ksr/YACC1-D/hardware/cards/README.md

# hardware/cards

One folder per card: README.md, kicad/ (current), eagle/<rev>/ (deprecated), docs/, bom/.

_Contents migrated 2026-09-19; MIGRATION.md at the repo root says which copy each item came from._
