ksr/YACC1-D/hardware/mechanical/README.md

# hardware/mechanical

Card divider clips (.stl/.skp), switch template (.svg), spacers, layout specs.

_Contents migrated 2026-09-19; MIGRATION.md at the repo root says which copy each item came from._
