ksr/YACC1-D/hardware/bus/bus-jumper-horizontal/README.md

# hardware/bus/bus-jumper-horizontal

V3.2.

_Contents migrated 2026-09-19; MIGRATION.md at the repo root says which copy each item came from._

Note (2026-09-20): the schematic is byte-identical to the vertical jumper's; only the board differs. `eagle/v3.2/` is the 4-layer 231 x 115 mm board in the machine (its `.brd.orig` is the unrouted intermediate labelled V3.1); `eagle/deprecated/v3.0/` is the first 2-layer 231 x 70 mm version.

Status (2026-09-20): built, **not fitted** — the jumper boards were for an older bus arrangement and are obsolete.
