ksr/YACC1-D/hardware/cards/sequencer-memory/kicad/v2.1/README.md

# sequencer-memory-v2.1 — KiCad conversion

Generated 2026-09-23 by `tools/eagle_to_kicad_all.py` from the Eagle design `Sequencer-Memory-V2.1` in `hardware/cards/sequencer-memory/eagle/v2.1/`. **The Eagle files are the record of what was designed and built; this KiCad project is derived from them and is regenerated from scratch on every run of the tool** (hand edits here will be lost - once a card is edited in KiCad, remove it from the tool's list). This revision was FABRICATED (see `hardware/FABRICATED.md`).

## Files

| File | What it is |
|---|---|
| `sequencer-memory-v2.1.kicad_pro` | project; OSH Park rules (6 mil track, 5 mil clearance, 10 mil drill, 4 mil annular) |
| `sequencer-memory-v2.1.kicad_sch` | root sheet; 4 sub-sheet(s) `sequencer-memory-v2.1-sheetN.kicad_sch` mirror the Eagle sheets |
| `sequencer-memory-v2.1-eagle.kicad_sym` | project symbol library generated from the Eagle libraries used (units = Eagle gates) |
| `sequencer-memory-v2.1.kicad_pcb` | the board: 4 copper layers, 63 footprints, 1681 track segments, 198 vias |
| `sequencer-memory-v2.1-eagle.pretty/` | project footprint library extracted from the imported board |
| `reports/` | ERC (`erc.json`), DRC (`drc.json`), schematic PDF, board renders (`-top.png`, `-bottom.png`), netlist + `netlist-compare.txt` |

## Proof

Schematic-vs-board netlist comparison (`tools/kicad/compare_netlists.py`: every (reference, pad) partition must be identical): **MATCH (106/106 nets)**

```
  same connectivity, different net name: [('/Sheet 3/ARD-RXIN', 'ARD-RXIN'), ('/Sheet 3/ARD-TXOUT', 'ARD-TXOUT'), ('/Sheet 3/FAULT', 'FAULT'), ('/Sheet 3/LD', 'LD'), ('/Sheet 3/LED-READY', 'LED-READY'), ('Net-(C19-Pad1)', 'N$8'), ('Net-(FAULT0-C)', 'N$27'), ('Net-(IC9-WP)', 'N$32'), ('Net-(IC15-AREF)', 'N$17'), ('Net-(IC15-PB6(XTAL1{slash}TOSC1))', 'N$6'), ('Net-(IC15-PB7(XTAL2{slash}TOSC2))', 'N$7'), ('Net-(IC15-PC0(ADC0))', 'N$30'), ('Net-(IC15-PC2(ADC2))', 'N$39'), ('Net-(JP3-DTR)', 'N$33'), ('Net-(JP3-VCC)', 'N$34'), ('Net-(LOADING0-C)', 'N$26'), ('Net-(PWR0-PadA)', 'N$1'), ('Net-(READY0-C)', 'N$25')]
```

## Readability

`tools/kicad/sch_overlaps.py` over every sheet: text over text 3, text over a symbol body 12, text crossed by a line 13, items off the drawing frame or on the title block 0. What is left is mostly the Eagle drawing itself (parts placed that close in Eagle) or KiCad drawing pin numbers centred on short pins.

## Residual ERC / DRC

ERC by type: unconnected_wire_endpoint 11.
`isolated_pin_label` = the converter's per-net global labels (cosmetic); `power_pin_not_driven` / unused-unit notes are the same ones KiCad's own Eagle importer leaves. `unconnected_wire_endpoint` / `pin_not_connected` = wire stubs Eagle leaves bare (mostly net wires ending on a bus, which is drawn as graphics here); since 2026-09-23 the converter no longer hangs a label on every such end (that was most of the label clutter), so they show as KiCad warnings.

DRC by type: lib_footprint_mismatch 2, shorting_items 1, silk_edge_clearance 9, silk_over_copper 199, silk_overlap 44, text_height 6, text_thickness 1, track_width 199; unconnected items 0; schematic parity 0.
Silk-over-pad and clearance notes reflect the Eagle design as drawn; unconnected items are Eagle airwires (parts the design left unrouted).

Converter: converted: 110 symbols, 584 wires, 398 labels, 82 junctions, 3 bus lines, 23 no-connects
