ksr/YACC1-D/hardware/cards/io/eagle/v1.1/Notes.md

*Converted from `Notes.rtf` (saved 2025-03-06) by `tools/rtf_to_md.py`; the .rtf is the original.*

IO Board V1.0    

Changes -  V1.1

TIL311 data latch connect to god so they always show data latch
TIL311 vcc to pin 14

LEDS are reversed hi bit to low bit

Add do not place under lcd (trestrict)

Change DB9 connector
 And add null modem logic to route tx/rx

Breakout TIL-311 to separate IO control

Next Version V1.2
Add a directional data bus buffer, probably driven by -io-rd (not done yet)

Connect 74138 IC5 pin 5 to -BUS-EN. (Not tested yet)
