ksr/YACC1-D/hardware/cards/mem-switch/eagle/v1.1/Notes.md

*Converted from `Notes.rtf` (saved 2025-03-06) by `tools/rtf_to_md.py`; the .rtf is the original.*

Version 1.0

Works
Missing bypass caps for address selection logic
Change to 74240 (inverted output)
Rotate switches (on up)

Add leds per address byte ?
Add additional address selection to locate with 16 byte blocks ?
