ksr/YACC1-D/hardware/cards/register/eagle/v1.1/Notes.md

*Converted from `Notes.rtf` (saved 2025-03-06) by `tools/rtf_to_md.py`; the .rtf is the original.*

Index registers V1.0

Next version 1.1

Changes since 1.0

Signal -IN and -OUT converted to In and OUT. Neither used in Index Register board

BUS Description PDF dated June 18 2020 is updated to new spec

NOTE from old design

Up or Down on rising edge other line must be high

IC38 switched to 4077 pin compatible with 74266

Version 1.1 to production 

Next version 1.2
SEE page 7
Is bus direction correct, should it be based on -rd-sel
