ksr/YACC1-D/hardware/cards/bus-tester/kicad/v3.1/reports/netlist-compare.txt

schematic: 110 components, 239 multi-pin nets; board: 239 multi-pin nets
identical net groups: 239 of 239
  same connectivity, different net name: [('/Sheet 3/ARD-RXIN', 'ARD-RXIN'), ('/Sheet 3/ARD-TXOUT', 'ARD-TXOUT'), ('Net-(C10-Pad1)', 'N$9'), ('Net-(IC7-WP)', 'N$2'), ('Net-(IC8-1Q)', 'N$38'), ('Net-(IC8-2Q)', 'N$31'), ('Net-(IC8-3Q)', 'N$35'), ('Net-(IC8-4Q)', 'N$32'), ('Net-(IC8-5Q)', 'N$33'), ('Net-(IC8-6Q)', 'N$34'), ('Net-(IC8-7Q)', 'N$36'), ('Net-(IC8-8Q)', 'N$37'), ('Net-(IC9A-A1)', 'N$40'), ('Net-(IC9A-A2)', 'N$43'), ('Net-(IC9A-A3)', 'N$42'), ('Net-(IC9A-A4)', 'N$41'), ('Net-(IC9B-A1)', 'N$44'), ('Net-(IC9B-A2)', 'N$46'), ('Net-(IC9B-A3)', 'N$47'), ('Net-(IC9B-A4)', 'N$45'), ('Net-(IC10-AREF)', 'N$14'), ('Net-(IC10-PB1(OC1A))', 'N$10'), ('Net-(IC10-PB2(SS{slash}OC1B))', 'N$8'), ('Net-(IC10-PB3(MOSI{slash}OC2))', 'N$7'), ('Net-(IC10-PB4(MISO))', 'N$6'), ('Net-(IC10-PB5(SCK))', 'N$1'), ('Net-(IC10-PB6(XTAL1{slash}TOSC1))', 'N$3'), ('Net-(IC10-PB7(XTAL2{slash}TOSC2))', 'N$4'), ('Net-(IC10-PC0(ADC0))', 'N$18'), ('Net-(IC10-PC1(ADC1))', 'N$19'), ('Net-(IC10-PC2(ADC2))', 'N$39'), ('Net-(IC18-2Q)', 'N$30'), ('Net-(IC18-4Q)', 'N$48'), ('Net-(JP1-DTR)', 'N$28'), ('Net-(JP1-VCC)', 'N$29'), ('Net-(L0-C)', 'N$26'), ('Net-(L1-C)', 'N$25'), ('Net-(L2-C)', 'N$24'), ('Net-(L3-C)', 'N$23'), ('Net-(L4-C)', 'N$22'), ('Net-(L5-C)', 'N$21'), ('Net-(L6-C)', 'N$20'), ('Net-(L7-C)', 'N$17'), ('Net-(LED1-C)', 'N$12'), ('Net-(LED2-C)', 'N$11'), ('Net-(LED3-C)', 'N$13'), ('Net-(LED4-C)', 'N$15'), ('Net-(LED5-C)', 'N$16'), ('Net-(OUT0-C)', 'N$27'), ('Net-(PWR0-PadA)', 'N$5')]
RESULT: MATCH
