ksr/YACC1-D/hardware/cards/cf/kicad/v1.0/reports/netlist-proof.txt

schematic 26 parts, 46 nets / 171 net pins, 92 unconnected pins (23 no-connect + 69 unused bus pins): MATCH
board     26 parts, 46 nets / 171 net pins, 92 unconnected pins (23 no-connect + 69 unused bus pins): MATCH
RESULT: MATCH (schematic and board both implement cf_netlist.py exactly)
