ksr/YACC1-D/hardware/cards/video/kicad/v1.1/reports/netlist-compare.txt

schematic: 47 components, 116 multi-pin nets; board: 116 multi-pin nets
identical net groups: 116 of 116
RESULT: MATCH
