ksr/YACC1-D/hardware/cards/memory/kicad/v2.0/options-keep-copper/reports/option-c-drc-summary.txt

     schematic parity: 53 items (built v1.3: 220); new: none
DRC: {'clearance': 1, 'items_not_allowed': 2, 'lib_footprint_mismatch': 1, 'shorting_items': 14, 'silk_edge_clearance': 4, 'silk_over_copper': 199, 'silk_overlap': 48, 'solder_mask_bridge': 63, 'text_height': 2, 'text_thickness': 1}
     the built card under the same rules: {'items_not_allowed': 2, 'lib_footprint_mismatch': 1, 'silk_edge_clearance': 4, 'silk_over_copper': 199, 'silk_overlap': 45, 'text_height': 2, 'text_thickness': 1}
     ratsnest 61 airwires (2488 mm), 61 of them touching a CF part (2488 mm); the built card: 0
     copper items (tracks + vias) 1377 = the built card's 1377, all kept (reports/option-X-locked.txt)
     non-cosmetic violations beyond the built card's: {'shorting_items': 14, 'clearance': 1, 'solder_mask_bridge': 63} -> FAIL
