ksr/YACC1-D/docs/programming/C-COMPILER.md

# y1cc — the C cross compiler for the YACC1

What C the compiler accepts, how the generated code works, how to build, run and test a program, and what to watch
for. Written 2026-09-23 from the YACC1-D tree.

Sources: `software/compiler/y1cc.py` (the compiler, its docstring is the primary reference; read as of 2026-09-23 09:37, when
`sys()`/`funcaddr()` had just been added — `README.md` is the 2026-09-22 text and does not have them yet), `software/compiler/README.md`,
`software/compiler/lib/y1lib.c`, `software/compiler/bench/sizecmp.sh` and `bench/*.c`, `tests/compiler/run.py`,
`tests/compiler/host_shim.h`, `tests/compiler/*.c`, `tests/ucemu/run.py`, `os/Makefile`, `os/lib_abi.c`,
`os/commands/*.c`, `firmware/abi/README.md`, `BACKLOG.md`. The worked example in section 9 was compiled, assembled
and run on `software/emulator` on 2026-09-23.

## 1. What it is

`y1cc.py` (Python 3, no dependencies, ~1,600 lines) turns a small C subset into YACC1 assembly for the RC/asm
assembler (`software/assembler`, `yacc1.def`). Written 2026-09-22; the front end (lexer, parser, the subset) is that
of the P8X compiler `p8cc.py`, so P8X C programs port unchanged as far as the subset goes; the back end is new,
written for what the YACC1 has: an 8-bit ACC and TMP, a carry flip-flop, eight 16-bit registers with R0 = PC and
R1 = SP, byte loads/stores through any register, absolute 16-bit register loads/stores, big-endian words, and no
indexed addressing.

```
python3 software/compiler/y1cc.py prog.c -o prog.asm            # for the machine: G3000 calls main (monitor of 2026-09-22)
python3 software/compiler/y1cc.py prog.c -o prog.asm --vector   # for the monitor as burned in 2021 (G = BRVR R7)
python3 software/compiler/y1cc.py prog.c -o prog.asm --boot     # stand-alone on an emulator
cd <dir with rcasm.rc (-h) + yacc1.def> && software/assembler/asm prog -d=yacc1 > prog.lst      # -> prog.img
software/emulator/emulator -x -f prog.img                       # runs a --boot image, exits at HALT
software/ucemu/y1ucemu -x -m -f prog.img                        # the same on the microcode emulator, ROM loaded
```
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
