ksr/YACC1-D/docs/cards/alu.md

# ALU card (V3.2) — theory of operation

The 8-bit arithmetic/logic unit of the YACC1 with the accumulator (AC), the carry flip-flop, the shift register and
the branch-condition multiplexer that every conditional branch in the machine goes through.

Written 2026-09-23 from the YACC1-D tree.
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
