ksr/YACC1-D/hardware/bus/backplane/kicad/v2.0/reports/backplane-v2.0-bottom.png

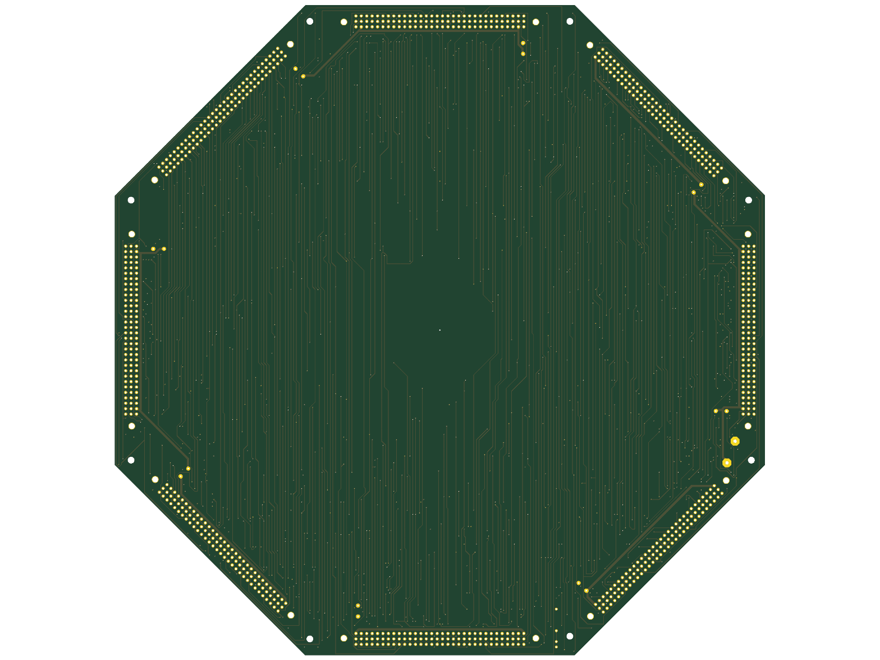
hardware/bus/backplane/kicad/v2.0/reports/backplane-v2.0-bottom.png
