ksr/YACC1-D/hardware/bus/blank-card/kicad/v3.2/reports/blank-card-v3.2-bottom.png

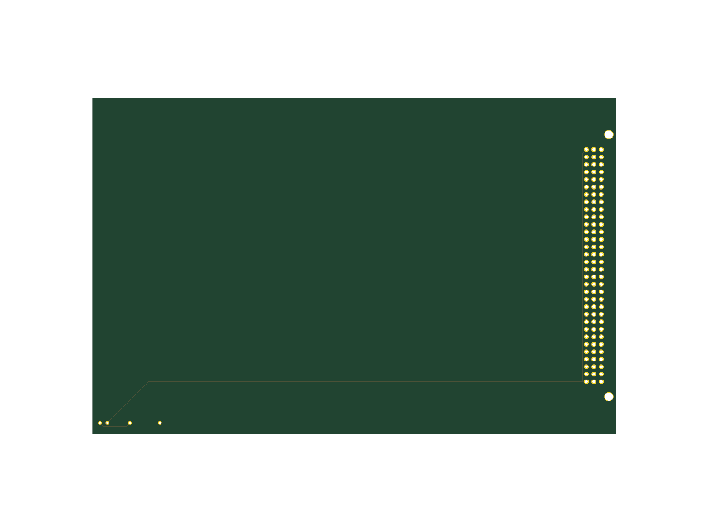
hardware/bus/blank-card/kicad/v3.2/reports/blank-card-v3.2-bottom.png
