ksr/YACC1-D/hardware/bus/bus-jumper-horizontal/kicad/v3.2/reports/bus-jumper-horizontal-v3.2-bottom.png

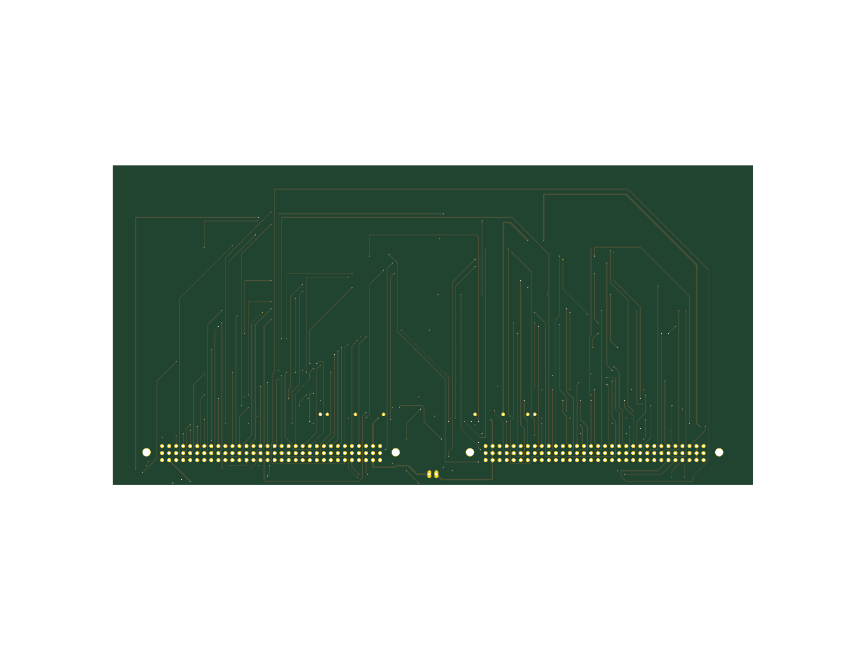
hardware/bus/bus-jumper-horizontal/kicad/v3.2/reports/bus-jumper-horizontal-v3.2-bottom.png
