ksr/YACC1-D/hardware/bus/bus-jumper-vertical/kicad/v3.0/reports/bus-jumper-vertical-v3.0-top.png

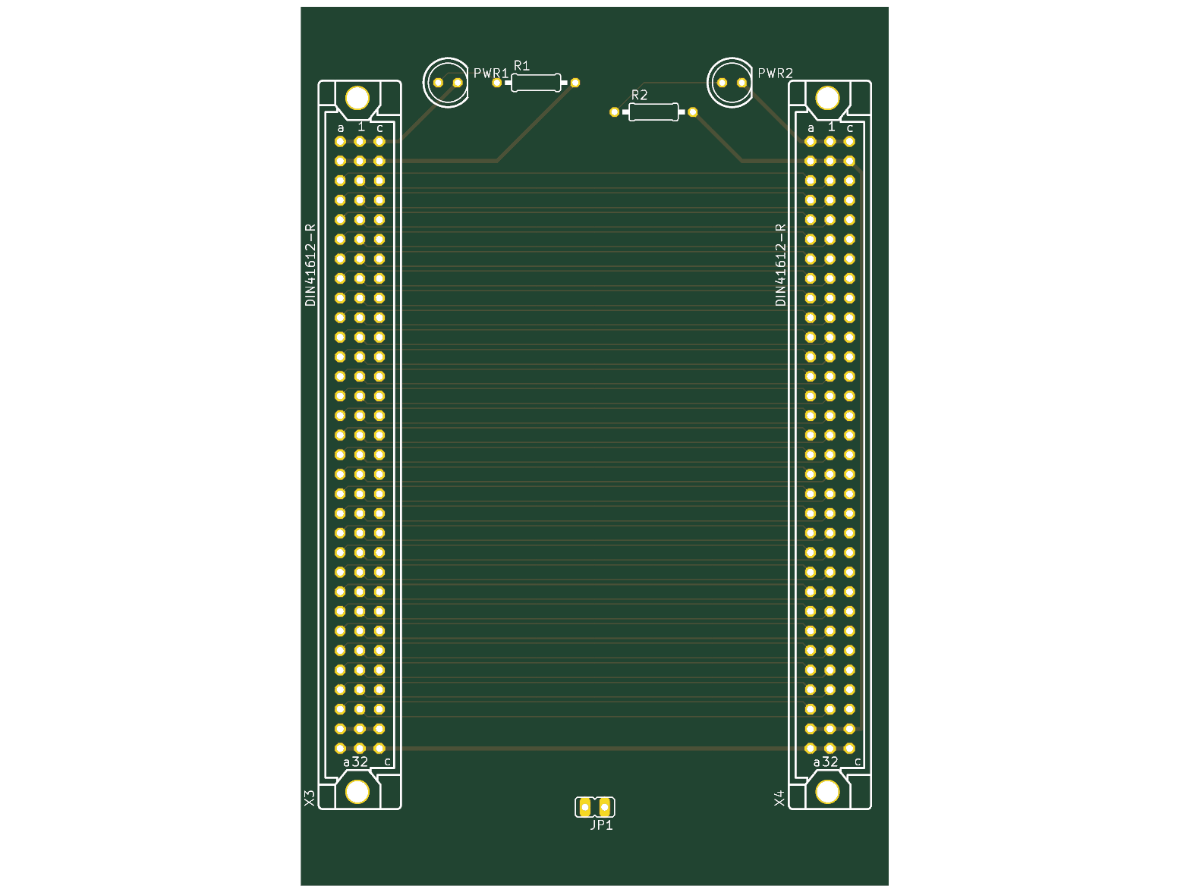
hardware/bus/bus-jumper-vertical/kicad/v3.0/reports/bus-jumper-vertical-v3.0-top.png
