ksr/YACC1-D/hardware/cards/alu/kicad/v3.2/reports/alu-v3.2-bottom.png

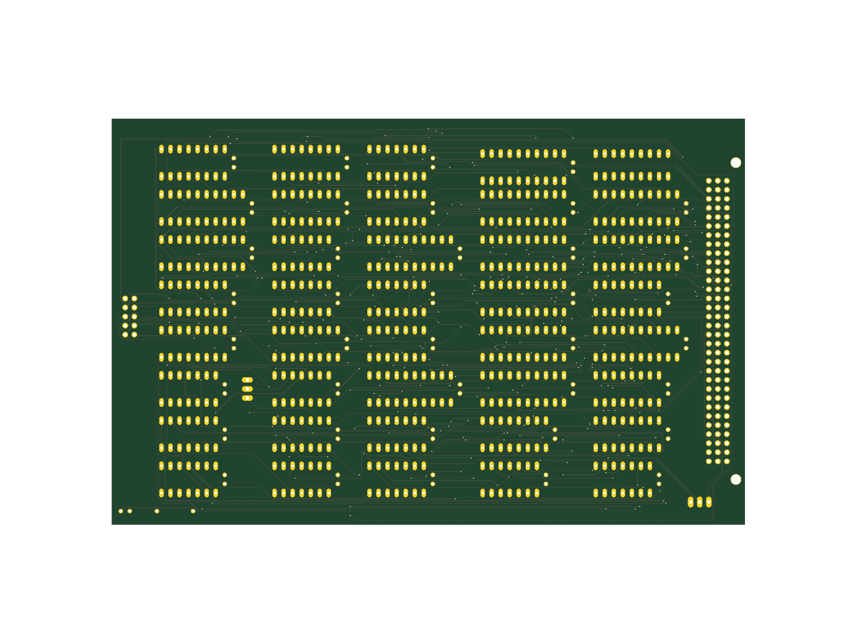
hardware/cards/alu/kicad/v3.2/reports/alu-v3.2-bottom.png
