ksr/YACC1-D/hardware/cards/cf/kicad/v1.0/yacc1-cf-card-render-top.png

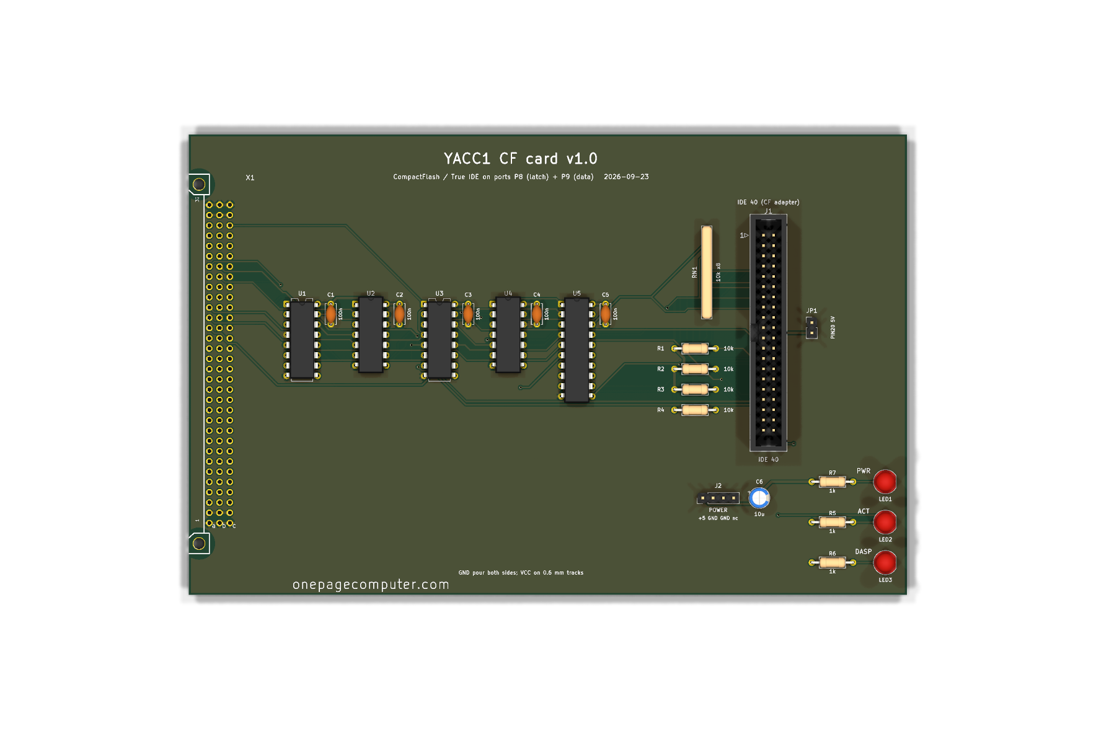
hardware/cards/cf/kicad/v1.0/yacc1-cf-card-render-top.png
