ksr/YACC1-D/hardware/cards/mem-register/kicad/v1.0/reports/mem-register-v1.0-bottom.png

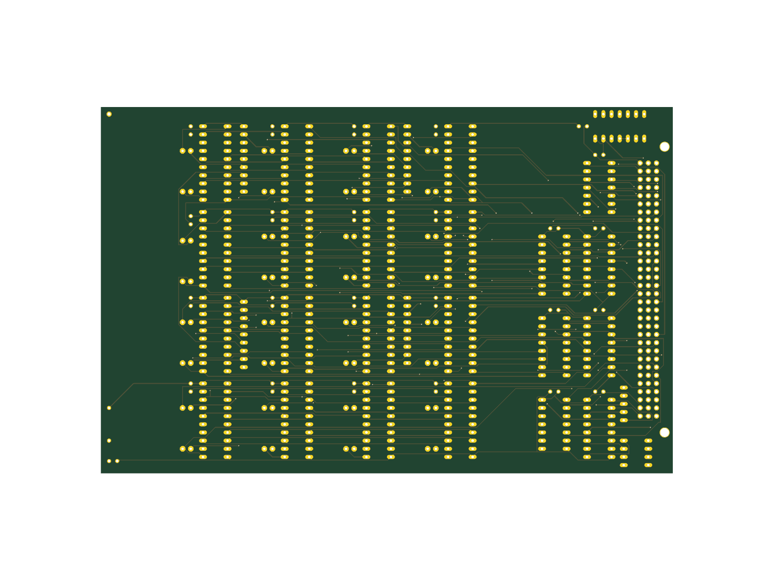
hardware/cards/mem-register/kicad/v1.0/reports/mem-register-v1.0-bottom.png
