ksr/YACC1-D/hardware/cards/mem-switch/kicad/v1.1/reports/mem-switch-v1.1-bottom.png

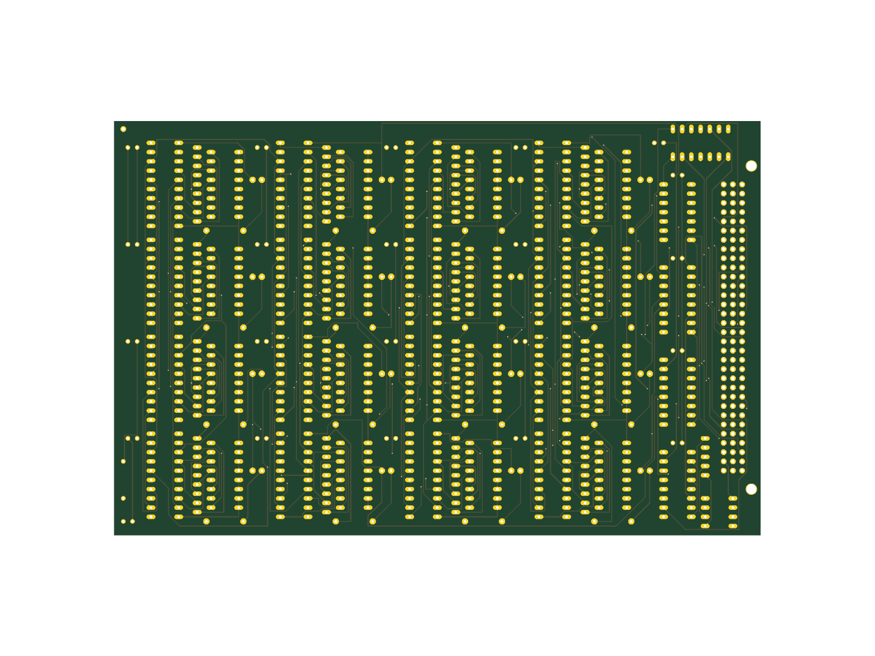
hardware/cards/mem-switch/kicad/v1.1/reports/mem-switch-v1.1-bottom.png
