ksr/YACC1-D/hardware/cards/memory/kicad/v2.0/memory-v2.0-render-bottom.png

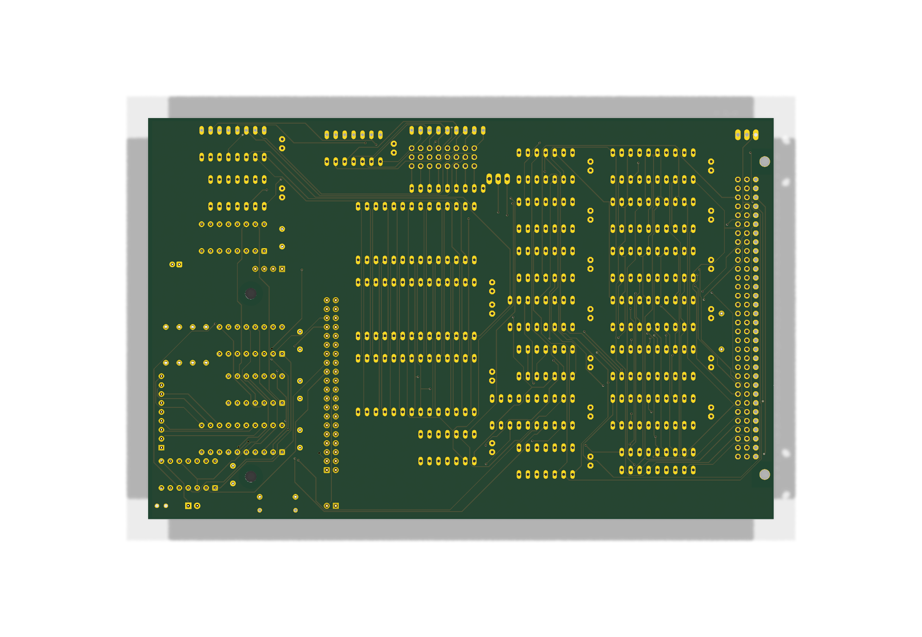
hardware/cards/memory/kicad/v2.0/memory-v2.0-render-bottom.png
