ksr/YACC1-D/hardware/cards/memory/kicad/v2.0/memory-v2.0-render-top.png

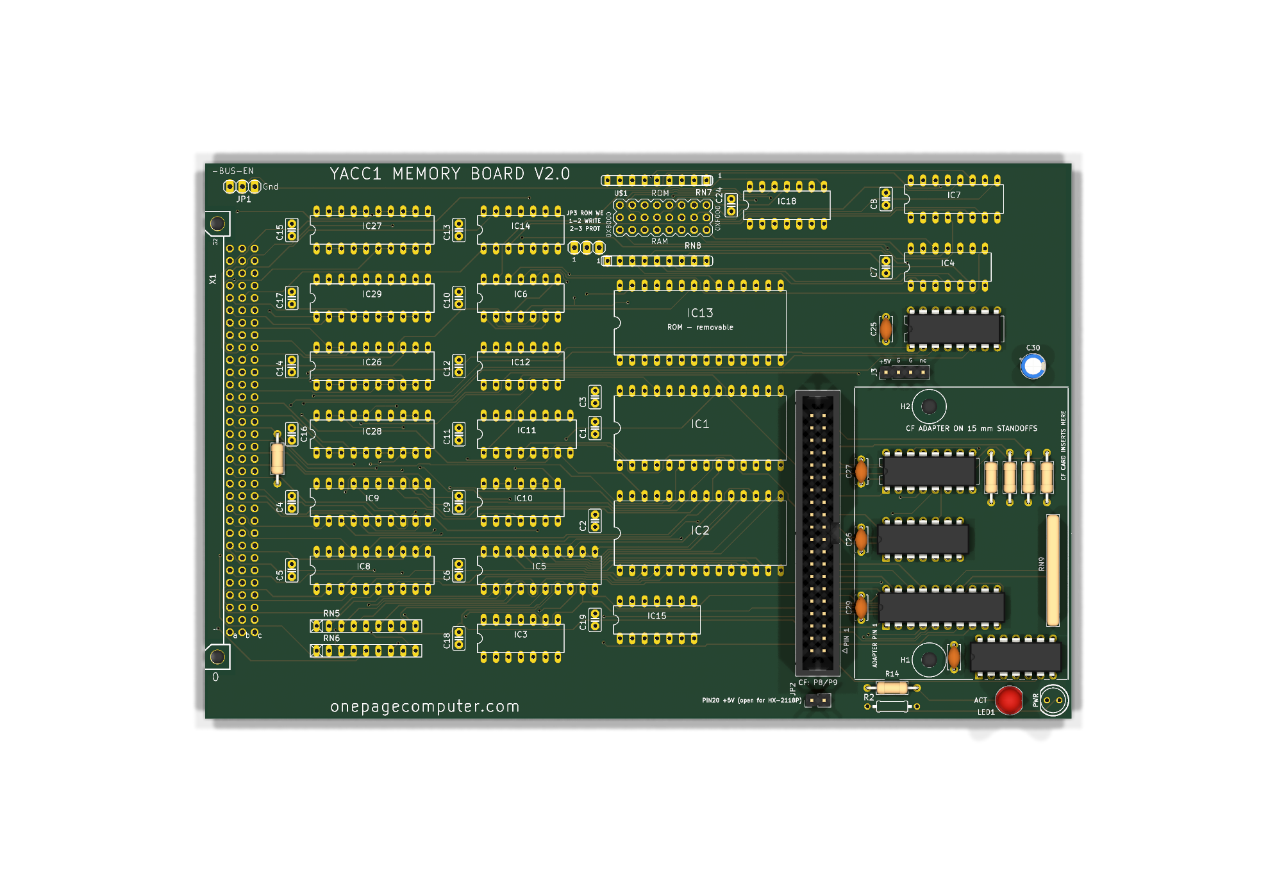
hardware/cards/memory/kicad/v2.0/memory-v2.0-render-top.png
