ksr/YACC1-D/hardware/cards/memory/kicad/v2.0/options-keep-copper/memory-v2.0-option-a-placement.png

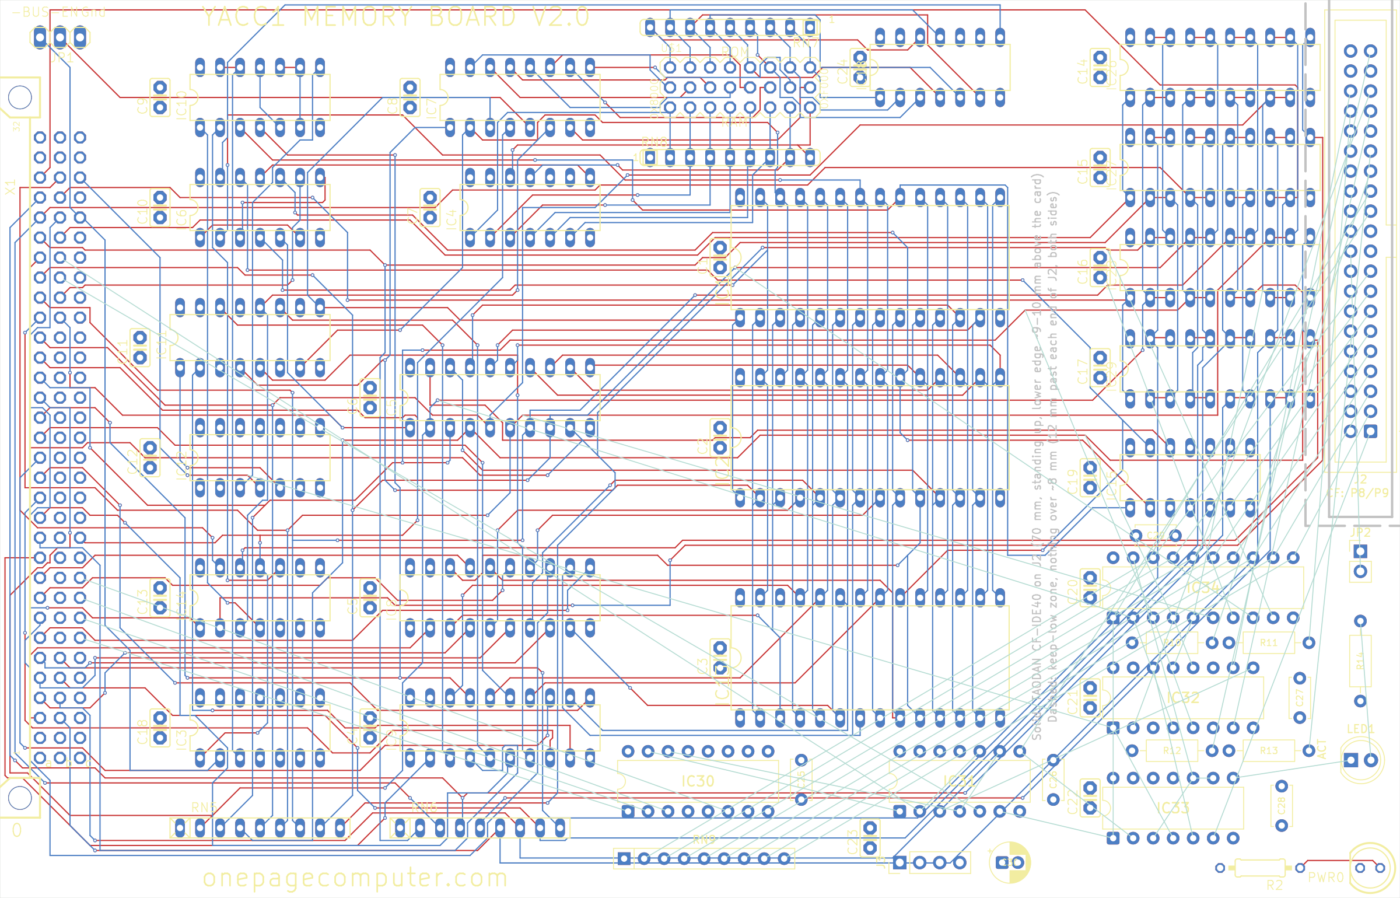
hardware/cards/memory/kicad/v2.0/options-keep-copper/memory-v2.0-option-a-placement.png
