ksr/YACC1-D/hardware/cards/memory/kicad/v2.0/options-keep-copper/memory-v2.0-option-a-render-top.png

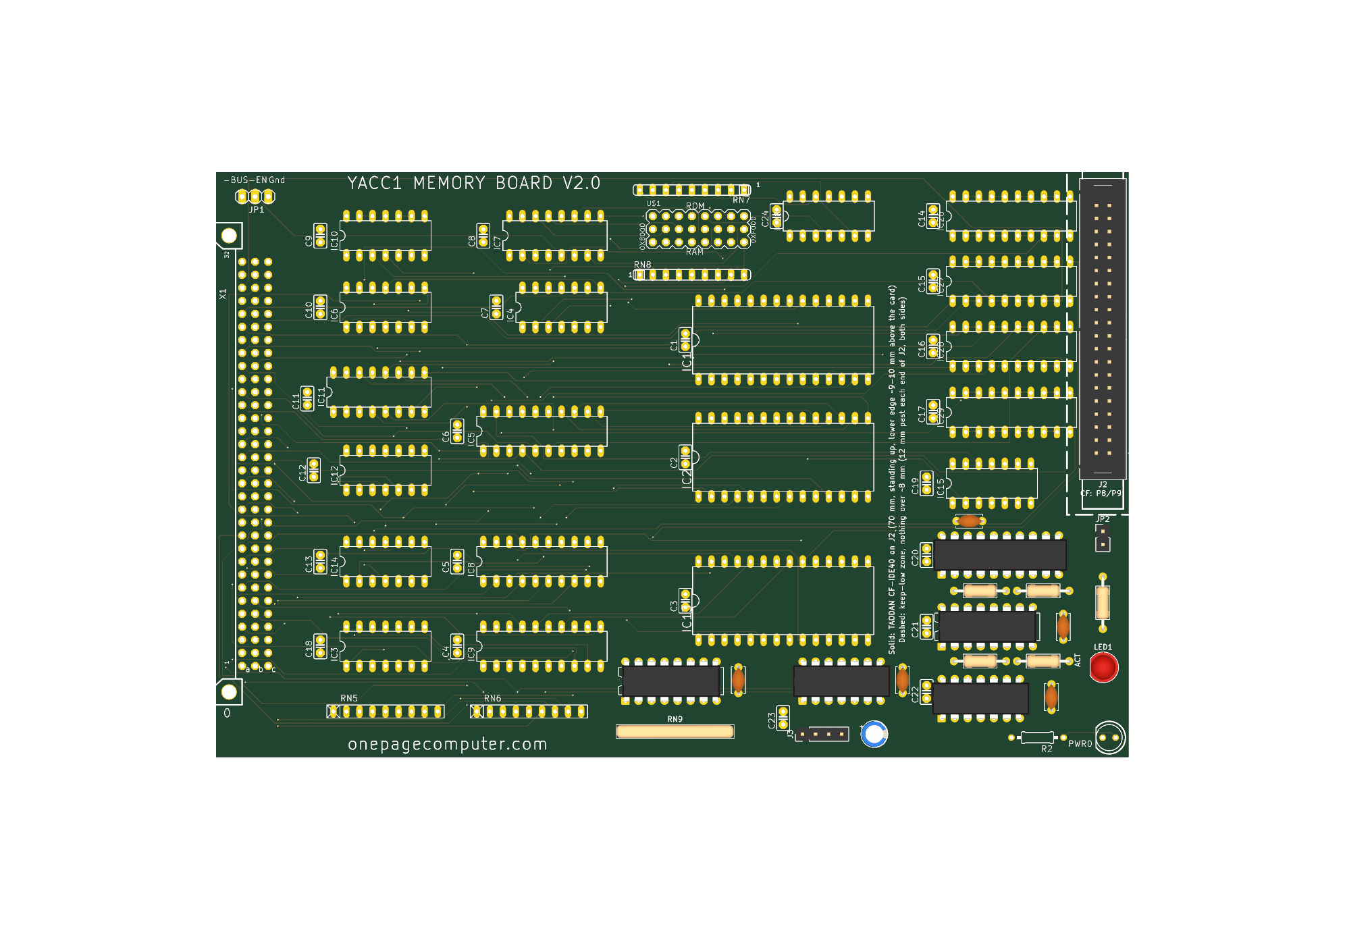
hardware/cards/memory/kicad/v2.0/options-keep-copper/memory-v2.0-option-a-render-top.png
