ksr/YACC1-D/hardware/cards/memory/kicad/v2.0/options-standoff/memory-v2.0-standoff-a-placement.png

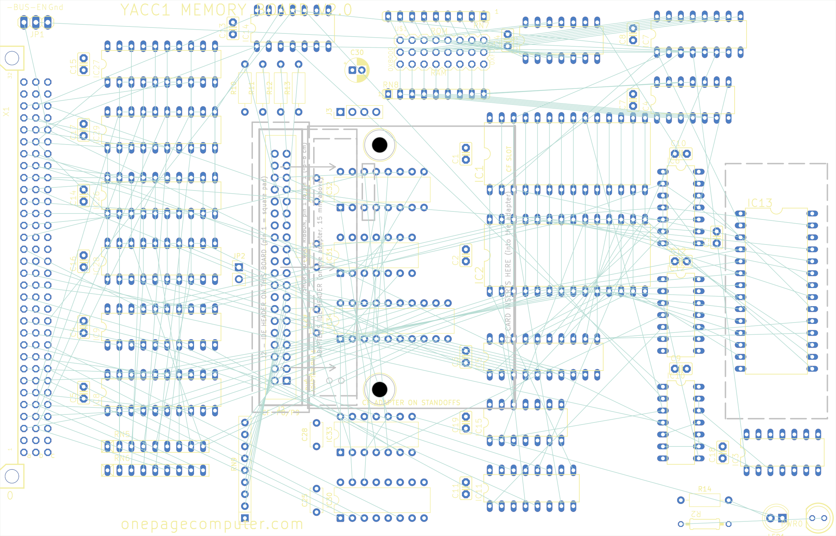
hardware/cards/memory/kicad/v2.0/options-standoff/memory-v2.0-standoff-a-placement.png
