ksr/YACC1-D/hardware/cards/memory/kicad/v2.0/options-standoff/memory-v2.0-standoff-e-render-top.png

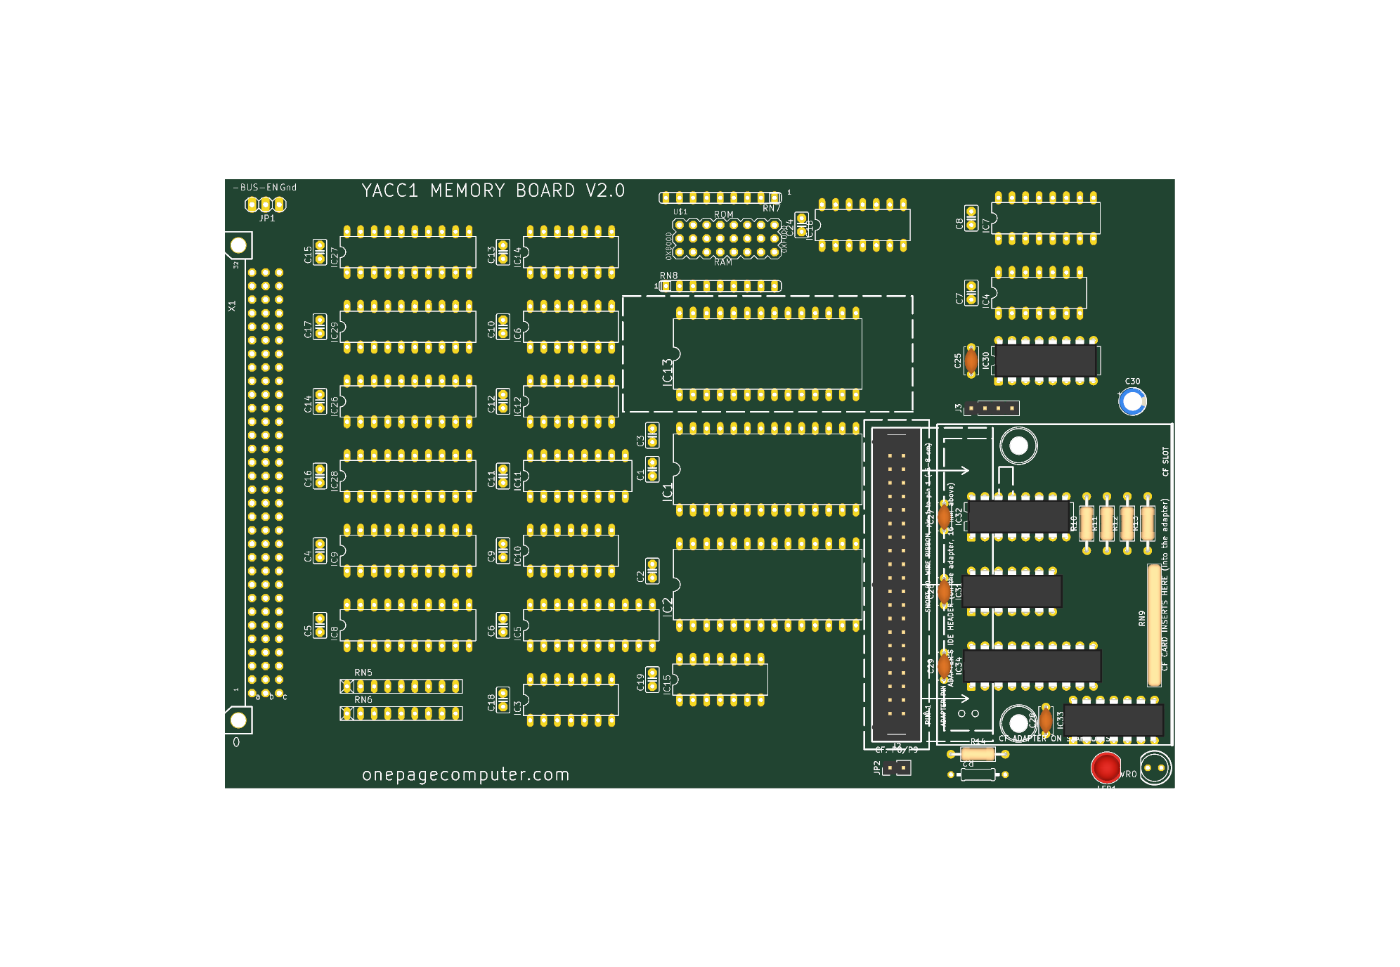
hardware/cards/memory/kicad/v2.0/options-standoff/memory-v2.0-standoff-e-render-top.png
