ksr/YACC1-D/hardware/cards/memory/kicad/v2.0/options-top-edge-J2/memory-v2.0-relayout-b-placement.png

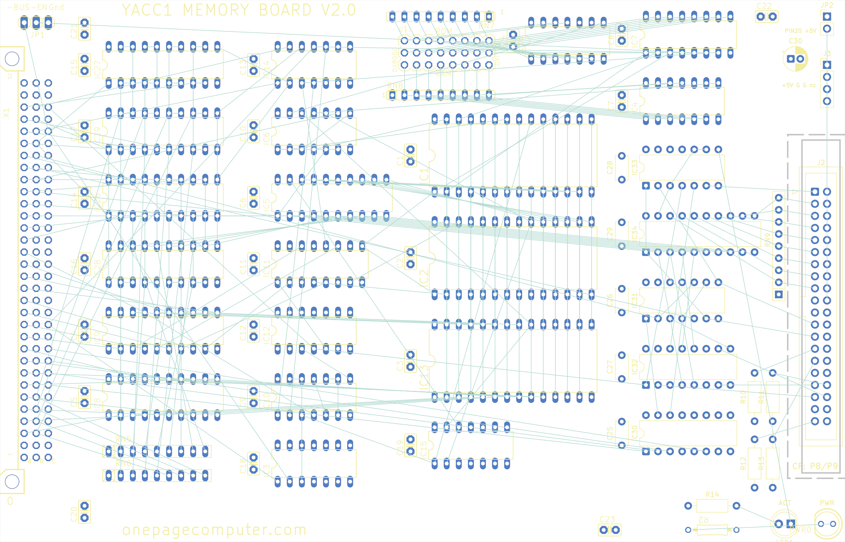
hardware/cards/memory/kicad/v2.0/options-top-edge-J2/memory-v2.0-relayout-b-placement.png
