ksr/YACC1-D/hardware/cards/protocard/kicad/v1.0/reports/protocard-v1.0-bottom.png

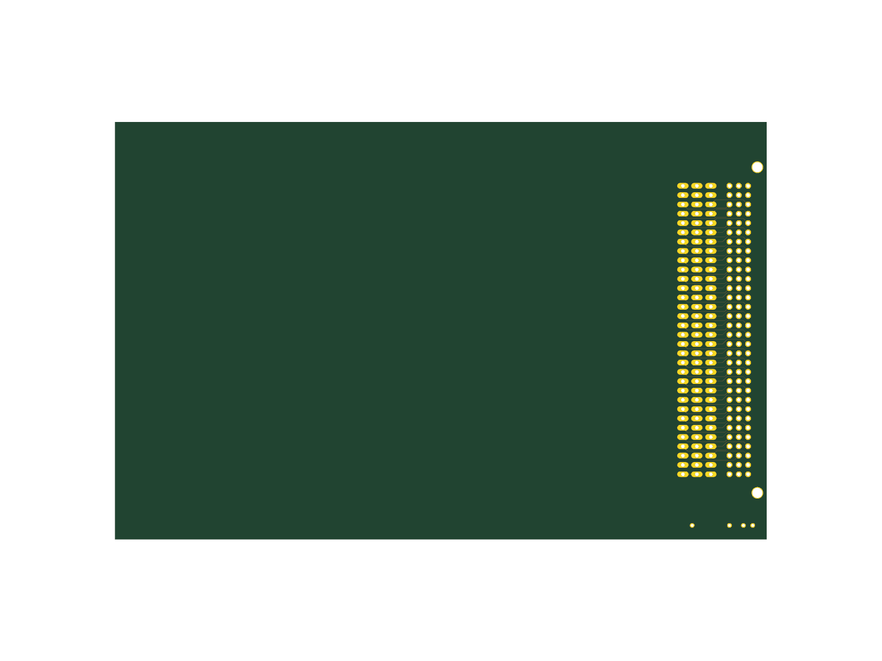
hardware/cards/protocard/kicad/v1.0/reports/protocard-v1.0-bottom.png
