ksr/YACC1-D/hardware/cards/register/kicad/v1.1/reports/register-v1.1-bottom.png

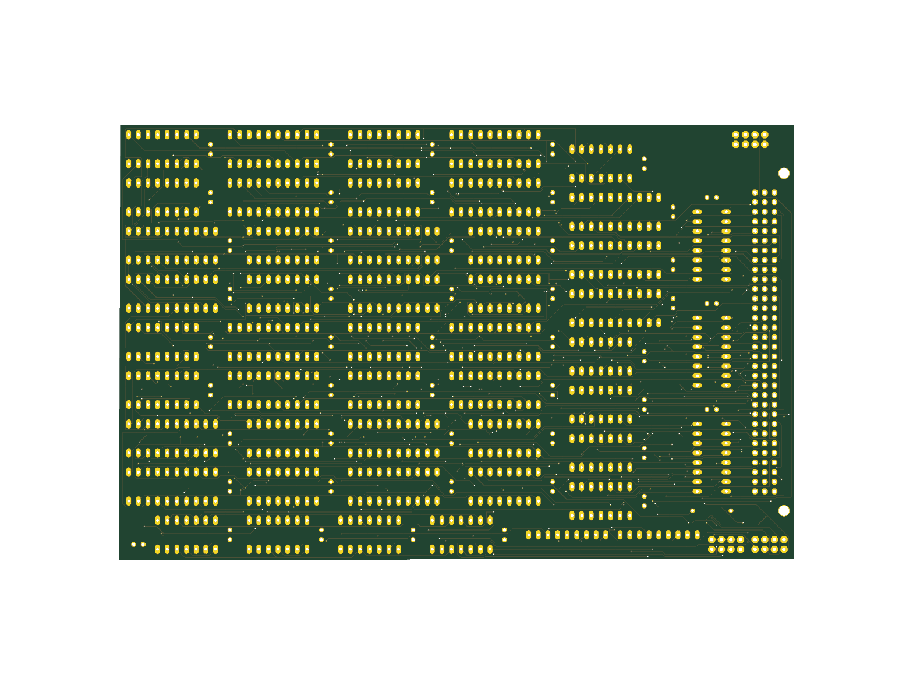
hardware/cards/register/kicad/v1.1/reports/register-v1.1-bottom.png
