ksr/YACC1-D/hardware/cards/register/kicad/v1.1/reports/register-v1.1-top.png

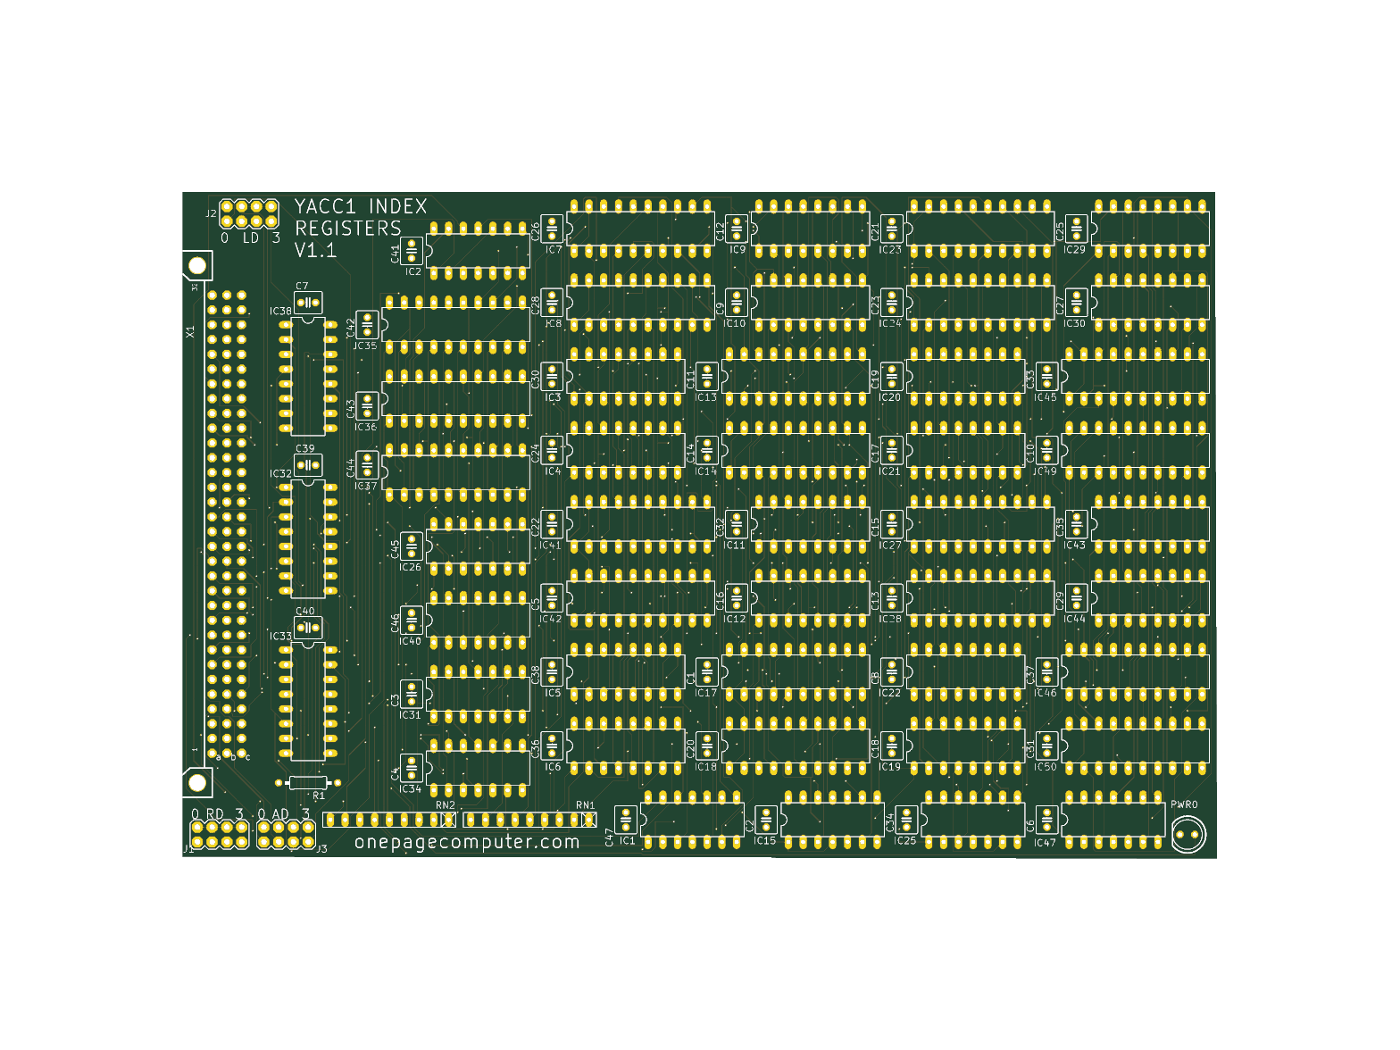
hardware/cards/register/kicad/v1.1/reports/register-v1.1-top.png
