ksr/YACC1-D/hardware/cards/sequencer-logic/kicad/v2.1/reports/sequencer-logic-v2.1-bottom.png

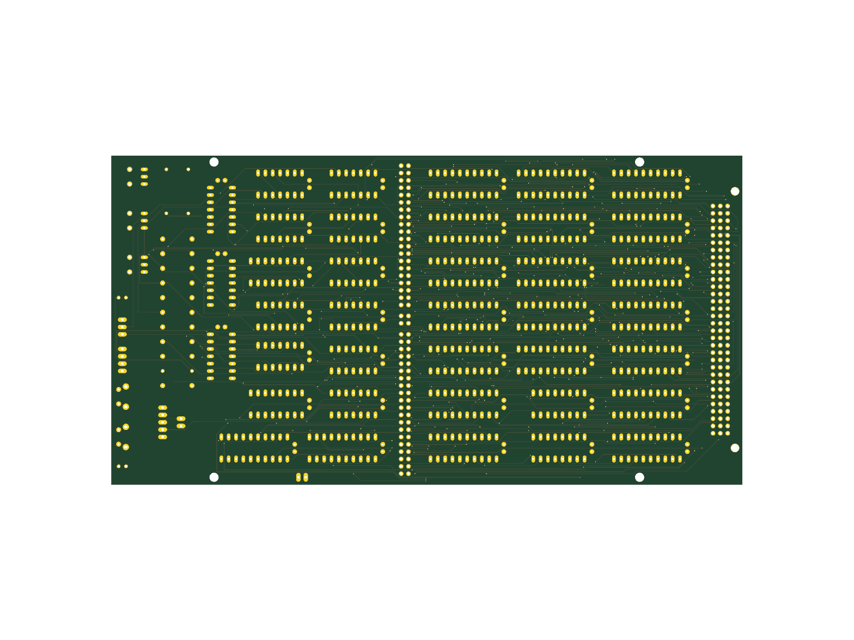
hardware/cards/sequencer-logic/kicad/v2.1/reports/sequencer-logic-v2.1-bottom.png
