ksr/YACC1-D/hardware/cards/sequencer-memory/accessories/eeprom-adaptor/kicad/reports/sequencer-memory-eeprom-adaptor-bottom.png

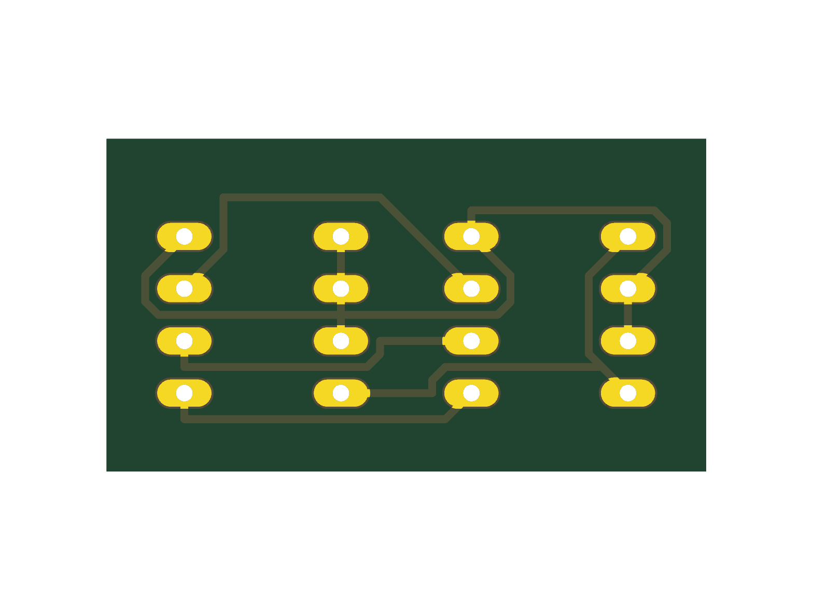
hardware/cards/sequencer-memory/accessories/eeprom-adaptor/kicad/reports/sequencer-memory-eeprom-adaptor-bottom.png
