ksr/YACC1-D/hardware/cards/sequencer-memory/kicad/v2.1/reports/sequencer-memory-v2.1-bottom.png

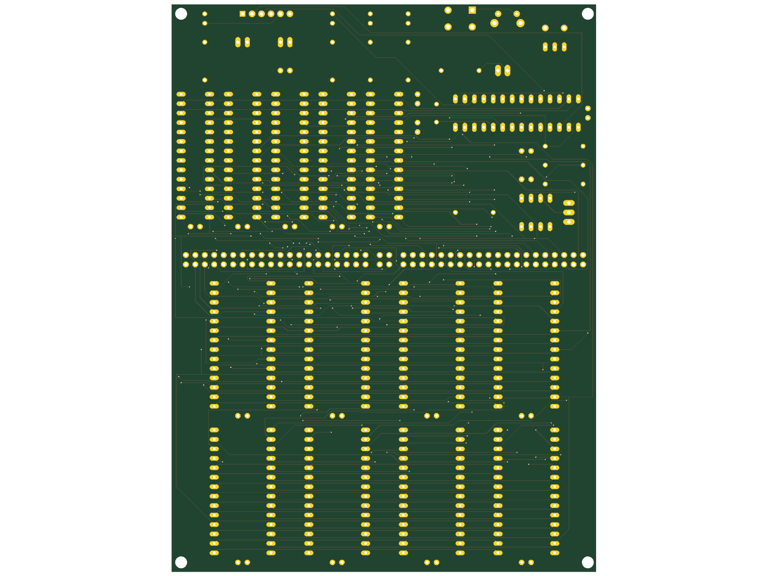
hardware/cards/sequencer-memory/kicad/v2.1/reports/sequencer-memory-v2.1-bottom.png
