ksr/YACC1-D/hardware/cards/video/kicad/v1.0-fusion-export-2026-09-18/reports/video-v1.0-fusion-export-2026-09-18-top.png

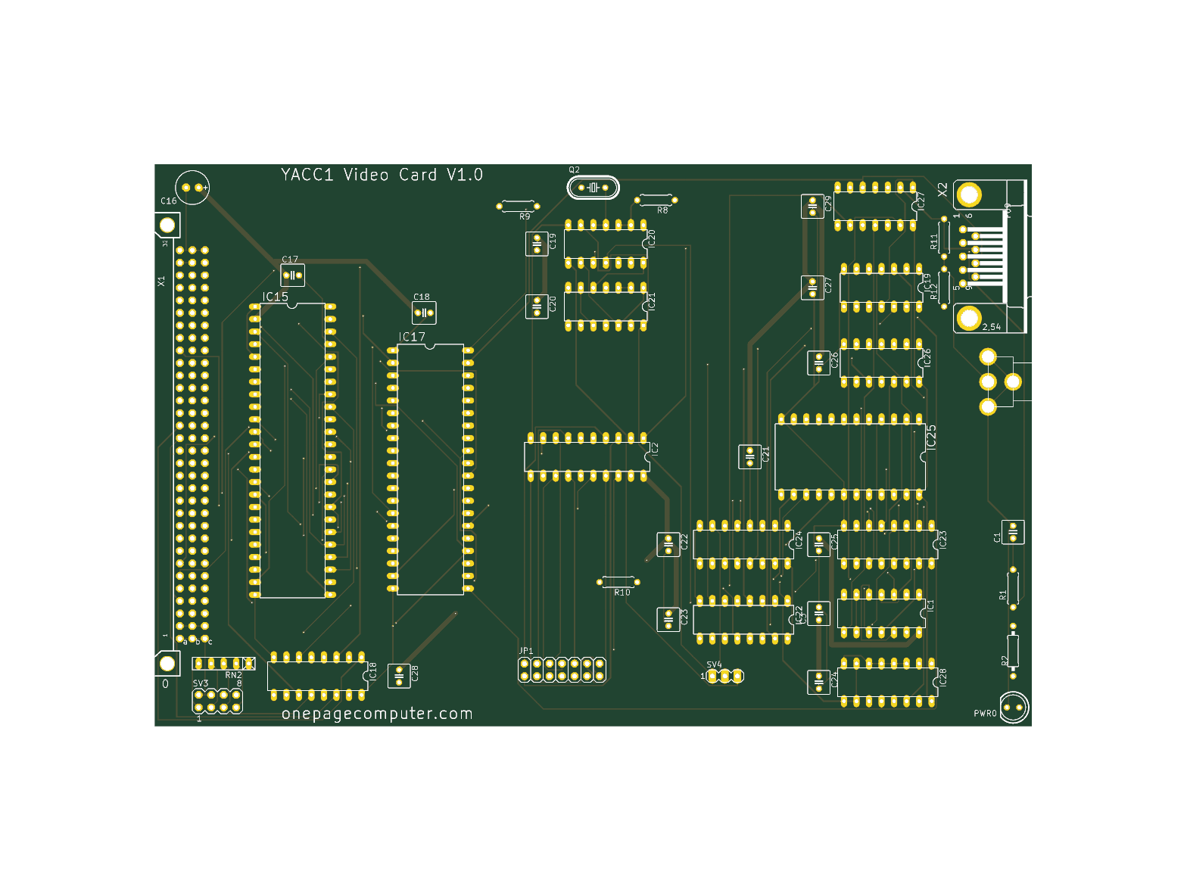
hardware/cards/video/kicad/v1.0-fusion-export-2026-09-18/reports/video-v1.0-fusion-export-2026-09-18-top.png
