ksr/YACC1-D/docs/bom/video.md

# BOM: Video V1.0 (Fusion export)

GENERATED by `tools/gen_bom.py` on 2026-09-23 from `hardware/cards/video/eagle/v1.0-fusion-export-2026-09-18/Video_1.0.sch` (Eagle 9.7.0) - do not edit; edit the schematic and re-run `make bom`.  
Role: machine. installed for bring-up, 6845 socket empty (MACHINE.md); KiCad v1.1 is the design master.

47 parts (16 ICs, 24 passives, 5 connectors/headers/jumpers, 2 others); 19 supply/frame symbols skipped. Value = the schematic's value attribute, or the deviceset with the Eagle technology substituted for `*` (a `*` left in a value means the schematic names no technology: the part number was never filled in).

## Parts by designator

| Designator | Value | Device (deviceset/device) | Package | Library | Technology | Class |
|---|---|---|---|---|---|---|
| C1 | 1 | C-US/025-050X050 | C025-050X050 | rcl |  | passive |
| C3 | .1 | C-US/025-050X050 | C025-050X050 | rcl |  | passive |
| C16 | 10.0 | CPOL-US/E2.5-7 | E2,5-7 | rcl |  | passive |
| C17 | .1 | C-US/025-050X050 | C025-050X050 | rcl |  | passive |
| C18 | .1 | C-US/025-050X050 | C025-050X050 | rcl |  | passive |
| C19 | .1 | C-US/025-050X050 | C025-050X050 | rcl |  | passive |
| C20 | .1 | C-US/025-050X050 | C025-050X050 | rcl |  | passive |
| C21 | .1 | C-US/025-050X050 | C025-050X050 | rcl |  | passive |
| C22 | .1 | C-US/025-050X050 | C025-050X050 | rcl |  | passive |
| C23 | .1 | C-US/025-050X050 | C025-050X050 | rcl |  | passive |
| C24 | .1 | C-US/025-050X050 | C025-050X050 | rcl |  | passive |
| C25 | .1 | C-US/025-050X050 | C025-050X050 | rcl |  | passive |
| C26 | .1 | C-US/025-050X050 | C025-050X050 | rcl |  | passive |
| C27 | .1 | C-US/025-050X050 | C025-050X050 | rcl |  | passive |
| C28 | .1 | C-US/025-050X050 | C025-050X050 | rcl |  | passive |
| C29 | .1 | C-US/025-050X050 | C025-050X050 | rcl |  | passive |
| IC1 | 74ALS08 | 74*08/N | DIL14 | 74xx-us | ALS | IC |
| IC2 | 74LS373 | 74*373/N | DIL20 | 74xx-us | LS | IC |
| IC15 | VRAM | 7134P | DIL48 | memory-idt |  | IC |
| IC17 | 6845 | 6845 | DIL40 | micro-motorola |  | IC |
| IC18 | 74S85 | 74*85/N | DIL16 | 74xx-us | S | IC |
| IC19 | 74LS00 | 74*00/N | DIL14 | 74xx-us | LS | IC |
| IC20 | 74LS04 | 74*04/N | DIL14 | 74xx-us | LS | IC |
| IC21 | 74LS90 | 74*90/N | DIL14 | 74xx-us | LS | IC |
| IC22 | 74LS175 | 74*175/N | DIL16 | 74xx-us | LS | IC |
| IC23 | 74LS174 | 74*174/N | DIL16 | 74xx-us | LS | IC |
| IC24 | 74LS166 | 74*166/N | DIL16 | 74xx-us | LS | IC |
| IC25 | CHARGEN | 2732 | DIL24 | memory |  | IC |
| IC26 | 74LS86 | 74*86/N | DIL14 | 74xx-us | LS | IC |
| IC27 | 74*16 | 74*16/N | DIL14 | 74xx-us |  | IC |
| IC28 | 74HC160 | 74*160/N | DIL16 | 74xx-eu | HC | IC |
| JP1 | PINHD-2X7 | PINHD-2X7 | 2X07 | Connector |  | connector |
| PWR | LED | LED/5MM | LED5MM | led |  | other |
| Q2 | CRYTAL | CRYTAL/HC49U-V | HC49U-V | crystal |  | other |
| R1 | 10K | R-US_/0207/7 | 0207/7 | rcl |  | passive |
| R2 | 330 | R/0207/10 | 0207/10 | eagle-ltspice |  | passive |
| R8 | 1K | R-US_/0207/7 | 0207/7 | rcl |  | passive |
| R9 | 1K | R-US_/0207/7 | 0207/7 | rcl |  | passive |
| R10 | 1K | R-US_/0207/7 | 0207/7 | rcl |  | passive |
| R11 | 33 | R-US_/0207/7 | 0207/7 | rcl |  | passive |
| R12 | 270 | R-US_/0207/7 | 0207/7 | rcl |  | passive |
| RN2 | RNX4 | RNX4 | RN-5 | resistor-net |  | passive |
| SV3 | MA04-2 | MA04-2 | MA04-2 | con-lstb |  | connector |
| SV4 | MA03-1 | MA03-1 | MA03-1 | con-lstb |  | connector |
| U$3 | RCA | RCA | RCA | cdp |  | IC |
| X1 | FABC96R | FABC96R | FABC96R | con-vg |  | connector |
| X2 | F09?S | F09?S/HP | F09HP | con-subd |  | connector |

## Order list (value + package)

| Qty | Value | Package | Designators |
|---|---|---|---|
| 14 | .1 | C025-050X050 | C3, C17, C18, C19, C20, C21, C22, C23, C24, C25, C26, C27, C28, C29 |
| 3 | 1K | 0207/7 | R8, R9, R10 |
| 1 | 1 | C025-050X050 | C1 |
| 1 | 10.0 | E2,5-7 | C16 |
| 1 | 10K | 0207/7 | R1 |
| 1 | 270 | 0207/7 | R12 |
| 1 | 33 | 0207/7 | R11 |
| 1 | 330 | 0207/10 | R2 |
| 1 | 6845 | DIL40 | IC17 |
| 1 | 74*16 | DIL14 | IC27 |
| 1 | 74ALS08 | DIL14 | IC1 |
| 1 | 74HC160 | DIL16 | IC28 |
| 1 | 74LS00 | DIL14 | IC19 |
| 1 | 74LS04 | DIL14 | IC20 |
| 1 | 74LS166 | DIL16 | IC24 |
| 1 | 74LS174 | DIL16 | IC23 |
| 1 | 74LS175 | DIL16 | IC22 |
| 1 | 74LS373 | DIL20 | IC2 |
| 1 | 74LS86 | DIL14 | IC26 |
| 1 | 74LS90 | DIL14 | IC21 |
| 1 | 74S85 | DIL16 | IC18 |
| 1 | CHARGEN | DIL24 | IC25 |
| 1 | CRYTAL | HC49U-V | Q2 |
| 1 | F09?S | F09HP | X2 |
| 1 | FABC96R | FABC96R | X1 |
| 1 | LED | LED5MM | PWR |
| 1 | MA03-1 | MA03-1 | SV4 |
| 1 | MA04-2 | MA04-2 | SV3 |
| 1 | PINHD-2X7 | 2X07 | JP1 |
| 1 | RCA | RCA | U$3 |
| 1 | RNX4 | RN-5 | RN2 |
| 1 | VRAM | DIL48 | IC15 |
