ksr/YACC1-D/hardware/cards/memory/kicad/v2.0/memory-v2.0-jlcpcb-order.txt

YACC1 memory card v2.0 - PCB order parameters (JLCPCB)            *** ORDERED 2026-10-09, 2000765A-Y52 ***
The v2.0 board: standoff option E (chosen 2026-09-25).
Generated by finish_v2.py fab from memory-v2.0.kicad_pcb.

The same stack-up and options as the built card's order: JLCPCB 2000765A-Y42 (2025-06-27, "Memory V1_2025-06-27_Y42",
hardware/cards/memory/eagle/v1.3/fab/jlcpcb-order-2000765A-Y42.zip, file YG/4te.json):

  Gerber file          memory-v2.0-gerbers.zip
  Base material        FR-4                              (4te.json board_type)
  Layers               4                                 (layers 4)
  Dimensions           177.8 x 114.0 mm                 (built card: 177.8 x 114.0 mm, size_x/size_y in cm)
  PCB thickness        1.6 mm                            (thickness 1.6)
  Outer copper weight  1 oz                              (cu_outer 1.0)
  Inner copper weight  0.5 oz                            (cu_inner 0.5)
  Solder mask          green                             (color_sm)
  Silkscreen           white                             (color_ss)
  Surface finish       HASL with lead                    (finished)
  Via covering         plugged (solder-mask plugged)     (via)
  Impedance control    none; castellated / gold fingers: none

Layer stack (top to bottom), the gerbers in the zip:
  L1  memory-v2.0-F_Cu.gbr     signals (top, component side)
  L2  memory-v2.0-In1_Cu.gbr   GND plane (solid, thermal reliefs on the GND pads)
  L3  memory-v2.0-In2_Cu.gbr   VCC plane (solid, thermal reliefs on the VCC pads)
  L4  memory-v2.0-B_Cu.gbr     signals (bottom)
  plus F_Mask, B_Mask, F_Silkscreen, B_Silkscreen, Edge_Cuts, the Excellon drill files (memory-v2.0-PTH.drl plated,
  memory-v2.0-NPTH.drl non-plated: the two 3.2 mm standoff holes H1 / H2 for the CF adapter and the bus connector
  X1's two 2.79 mm mounting holes) and the drill maps.

Design minimums on this board: track 0.25 mm, clearance 0.2 mm, via 0.8 mm pad / 0.4 mm drill, copper to edge 0.5 mm;
72 vias, all through vias; every part through-hole (no SMD, no assembly, no stencil).
