ksr/YACC1-D/hardware/cards/memory/kicad/v2.0/reports/memory-v2.0-order.txt

  kept: run 1 (order 15)
  run 1 (order 15): unrouted 0, vias 69, track 12783 mm
