ksr/YACC1-D/hardware/cards/memory/kicad/v2.0/memory-v2.0-bom.csv

Refs | Value | Footprint | Qty
C1-C19,C24 | C-US | memory-v1.3-eagle:C025-025X050 | 20
C25-C29 | 100n | Capacitor_THT:C_Disc_D5.0mm_W2.5mm_P5.00mm | 5
C30 | 10u | Capacitor_THT:CP_Radial_D5.0mm_P2.00mm | 1
IC1,IC2 | 62256P | memory-v1.3-eagle:DIL28-6 | 2
IC3 | 74*32 | memory-v1.3-eagle:DIL14 | 1
IC4,IC18 | 74*30 | memory-v1.3-eagle:DIL14 | 2
IC5 | 74*245 | memory-v1.3-eagle:DIL20 | 1
IC6,IC14 | 74*04 | memory-v1.3-eagle:DIL14 | 2
IC7 | 74*138 | memory-v1.3-eagle:DIL16 | 1
IC8,IC9 | 74*244 | memory-v1.3-eagle:DIL20 | 2
IC10 | 74*00 | memory-v1.3-eagle:DIL14 | 1
IC11 | 74*157 | memory-v1.3-eagle:DIL16 | 1
IC12 | 74*74 | memory-v1.3-eagle:DIL14 | 1
IC13 | 28C64C | memory-v1.3-eagle:DIL28-6 | 1
IC15 | 74*11 | memory-v1.3-eagle:DIL14 | 1
IC26-IC29 | 74*374 | memory-v1.3-eagle:DIL20 | 4
IC30 | 74LS138 | Package_DIP:DIP-16_W7.62mm | 1
IC31 | 74LS32 | Package_DIP:DIP-14_W7.62mm | 1
IC32 | 74LS175 | Package_DIP:DIP-16_W7.62mm | 1
IC33 | 74LS08 | Package_DIP:DIP-14_W7.62mm | 1
IC34 | 74LS245 | Package_DIP:DIP-20_W7.62mm | 1
J2 | IDE 40 | Connector_IDC:IDC-Header_2x20_P2.54mm_Vertical | 1
J3 | POWER | Connector_PinHeader_2.54mm:PinHeader_1x04_P2.54mm_Vertical | 1
JP1,JP3 | PINHD-1X3 | memory-v1.3-eagle:1X03 | 2
JP2 | PIN20 5V | Connector_PinHeader_2.54mm:PinHeader_1x02_P2.54mm_Vertical | 1
LED1 | ACT yellow | LED_THT:LED_D5.0mm | 1
PWR0 | LED | memory-v1.3-eagle:LED5MM | 1
R2 | 330 | memory-v1.3-eagle:0207_10 | 1
R10-R13 | 10k | Resistor_THT:R_Axial_DIN0207_L6.3mm_D2.5mm_P10.16mm_Horizontal | 4
R14 | 1k | Resistor_THT:R_Axial_DIN0207_L6.3mm_D2.5mm_P10.16mm_Horizontal | 1
R15 | 470 | Resistor_THT:R_Axial_DIN0207_L6.3mm_D2.5mm_P10.16mm_Horizontal | 1
RN5,RN6 | RNX8 | memory-v1.3-eagle:RN-9 | 2
RN7,RN8 | G08R | memory-v1.3-eagle:SIL9 | 2
RN9 | 10k x8 | Resistor_THT:R_Array_SIP9 | 1
U$1 | PIN_3X8 | memory-v1.3-eagle:PIN_3X8 | 1
X1 | FABC96R | memory-v1.3-eagle:FABC96R | 1
H1,H2 | M3 mounting hole 3.2 mm NPTH - board feature, NO PART (the adapter's standoffs) | MountingHole:MountingHole_3.2mm_M3 | 0
HW1 | M3 hex standoff 15 mm female-female (5.5 mm across flats) | hardware | 2
HW2 | M3 x 6 mm screw (2 above the adapter, 2 under the card) | hardware | 4
HW3 | M3 flat washer 7 mm OD | hardware | 4
HW4 | 40-wire IDE ribbon ~5-8 cm between two 40-way IDC plugs, crimped alike (pin 1 to pin 1); pin 20 OPEN on the J2 plug (or pull J2 pin 20) | hardware | 1
HW5 | adapter power cable J3 (+5V G G nc) -> the adapter's four power pads (floppy order +5V G G +12V): straight through, pin 1 to pin 1; find the adapter's pin-1 pad | hardware | 1
HW6 | HX-2118P CF-to-IDE adapter (40-pin male header, no pin 20) | hardware | 1
