ksr/YACC1-D/migration/inventory-2026-09-20.txt

indexed 10550 files; dataless (not on disk): 0; unreadable: 0
