ksr/YACC1-D/archive/gen1-2015-2018/YACC1A1/Old/4 reg no inc-dec-PROD-V1.1/regsimple2addfp-bom.txt

Partlist exported from /Users/ksr77/Library/Mobile Documents/com~apple~CloudDocs/eagle/YACC1A/Prod V1.0/4 reg no inc:dec-PROD-V1.0/regsimple2addfp.sch at 5/26/16 10:07 AM

Part        Value    Device          Package      Description                                               MF MPN OC_FARNELL OC_NEWARK
ADDOUT-SEL           PINHD-2X4       2X04         PIN HEADER                                                                           
ADDRCLK-SEL          PINHD-2X4       2X04         PIN HEADER                                                                           
C1                   C-US025-040X050 C025-040X050 CAPACITOR, American symbol                                                           
C2                   C-US025-040X050 C025-040X050 CAPACITOR, American symbol                                                           
C3                   C-US025-040X050 C025-040X050 CAPACITOR, American symbol                                                           
C4                   C-US025-040X050 C025-040X050 CAPACITOR, American symbol                                                           
C21                  C-US025-040X050 C025-040X050 CAPACITOR, American symbol                                                           
C22                  C-US025-040X050 C025-040X050 CAPACITOR, American symbol                                                           
C23                  C-US025-040X050 C025-040X050 CAPACITOR, American symbol                                                           
C24                  C-US025-040X050 C025-040X050 CAPACITOR, American symbol                                                           
C25                  C-US025-040X050 C025-040X050 CAPACITOR, American symbol                                                           
C26                  C-US025-040X050 C025-040X050 CAPACITOR, American symbol                                                           
C27                  C-US025-040X050 C025-040X050 CAPACITOR, American symbol                                                           
C28                  C-US025-040X050 C025-040X050 CAPACITOR, American symbol                                                           
C29                  C-US025-040X050 C025-040X050 CAPACITOR, American symbol                                                           
C30                  C-US025-040X050 C025-040X050 CAPACITOR, American symbol                                                           
C31                  C-US025-040X050 C025-040X050 CAPACITOR, American symbol                                                           
C32                  C-US025-040X050 C025-040X050 CAPACITOR, American symbol                                                           
C33                  C-US025-040X050 C025-040X050 CAPACITOR, American symbol                                                           
C34                  C-US025-040X050 C025-040X050 CAPACITOR, American symbol                                                           
C35                  C-US025-040X050 C025-040X050 CAPACITOR, American symbol                                                           
C36                  C-US025-040X050 C025-040X050 CAPACITOR, American symbol                                                           
C37                  C-US025-040X050 C025-040X050 CAPACITOR, American symbol                                                           
C38                  C-US025-040X050 C025-040X050 CAPACITOR, American symbol                                                           
C39                  C-US025-040X050 C025-040X050 CAPACITOR, American symbol                                                           
C40                  C-US025-040X050 C025-040X050 CAPACITOR, American symbol                                                           
IC1         74S374N  74S374N         DIL20        Octal D type transparent LATCH, edge triggered                                       
IC2         74S374N  74S374N         DIL20        Octal D type transparent LATCH, edge triggered                                       
IC3         74S374N  74S374N         DIL20        Octal D type transparent LATCH, edge triggered                                       
IC4         74S374N  74S374N         DIL20        Octal D type transparent LATCH, edge triggered                                       
IC5         74S374N  74S374N         DIL20        Octal D type transparent LATCH, edge triggered                                       
IC6         74S374N  74S374N         DIL20        Octal D type transparent LATCH, edge triggered                                       
IC7         74S374N  74S374N         DIL20        Octal D type transparent LATCH, edge triggered                                       
IC8         74S374N  74S374N         DIL20        Octal D type transparent LATCH, edge triggered                                       
IC9         74LS139N 74LS139N        DIL16        Dual 2-line to 4-line DECODER/DEMULTIPLEXER                                          
IC10        7432N    7432N           DIL14        Quad 2-input OR gate                                                                 
IC11        74LS139N 74LS139N        DIL16        Dual 2-line to 4-line DECODER/DEMULTIPLEXER                                          
IC12        74LS02N  74LS02N         DIL14        Quad 2-input NOR gate                                                                
IC13        74LS04N  74LS04N         DIL14        Hex INVERTER                                                                         
IC14        7432N    7432N           DIL14        Quad 2-input OR gate                                                                 
IC15        74LS02N  74LS02N         DIL14        Quad 2-input NOR gate                                                                
IC16        74S374N  74S374N         DIL20        Octal D type transparent LATCH, edge triggered                                       
IC17        74S374N  74S374N         DIL20        Octal D type transparent LATCH, edge triggered                                       
IC18        74LS139N 74LS139N        DIL16        Dual 2-line to 4-line DECODER/DEMULTIPLEXER                                          
IC19        74LS00N  74LS00N         DIL14        Quad 2-input NAND gate                                                               
IC20        74LS00N  74LS00N         DIL14        Quad 2-input NAND gate                                                               
IC29        74LS245N 74LS245N        DIL20        Octal BUS TRANSCEIVER, 3-state                                                       
IC30        74LS245N 74LS245N        DIL20        Octal BUS TRANSCEIVER, 3-state                                                       
IC31        74LS245N 74LS245N        DIL20        Octal BUS TRANSCEIVER, 3-state                                                       
IC41        74S244N  74S244N         DIL20        Octal BUFFER and LINE DRIVER, 3-state                                                
JP5                  PINHD-2X14      2X14         PIN HEADER                                                                           
RD-BRDSEL            PINHD-2X4       2X04         PIN HEADER                                                                           
RN3                  RNX8            RN-9         RESISTOR NETWORK                                                 unknown    unknown  
RN4                  RNX8            RN-9         RESISTOR NETWORK                                                 unknown    unknown  
WR-BRDSEL            PINHD-2X4       2X04         PIN HEADER                                                                           
X1          FABC96R  FABC96R         FABC96R      CONNECTOR female, 96 pins, type R, rows ABC, grid 2.54 mm
