ksr/YACC1-D/archive/gen1-2015-2018/YACC1A1/Old/alu conv accum to shift/alu2-bom.txt

Partlist exported from /Users/ksr77/Library/Mobile Documents/com~apple~CloudDocs/eagle/YACC1A/Working/alu/alu2.sch at 5/26/16 10:17 AM

Part Value    Device   Package Description                                               MF MPN OC_FARNELL OC_NEWARK
IC1  74LS83N  74LS83N  DIL16   4-bit binary full ADDER, fast carry                                                  
IC2  74LS83N  74LS83N  DIL16   4-bit binary full ADDER, fast carry                                                  
IC3  74LS244N 74LS244N DIL20   Octal BUFFER and LINE DRIVER, 3-state                                                
IC4  74LS138N 74LS138N DIL16   3-line to 8-line DECODER/DEMULTIPLEXER                                               
IC5  74LS32N  74LS32N  DIL14   Quad 2-input OR gate                                                                 
IC6  74LS32N  74LS32N  DIL14   Quad 2-input OR gate                                                                 
IC7  74LS08N  74LS08N  DIL14   Quad 2-input AND gate                                                                
IC8  74LS86N  74LS86N  DIL14   Quad 2-input EXCLUSIV-OR (XOR) gate                                                  
IC9  74LS86N  74LS86N  DIL14   Quad 2-input EXCLUSIV-OR (XOR) gate                                                  
IC10 74LS08N  74LS08N  DIL14   Quad 2-input AND gate                                                                
IC11 74LS86N  74LS86N  DIL14   Quad 2-input EXCLUSIV-OR (XOR) gate                                                  
IC12 74LS86N  74LS86N  DIL14   Quad 2-input EXCLUSIV-OR (XOR) gate                                                  
IC13 74LS244N 74LS244N DIL20   Octal BUFFER and LINE DRIVER, 3-state                                                
IC14 74LS244N 74LS244N DIL20   Octal BUFFER and LINE DRIVER, 3-state                                                
IC15 74LS244N 74LS244N DIL20   Octal BUFFER and LINE DRIVER, 3-state                                                
IC16 74LS240N 74LS240N DIL20   Octal BUFFER and LINE DRIVER, 3-state                                                
IC17 74LS244N 74LS244N DIL20   Octal BUFFER and LINE DRIVER, 3-state                                                
IC18 74LS244N 74LS244N DIL20   Octal BUFFER and LINE DRIVER, 3-state                                                
IC19 74LS374N 74LS374N DIL20   Octal D type transparent LATCH, edge triggered                                       
IC20 74LS244N 74LS244N DIL20   Octal BUFFER and LINE DRIVER, 3-state                                                
IC21 74LS244N 74LS244N DIL20   Octal BUFFER and LINE DRIVER, 3-state                                                
IC22 74LS85N  74LS85N  DIL16   4-bit magnitude COMPARATOR                                                           
IC23 74LS85N  74LS85N  DIL16   4-bit magnitude COMPARATOR                                                           
IC24 74ALS04N 74ALS04N DIL14   Hex INVERTER                                                                         
IC25 74LS32N  74LS32N  DIL14   Quad 2-input OR gate                                                                 
IC26 74LS251N 74LS251N DIL16   1 of 8 data SELECTOR/MULTIPLEXER, 3-state                                            
IC27 74LS86N  74LS86N  DIL14   Quad 2-input EXCLUSIV-OR (XOR) gate                                                  
IC28 74LS192N 74LS192N DIL16   Synchronous 4-bit UP/DOWN COUNTER                                                    
IC29 74LS192N 74LS192N DIL16   Synchronous 4-bit UP/DOWN COUNTER                                                    
IC30 74LS192N 74LS192N DIL16   Synchronous 4-bit UP/DOWN COUNTER                                                    
IC31 74LS192N 74LS192N DIL16   Synchronous 4-bit UP/DOWN COUNTER                                                    
IC32 74LS244N 74LS244N DIL20   Octal BUFFER and LINE DRIVER, 3-state                                                
IC33 74LS245N 74LS245N DIL20   Octal BUS TRANSCEIVER, 3-state                                                       
IC34 74LS244N 74LS244N DIL20   Octal BUFFER and LINE DRIVER, 3-state                                                
IC35 74LS245N 74LS245N DIL20   Octal BUS TRANSCEIVER, 3-state                                                       
IC39 74LS00N  74LS00N  DIL14   Quad 2-input NAND gate                                                               
IC41 74LS245N 74LS245N DIL20   Octal BUS TRANSCEIVER, 3-state                                                       
RN3           RNX8     RN-9    RESISTOR NETWORK                                                 unknown    unknown  
RN4           RNX8     RN-9    RESISTOR NETWORK                                                 unknown    unknown  
V1   744078N  744078N  DIL14   8-input OR/NOR, complementary outputs                                                
V2   744078N  744078N  DIL14   8-input OR/NOR, complementary outputs                                                
X1   FABC96R  FABC96R  FABC96R CONNECTOR female, 96 pins, type R, rows ABC, grid 2.54 mm
