ksr/YACC1-D/hardware/cards/memory/kicad/v2.0/reports/memory-v2.0-make.txt

make-e: memory-v2.0.kicad_pcb from final-e.kicad_pcb; 0 via(s) were imported as buried/blind -> through; taken off: {'silk corner marks': 8, 'User.Drawings': 50, 'option silk texts': 5}
cleanup: 0 via(s) removed []; 69 kept (why, per side tried: {'a track of another net there': 66, 'the run does not end on a pad or via': 12, 'a T-junction on the run': 4, 'a pad of another net there': 1}); 2049 -> 2038 track segments (collinear merged); every via a through via
adapter outline on the silkscreen: 15 pieces (cut around pads, vias and other silk)
silk tidy: 51 text(s) moved ['ref:R13 2.0 mm', 'ref:IC2 0.3 mm', 'ref:R2 1.1 mm (turned upright)', 'ref:C11 0.3 mm', 'ref:C28 2.3 mm', 'ref:C2 0.3 mm', 'ref:RN7 0.5 mm', 'ref:RN8 0.5 mm', 'ref:X1 0.3 mm', 'ref:C10 0.3 mm', 'ref:C14 0.3 mm', 'ref:IC8 1.8 mm', 'ref:R11 2.0 mm', 'ref:R14 0.5 mm', 'ref:JP2 2.7 mm', 'ref:C1 0.3 mm', 'ref:C16 0.3 mm', 'ref:IC28 0.3 mm', 'ref:C8 0.3 mm', 'ref:IC10 0.5 mm', 'ref:R10 2.0 mm', 'ref:C6 0.3 mm', 'ref:C18 0.3 mm', 'ref:C9 0.3 mm', 'ref:C5 0.3 mm', 'ref:C15 0.3 mm', 'ref:R12 2.0 mm', 'ref:J2 3.3 mm', 'ref:C12 0.3 mm', 'ref:C13 0.3 mm', 'ref:C7 0.3 mm', 'ref:C3 0.3 mm', 'ref:C4 0.3 mm', 'ref:C19 0.3 mm', 'ref:C24 2.6 mm', 'ref:C17 0.3 mm', 'ref:LED1 5.1 mm', 'gr:nc@165.070,50.680 0.3 mm', 'gr:G@162.530,50.680 0.3 mm', 'gr:G@159.990,50.680 0.3 mm', 'gr:+5V@157.450,50.680 0.3 mm', 'gr:PWR@188.695,120.190 0.5 mm', 'gr:CF CARD INSERTS HERE@194.090,67.900 0.3 mm', 'gr:ADAPTER PIN 1@152.140,108.900 3.0 mm', 'gr:IDE@140.020,85.900 6.6 mm', 'gr:PIN 1@149.350,110.030 2.8 mm', 'gr:0X8000@100.300,19.860 0.3 mm', 'gr:0XF000@121.890,18.590 0.5 mm', 'gr:Gnd@29.210,14.780 0.3 mm', 'gr:ROM@109.190,17.320 0.5 mm', 'gr:RAM@109.190,26.210 0.5 mm']
