ksr/YACC1-D/hardware/cards/memory/kicad/v2.0/options-top-edge-J2/reports/memory-v2.0-make.txt

make: memory-v2.0.kicad_pcb from memory-v2.0-relayout-b-trial.kicad_pcb; 43 via(s) were imported as buried/blind -> through
cleanup: 0 via(s) removed []; 43 kept (why, per side tried: {'a track of another net there': 43, 'a pad of another net there': 2, 'the run does not end on a pad or via': 2, 'a T-junction on the run': 2}); 1801 -> 1794 track segments (collinear merged); every via a through via
silk tidy: 46 text(s) moved ['ref:C4 0.3 mm', 'ref:C20 0.3 mm', 'ref:J2 0.3 mm', 'ref:C8 3.1 mm', 'ref:C16 0.3 mm', 'ref:IC12 0.3 mm', 'ref:C11 0.3 mm', 'ref:R13 2.0 mm', 'ref:C21 1.0 mm', 'ref:C22 2.4 mm', 'ref:C10 0.3 mm', 'ref:IC7 1.5 mm', 'ref:C27 1.0 mm', 'ref:C17 0.3 mm', 'ref:C1 0.3 mm', 'ref:C2 0.3 mm', 'ref:RN8 0.5 mm', 'ref:C5 0.6 mm', 'ref:RN7 0.5 mm', 'ref:C15 0.3 mm', 'ref:C18 0.3 mm', 'ref:C7 0.3 mm', 'ref:C19 0.3 mm', 'ref:C3 0.3 mm', 'ref:C6 0.3 mm', 'ref:C12 0.3 mm', 'ref:R2 1.0 mm (turned upright)', 'ref:PWR0 2.6 mm', 'ref:C13 0.3 mm', 'ref:C24 2.6 mm', 'ref:X1 0.3 mm', 'ref:LED1 5.1 mm', 'ref:JP2 1.8 mm', 'ref:C14 0.3 mm', 'ref:R11 2.0 mm', 'ref:C23 0.3 mm', 'ref:C9 0.3 mm', 'gr:nc@190.590,31.290 0.5 mm', 'gr:G@190.590,28.750 0.5 mm', 'gr:G@190.590,26.210 0.5 mm', 'gr:+5V@190.590,23.670 0.5 mm', 'gr:0X8000@100.300,19.860 0.3 mm', 'gr:0XF000@121.890,18.590 0.5 mm', 'gr:Gnd@29.210,14.780 0.3 mm', 'gr:ROM@109.190,17.320 0.5 mm', 'gr:RAM@109.190,26.210 0.5 mm']
