ksr/YACC1-D/archive/superseded-revisions/software-old-obsolete/Assembler-old/Readme.md

Classic assembler - Takes a .asm file and generates a .img file

asm.doc and asm.txt have more info

yacc1.def contains the definitions of the YACC1 instruction set
