ksr/YACC1-D/archive/gen1-2015-2018/YACC1-BACKUP/Build notes and revisions.rtf

Build Notes

PCB generation process

board name & version (location)
onepagecomputer.com (location)
power led
connector is centered at 2.25

Board size is 7 inches x 4.5 inches (177.8 * 114.3)

Design Changes
1) Remove address latch register from register file
recover bus pins & men cantle pins
update 1.2 bus definition
on definition
cards in progress or prod

2) add temp 8 bit latch to sequencer card to facilitate men to men transfer

3) convert reg card to 8 registers
modify bus definition to 3 bits register select, 1 bit board select
modify bus definition + all cords in process

4) Reduce to 8 registers only, jumper to hold the now 1 bit board select to 0
maybe add jumpers so reg selection is 3 bit, tie upper bit to 0

5) TESTER Board
probably (almost for sure) do not need individual pull-ups for CNTL chips

Gerber File
Copper
CMP
LY2 (4 layer)
LY15 (4 layer)
SOL

Silk Screen
PLS

Stop Masks
Top
STC
Bottom
STS

Drill file
DRD

Test
