ksr/YACC1-D/archive/gen1-2015-2018/YACC1A/PCB Build notes.rtfd/TXT.rtf

PCB generation process

DRU File
USE YACC1-…
Update 2 layer to match YACC1… 4 layer file

1. board name & version (location)
2. onepagecomputer.com (location)
3. power led (location) POWER LED .15” from edge x+y, flat edge of LED down
4. connector is centered at 2.25 x ???

Board size is 7 inches x 4.5 inches (177.8 * 114.3)

Gerber Files

document gerber file generation process

Layers as suggested (default) not 27

Copper
CMP
LY2 (4 layer)
LY15 (4 layer)
SOL

Silk Screen
PLS

Stop Masks
Top
STC
Bottom
STS

Drill file
DRD

Layout
¬
