ksr/YACC1-D/docs/bom/bus-tester.md

# BOM: Bus Test Card v1.1

GENERATED by `tools/gen_bom.py` on 2026-09-23 from `hardware/cards/bus-tester/eagle/v1.1/tester.sch` (Eagle 9.6.2) - do not edit; edit the schematic and re-run `make bom`.  
Role: bench. plugged in for bring-up sessions.

86 parts (10 ICs, 42 passives, 5 connectors/headers/jumpers, 29 others); 39 supply/frame symbols skipped. Value = the schematic's value attribute, or the deviceset with the Eagle technology substituted for `*` (a `*` left in a value means the schematic names no technology: the part number was never filled in).

## Parts by designator

| Designator | Value | Device (deviceset/device) | Package | Library | Technology | Class |
|---|---|---|---|---|---|---|
| BUS-RESET | SWITCH-MOMENTARY-2 | SWITCH-MOMENTARY-2/SIDE_EZ | TACTILE-PTH-SIDEEZ | SparkFun-Electromechanical |  | other |
| C1 | 0.1 | C-US/025-024X044 | C025-024X044 | adafruit |  | passive |
| C2 | 0.1 | C-US/025-024X044 | C025-024X044 | adafruit |  | passive |
| C3 | 0.1 | C-US/025-024X044 | C025-024X044 | adafruit |  | passive |
| C4 | 0.1 | C-US/025-024X044 | C025-024X044 | adafruit |  | passive |
| C5 | 0.1 | C-US/025-024X044 | C025-024X044 | adafruit |  | passive |
| C6 | 20pf | C-US/025-024X044 | C025-024X044 | adafruit |  | passive |
| C7 | 20pf | C-US/025-024X044 | C025-024X044 | adafruit |  | passive |
| C8 | 0.1 | C-US/025-024X044 | C025-024X044 | adafruit |  | passive |
| C9 | 0.1 | C-US/025-024X044 | C025-024X044 | adafruit |  | passive |
| C10 | 0.1 | C-US/025-024X044 | C025-024X044 | adafruit |  | passive |
| C11 | 0.1 | C-US/025-024X044 | C025-024X044 | adafruit |  | passive |
| C12 | 0.1 | C-US/025-024X044 | C025-024X044 | adafruit |  | passive |
| C13 | 0.1 | C-US/025-024X044 | C025-024X044 | adafruit |  | passive |
| CPU-RESET | TS-1109-7 | DIP-BUTTON-TOP-BLACK(4P-D6.2MM) | SW4-6.2X6.2X5.0MM | Seeed-OPL-Switch |  | other |
| DTR-RESET | JP1E | JP1E | JP1 | jumper |  | connector |
| FTDI-VCC | JP1E | JP1E | JP1 | jumper |  | connector |
| IC1 | MCP23017 | MCP23017/SP | DIL28-3 | microchip |  | IC |
| IC2 | MCP23017 | MCP23017/SP | DIL28-3 | microchip |  | IC |
| IC3 | MCP23017 | MCP23017/SP | DIL28-3 | microchip |  | IC |
| IC4 | MCP23017 | MCP23017/SP | DIL28-3 | microchip |  | IC |
| IC5 | MCP23017 | MCP23017/SP | DIL28-3 | microchip |  | IC |
| IC6 | MCP23017 | MCP23017/SP | DIL28-3 | microchip |  | IC |
| IC7 | 24AA01 | 24*/P | DIL8 | microchip | AA01 | IC |
| IC8 | 74LS374 | 74*374/N | DIL20 | 74xx-us | LS | IC |
| IC9 | 74LS244 | 74*244/N | DIL20 | 74xx-us | LS | IC |
| IC10 | ATMEGA328P_PDIP | ATMEGA328P_PDIP | DIL28-3 | SparkFun-DigitalIC |  | IC |
| IN | M9040P | M9040P | M9040P | switch |  | other |
| JP1 | FTDI_DEVICE | FTDI_DEVICE | FTDI_DEVICE_SIDE | SparkFun-Connectors |  | connector |
| JP2 | PINHD-1X3 | PINHD-1X3 | 1X03 | pinhead |  | connector |
| L0 | LED | LED/5MM | LED5MM | led |  | other |
| L1 | LED | LED/5MM | LED5MM | led |  | other |
| L2 | LED | LED/5MM | LED5MM | led |  | other |
| L3 | LED | LED/5MM | LED5MM | led |  | other |
| L4 | LED | LED/5MM | LED5MM | led |  | other |
| L5 | LED | LED/5MM | LED5MM | led |  | other |
| L6 | LED | LED/5MM | LED5MM | led |  | other |
| L7 | LED | LED/5MM | LED5MM | led |  | other |
| LED1 | LED | LED/5MM | LED5MM | led |  | other |
| LED2 | LED | LED/5MM | LED5MM | led |  | other |
| LED3 | LED | LED/5MM | LED5MM | led |  | other |
| LED4 | LED | LED/5MM | LED5MM | led |  | other |
| LED5 | LED | LED/5MM | LED5MM | led |  | other |
| OUT | LED | LED/5MM | LED5MM | led |  | other |
| PWR | LED | LED/5MM | LED5MM | led |  | other |
| Q1 | 16Mhz | CRYSTAL/HC49S | HC49/S | crystal |  | other |
| R1 | 330 | R/0207/10 | 0207/10 | eagle-ltspice |  | passive |
| R2 | 10k | R-US_/0207/10 | 0207/10 | adafruit |  | passive |
| R3 | 10k | R-US_/0207/10 | 0207/10 | adafruit |  | passive |
| R4 | 10k | R-US_/0207/10 | 0207/10 | adafruit |  | passive |
| R5 | 10k | R-US_/0207/10 | 0207/10 | adafruit |  | passive |
| R6 | 10k | R-US_/0207/10 | 0207/10 | adafruit |  | passive |
| R7 | 10k | R-US_/0207/10 | 0207/10 | adafruit |  | passive |
| R8 | 10k | R-US_/0207/10 | 0207/10 | resistor |  | passive |
| R9 | 330 | R-US_/0207/10 | 0207/10 | resistor |  | passive |
| R10 | 2.2k | R-US_/0207/10 | 0207/10 | resistor |  | passive |
| R11 | 330 | R-US_/0207/10 | 0207/10 | resistor |  | passive |
| R12 | 2.2k | R-US_/0207/10 | 0207/10 | resistor |  | passive |
| R13 | 330 | R-US_/0207/10 | 0207/10 | resistor |  | passive |
| R14 | 330 | R-US_/0207/10 | 0207/10 | resistor |  | passive |
| R15 | 330 | R-US_/0207/10 | 0207/10 | resistor |  | passive |
| R16 | 330 | R-US_/0207/10 | 0207/10 | resistor |  | passive |
| R17 | 330 | R-US_/0207/10 | 0207/10 | resistor |  | passive |
| R18 | 330 | R-US_/0207/10 | 0207/10 | resistor |  | passive |
| R19 | 330 | R-US_/0207/10 | 0207/10 | resistor |  | passive |
| R20 | 330 | R-US_/0207/10 | 0207/10 | resistor |  | passive |
| R21 | 330 | R-US_/0207/10 | 0207/10 | resistor |  | passive |
| R22 | 330 | R-US_/0207/10 | 0207/10 | resistor |  | passive |
| R23 | 330 | R-US_/0207/10 | 0207/10 | resistor |  | passive |
| R24 | 330 | R-US_/0207/10 | 0207/10 | resistor |  | passive |
| R25 | 10k | R-US_/0207/10 | 0207/10 | resistor |  | passive |
| RN1 | RNX8 | RNX8 | RN-9 | resistor-net |  | passive |
| RN2 | RNX8 | RNX8 | RN-9 | resistor-net |  | passive |
| RN3 | RNX8 | RNX8 | RN-9 | resistor-net |  | passive |
| RN4 | RNX8 | RNX8 | RN-9 | resistor-net |  | passive |
| S0 | M9040P | M9040P | M9040P | switch |  | other |
| S1 | M9040P | M9040P | M9040P | switch |  | other |
| S2 | M9040P | M9040P | M9040P | switch |  | other |
| S3 | M9040P | M9040P | M9040P | switch |  | other |
| S4 | M9040P | M9040P | M9040P | switch |  | other |
| S5 | M9040P | M9040P | M9040P | switch |  | other |
| S6 | M9040P | M9040P | M9040P | switch |  | other |
| S7 | M9040P | M9040P | M9040P | switch |  | other |
| S-A | 9070-1W | 9070-1W | 9070-1W | switch |  | other |
| S-B | 9070-1W | 9070-1W | 9070-1W | switch |  | other |
| X1 | FABC96R | FABC96R | FABC96R | con-vg |  | connector |

## Order list (value + package)

| Qty | Value | Package | Designators |
|---|---|---|---|
| 15 | 330 | 0207/10 | R1, R9, R11, R13, R14, R15, R16, R17, R18, R19, R20, R21, R22, R23, R24 |
| 15 | LED | LED5MM | L0, L1, L2, L3, L4, L5, L6, L7, LED1, LED2, LED3, LED4, LED5, OUT, PWR |
| 11 | 0.1 | C025-024X044 | C1, C2, C3, C4, C5, C8, C9, C10, C11, C12, C13 |
| 9 | M9040P | M9040P | IN, S0, S1, S2, S3, S4, S5, S6, S7 |
| 8 | 10k | 0207/10 | R2, R3, R4, R5, R6, R7, R8, R25 |
| 6 | MCP23017 | DIL28-3 | IC1, IC2, IC3, IC4, IC5, IC6 |
| 4 | RNX8 | RN-9 | RN1, RN2, RN3, RN4 |
| 2 | 2.2k | 0207/10 | R10, R12 |
| 2 | 20pf | C025-024X044 | C6, C7 |
| 2 | 9070-1W | 9070-1W | S-A, S-B |
| 2 | JP1E | JP1 | DTR-RESET, FTDI-VCC |
| 1 | 16Mhz | HC49/S | Q1 |
| 1 | 24AA01 | DIL8 | IC7 |
| 1 | 74LS244 | DIL20 | IC9 |
| 1 | 74LS374 | DIL20 | IC8 |
| 1 | ATMEGA328P_PDIP | DIL28-3 | IC10 |
| 1 | FABC96R | FABC96R | X1 |
| 1 | FTDI_DEVICE | FTDI_DEVICE_SIDE | JP1 |
| 1 | PINHD-1X3 | 1X03 | JP2 |
| 1 | SWITCH-MOMENTARY-2 | TACTILE-PTH-SIDEEZ | BUS-RESET |
| 1 | TS-1109-7 | SW4-6.2X6.2X5.0MM | CPU-RESET |
