ksr/YACC1-D/tests/assembler/test_output.txt

RC/asm v2.2
by Michael H. Riley

yacc1 -> Native
2 Classes read.
92 Patterns read.
    1 0000:             
    2 0000:             ;
    3 0000:             ; Hardware info
    4 0000:             UARTA0:       EQU 000h
    5 0000:             UARTA1:       EQU 008h
    6 0000:             UARTA2:       EQU 010h
    7 0000:             UARTA3:       EQU 018h
    8 0000:             UARTA4:       EQU 020h
    9 0000:             UARTA5:       EQU 028h
   10 0000:             UARTA6:       EQU 030h
   11 0000:             UARTA7:       EQU 038h
   12 0000:             
   13 0000:             SWITCHLED:    EQU 001H
   14 0000:             LCDENABLE:    EQU 002H
   15 0000:             LCDREGISTER:  EQU 004H
   16 0000:             UARTCS:       EQU 040H
   17 0000:             TIL311:       EQU 080H
   18 0000:             
   19 0000:             CNTL-PORT:    EQU "P0"
   20 0000:             DATAPORT:     EQU "P1"
   21 0000:             
   22 0000:             ;
   23 0000:             ; Basic interpreter tokens
   24 0000:             ;
   25 0000:             TOKENIZER_ERROR: EQU 00
   26 0000:             TOKENIZER_EOF: EQU 01
   27 0000:             TOKENIZER_NUMBER: EQU 02
   28 0000:             TOKENIZER_STRING: EQU 03
   29 0000:             TOKENIZER_VARIABLE: EQU 04
   30 0000:             TOKENIZER_LET: EQU 05
   31 0000:             TOKENIZER_PRINT: EQU 06
   32 0000:             TOKENIZER_IF: EQU 07
   33 0000:             TOKENIZER_THEN: EQU 08
   34 0000:             TOKENIZER_ELSE: EQU 09
   35 0000:             TOKENIZER_FOR: EQU 10
   36 0000:             TOKENIZER_TO: EQU 11
   37 0000:             TOKENIZER_NEXT: EQU 12
   38 0000:             TOKENIZER_GOTO: EQU 13
   39 0000:             TOKENIZER_GOSUB: EQU 14
   40 0000:             TOKENIZER_RETURN: EQU 15
   41 0000:             TOKENIZER_CALL: EQU 16
   42 0000:             TOKENIZER_REM: EQU 17
   43 0000:             TOKENIZER_PEEK: EQU 18
   44 0000:             TOKENIZER_POKE: EQU 19
   45 0000:             TOKENIZER_END: EQU 20
   46 0000:             TOKENIZER_COMMA: EQU 21
   47 0000:             TOKENIZER_SEMICOLON: EQU 22
   48 0000:             TOKENIZER_PLUS: EQU 23
   49 0000:             TOKENIZER_MINUS: EQU 24
   50 0000:             TOKENIZER_AND: EQU 25
   51 0000:             TOKENIZER_OR: EQU 26
   52 0000:             TOKENIZER_ASTR: EQU 27
   53 0000:             TOKENIZER_SLASH: EQU 28
   54 0000:             TOKENIZER_MOD: EQU 29
   55 0000:             TOKENIZER_HASH: EQU 30
   56 0000:             TOKENIZER_LEFTP: EQU 31
   57 0000:             TOKENIZER_RIGHTP: EQU 32
   58 0000:             TOKENIZER_LT: EQU 33
   59 0000:             TOKENIZER_GT: EQU 34
   60 0000:             TOKENIZER_EQ: EQU 35
   61 0000:             TOKENIZER_CR: EQU 36
   62 0000:             TOKENIZER_LINENUM: EQU 37
   63 0000:             
   64 0000:             ;
   65 0000:             ; MONITOR MODES
   66 0000:             ;
   67 0000:             NOMODE:       EQU 0
   68 0000:             EXAMINEMODE:  EQU 1
   69 0000:             DUMPMODE:     EQU 2
   70 0000:             BLOCKMODE:    EQU 3
   71 0000:             FILLMODE:     EQU 4
   72 0000:             
   73 0000:             ;
   74 0000:             ; Setup Stack, use R1
   75 0000:             ;
   76 0000:             STACK: EQU 0FFFh
   77 0000:             
   78 0000:             ;
   79 0000:             ; remap eprom from 0x0000 to 0xf000 by initial access to 0xf003 via BRanch
   80 0000:             ;
   81 0000:                      ORG 0f000h
   82 f000: a0 f0 03             BR eprom
   83 f003:                      ORG 0f003h
   84 f003:             eprom:
   85 f003:             ;
   86 f003:             ; Setup Stack
   87 f003:             ;
   88 f003: 19 0f ff             MVIW R1,STACK
   89 f006:             
   90 f006:             ;
   91 f006:             ; BASIC interpreter user variables area
   92 f006:             ; currently 26 1-byte variables
   93 f006:             ; for now must be 0xAA00 (256 byte) aligned
   94 f006:             ;
   95 f006:             BASIC_VARS: EQU 0100h
   96 f006:             
   97 f006:             ;
   98 f006:             ; Basic interpreter internal variables
   99 f006:             ;
  100 f006:             emu_mode: EQU 01f0H
  101 f006:             ;
  102 f006:             bas_ended: EQU 0200h
  103 f006:             
  104 f006:             ;
  105 f006:             ; for next statement stack ptr and stack data
  106 f006:             ;
  107 f006:             ; for next stack data
  108 f006:             ; format
  109 f006:             ;   2 bytes for variable id (only first byte used for now)
  110 f006:             ;   2 bytes to value (upper value) (format HL) (only first byte used for now)
  111 f006:             ;   2 bytes ptr to line after for instruction (format HL)
  112 f006:             ; later add step amount
  113 f006:             ;
  114 f006:             bas_forstackptr: EQU 0202h
  115 f006:             bas_forstack: EQU 0204h
  116 f006:             
  117 f006:             ;
  118 f006:             ; gosub stack ptr and data
  119 f006:             ;
  120 f006:             ; gosub STACK
  121 f006:             ; format
  122 f006:             ;   2 bytes return location ptr
  123 f006:             ;
  124 f006:             bas_gosubptr: EQU 0240h
  125 f006:             bas_gosubstack: EQU 0242h
  126 f006:             
  127 f006:             ;
  128 f006:             ; Basic interpreter text line buffer
  129 f006:             ;
  130 f006:             parse_input_line: EQU 300h
  131 f006:             parse_token_buffer: EQU 400h
  132 f006:             
  133 f006:             ;
  134 f006:             ; basic interpreter, add IO and peek/poke
  135 f006:             ;
  136 f006:             
  137 f006:             ;
  138 f006:             ; SERIAL OUT SETUP
  139 f006:             ;
  140 f006: 70 58                OUTI  P0,(UARTA3!UARTCS)
  141 f008: 71 80                OUTI  P1,080H
  142 f00a:             
  143 f00a: 70 40                OUTI  P0,(UARTA0!UARTCS)
  144 f00c: 71 0c                OUTI  P1,12
  145 f00e:             
  146 f00e: 70 48                OUTI  P0,(UARTA1!UARTCS)
  147 f010: 71 00                OUTI  P1,00
  148 f012:             
  149 f012: 70 58                OUTI  P0,(UARTA3!UARTCS)
  150 f014: 71 03                OUTI  P1,03H
  151 f016:             
  152 f016:             ; Set intial monitor mode
  153 f016:             
  154 f016: 16 00                MVIB R6,NOMODE
  155 f018:             ;
  156 f018:             ; Main
  157 f018:             ;
  158 f018: 04 f7 e2              JSR lblink
  159 f01b: 1a f8 08              MVIW R2,hello
  160 f01e: 04 f7 60              JSR stringout
  161 f021:             ;
  162 f021:             ; additional proof of life
  163 f021:             ;
  164 f021:             ; show first 16 bytes of ROM & REGISTERS
  165 f021:             ;
  166 f021: 1b f0 00             MVIW R3,0f000h
  167 f024: 04 f6 4f             JSR showaddr
  168 f027: 04 f6 eb             JSR show16
  169 f02a: 04 f6 b6             JSR showregs
  170 f02d: 1a f8 28             MVIW R2,CRLF
  171 f030: 04 f7 60             JSR stringout
  172 f033:             ;
  173 f033:             ; show test code addr to use with go command
  174 f033:             ;
  175 f033: 1b f0 42             MVIW R3,tttt
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
 1783 e044:             exe:
 1784 e044:             
 1785 e044:             ;
 1786 e044:             ; void ubasic_init()
 1787 e044:             ;
 1788 e044:             ; Setup basic interpreter execution engine
 1789 e044:             ;
 1790 e044:             ; destorys R4 and accumulator
 1791 e044:             ; ?? Should these pointers be zero based or actual address in memory
 1792 e044:             ;
 1793 e044:             exe_init:
 1794 e044: 1d 02 42        MVIW R5,bas_gosubstack
 1795 e047:             ;    movrr r6,r9
 1796 e047: 1c 02 04        MVIW R4,bas_forstack
 1797 e04a:             ;    movrr r6,r8
 1798 e04a: 1e 02 00        MVIW R6,bas_ended
 1799 e04d: 0e 00           LDAI 0
 1800 e04f: 4e              STAVR R6
 1801 e050:             ;
 1802 e050:             ; initialize tokenbufferptr to start of tokenBuffer (actual memory address)
 1803 e050:             ;
 1804 e050: 04 e3 b3        JSR tok_init
 1805 e053: 05              RET
 1806 e054:             
 1807 e054:             ;
 1808 e054:             ; void accept(int)
 1809 e054:             ;
 1810 e054:             ; compare accumulator with current token then advance to next token in buffer
 1811 e054:             ; assume accumulator destroyed
 1812 e054:             ;
 1813 e054:             exe_accept:
 1814 e054: 09              push
 1815 e055:             ;
 1816 e055:             ; get current token into accumulator
 1817 e055:             ;
 1818 e055: 04 e3 b1        jsr tok_token
 1819 e058: 0b              MVAT
 1820 e059: 0a              POP
 1821 e05a: a8 e0 63        BREQ exe_accept_done
 1822 e05d: 1a e0 00        mviw r2,bas_msg1
 1823 e060: 04 e3 b0        JSR bas_error
 1824 e063:             exe_accept_done:
 1825 e063: 04 e3 b7        jsr tok_next
 1826 e066: 05              RET
 1827 e067:             
 1828 e067:             ;
 1829 e067:             ; int varfactor()
 1830 e067:             ;
 1831 e067:             ; get variable id pointed to by tok_variable_num in token stream
 1832 e067:             ; (this is not a value but a variable id)
 1833 e067:             ; value returned by exe_get_variable in r7
 1834 e067:             ;
 1835 e067:             ; return value in R7
 1836 e067:             ;
 1837 e067:             exe_varfactor:
 1838 e067:             ; get variable number id (one byte for now a-z) into accumulator
 1839 e067:             ;
 1840 e067: 04 e3 f0        jsr tok_variable_num
 1841 e06a:             ;
 1842 e06a:             ; variable id in accumulator, return in r7
 1843 e06a:             ;
 1844 e06a: 04 e3 a6        jsr exe_get_variable
 1845 e06d: 0e 04           LDAI TOKENIZER_VARIABLE
 1846 e06f: 04 e0 54        JSR exe_accept
 1847 e072: 05              RET
 1848 e073:             
 1849 e073:             ;
 1850 e073:             ; int factor()
 1851 e073:             ; return value in R7
 1852 e073:             ;
 1853 e073:             exe_factor:
 1854 e073:             ;
 1855 e073:             ; get current token into accumulator
 1856 e073:             ;
 1857 e073: 04 e3 b1        jsr tok_token
 1858 e076:             ;
 1859 e076: 0d 02           LDTI TOKENIZER_NUMBER
 1860 e078: aa e0 83        BRNEQ exe_factor1
 1861 e07b: 04 e3 e7        JSR tok_num
 1862 e07e: 0c              MVTA
 1863 e07f: 04 e0 54        JSR exe_accept
 1864 e082: 05              RET
 1865 e083:             
 1866 e083:             exe_factor1:
 1867 e083: 0d 1f           LDTI TOKENIZER_LEFTP
 1868 e085: aa e0 94        BRNEQ exe_factor2
 1869 e088: 04 e0 54        JSR exe_accept
 1870 e08b: 04 e0 de        JSR exe_expr
 1871 e08e: 0e 20           LDAI TOKENIZER_RIGHTP
 1872 e090: 04 e0 54        JSR exe_accept
 1873 e093: 05              RET
 1874 e094:             
 1875 e094:             exe_factor2:
 1876 e094: 04 e0 67        jsr exe_varfactor
 1877 e097: 05              ret
 1878 e098:             
 1879 e098:             ;
 1880 e098:             ; int term()
 1881 e098:             ; R5 = F1
 1882 e098:             ; R6 = F2
 1883 e098:             ; R7 = return value
 1884 e098:             ;
 1885 e098:             exe_term:
 1886 e098: 07 05           pushr r5
 1887 e09a: 07 06           pushr r6
 1888 e09c:             
 1889 e09c: 04 e0 73        jsr exe_factor
 1890 e09f: 0f 57           MOVRR r7,r5
 1891 e0a1:             
 1892 e0a1:             exe_term_loop:
 1893 e0a1: 04 e3 b1        jsr tok_token
 1894 e0a4: 0d 1b           ldti TOKENIZER_ASTR
 1895 e0a6: a8 e0 b6        BREQ exe_term_astr
 1896 e0a9: 0d 1c           LDTI TOKENIZER_SLASH
 1897 e0ab: a8 e0 c1        breq exe_term_slash
 1898 e0ae: 0d 1d           ldti TOKENIZER_MOD
 1899 e0b0: a8 e0 cc        breq exe_term_mod
 1900 e0b3: a0 e0 d7        br exe_term_done
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
 3669 ea00: 20 64 6f 6e 
            65 00 24 25 
            6e 00 11 00 
            06 03 69 6e     DB  20h,64h,6fh,6eh,65h,00h,24h,25h,6eh,00h,11h,00h,06h,03h,69h,6eh
 3670 ea10: 20 67 6f 73 
            75 62 00 24 
            25 70 00 11 
            00 06 03 69     DB  20h,67h,6fh,73h,75h,62h,00h,24h,25h,70h,00h,11h,00h,06h,03h,69h
 3671 ea20: 6e 20 73 75 
            62 20 32 00 
            24 25 72 00 
            07 00 0f 24     DB  6eh,20h,73h,75h,62h,20h,32h,00h,24h,25h,72h,00h,07h,00h,0fh,24h
 3672 ea30: 25 7d 00 0c 
            00 06 03 65 
            6e 64 00 24 
            25 7e 00 07     DB  25h,7dh,00h,0ch,00h,06h,03h,65h,6eh,64h,00h,24h,25h,7eh,00h,07h
 3673 ea40: 00 14 24 01 
            00 00 00 00 
            00 00 00 00 
            00 00 00 00     DB  00h,14h,24h,01h,00h,00h,00h,00h,00h,00h,00h,00h,00h,00h,00h,00h
 3674 ea50:             
 3675 ea50:             ;
 3676 ea50:             ; The End
 3677 ea50:             ;
 3678 ea50:             ZZZZ:
 3679 ea50: 00            DB   0
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
