ksr/YACC1-D/hardware/cards/bus-tester/kicad/v3.1/reports/bus-tester-v3.1-top.png

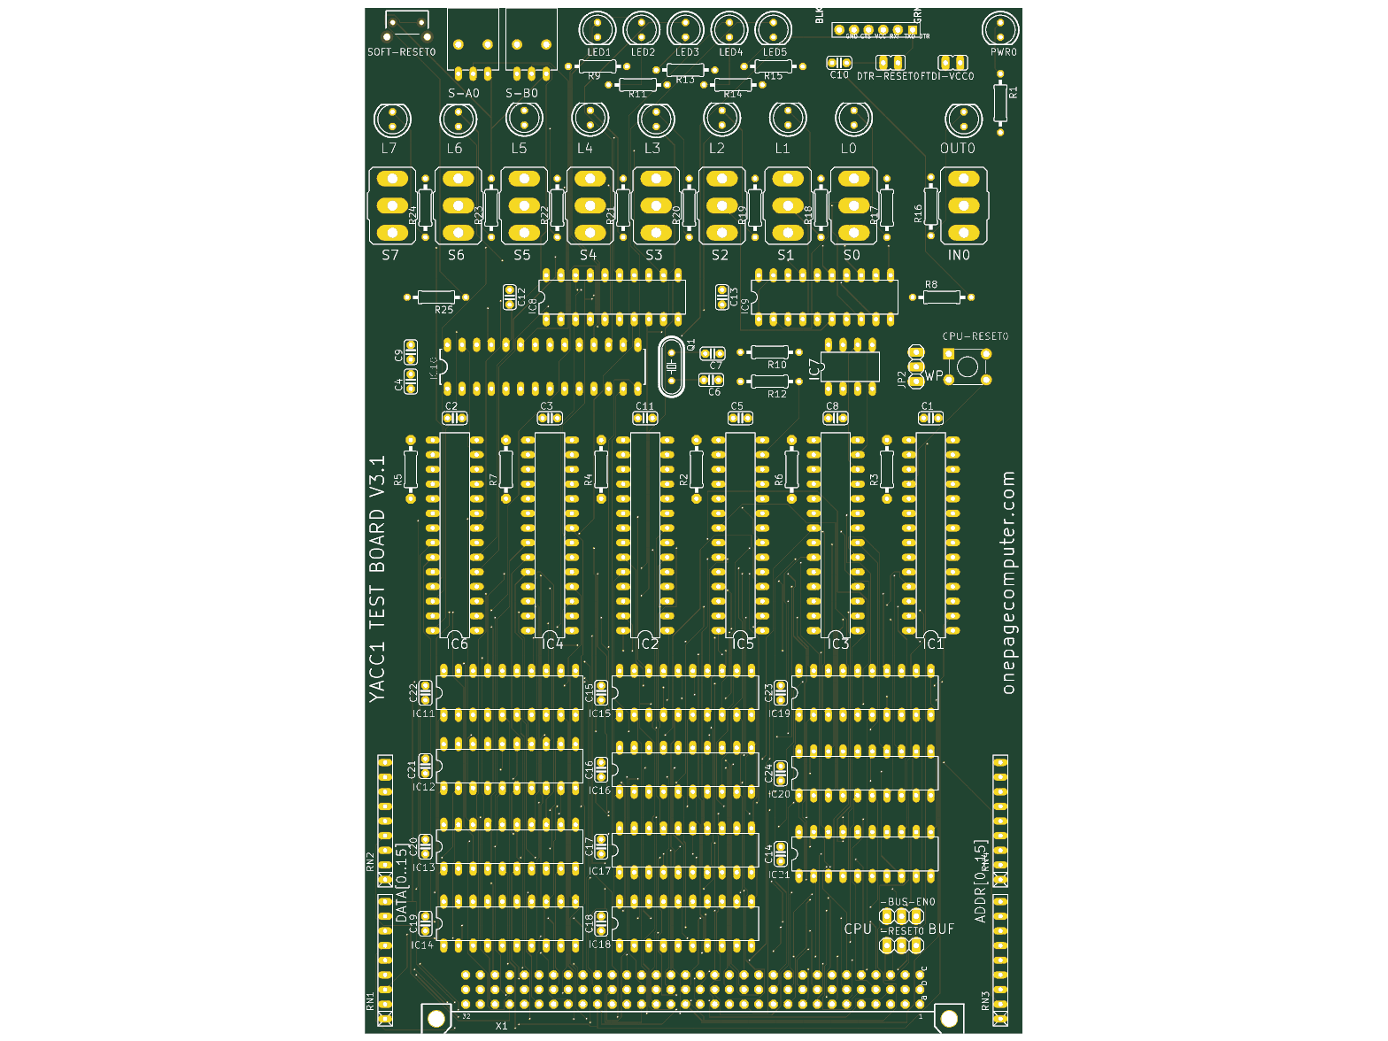
hardware/cards/bus-tester/kicad/v3.1/reports/bus-tester-v3.1-top.png
