ksr/YACC1-D/archive/superseded-revisions/README.md

# archive/superseded-revisions

2020-era board revisions replaced by later ones, and everything from the 'Old and obsolete' folders.

_Contents migrated 2026-09-19; MIGRATION.md at the repo root says which copy each item came from._
