ksr/YACC1-D/archive/gen1-2015-2018/YACC1A1/PRODUCTION/TESTER-PROD-V1.1/new - 1.21 bus/changes.rtf

Adjusted to use Bus 1.21 from Bus 1.20

No electrical differences -

0) Rename original UNSED2 to RUN

1) removed ADDR register on Register File Board therefore 4 control lines free up
1a) renamed to UNUSED2-UNUSED5

2) Change Register File Board from 4 - 8 registers

2A) Rename REG-BRD-RD-ID[0..1] and REG-BRD-LD-ID[0..1] to
REG-BRD-RD-ID and REG-BRD-LD-ID
Freed up signal used for extra register id, see next step

2B) Change REG-RD-ID[0..1] and REG-LD-ID[0..1] to
REG-RD-ID[0..2] and REG-LD-ID[0..2]

FIX
Join R21 to R9 to gnd 8 leds
