ksr/YACC1-D/hardware/cards/memory/kicad/v2.0/options-top-edge-J2/memory-v2.0-placement.pdf

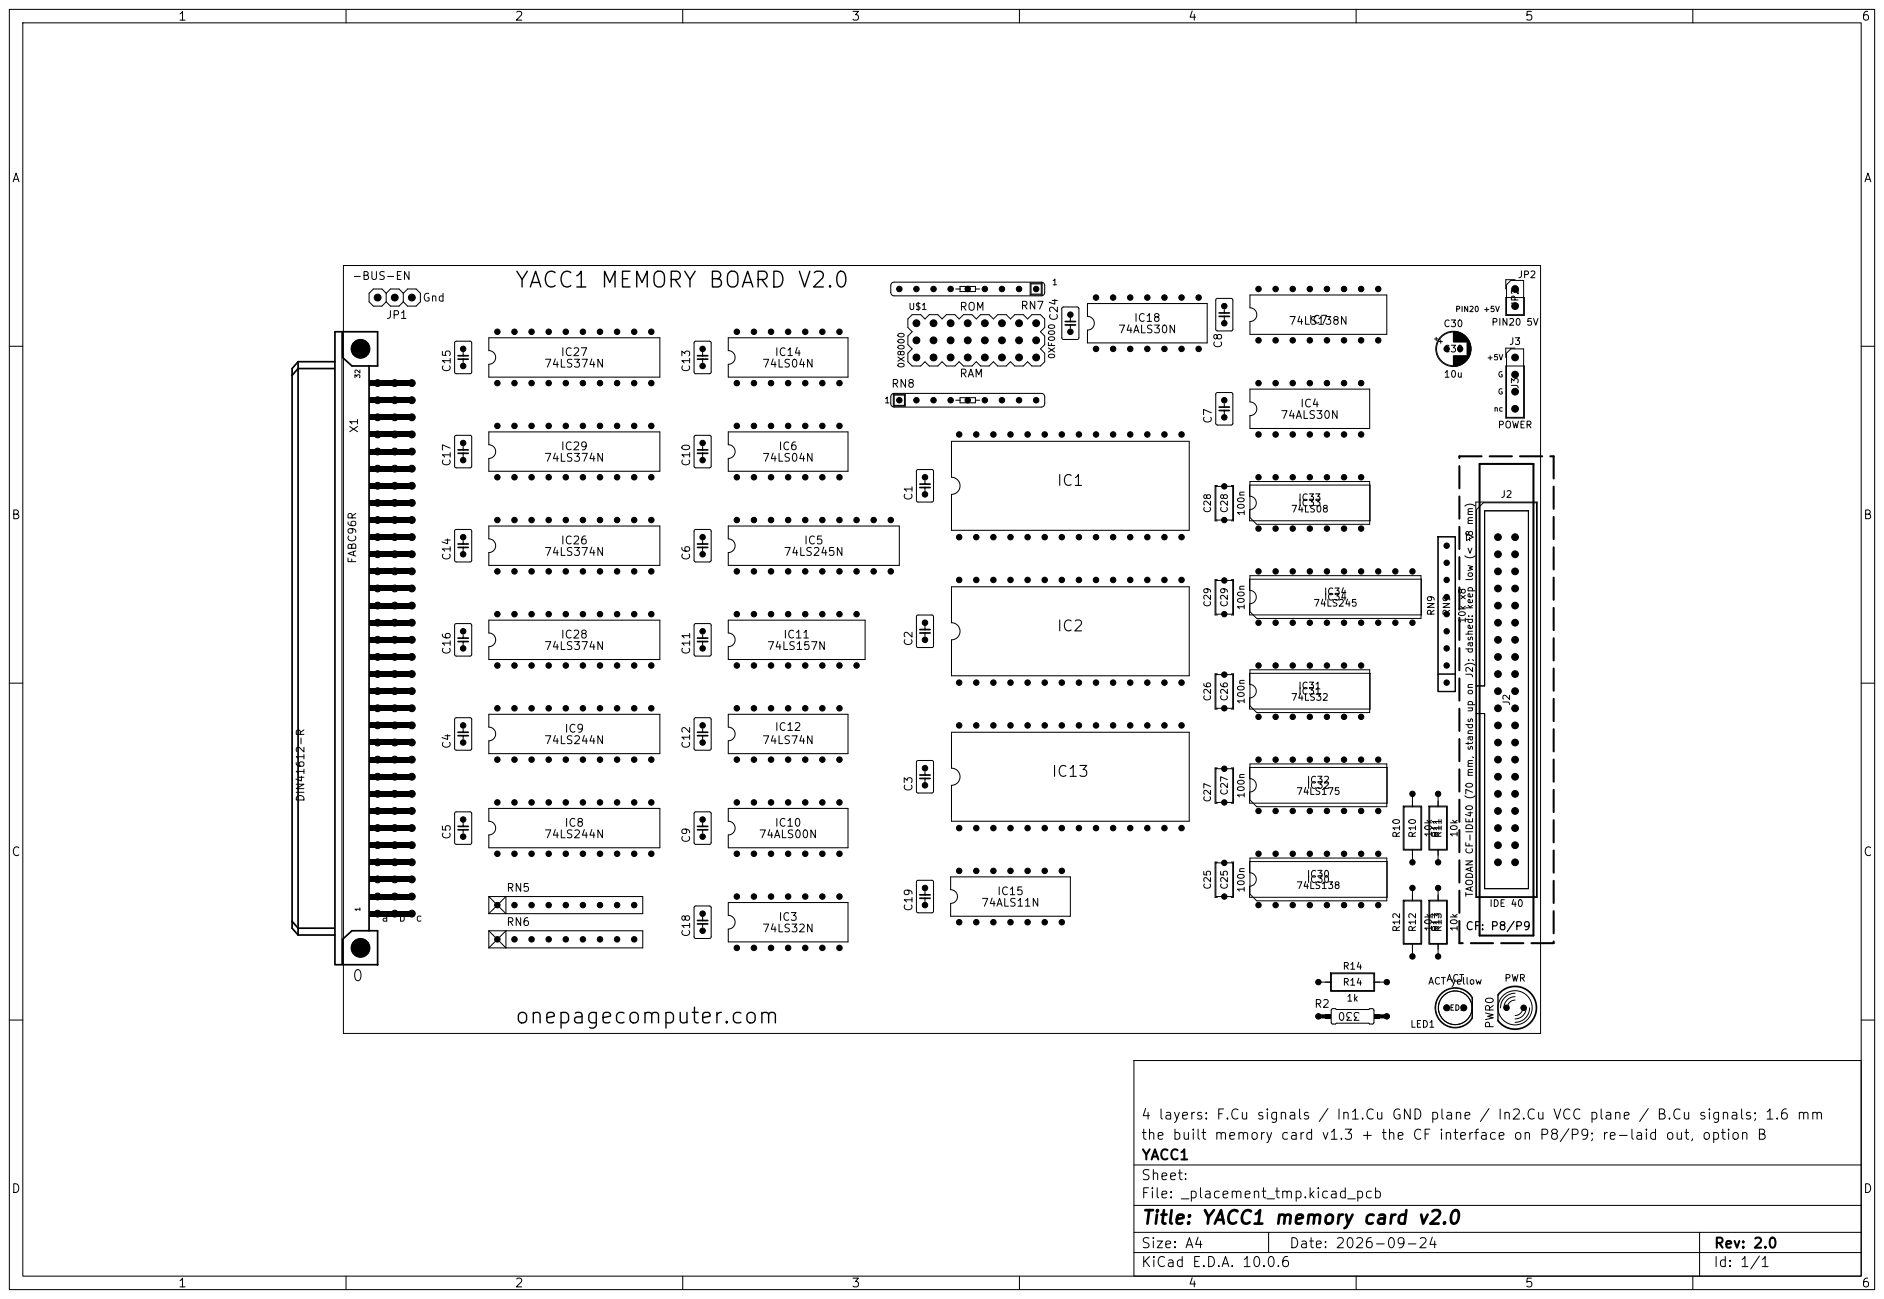
[picture p69: page 1]

4 layers: F.Cu signals / In1.Cu GND plane / In2.Cu VCC plane / B.Cu signals; 1.6 mm
the built memory card v1.3 + the CF interface on P8/P9; re-laid out, option B
YACC1
Sheet:
File: _placement_tmp.kicad_pcb
Title: YACC1 memory card v2.0

Size: A4 | Rev: 2.0
KiCad E.D.A. 10.0.6 | Id: 1/1
