ksr/YACC1-D/hardware/cards/memory/eagle/v1.3/pdf/Memory V1.3-schematic.pdf

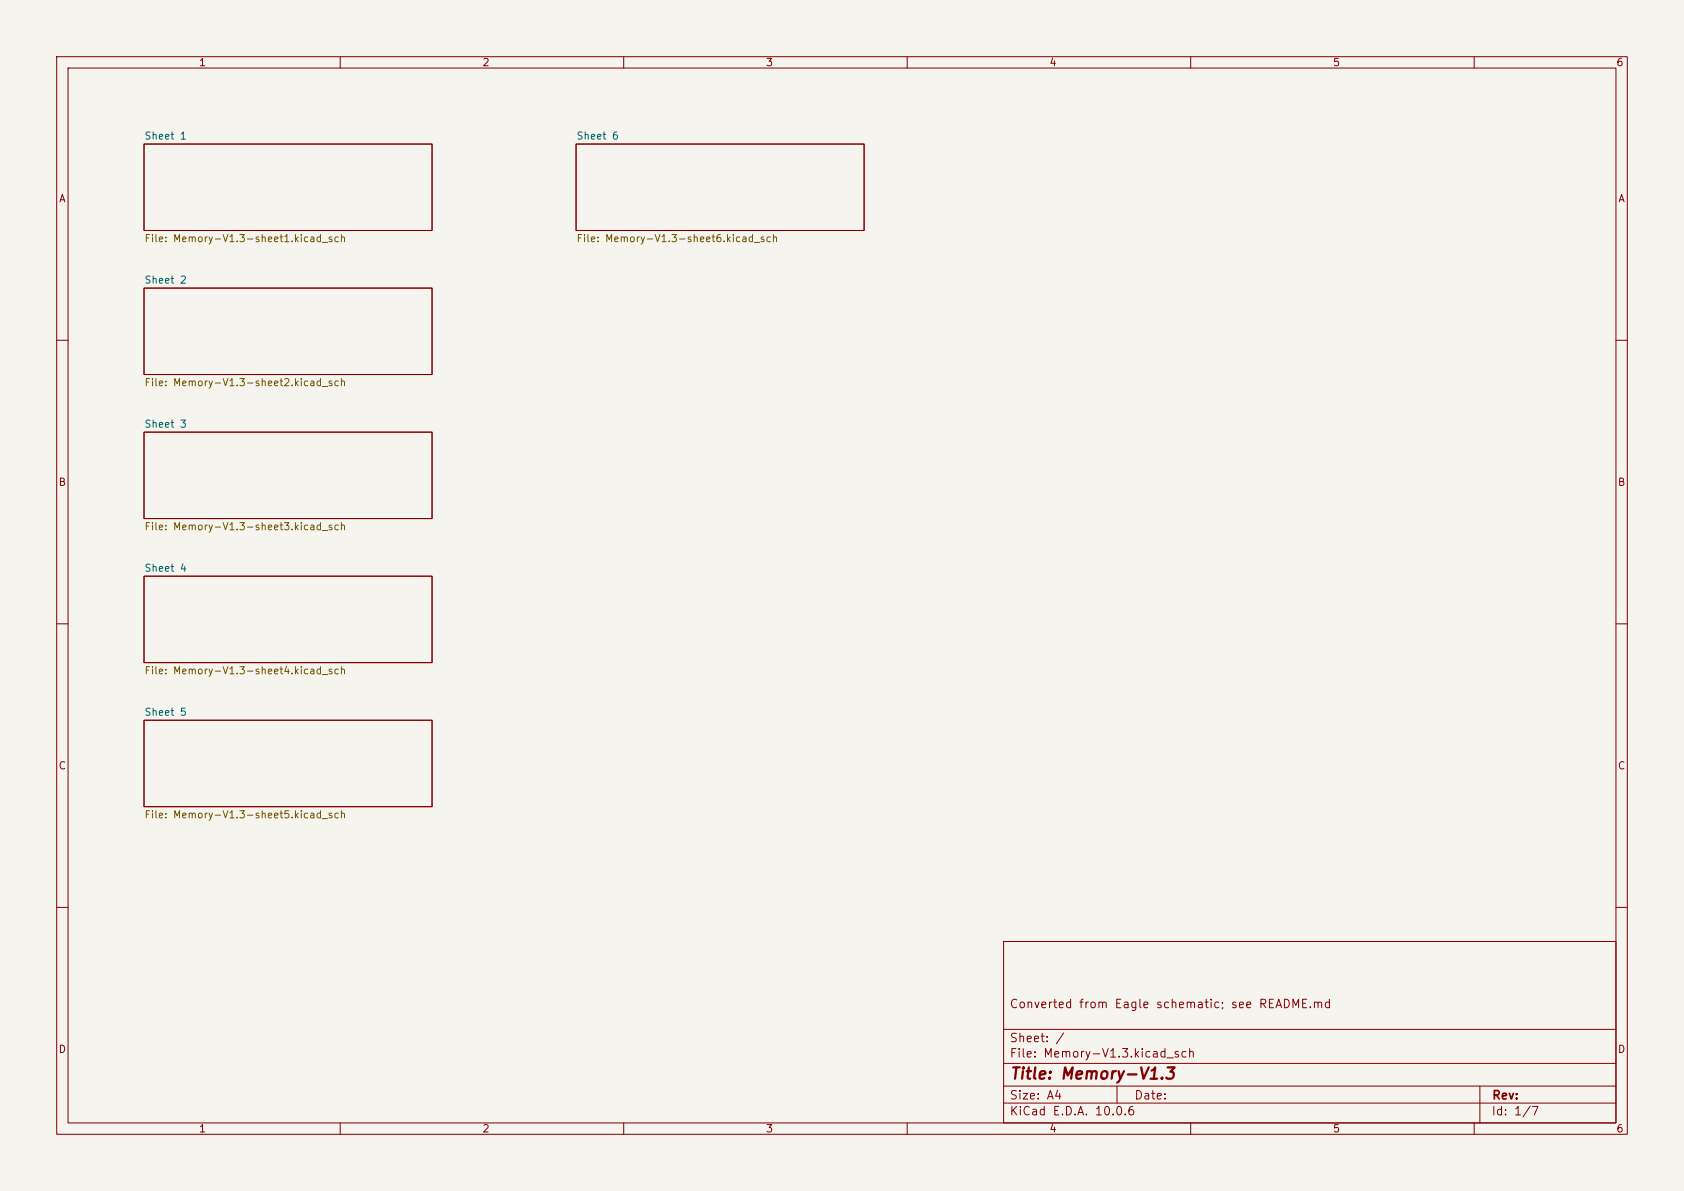
[picture p70: page 1]

Converted from Eagle schematic; see README.md

Size: A4 | Rev:
KiCad E.D.A. 10.0.6 | Id: 1/7

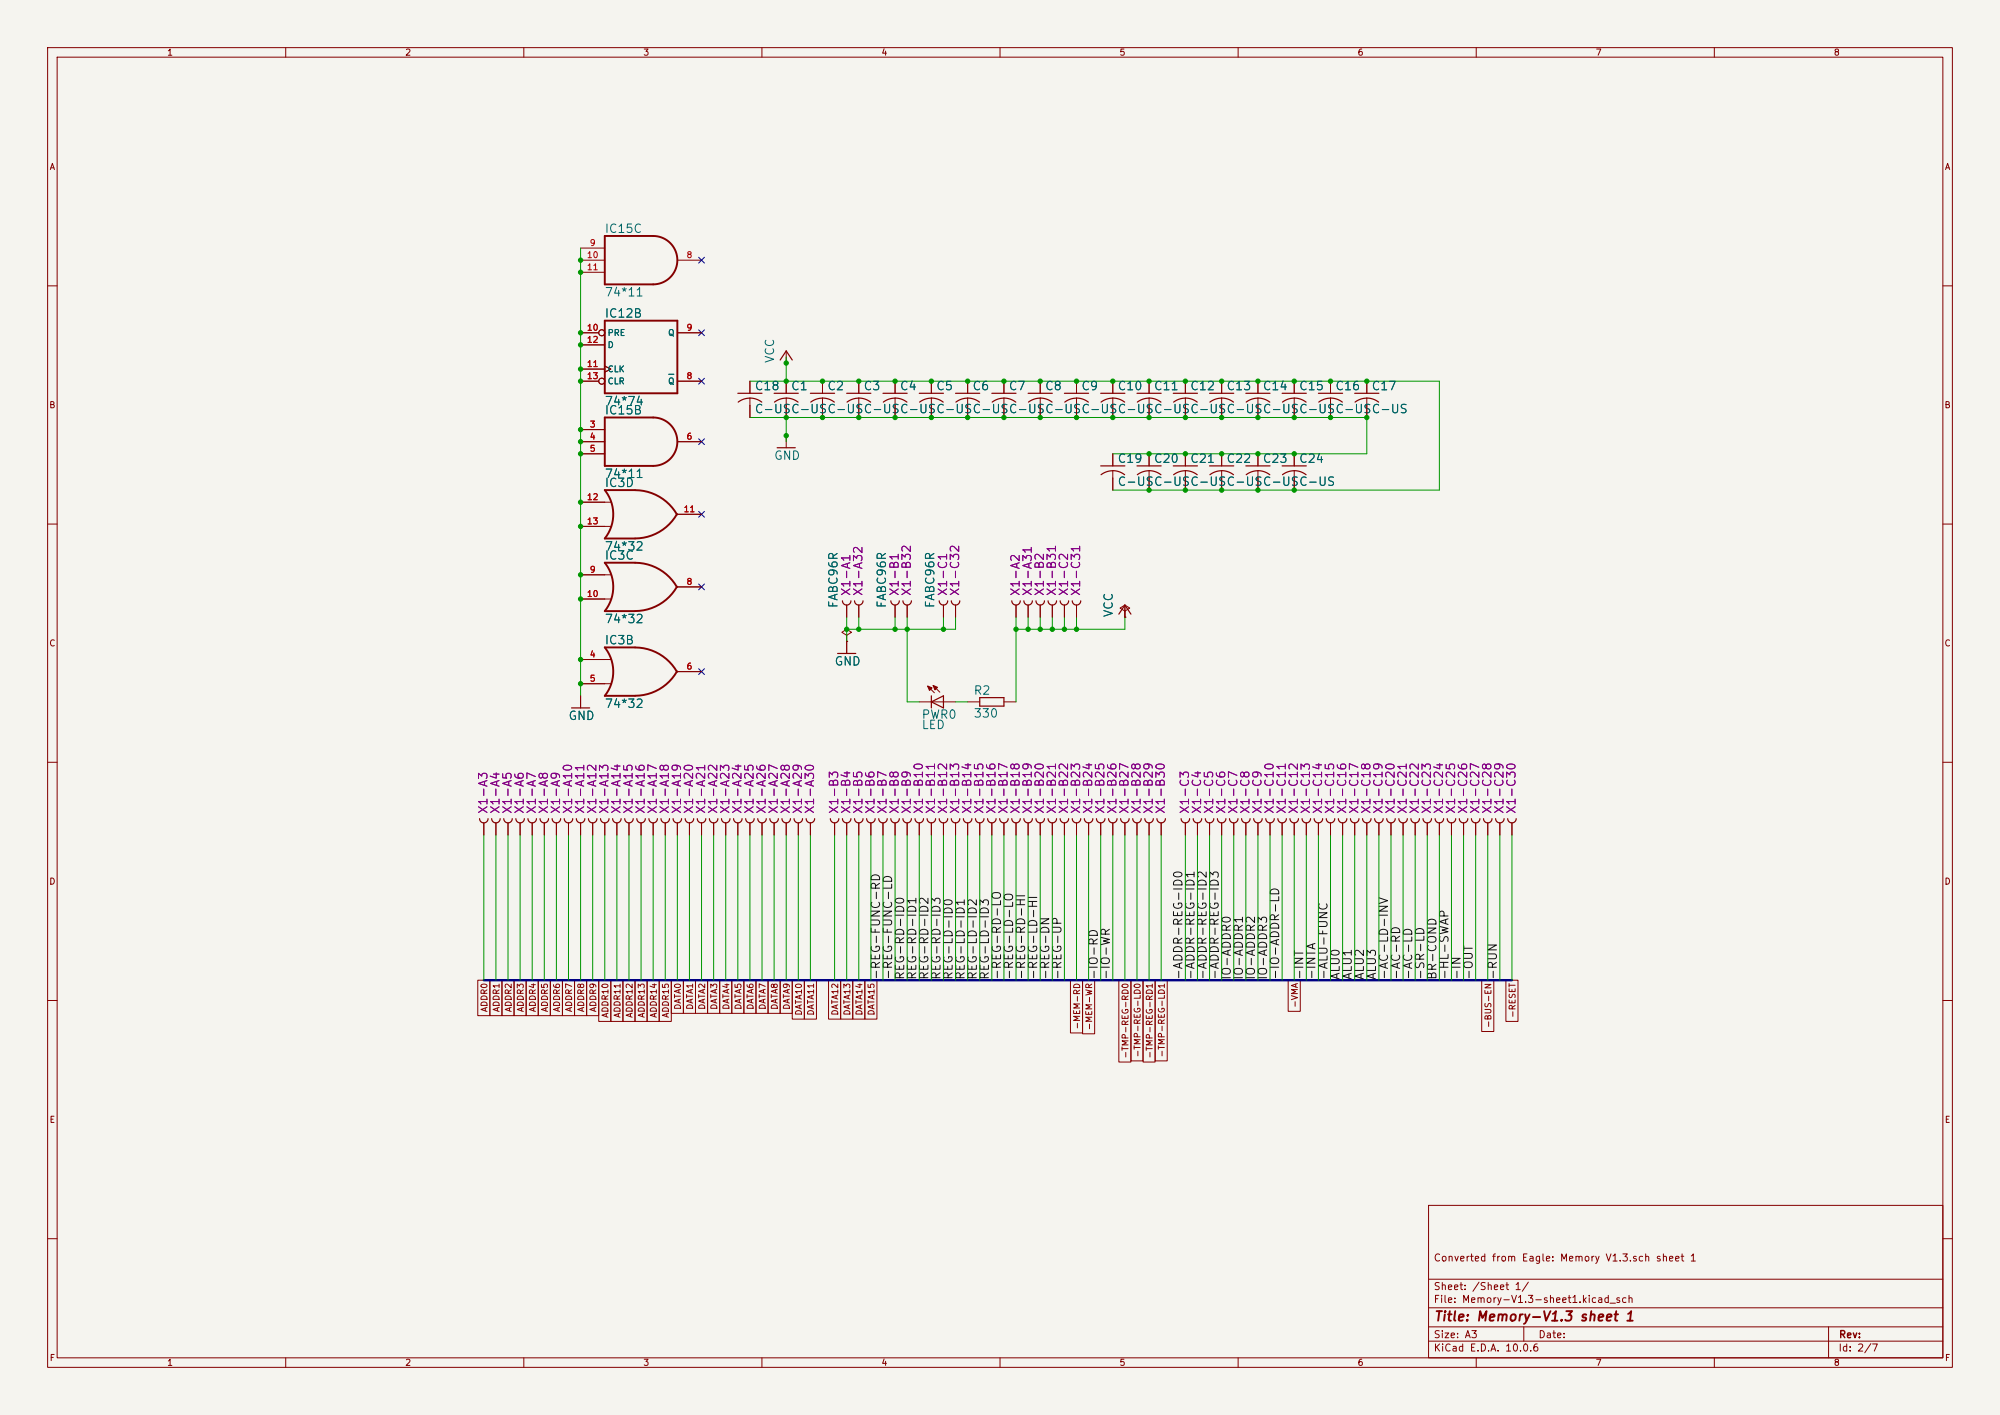
[picture p71: page 2]

Converted from Eagle: Memory V1.3.sch sheet 1 X1-A7

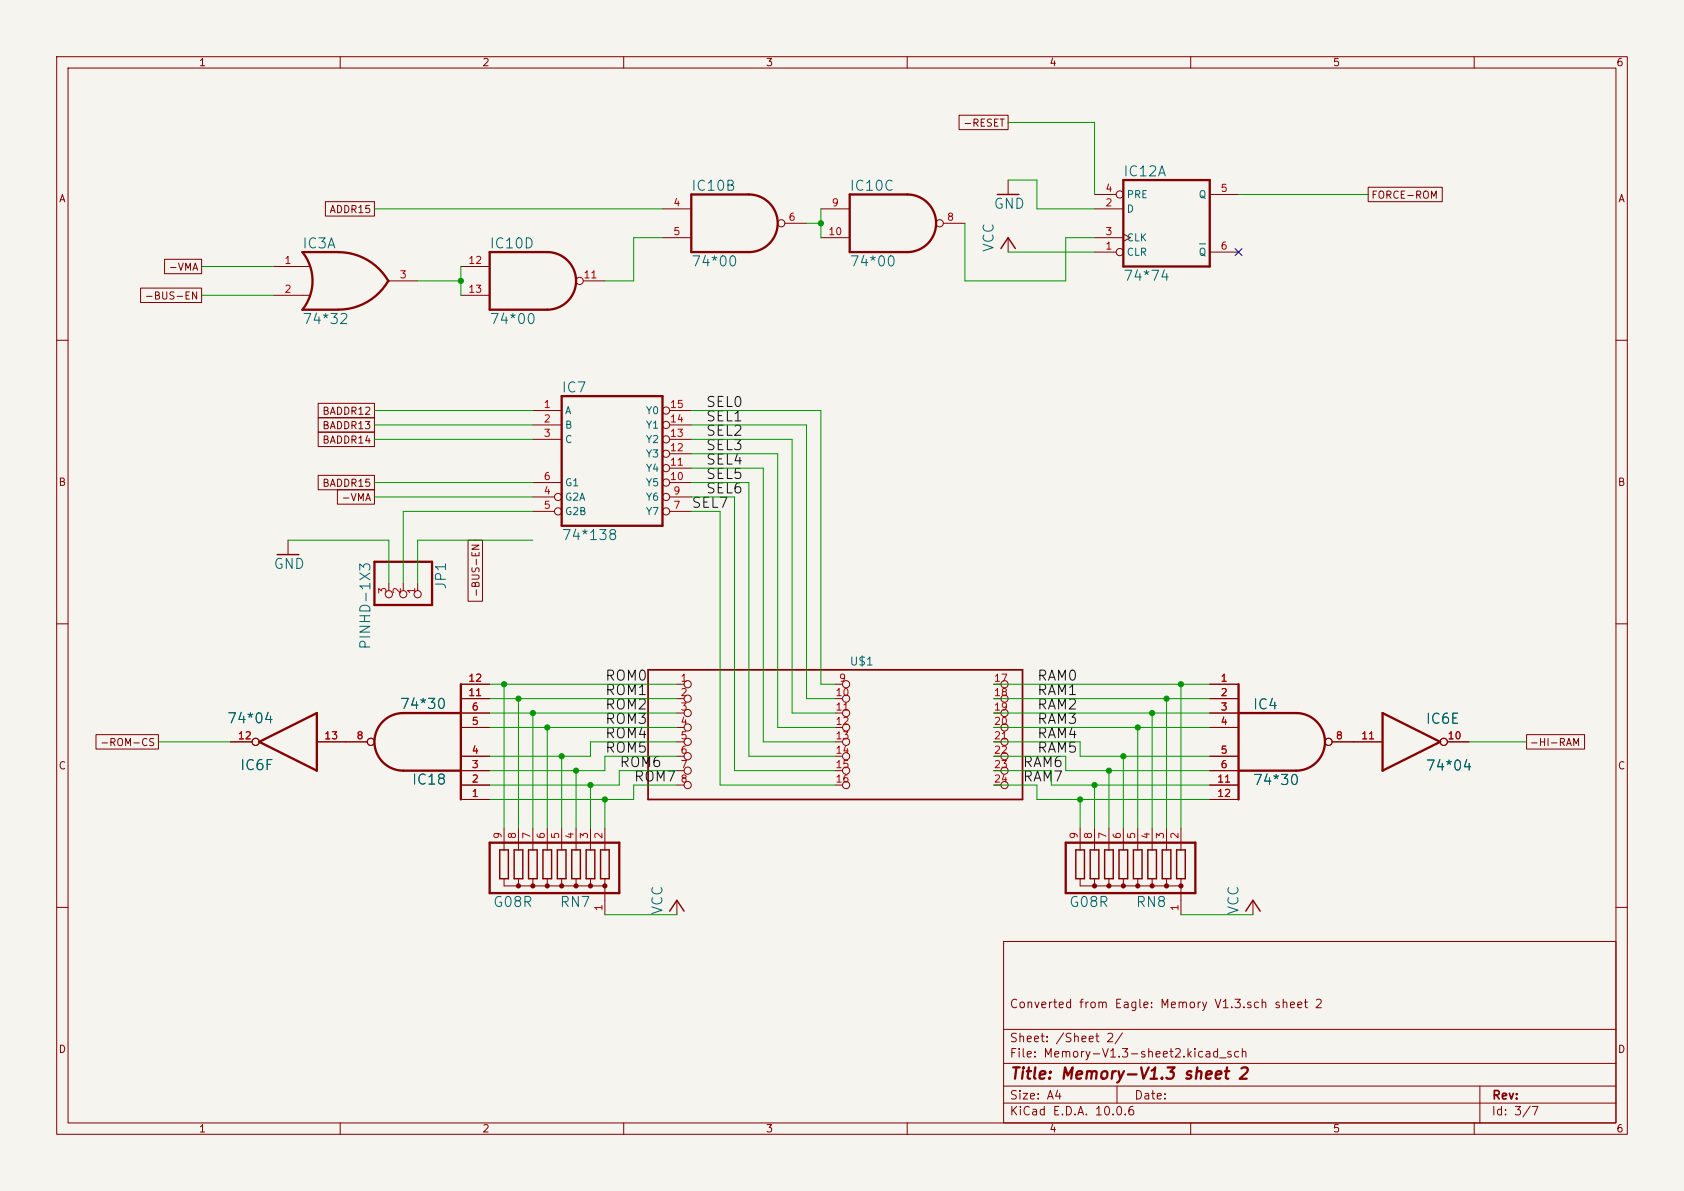
[picture p72: page 3]

11 11 | ROM1
6 6 | | ROM2
5 5 | | | ROM3
4 4 | | | | ROM4

Converted from Eagle: Memory V1.3.sch sheet 2

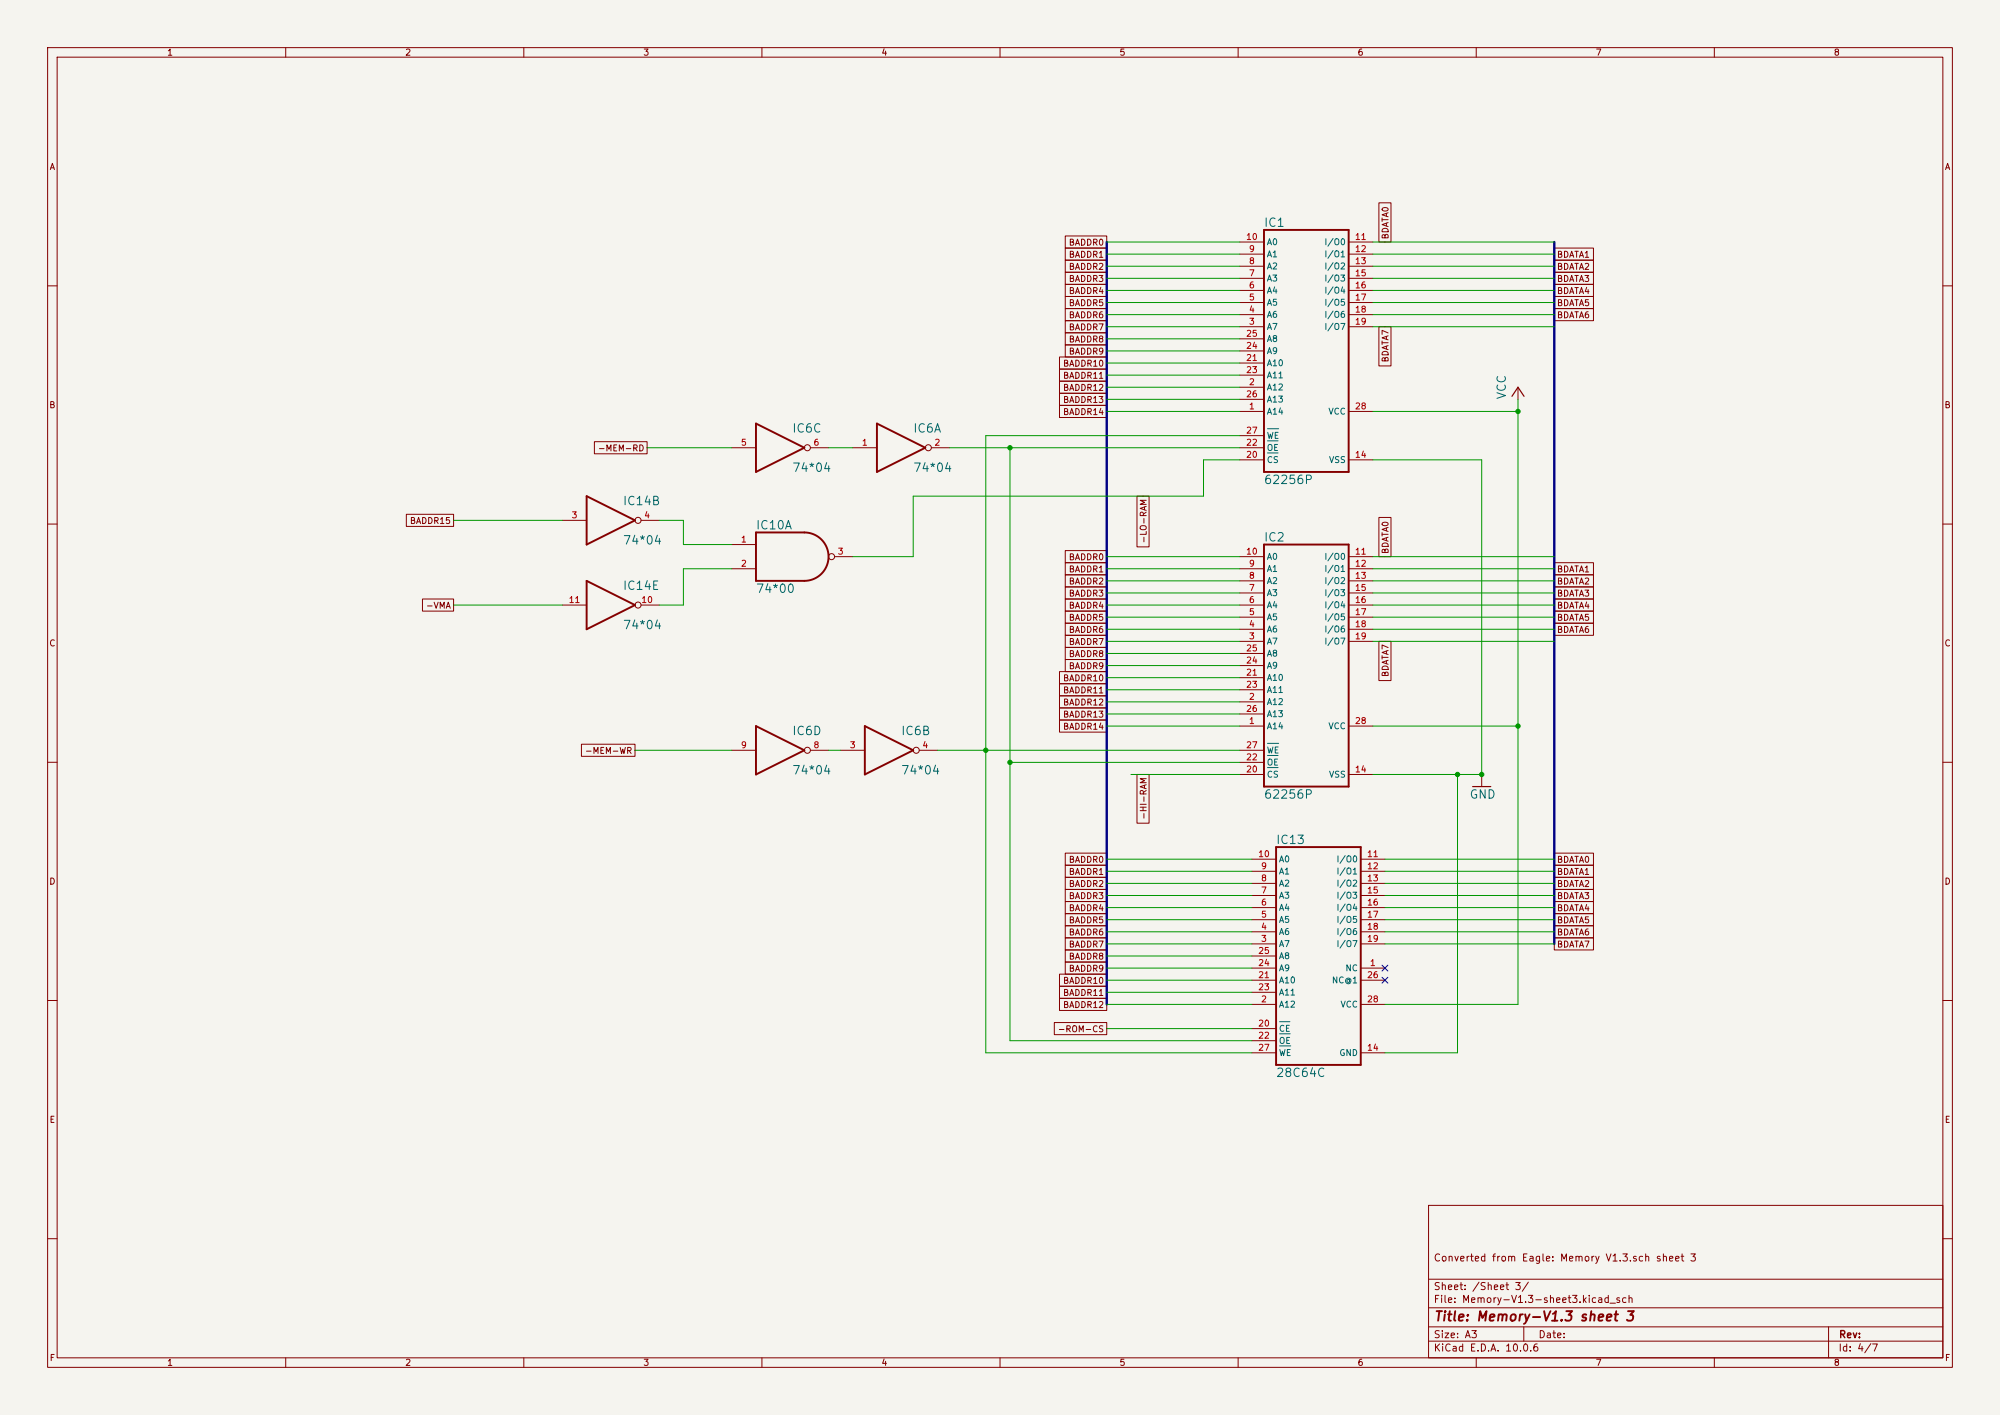
[picture p73: page 4]

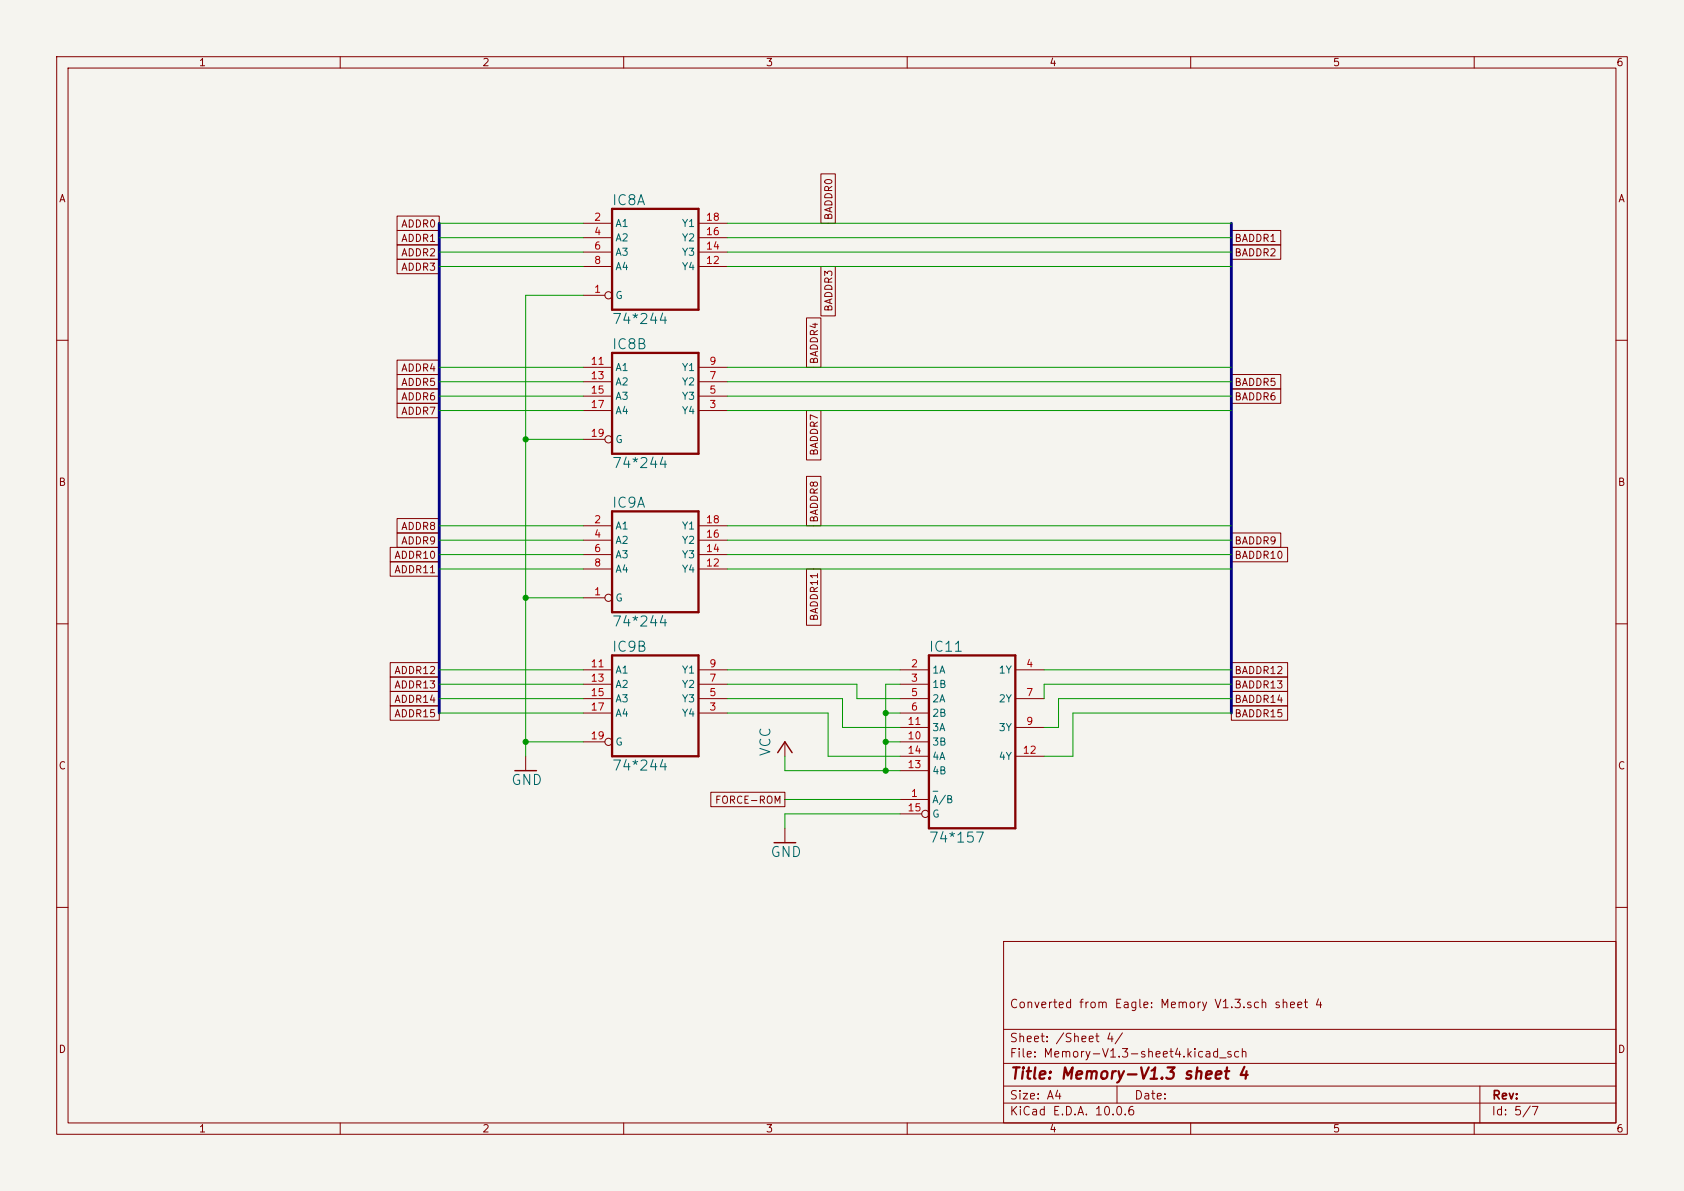
[picture p74: page 5]

Converted from Eagle: Memory V1.3.sch sheet 4 A/B 1

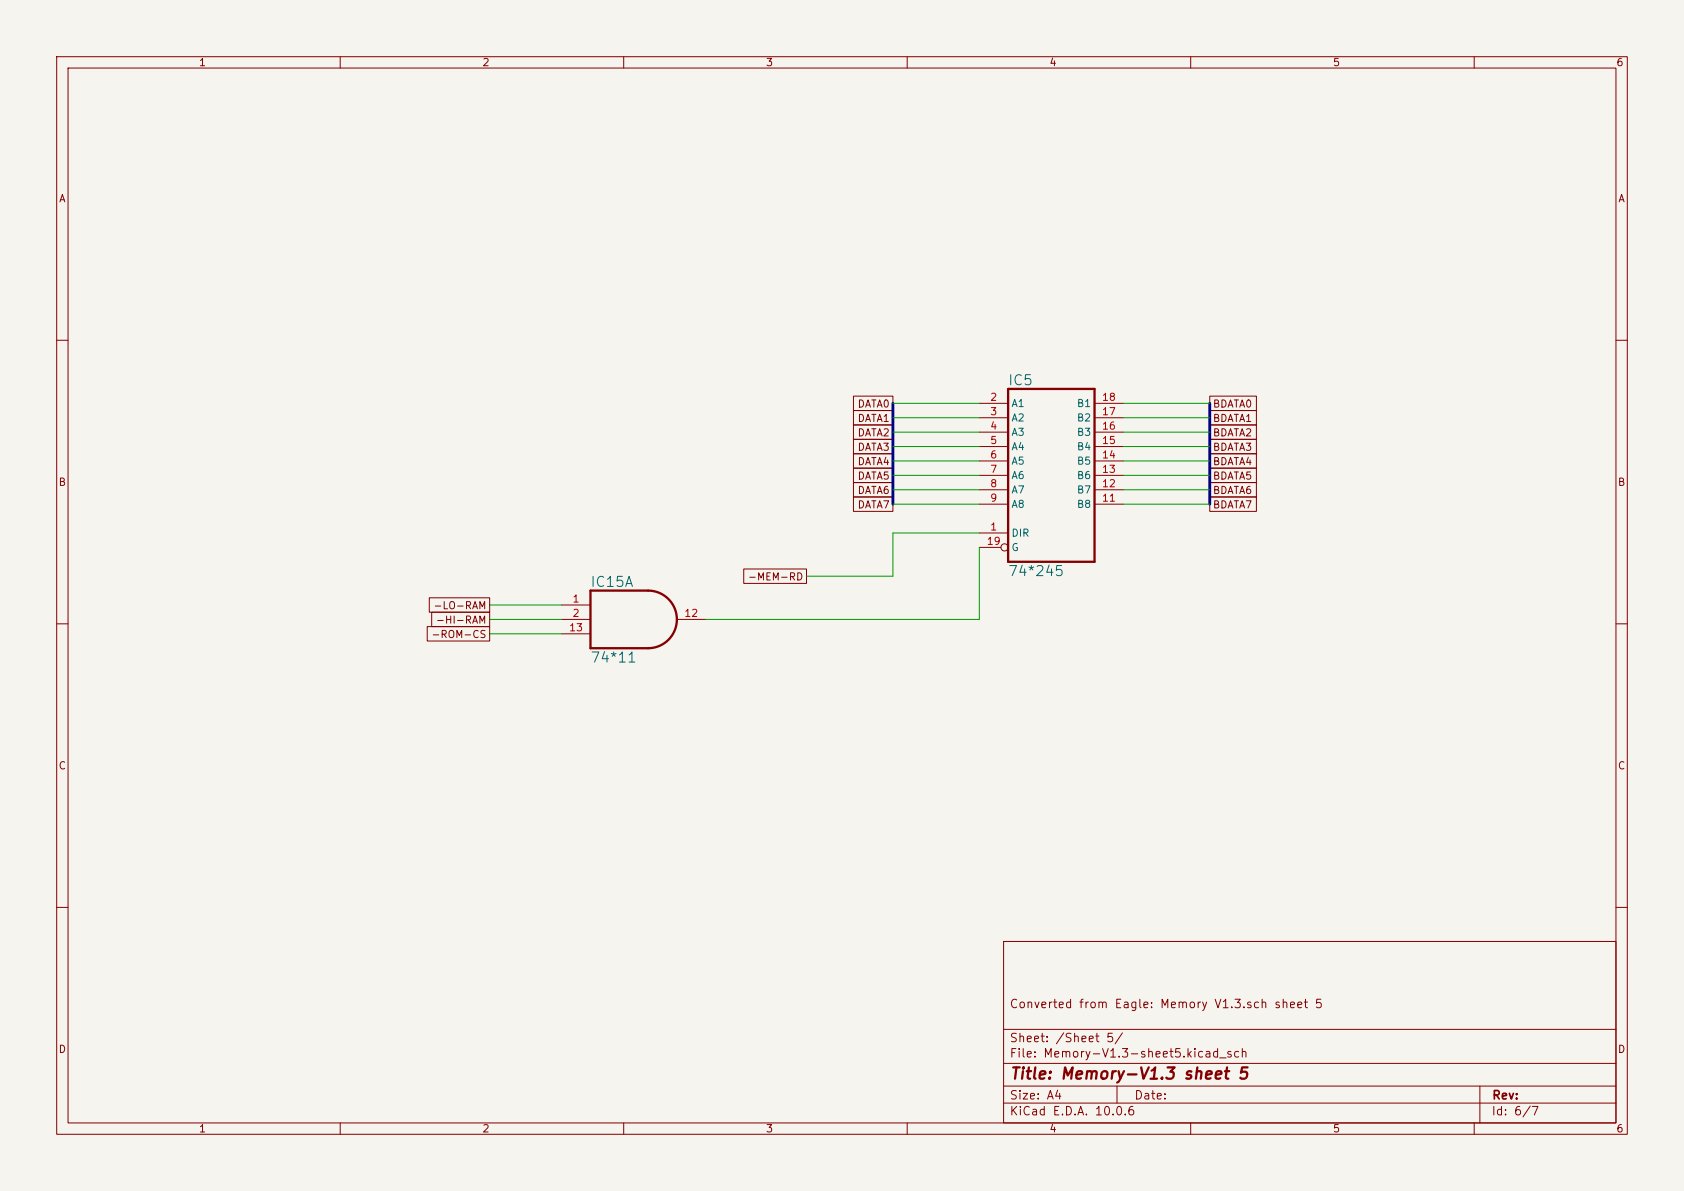
[picture p75: page 6]

Converted from Eagle: Memory V1.3.sch sheet 5

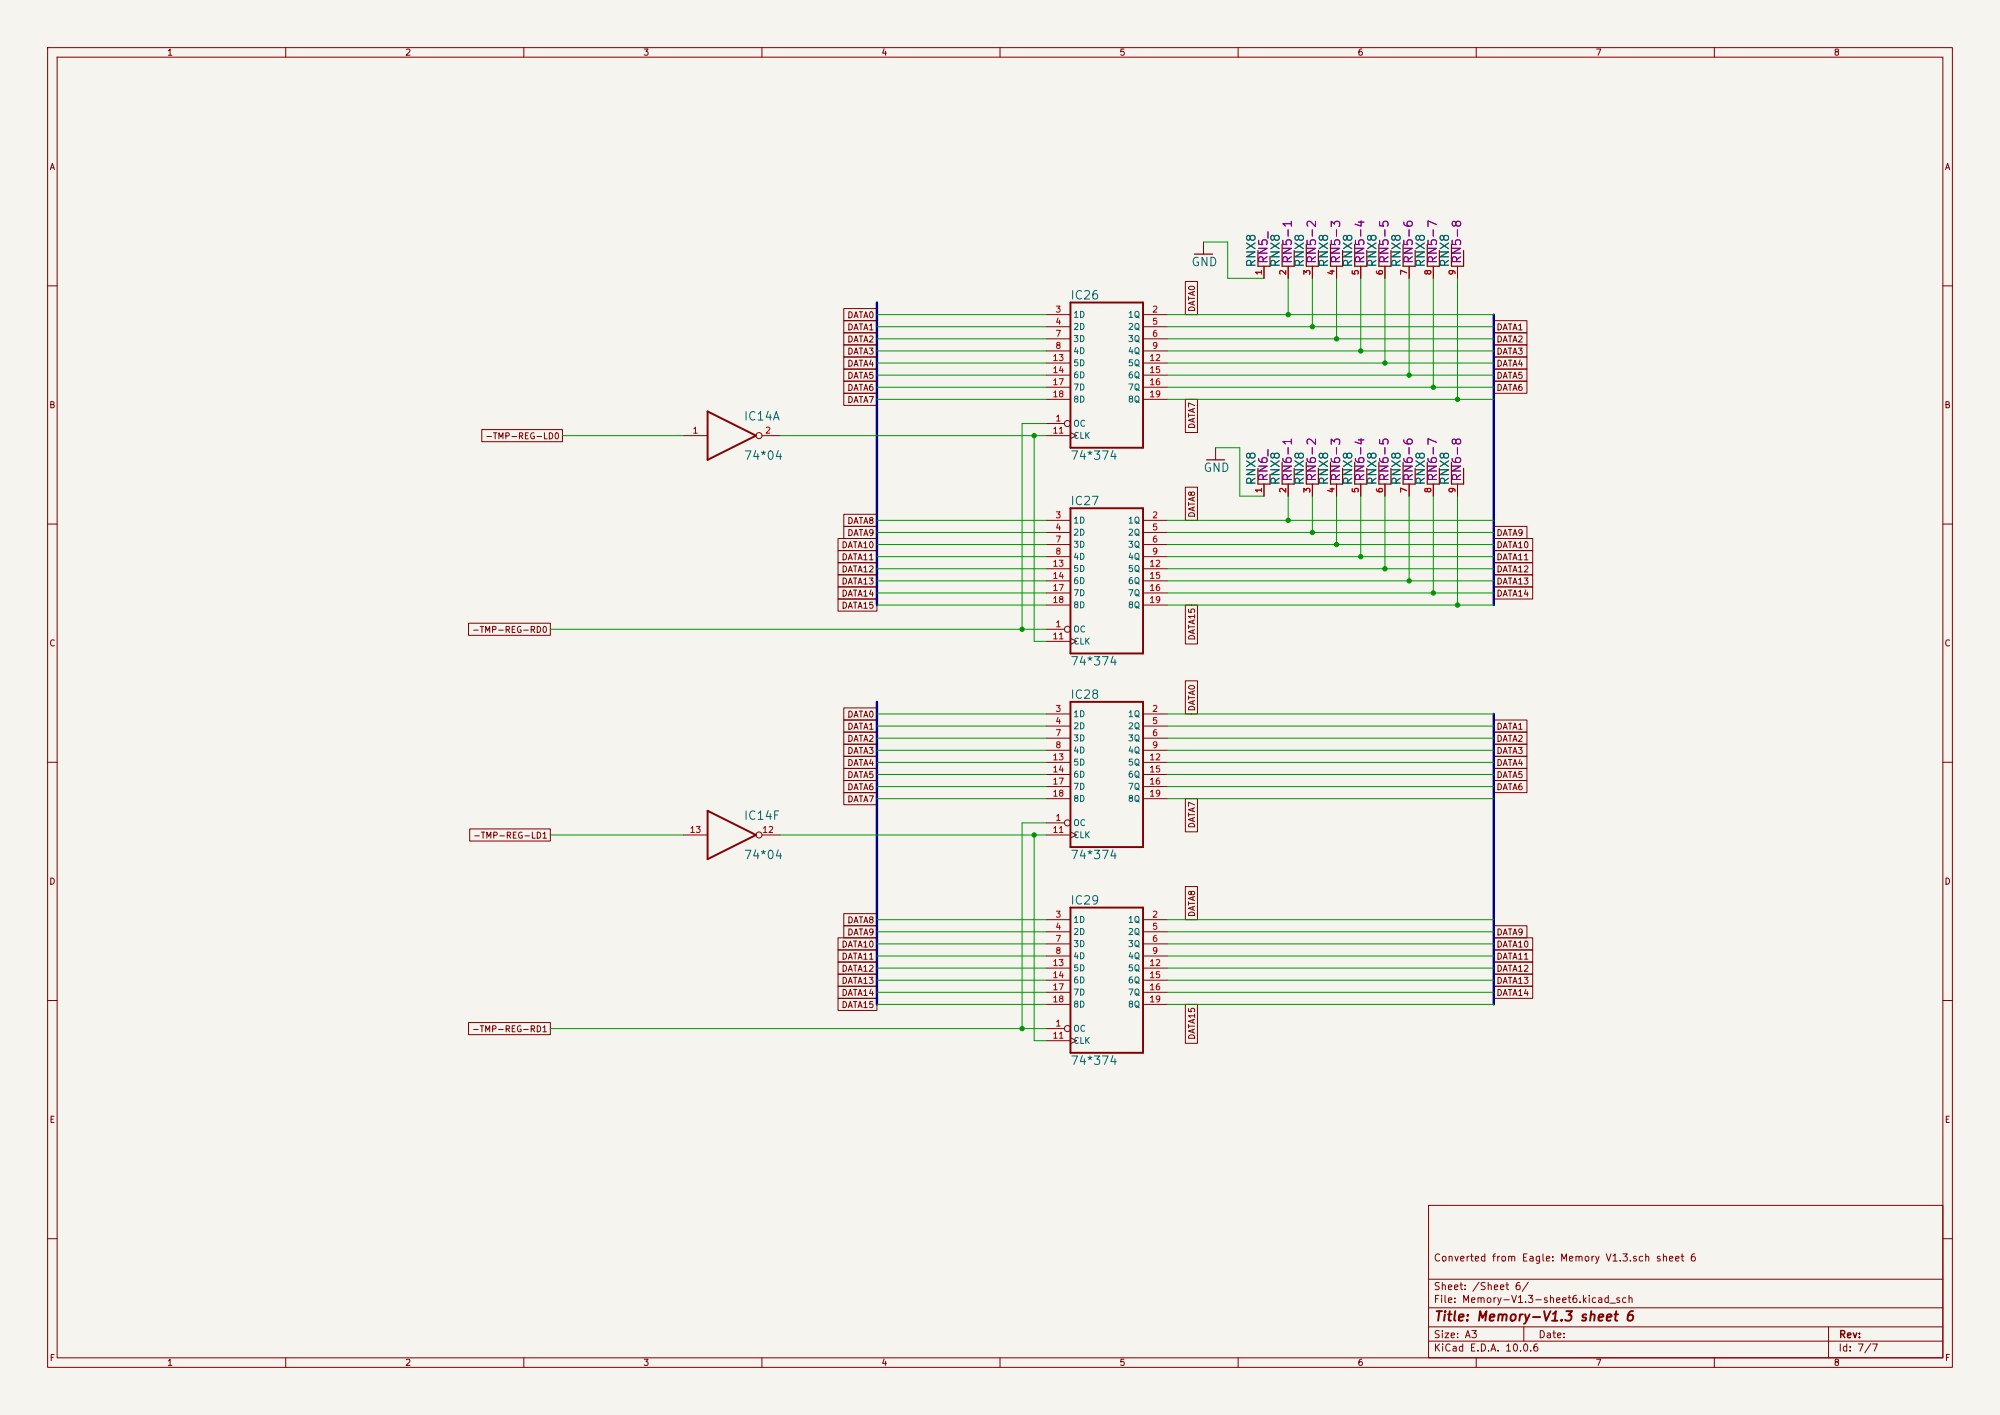
[picture p76: page 7]

Converted from Eagle: Memory V1.3.sch sheet 6 9 RNX8 RN6-8
