ksr/YACC1-D/hardware/bus/backplane/eagle/v2.0/pdf/yacc2buss-schematic.pdf

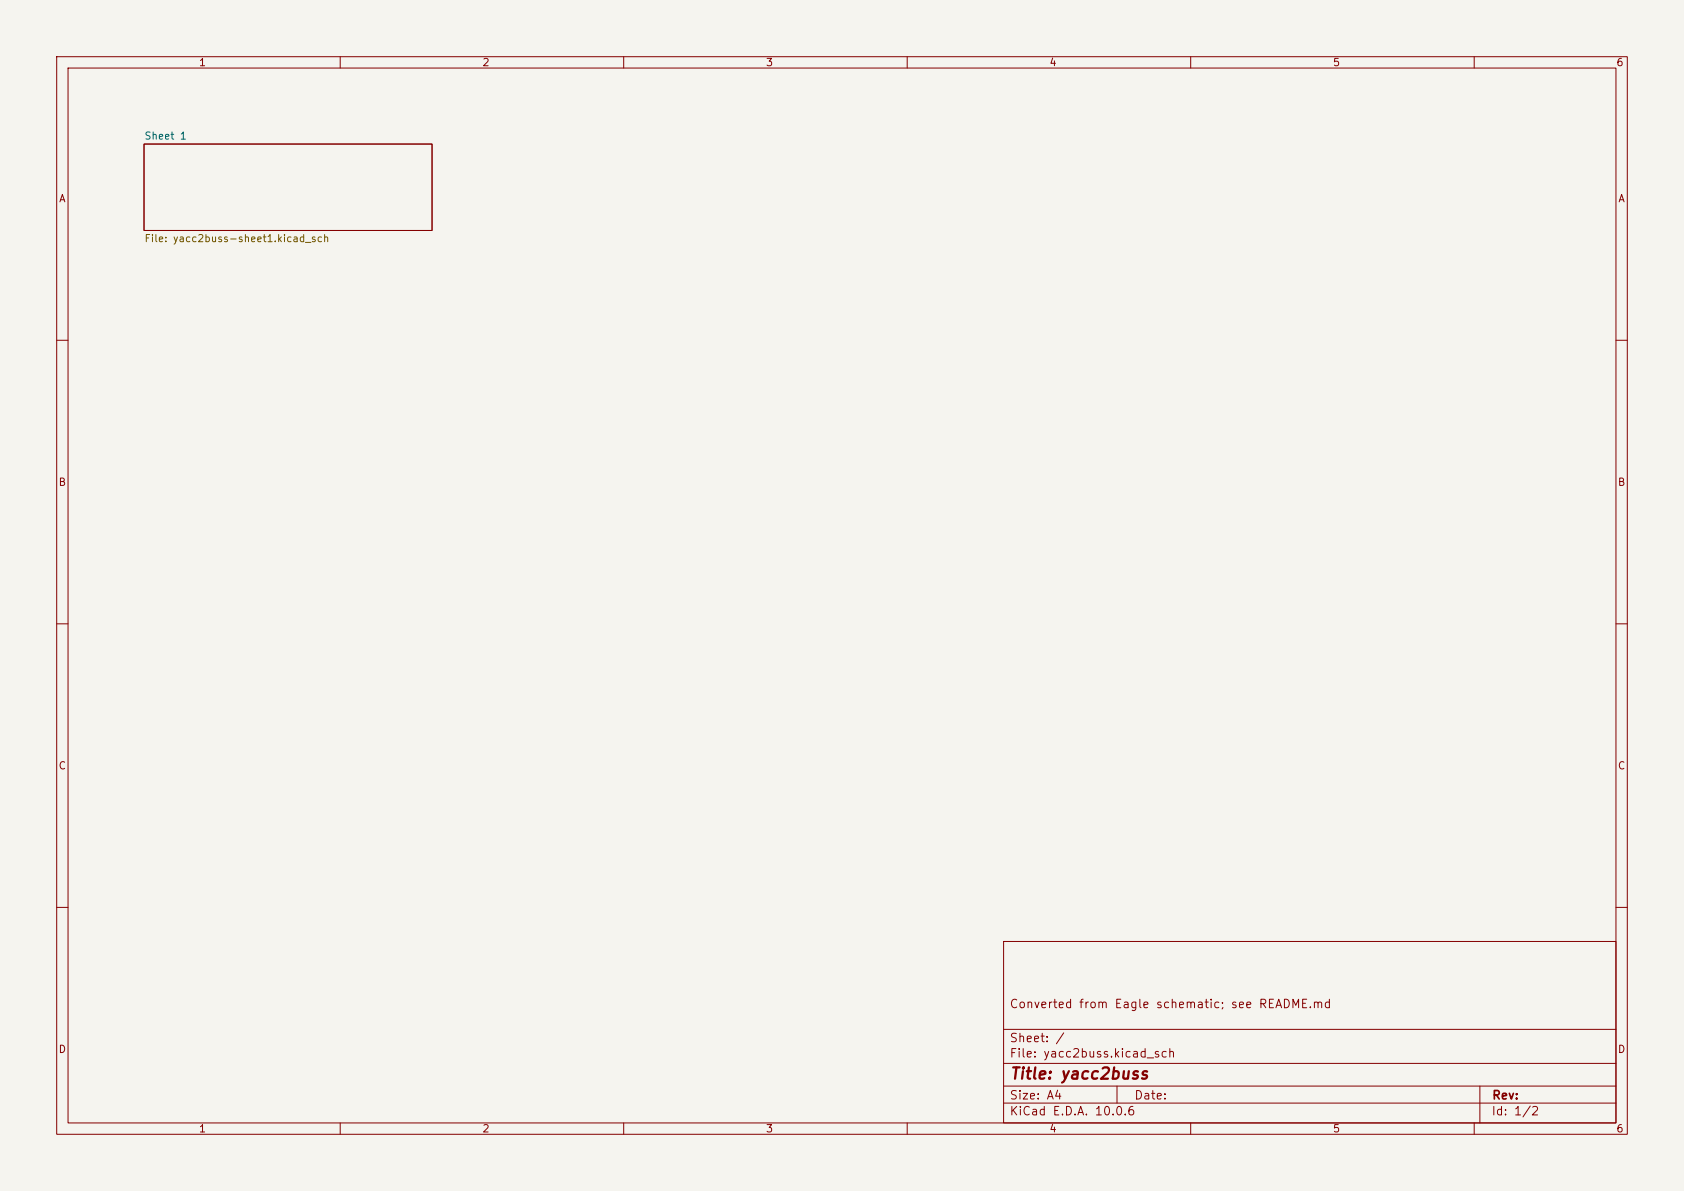
[picture p77: page 1]

Converted from Eagle schematic; see README.md

Size: A4 | Rev:
KiCad E.D.A. 10.0.6 | Id: 1/2

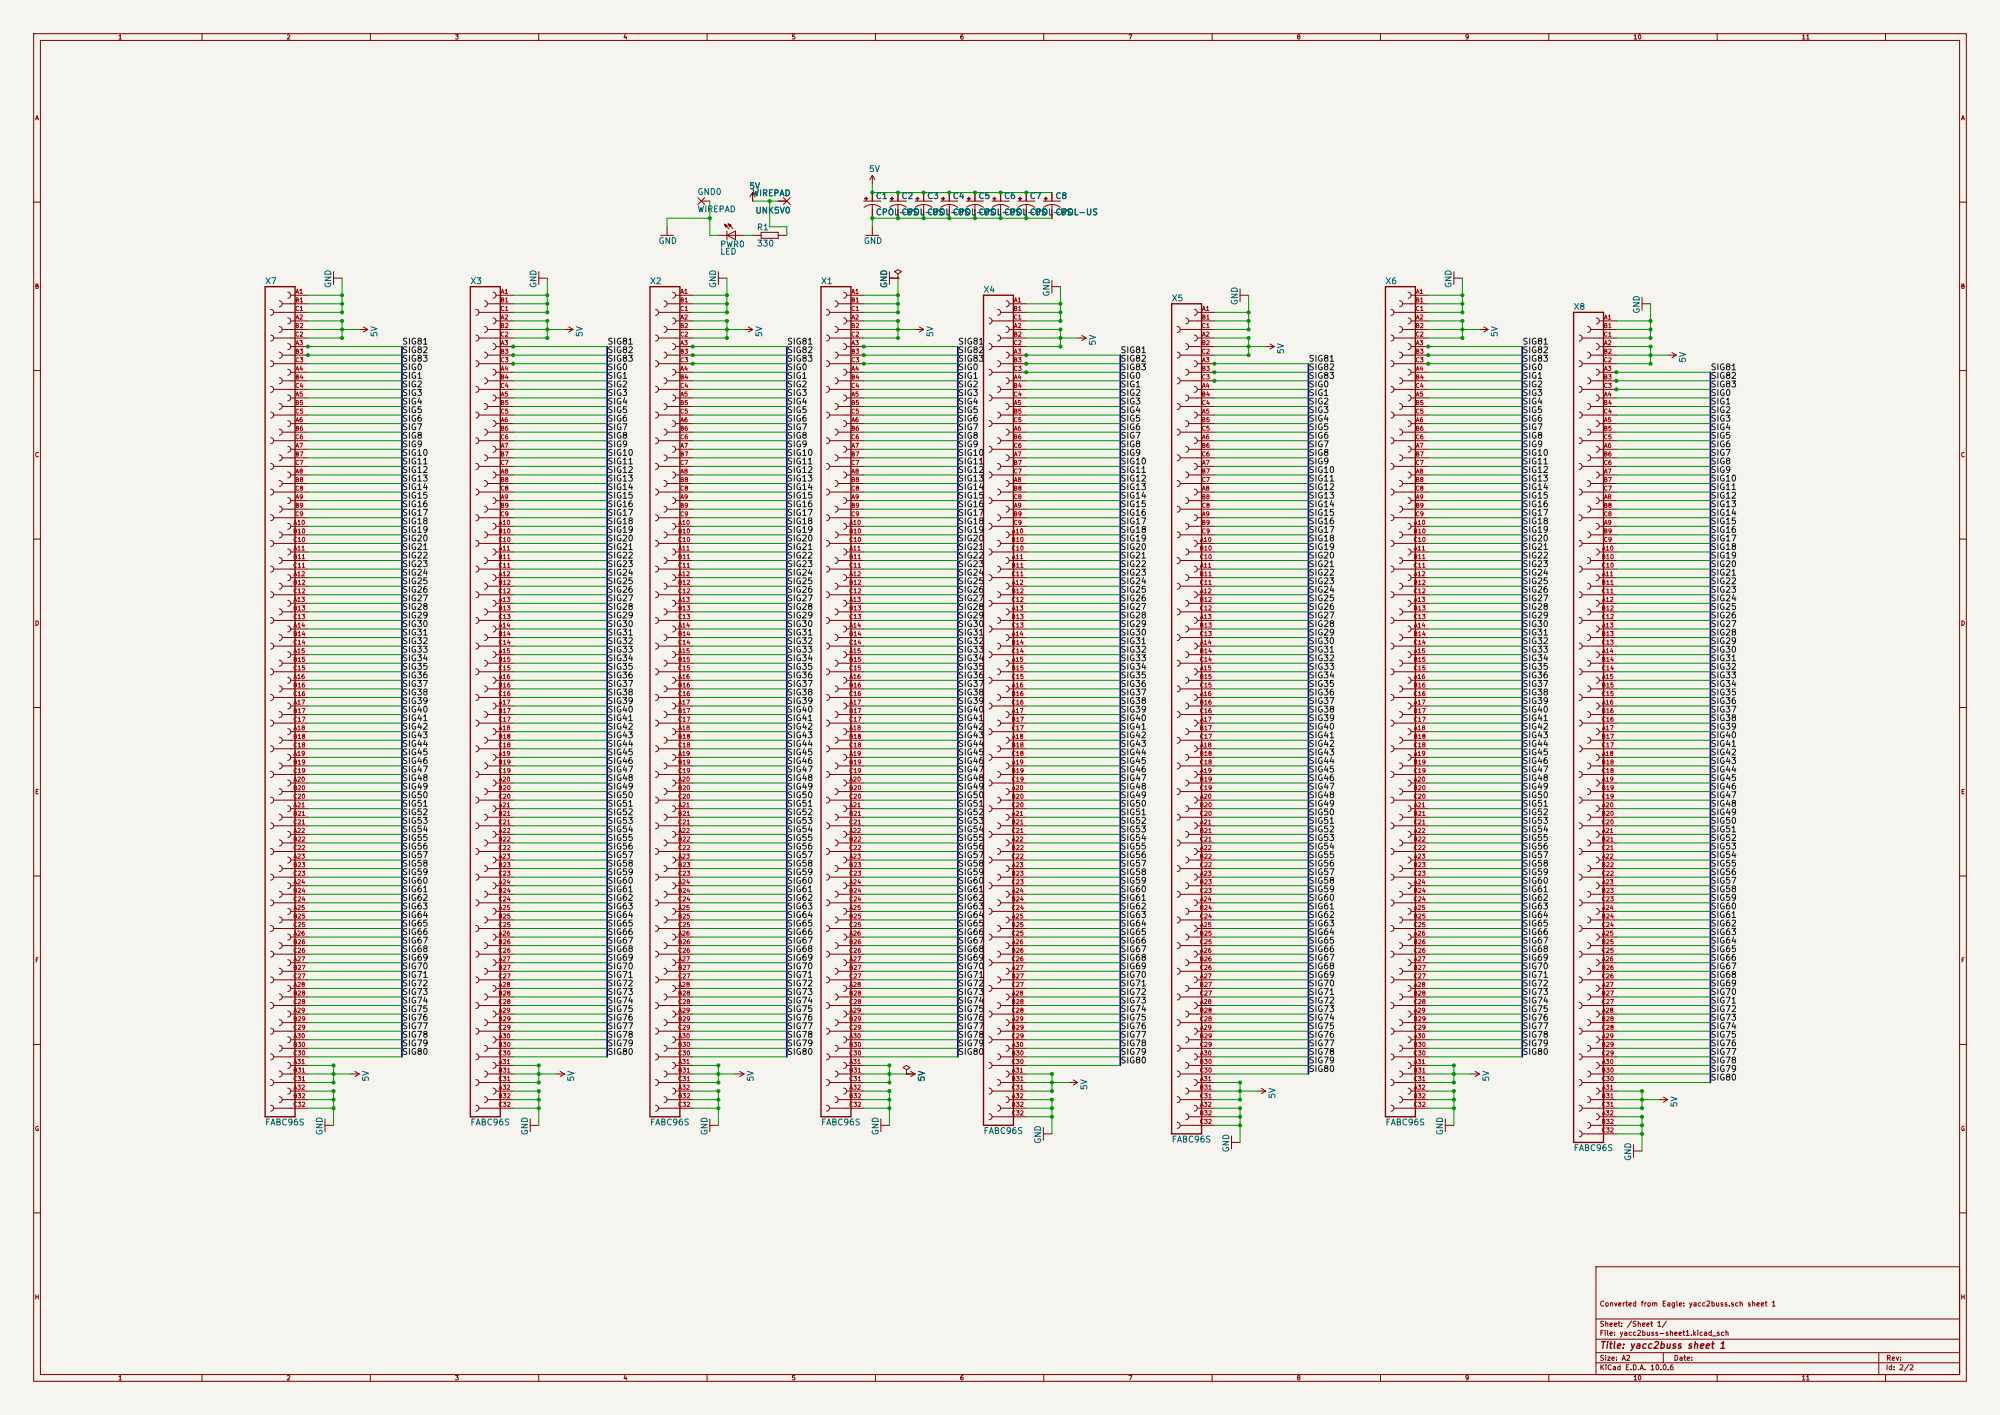
[picture p78: page 2]

Size: A2 | Rev:
KiCad E.D.A. 10.0.6 | Id: 2/2
