ksr/YACC1-D/hardware/bus/backplane/kicad/v2.0/reports/backplane-v2.0-schematic.pdf

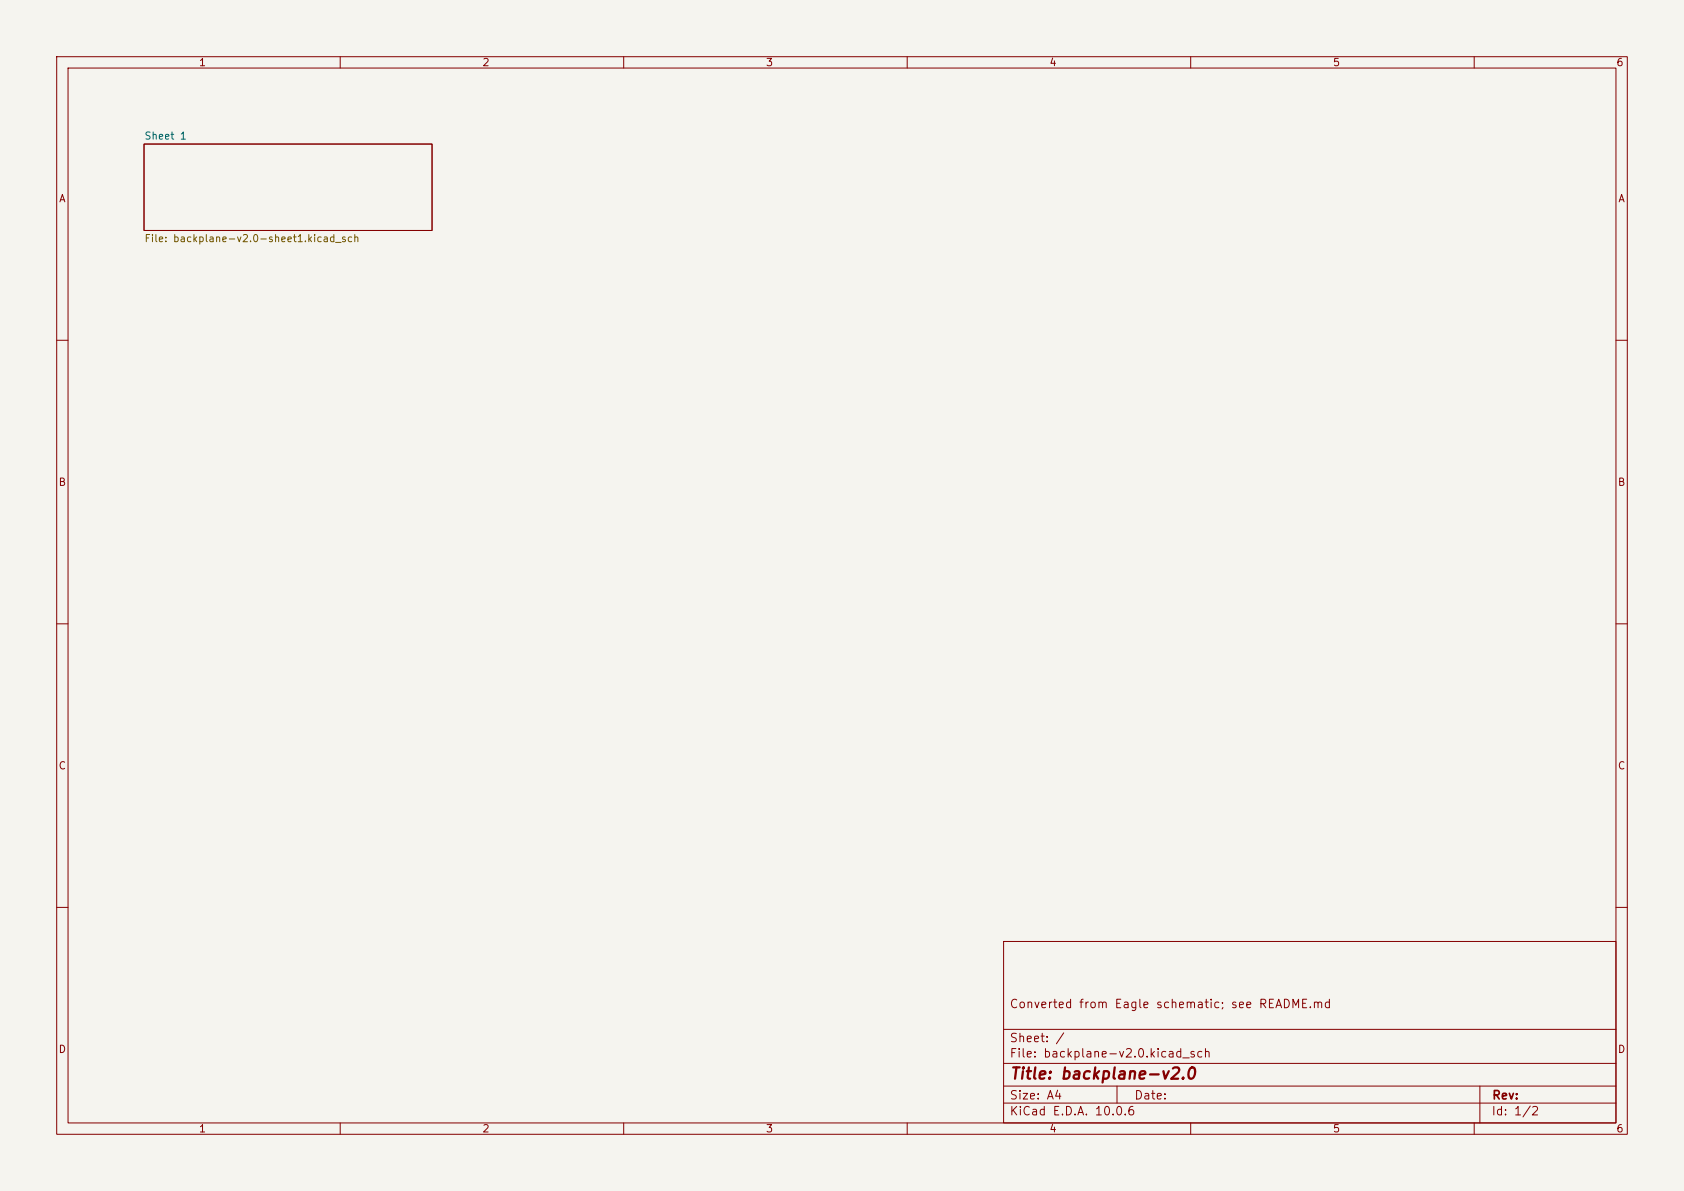
[picture p79: page 1]

Converted from Eagle schematic; see README.md

Size: A4 | Rev:
KiCad E.D.A. 10.0.6 | Id: 1/2

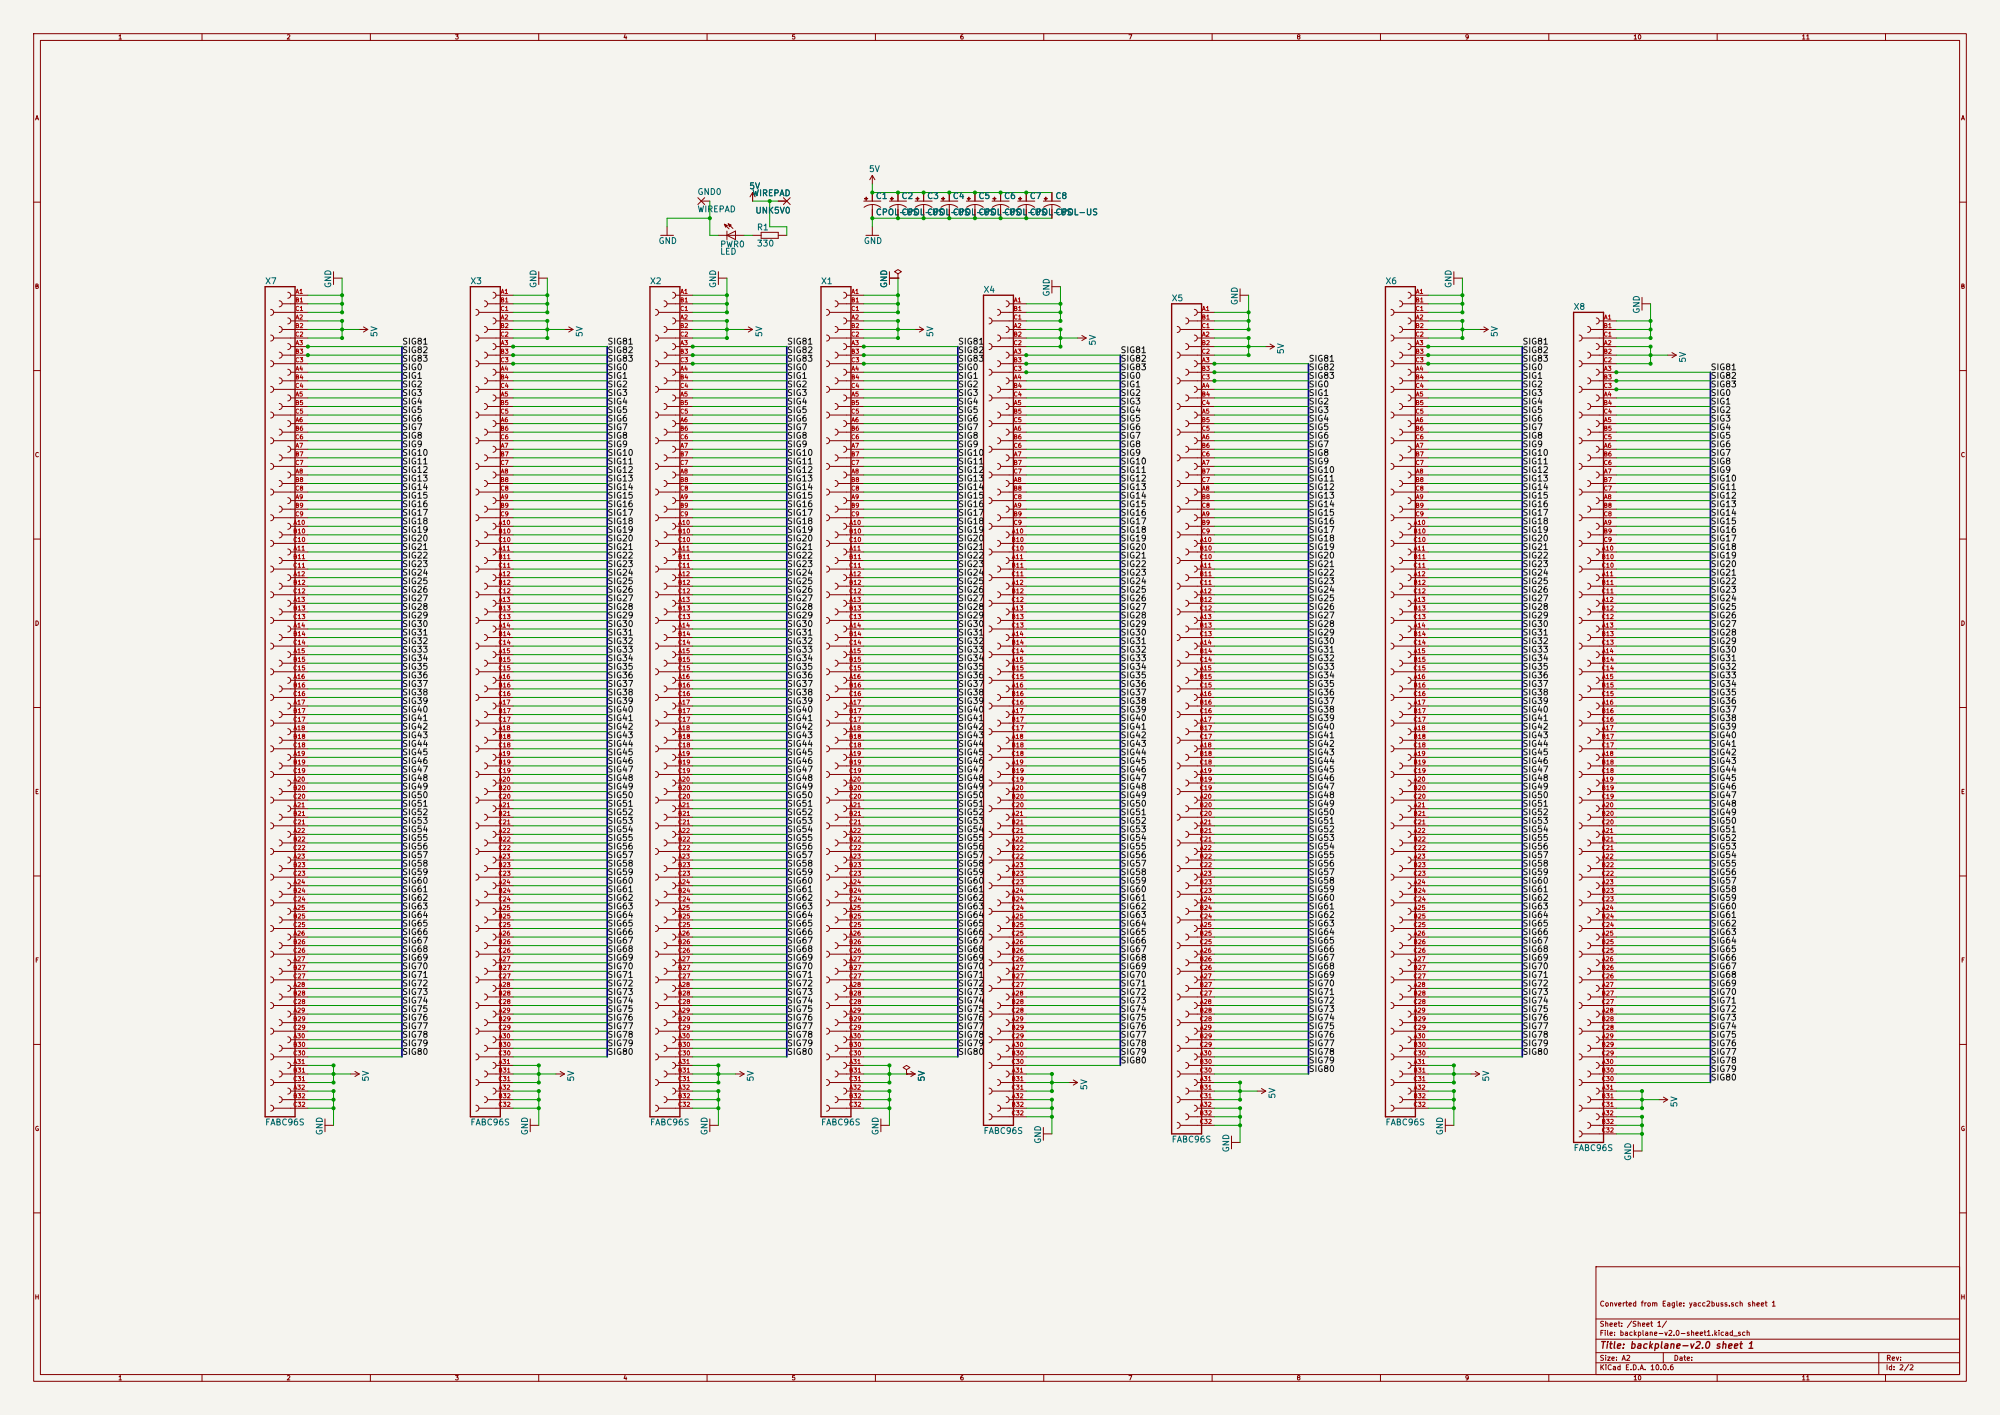
[picture p80: page 2]

Size: A2 | Rev:
KiCad E.D.A. 10.0.6 | Id: 2/2
