ksr/YACC1-D/hardware/bus/blank-card/eagle/v3.2/pdf/Blank V3.2-schematic.pdf

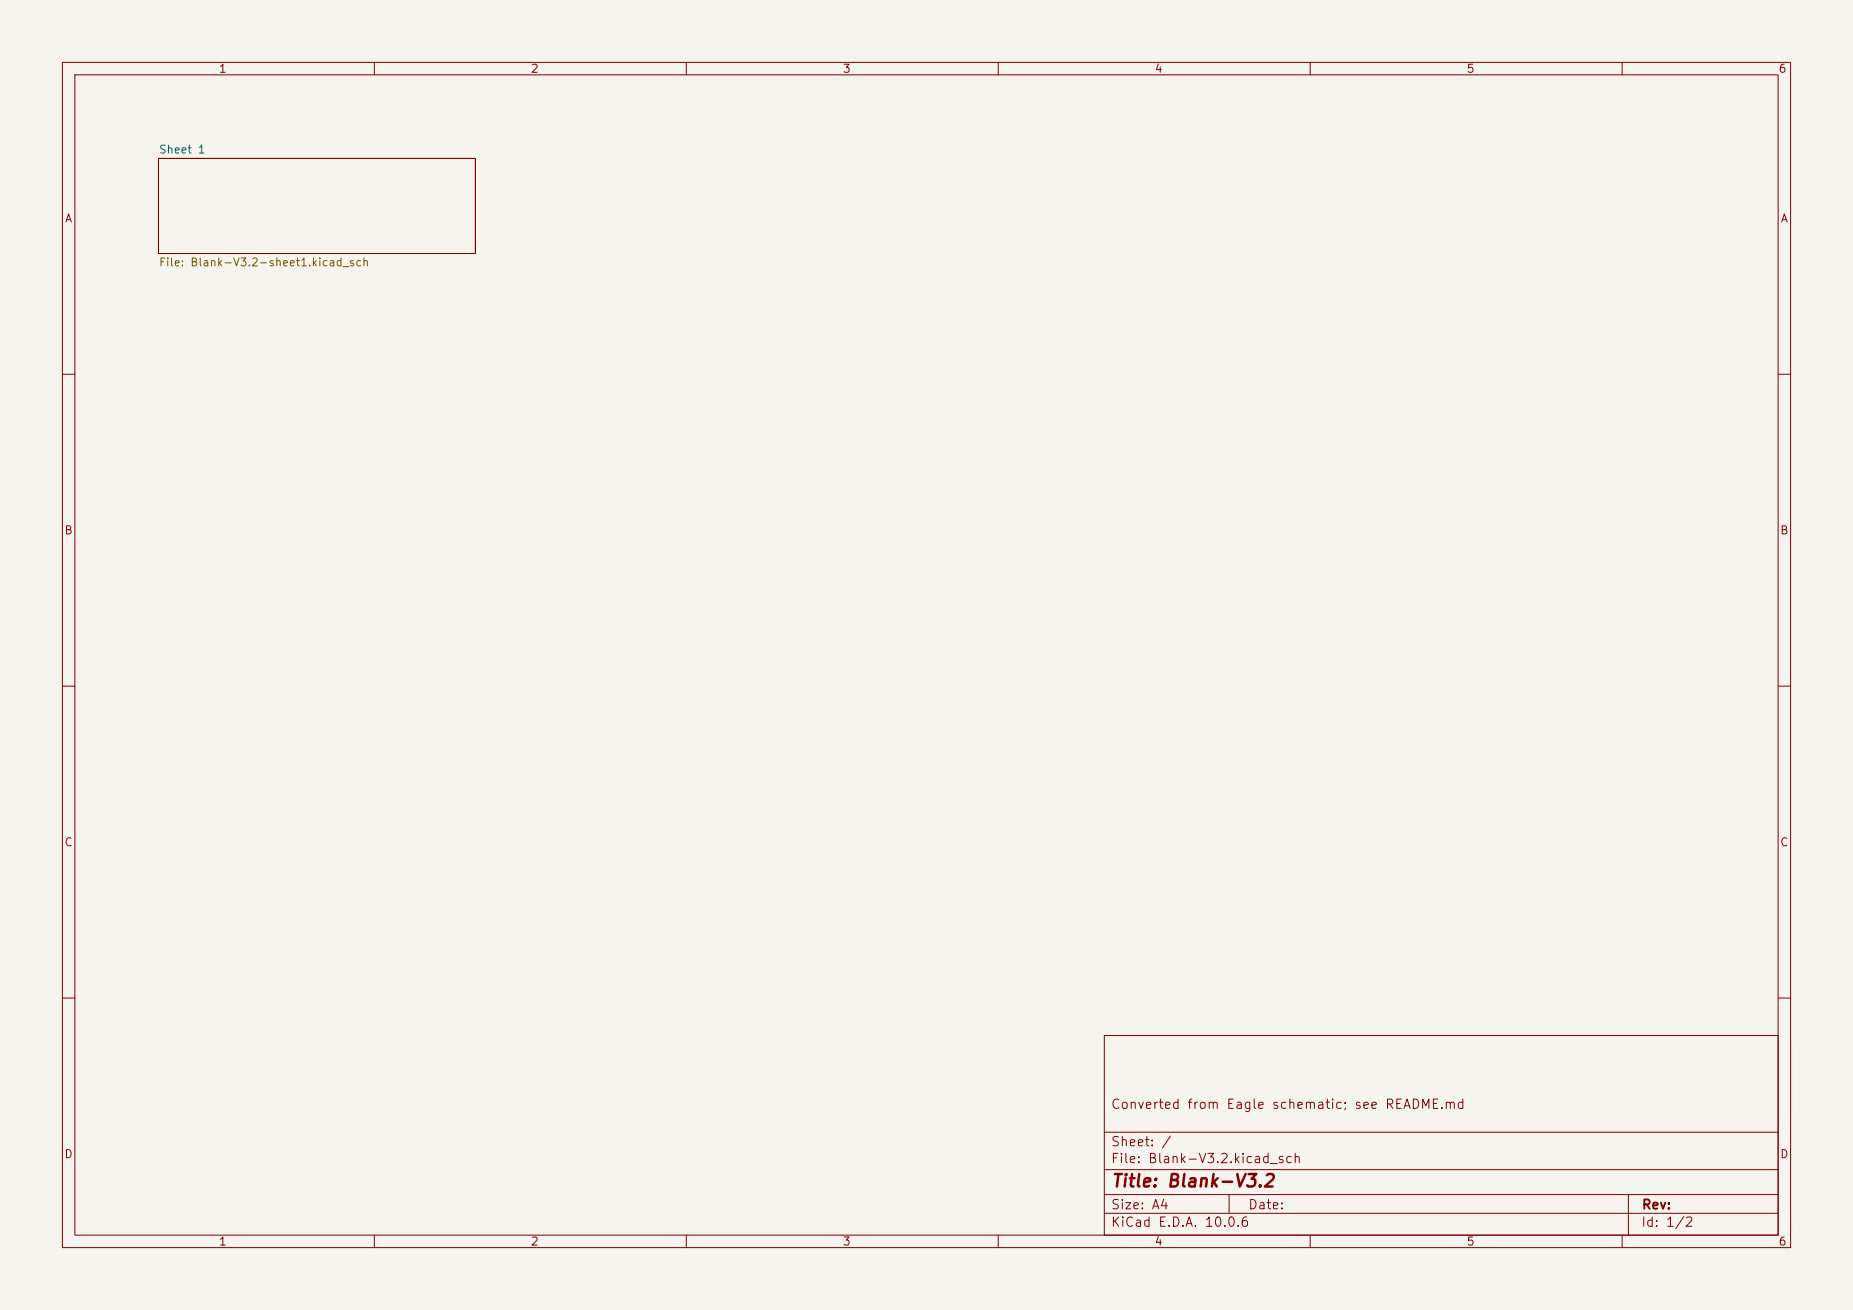
[picture p81: page 1]

Converted from Eagle schematic; see README.md

Size: A4 | Rev:
KiCad E.D.A. 10.0.6 | Id: 1/2

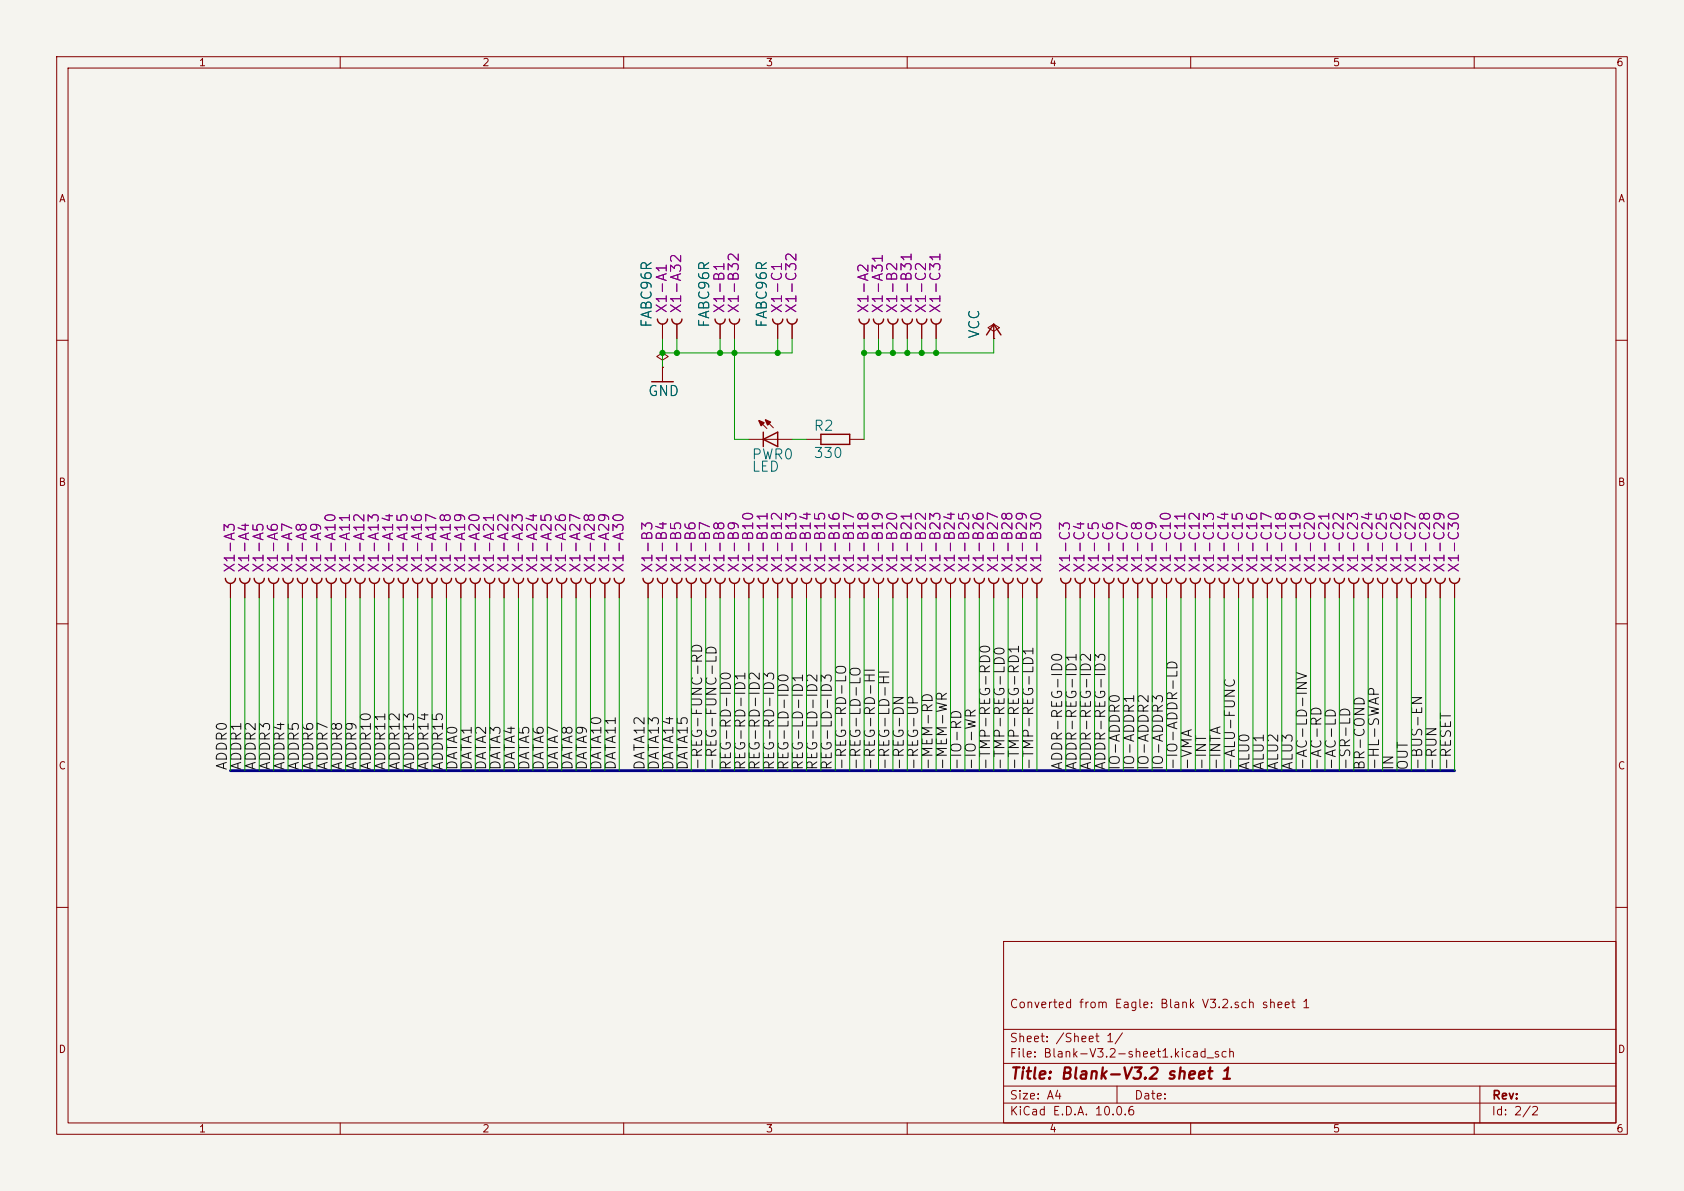
[picture p82: page 2]

Size: A4 | Rev:
KiCad E.D.A. 10.0.6 | Id: 2/2
