ksr/YACC1-D/hardware/bus/bus-jumper-horizontal/eagle/v3.2/pdf/Jumper Board Horizontal V3.1-schematic.pdf

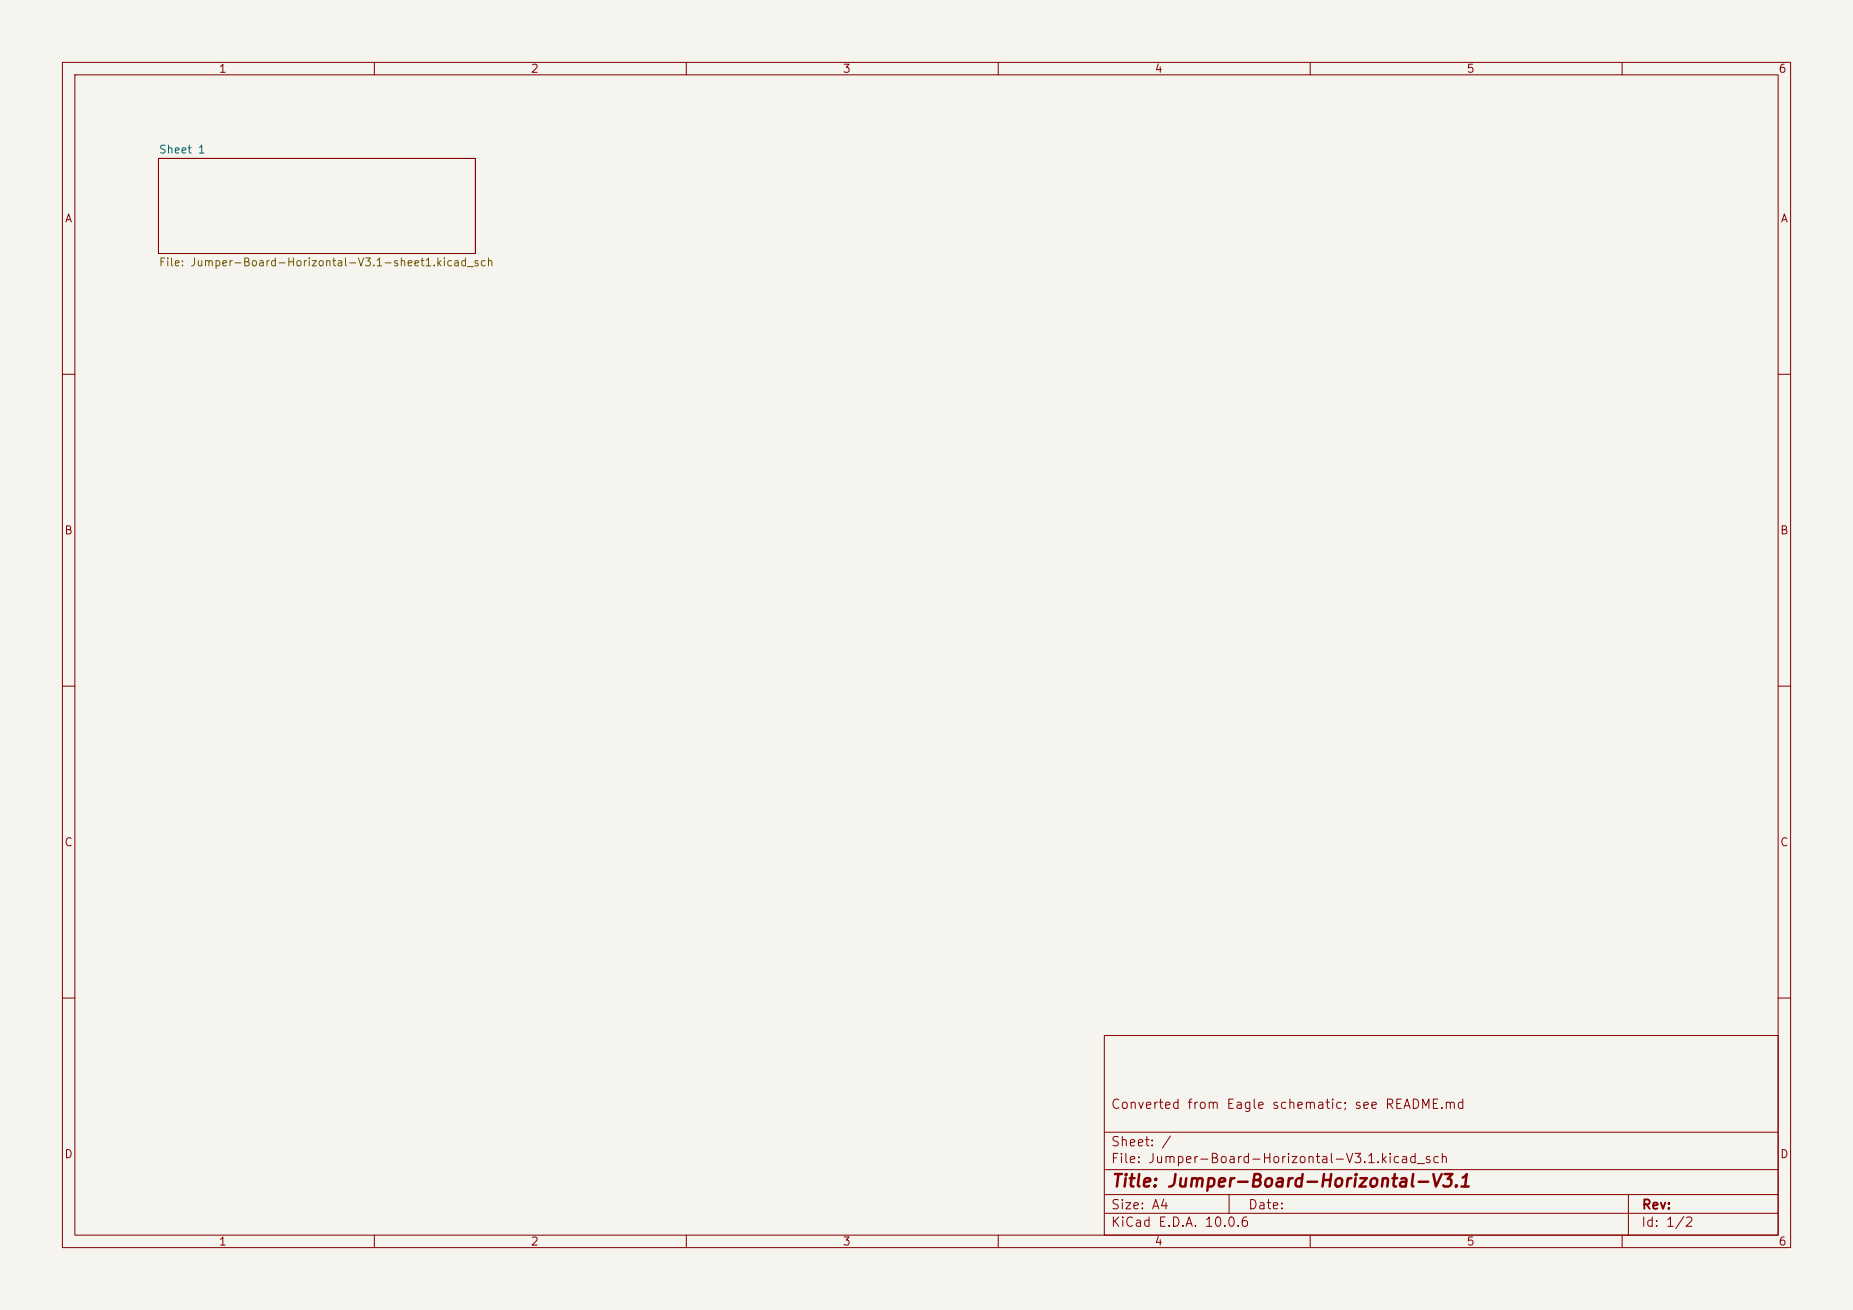
[picture p85: page 1]

File: Jumper-Board-Horizontal-V3.1-sheet1.kicad_sch

Converted from Eagle schematic; see README.md

Sheet: /
File: Jumper-Board-Horizontal-V3.1.kicad_sch
Title: Jumper-Board-Horizontal-V3.1

Size: A4 | Rev:
KiCad E.D.A. 10.0.6 | Id: 1/2

1 | 2 | 3 | 4 | 5 | 6

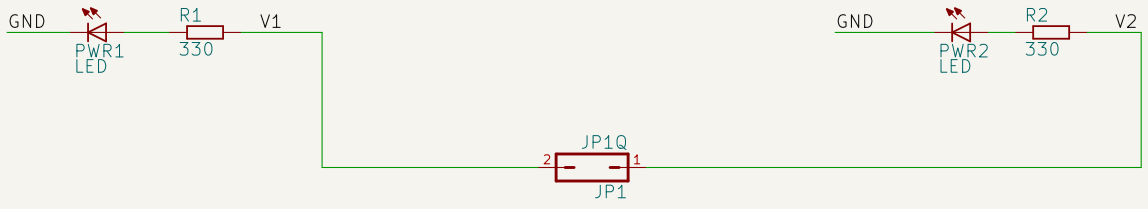
[picture p86: figure]
PWR2; PWR1

1 | 2 | 3 | 4 | 5 | 6

AB

C

D

AB

C

### D Date:

Size: A4 | Rev:
KiCad E.D.A. 10.0.6 | Id: 2/2

## Title: Jumper-Board-Horizontal-V3.1 sheet 1

### File: Jumper-Board-Horizontal-V3.1-sheet1.kicad_sch

### Sheet: /Sheet 1/

Converted from Eagle: Jumper Board Horizontal V3.1.sch sheet 1 X3-B12 | X4-B14 MABC96RX3-A1 | X4-B23 X3-A4 | X4-B20 X3-B15 | X4-B21 X3-B20 | X4-B22 X3-B18 X4-B19 X3-B13 | X3-B16 | X3-B23 X4-A20 | X4-B3 | X4-C4 X3-A19 | X3-A26 | X3-A31 X4-A10 | X3-B9 | X4-B30 | X4-C23 | X3-C29 X4-C14 X3-A2 | X3-A14 | X3-B14 | X3-B22 | X3-C10 X4-A2 | X4-C5 X3-A9 | X3-B2 | X3-B5 X4-B6 | X4-C27 X4-B5 | X3-C25 X4-C8 X3-A25 | X3-C4 X4-A28 | X4-C18 | X3-C22 X4-A6 | X4-A16 | X4-B16 X3-A10 | X3-C14 X4-A17 | X3-C17 X4-B27 | X3-B29 X4-A30 | X4-B25 | X4-C2 X3-A7 | X3-B4 | X4-C22 X3-B7 X4-A3 | MABC96R X4-C1 | X4-C25
LED X4-B2 | X4-B32 | X4-C31
JP1Q | X3-C23 X4-C11 X3-C6 | X3-C27 | X3-C30 X4-C10 X3-A27 X4-A9 | X4-A24 | X4-A29 | X4-C16 X3-C9 X4-A23 | X4-C20 X3-B30 | X3-C21 X4-A19
330 X3-A11 | X3-A16 | X3-C12 X4-B18 X3-A23 X4-A11 | X3-A21 | X3-B19 X4-A12 | X4-A32 | X4-B13 | X4-B26 X3-B10 | X3-B26 X4-A31 | X4-B24 | X4-B28 X3-A5 | X4-C7 MABC96RX3-B1 | X3-B24 MABC96R X4-A1 | X3-A8 | X3-A32 | X3-B6 | X3-B8 | X3-B11 | X4-C26 X4-C3 X3-B31 | X4-C6 | X4-C24 X4-B8 X3-A6 | X4-B9 | X4-B31 | X4-C21 X4-A4 | X4-B29 | X4-C30 X4-B7MABC96R X4-B1 | X4-B4 | X4-C28
LED | X4-B11 | X4-C32 X3-C8 | X3-C24 | X3-C26 X4-C12 | X3-C28 X4-A7 | X3-C31 X4-C9 X3-A29 | X3-C5 | X3-C32 X4-C13 X3-A28 | X3-B32 X4-A25 | X4-A27 | X4-C19 X3-C3 X4-A21 | X4-A26 | X4-C17 X4-A8 | X4-A22 | X4-C15 X3-B3 | X3-B28 | X3-C16 | X3-C18 X3-C19 X3-C20 X4-A14 | X3-A30 X4-A15 X3-A13 | X3-C11 X4-B15 X3-A12 X4-A13 | X3-A15 | X4-B17 X3-A3 | X3-A17 X3-A18 | X3-A20 | X3-A22 | X3-A24 | X3-B21 | X3-C2 | X3-C13 | X3-C15 X4-A18 | X3-B17 X4-B10 | X4-B12 | X3-B25 | X3-B27 | MABC96RX3-C1 X4-A5 | X3-C7 | X4-C29
330 | GND | V2 V1 GND
GND | V1 | V1 GND V2 | GND
GND V2 | V2 | V1 GNDGNDV1 | V2 V1

V2 V2

V1 | X3-B14 X3-B15 X3-B16 X3-B17 X3-B18 X3-B19 X3-B20 X3-B21 X3-B22 X3-B23 X3-B24 X3-B25 X3-B26 X3-B27 X3-B28 X3-B29 | X3-B31 | MABC96RX3-B30 | X3-B32 | X3-C1 X3-C2 X3-C3 X3-C4 X3-C5 X3-C6 X3-C7 X3-C8 X3-C9 X3-C10 X3-C11 X3-C12 X3-C13 X3-C14 X3-C15 X3-C16 X3-C17 X4-C11 X4-C12 | X4-C21 X4-C22 X4-C23 X4-C24 X4-C25 X4-C26 X4-C27 X4-C28 X4-C29 X4-C30 X4-C31 X4-C32 X4-C8 X4-C9 X4-B14 X4-B15 X4-B16 X4-B17 X4-B18 X4-B19 X4-B20 X4-B21 X4-B22 X4-B23 X4-B24 X4-B25 X4-B26 X4-B27 X4-B28 | X4-C10 | X4-C13 X4-C14 X4-C15 X4-C16 X4-C17 X4-C18 X4-C19 X4-C20 X4-C2 X4-C3 X4-C4 X4-C5 X4-C6 X4-C7MABC96R X4-C1 X4-B29 X4-B30 X4-B31 X4-B32 X3-A10 X3-A11 X3-A12 X3-A13 X3-A14 X3-A15 X3-A16 X3-A17 X3-A18 X3-A19 X3-A20 X3-A21 X3-A22 X3-A23 X3-A24 | X3-C18 X3-C19 X3-C20 X3-C21 X3-C22 X3-C23 X3-C24 X3-C25 X3-C26 X3-C27 X3-C28 X3-C29 X3-C30 X3-C31 X3-C32 X4-B4 X4-B5 X4-B6 X4-B7 X4-B8 X4-B9 X3-B4 X3-B5 X3-B6 X3-B7 X3-B8 X3-B9 X3-B10 X3-B11 X3-B12 X3-B13 X4-A14 X4-A15 X4-A16 X4-A17 X4-A18 X4-A19 X4-A20 X4-A21 X4-A22 X4-A23 X4-A24 X4-A25 X4-A26 X4-A27 X4-A28 X4-A29 | X4-B10 X4-B11 X4-B12 X4-B13 X3-A25 X3-A26 X3-A27 X3-A28 X3-A29 X3-A30 X3-A31 X3-A32 | X3-B2 X3-B3 MABC96RX3-B1 X4-A30 X4-A31 | X4-B3 X4-A32 | MABC96R X4-B1 X4-B2 X3-A5 X3-A6 X3-A7 X3-A8 X3-A9 X4-A10 X4-A11 X4-A12 X4-A13 X4-A3 X4-A4 X4-A5 X4-A6 X4-A7 X4-A8 X4-A9MABC96R X4-A1 X4-A2 X3-A3 X3-A4 MABC96RX3-A1 X3-A2
