ksr/YACC1-D/hardware/bus/bus-template/eagle/v3.2/pdf/Bus Template V3.2-schematic.pdf

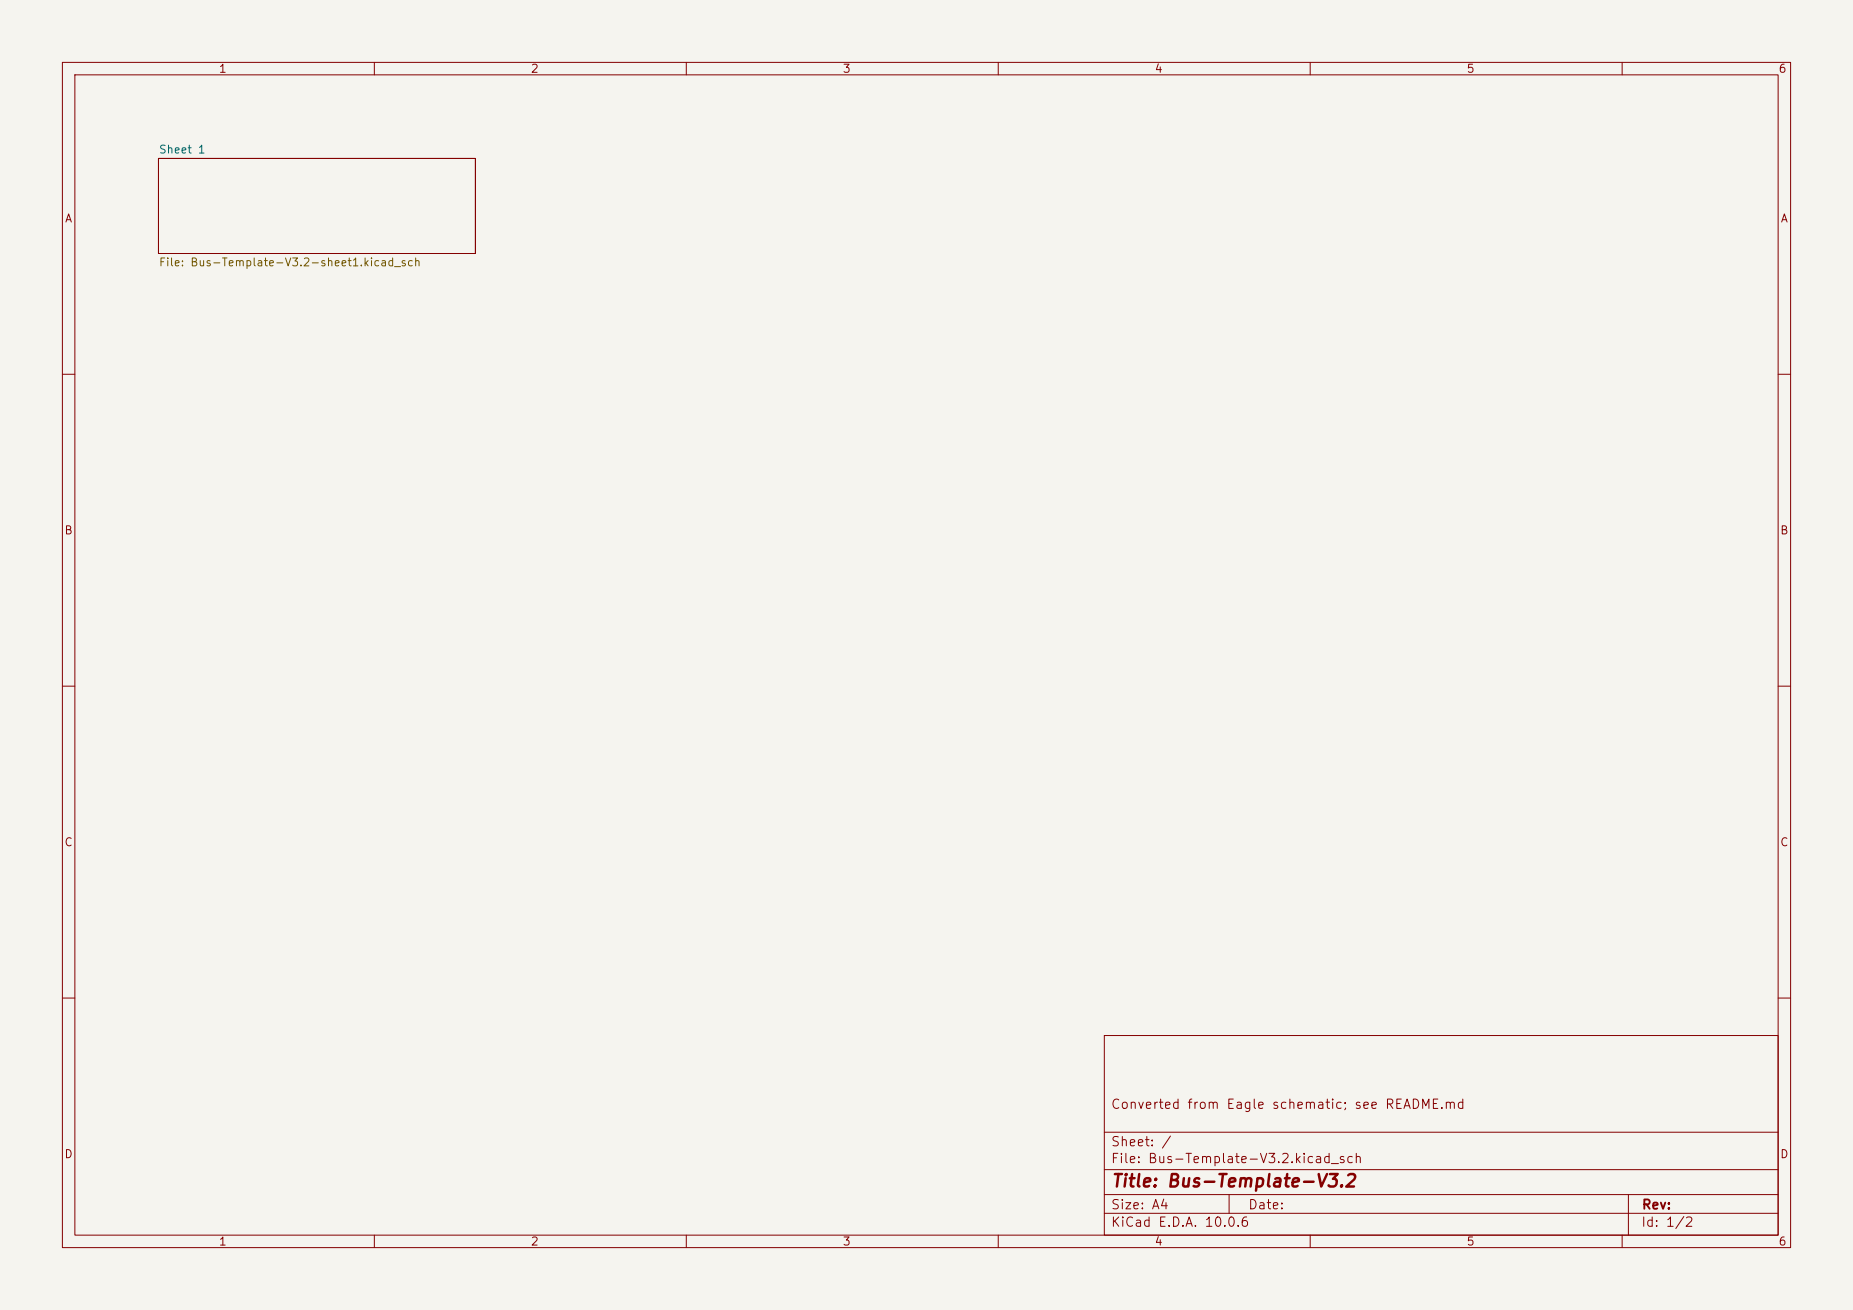
[picture p87: page 1]

Converted from Eagle schematic; see README.md

Size: A4 | Rev:
KiCad E.D.A. 10.0.6 | Id: 1/2

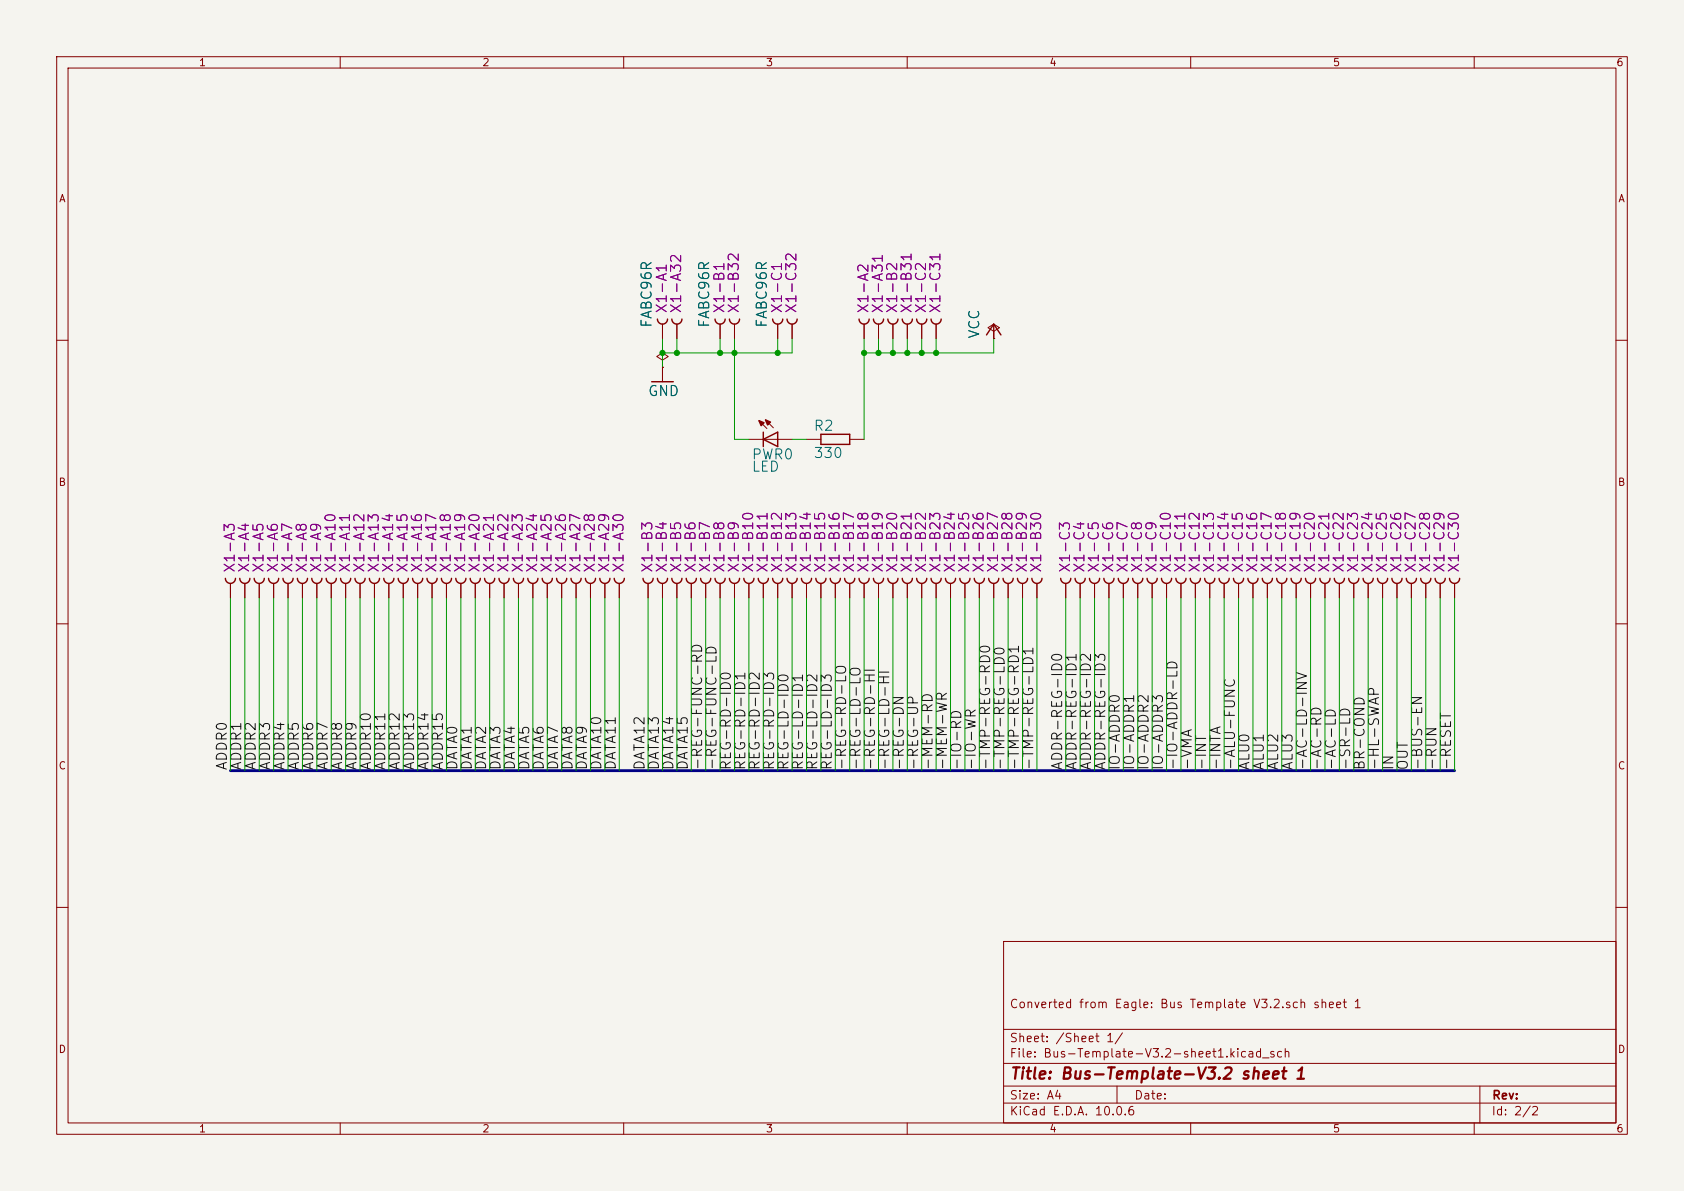
[picture p88: page 2]

Sheet: /Sheet 1/
File: Bus-Template-V3.2-sheet1.kicad_sch
Title: Bus-Template-V3.2 sheet 1

Size: A4 | Rev:
KiCad E.D.A. 10.0.6 | Id: 2/2
