ksr/YACC1-D/hardware/cards/alu/eagle/v3.2/pdf/ALU V3.2-schematic.pdf

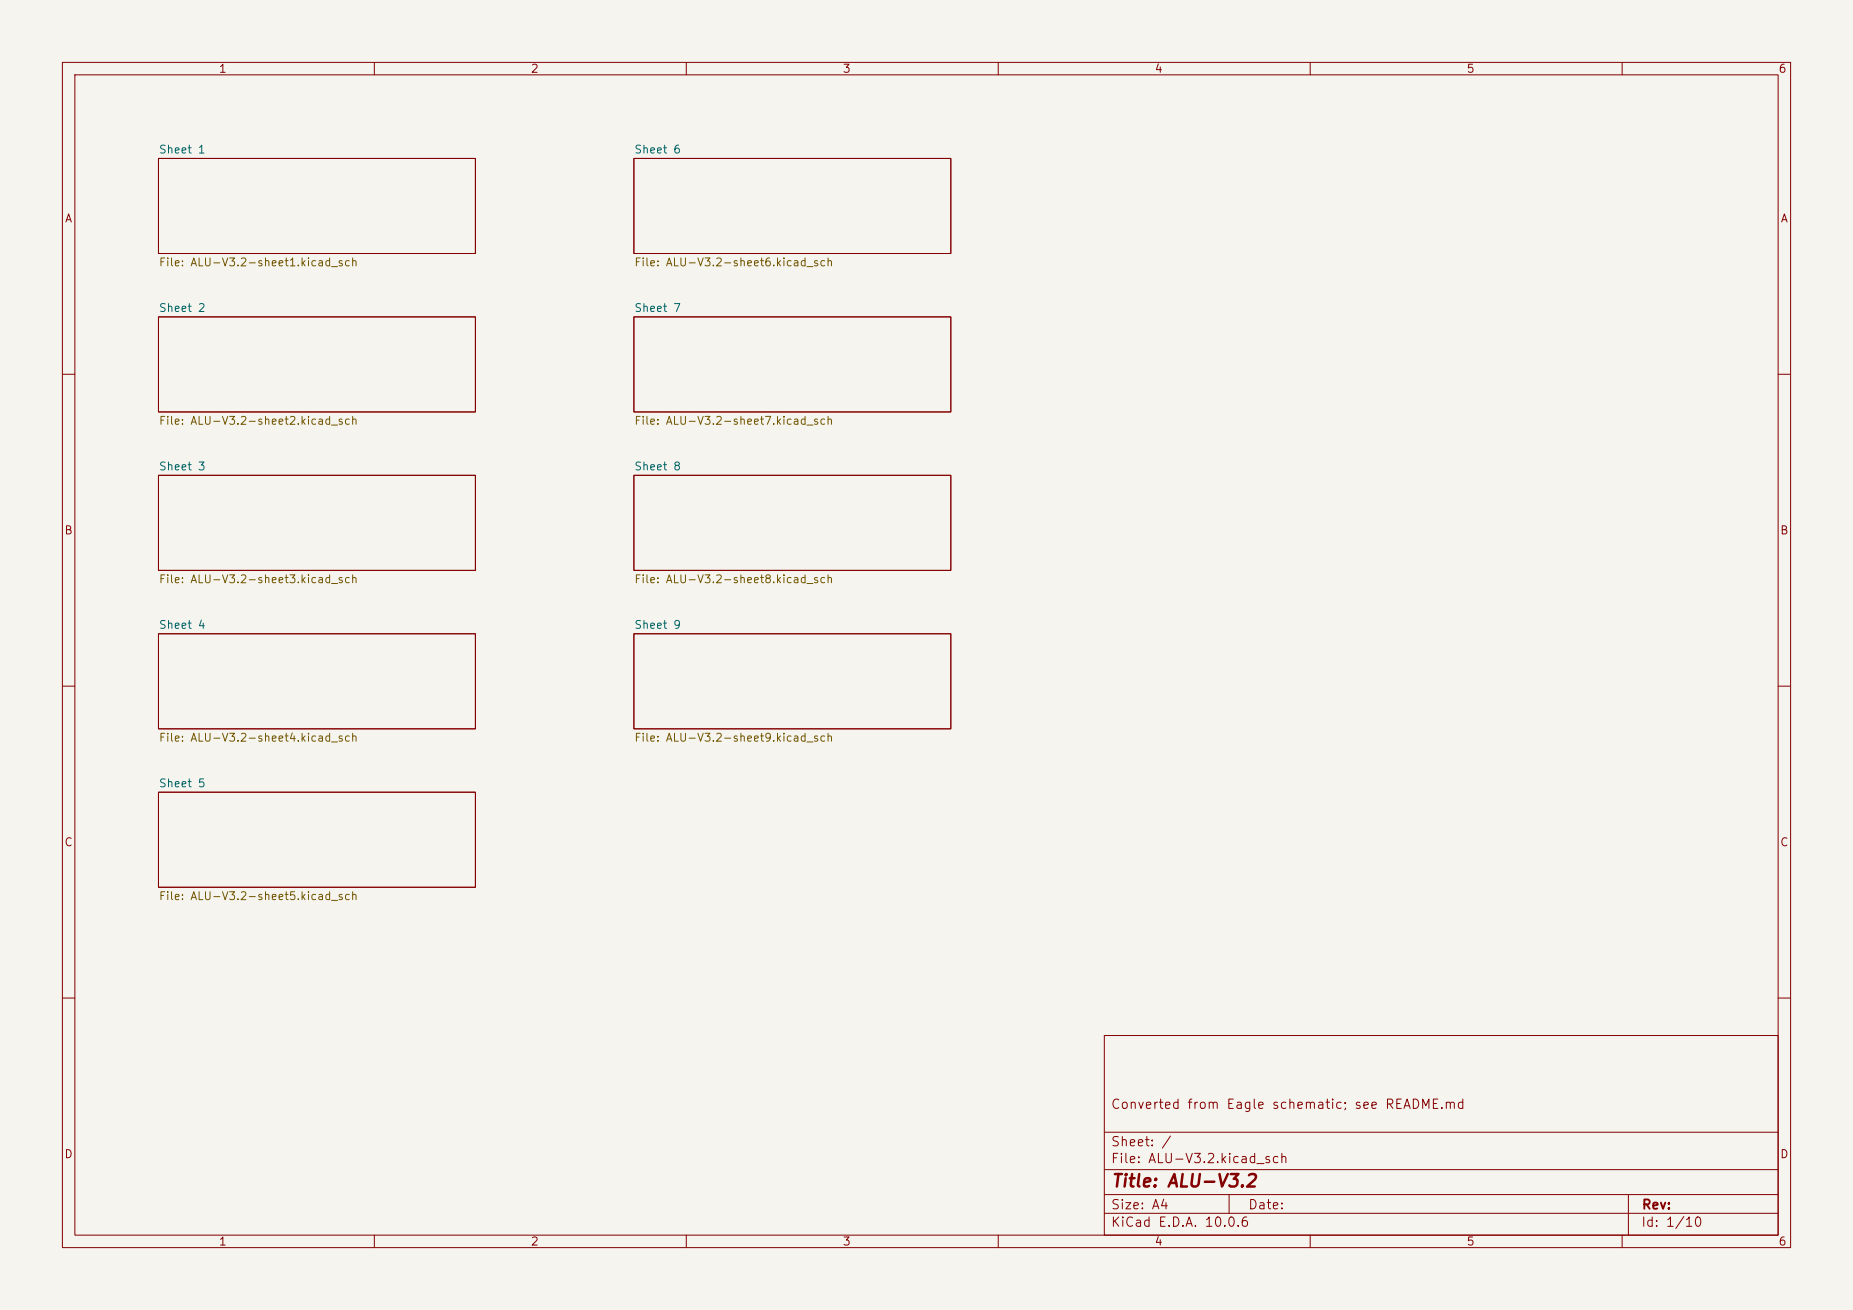
[picture p91: page 1]

Converted from Eagle schematic; see README.md

Size: A4 | Rev:
KiCad E.D.A. 10.0.6 | Id: 1/10

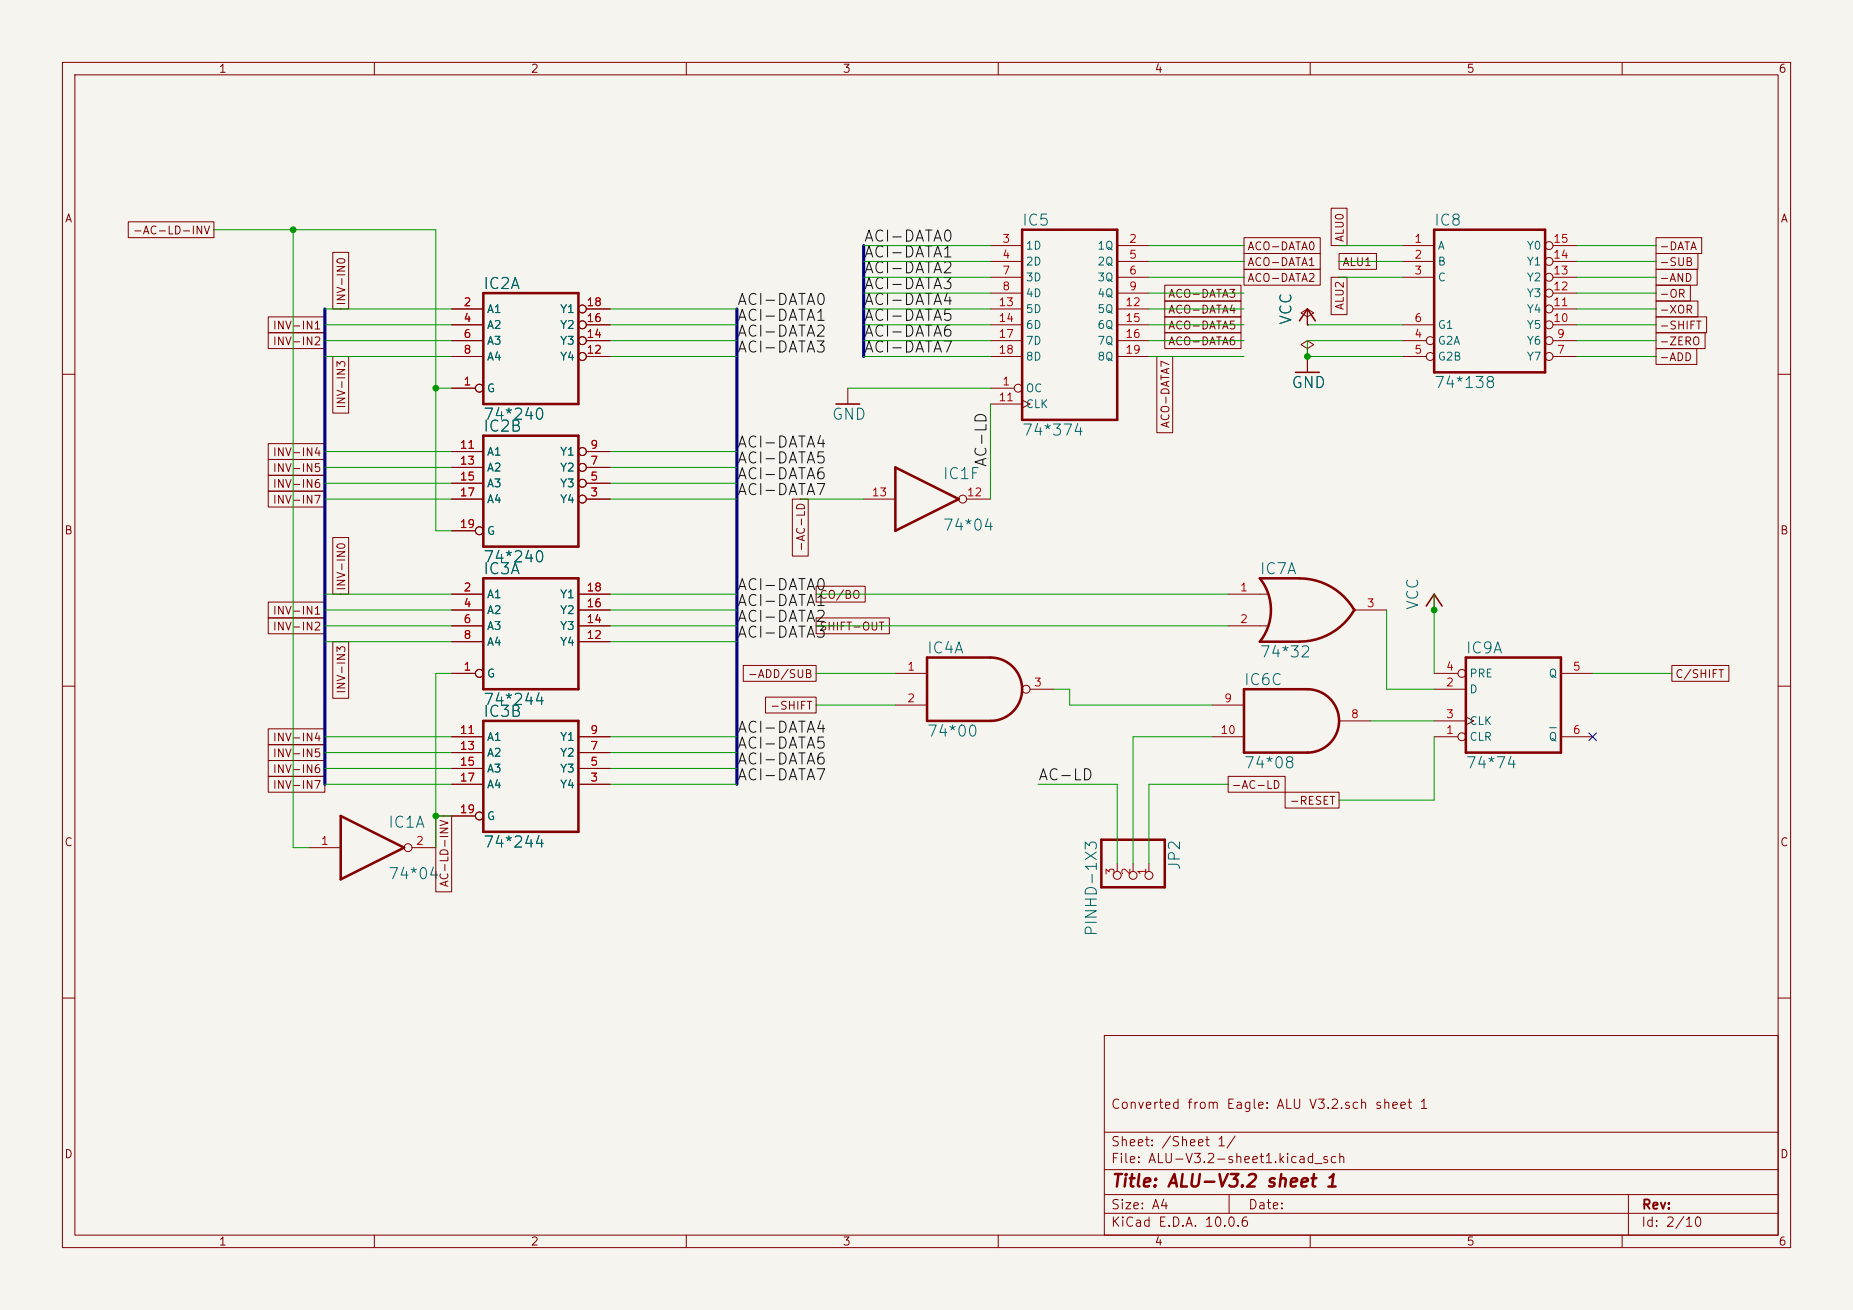
[picture p92: page 2]

ACO-DATA1 -AC-LD -RESET

INV-IN2 -AC-LD-INV

A2 13
A3 15

Converted from Eagle: ALU V3.2.sch sheet 1

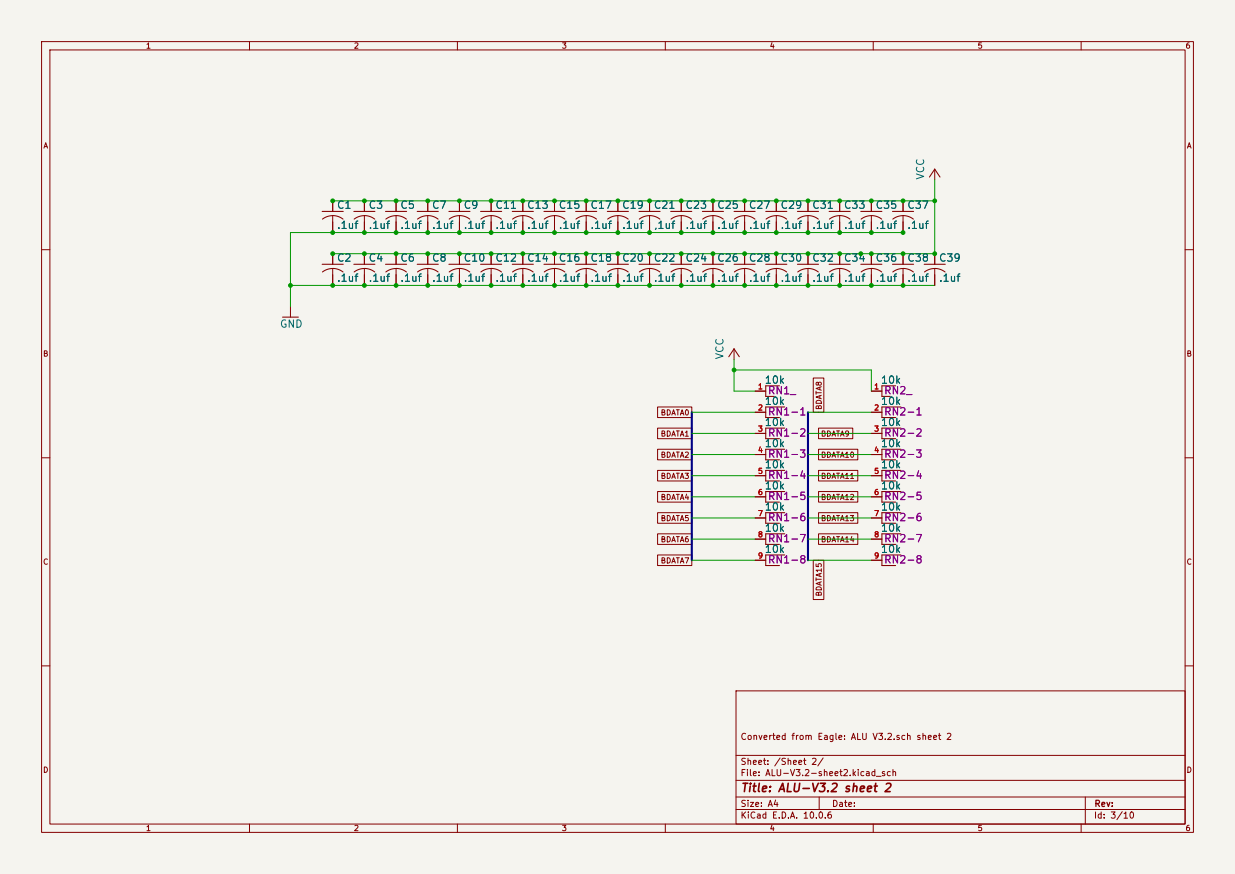
[picture p93: page 3]

Converted from Eagle: ALU V3.2.sch sheet 2

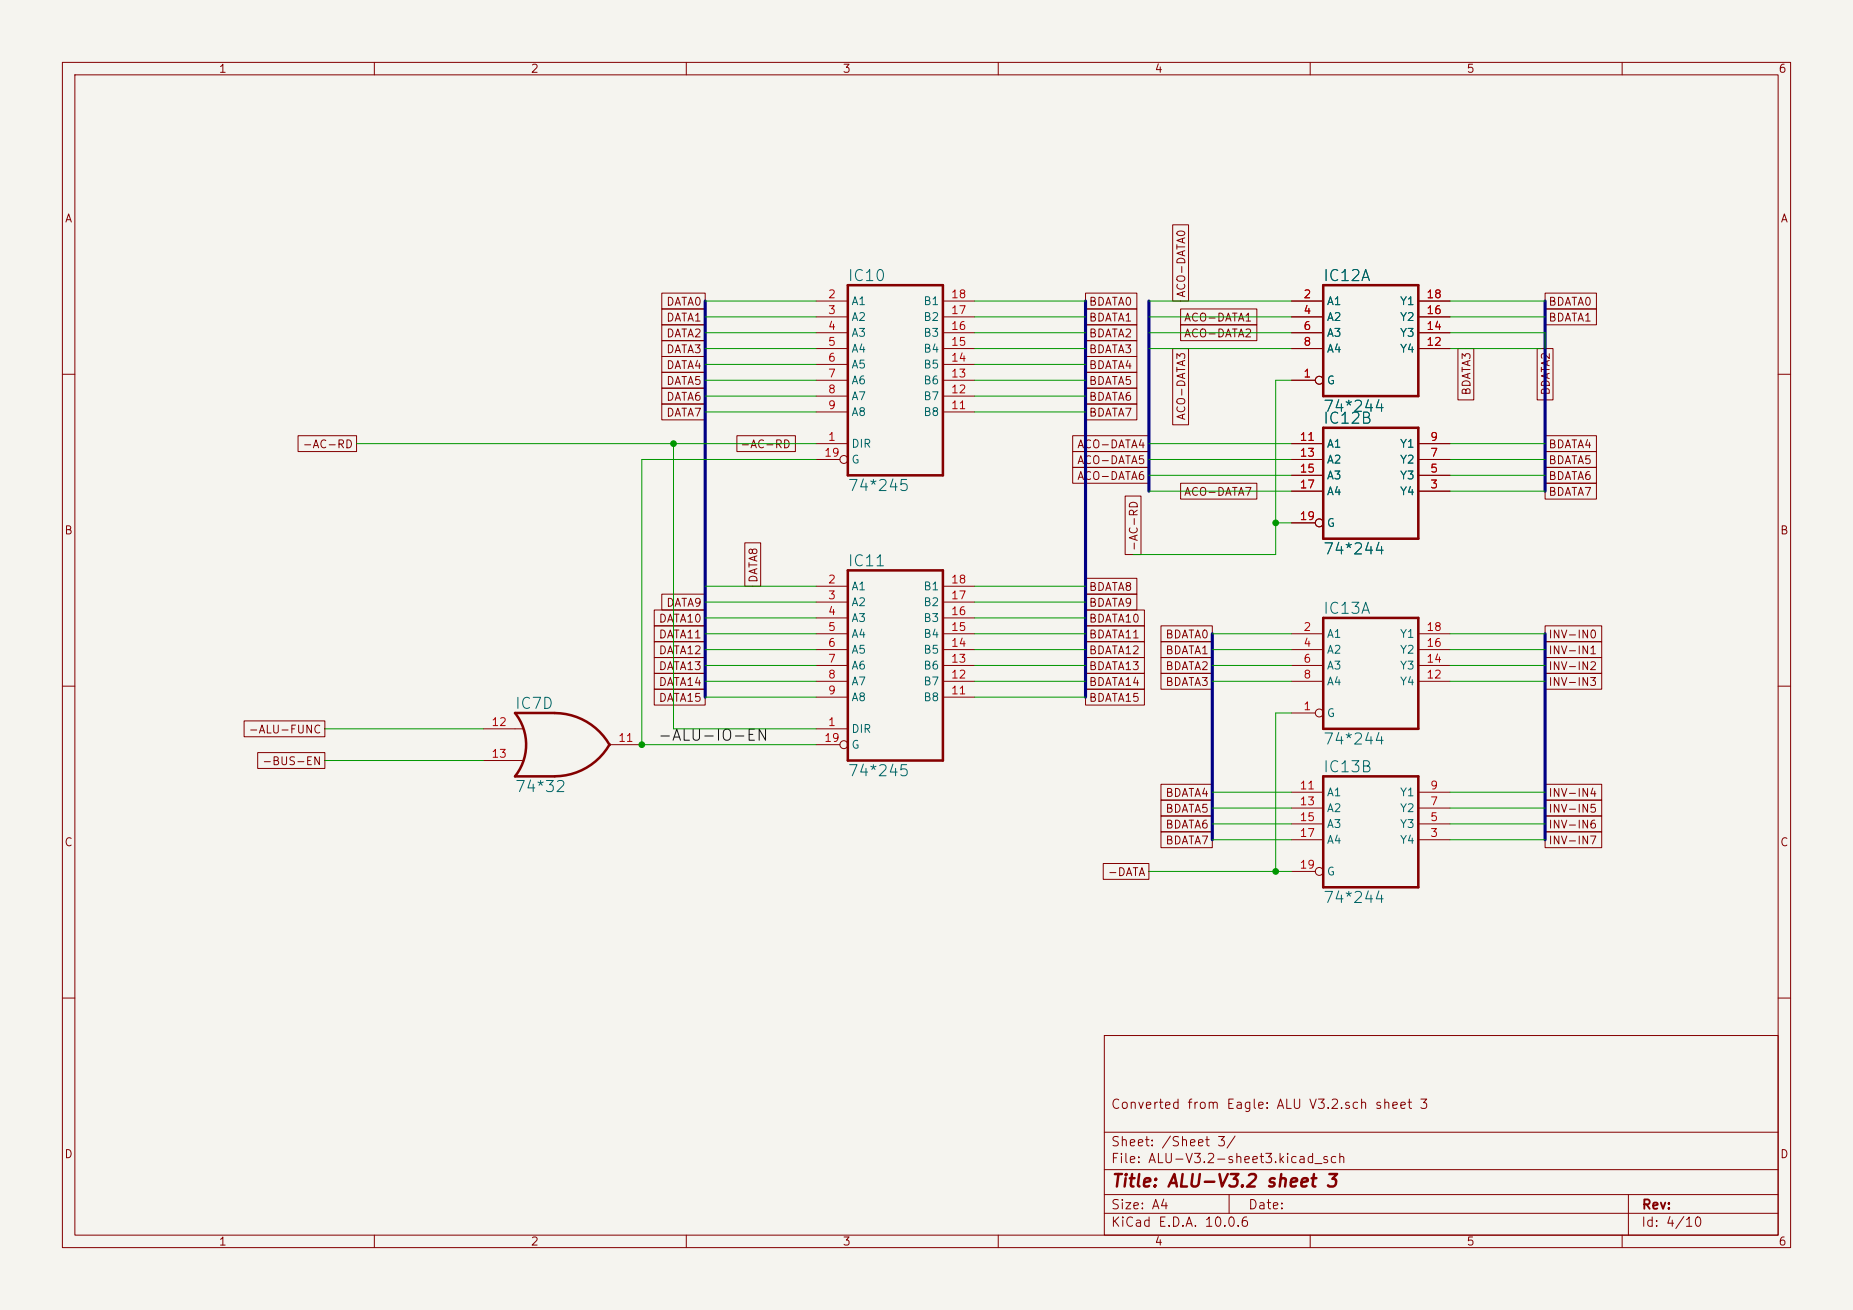
[picture p94: page 4]

INV-IN0 BDATA1 -ALU-IO-EN

Converted from Eagle: ALU V3.2.sch sheet 3

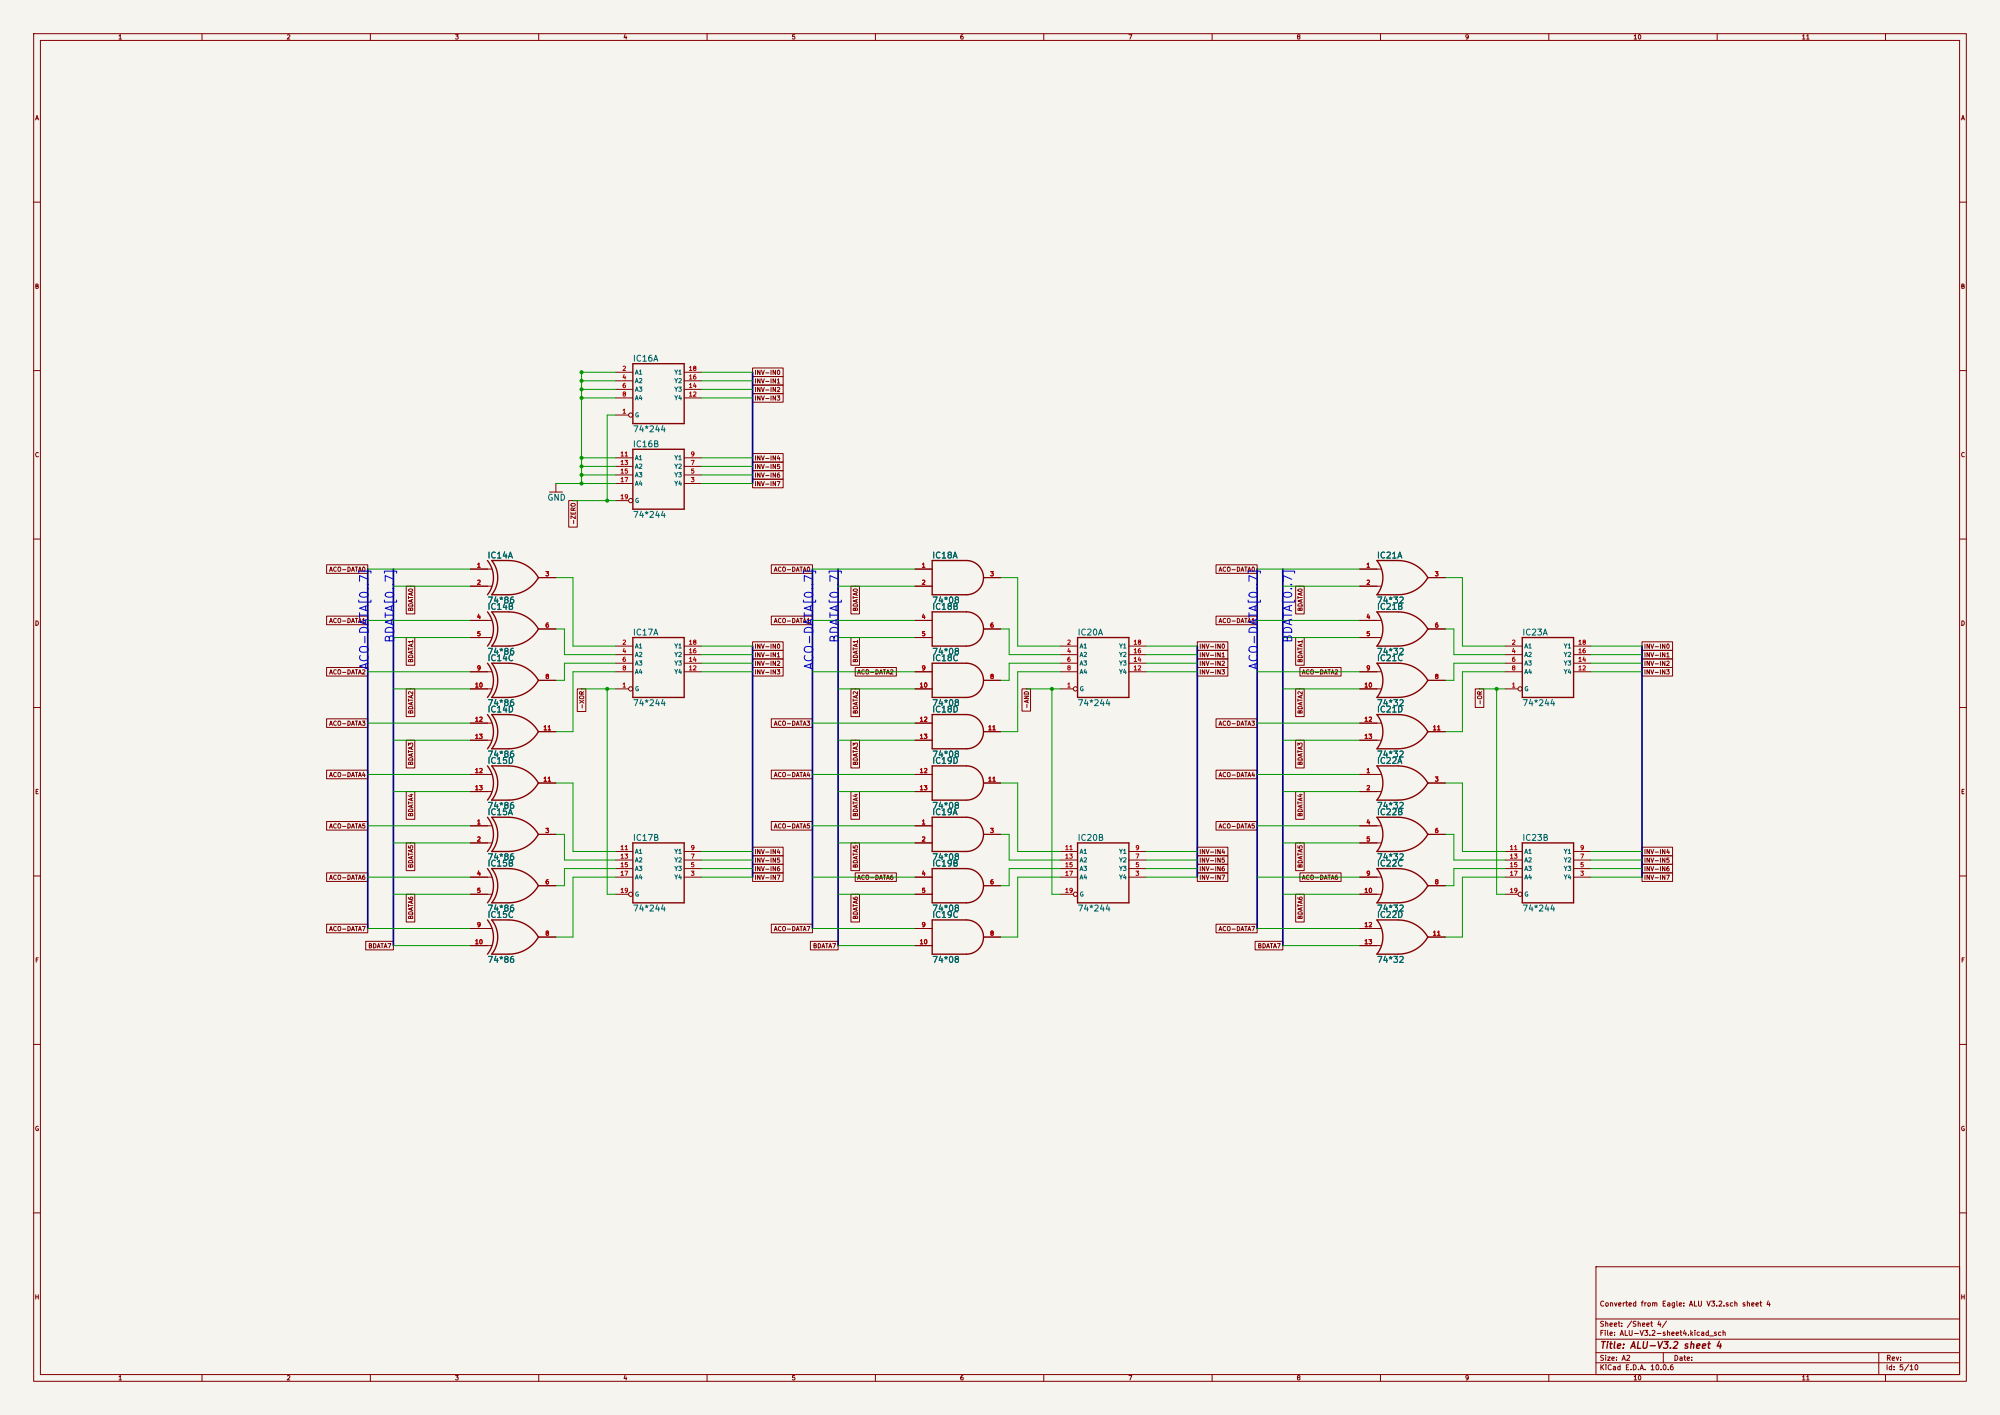
[picture p95: page 5]

Converted from Eagle: ALU V3.2.sch sheet 4

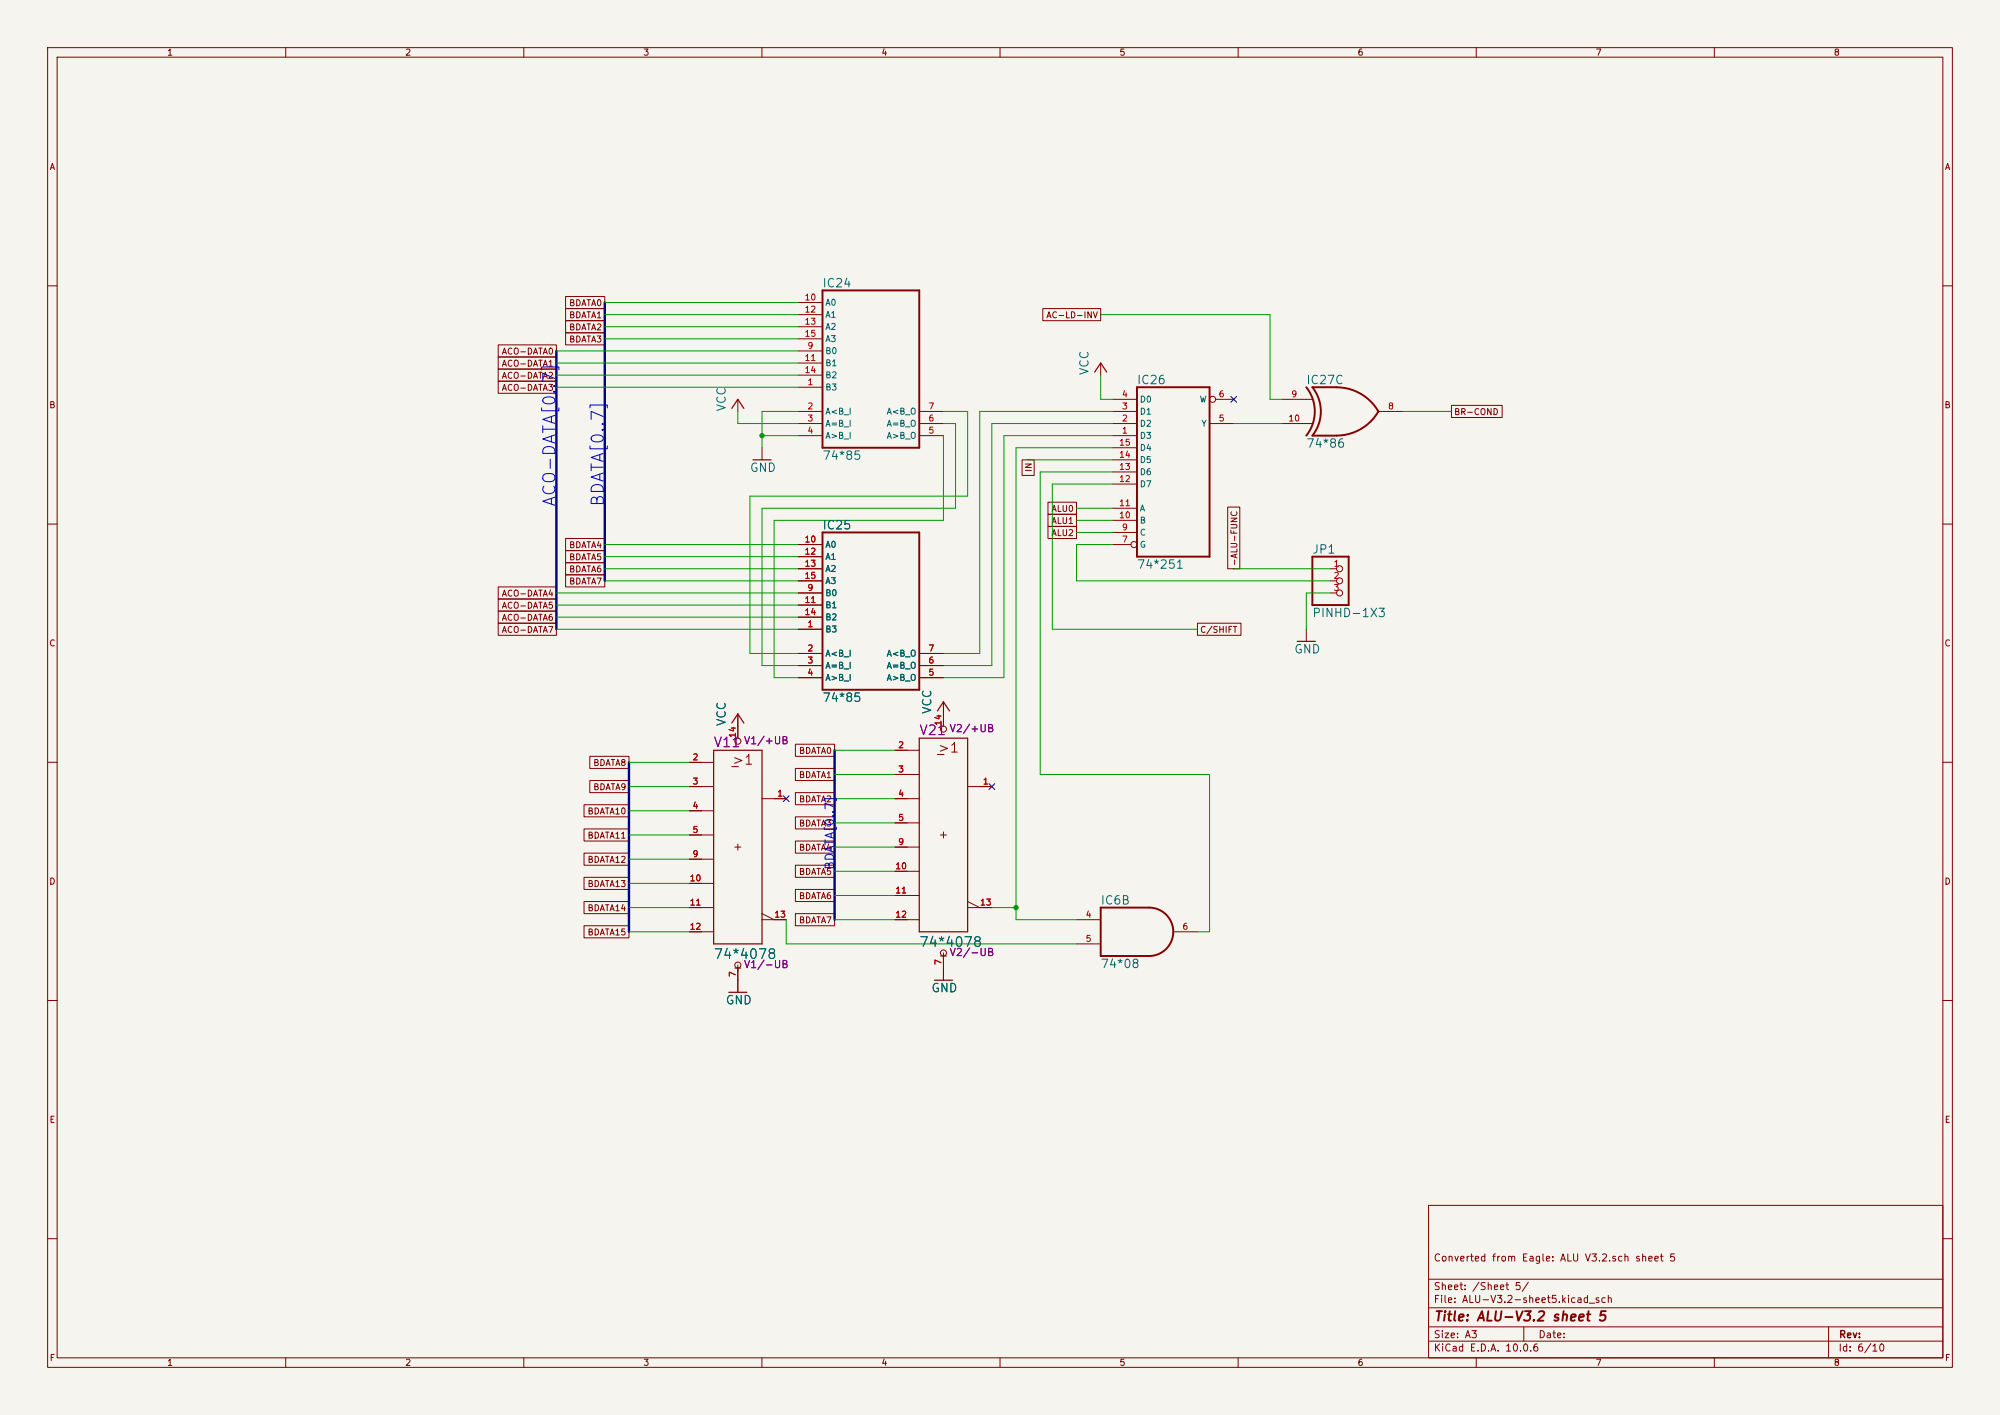
[picture p96: page 6]

A1 12
A2 13 B2 14 A2 13 B2 14 A3 15

A<B_I 2
A=B_I 3

Converted from Eagle: ALU V3.2.sch sheet 5

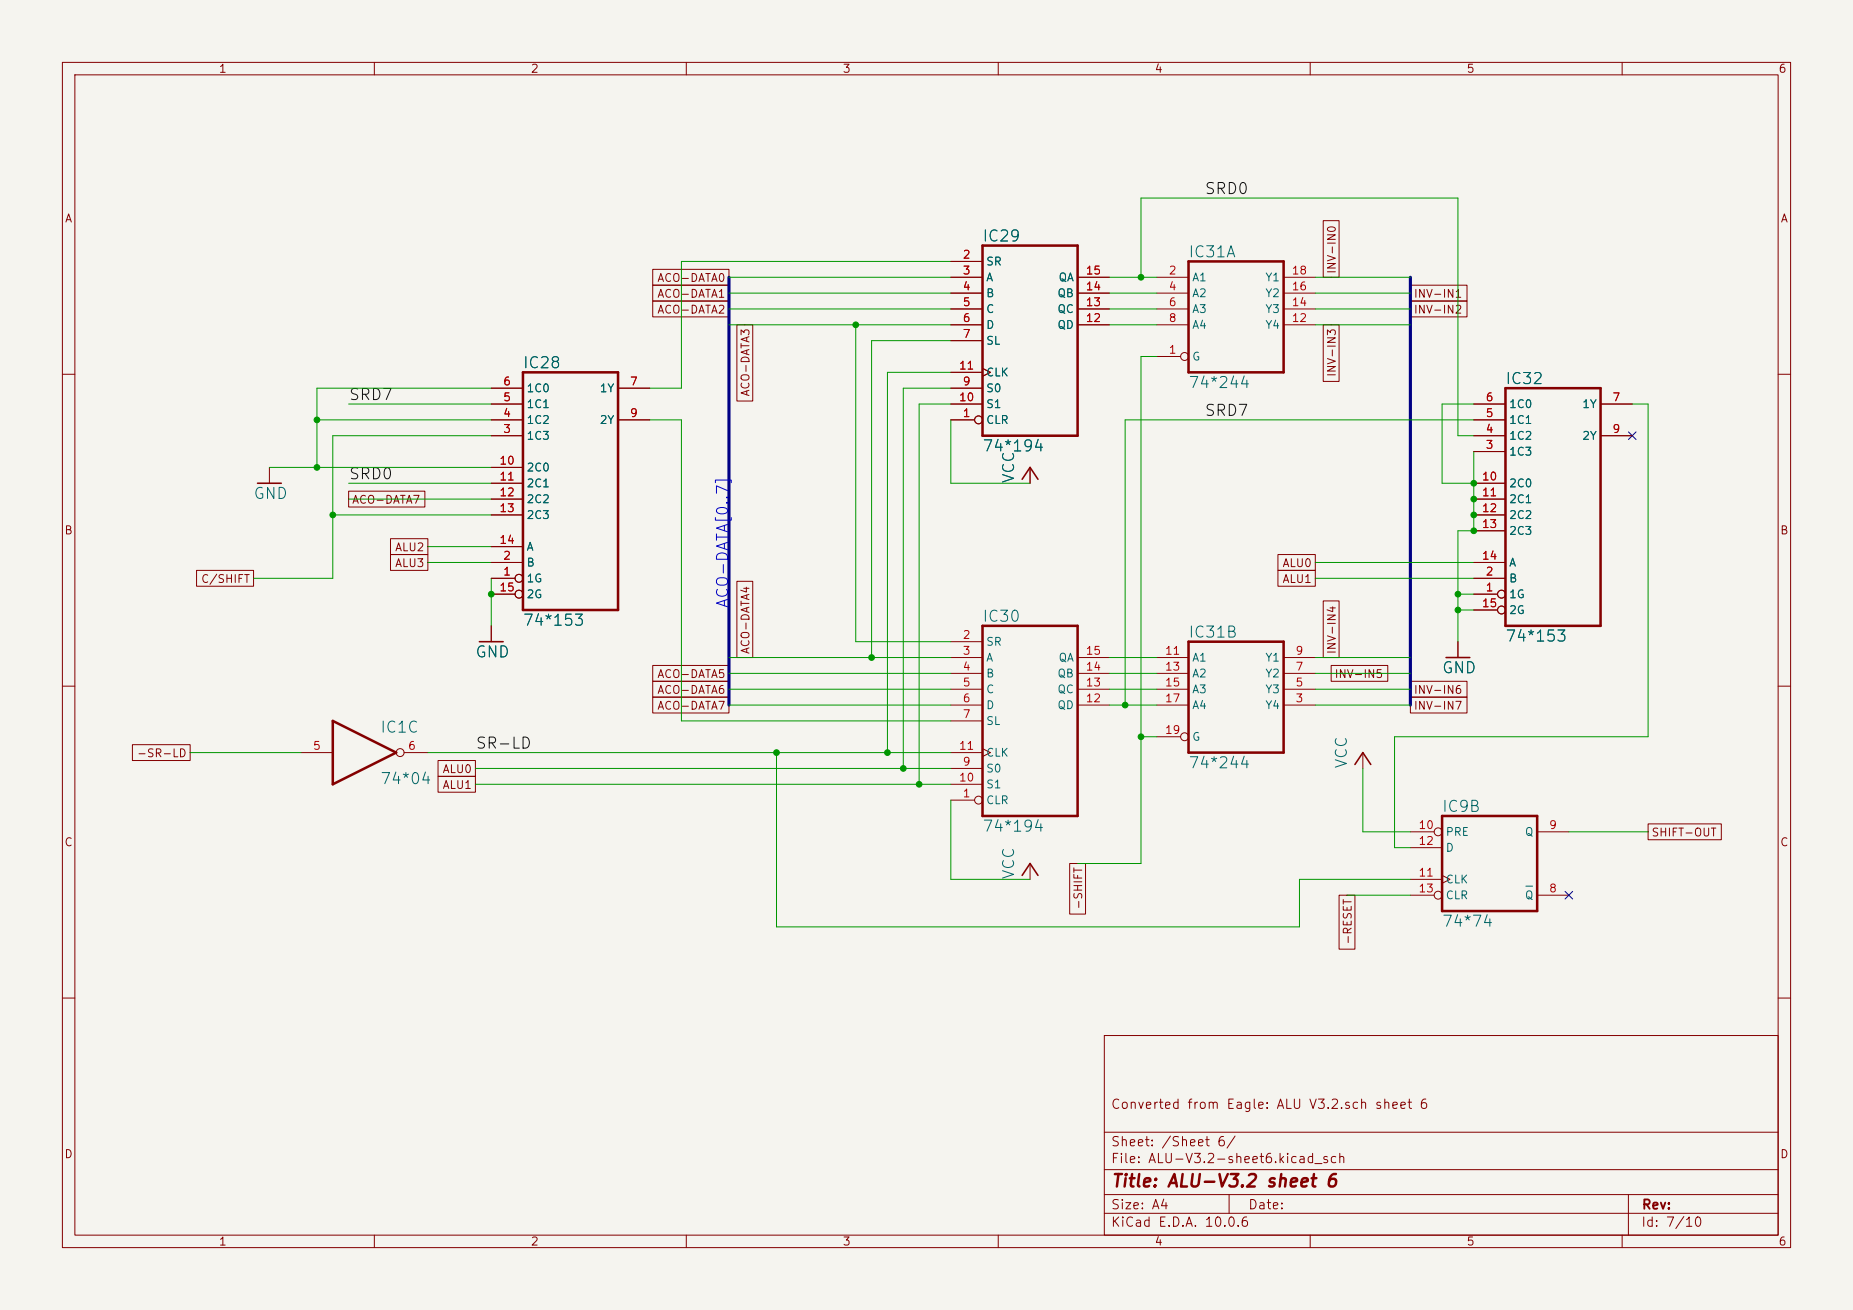
[picture p97: page 7]

Converted from Eagle: ALU V3.2.sch sheet 6

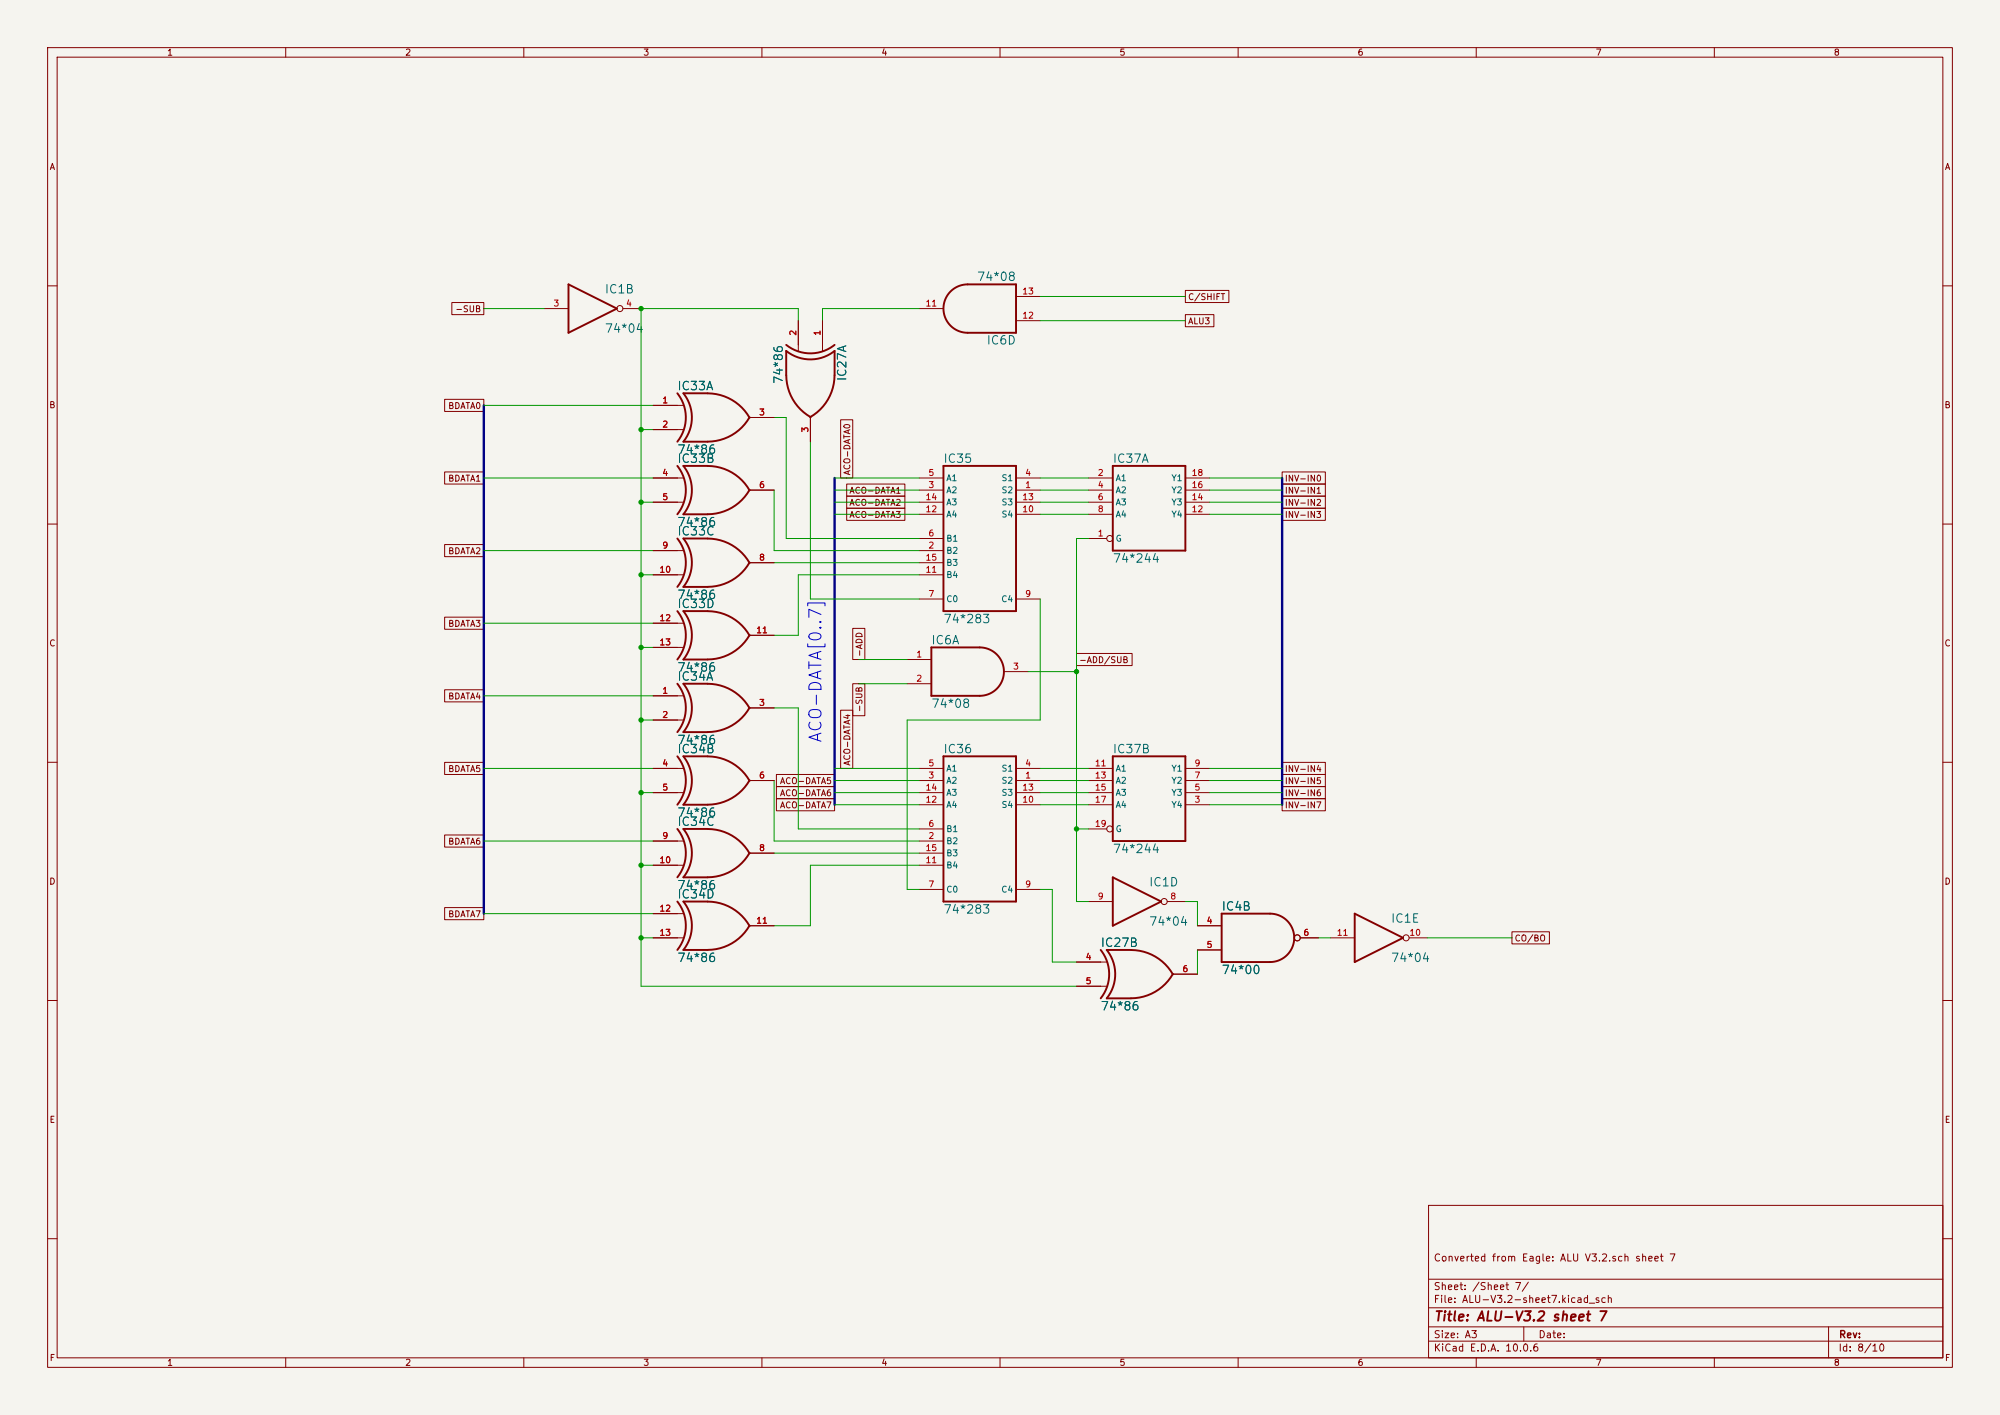
[picture p98: page 8]

Converted from Eagle: ALU V3.2.sch sheet 7

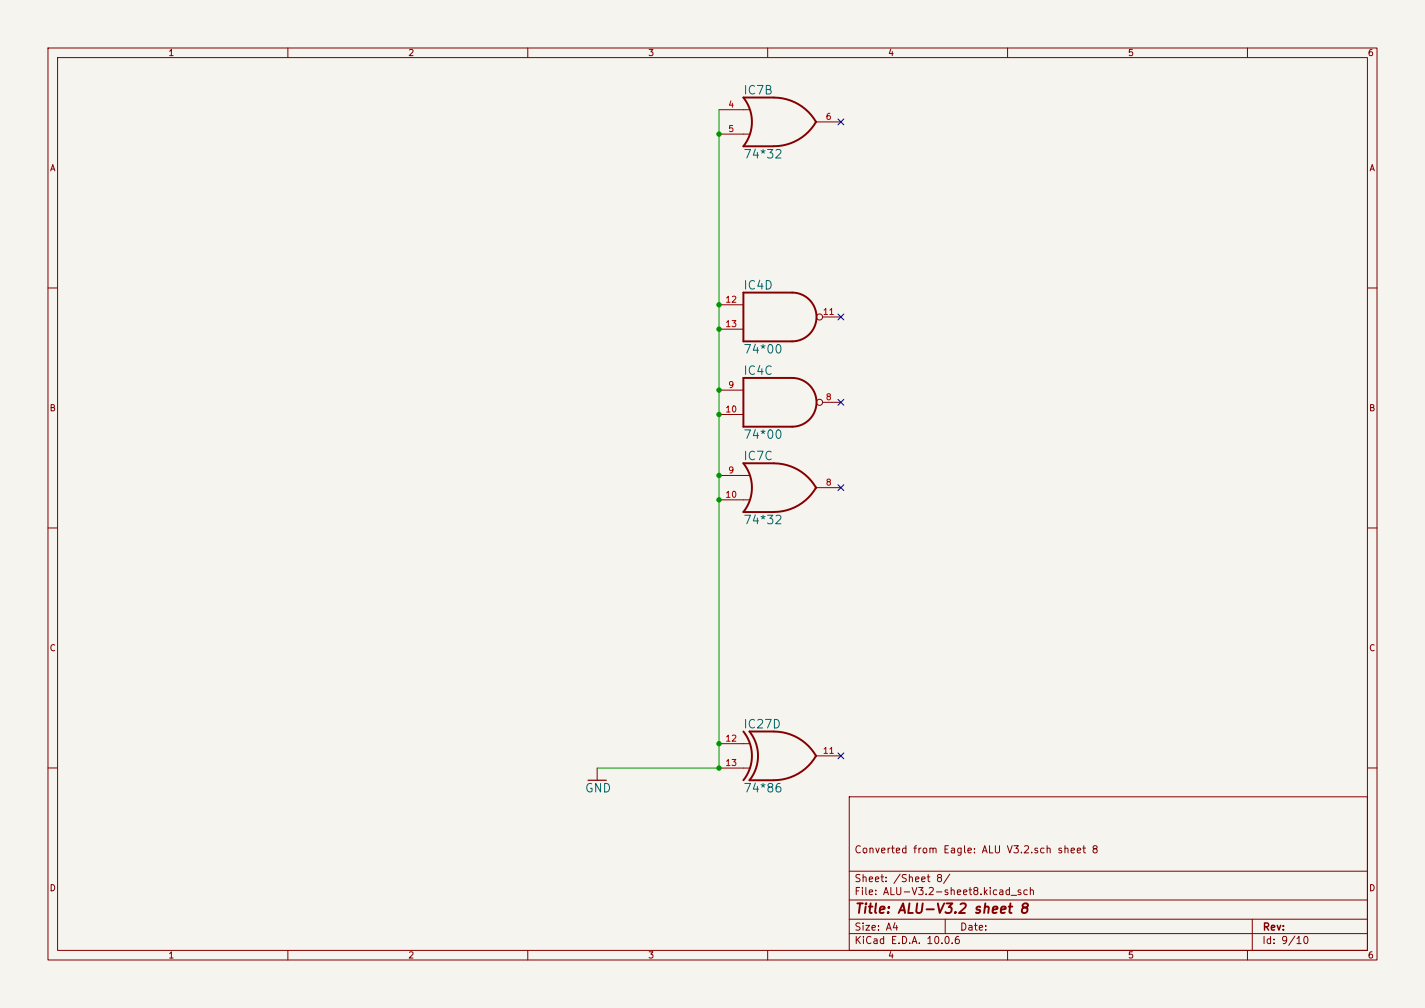
[picture p99: page 9]

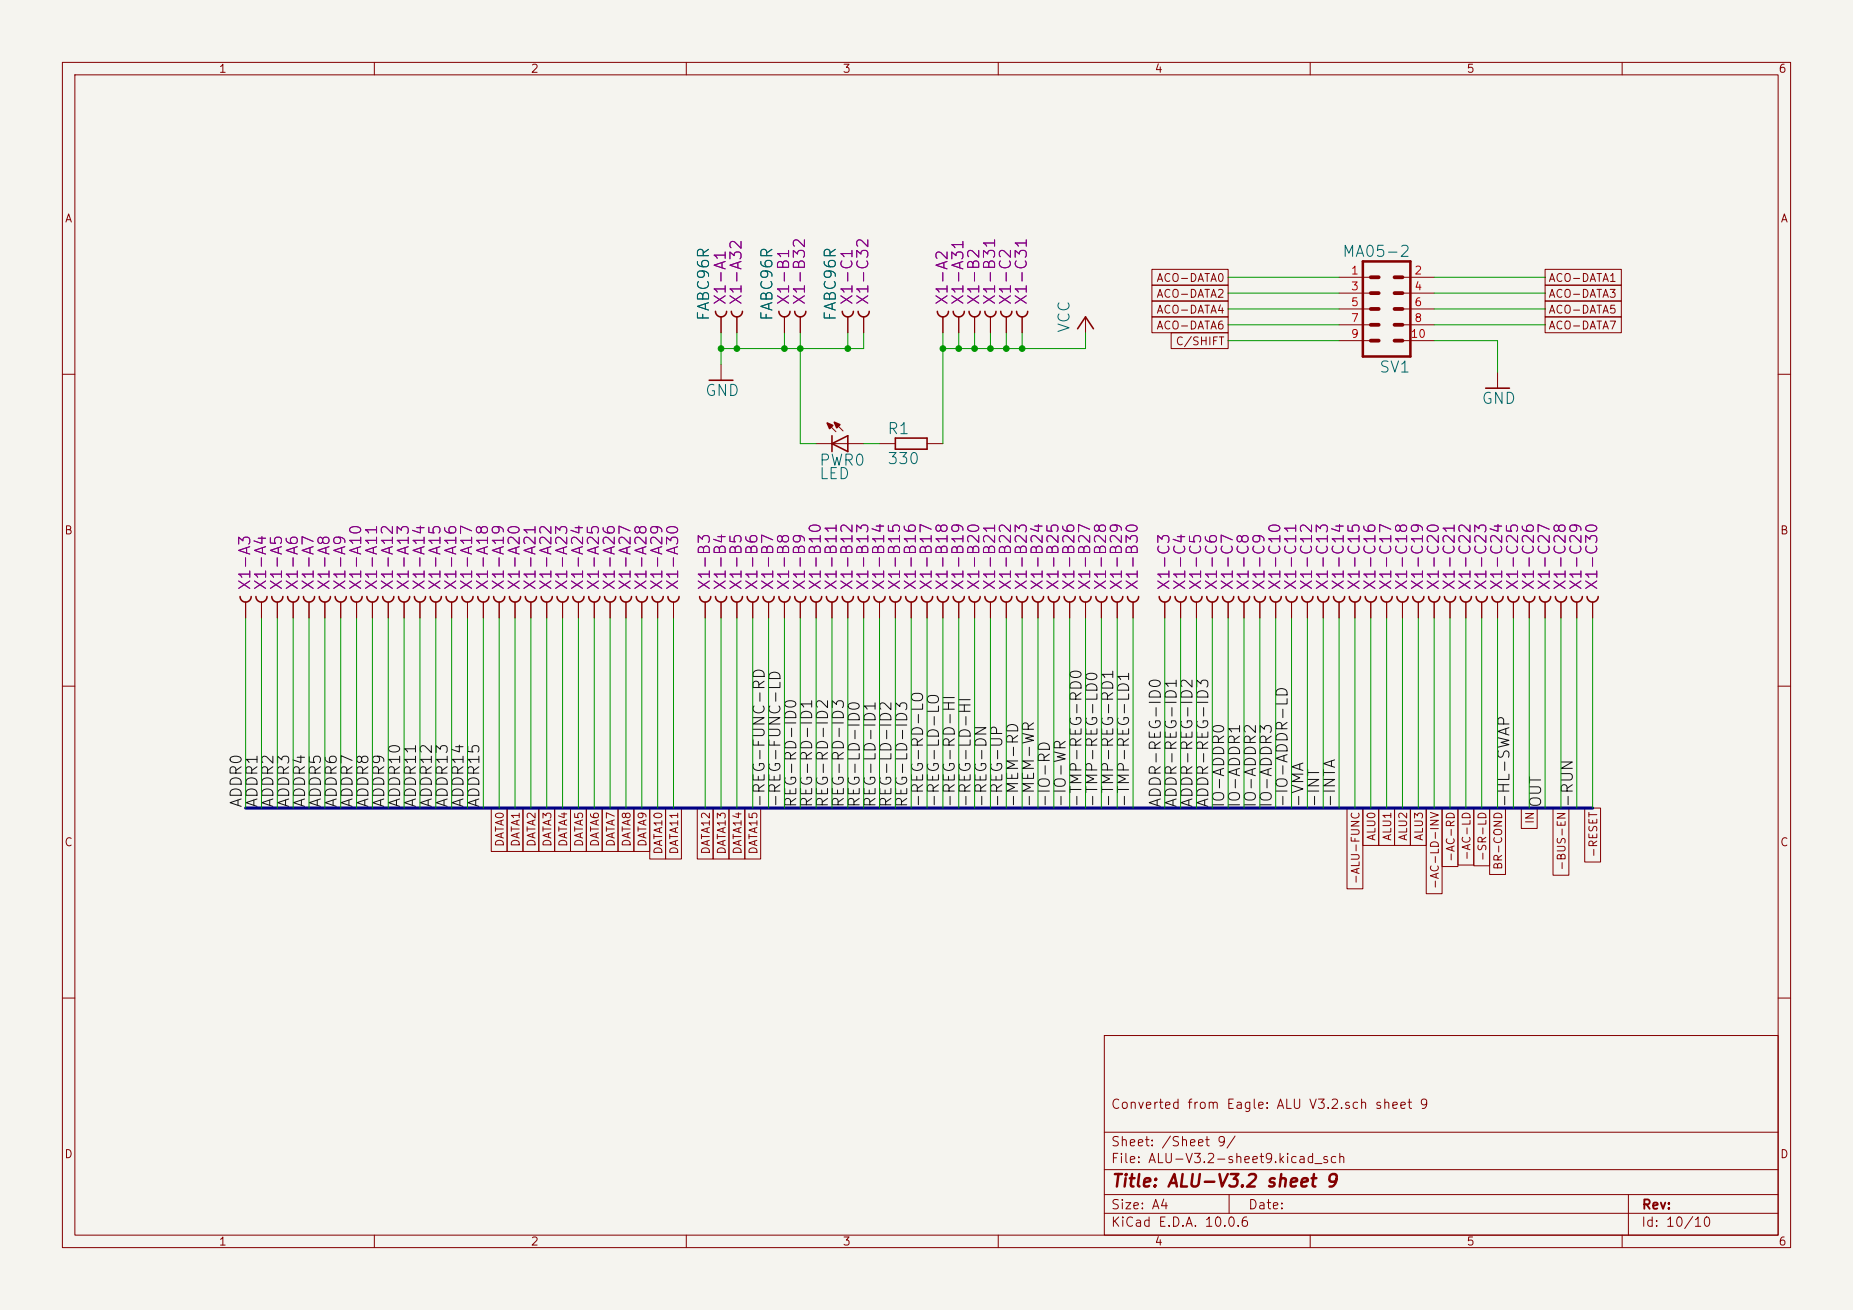
[picture p100: page 10]
