ksr/YACC1-D/hardware/cards/bus-tester/eagle/v3.1/pdf/tester-schematic.pdf

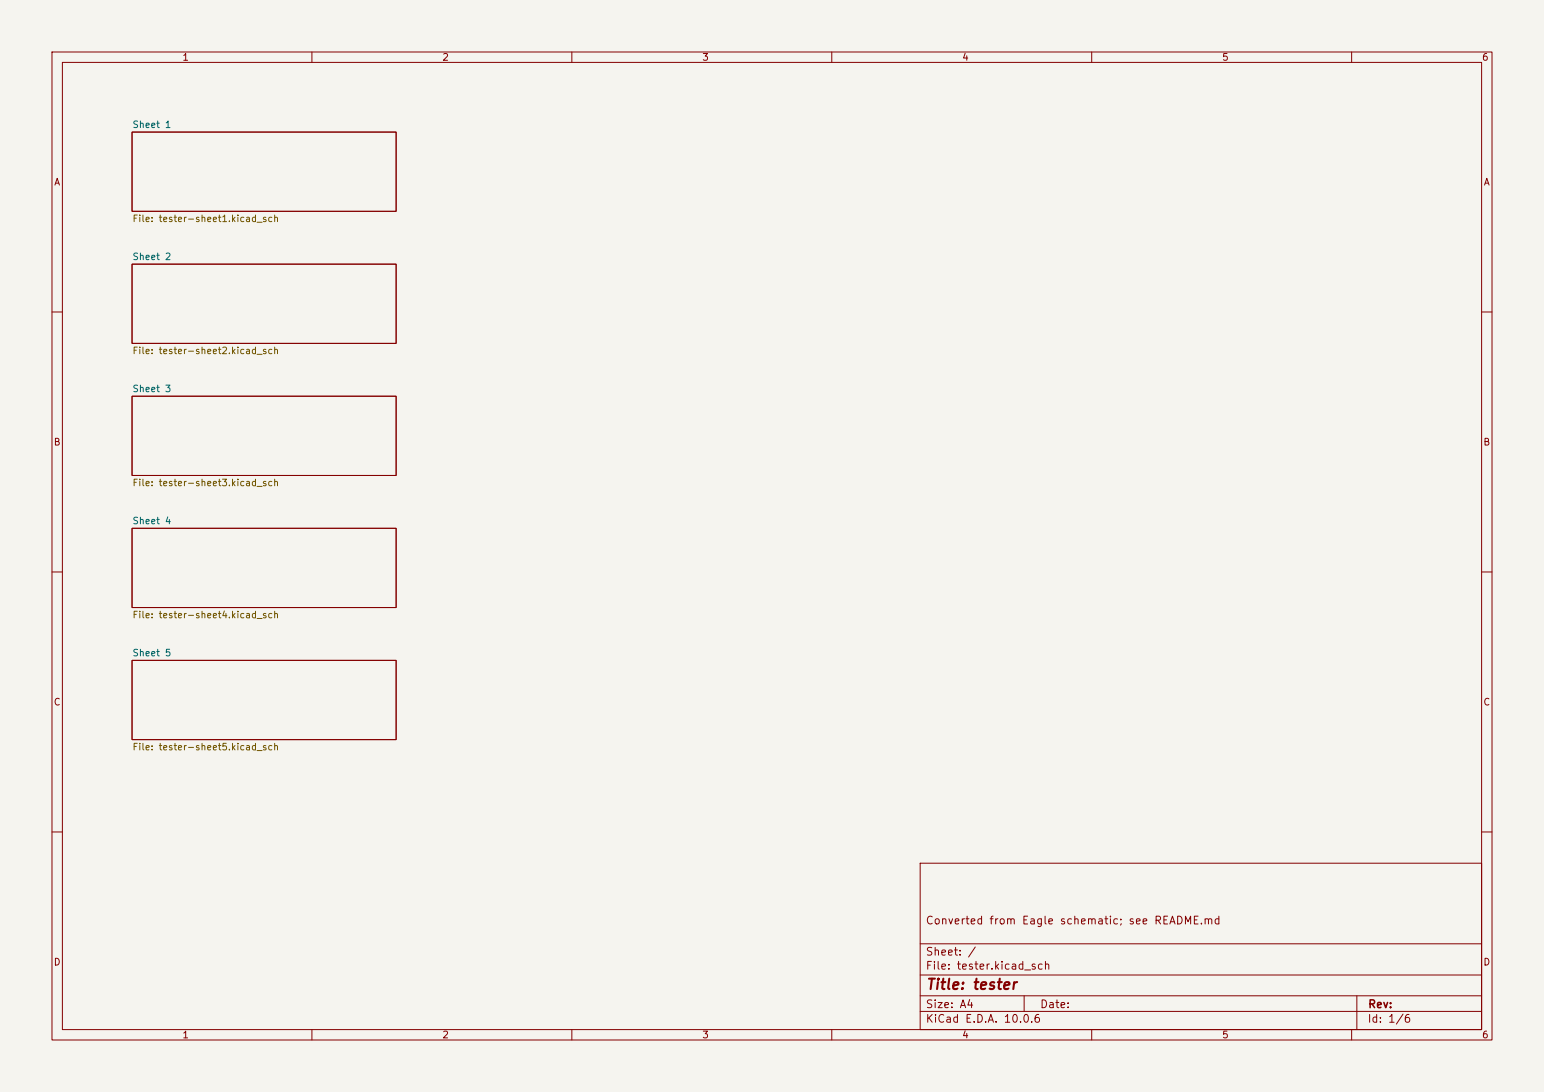
[picture p111: page 1]

Converted from Eagle schematic; see README.md

Size: A4 | Rev:
KiCad E.D.A. 10.0.6 | Id: 1/6

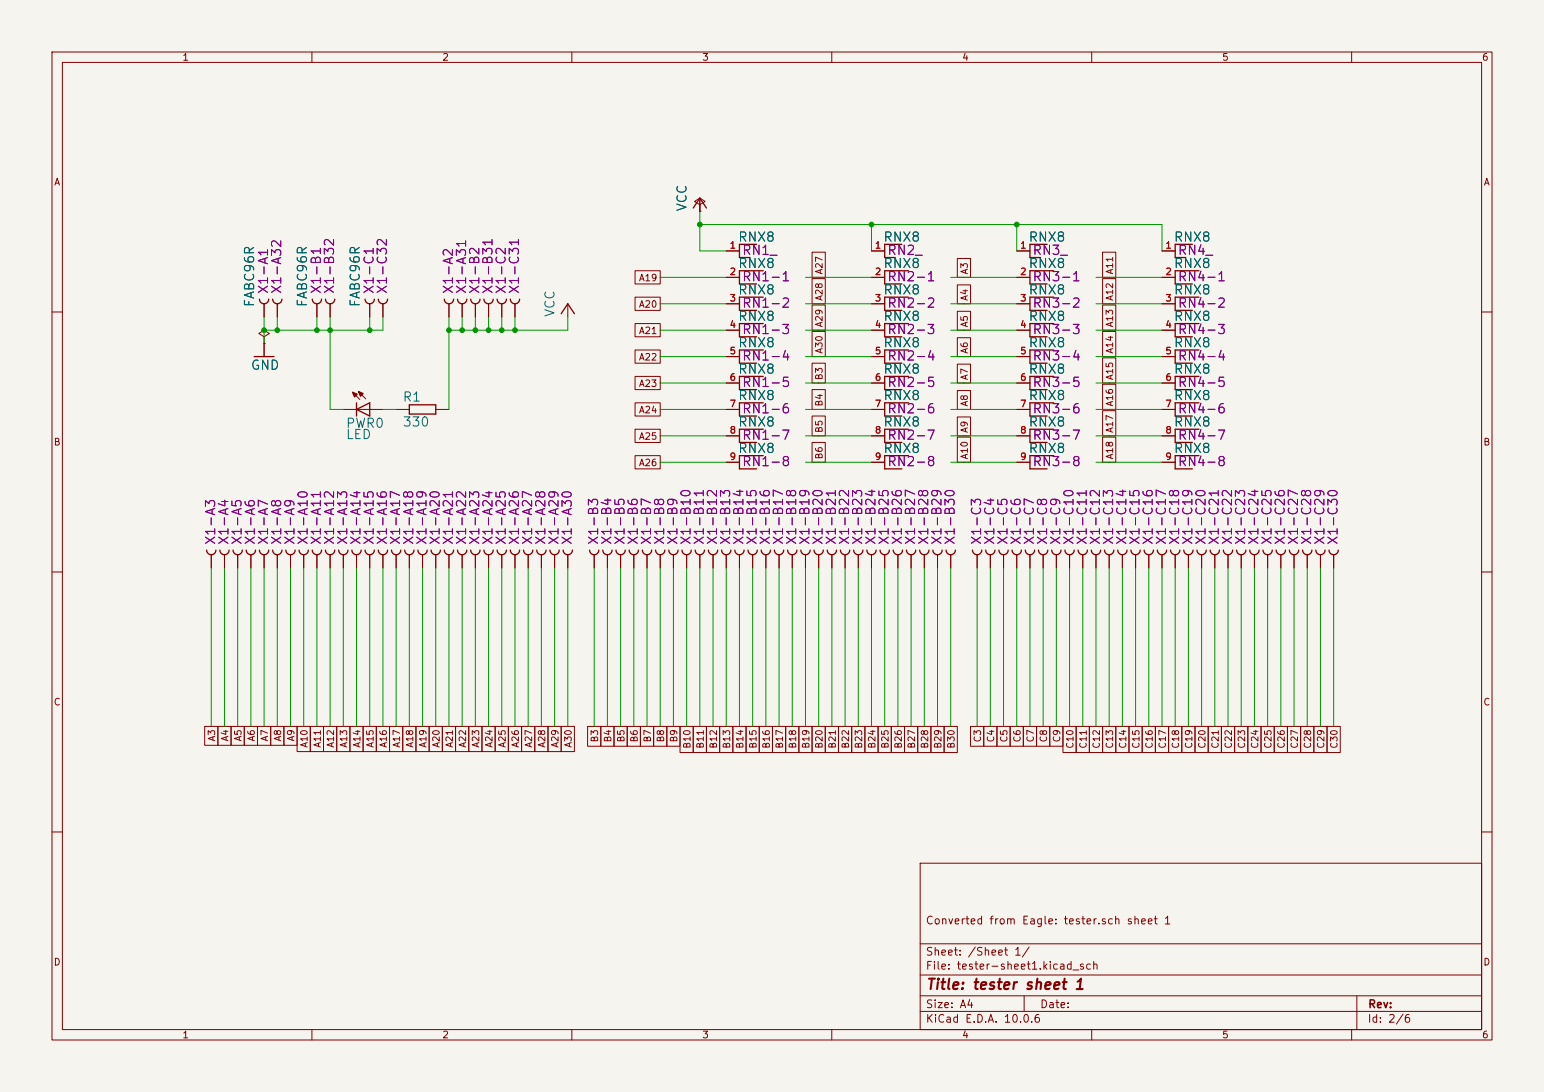
[picture p112: page 2]

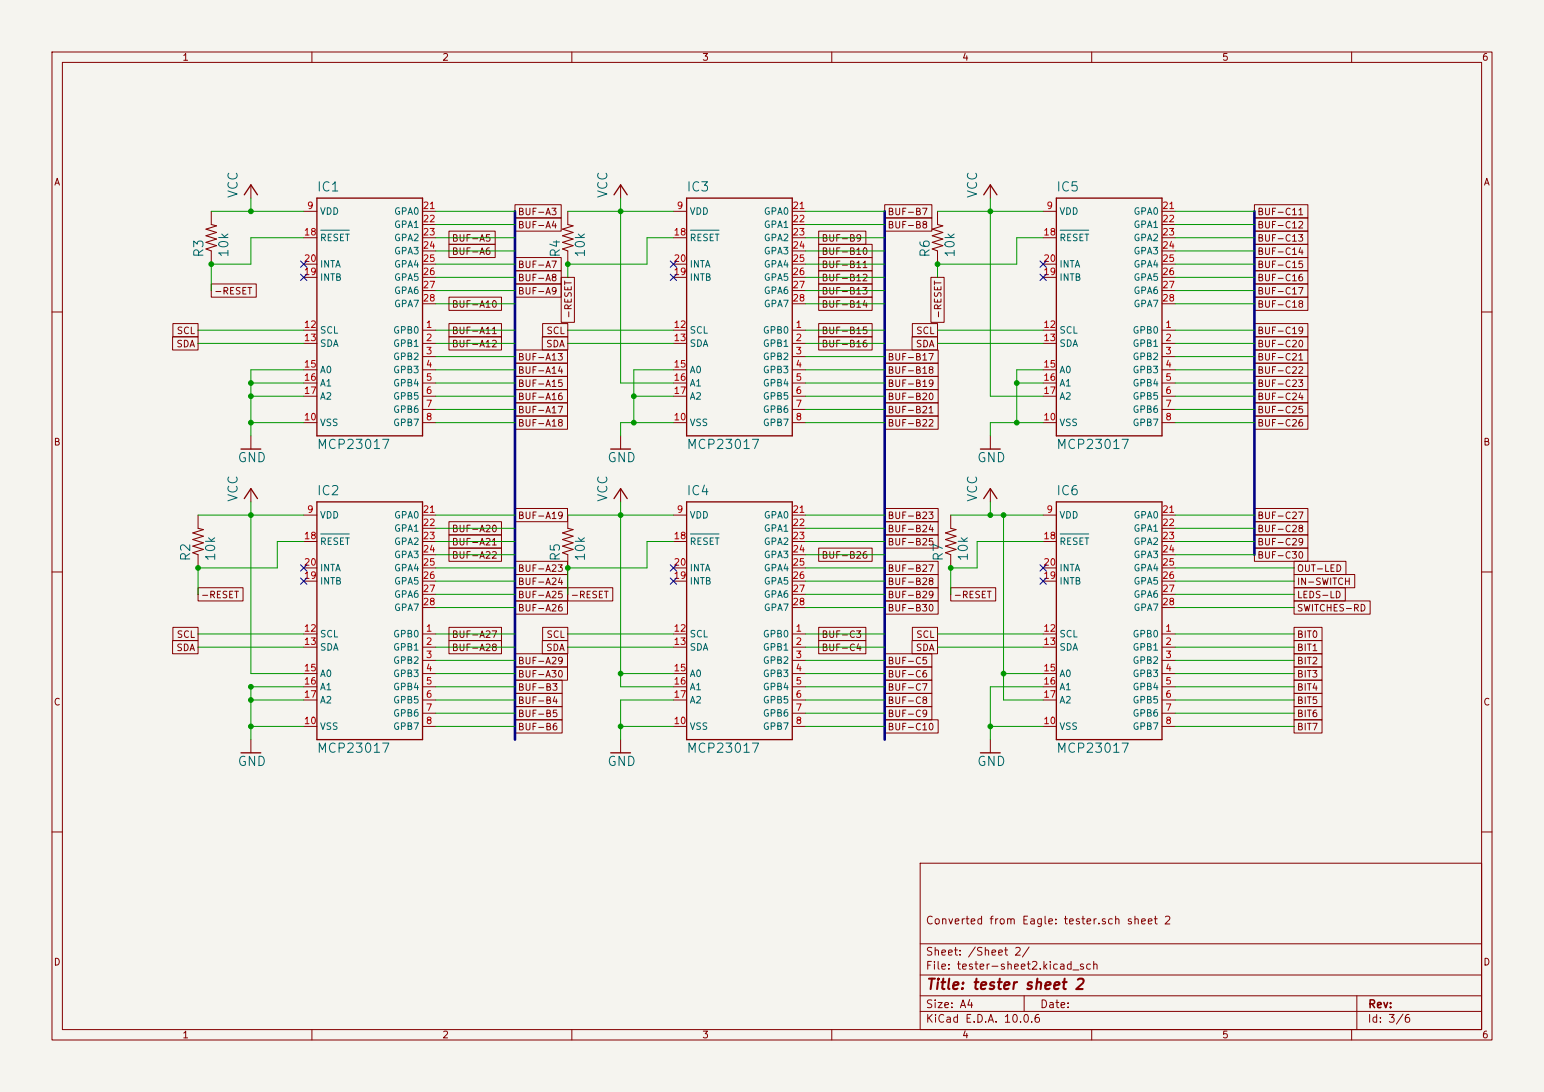
[picture p113: page 3]

BIT0 BUF-C15BIT1 BIT2 BIT3 BUF-C16BIT4 BIT5 BIT6 BUF-C17BIT7 BUF-C18 BUF-C19 BUF-C20 BUF-B22

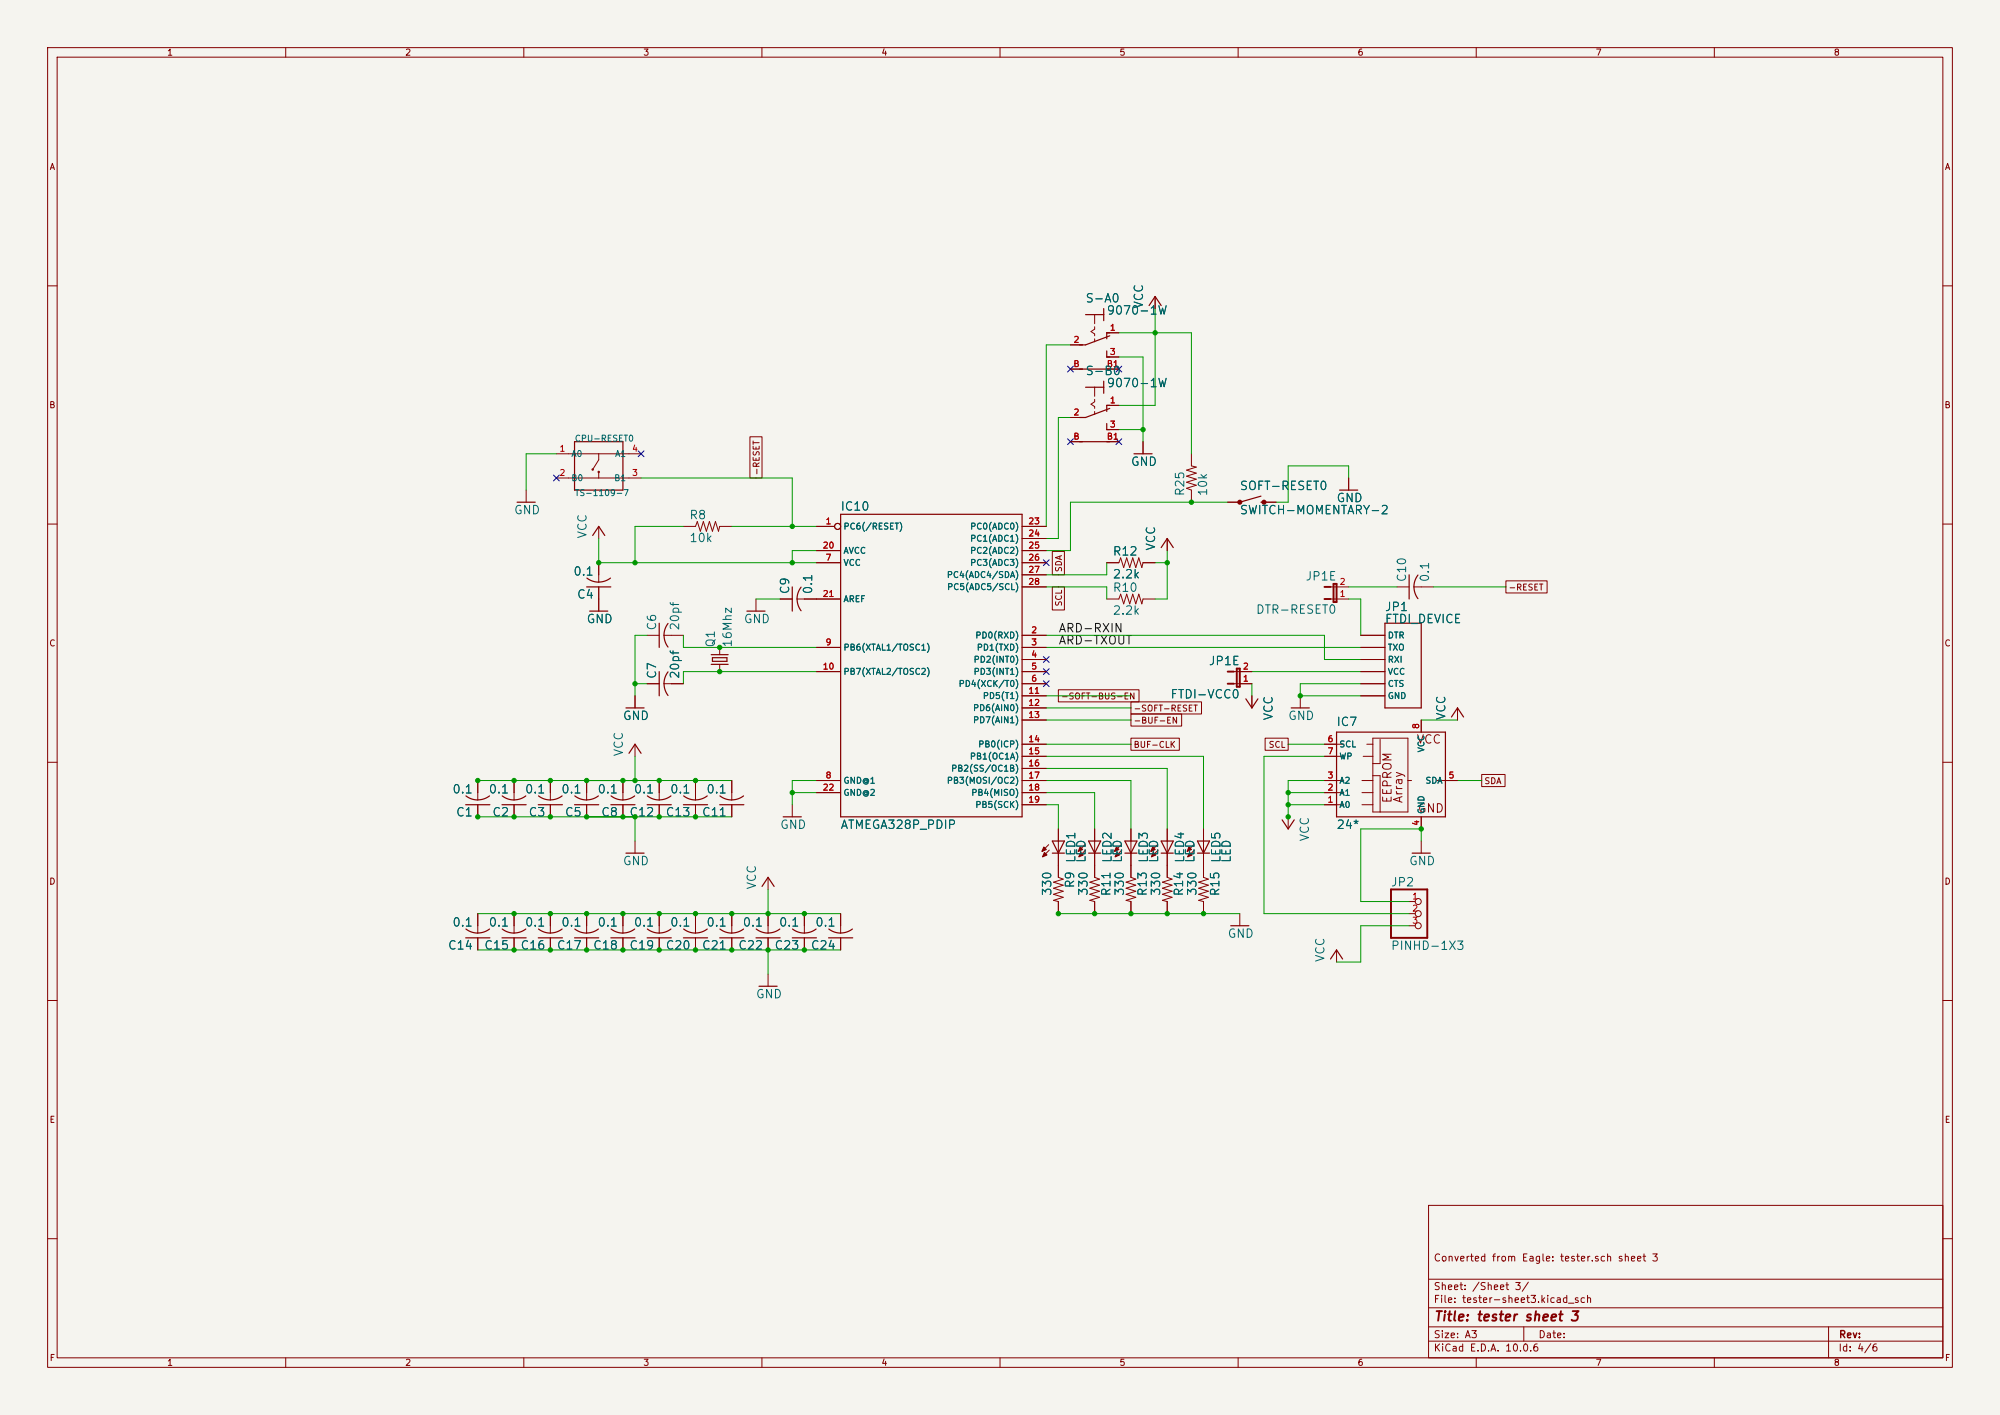
[picture p114: page 4]

Converted from Eagle: tester.sch sheet 3

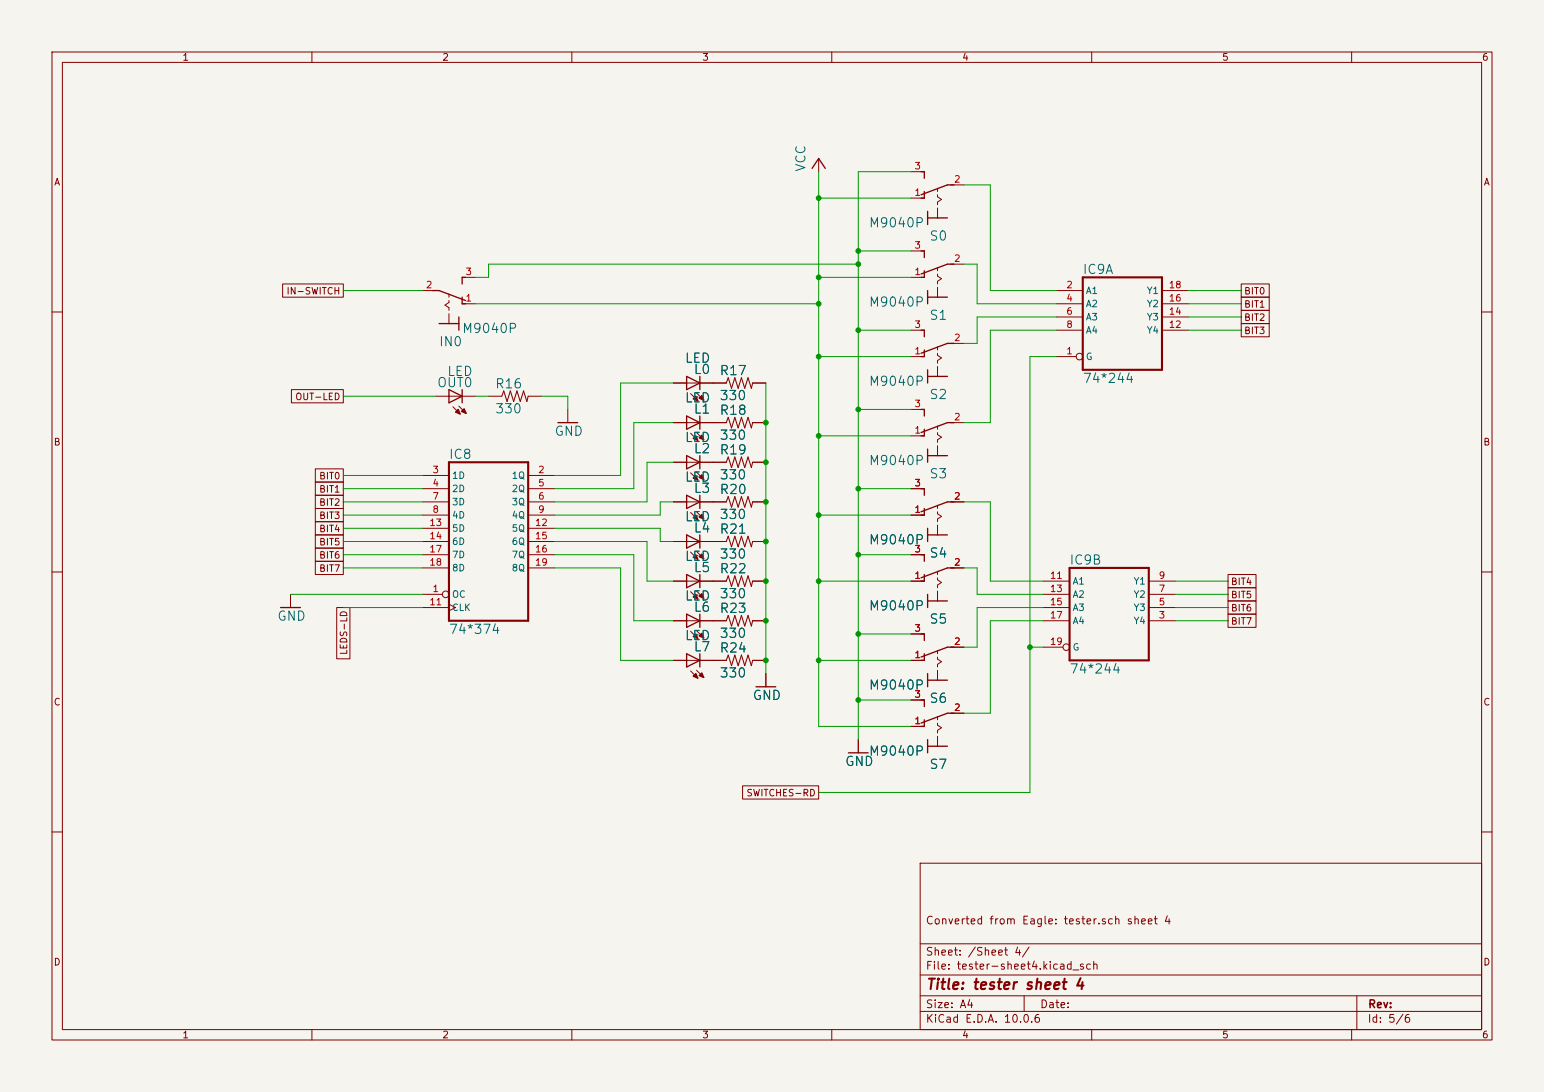
[picture p115: page 5]

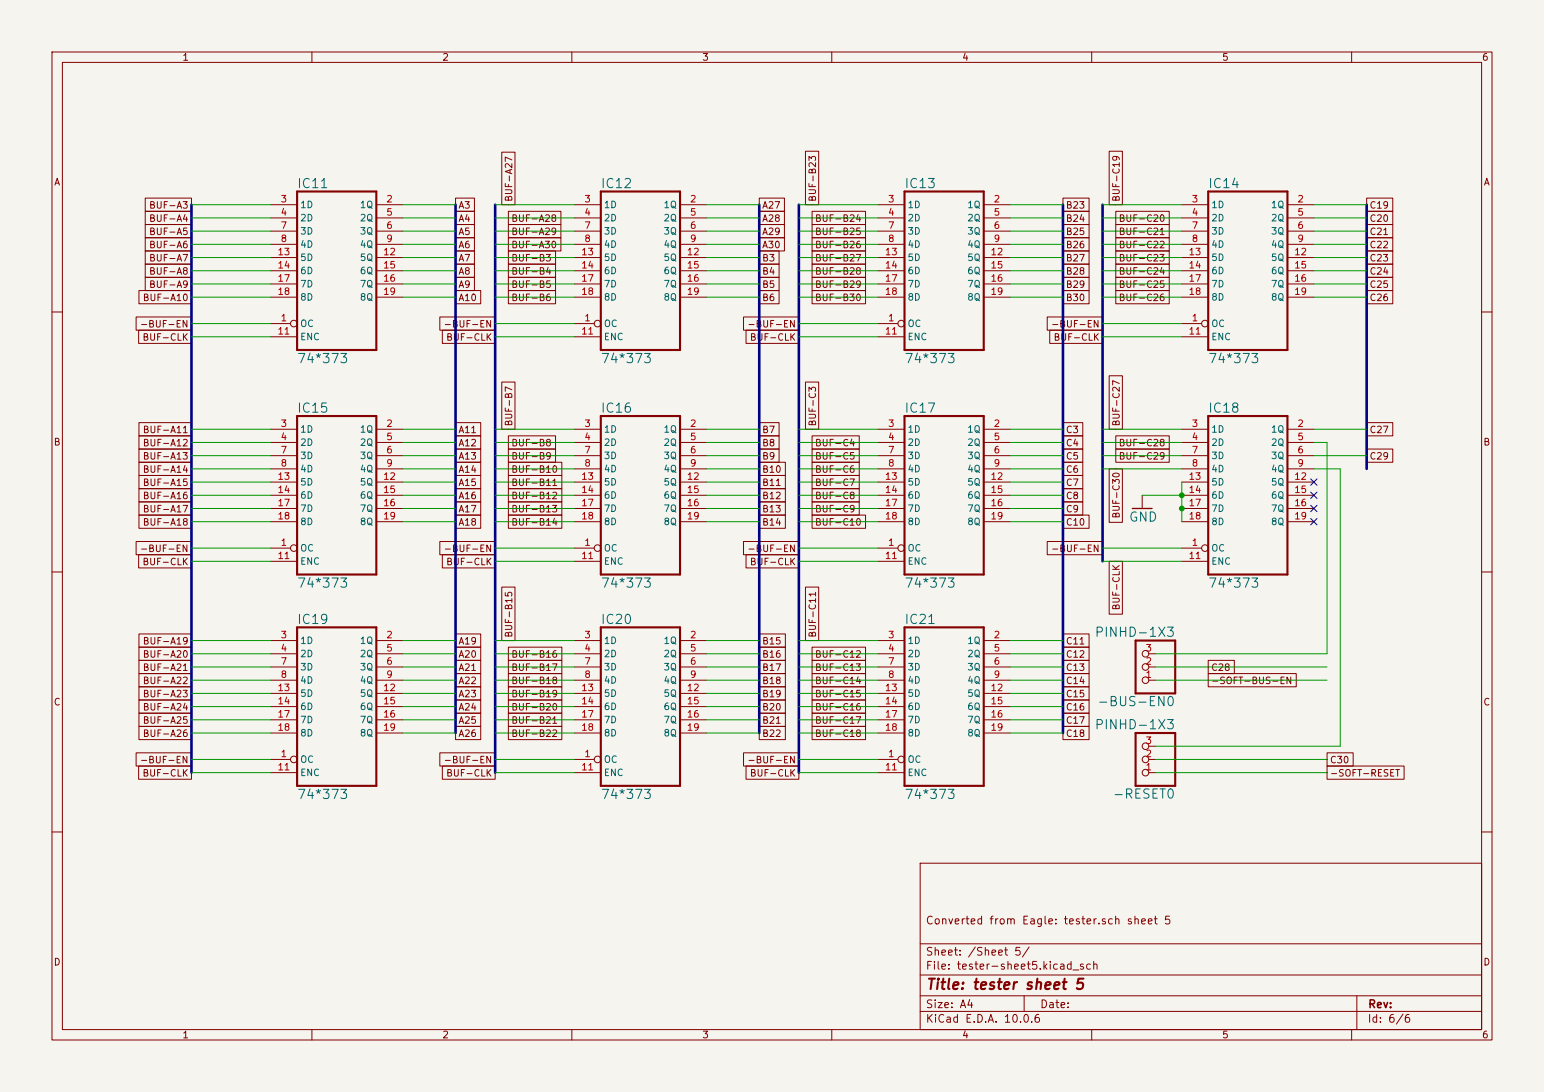
[picture p116: page 6]

BUF-C26 BUF-C25 BUF-C24 BUF-C23

BUF-C10 BUF-C9 BUF-C8 BUF-C7 BUF-C6 BUF-CLK -BUF-EN

Converted from Eagle: tester.sch sheet 5
