ksr/YACC1-D/hardware/cards/bus-tester/kicad/v3.1/reports/bus-tester-v3.1-schematic.pdf

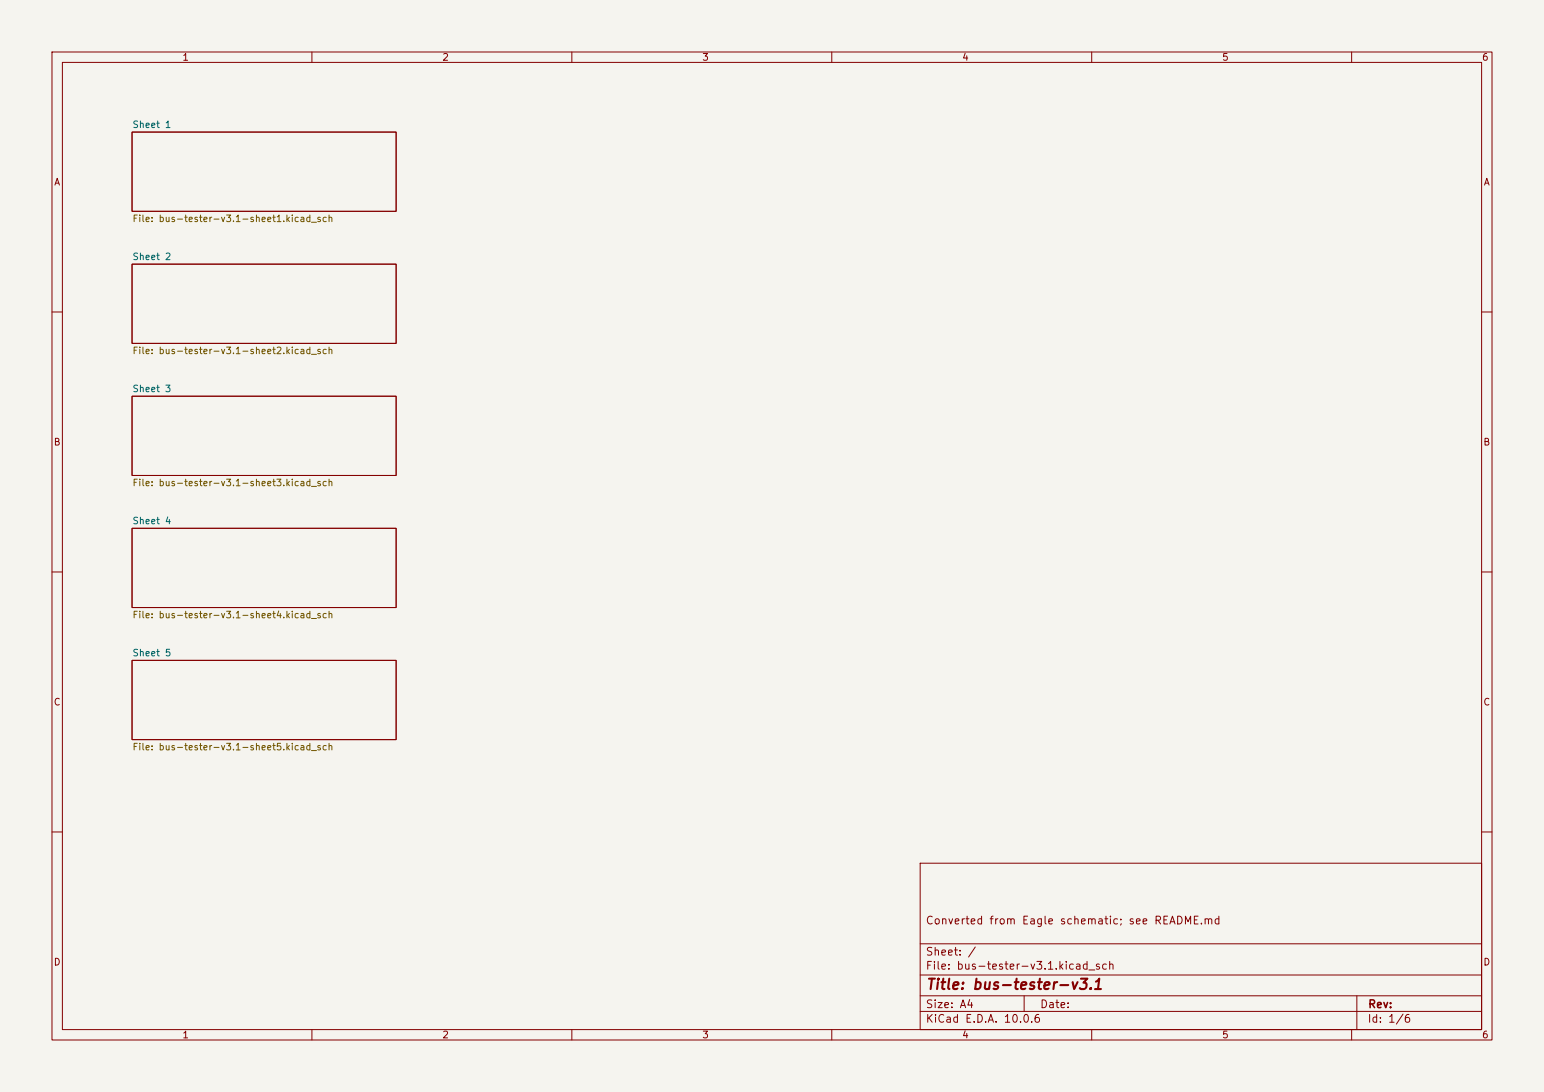
[picture p117: page 1]

File: bus-tester-v3.1-sheet1.kicad_sch Sheet 2

File: bus-tester-v3.1-sheet2.kicad_sch Sheet 3

File: bus-tester-v3.1-sheet3.kicad_sch Sheet 4

File: bus-tester-v3.1-sheet4.kicad_sch Sheet 5

Converted from Eagle schematic; see README.md

Size: A4 | Rev:
KiCad E.D.A. 10.0.6 | Id: 1/6

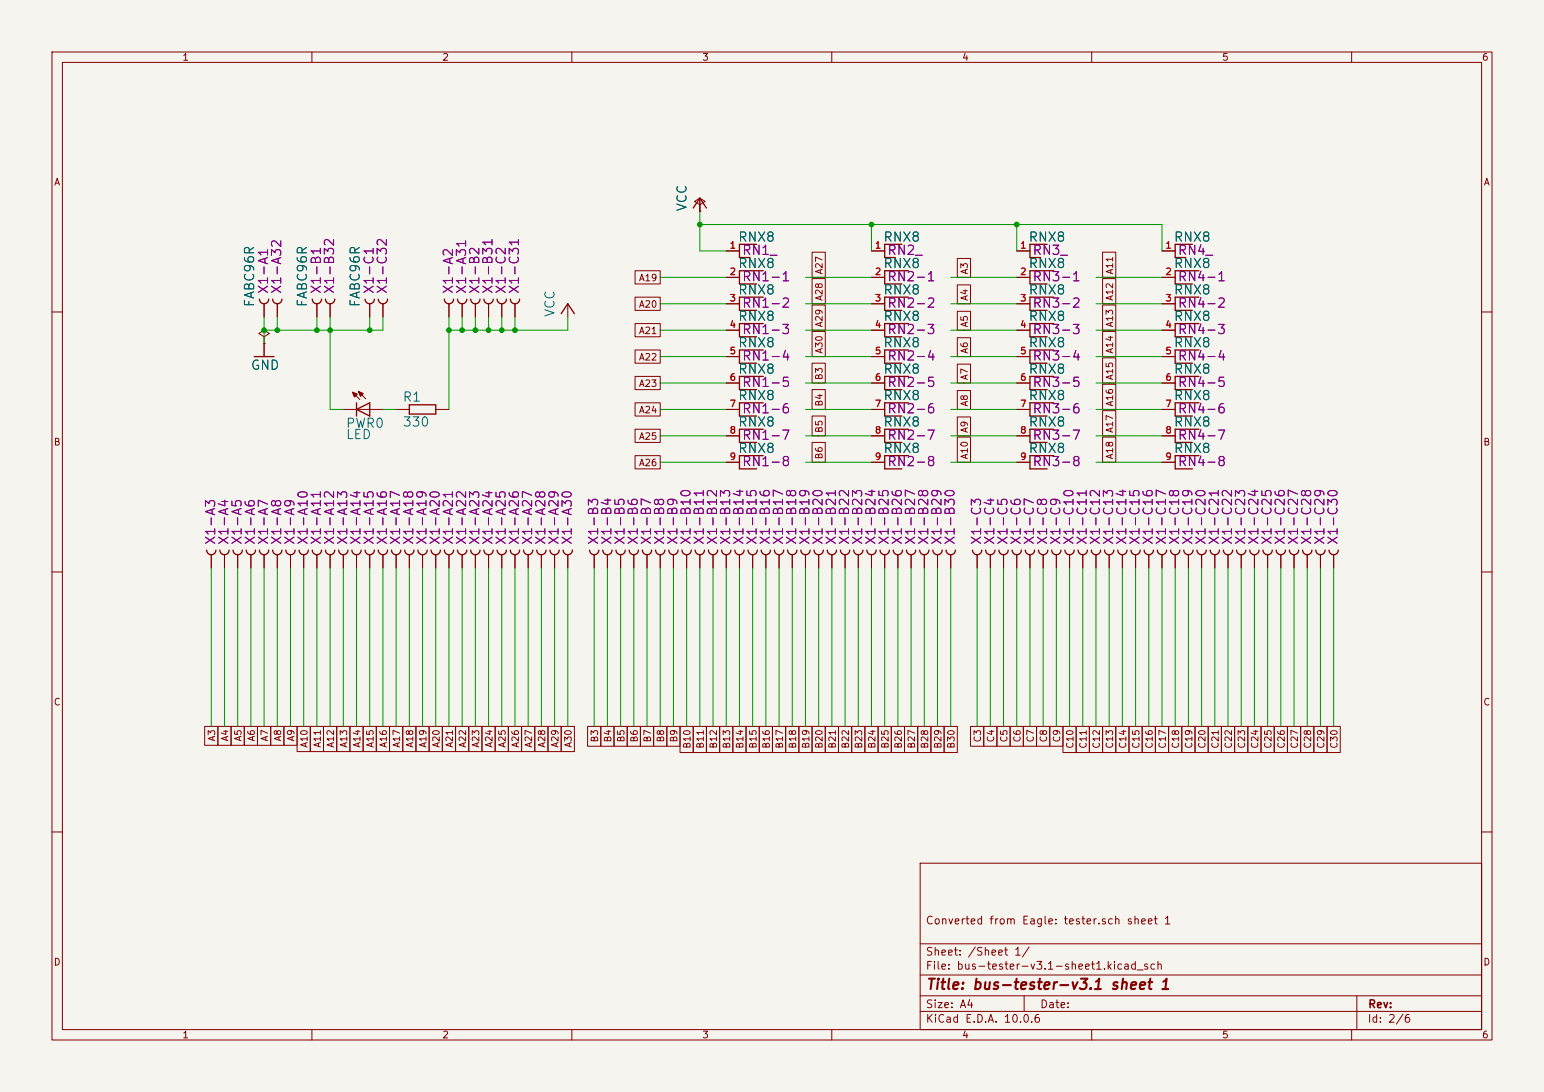
[picture p118: page 2]

Sheet: /Sheet 1/
File: bus-tester-v3.1-sheet1.kicad_sch
Title: bus-tester-v3.1 sheet 1

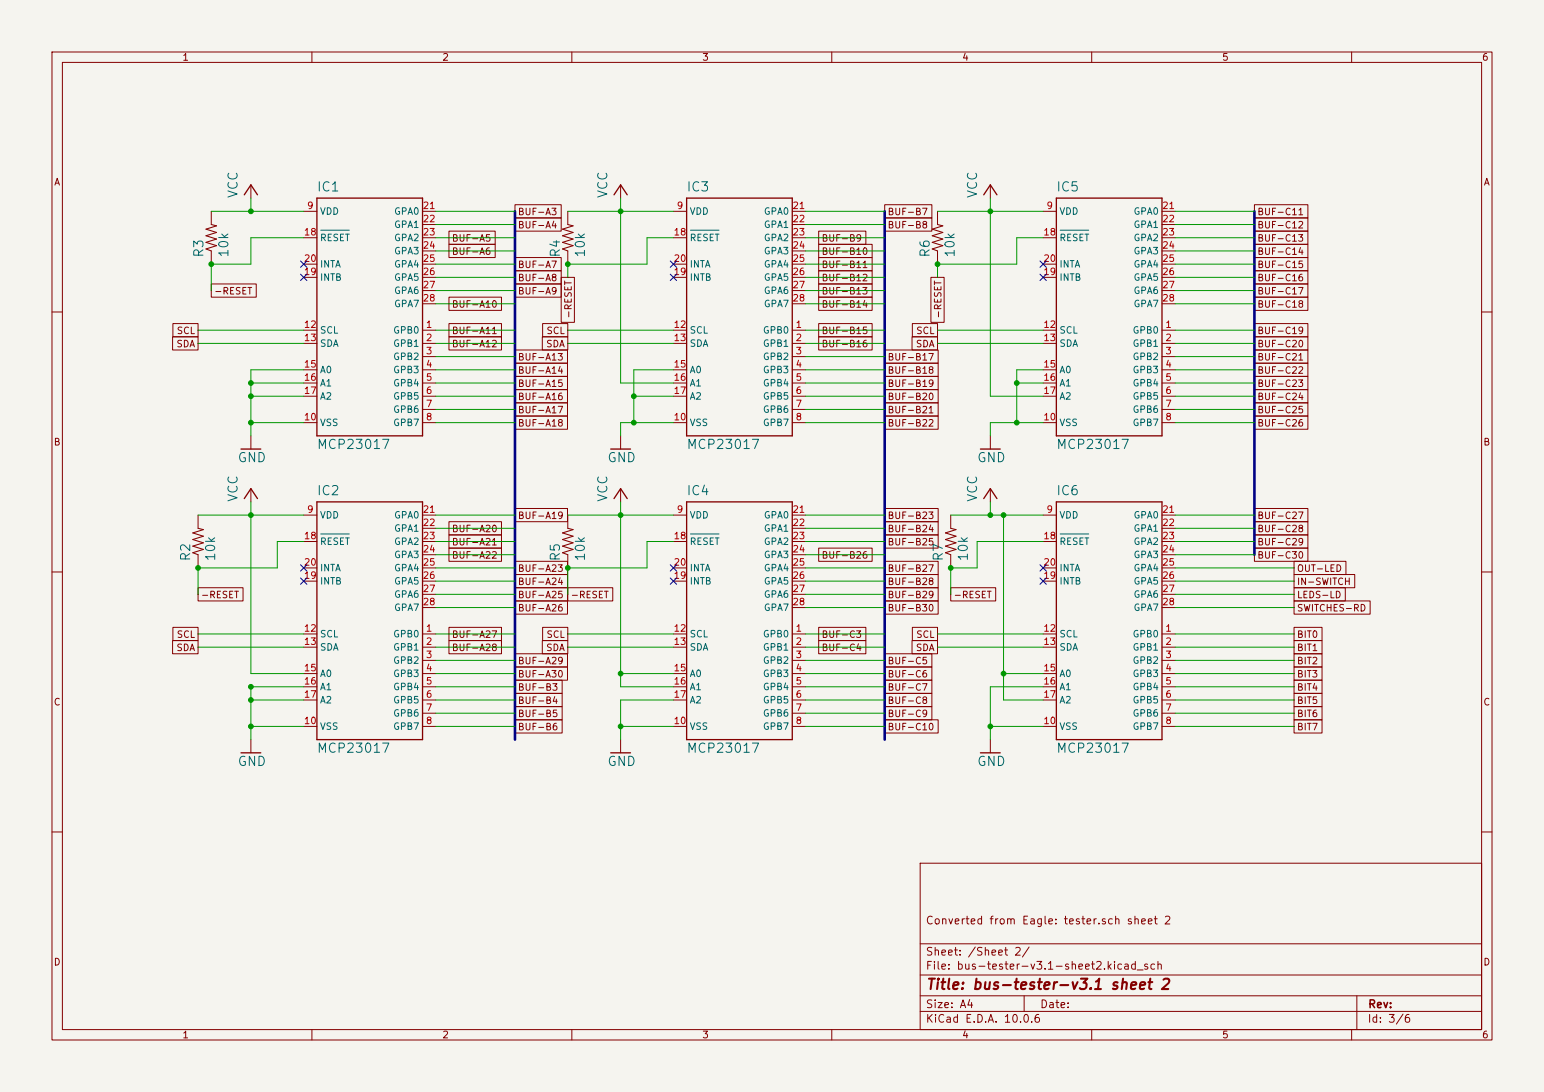
[picture p119: page 3]

BIT0 BUF-C15BIT1 BIT2 BIT3 BUF-C16BIT4 BIT5 BIT6 BUF-C17BIT7 BUF-C18 BUF-C19 BUF-C20 BUF-B22

Sheet: /Sheet 2/
File: bus-tester-v3.1-sheet2.kicad_sch
Title: bus-tester-v3.1 sheet 2

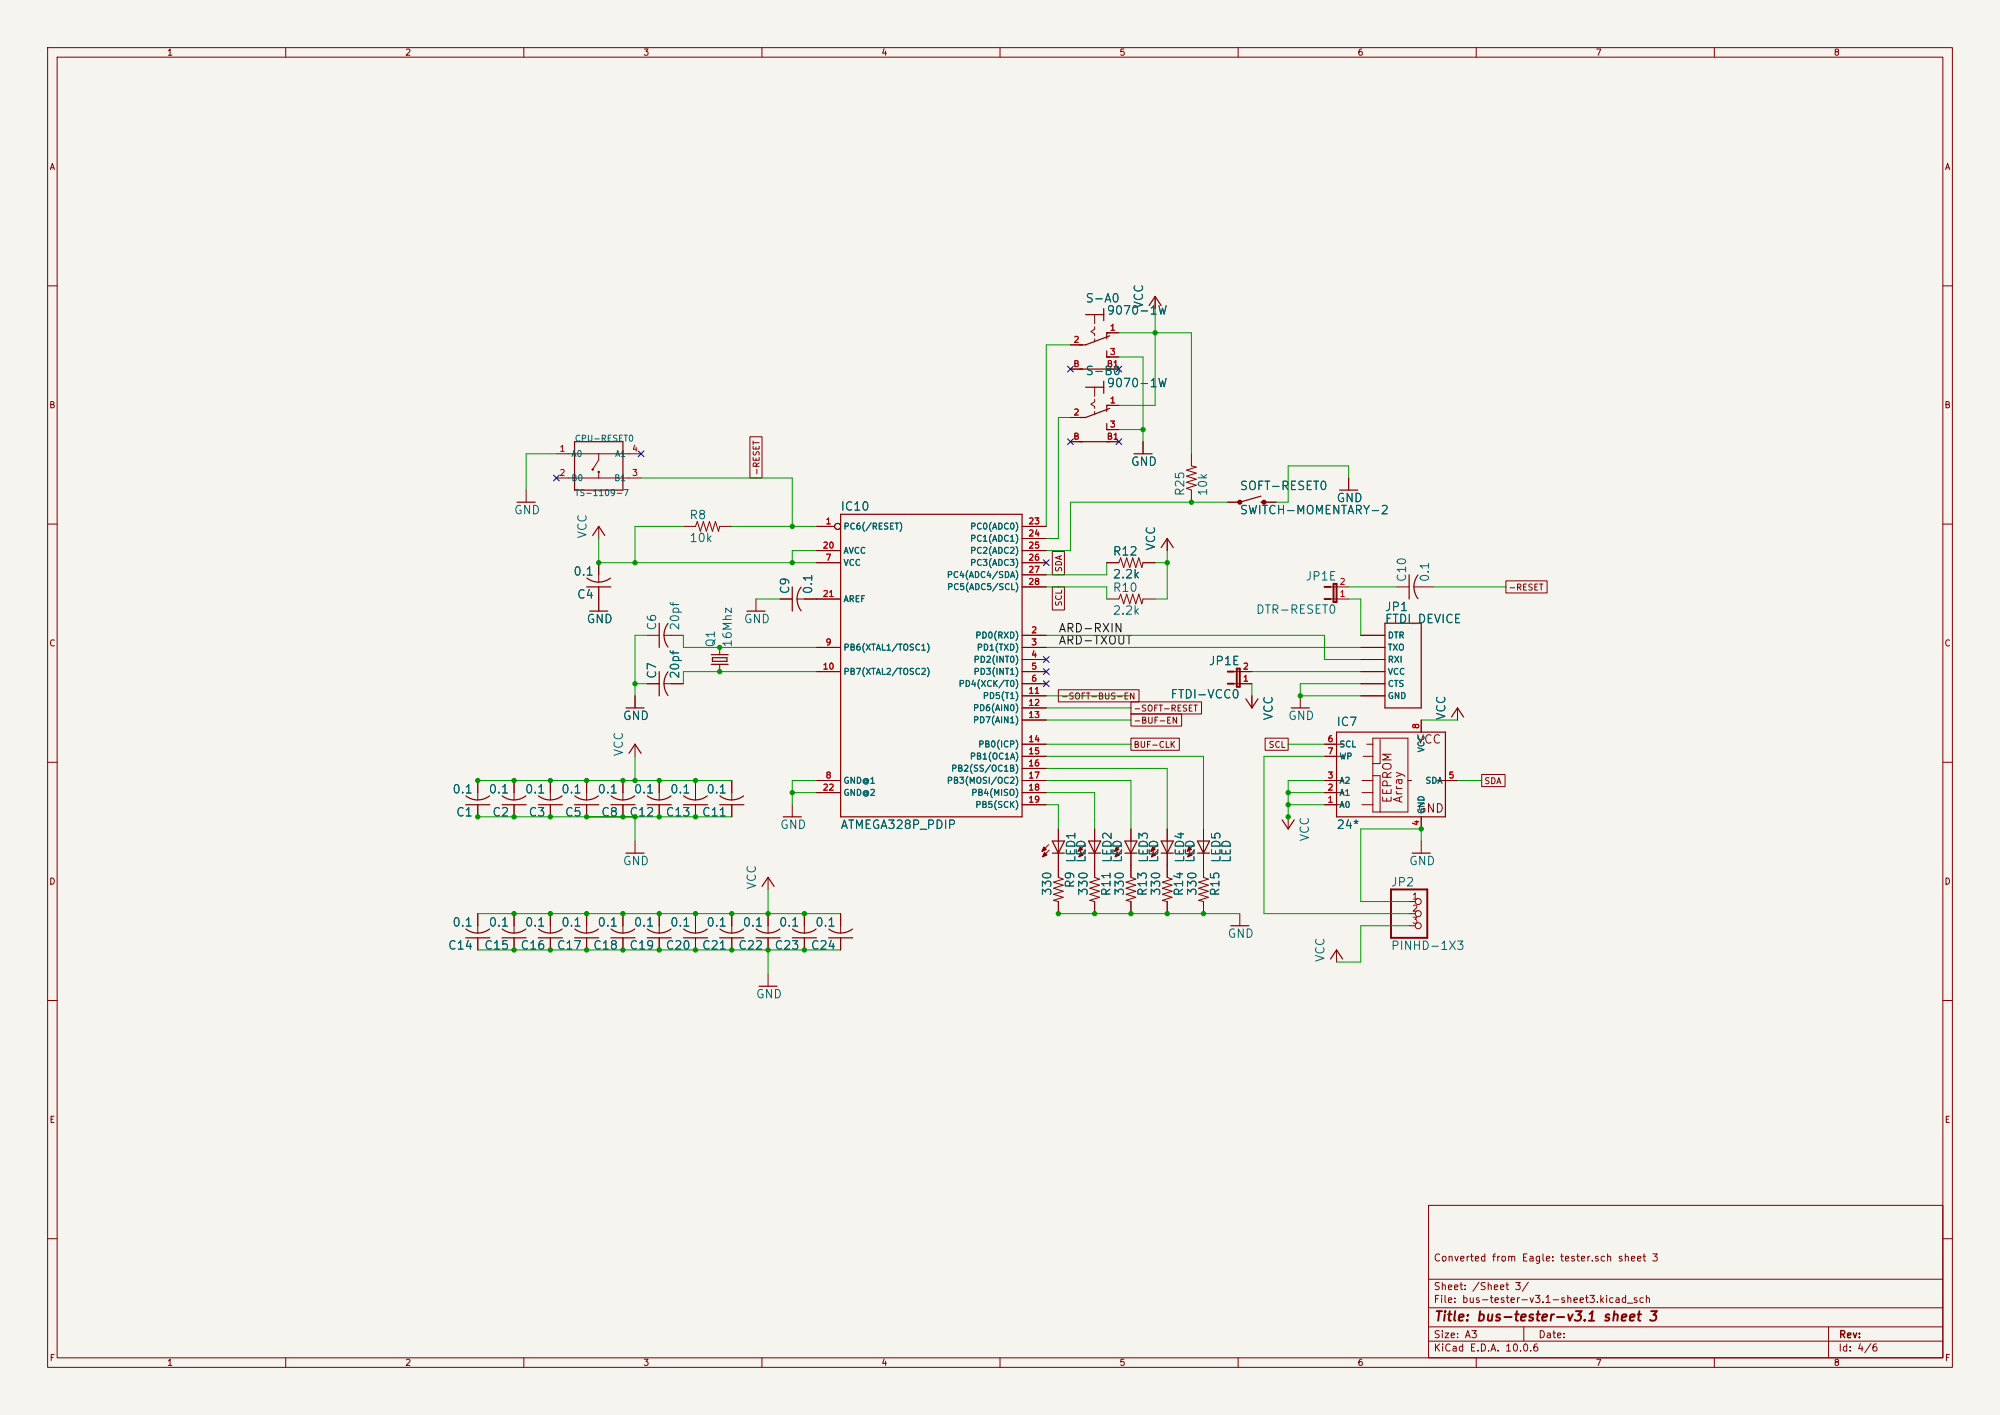
[picture p120: page 4]

Converted from Eagle: tester.sch sheet 3

Sheet: /Sheet 3/
File: bus-tester-v3.1-sheet3.kicad_sch
Title: bus-tester-v3.1 sheet 3

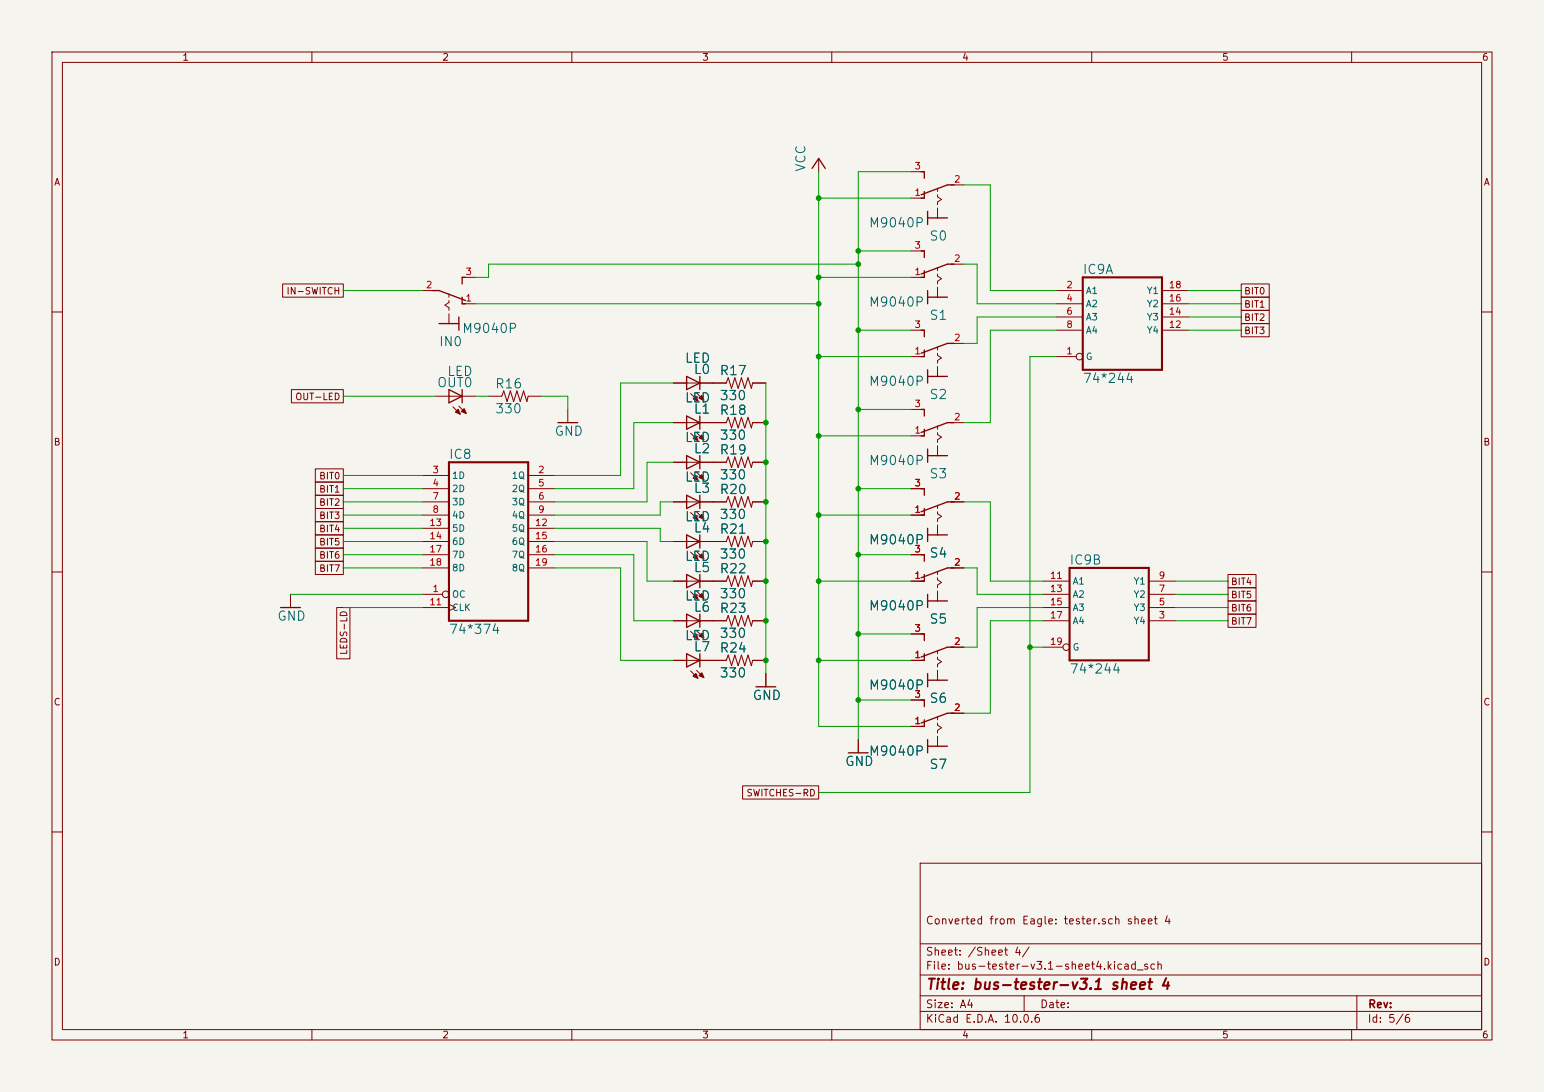
[picture p121: page 5]

Sheet: /Sheet 4/
File: bus-tester-v3.1-sheet4.kicad_sch
Title: bus-tester-v3.1 sheet 4

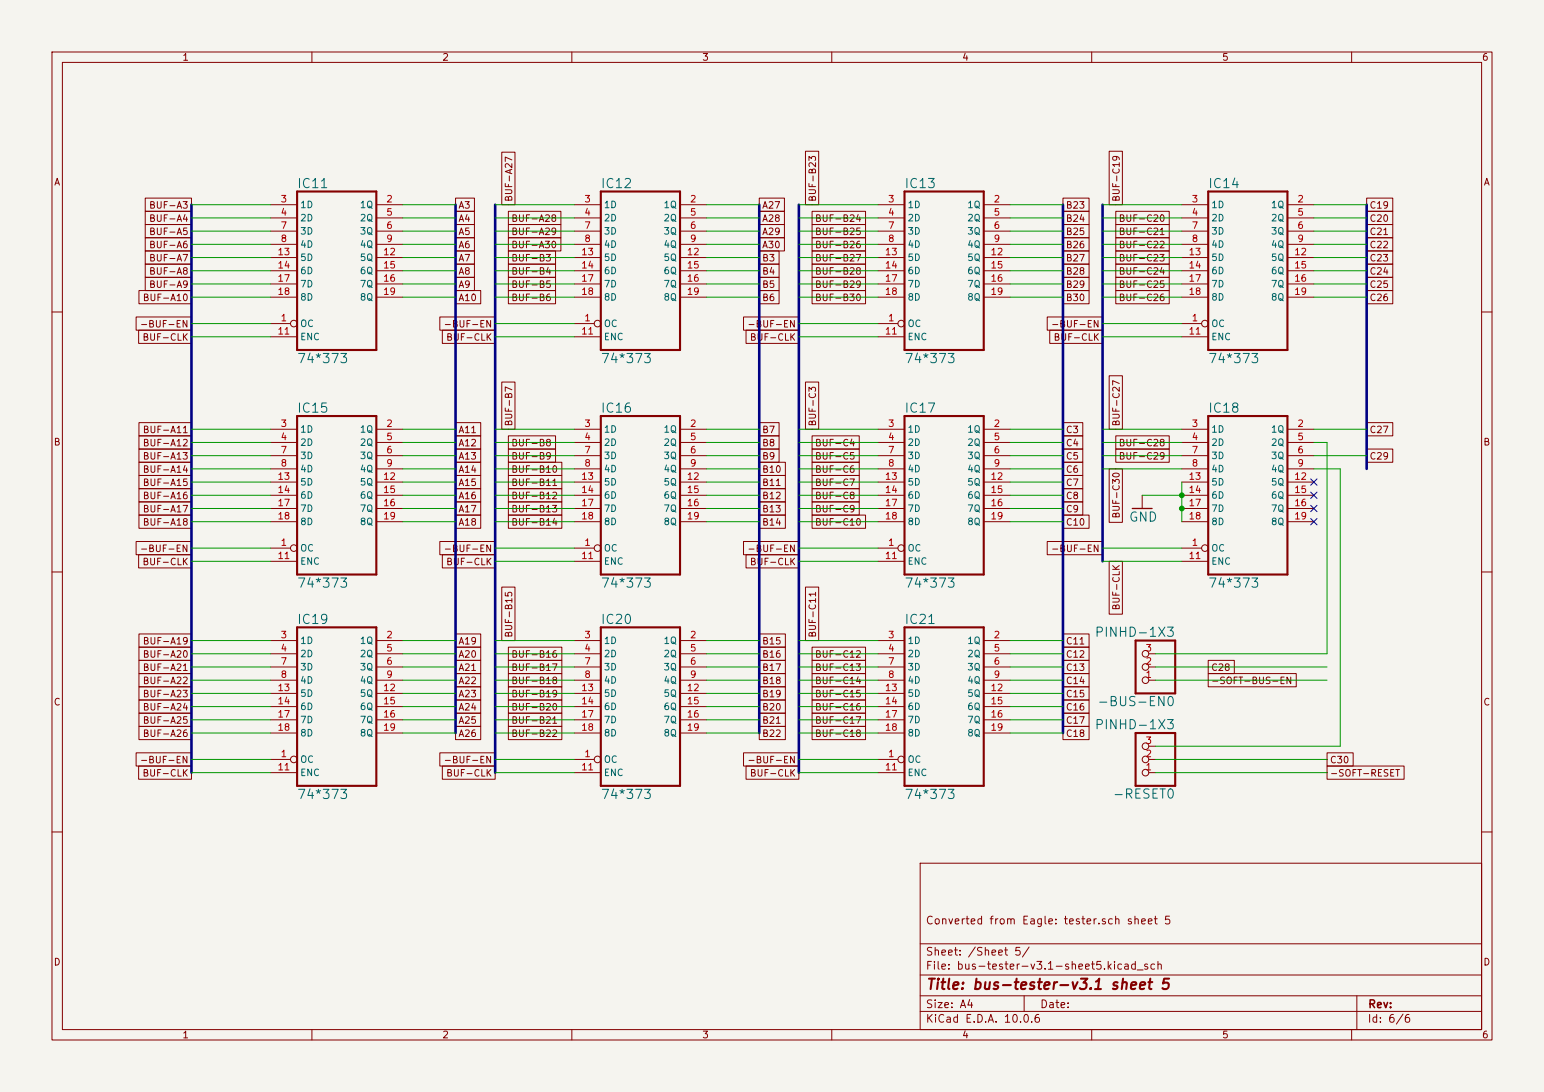
[picture p122: page 6]

BUF-C26 BUF-C25 BUF-C24 BUF-C23

BUF-C10 BUF-C9 BUF-C8 BUF-C7 BUF-C6 BUF-CLK -BUF-EN

Converted from Eagle: tester.sch sheet 5

Sheet: /Sheet 5/
File: bus-tester-v3.1-sheet5.kicad_sch
Title: bus-tester-v3.1 sheet 5
