ksr/YACC1-D/hardware/cards/io/eagle/v1.1/pdf/IO V1.1-schematic.pdf

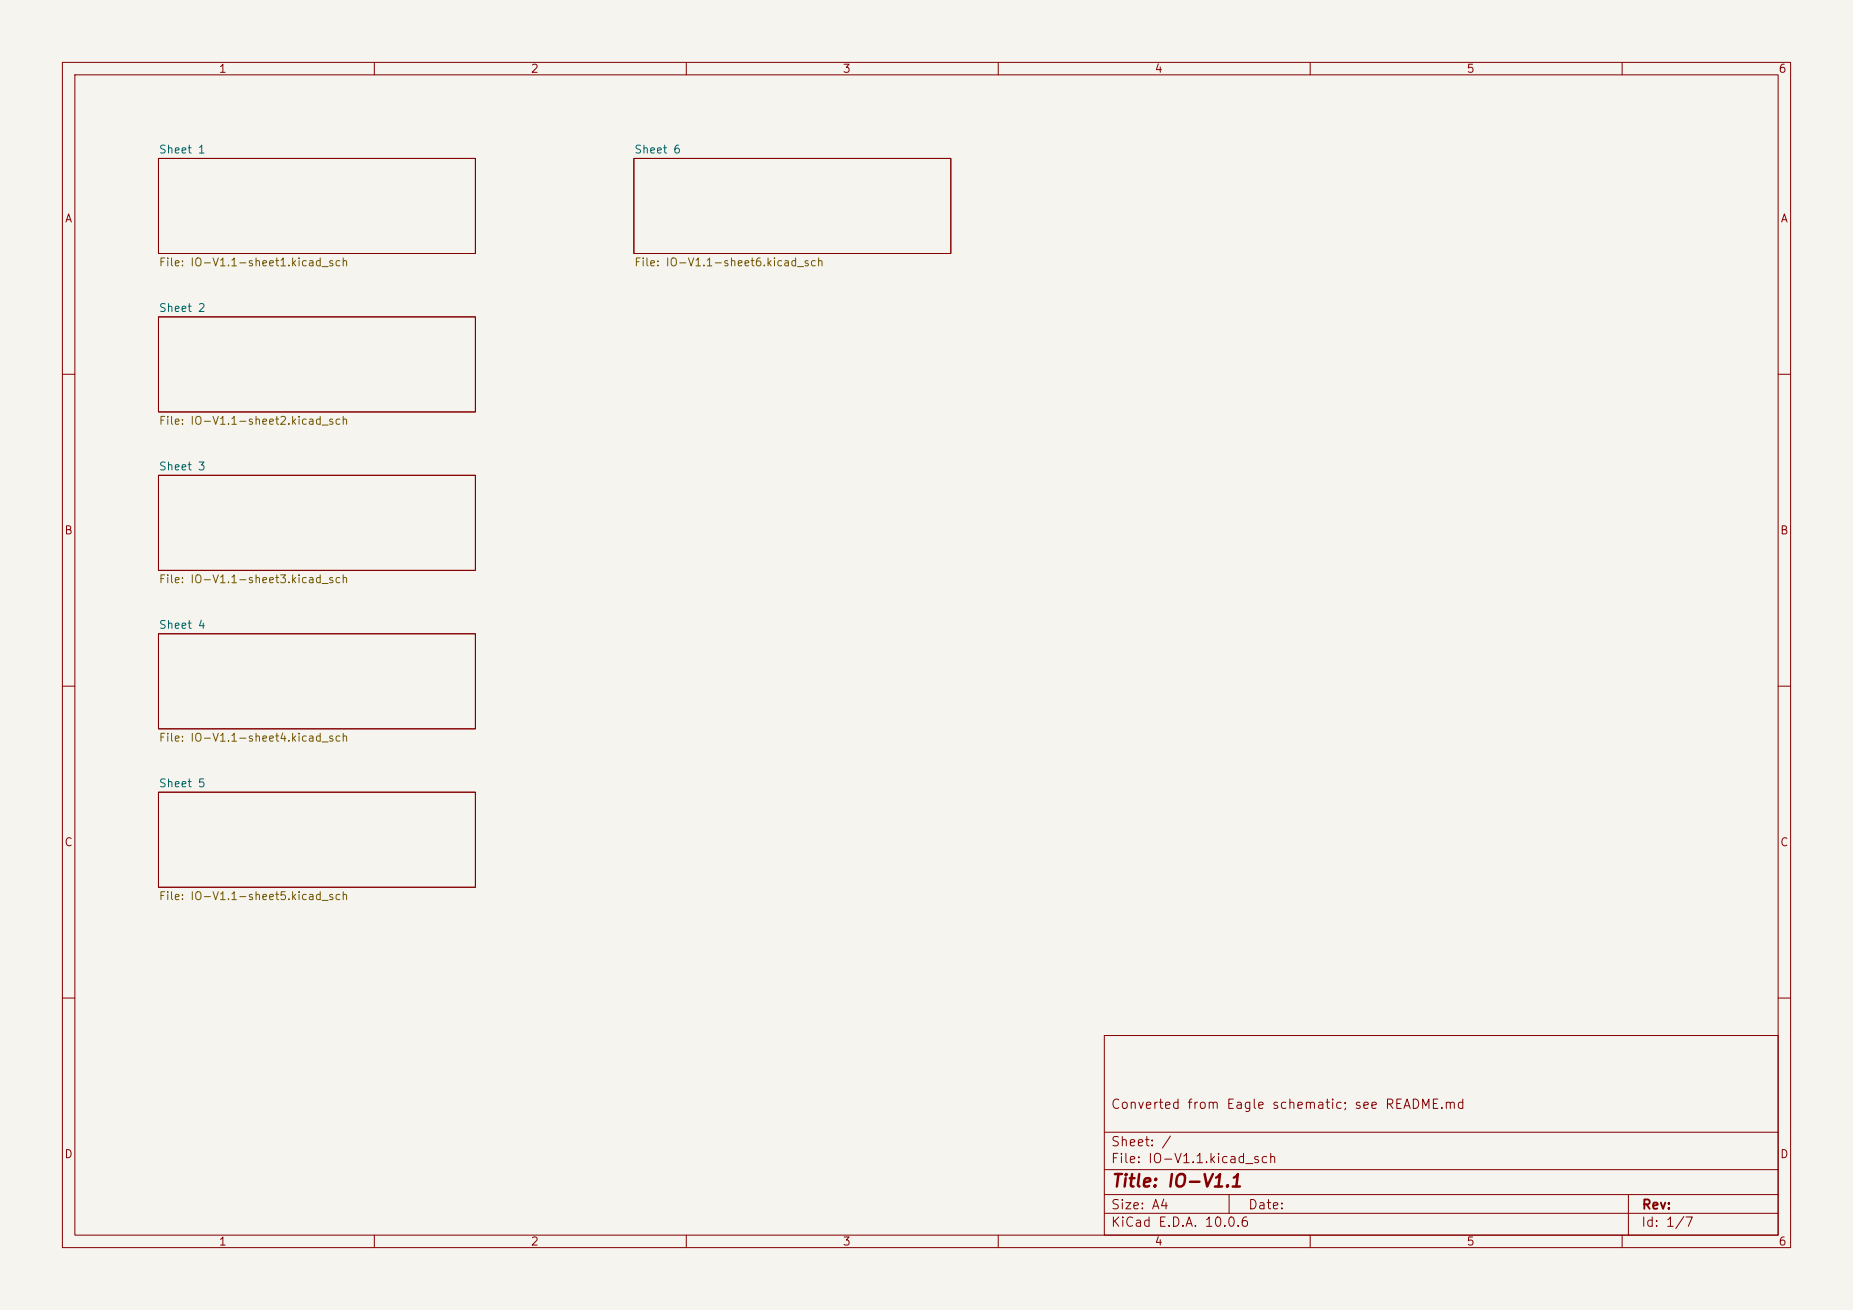
[picture p123: page 1]

Converted from Eagle schematic; see README.md

Size: A4 | Rev:
KiCad E.D.A. 10.0.6 | Id: 1/7

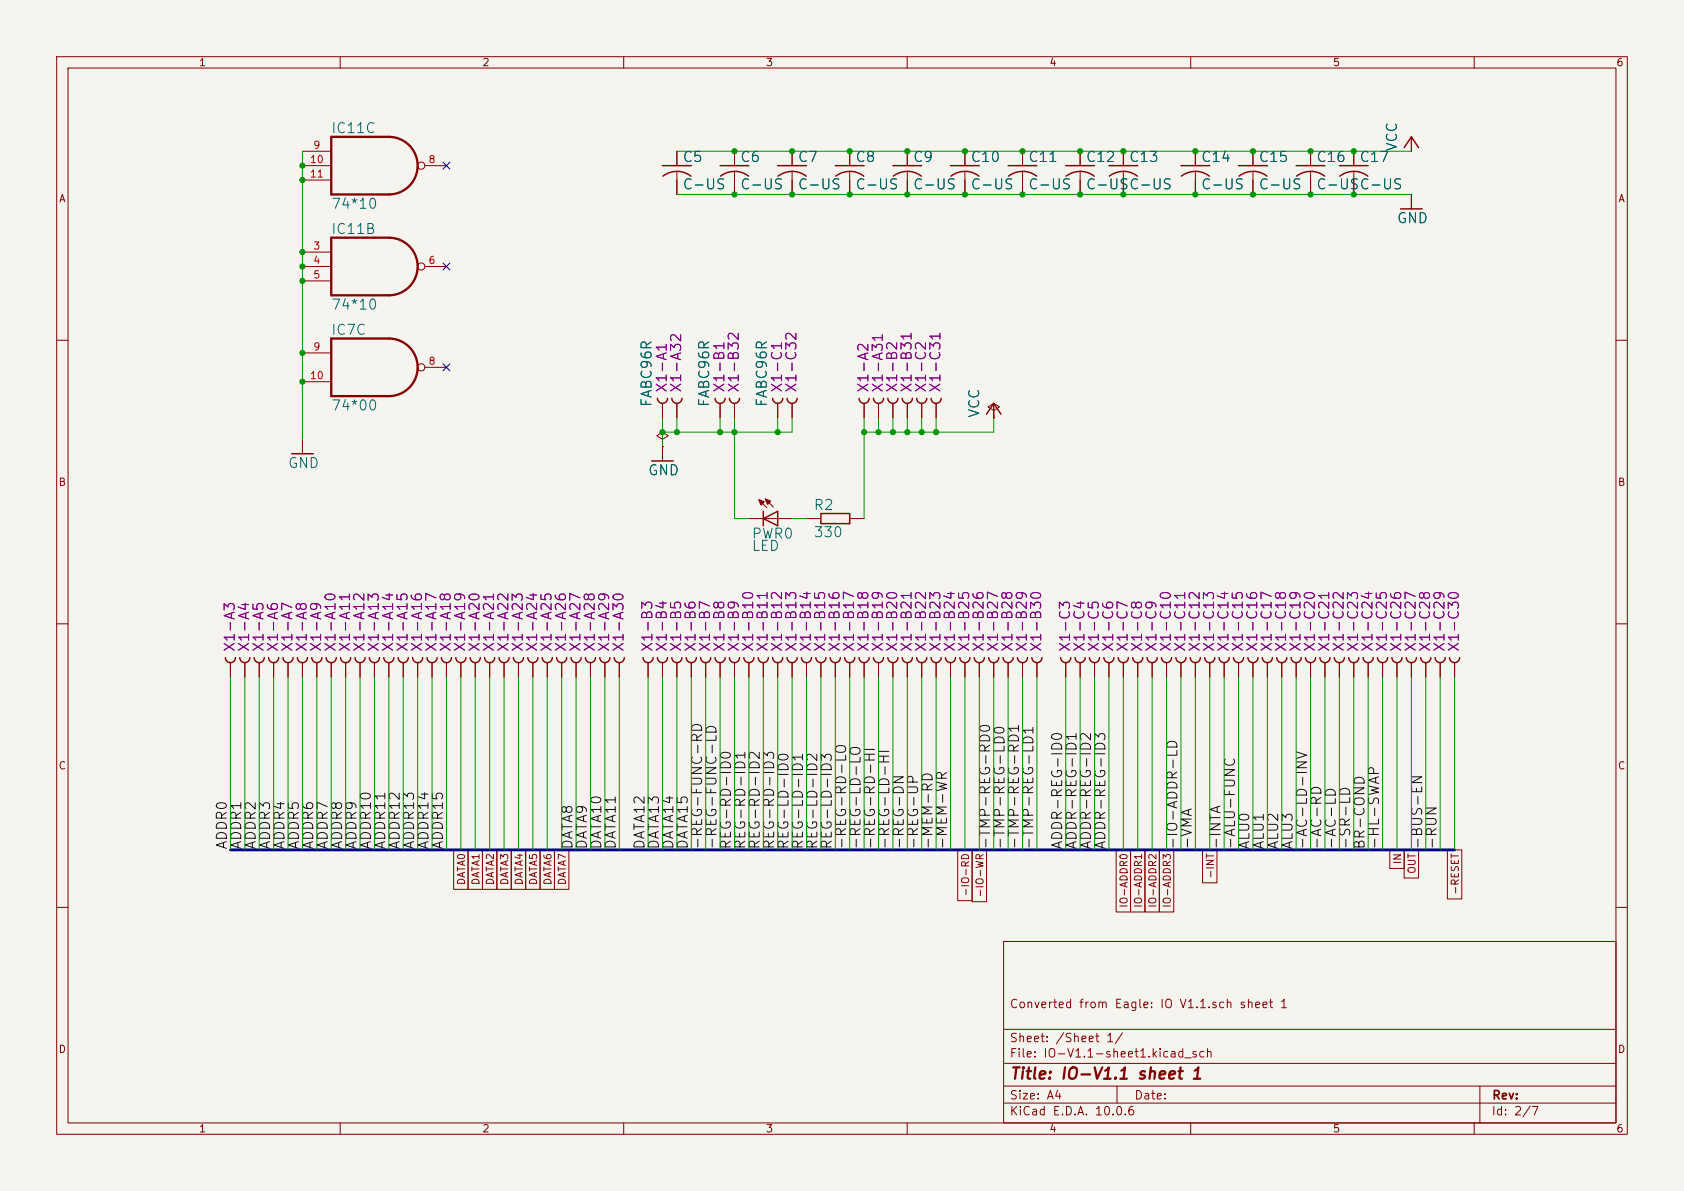
[picture p124: page 2]

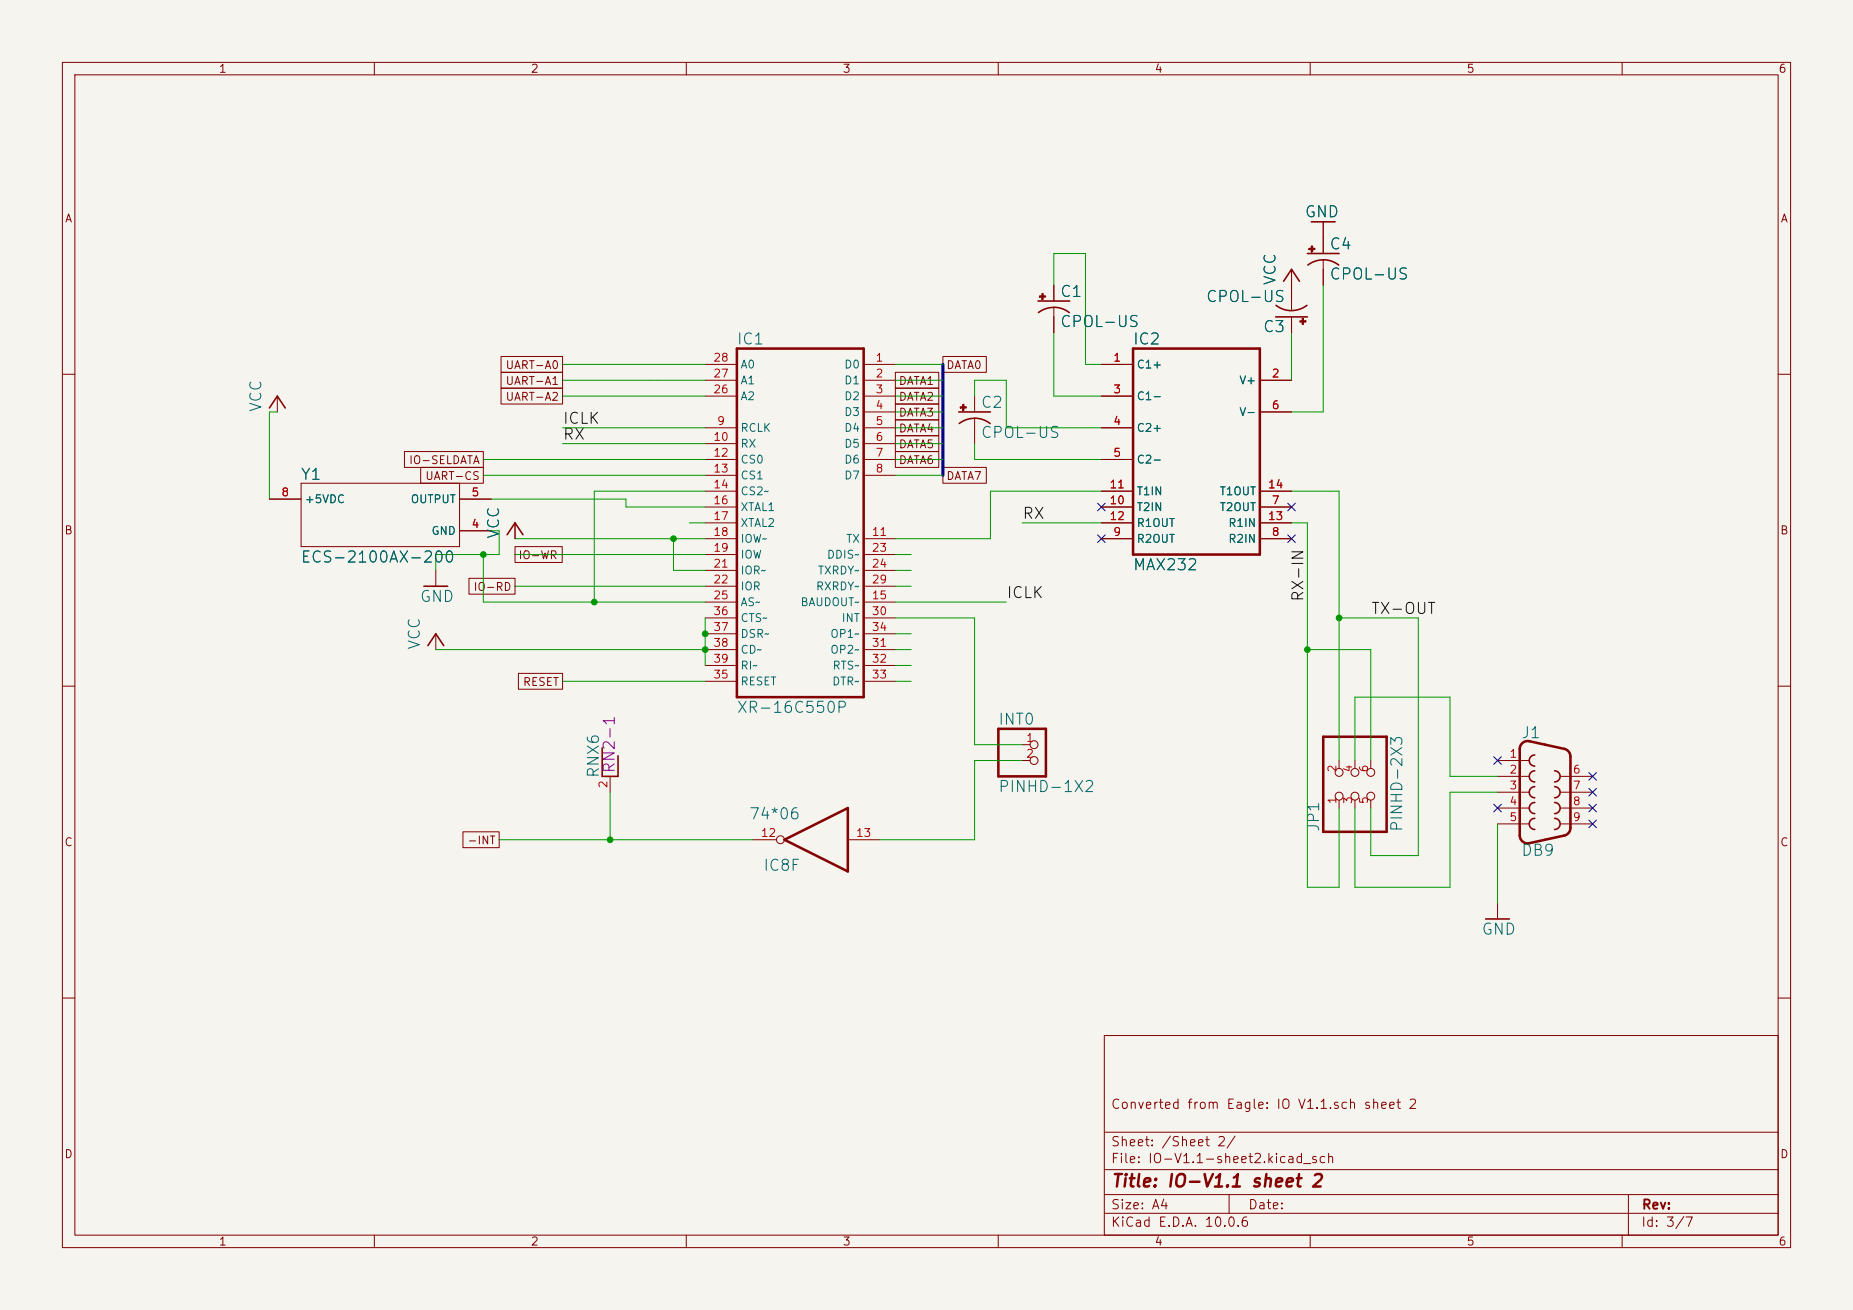
[picture p125: page 3]

Converted from Eagle: IO V1.1.sch sheet 2

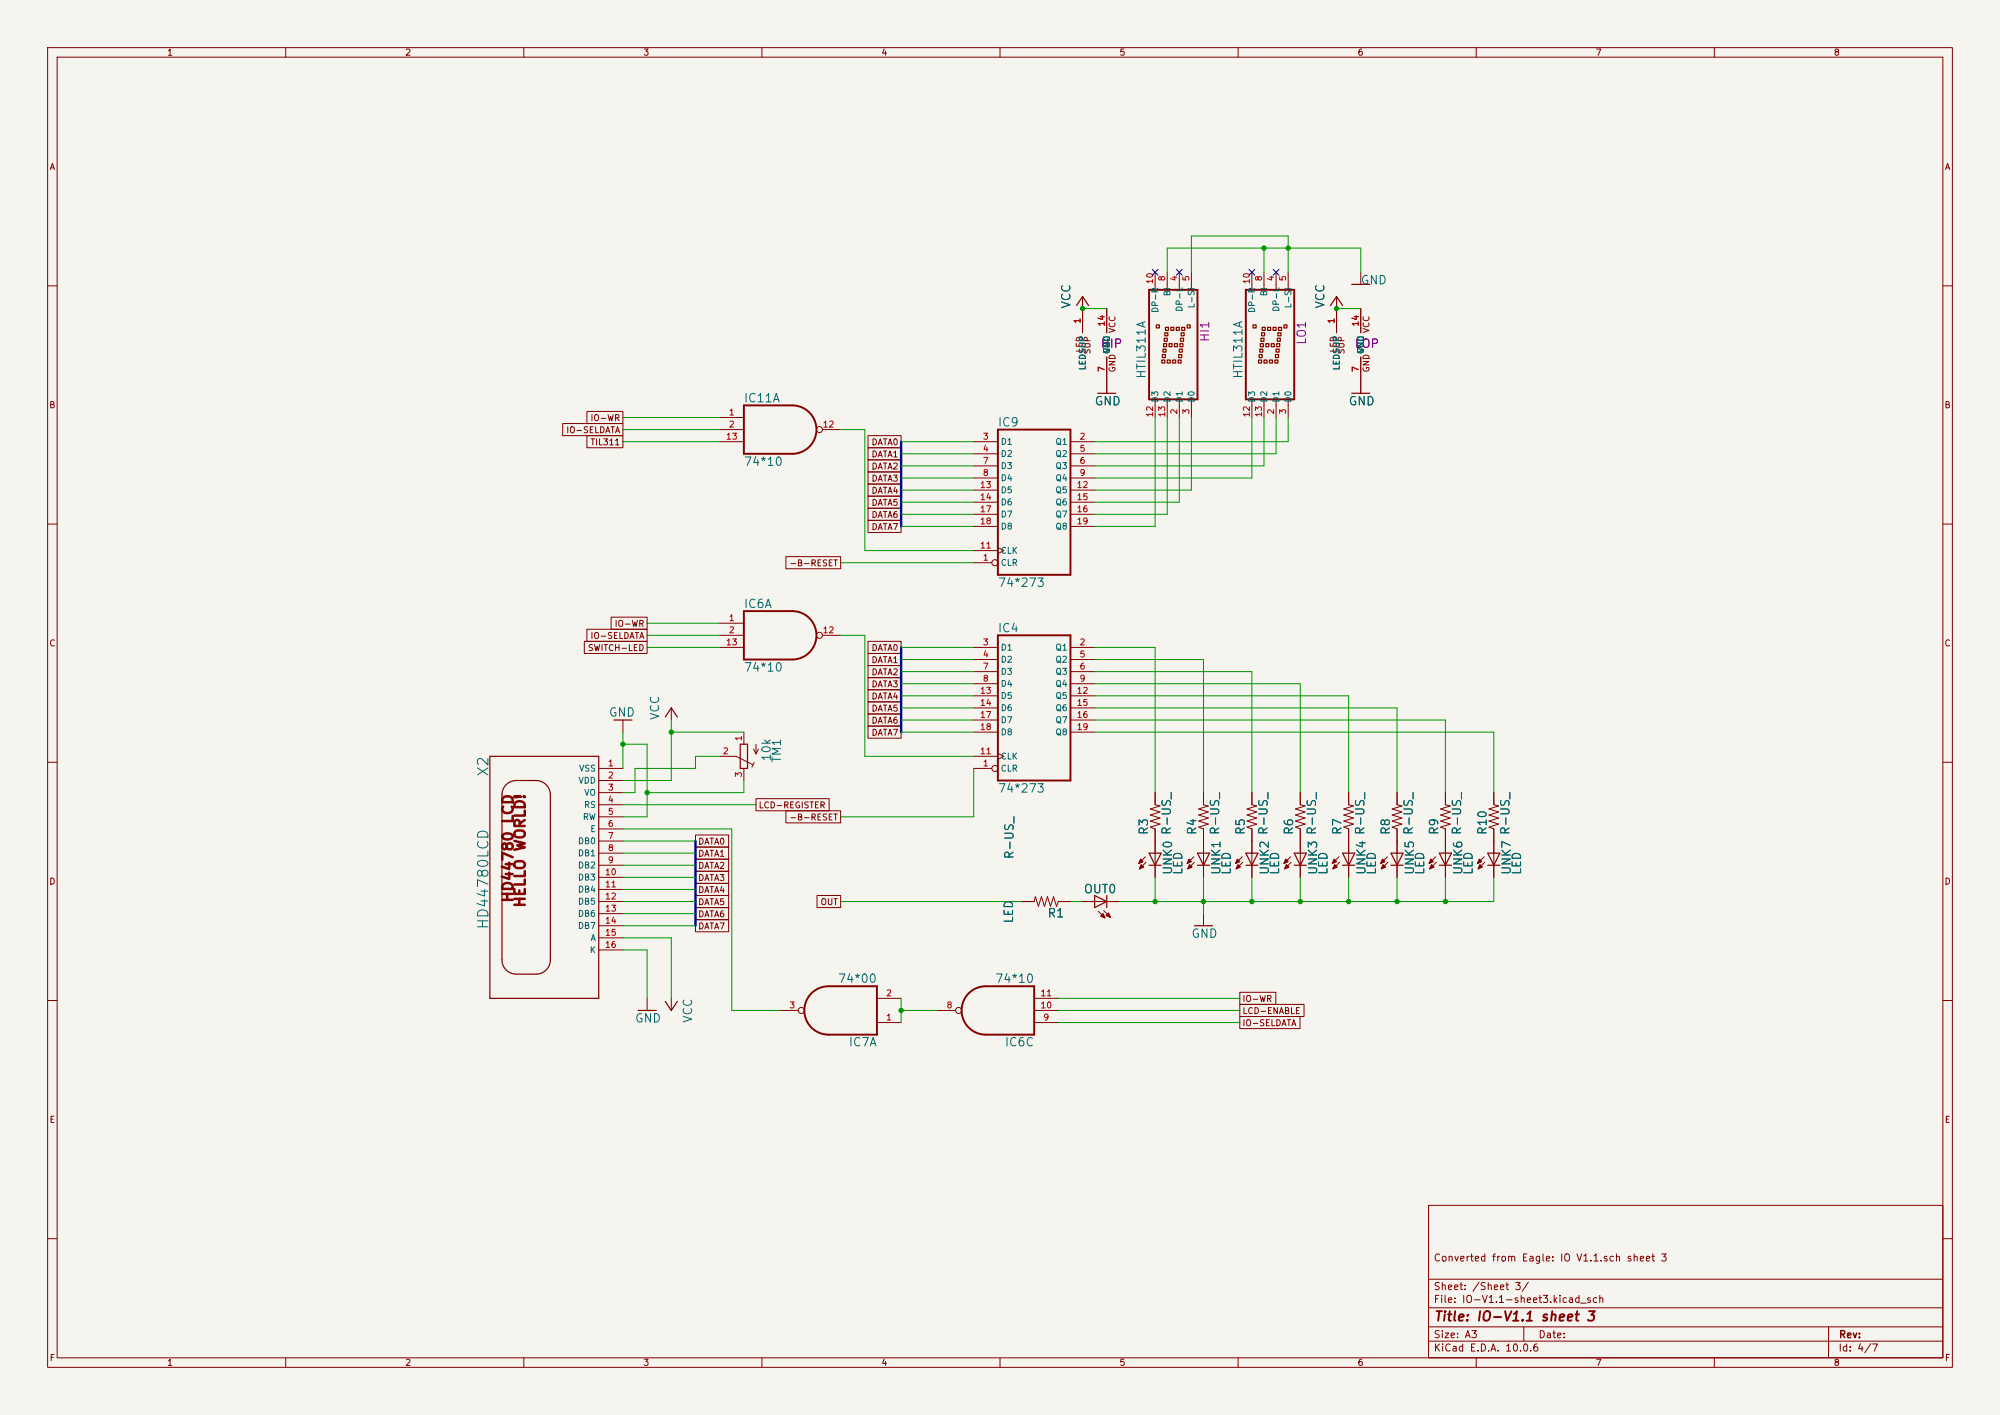
[picture p126: page 4]

Converted from Eagle: IO V1.1.sch sheet 3

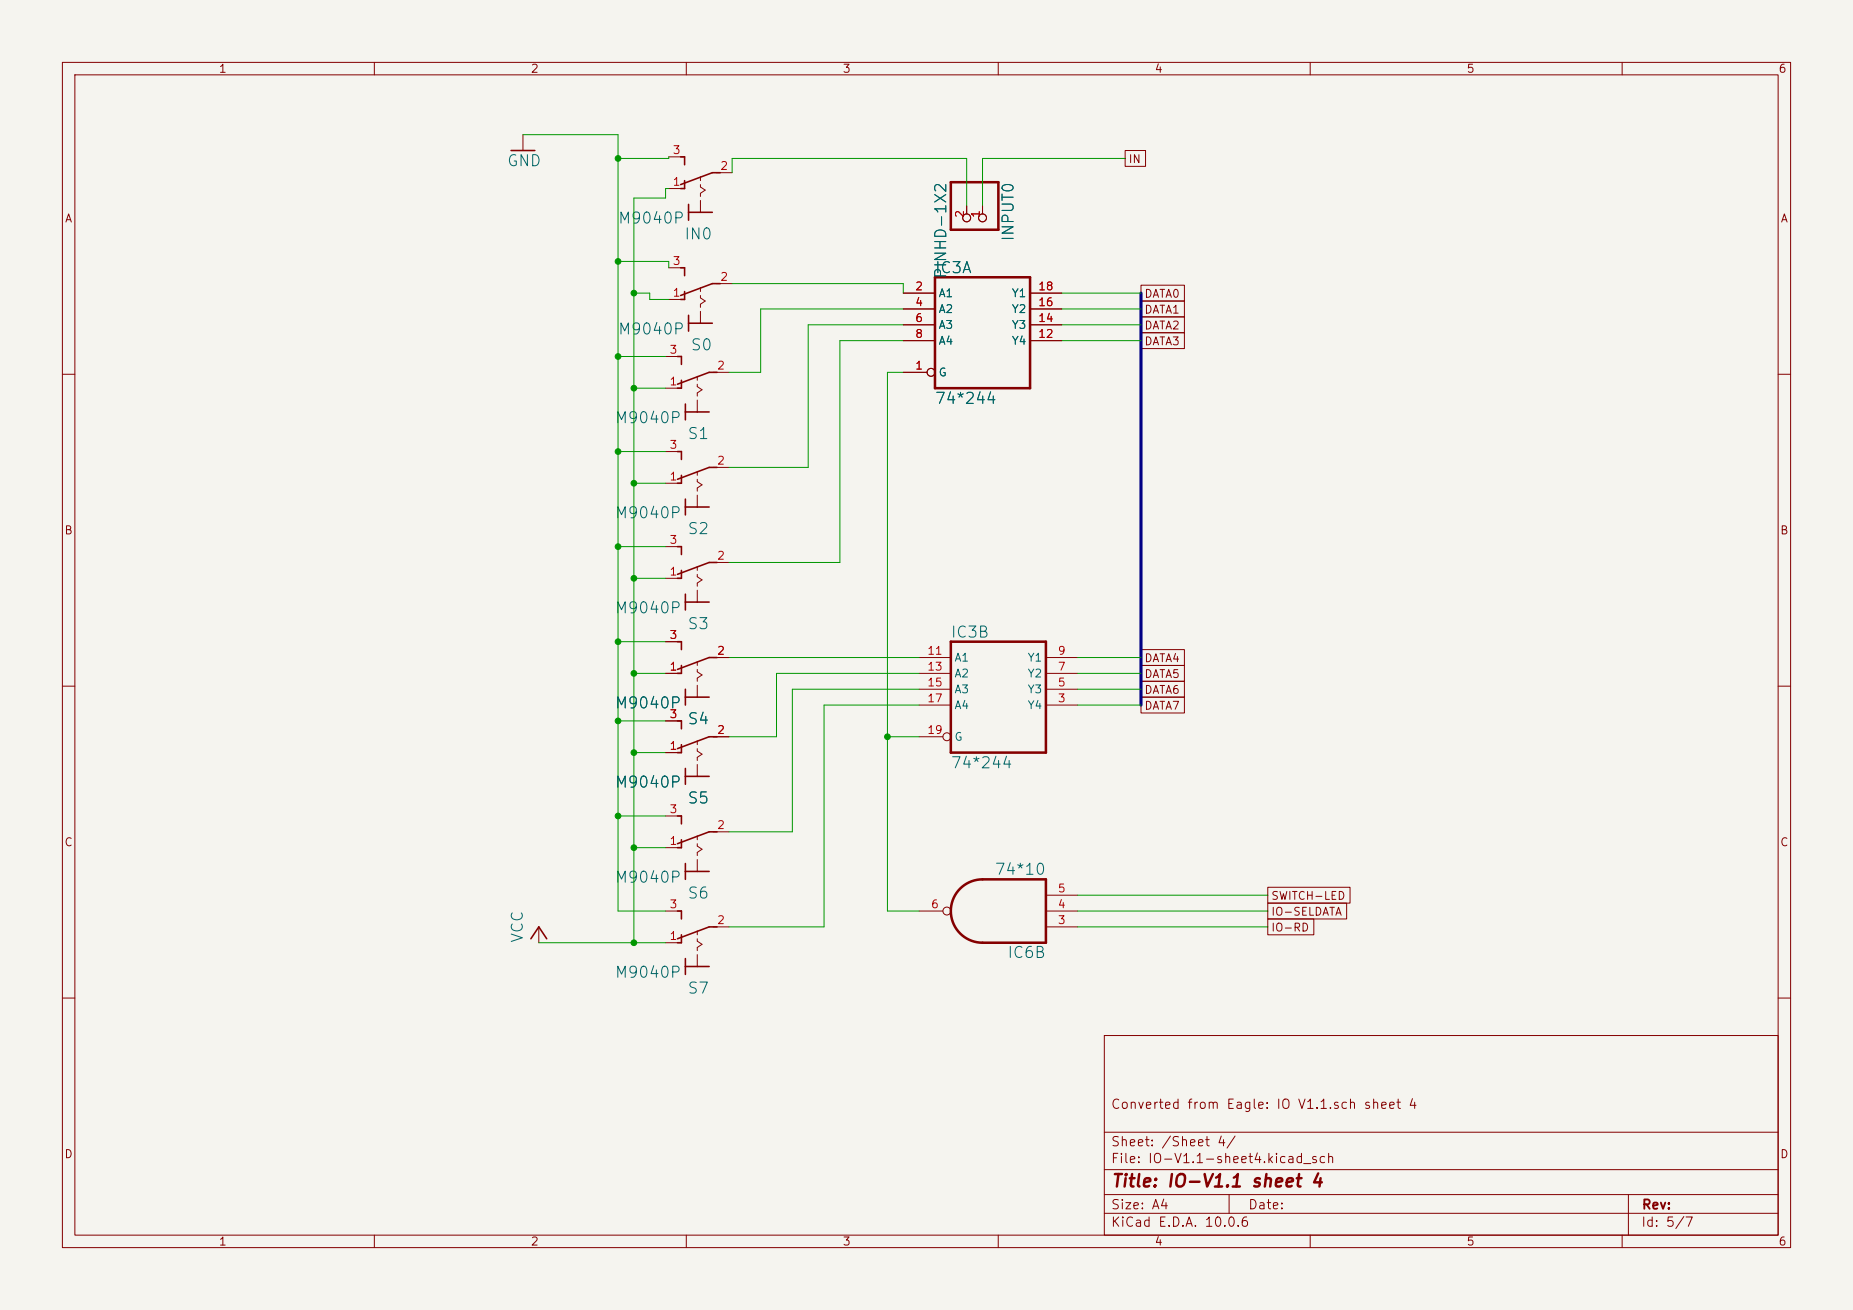
[picture p127: page 5]

Converted from Eagle: IO V1.1.sch sheet 4 VCC

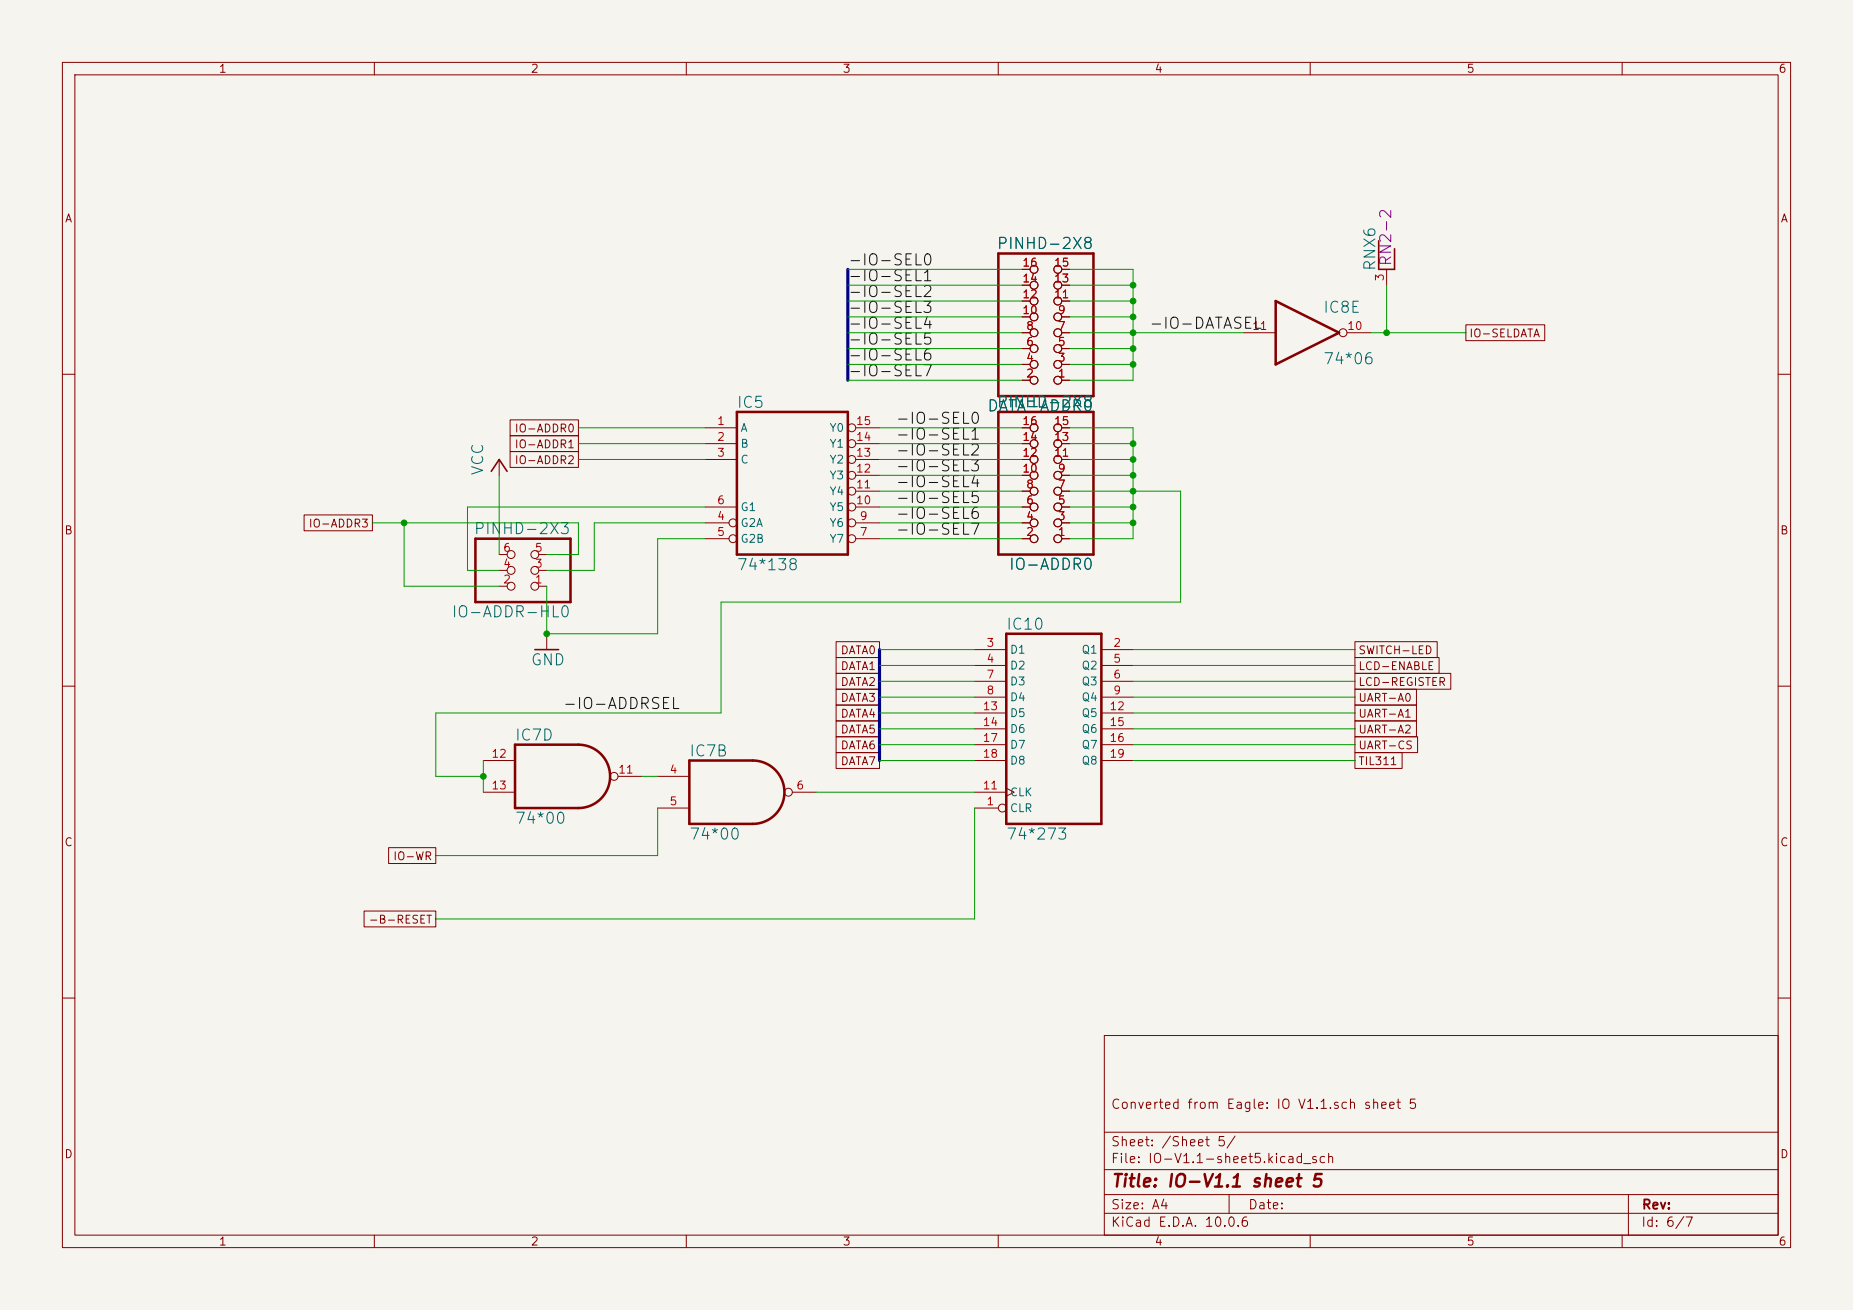
[picture p128: page 6]

IO-SELDATA -IO-ADDRSEL
IO-ADDR3-B-RESET

LCD-REGISTER UART-CS UART-A2 UART-A1 UART-A0 DATA0 DATA1
DATA2 DATA6

Converted from Eagle: IO V1.1.sch sheet 5

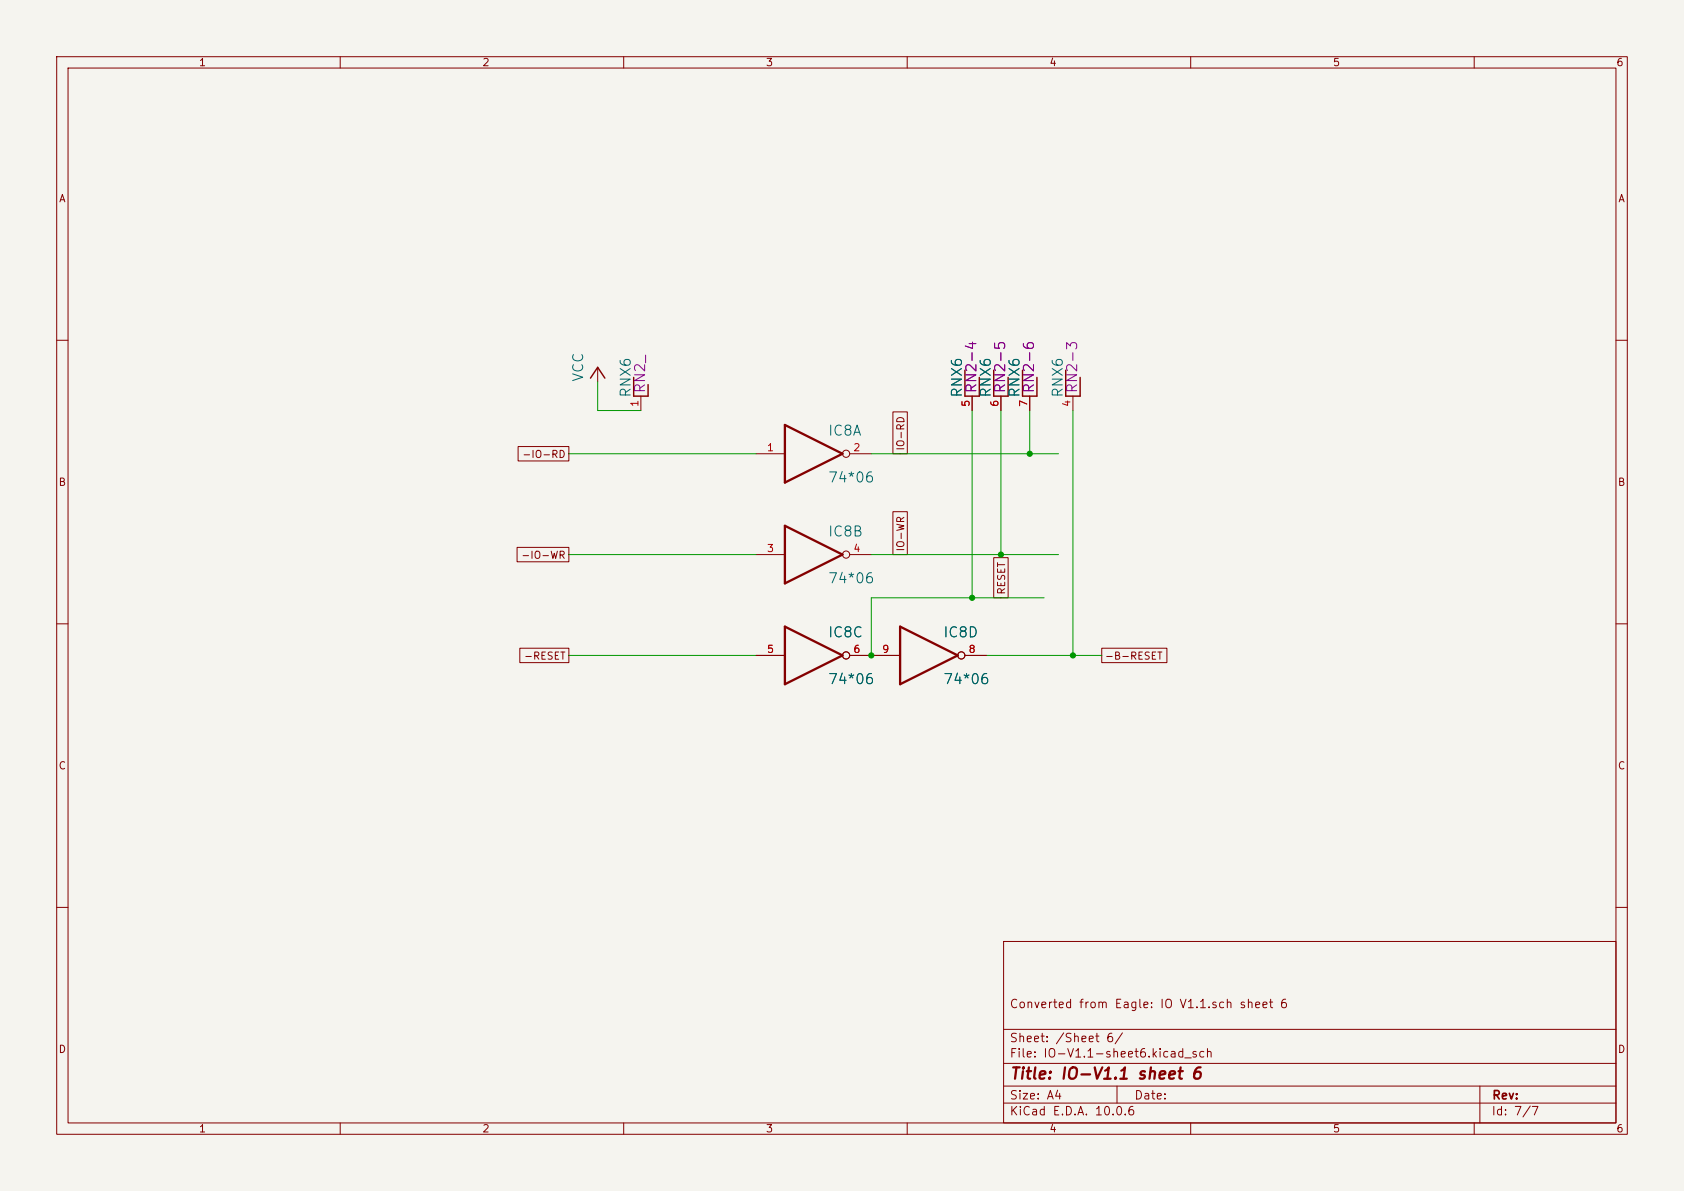
[picture p129: page 7]

Converted from Eagle: IO V1.1.sch sheet 6
