ksr/YACC1-D/hardware/cards/mem-register/eagle/v1.0/pdf/Mem Register V1.0-schematic.pdf

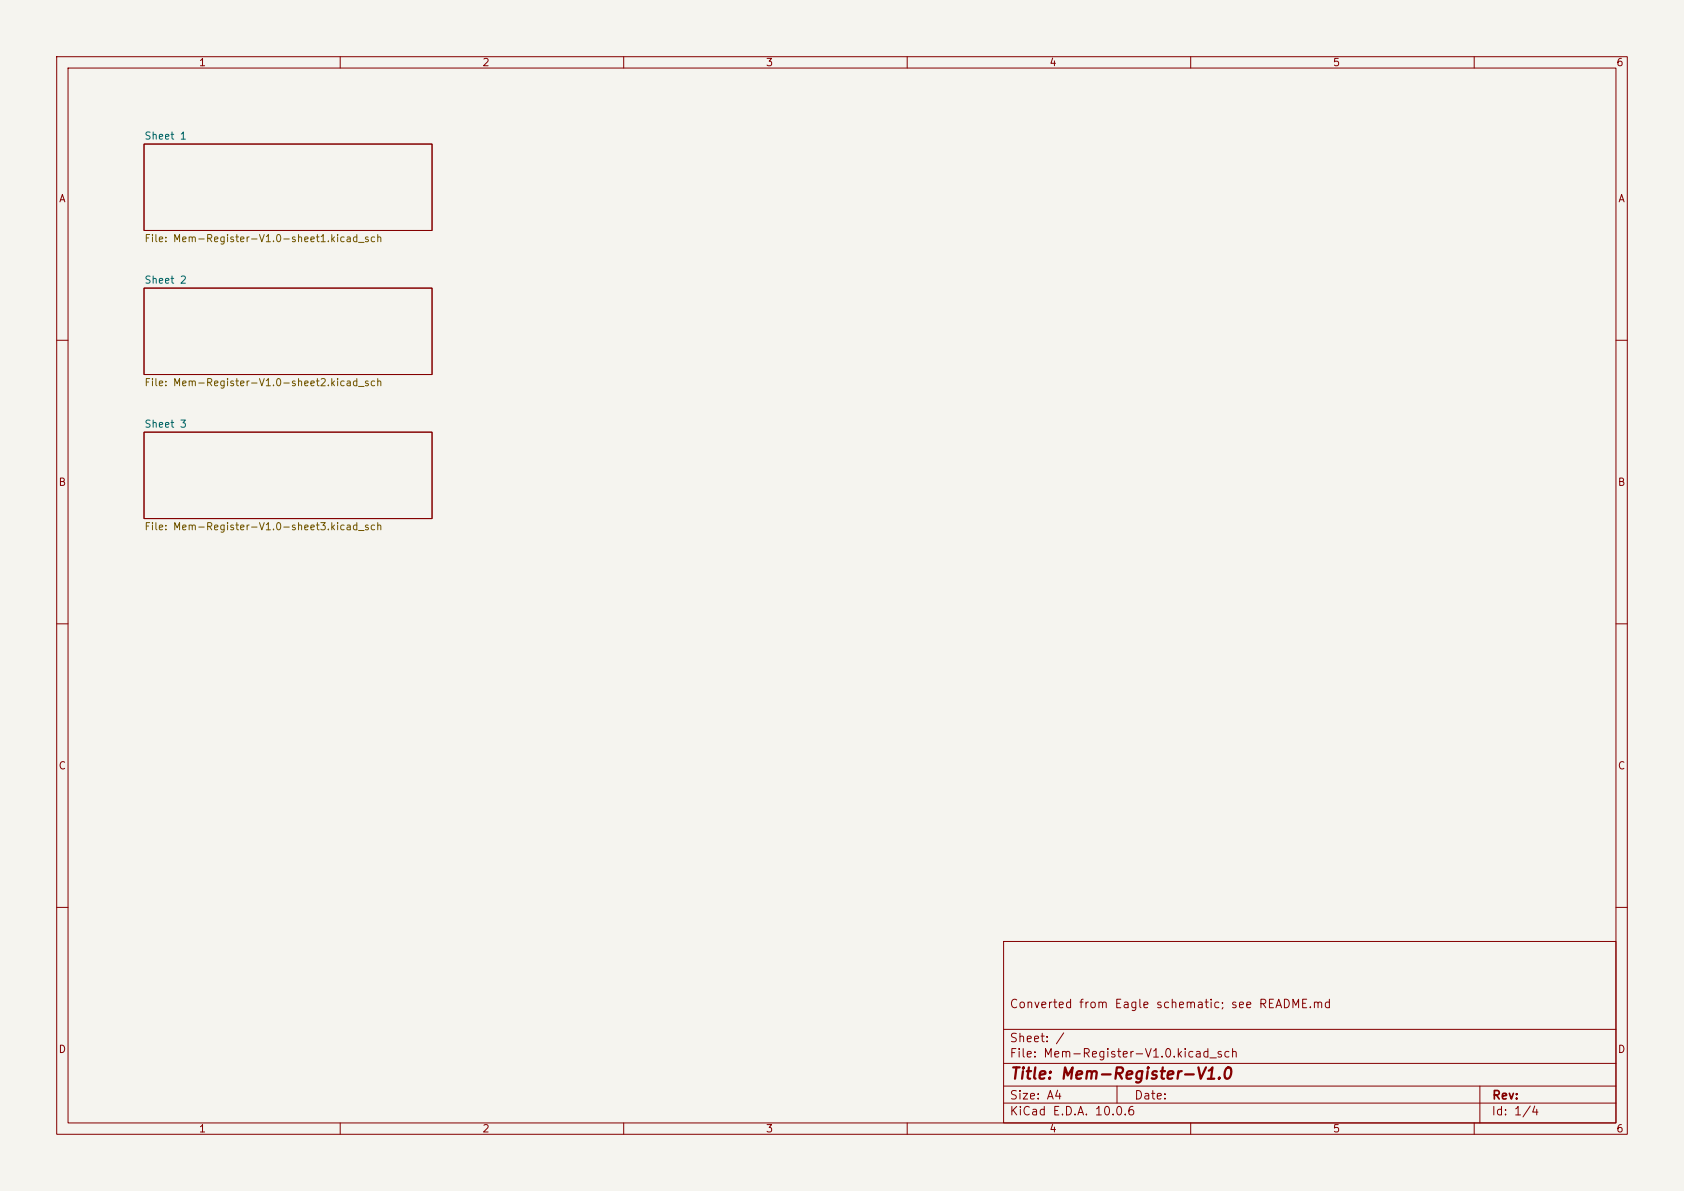
[picture p130: page 1]

File: Mem-Register-V1.0-sheet1.kicad_sch Sheet 2

File: Mem-Register-V1.0-sheet2.kicad_sch Sheet 3

Converted from Eagle schematic; see README.md

Size: A4 | Rev:
KiCad E.D.A. 10.0.6 | Id: 1/4

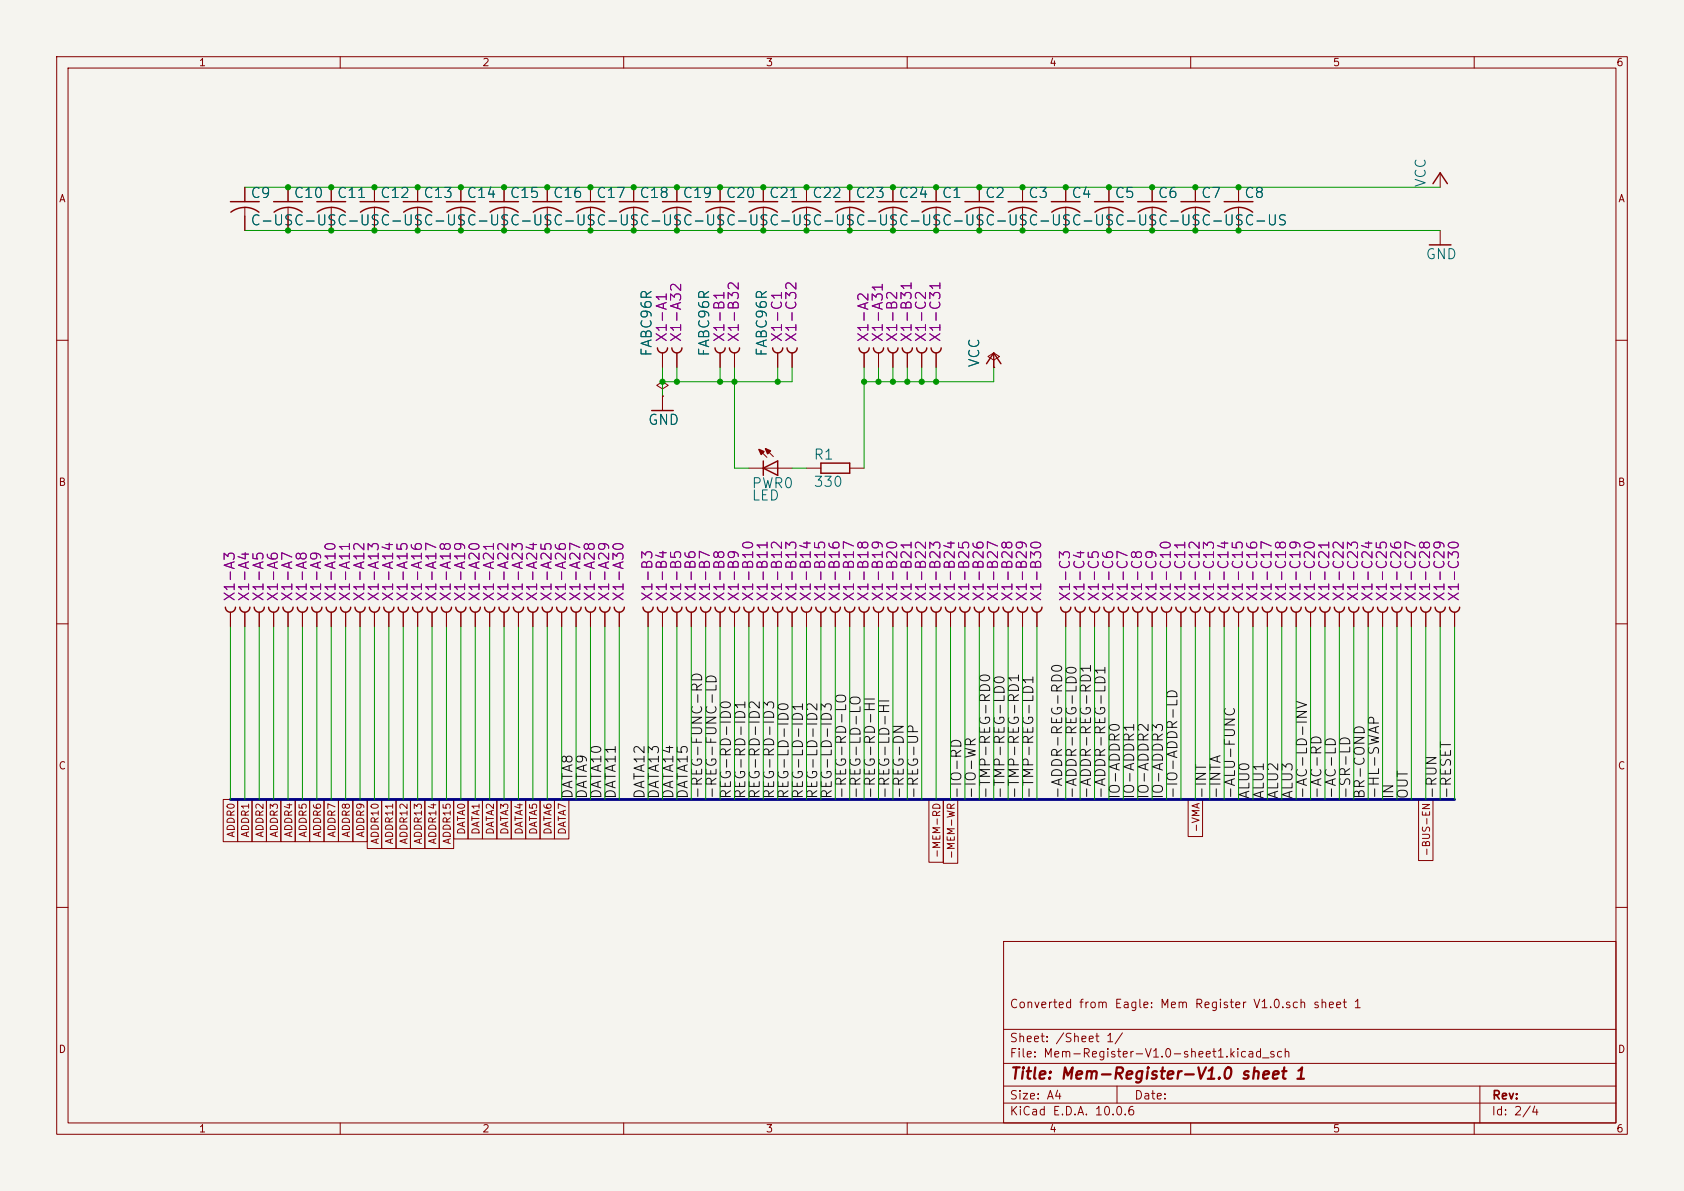
[picture p131: page 2]

Sheet: /Sheet 1/
File: Mem-Register-V1.0-sheet1.kicad_sch
Title: Mem-Register-V1.0 sheet 1

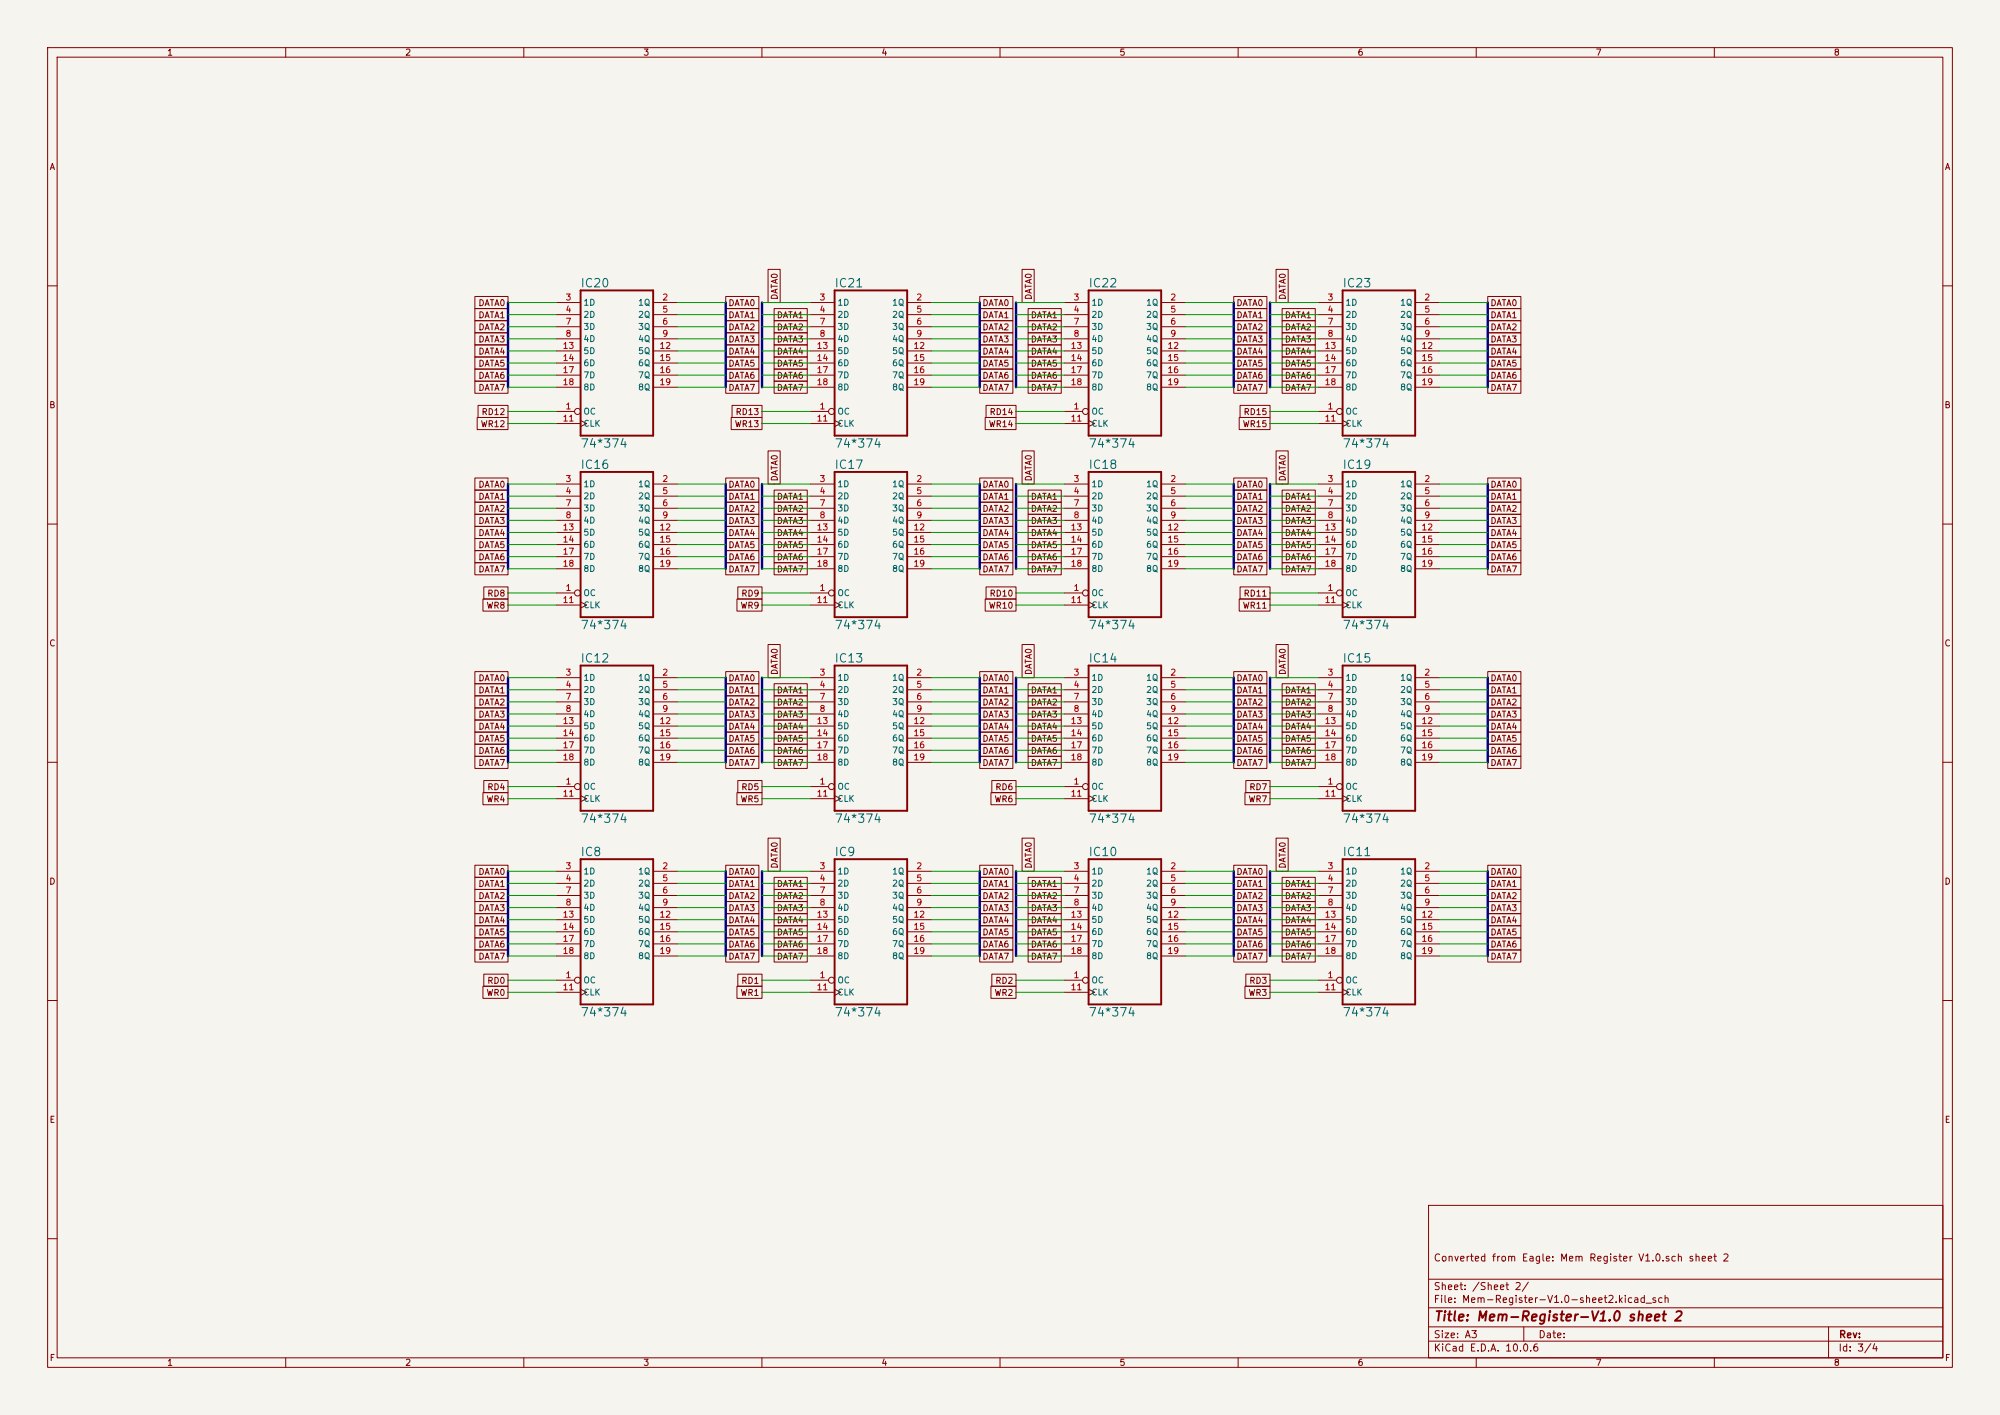
[picture p132: page 3]

Converted from Eagle: Mem Register V1.0.sch sheet 2

Sheet: /Sheet 2/
File: Mem-Register-V1.0-sheet2.kicad_sch
Title: Mem-Register-V1.0 sheet 2

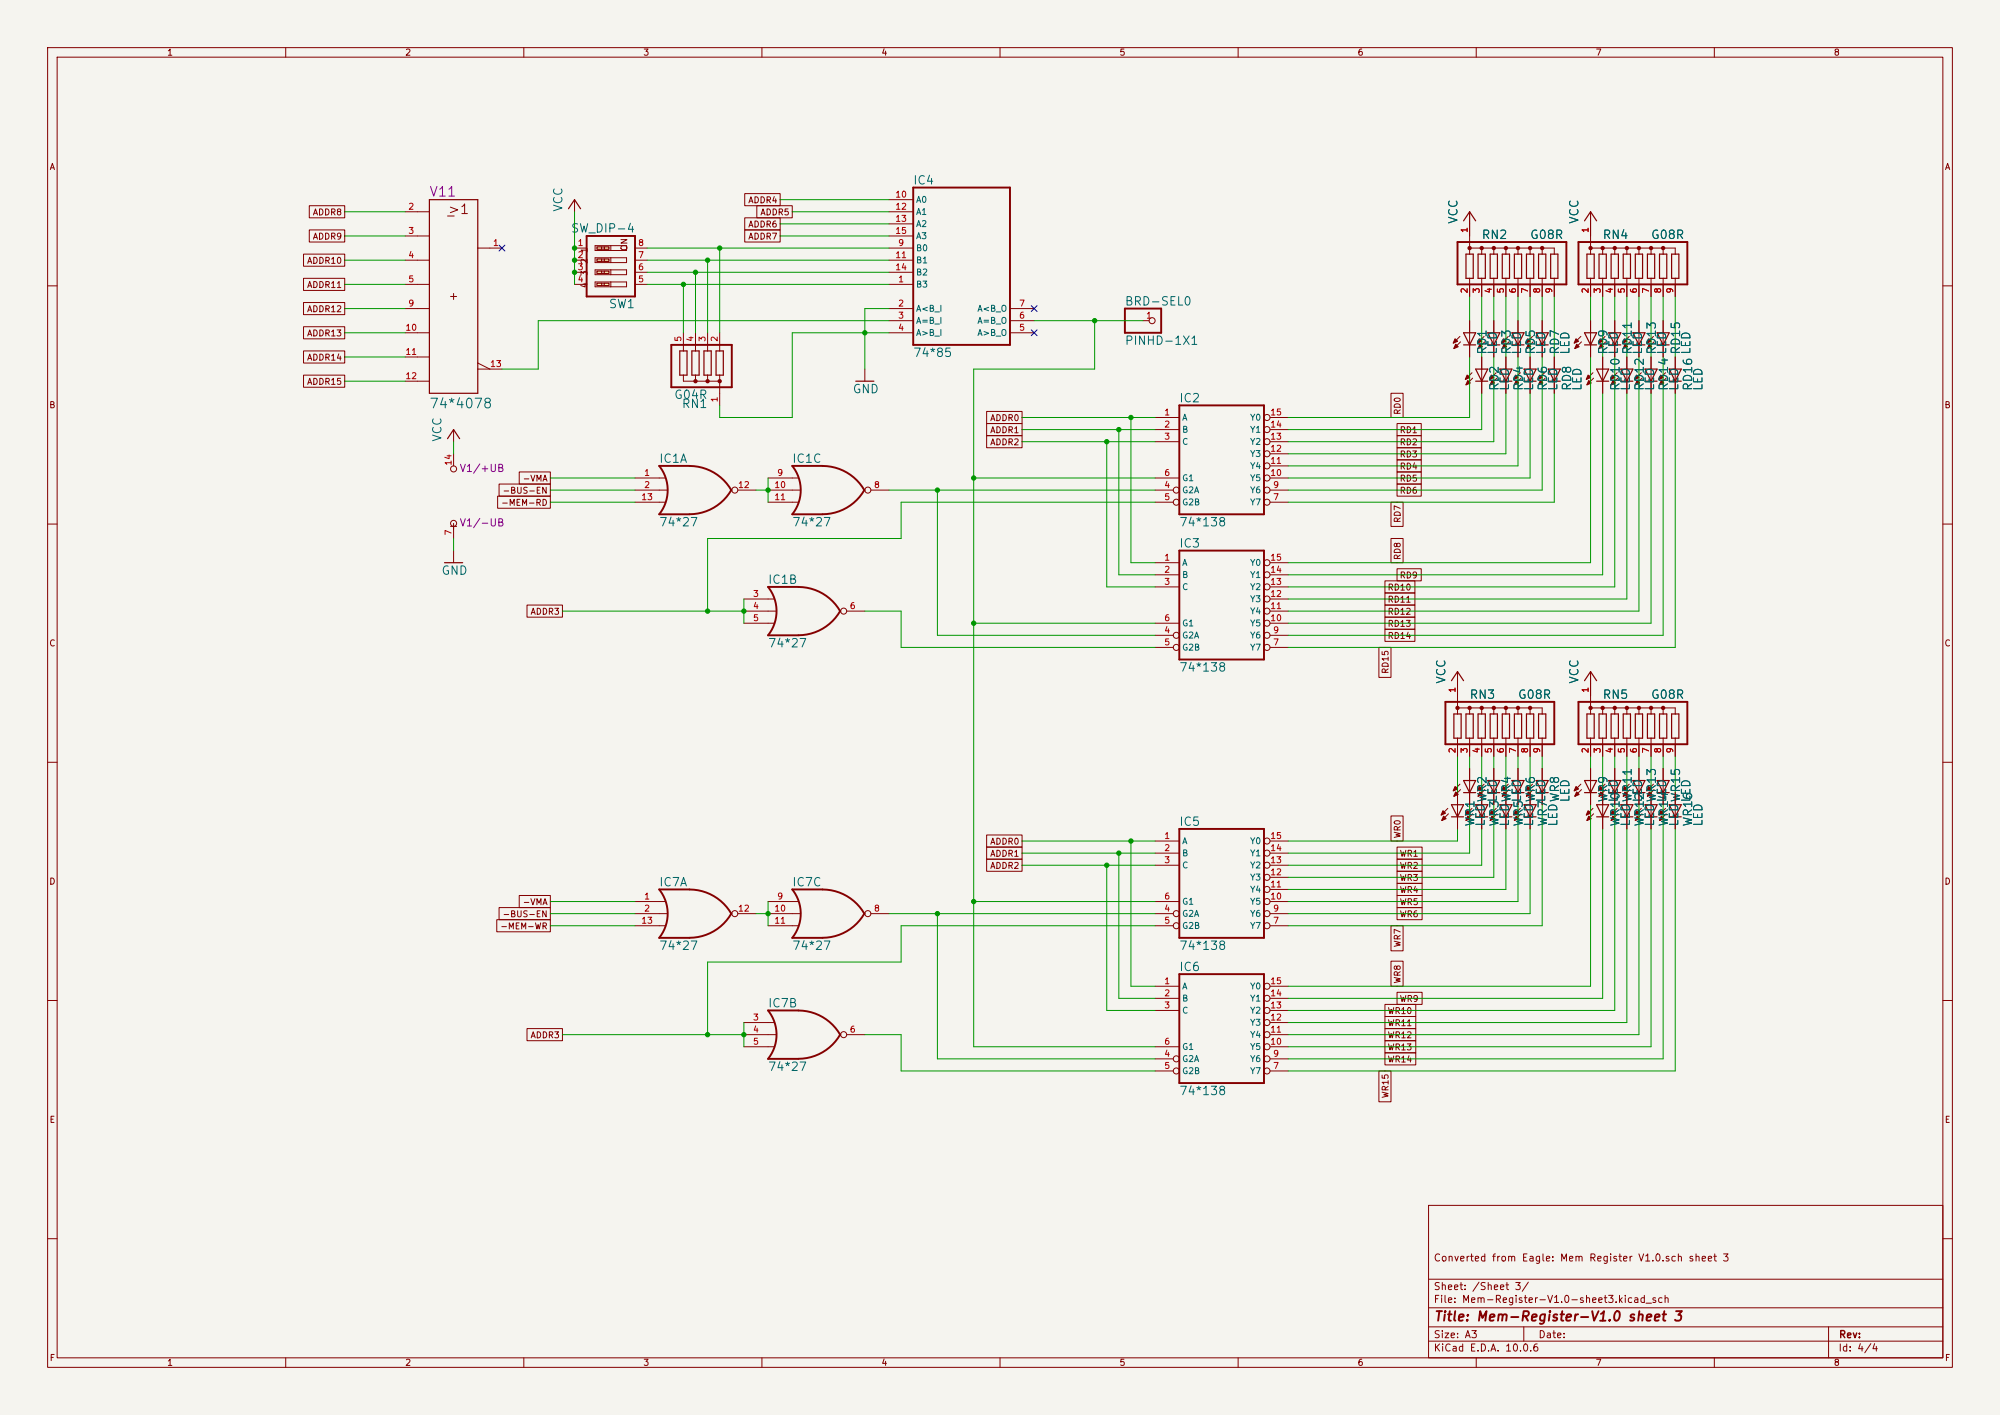
[picture p133: page 4]

Sheet: /Sheet 3/
File: Mem-Register-V1.0-sheet3.kicad_sch
Title: Mem-Register-V1.0 sheet 3
