ksr/YACC1-D/hardware/cards/mem-switch/kicad/v1.1/reports/mem-switch-v1.1-schematic.pdf

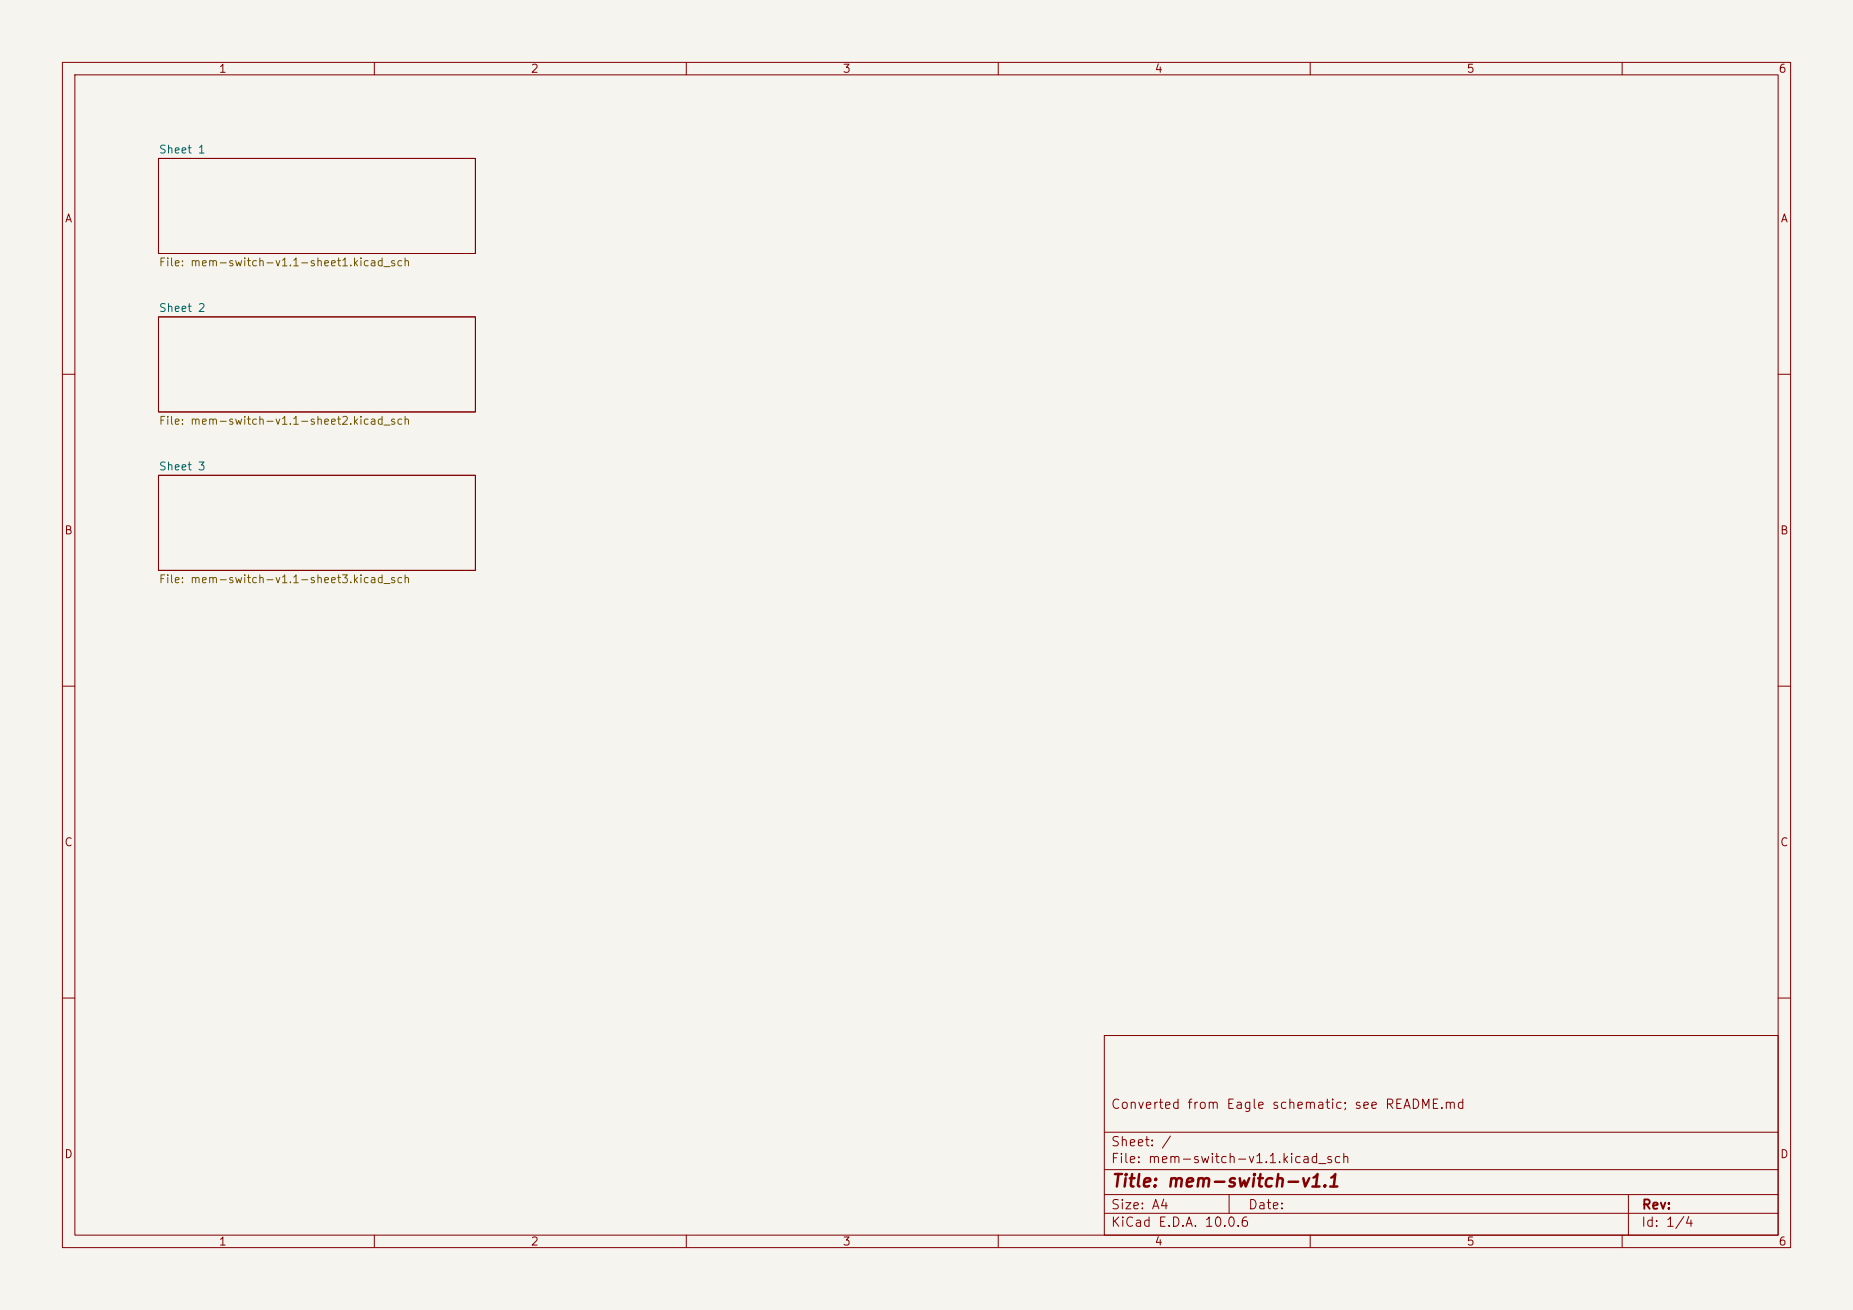
[picture p142: page 1]

File: mem-switch-v1.1-sheet1.kicad_sch Sheet 2

File: mem-switch-v1.1-sheet2.kicad_sch Sheet 3

Converted from Eagle schematic; see README.md

Size: A4 | Rev:
KiCad E.D.A. 10.0.6 | Id: 1/4

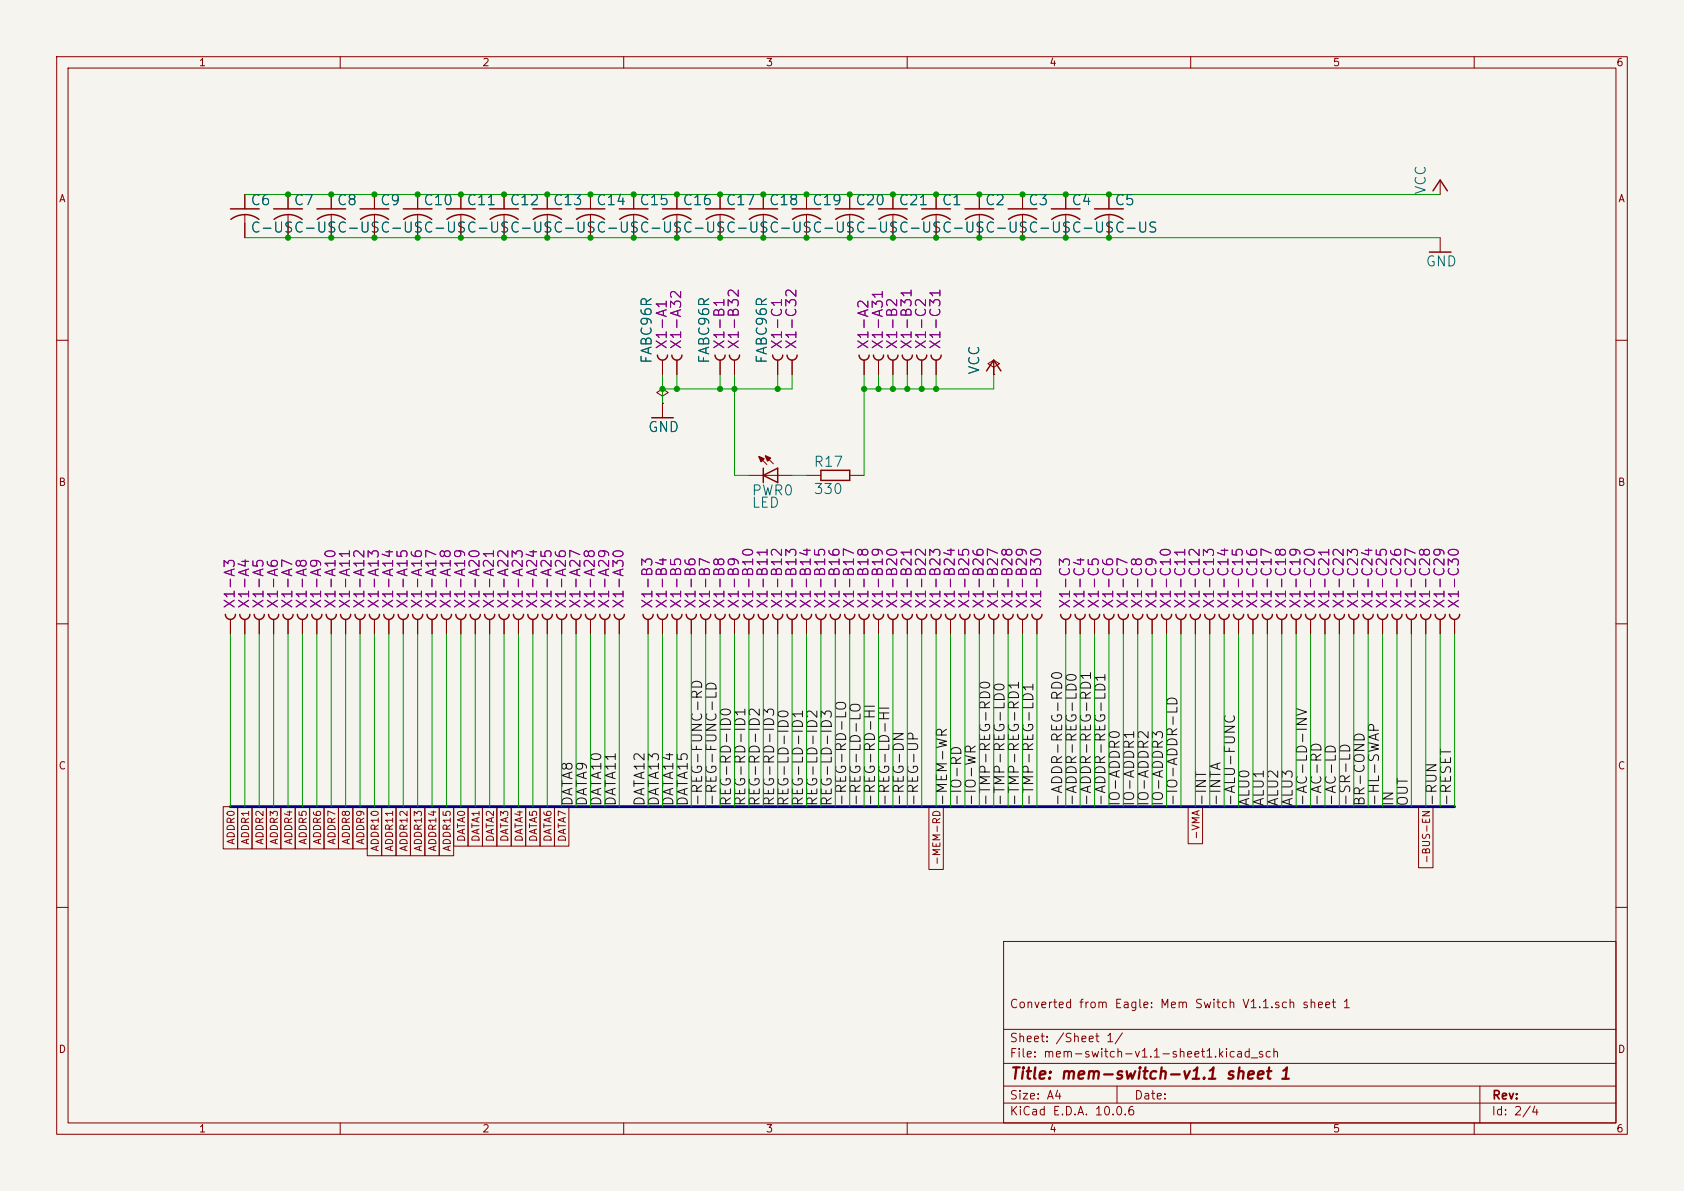
[picture p143: page 2]

Converted from Eagle: Mem Switch V1.1.sch sheet 1

Sheet: /Sheet 1/
File: mem-switch-v1.1-sheet1.kicad_sch
Title: mem-switch-v1.1 sheet 1

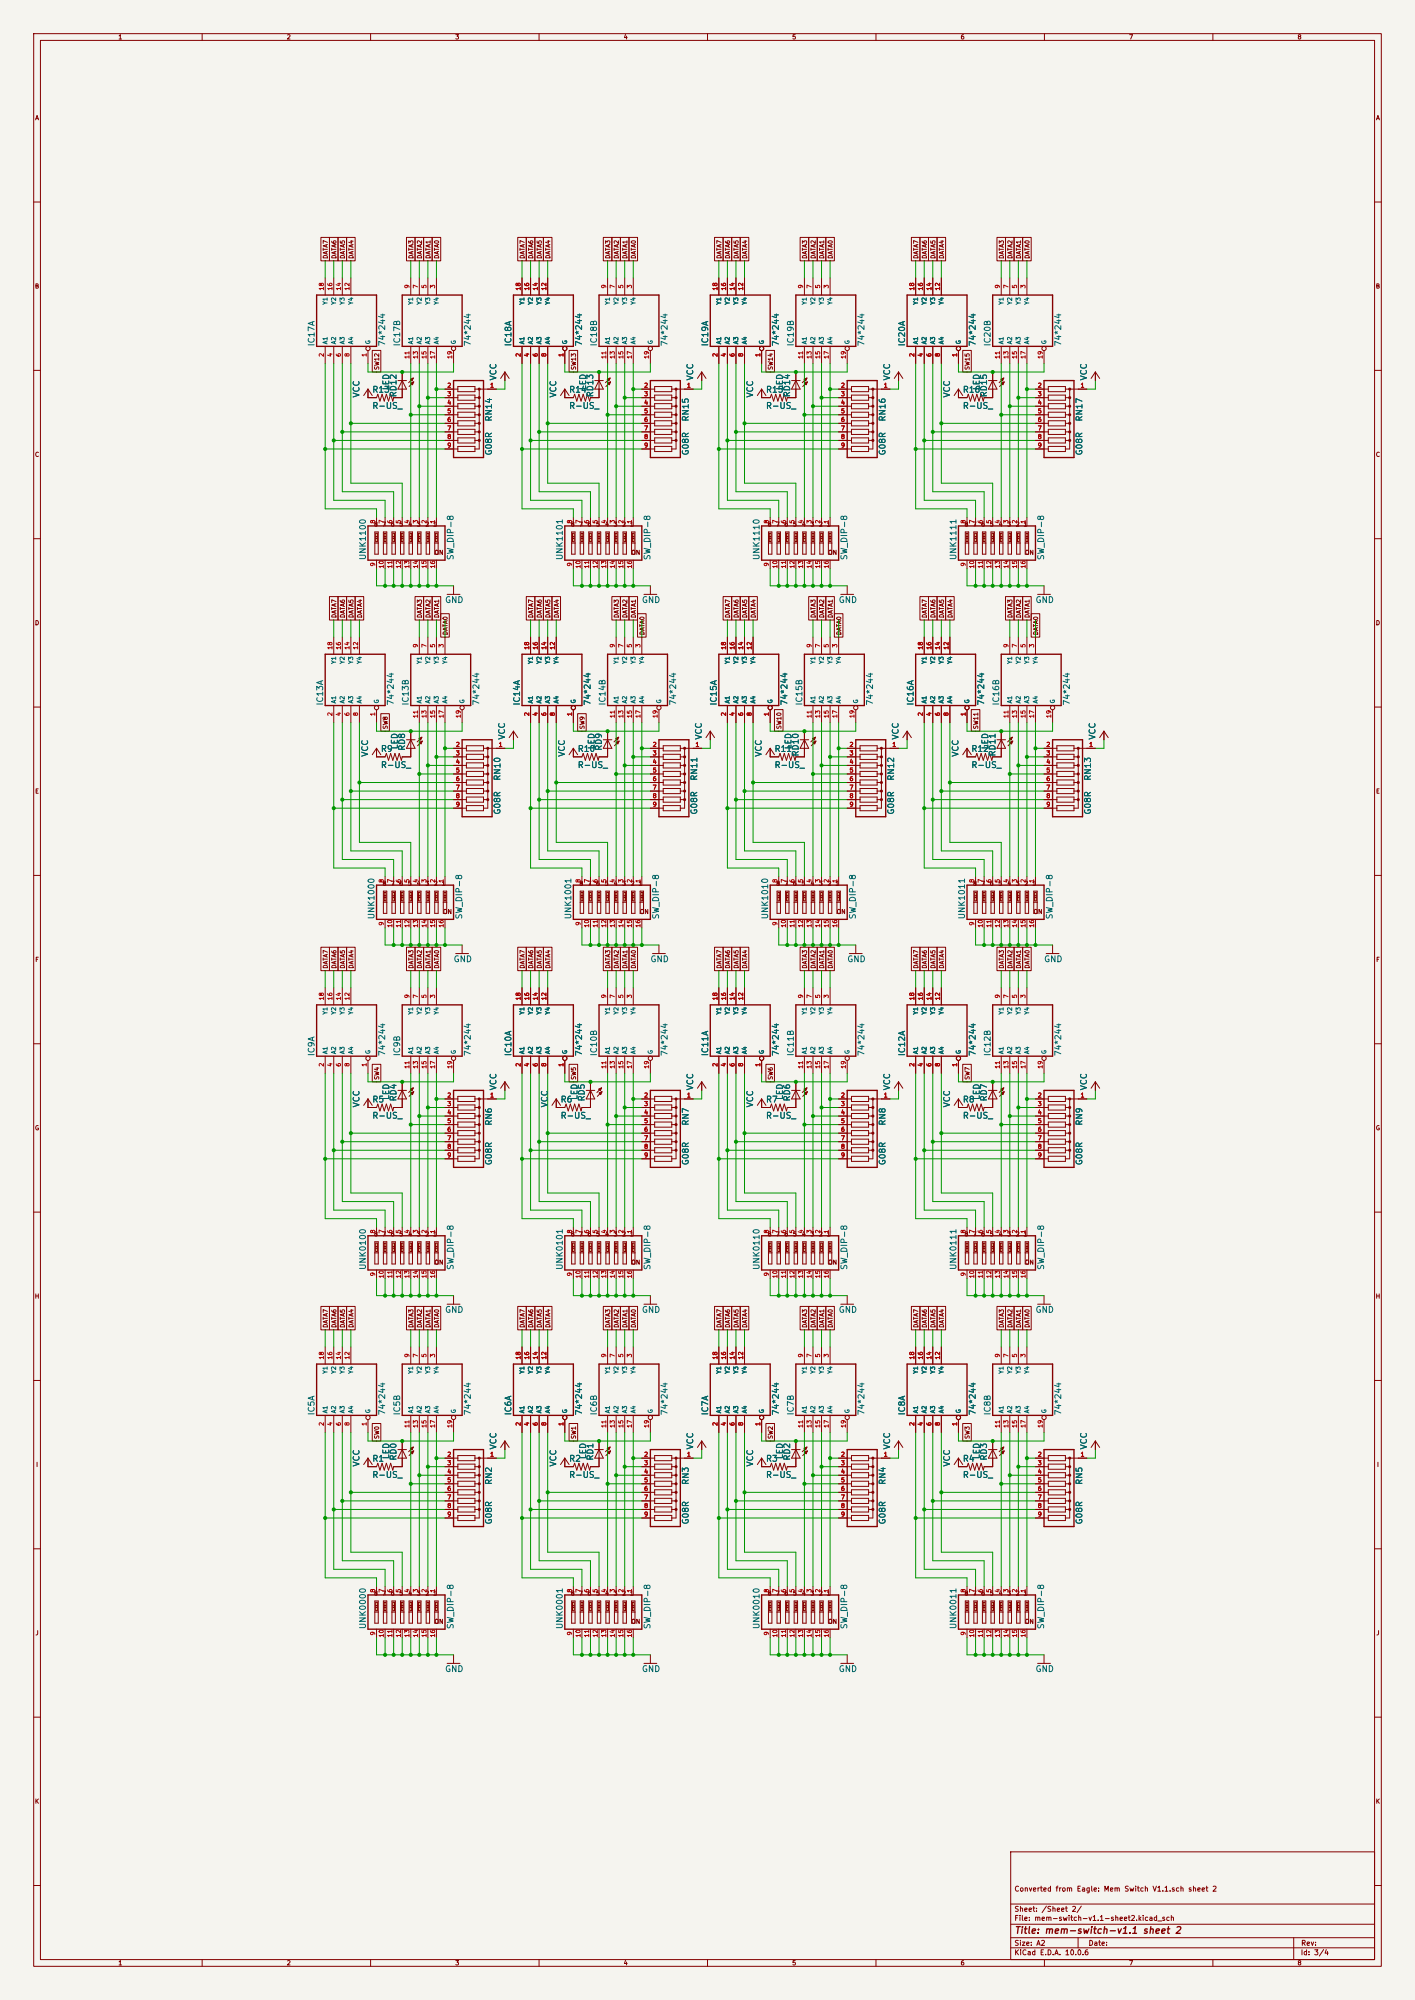
[picture p144: page 3]

Converted from Eagle: Mem Switch V1.1.sch sheet 2 Y4

Sheet: /Sheet 2/
File: mem-switch-v1.1-sheet2.kicad_sch
Title: mem-switch-v1.1 sheet 2

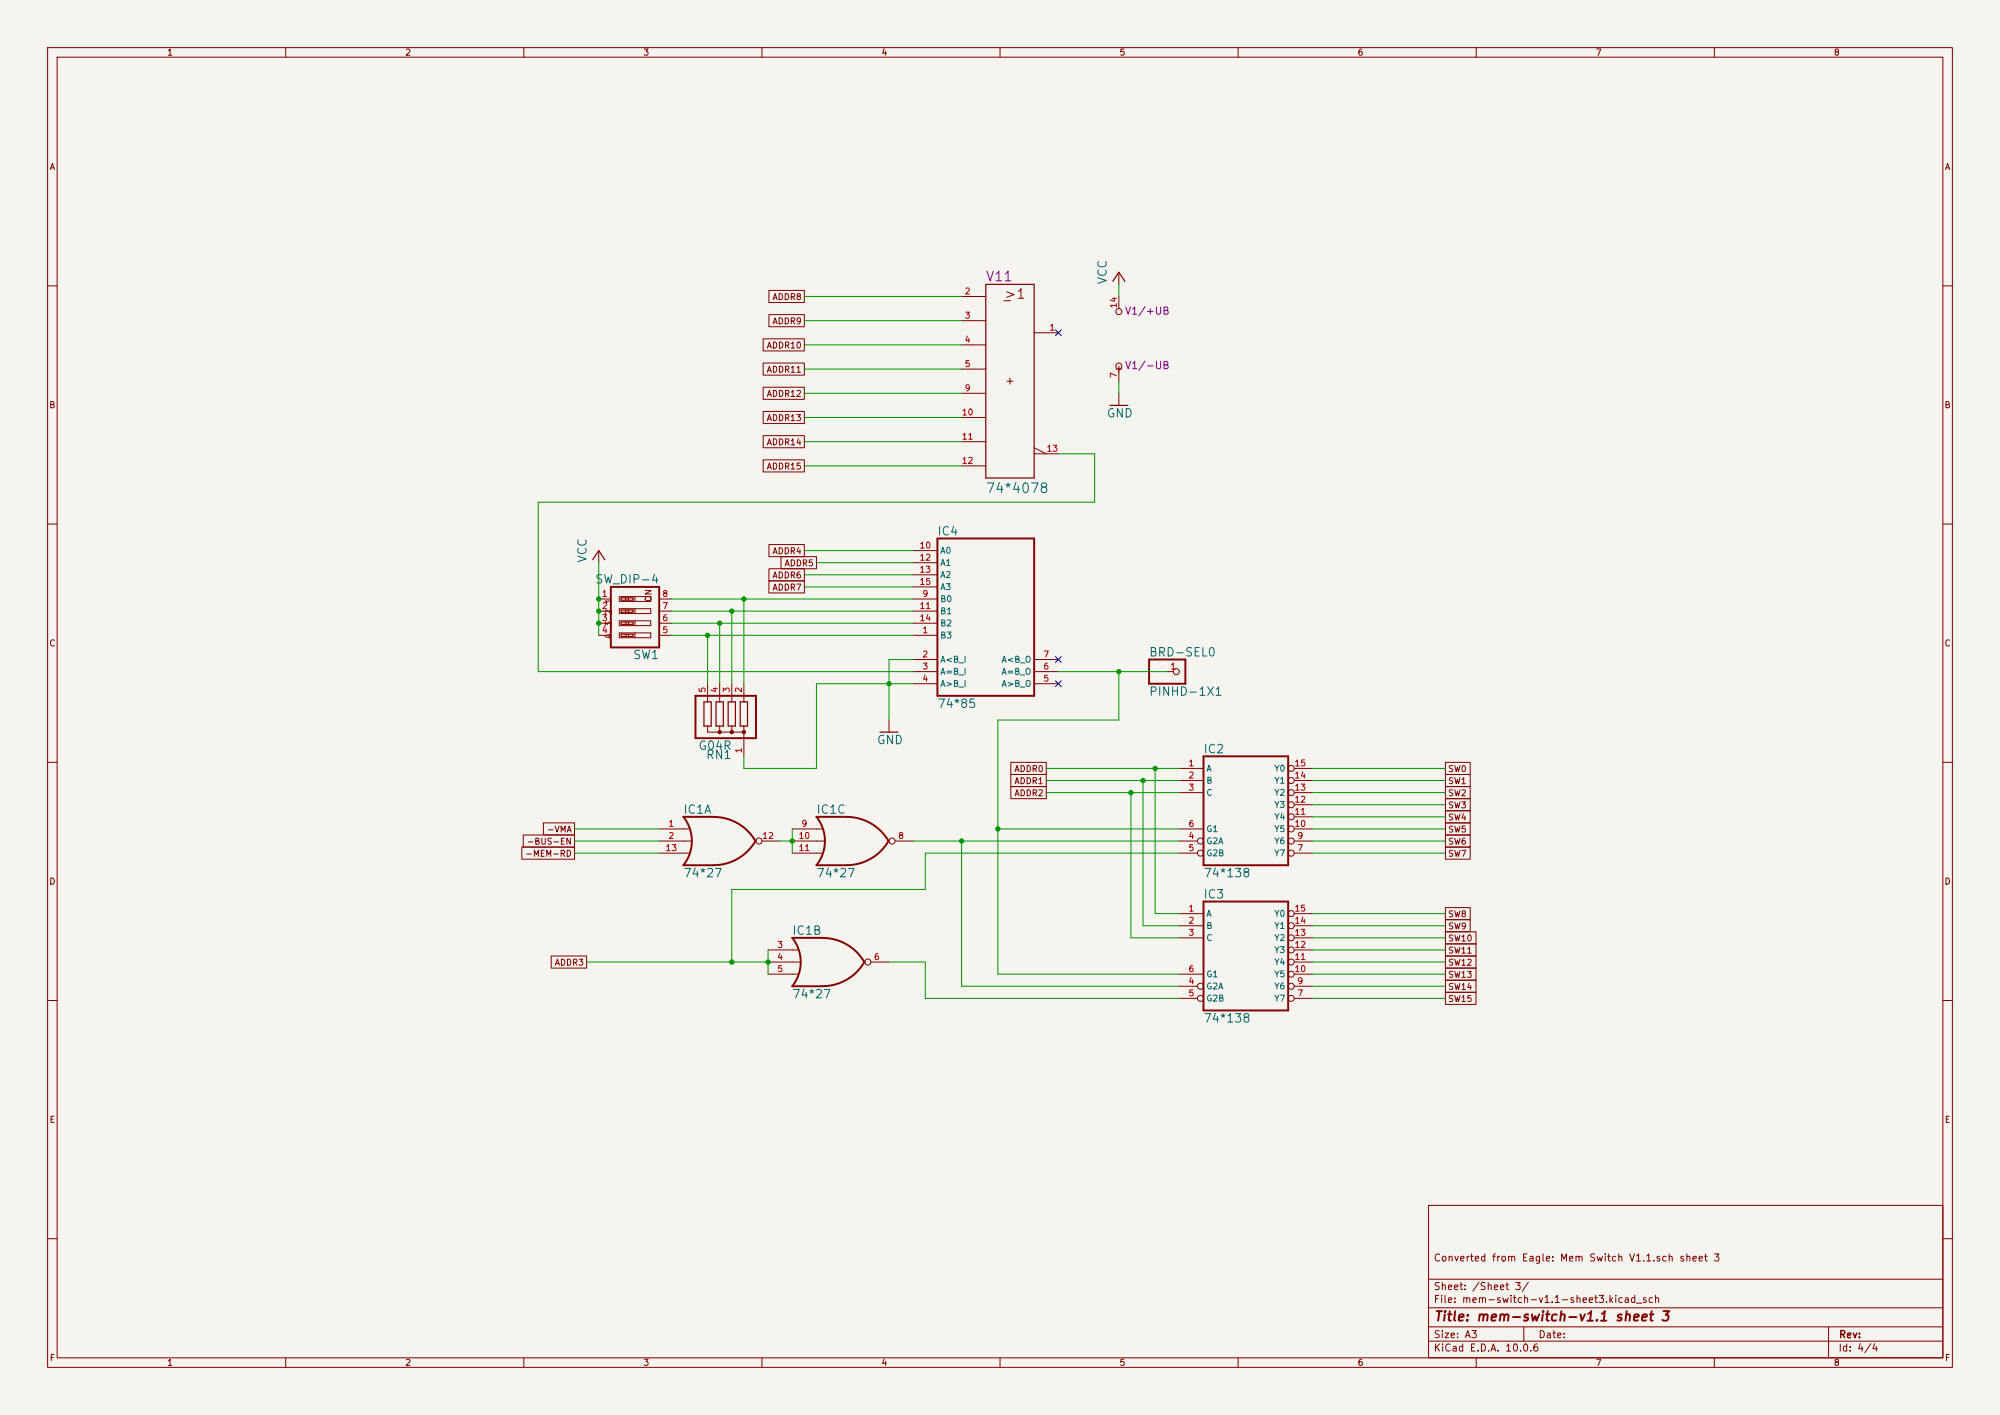
[picture p145: page 4]

Converted from Eagle: Mem Switch V1.1.sch sheet 3

Sheet: /Sheet 3/
File: mem-switch-v1.1-sheet3.kicad_sch
Title: mem-switch-v1.1 sheet 3
