ksr/YACC1-D/hardware/cards/protocard/kicad/v1.0/reports/protocard-v1.0-schematic.pdf

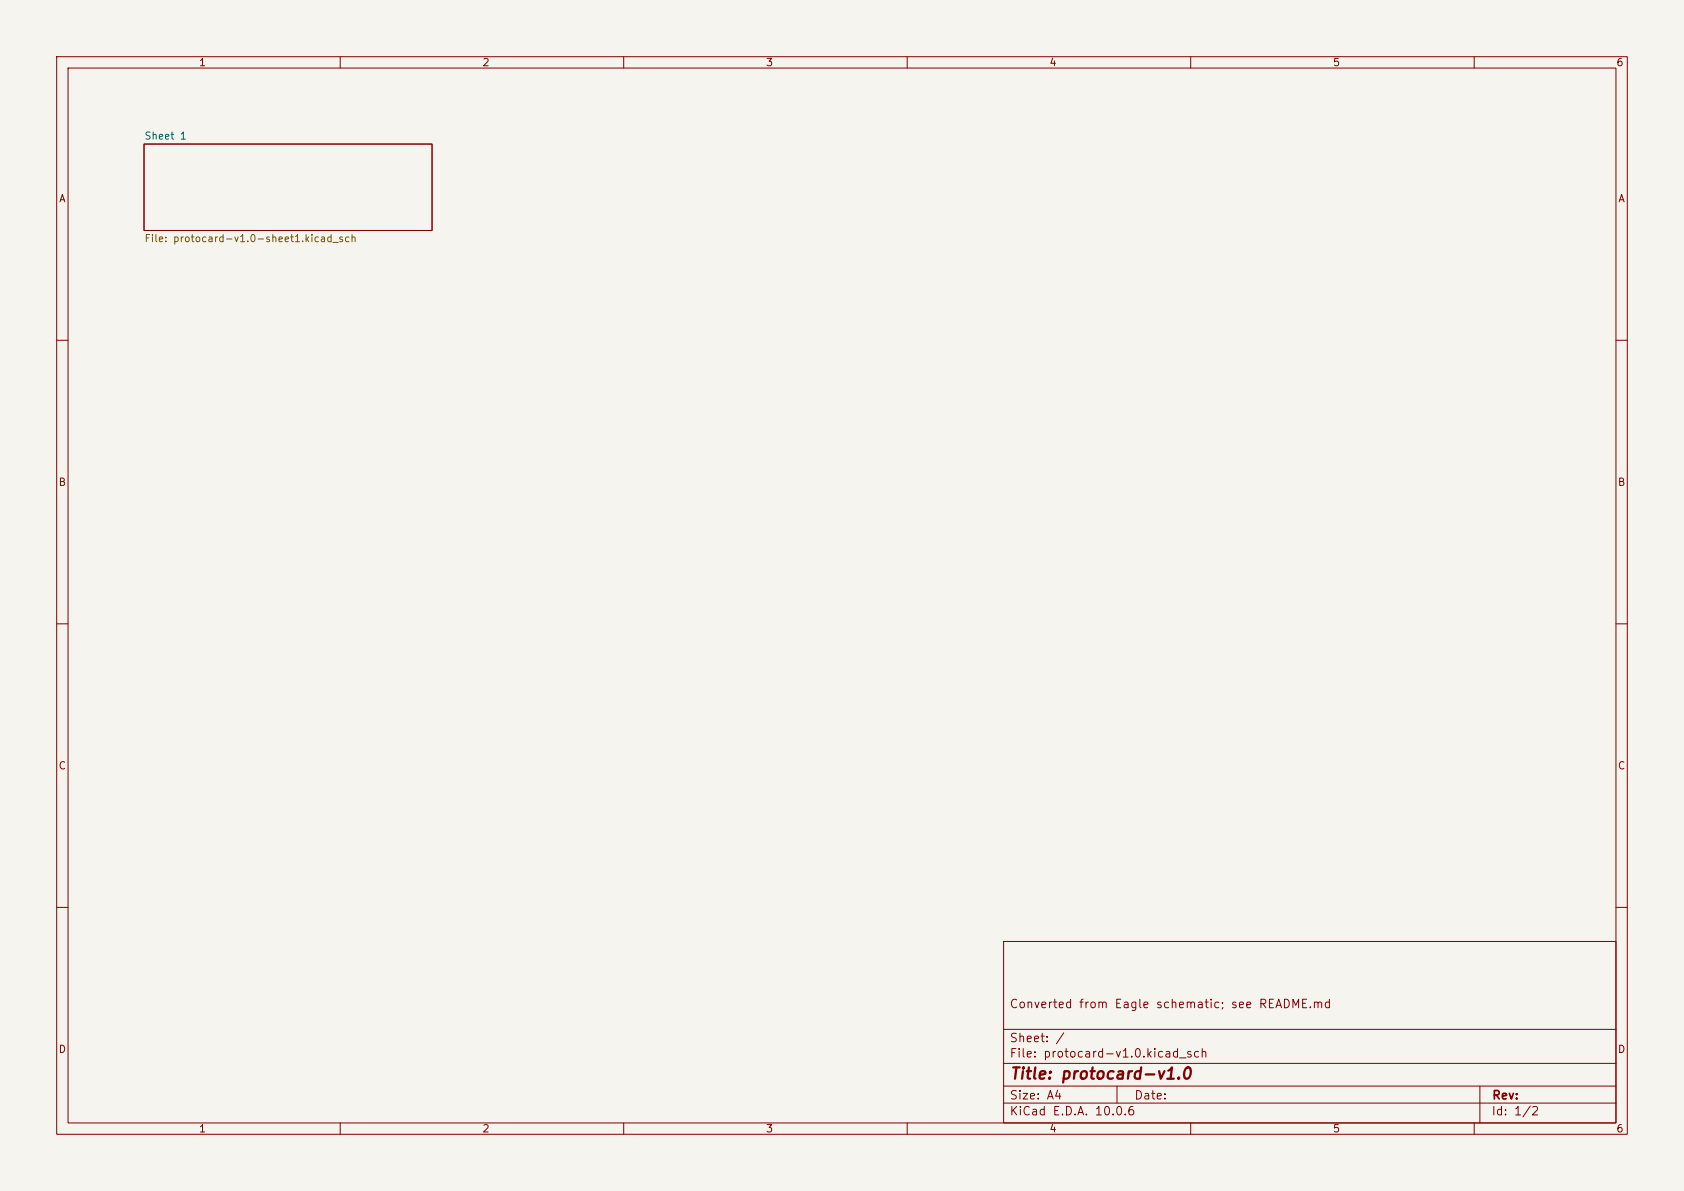
[picture p148: page 1]

Converted from Eagle schematic; see README.md

Size: A4 | Rev:
KiCad E.D.A. 10.0.6 | Id: 1/2

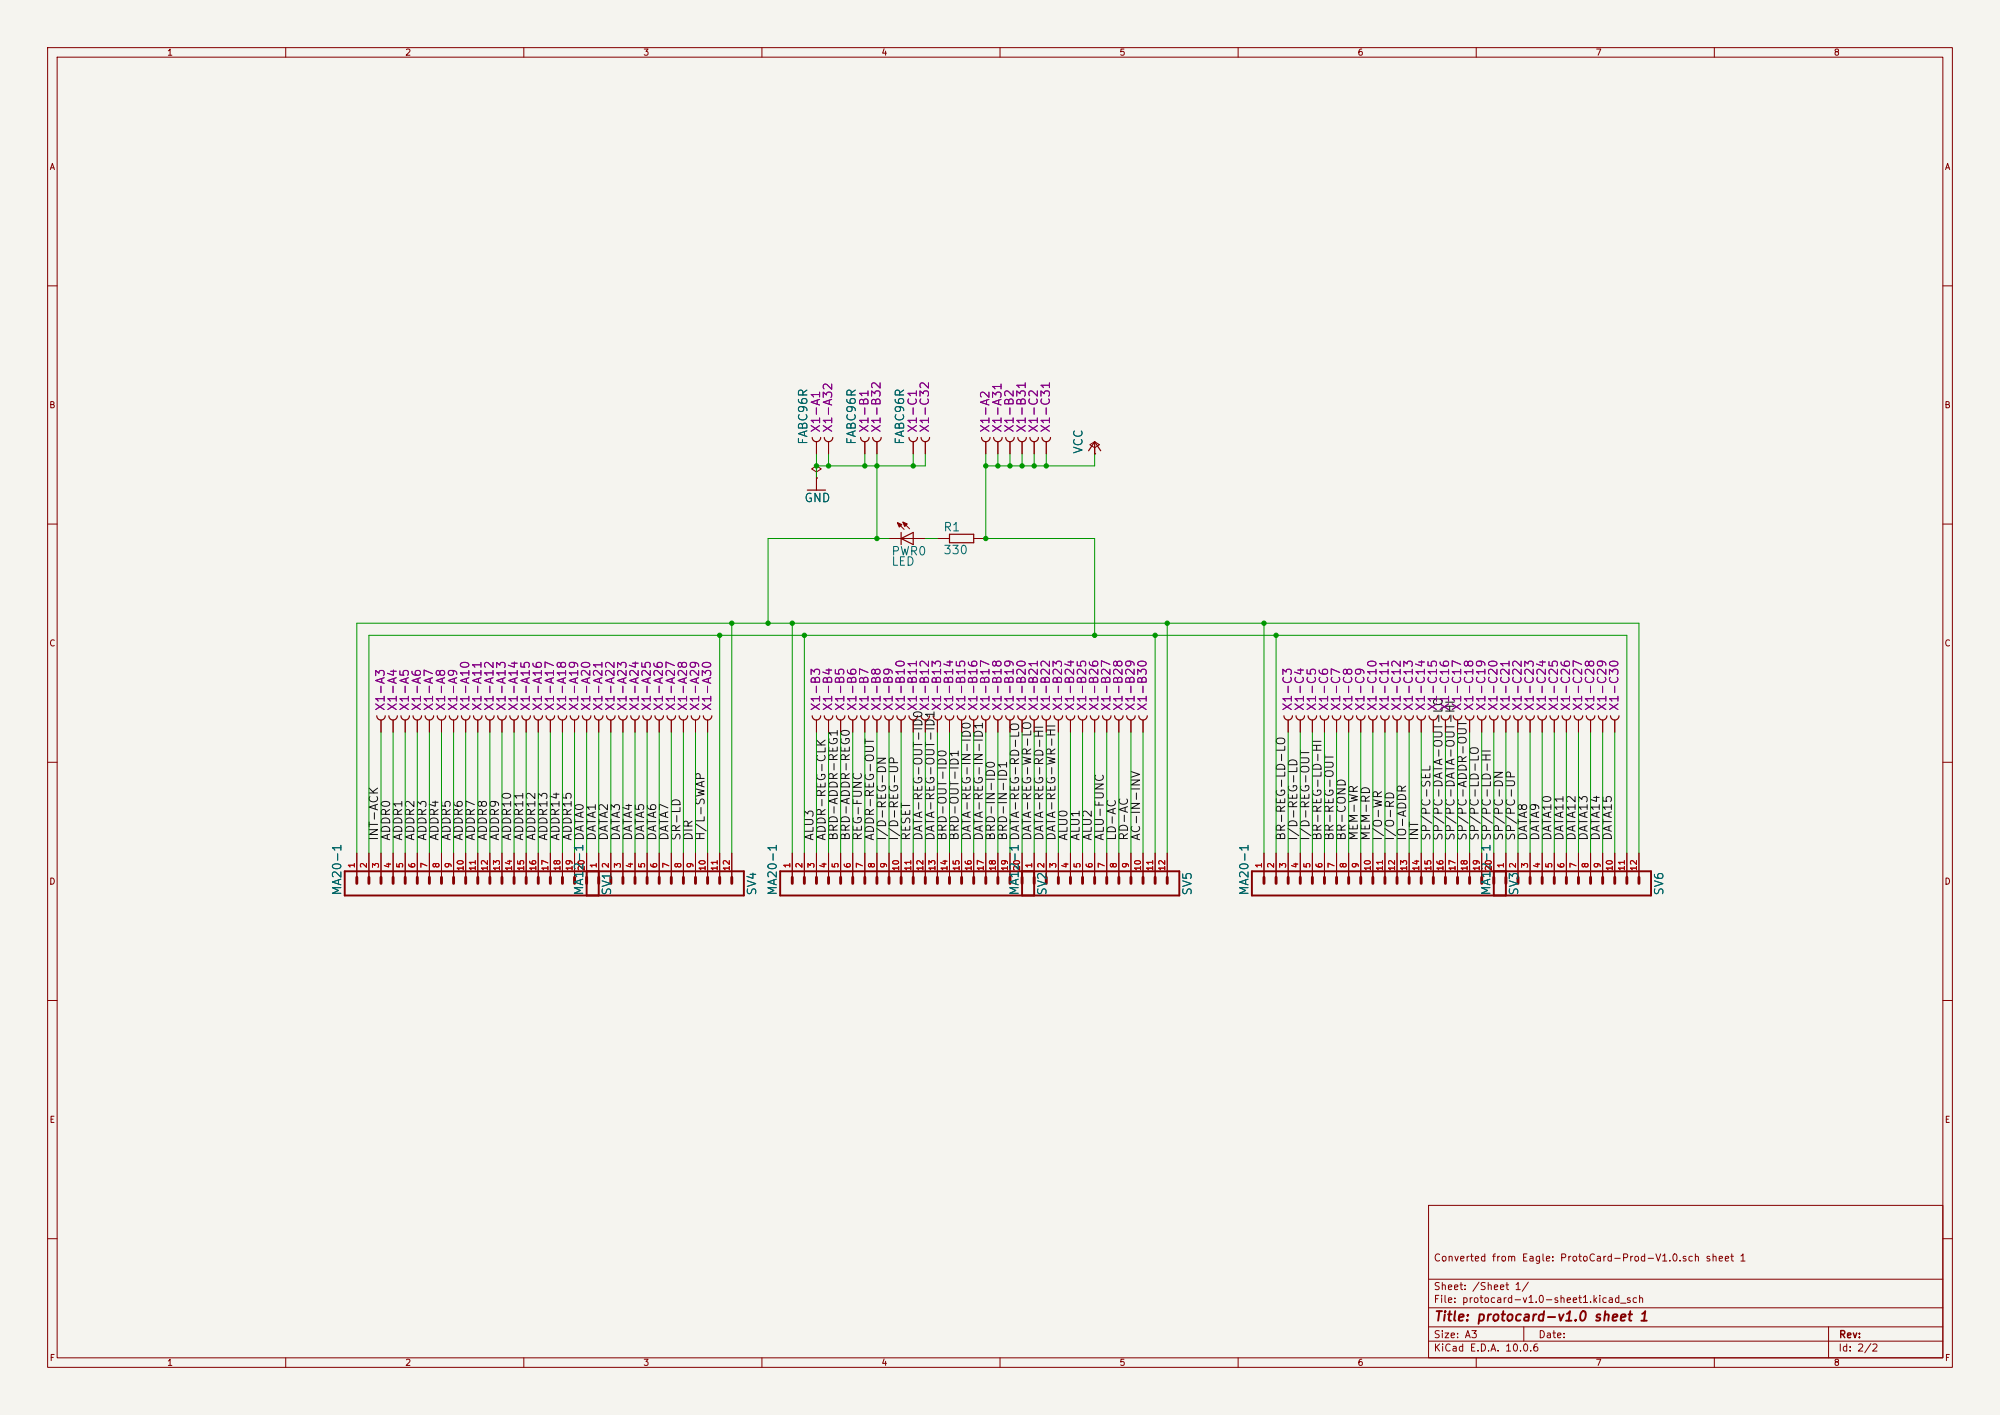
[picture p149: page 2]

91011121314151617181920 MA20-1 SV2 INT-ACK ADDR0 ADDR1 ADDR2 ADDR3 ADDR4 ADDR5 ADDR6 ADDR7 ADDR8 ADDR9 ADDR10 ADDR11 ADDR12 ADDR13 ADDR14 ADDR15 DATA0 DATA1 DATA2 DATA3 DATA4 DATA5 DATA6 DATA7 SR-LD DIR H/L-SWAP ALU3 ADDR-REG-CLK BRD-ADDR-REG1 BRD-ADDR-REG0 REG-FUNC ADDR-REG-OUT I/D-REG-DN I/D-REG-UP RESET DATA-REG-OUT-ID0 DATA-REG-OUT-ID1 BRD-OUT-ID0 BRD-OUT-ID1 DATA-REG-IN-ID0 DATA-REG-IN-ID1 BRD-IN-ID0 BRD-IN-ID1 DATA-REG-RD-LO DATA-REG-WR-LO DATA-REG-RD-HI DATA-REG-WR-HI ALU0 ALU1 ALU2 ALU-FUNC LD-AC RD-AC AC-IN-INV BR-REG-LD-LO I/D-REG-LD I/D-REG-OUT BR-REG-LD-HI BR-REG-OUT BR-COND MEM-WR MEM-RD I/O-WR I/O-RD IO-ADDR INT SP/PC-SEL SP/PC-DATA-OUT-LO SP/PC-DATA-OUT-HI SP/PC-ADDR-OUT SP/PC-LD-LO SP/PC-LD-HI SP/PC-DN SP/PC-UP DATA8 DATA9 DATA10 DATA11 DATA12 DATA13 DATA14 DATA15 X1-A3 X1-A8 X1-A9 X1-A10 X1-A11 X1-A13 X1-A14 MA20-1 SV1

Converted from Eagle: ProtoCard-Prod-V1.0.sch sheet 1

Size: A3 | Rev: | F Date:
KiCad E.D.A. 10.0.6 | Id: 2/2
