ksr/YACC1-D/hardware/cards/register/eagle/v1.1/pdf/Index Registers - 1.1-schematic.pdf

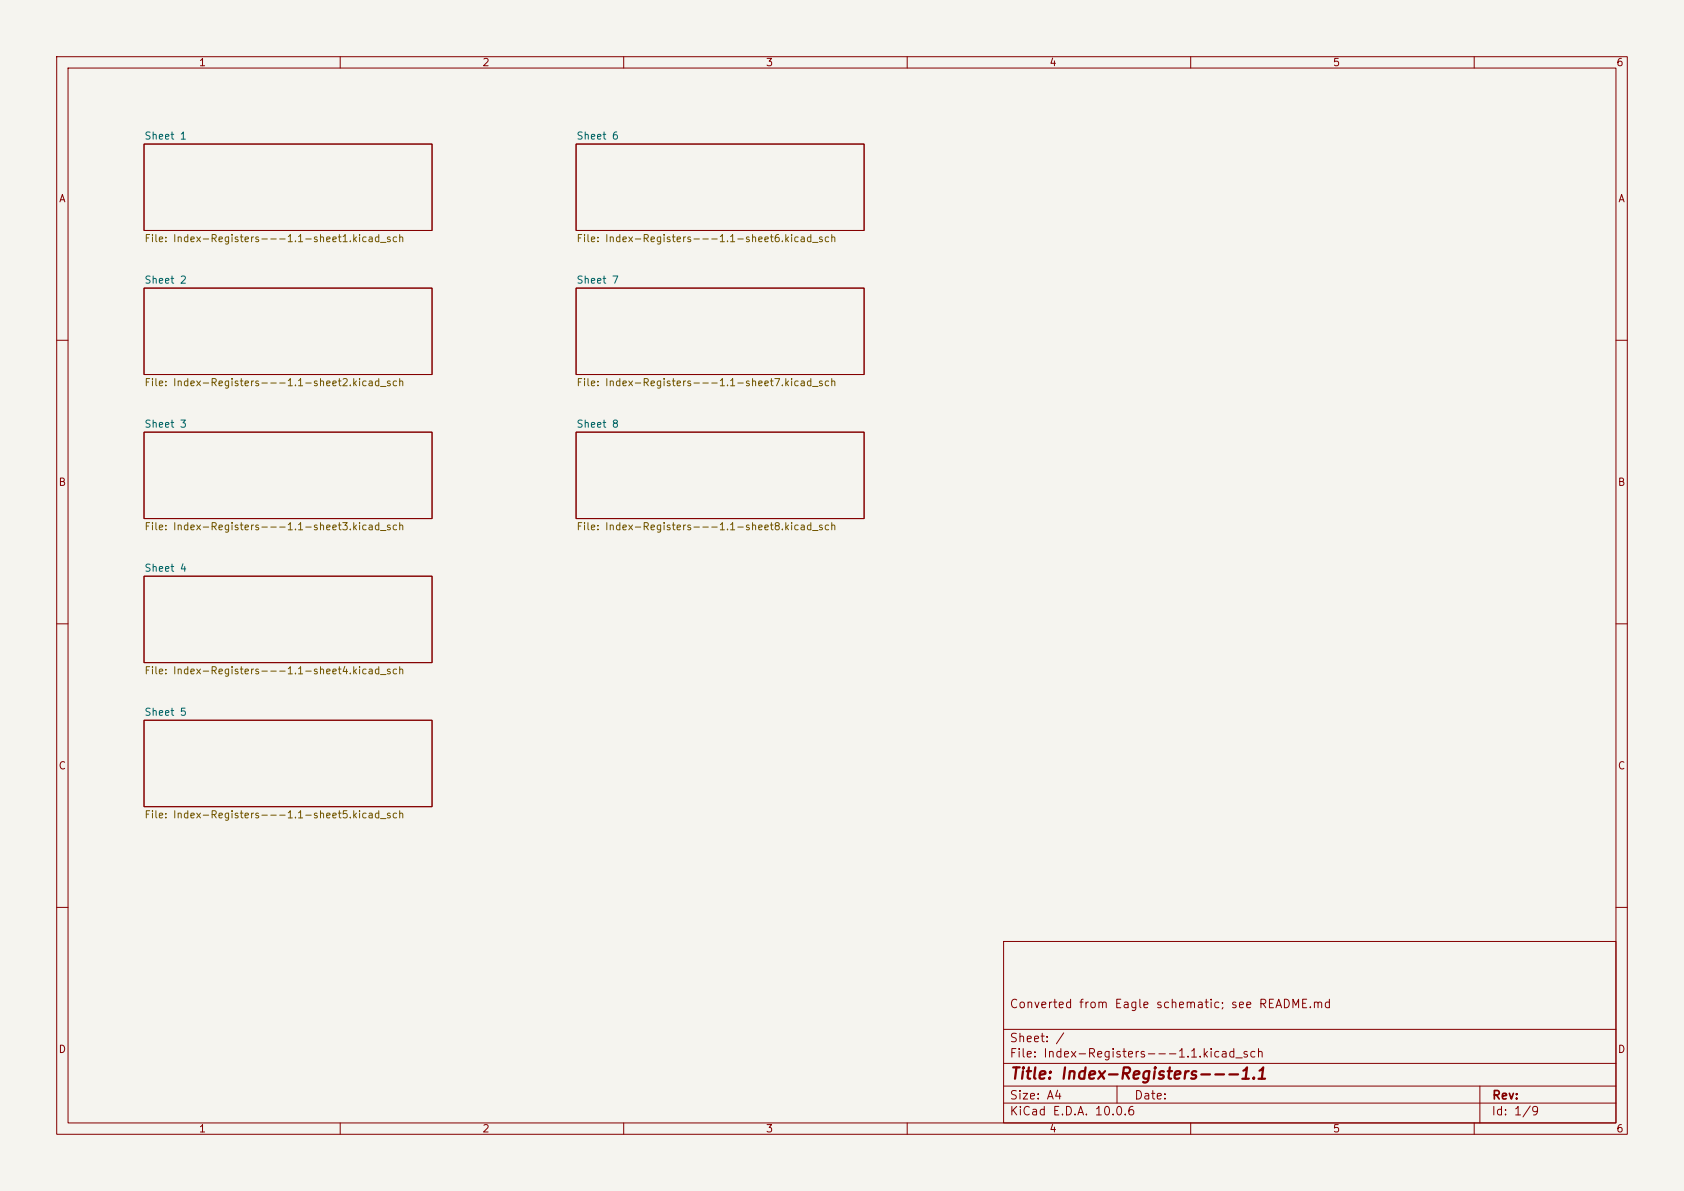
[picture p150: page 1]

File: Index-Registers---1.1-sheet1.kicad_sch Sheet 2

File: Index-Registers---1.1-sheet6.kicad_sch Sheet 7

File: Index-Registers---1.1-sheet2.kicad_sch Sheet 3

File: Index-Registers---1.1-sheet7.kicad_sch Sheet 8

File: Index-Registers---1.1-sheet3.kicad_sch Sheet 4

File: Index-Registers---1.1-sheet4.kicad_sch Sheet 5

Converted from Eagle schematic; see README.md

Size: A4 | Rev:
KiCad E.D.A. 10.0.6 | Id: 1/9

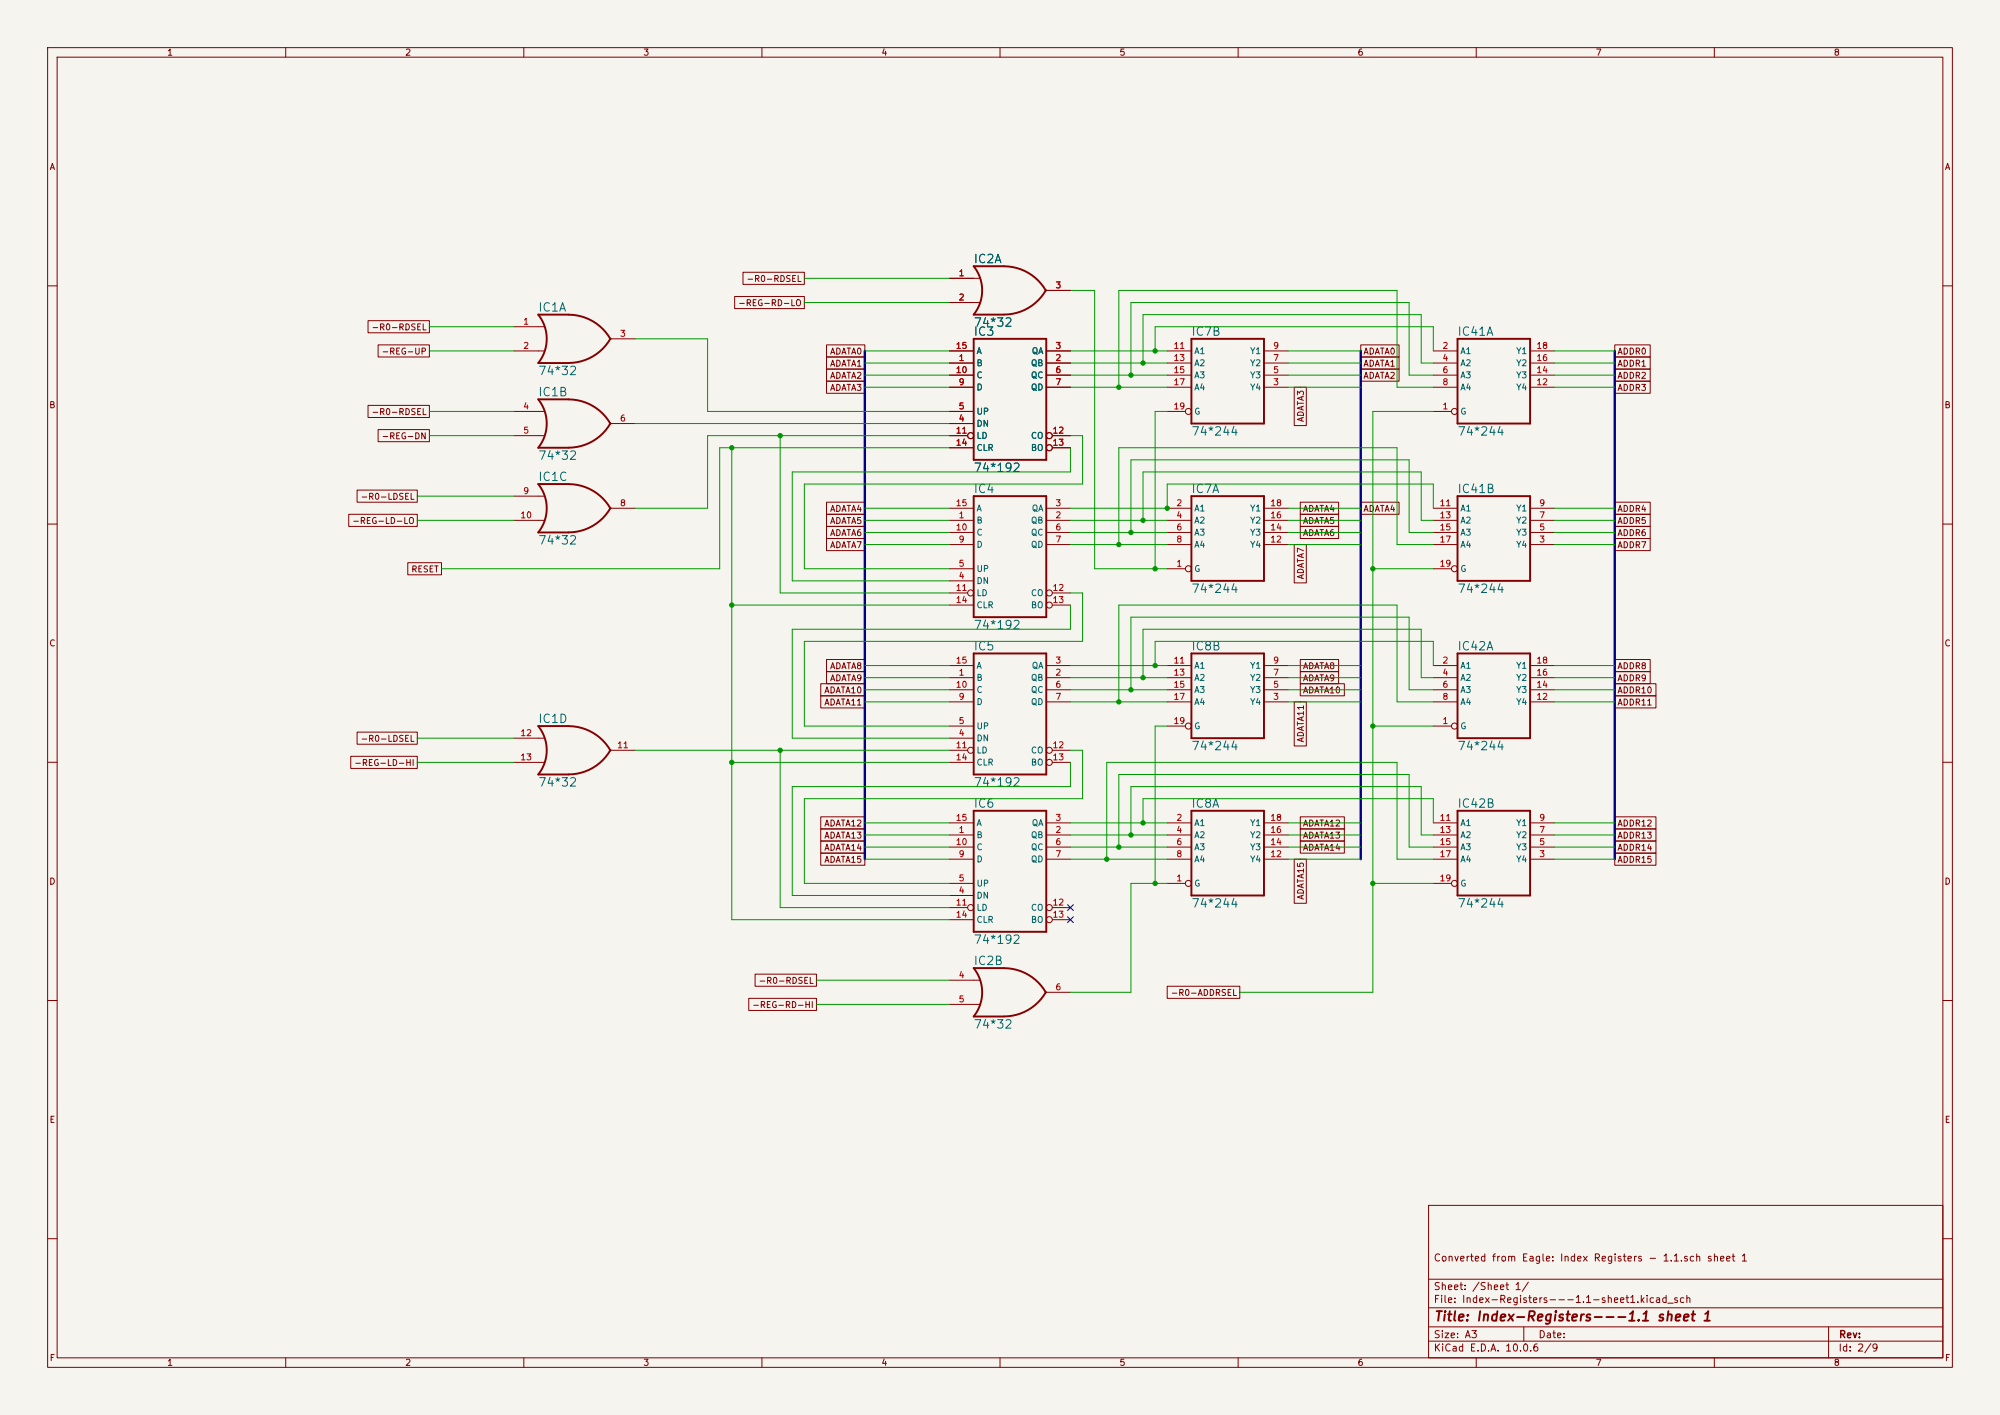
[picture p151: page 2]

Sheet: /Sheet 1/
File: Index-Registers---1.1-sheet1.kicad_sch
Title: Index-Registers---1.1 sheet 1

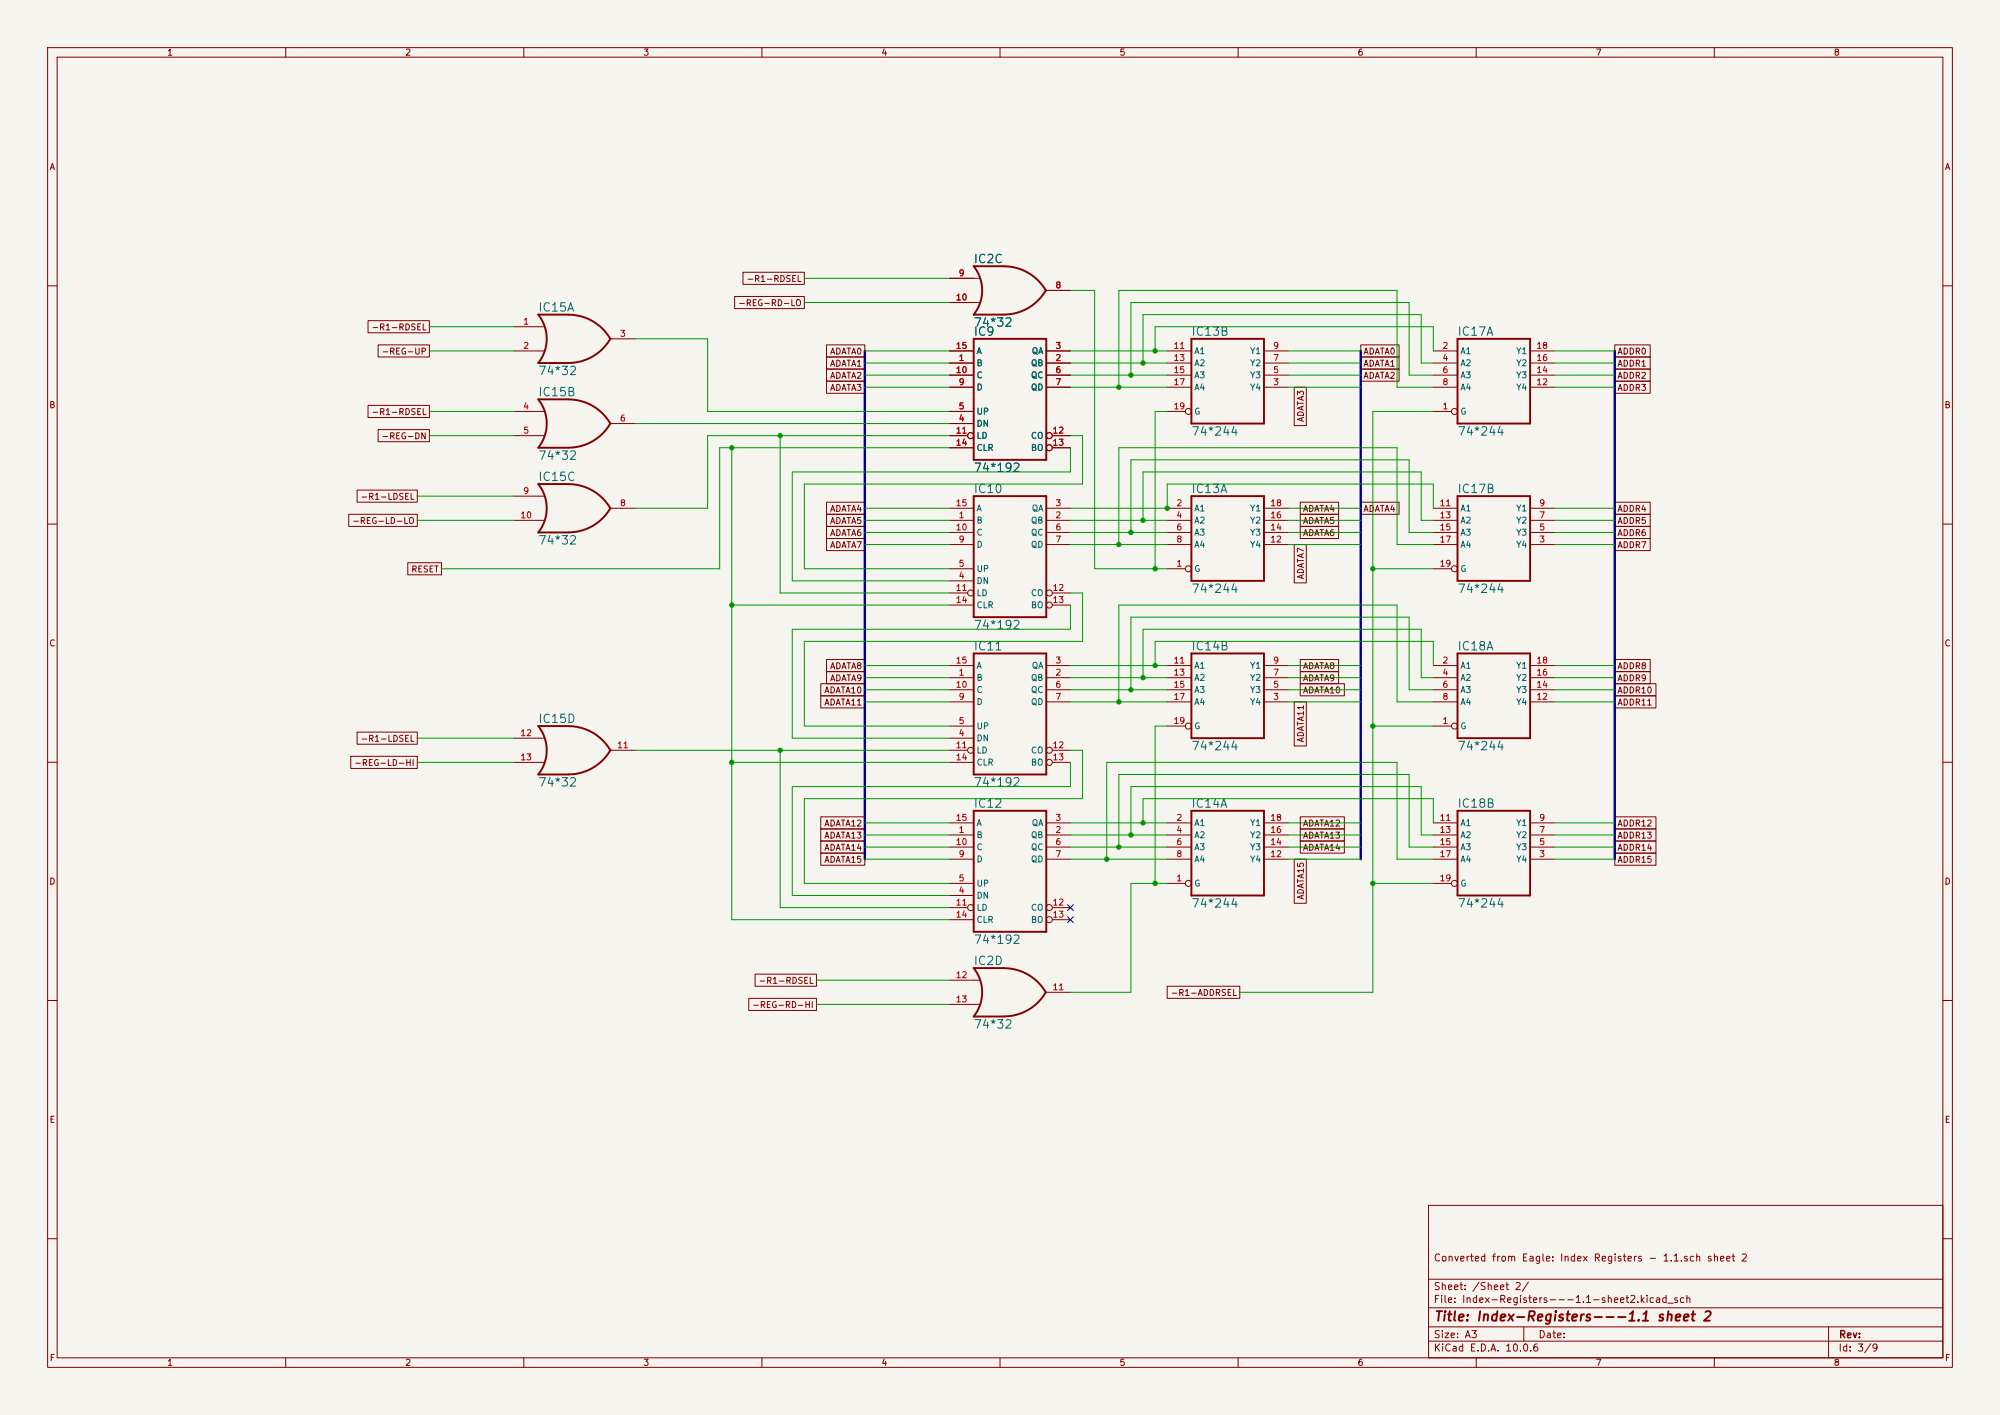
[picture p152: page 3]

ADATA0 -R1-RDSEL -REG-RD-LO

ADDR12 -R1-RDSEL -R1-RDSEL -REG-DN -REG-UP

Converted from Eagle: Index Registers - 1.1.sch sheet 2

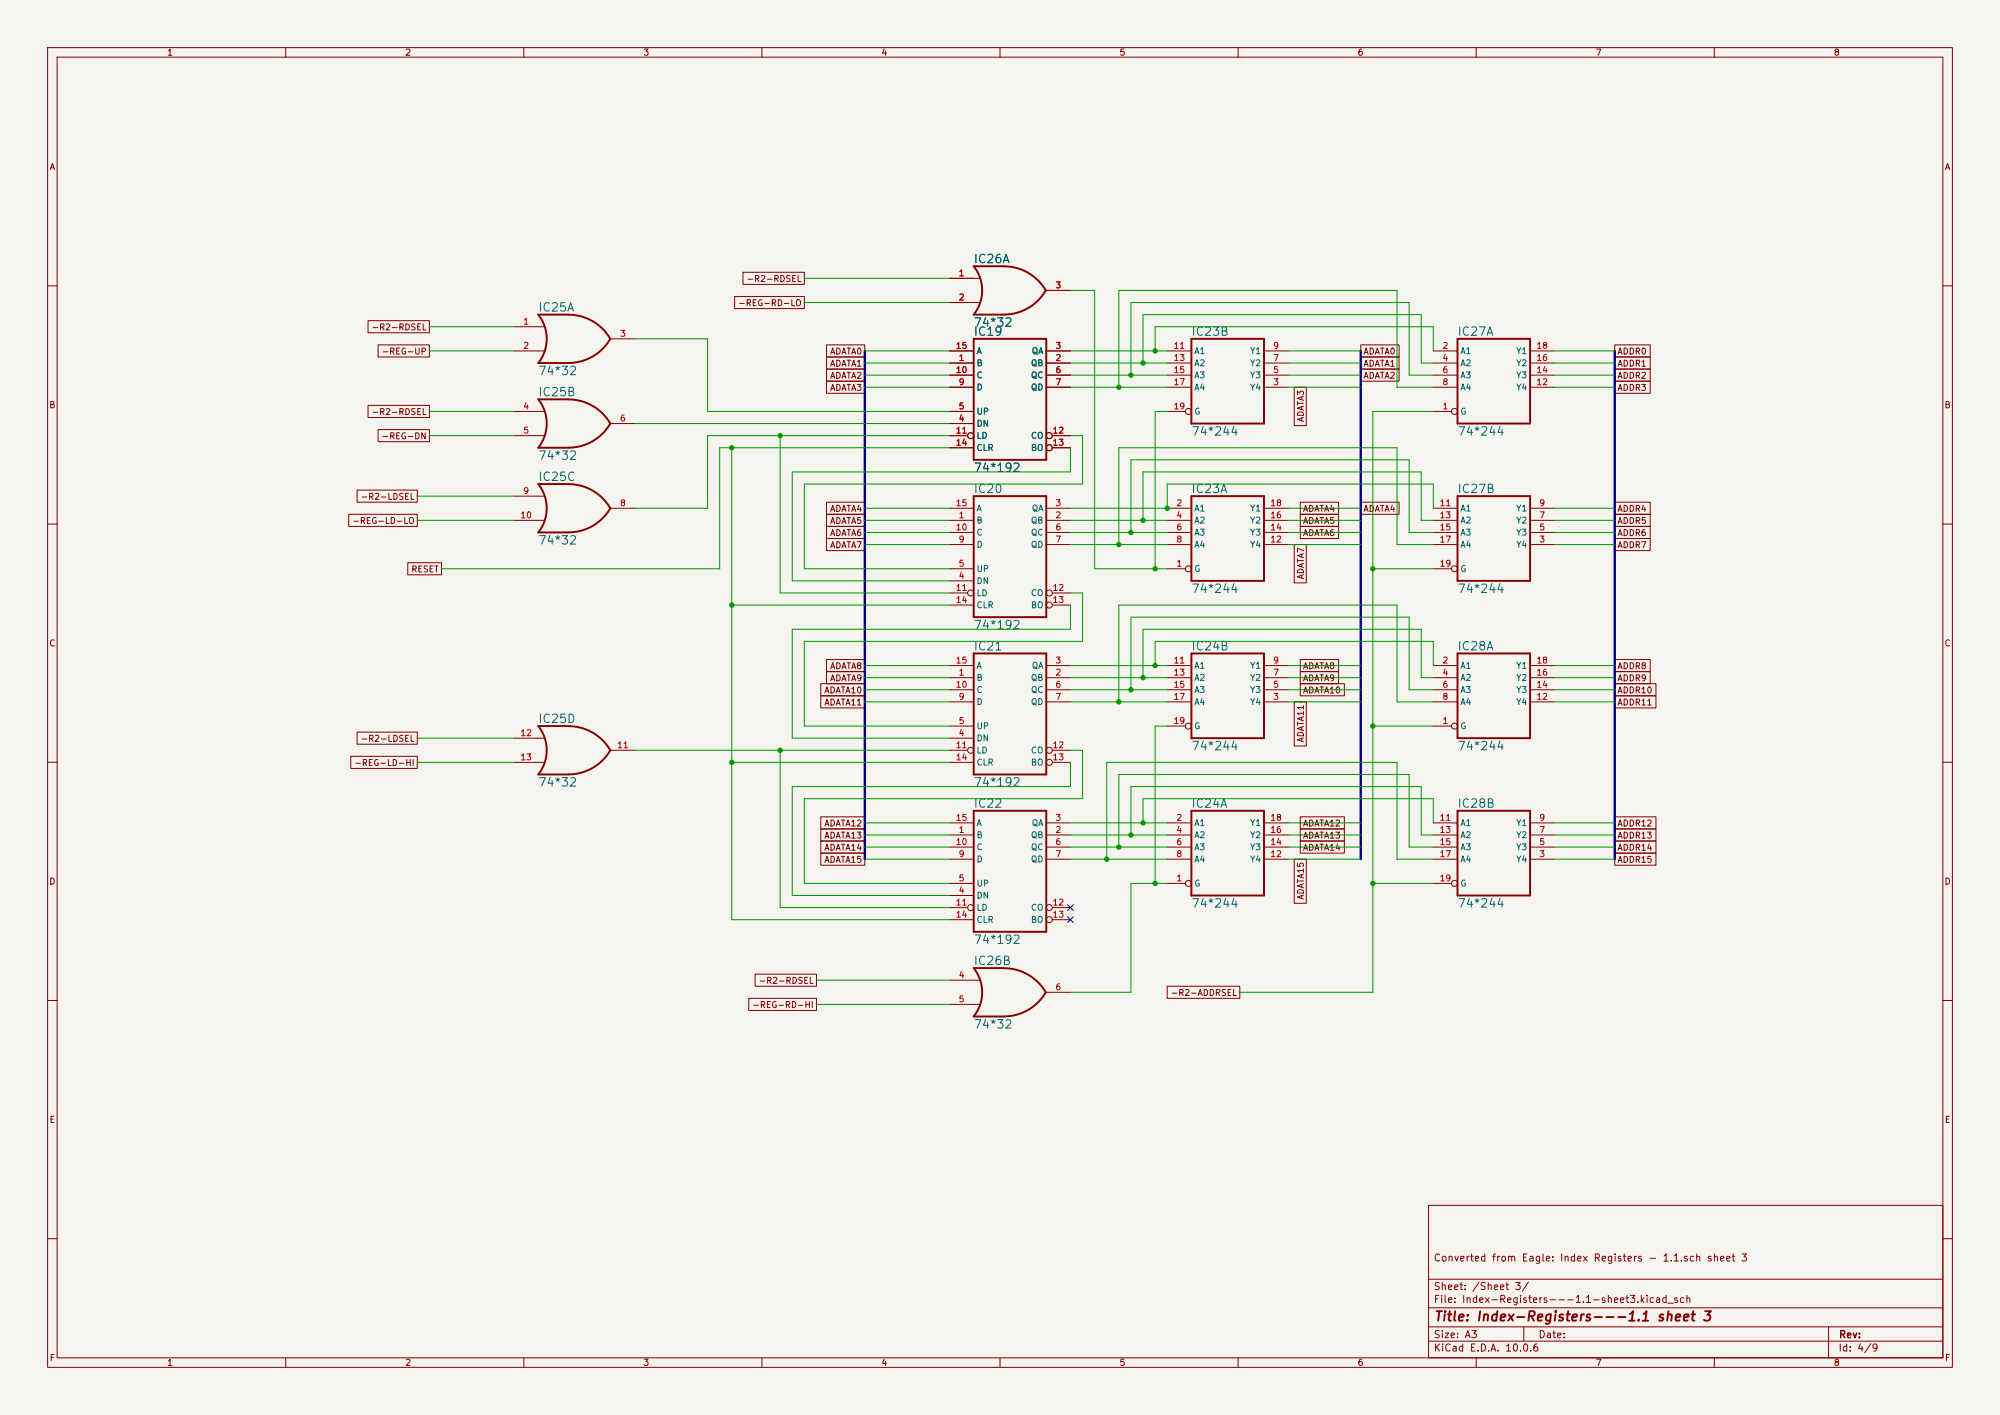
[picture p153: page 4]

Converted from Eagle: Index Registers - 1.1.sch sheet 3 8 9

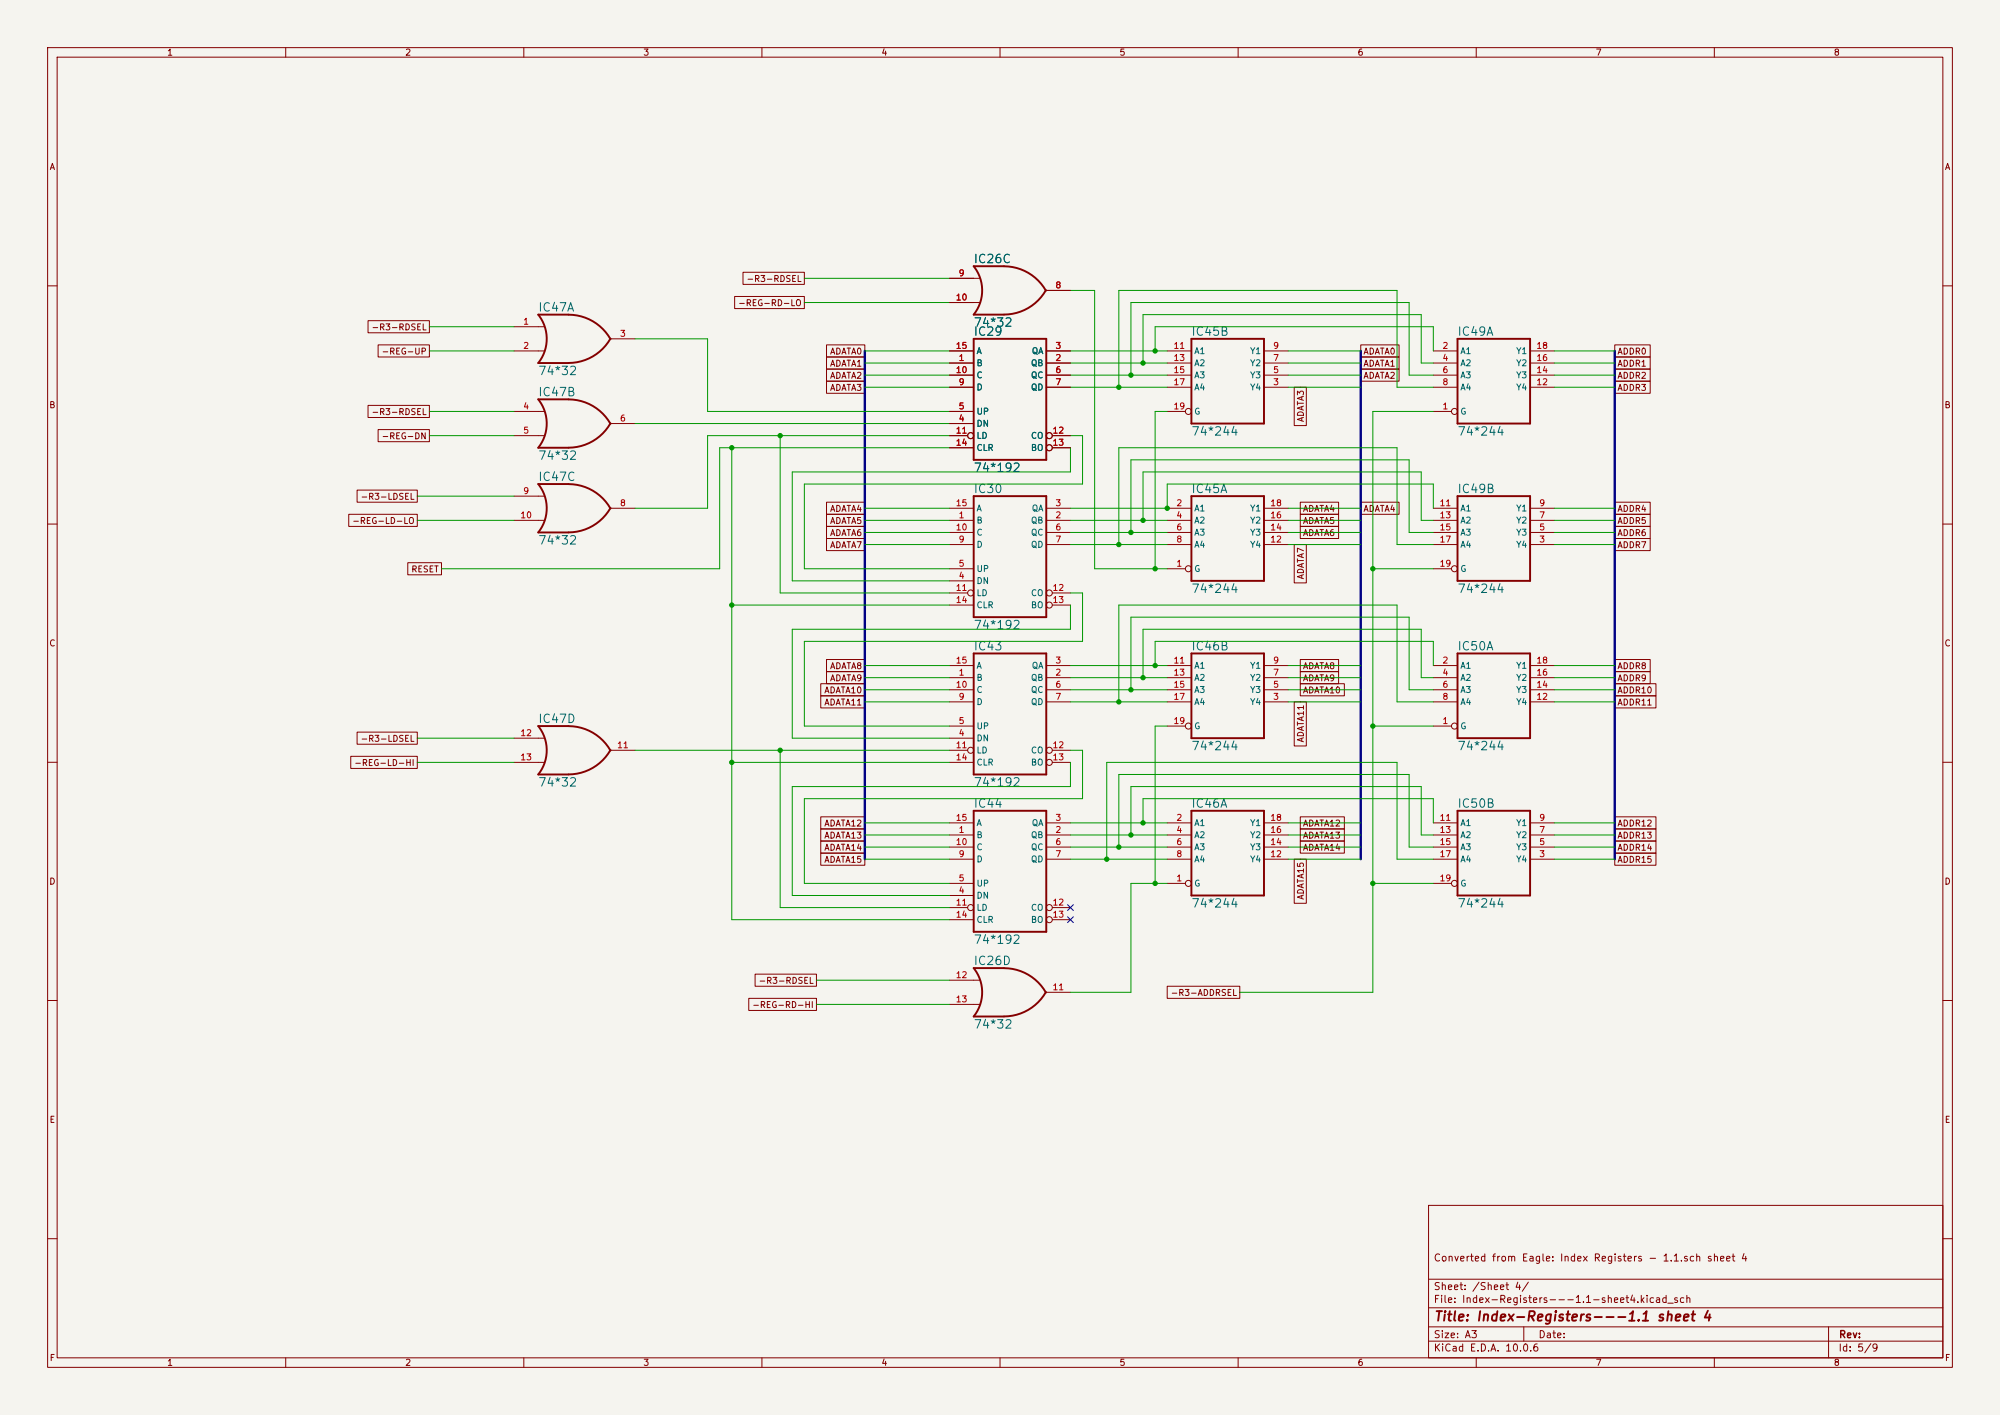
[picture p154: page 5]

ADATA0 -R3-RDSEL -REG-RD-LO

ADDR12 -R3-RDSEL -R3-RDSEL -REG-DN -REG-UP

Converted from Eagle: Index Registers - 1.1.sch sheet 4

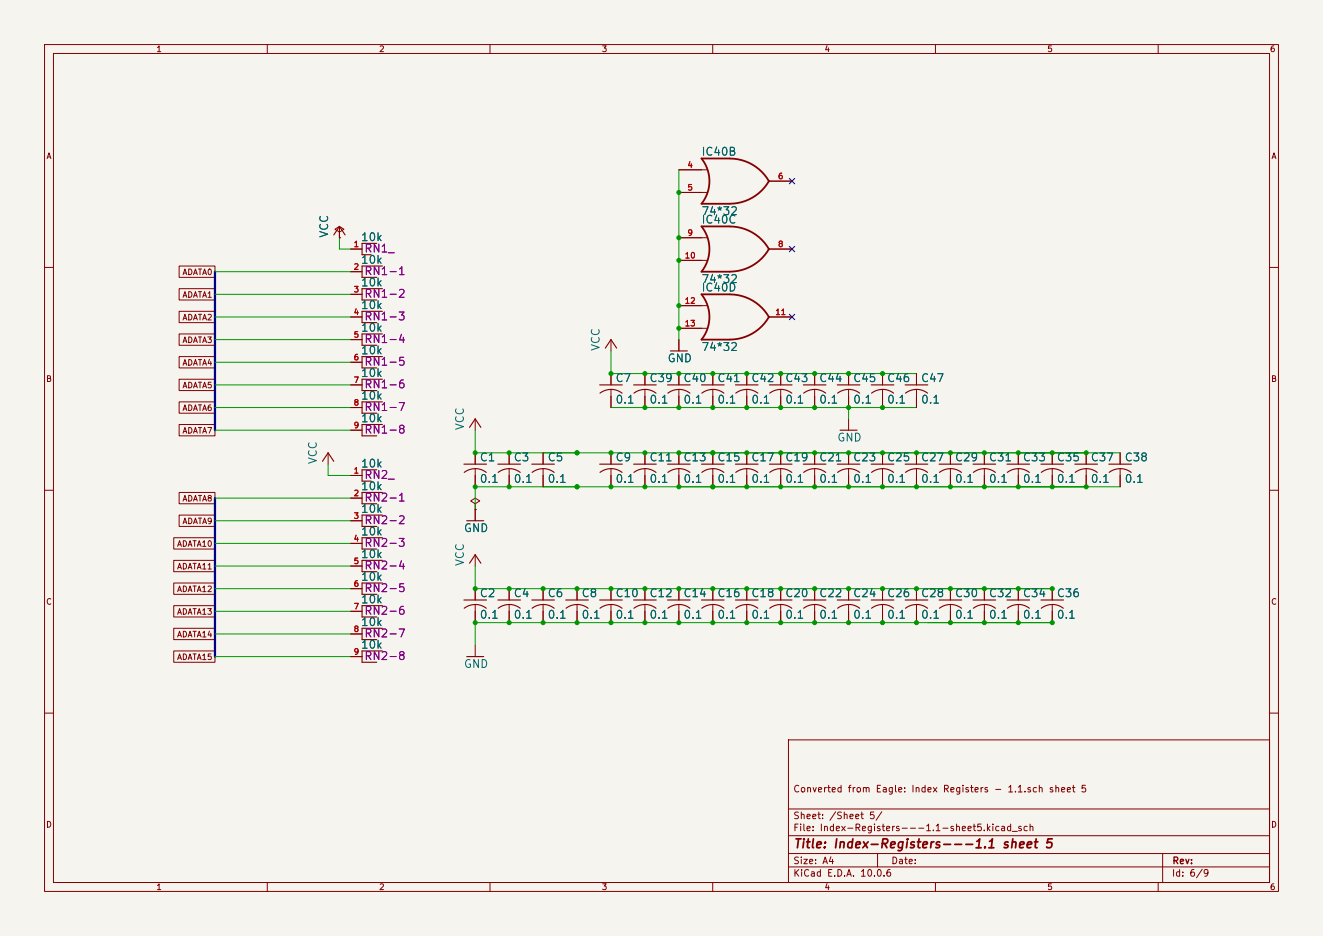
[picture p155: page 6]

Converted from Eagle: Index Registers - 1.1.sch sheet 5

Sheet: /Sheet 5/
File: Index-Registers---1.1-sheet5.kicad_sch
Title: Index-Registers---1.1 sheet 5

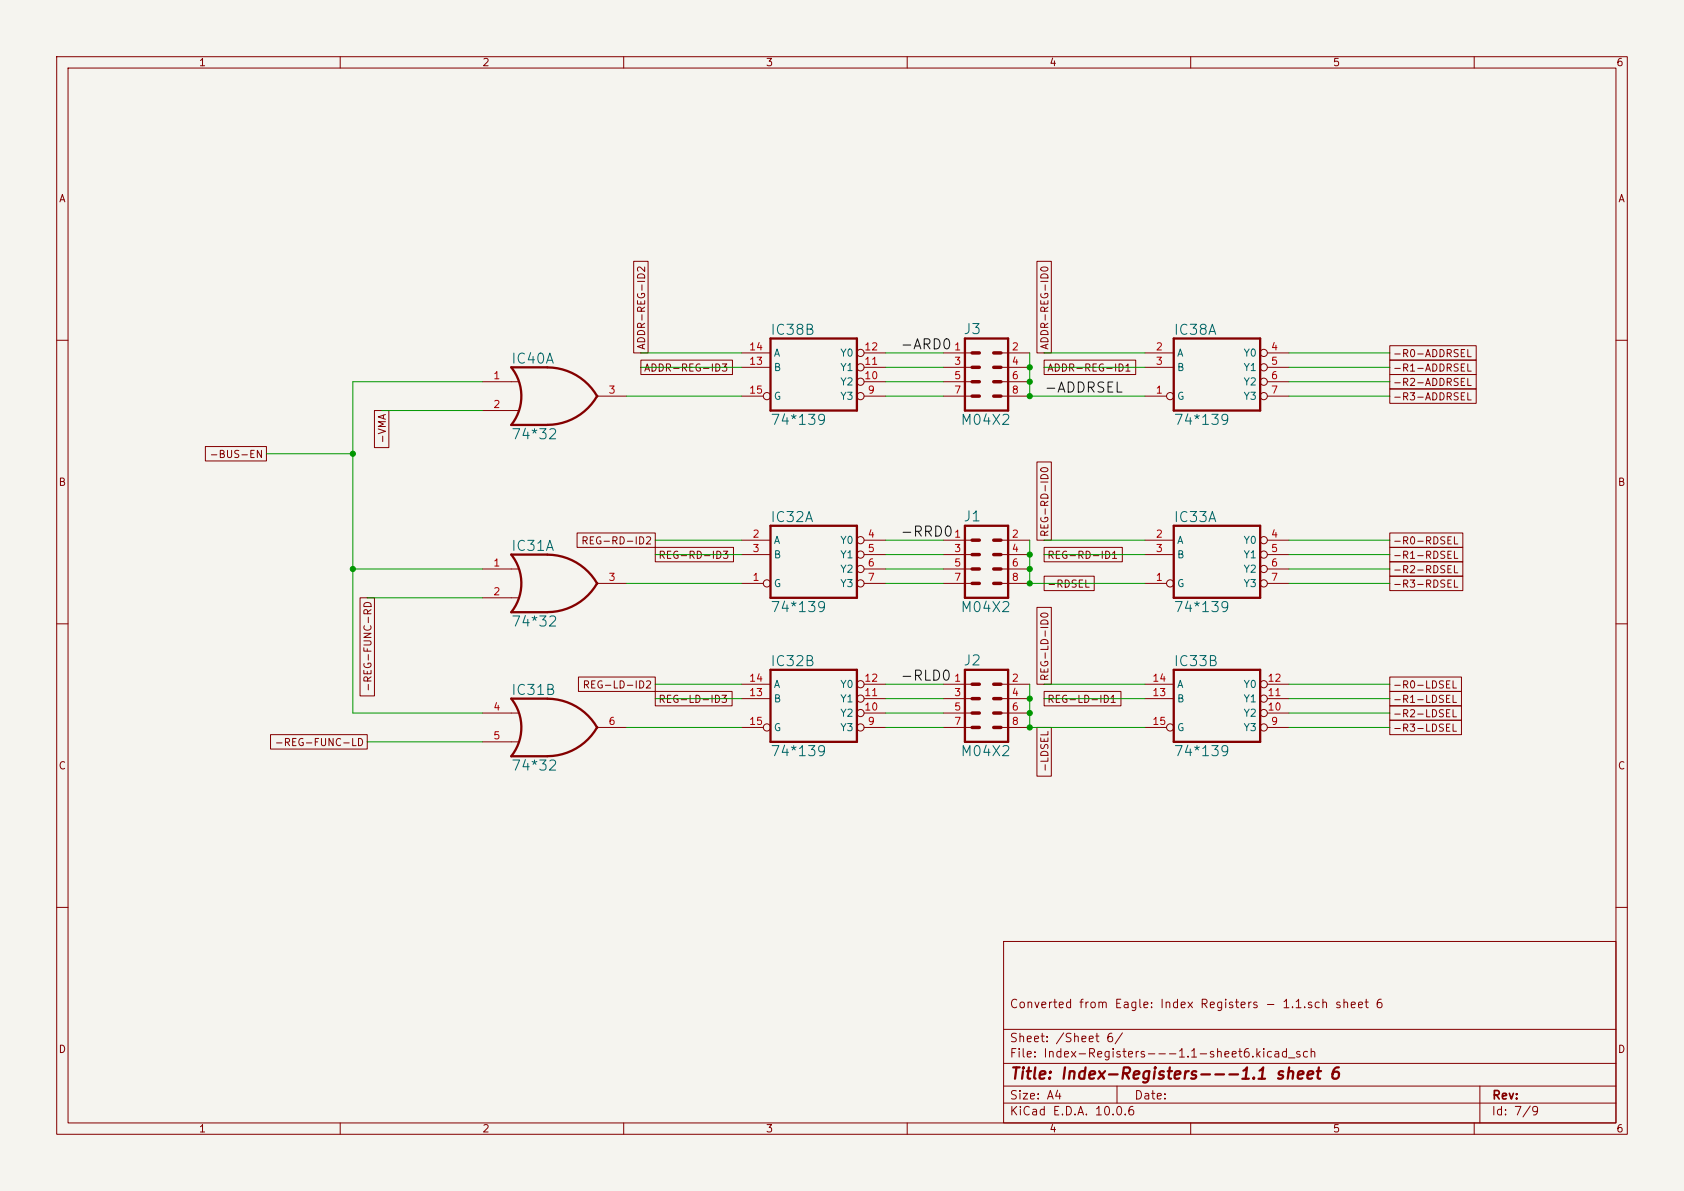
[picture p156: page 7]

Converted from Eagle: Index Registers - 1.1.sch sheet 6

Sheet: /Sheet 6/
File: Index-Registers---1.1-sheet6.kicad_sch
Title: Index-Registers---1.1 sheet 6

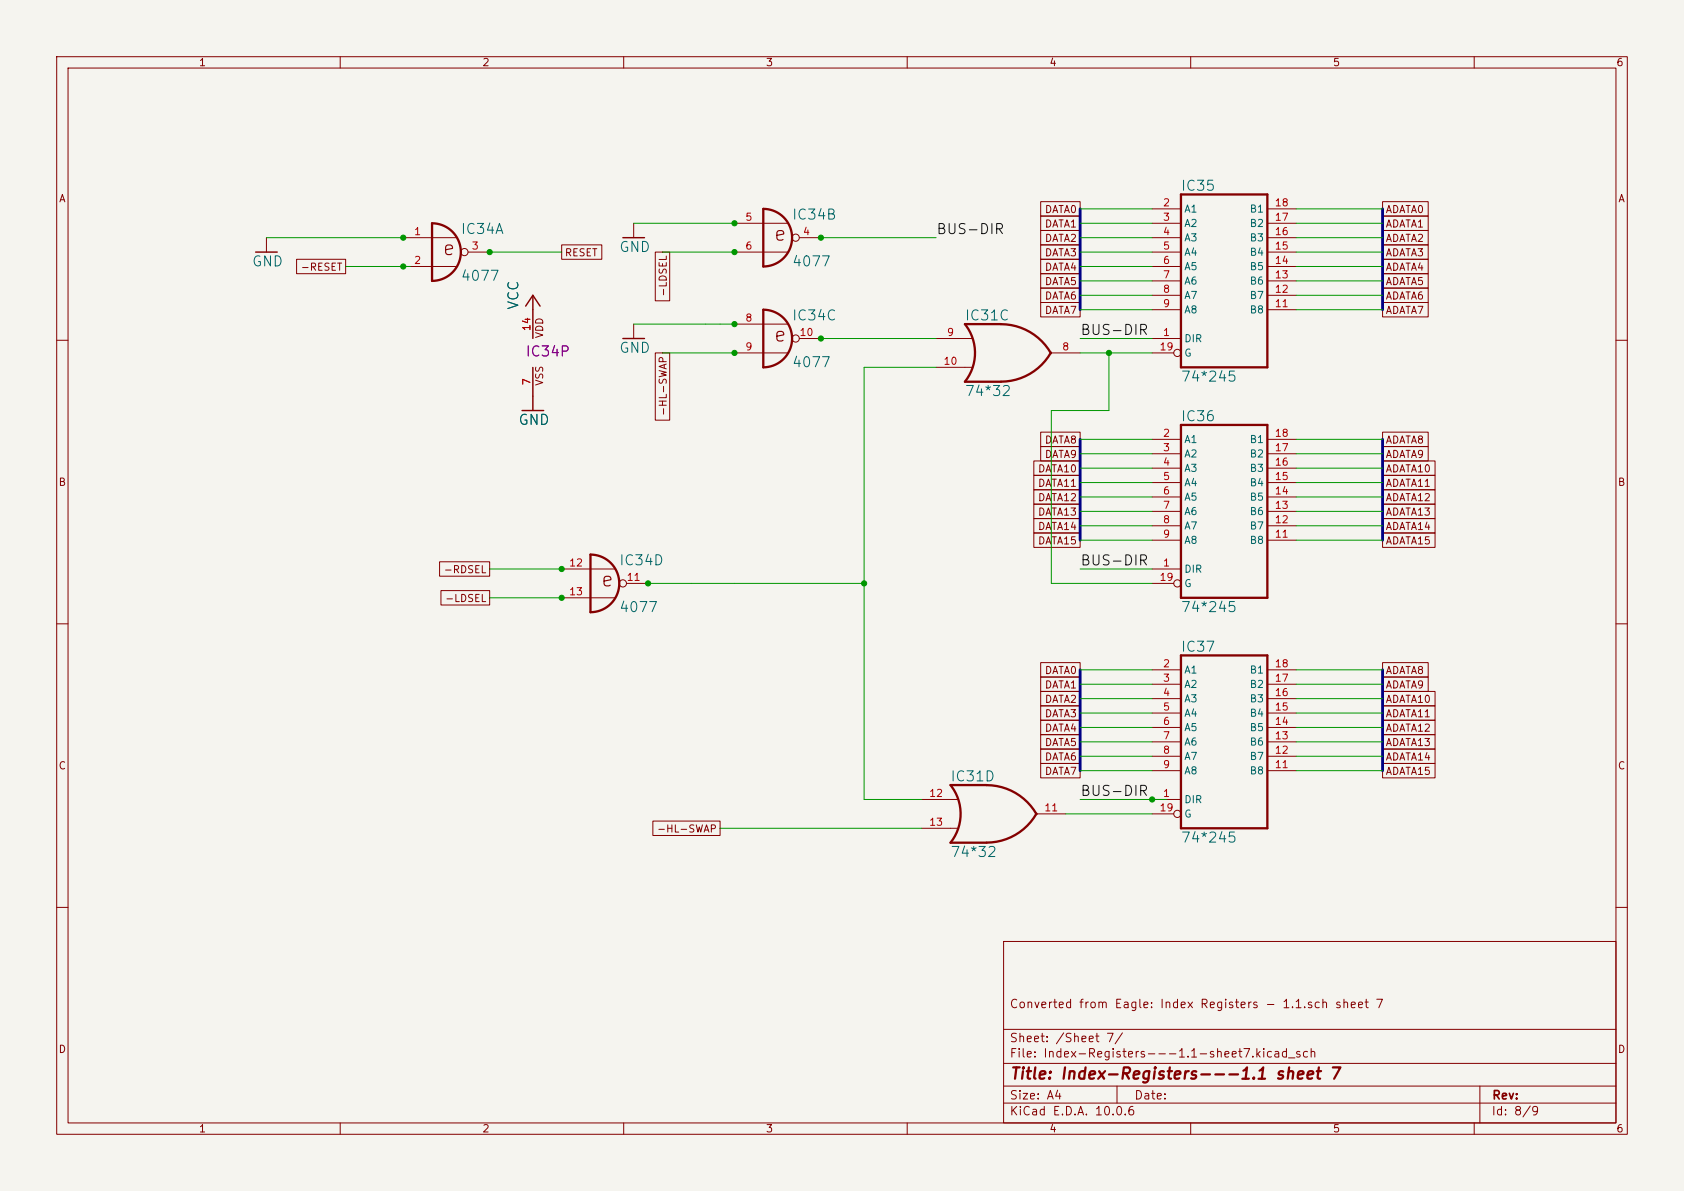
[picture p157: page 8]

Converted from Eagle: Index Registers - 1.1.sch sheet 7

Sheet: /Sheet 7/
File: Index-Registers---1.1-sheet7.kicad_sch
Title: Index-Registers---1.1 sheet 7

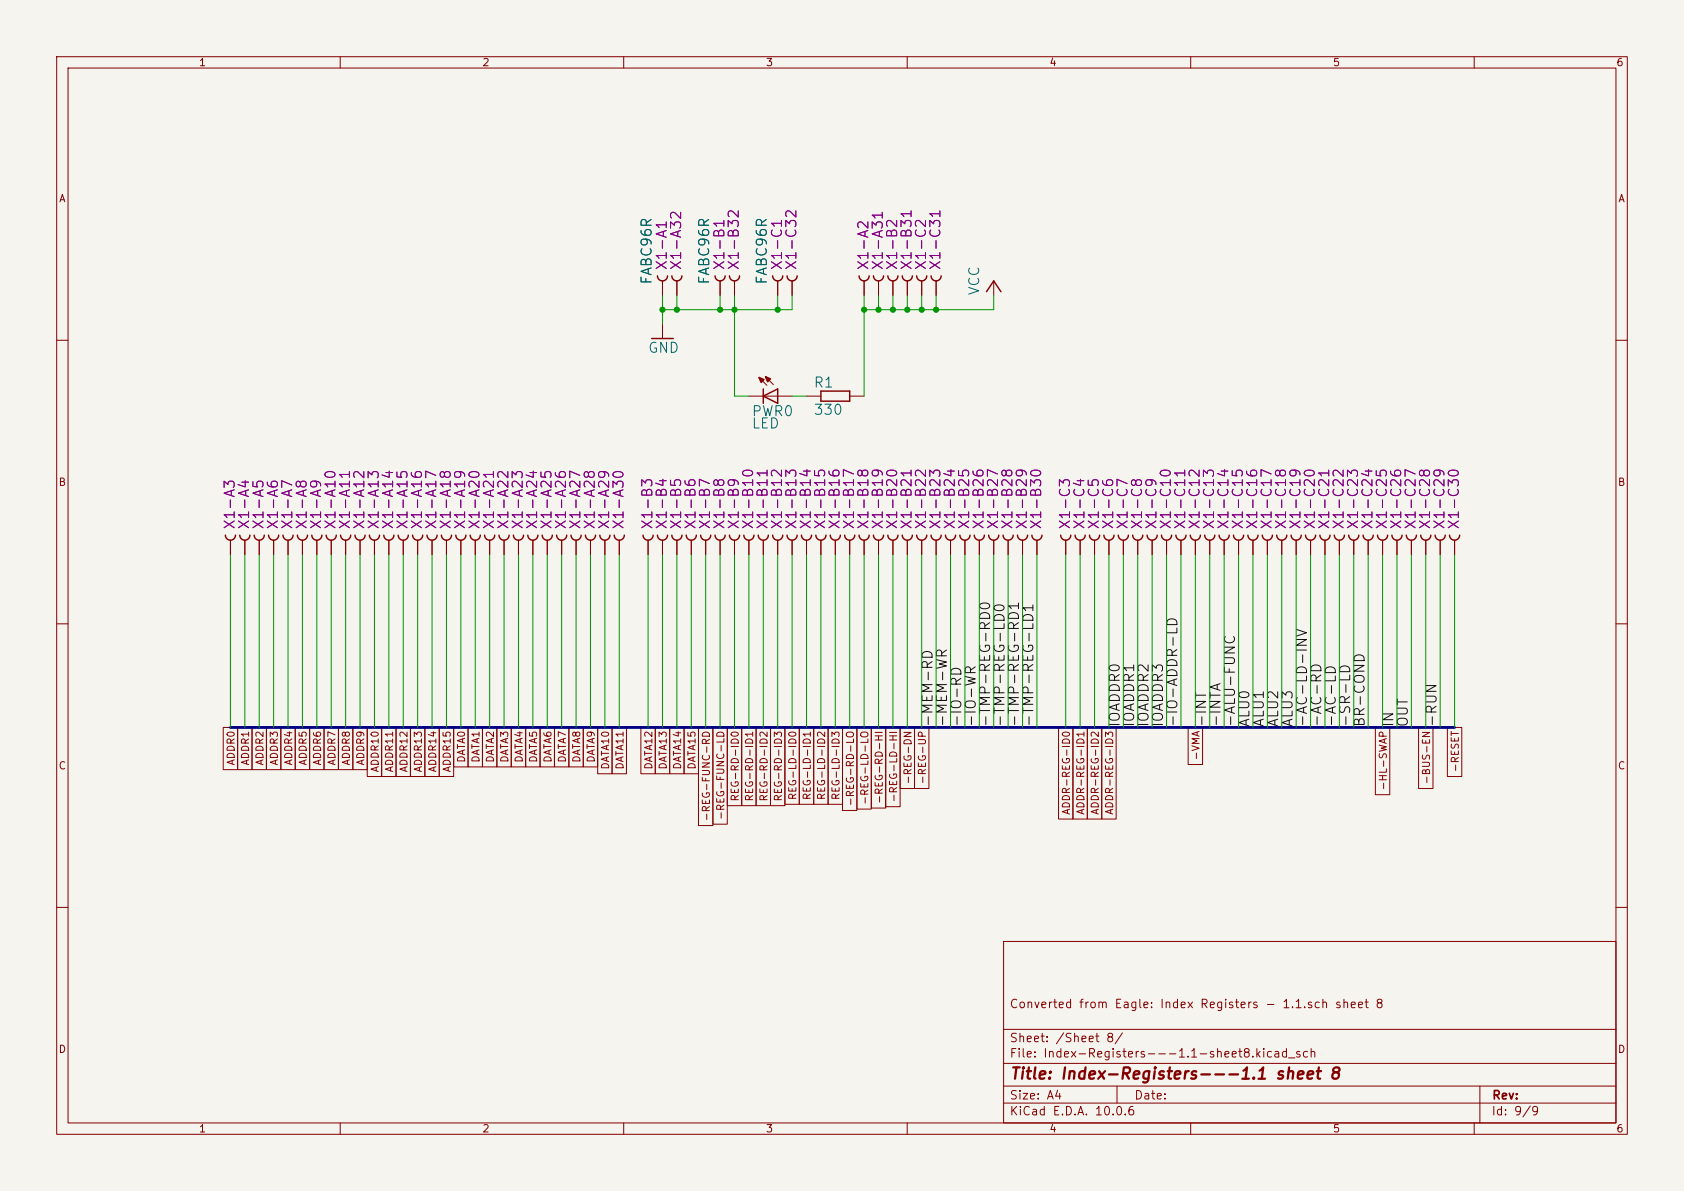
[picture p158: page 9]

Sheet: /Sheet 8/
File: Index-Registers---1.1-sheet8.kicad_sch
Title: Index-Registers---1.1 sheet 8
