ksr/YACC1-D/hardware/cards/register/kicad/v1.1/reports/register-v1.1-schematic.pdf

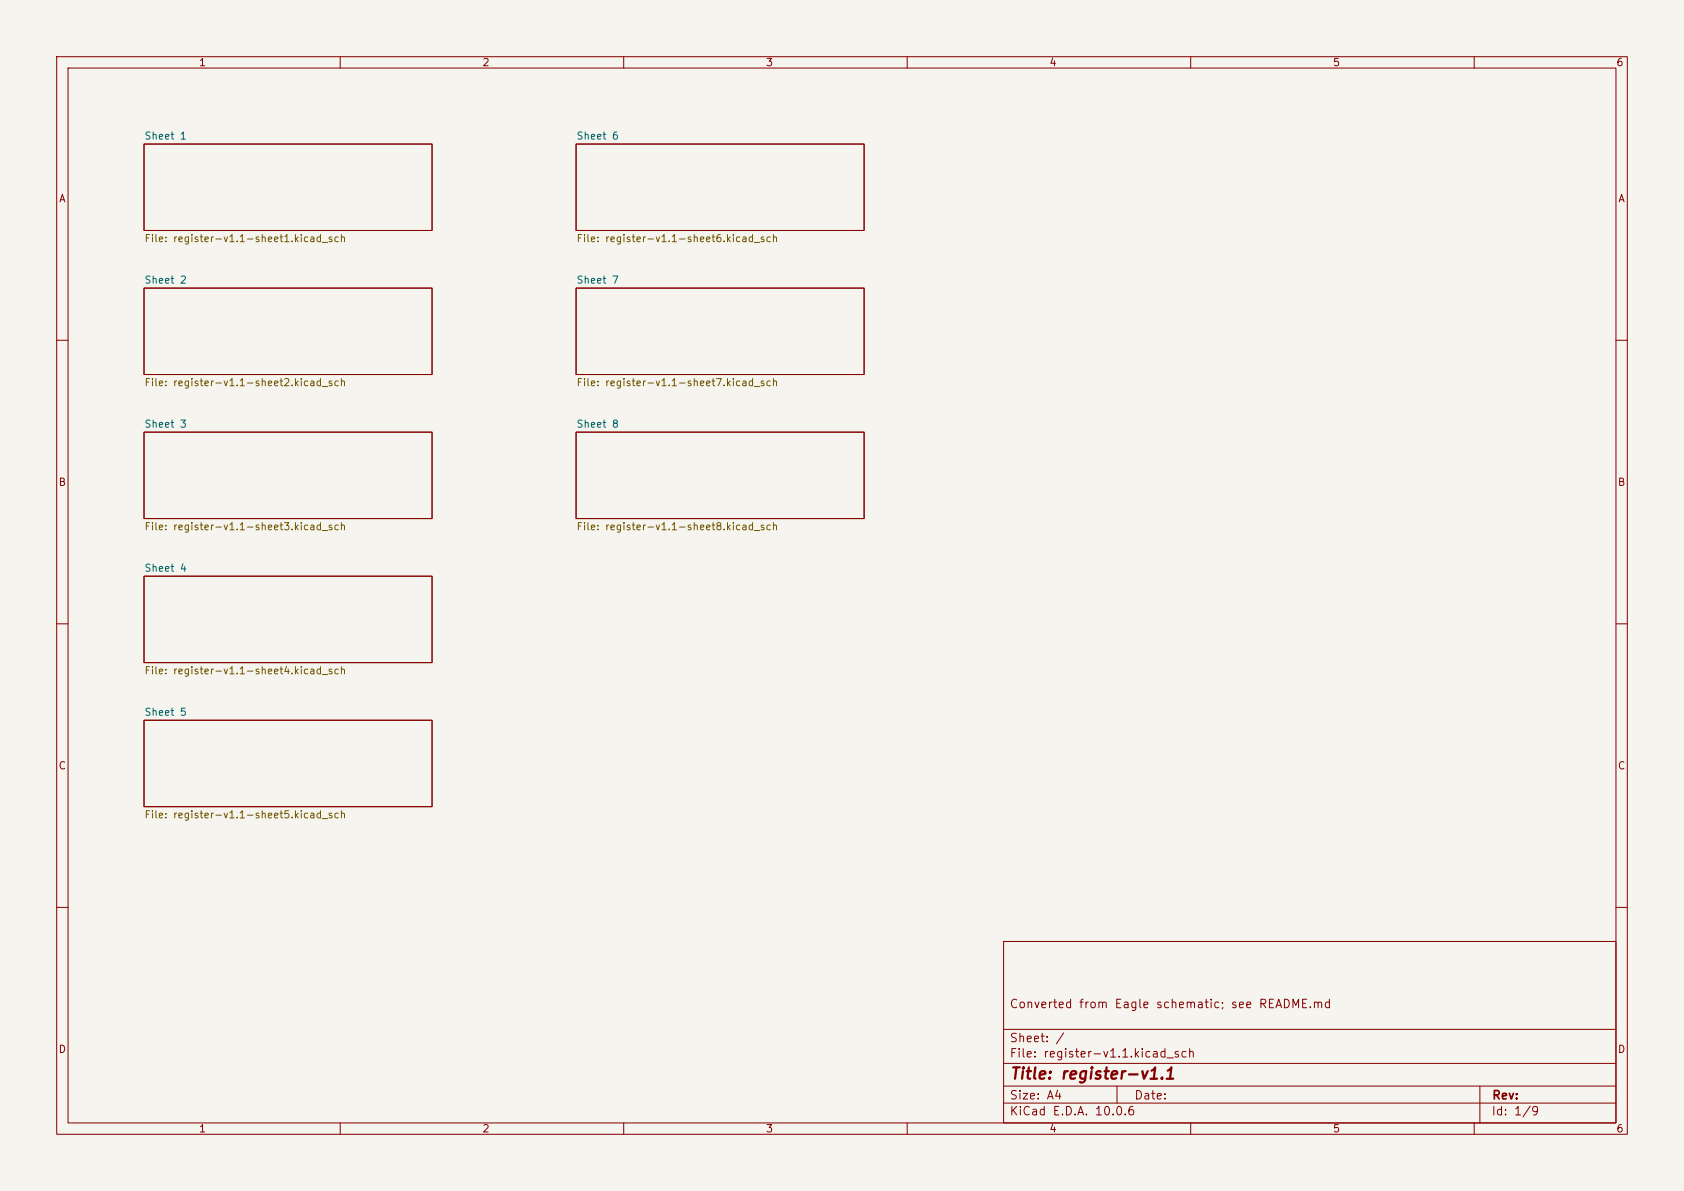
[picture p159: page 1]

Converted from Eagle schematic; see README.md

Size: A4 | Rev:
KiCad E.D.A. 10.0.6 | Id: 1/9

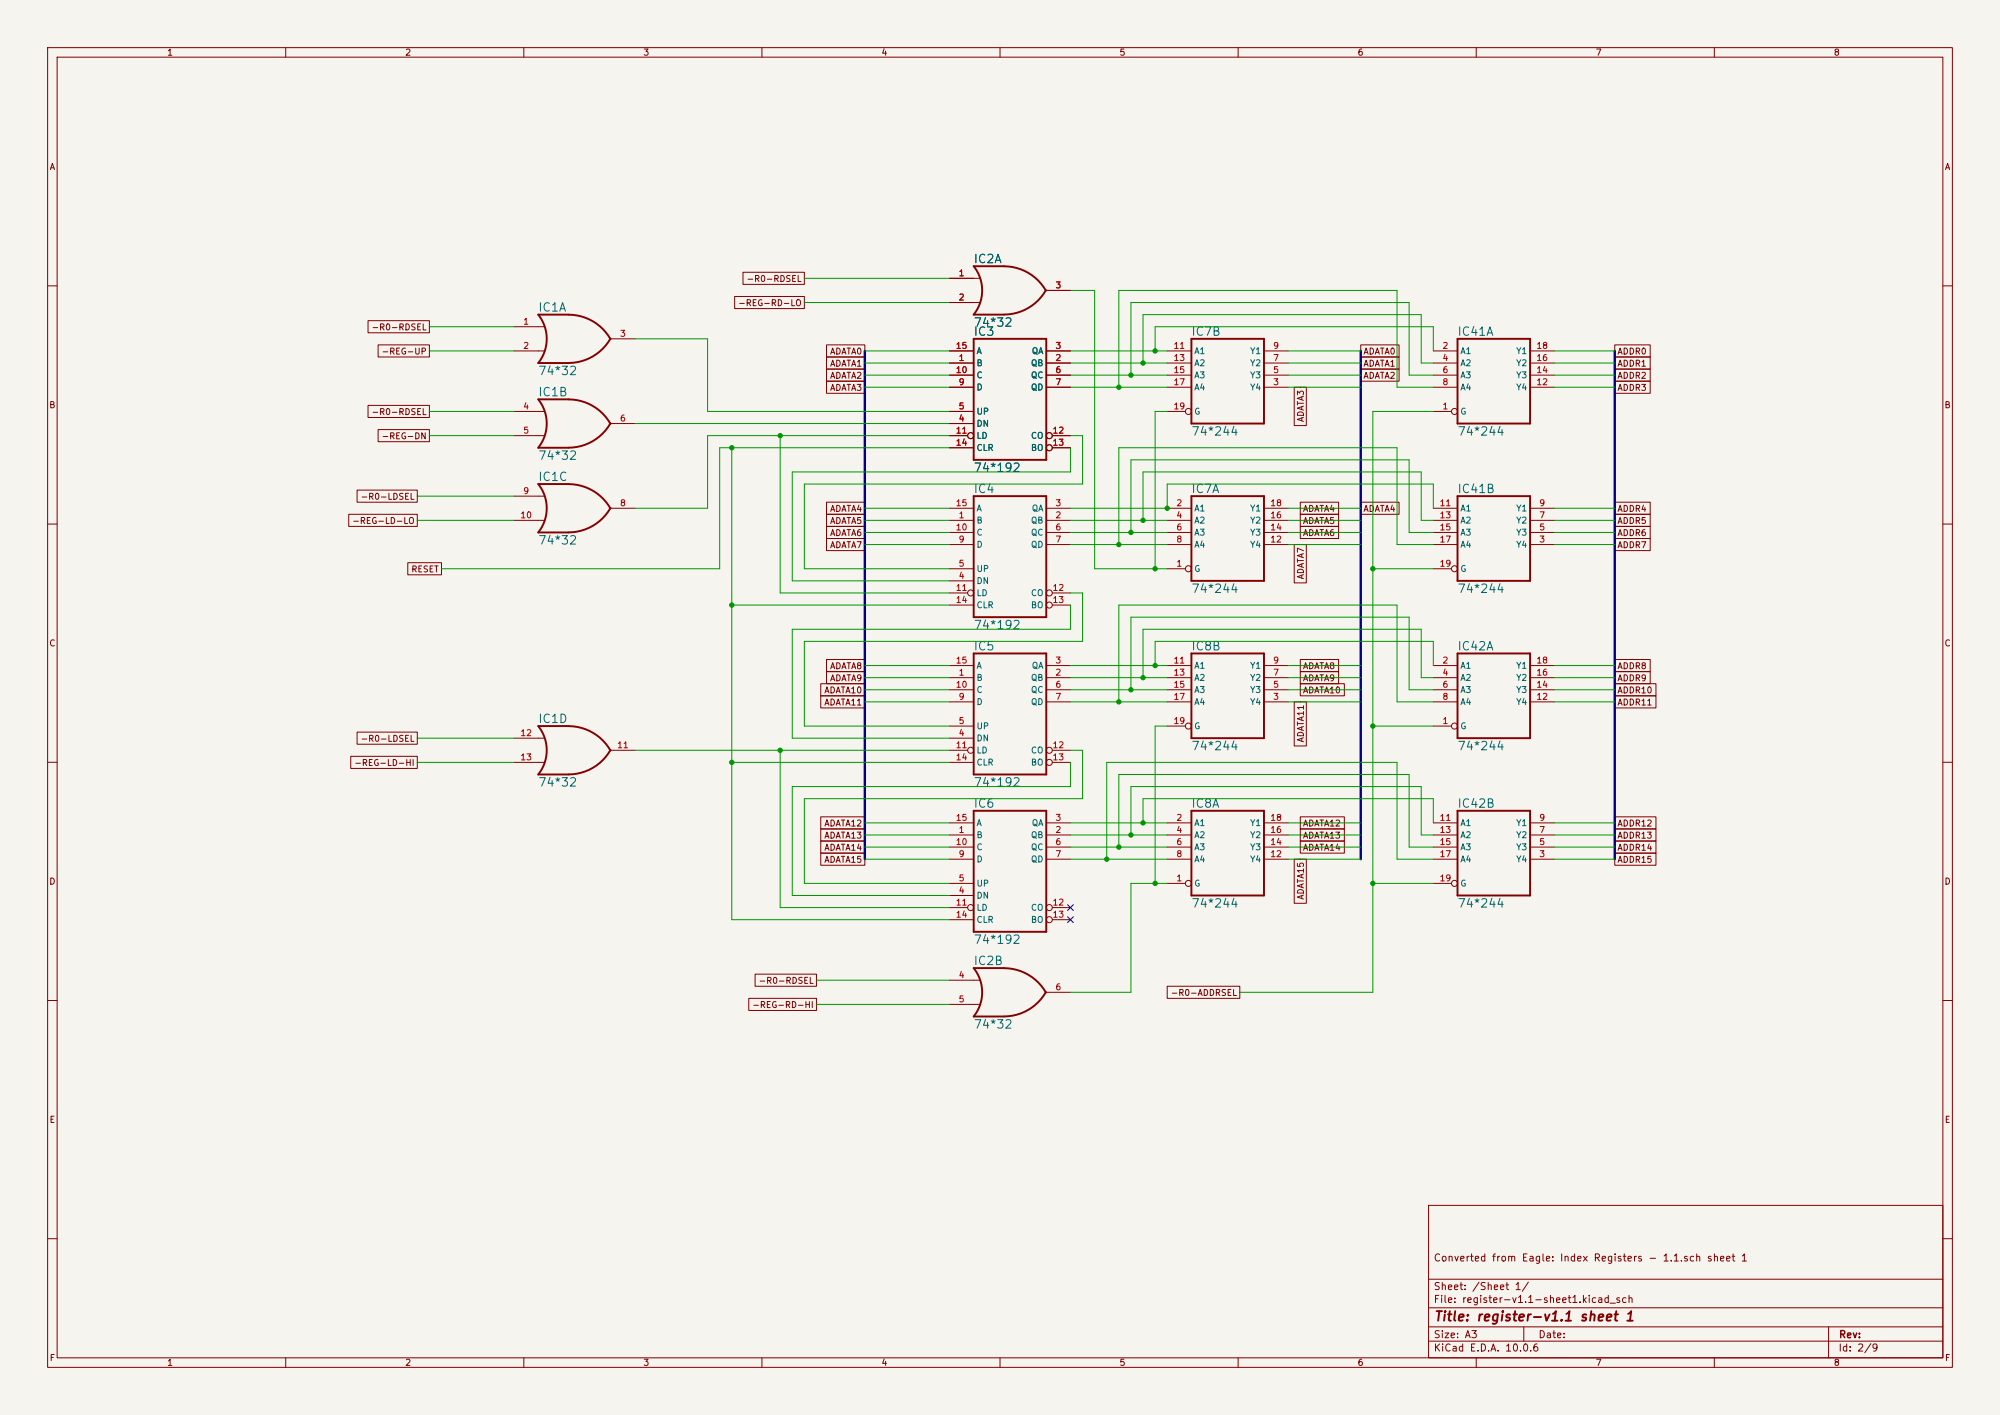
[picture p160: page 2]

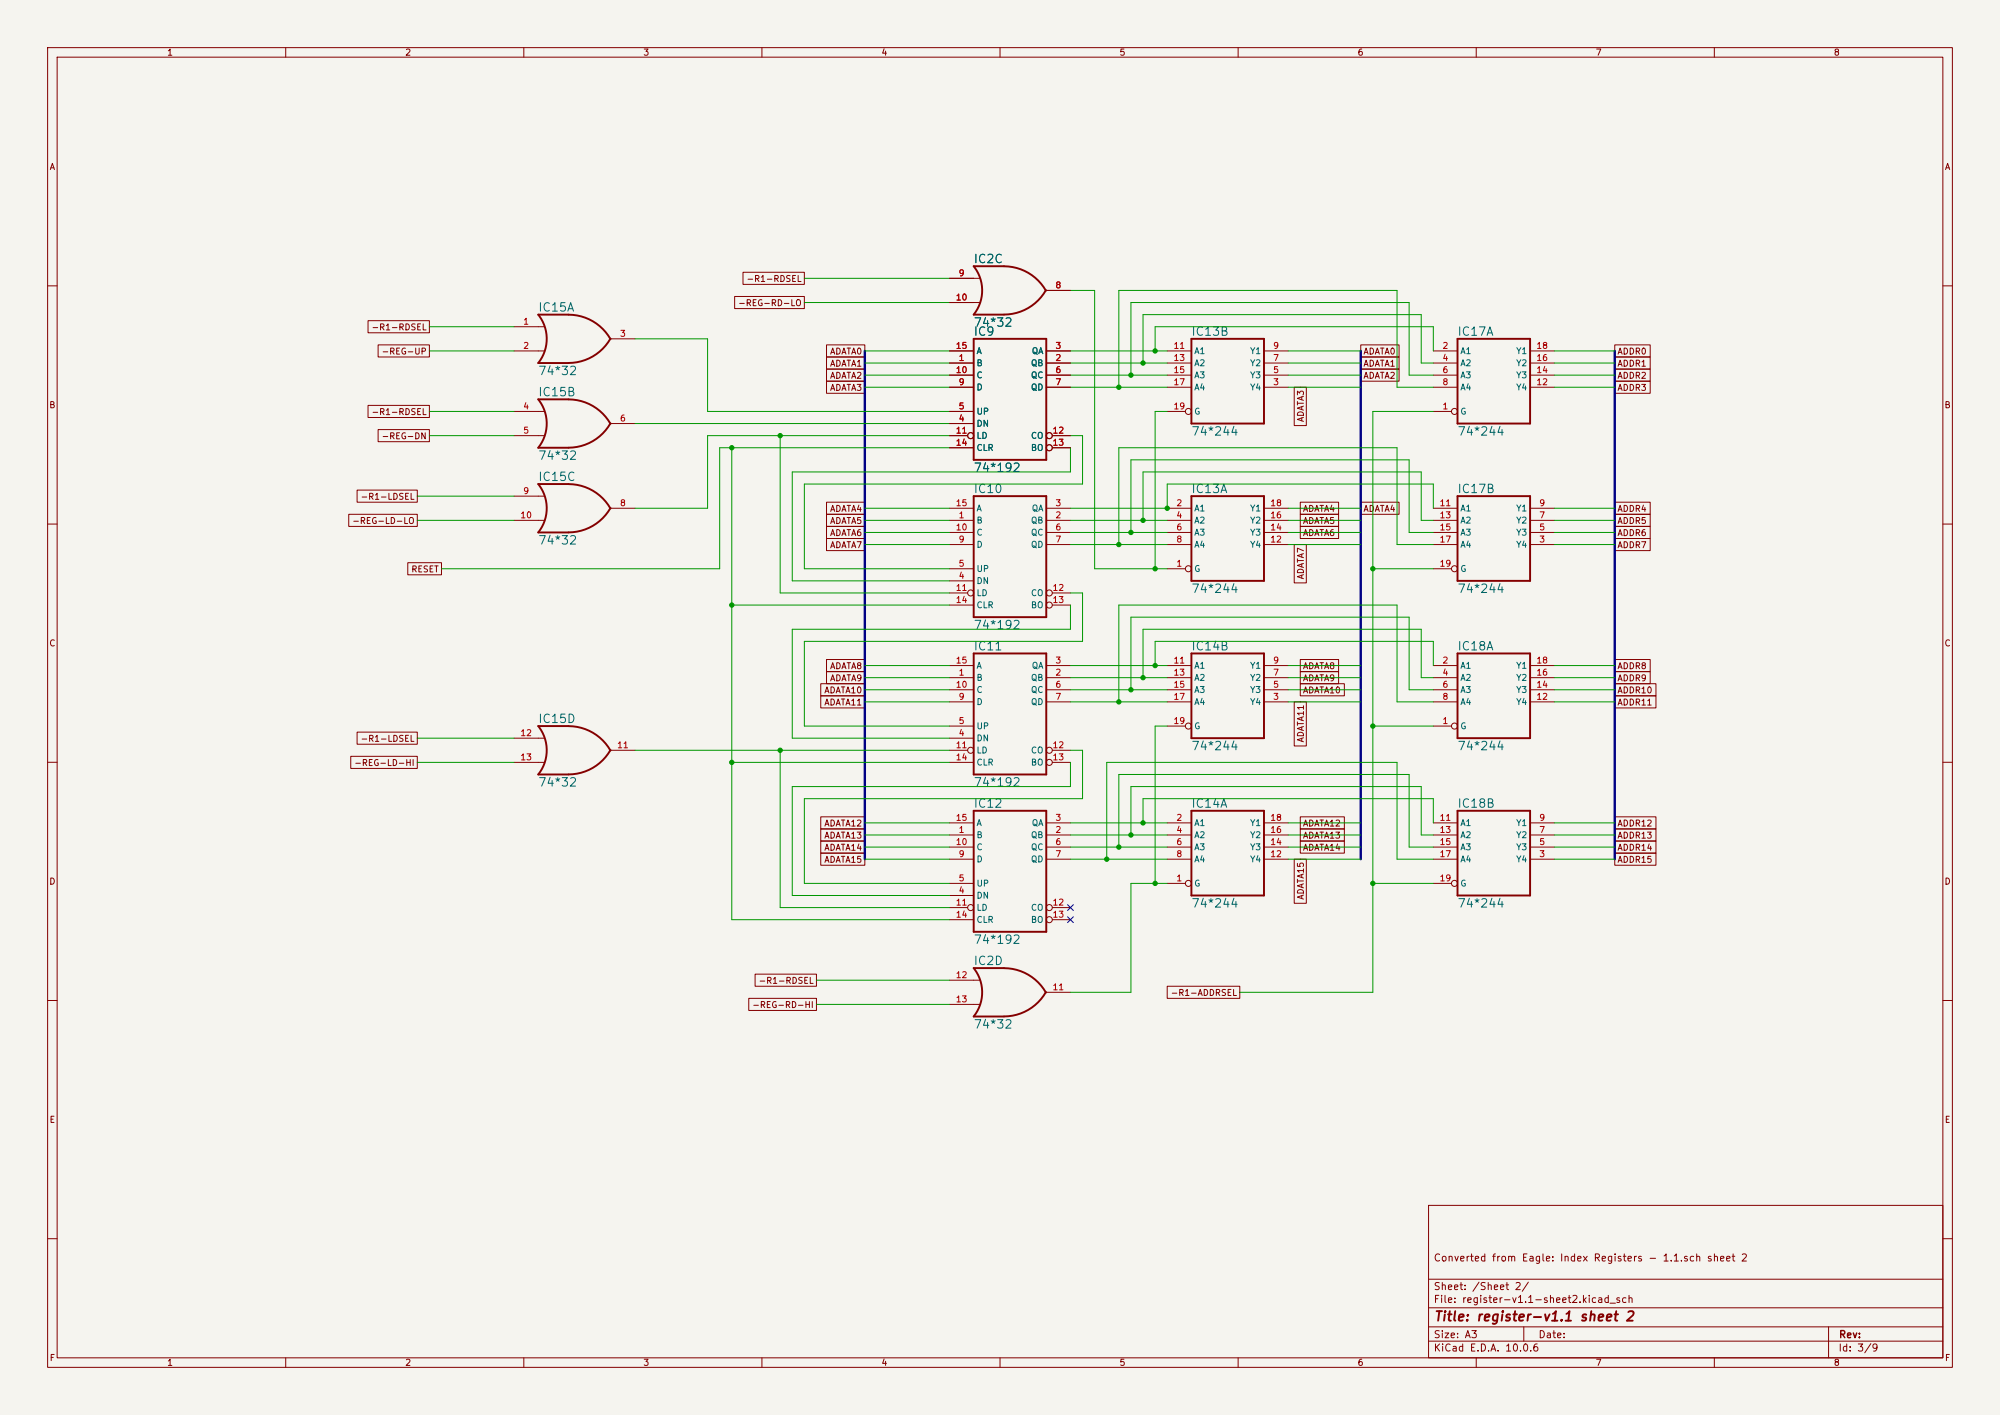
[picture p161: page 3]

ADATA0 -R1-RDSEL -REG-RD-LO

ADDR12 -R1-RDSEL -R1-RDSEL -REG-DN -REG-UP

Converted from Eagle: Index Registers - 1.1.sch sheet 2

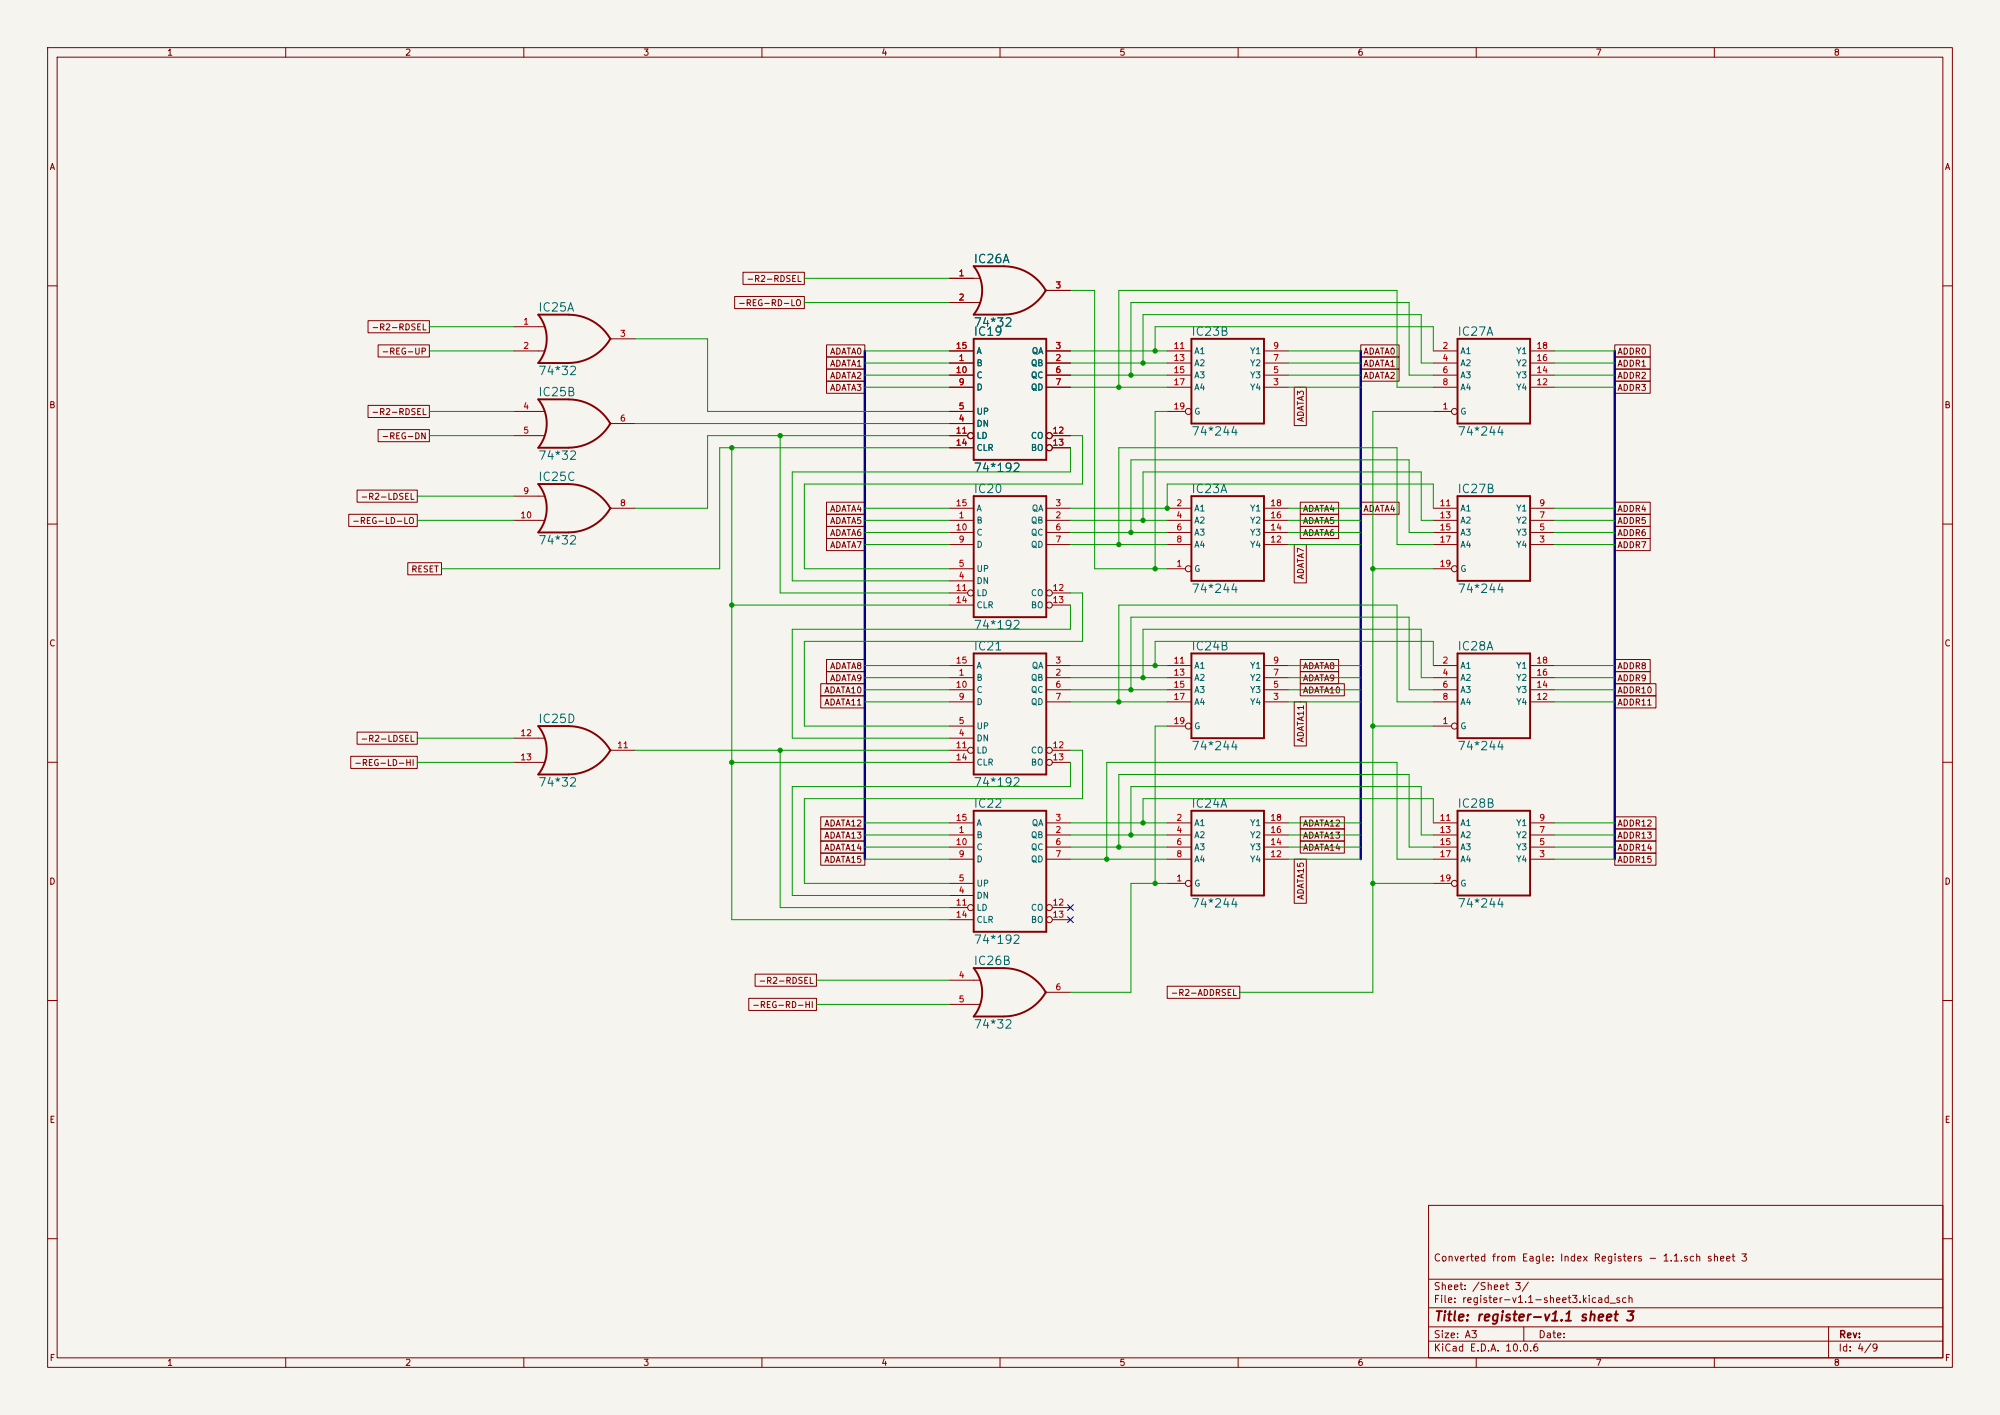
[picture p162: page 4]

Converted from Eagle: Index Registers - 1.1.sch sheet 3 8 9

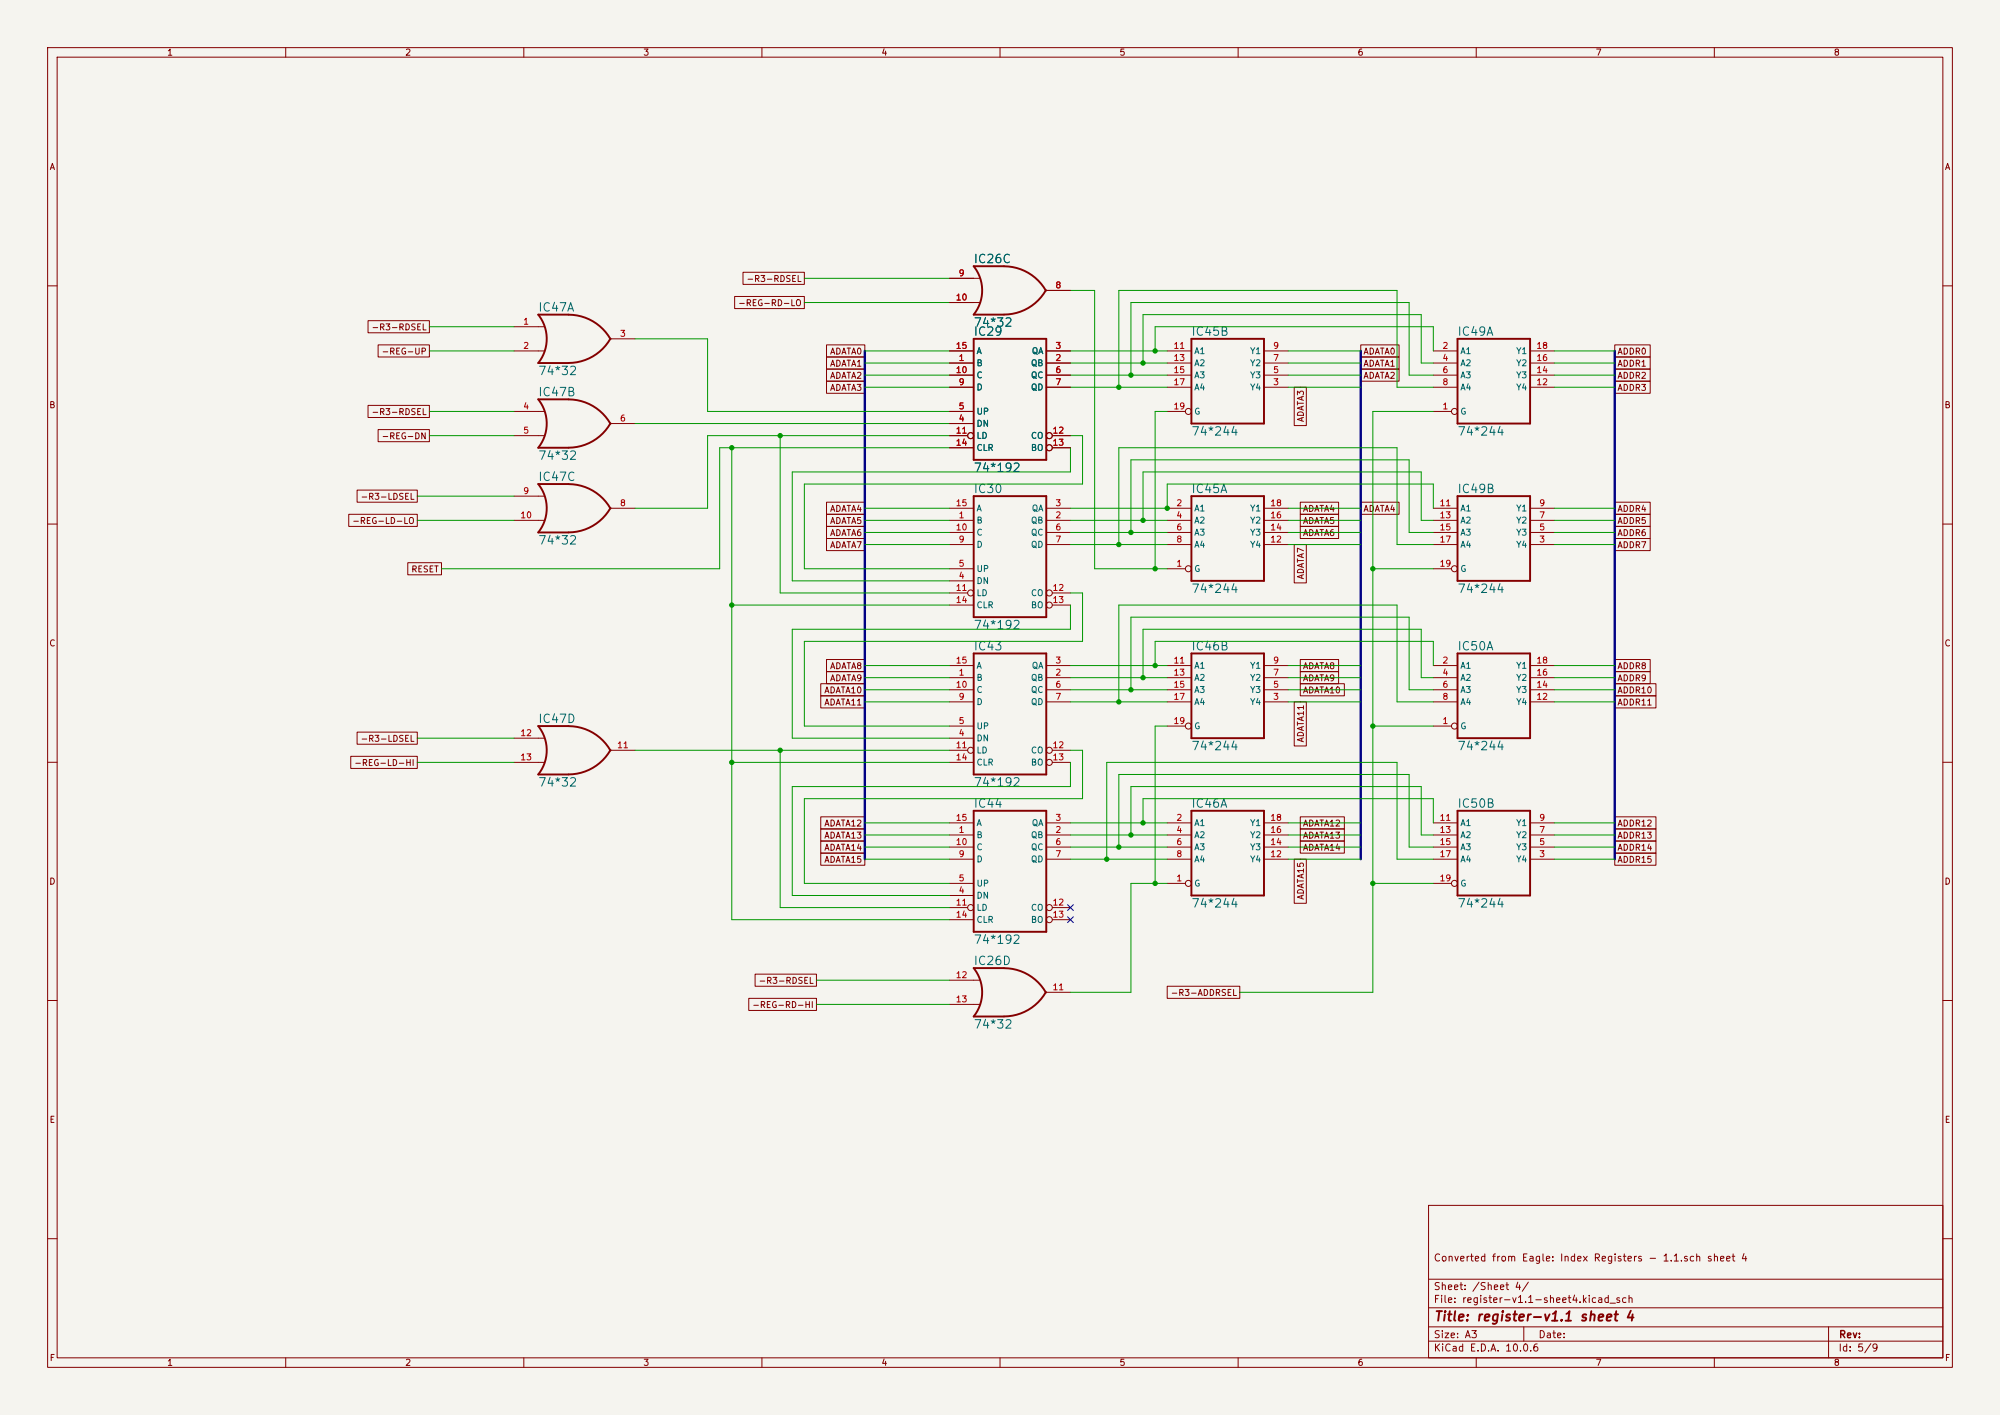
[picture p163: page 5]

ADATA0 -R3-RDSEL -REG-RD-LO

ADDR12 -R3-RDSEL -R3-RDSEL -REG-DN -REG-UP

Converted from Eagle: Index Registers - 1.1.sch sheet 4

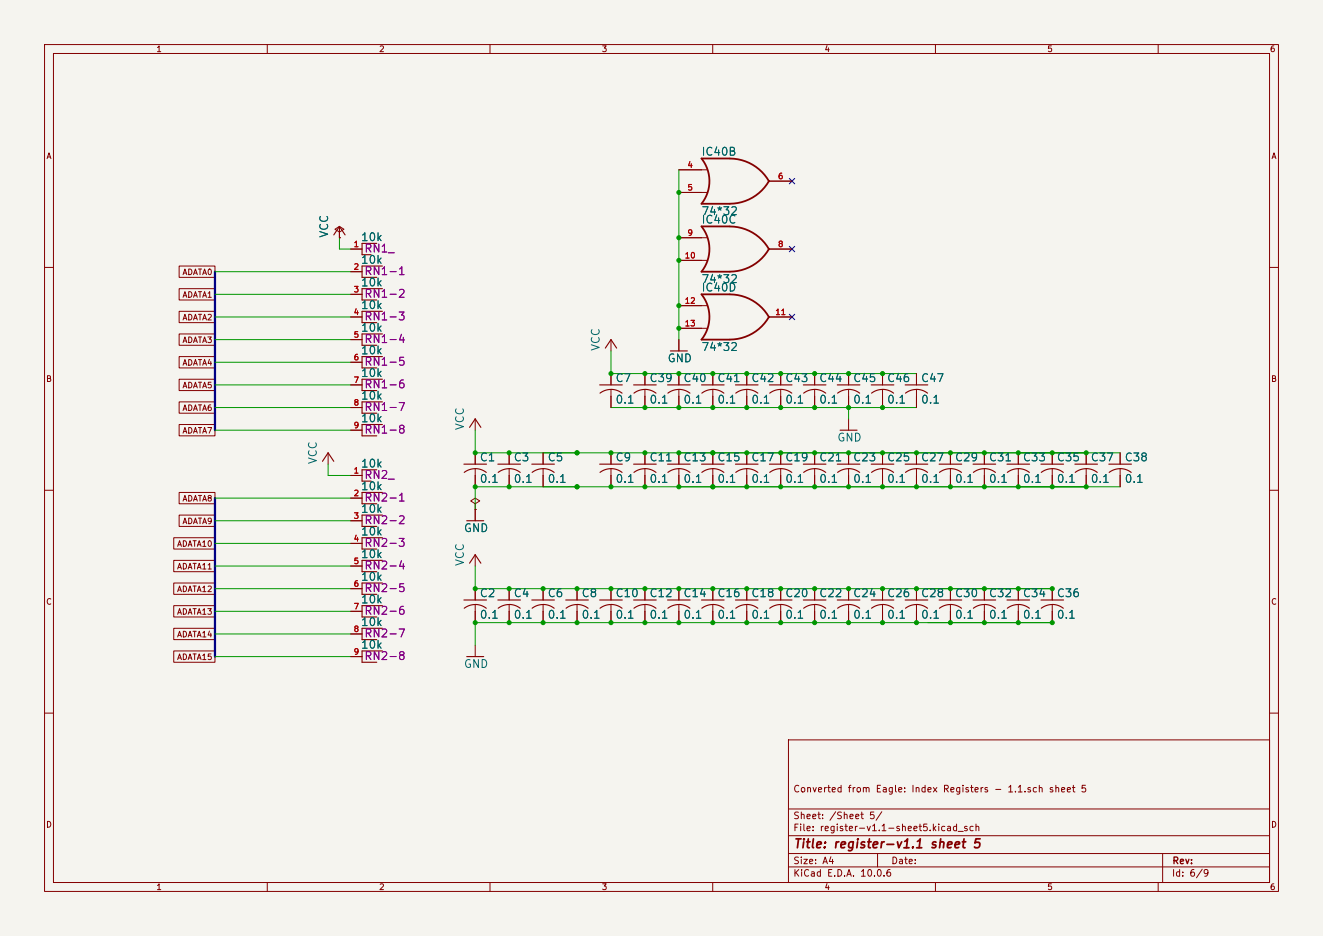
[picture p164: page 6]

Converted from Eagle: Index Registers - 1.1.sch sheet 5

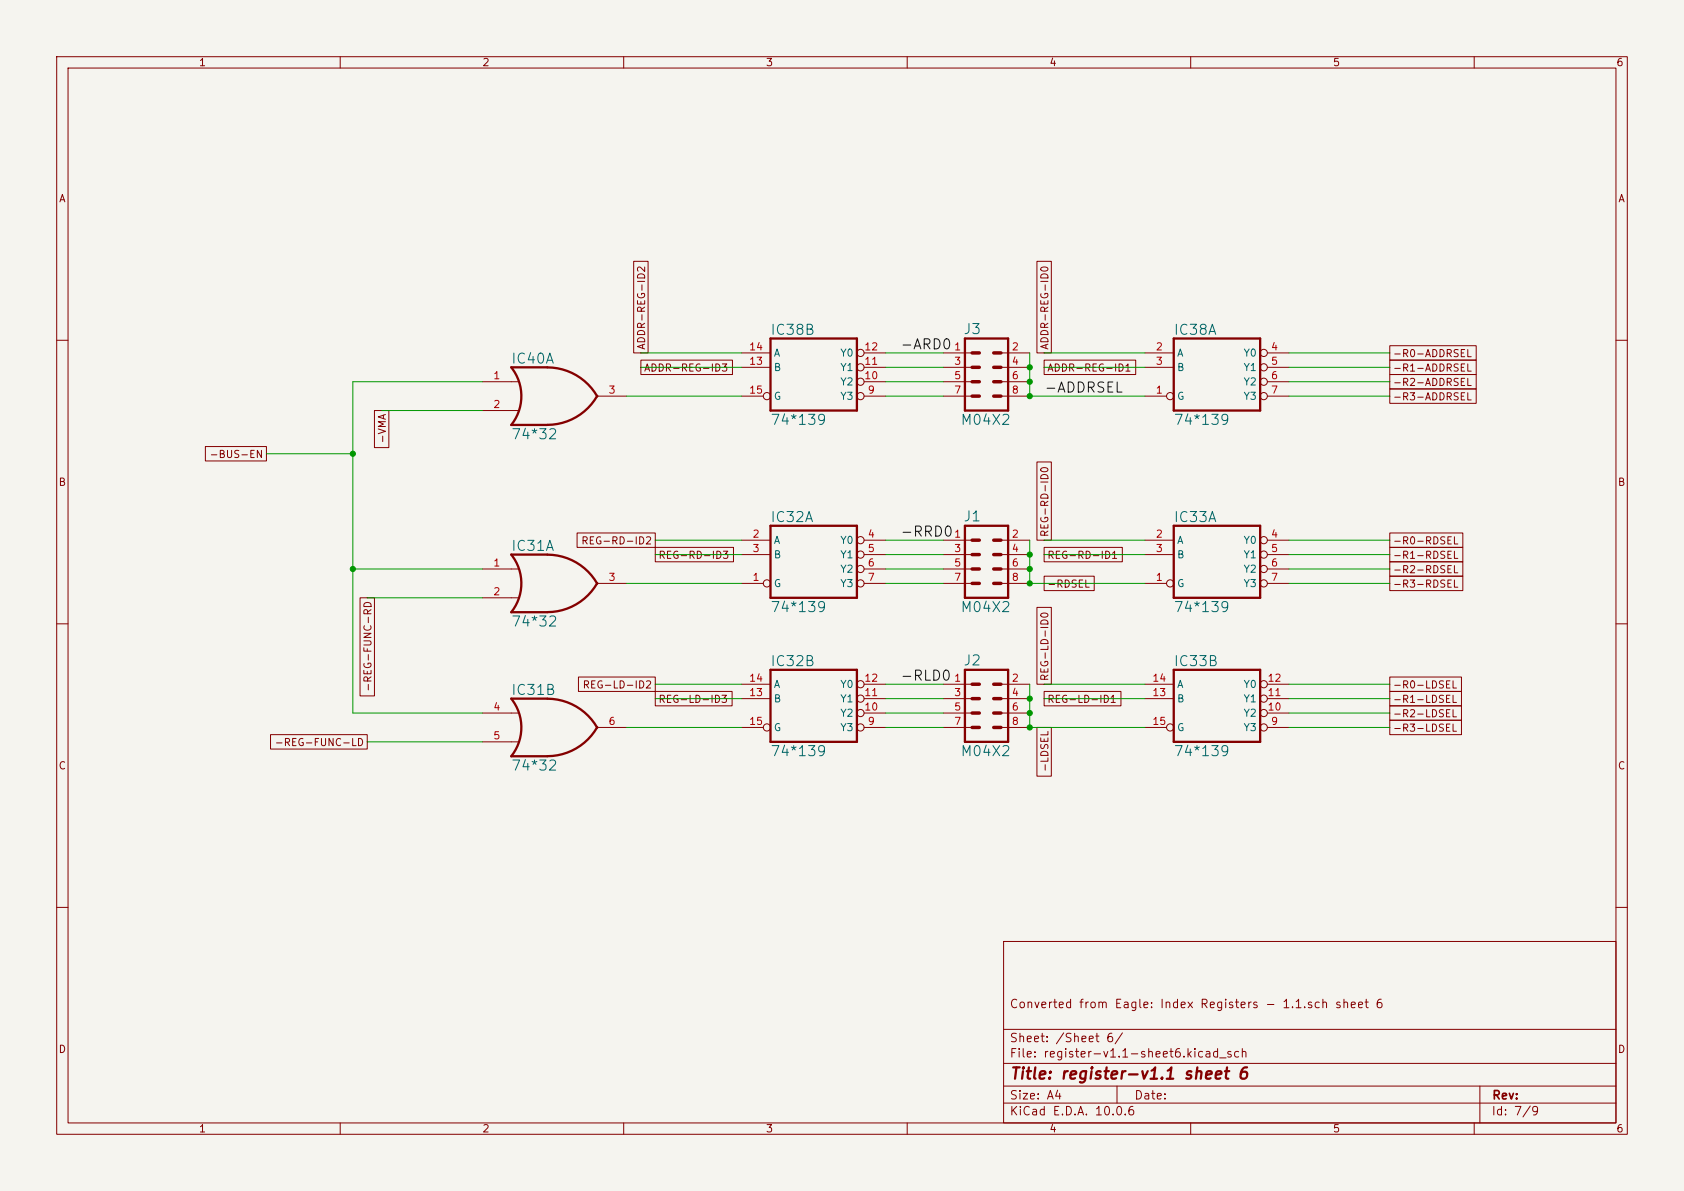
[picture p165: page 7]

Converted from Eagle: Index Registers - 1.1.sch sheet 6

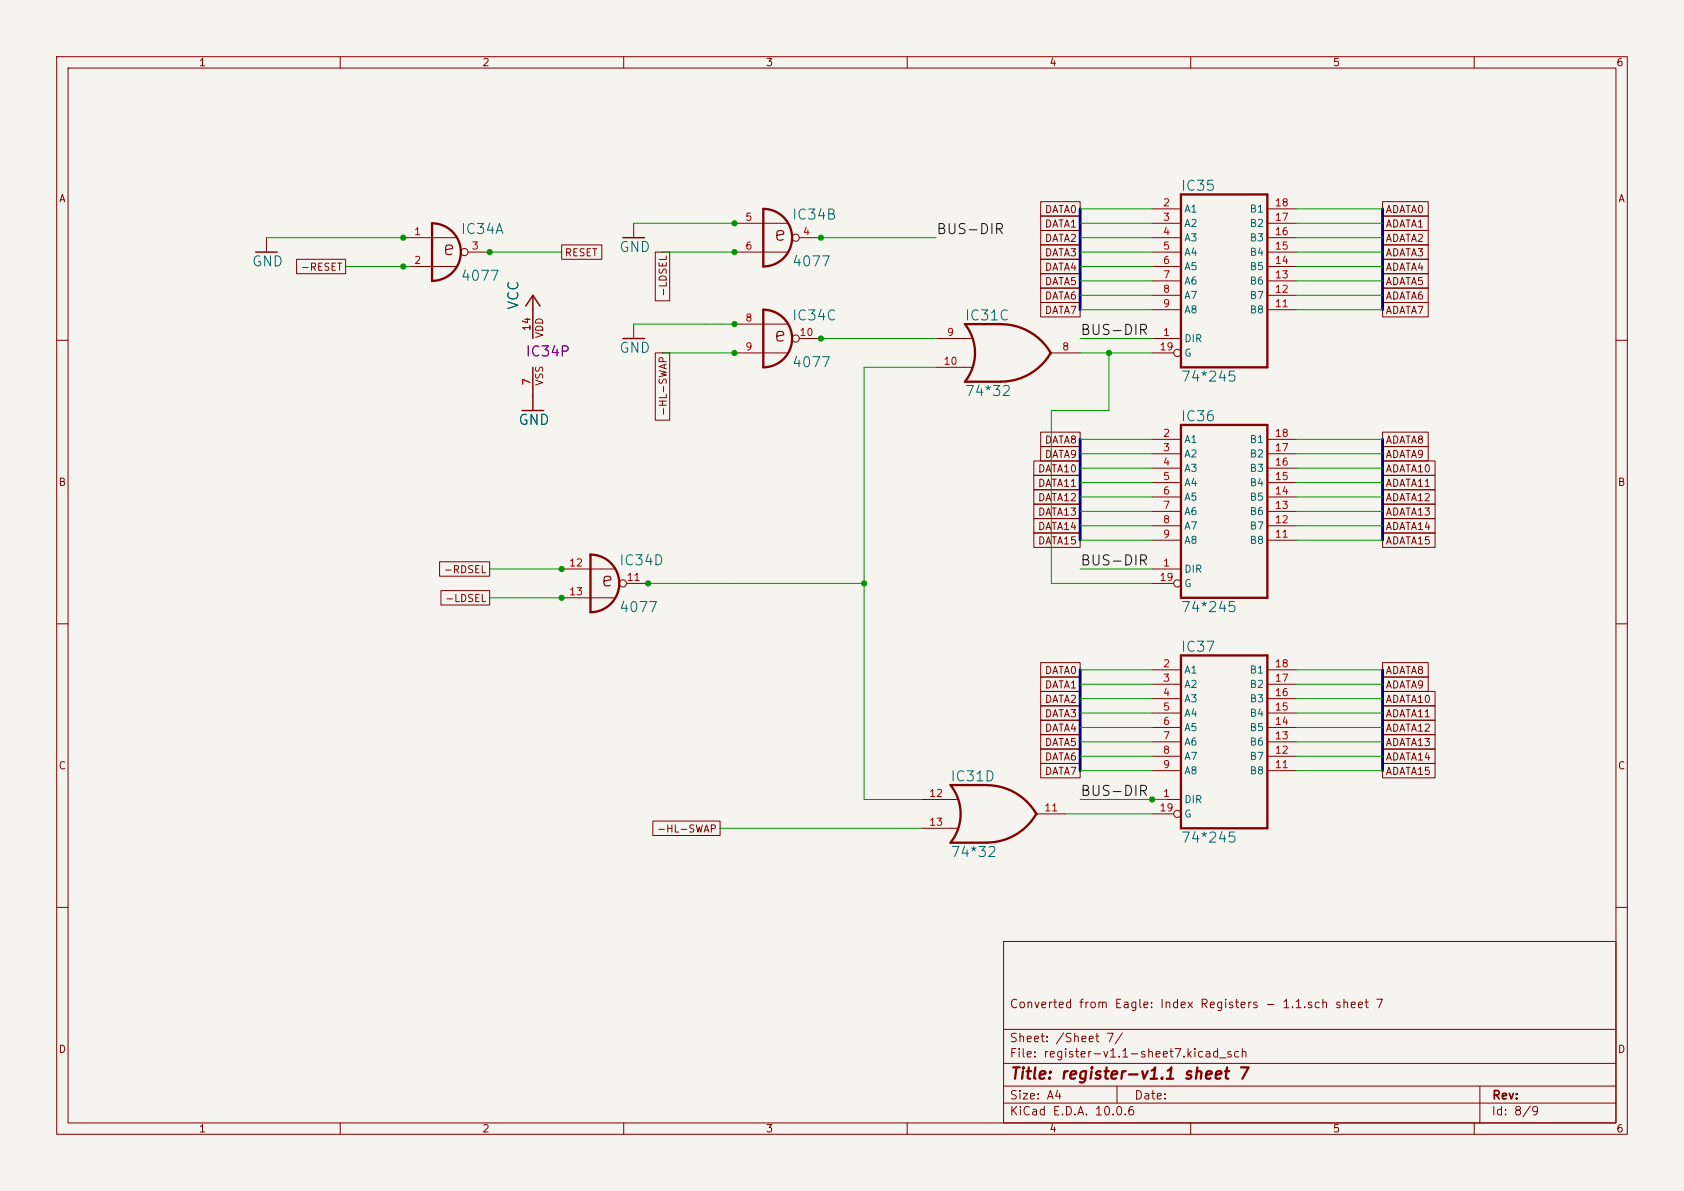
[picture p166: page 8]

Converted from Eagle: Index Registers - 1.1.sch sheet 7

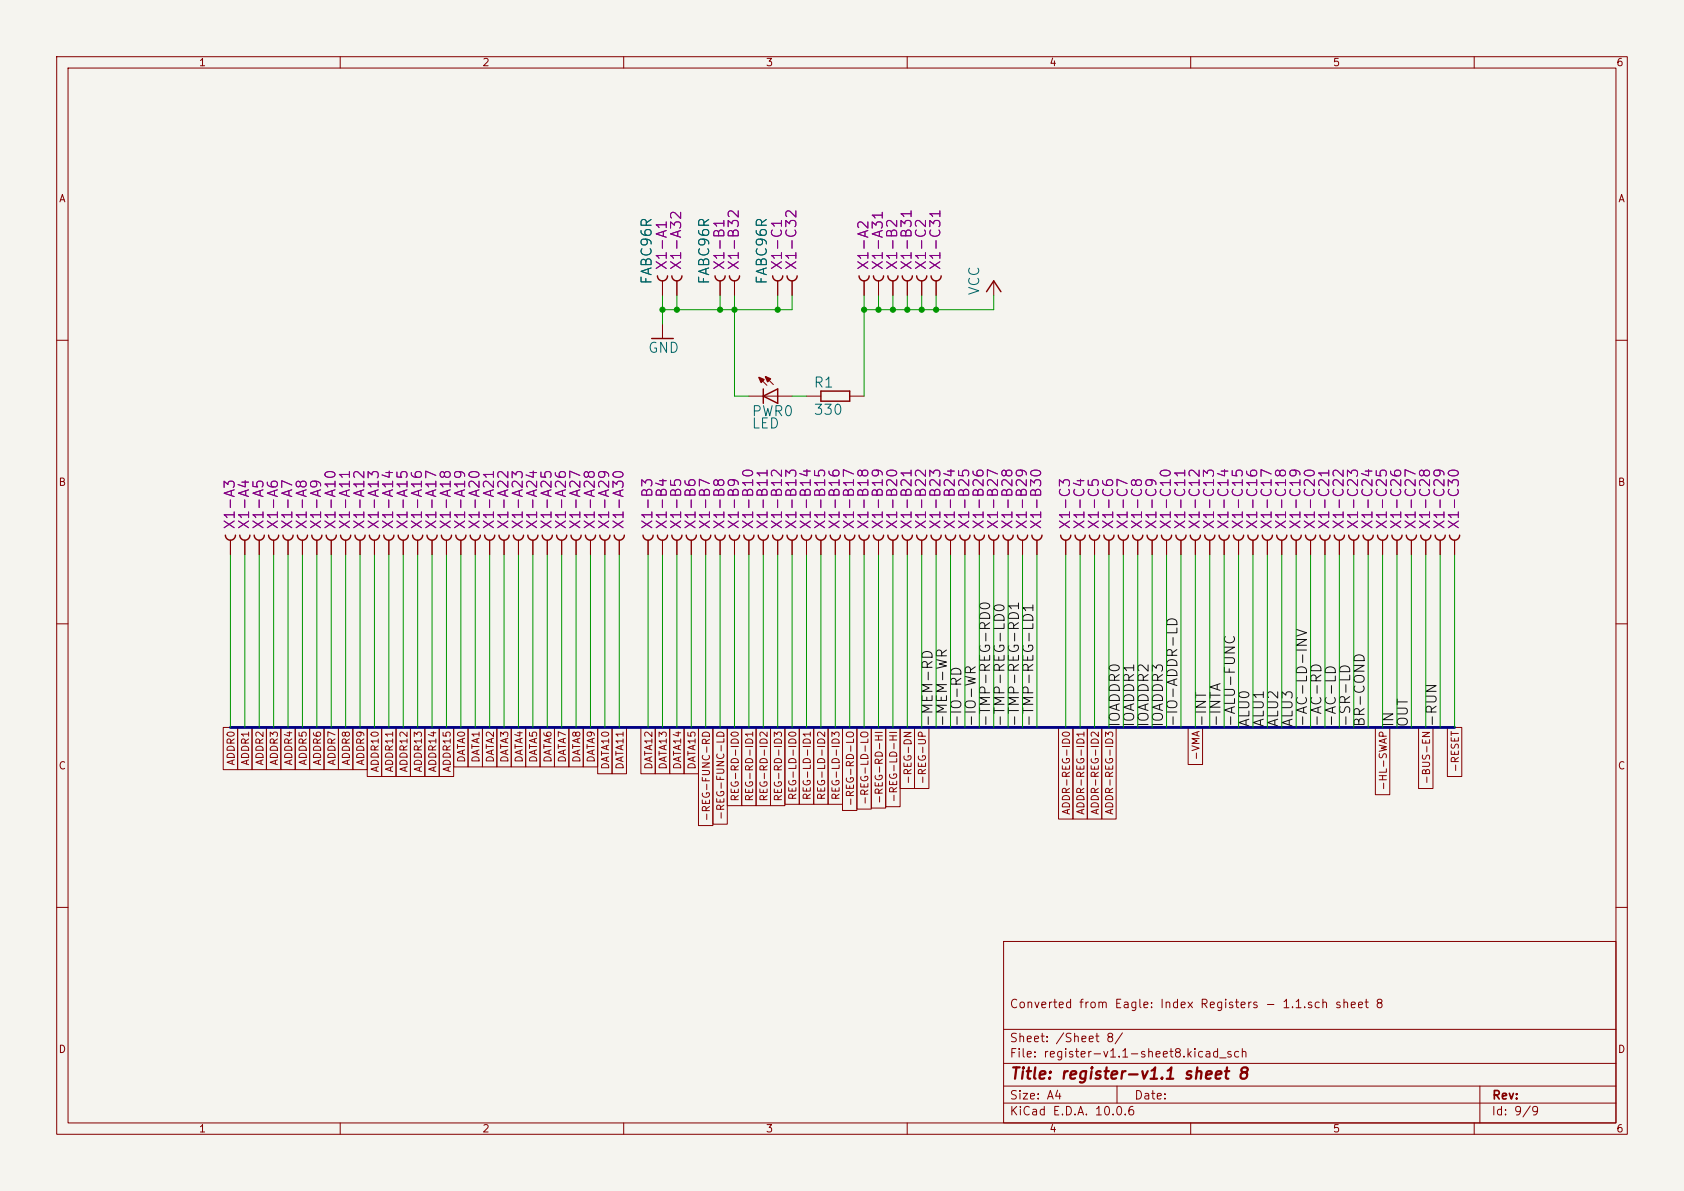
[picture p167: page 9]
