ksr/YACC1-D/hardware/cards/sequencer-logic/eagle/v2.1/pdf/Sequencer-Logic-Prod-V2.1l-schematic.pdf

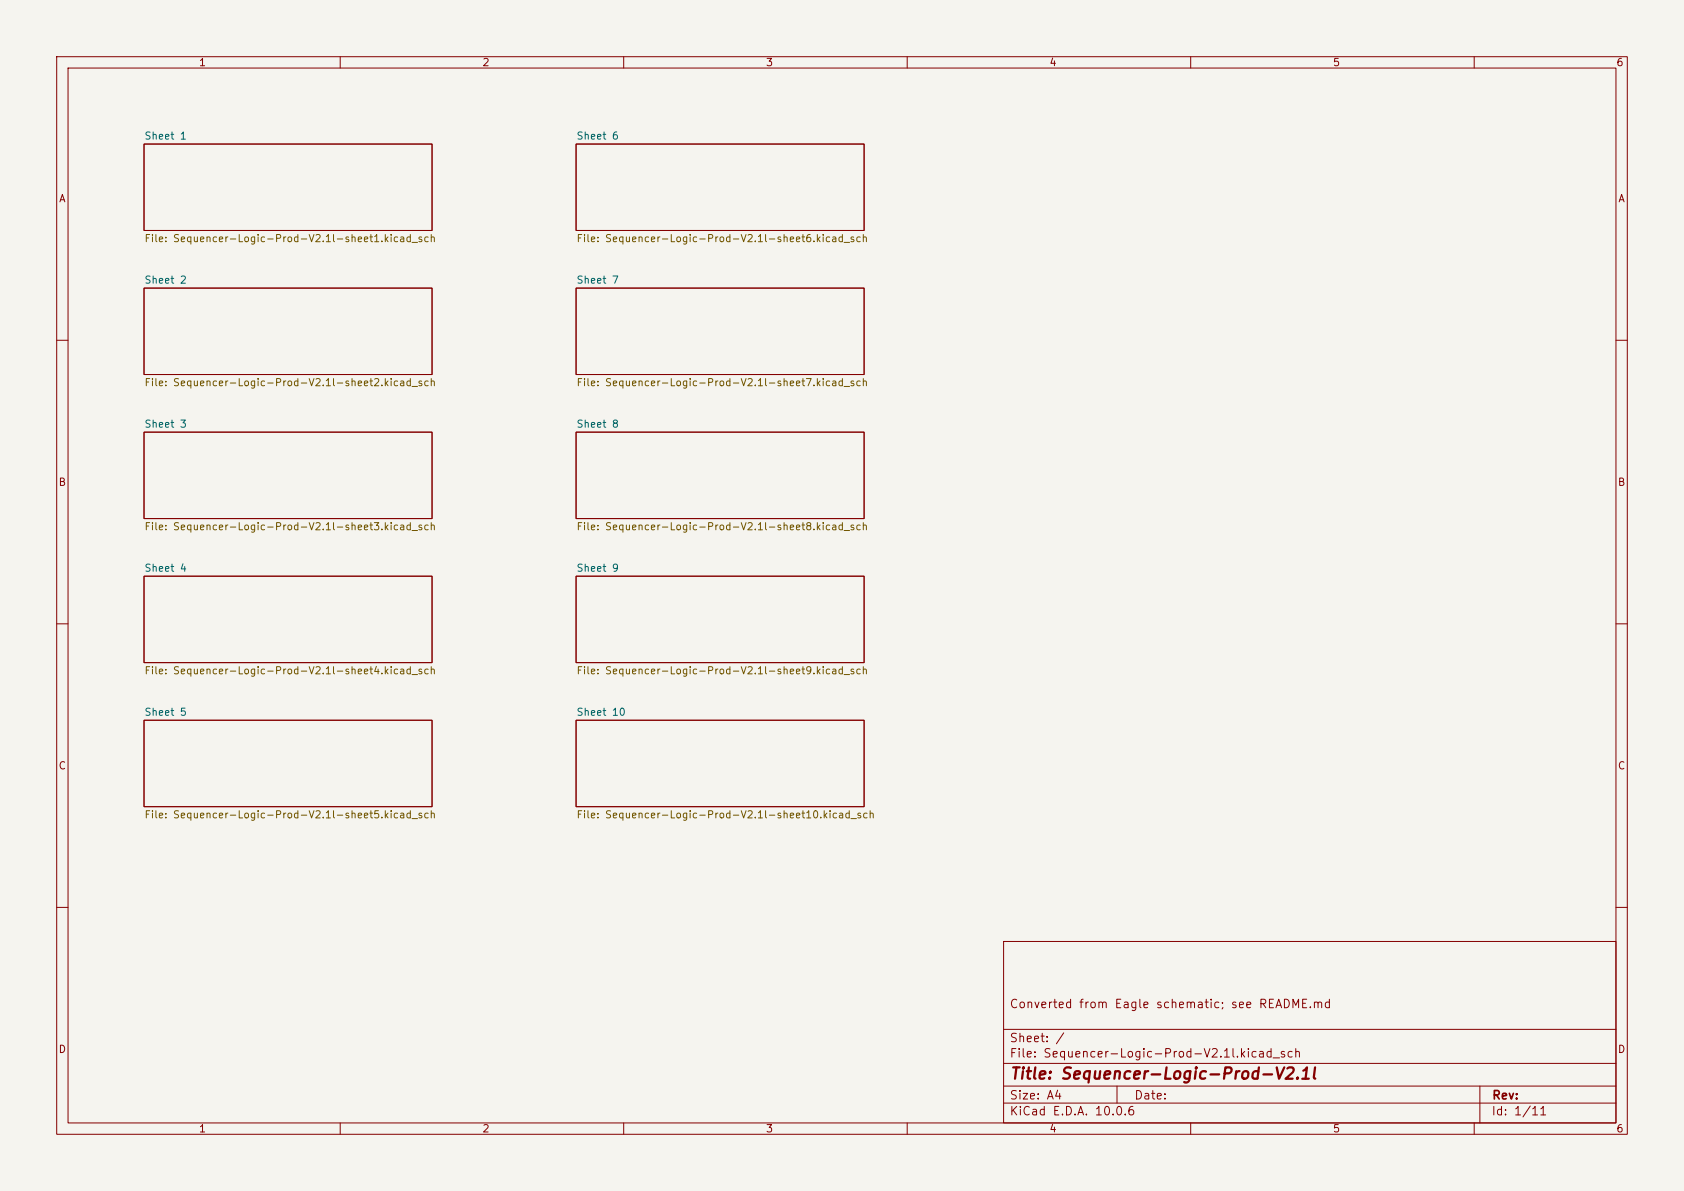
[picture p168: page 1]

File: Sequencer-Logic-Prod-V2.1l-sheet1.kicad_sch Sheet 2

File: Sequencer-Logic-Prod-V2.1l-sheet6.kicad_sch Sheet 7

File: Sequencer-Logic-Prod-V2.1l-sheet2.kicad_sch Sheet 3

File: Sequencer-Logic-Prod-V2.1l-sheet7.kicad_sch Sheet 8

File: Sequencer-Logic-Prod-V2.1l-sheet3.kicad_sch Sheet 4

File: Sequencer-Logic-Prod-V2.1l-sheet8.kicad_sch Sheet 9

File: Sequencer-Logic-Prod-V2.1l-sheet4.kicad_sch Sheet 5

File: Sequencer-Logic-Prod-V2.1l-sheet9.kicad_sch Sheet 10

File: Sequencer-Logic-Prod-V2.1l-sheet5.kicad_sch

File: Sequencer-Logic-Prod-V2.1l-sheet10.kicad_sch

Converted from Eagle schematic; see README.md

Sheet: /
File: Sequencer-Logic-Prod-V2.1l.kicad_sch
Title: Sequencer-Logic-Prod-V2.1l

Size: A4 | Rev:
KiCad E.D.A. 10.0.6 | Id: 1/11

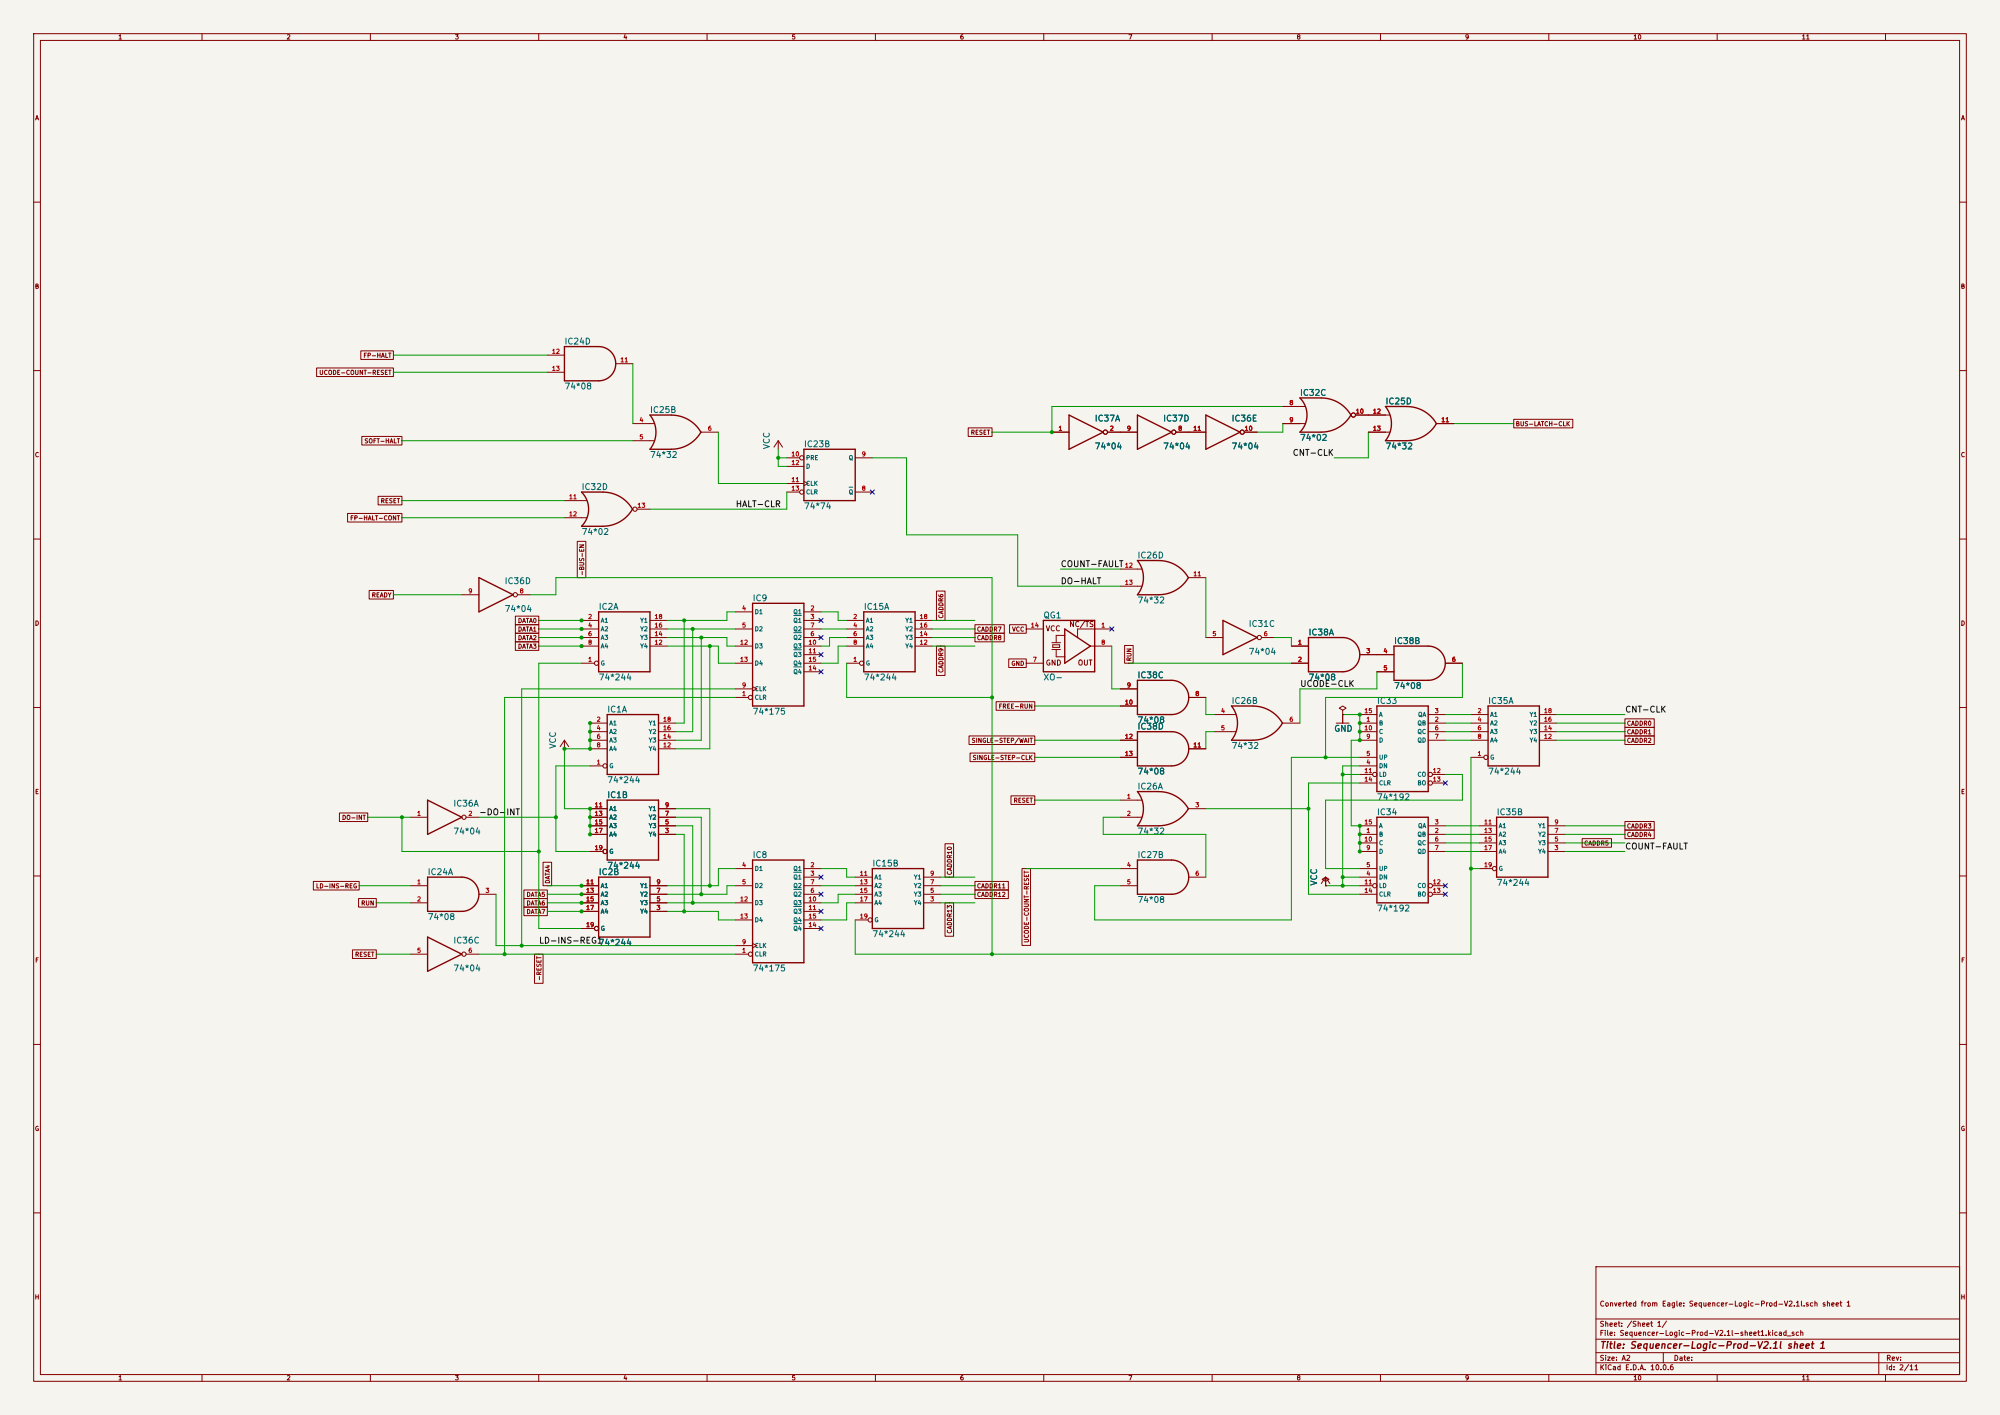
[picture p169: page 2]

Converted from Eagle: Sequencer-Logic-Prod-V2.1l.sch sheet 1

Sheet: /Sheet 1/
File: Sequencer-Logic-Prod-V2.1l-sheet1.kicad_sch
Title: Sequencer-Logic-Prod-V2.1l sheet 1

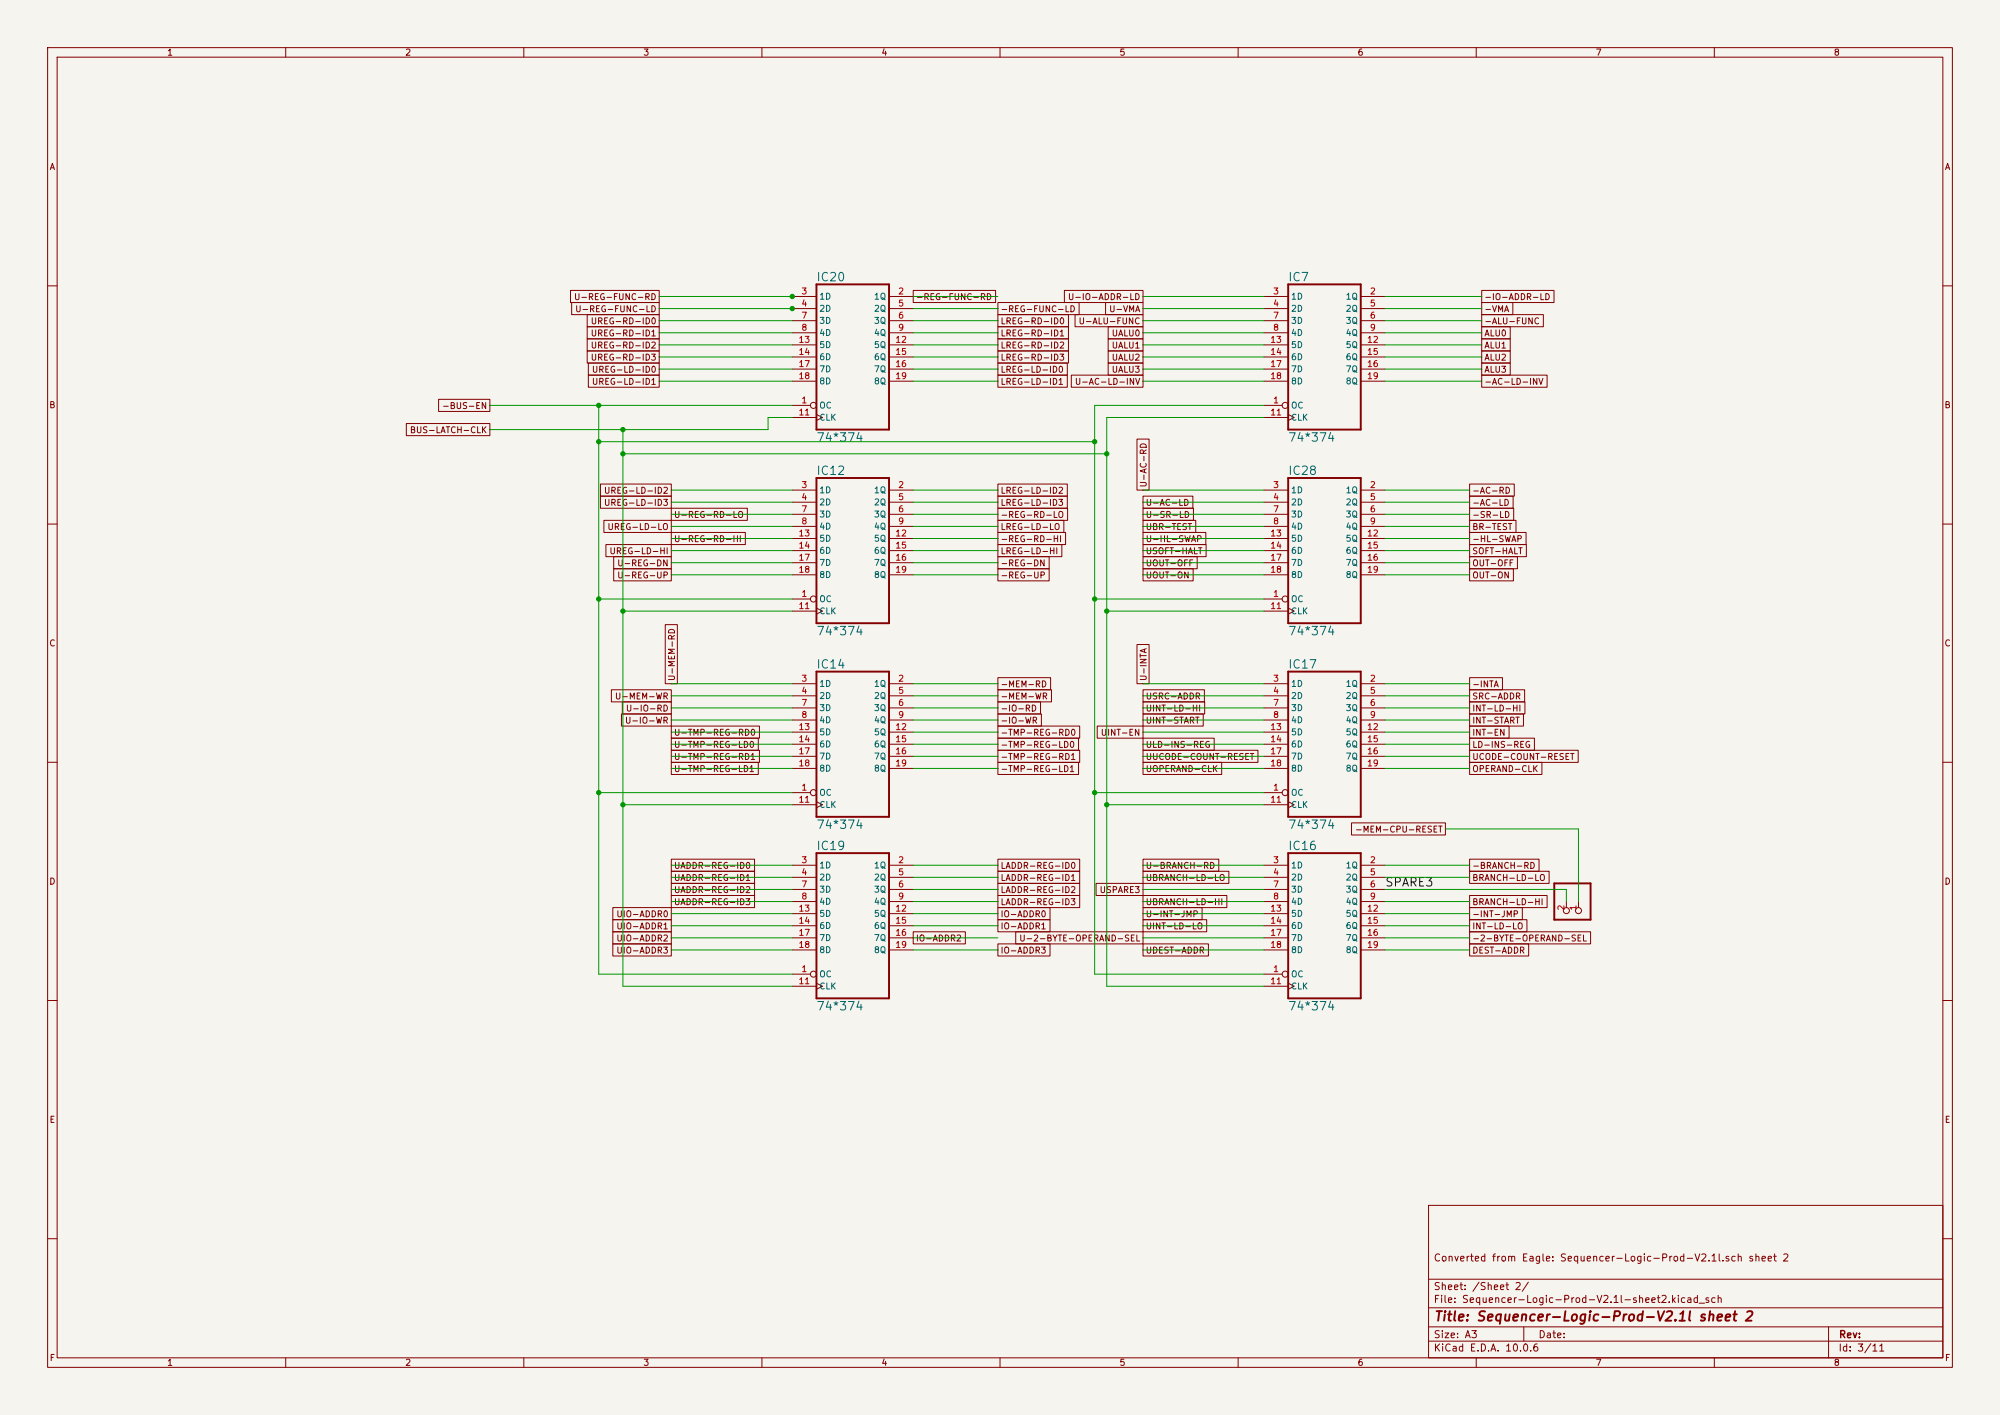
[picture p170: page 3]

LD-INS-REG -AC-LD-INV

SRC-ADDR OPERAND-CLK -SR-LD
BR-TEST -HL-SWAP
SOFT-HALT OUT-OFF OUT-ON -INTA

ULD-INS-REG UUCODE-COUNT-RESET UOPERAND-CLK -BUS-EN

UBRANCH-LD-HI U-INT-JMP UDEST-ADDR -TMP-REG-LD0

IO-ADDR2 UADDR-REG-ID3 UADDR-REG-ID2 UADDR-REG-ID1 UADDR-REG-ID0 UIO-ADDR1 UIO-ADDR0

BRANCH-LD-LO -BRANCH-RD -INT-JMP

BRANCH-LD-HI DEST-ADDR

INT-LD-LO -2-BYTE-OPERAND-SEL

Converted from Eagle: Sequencer-Logic-Prod-V2.1l.sch sheet 2

Sheet: /Sheet 2/
File: Sequencer-Logic-Prod-V2.1l-sheet2.kicad_sch
Title: Sequencer-Logic-Prod-V2.1l sheet 2

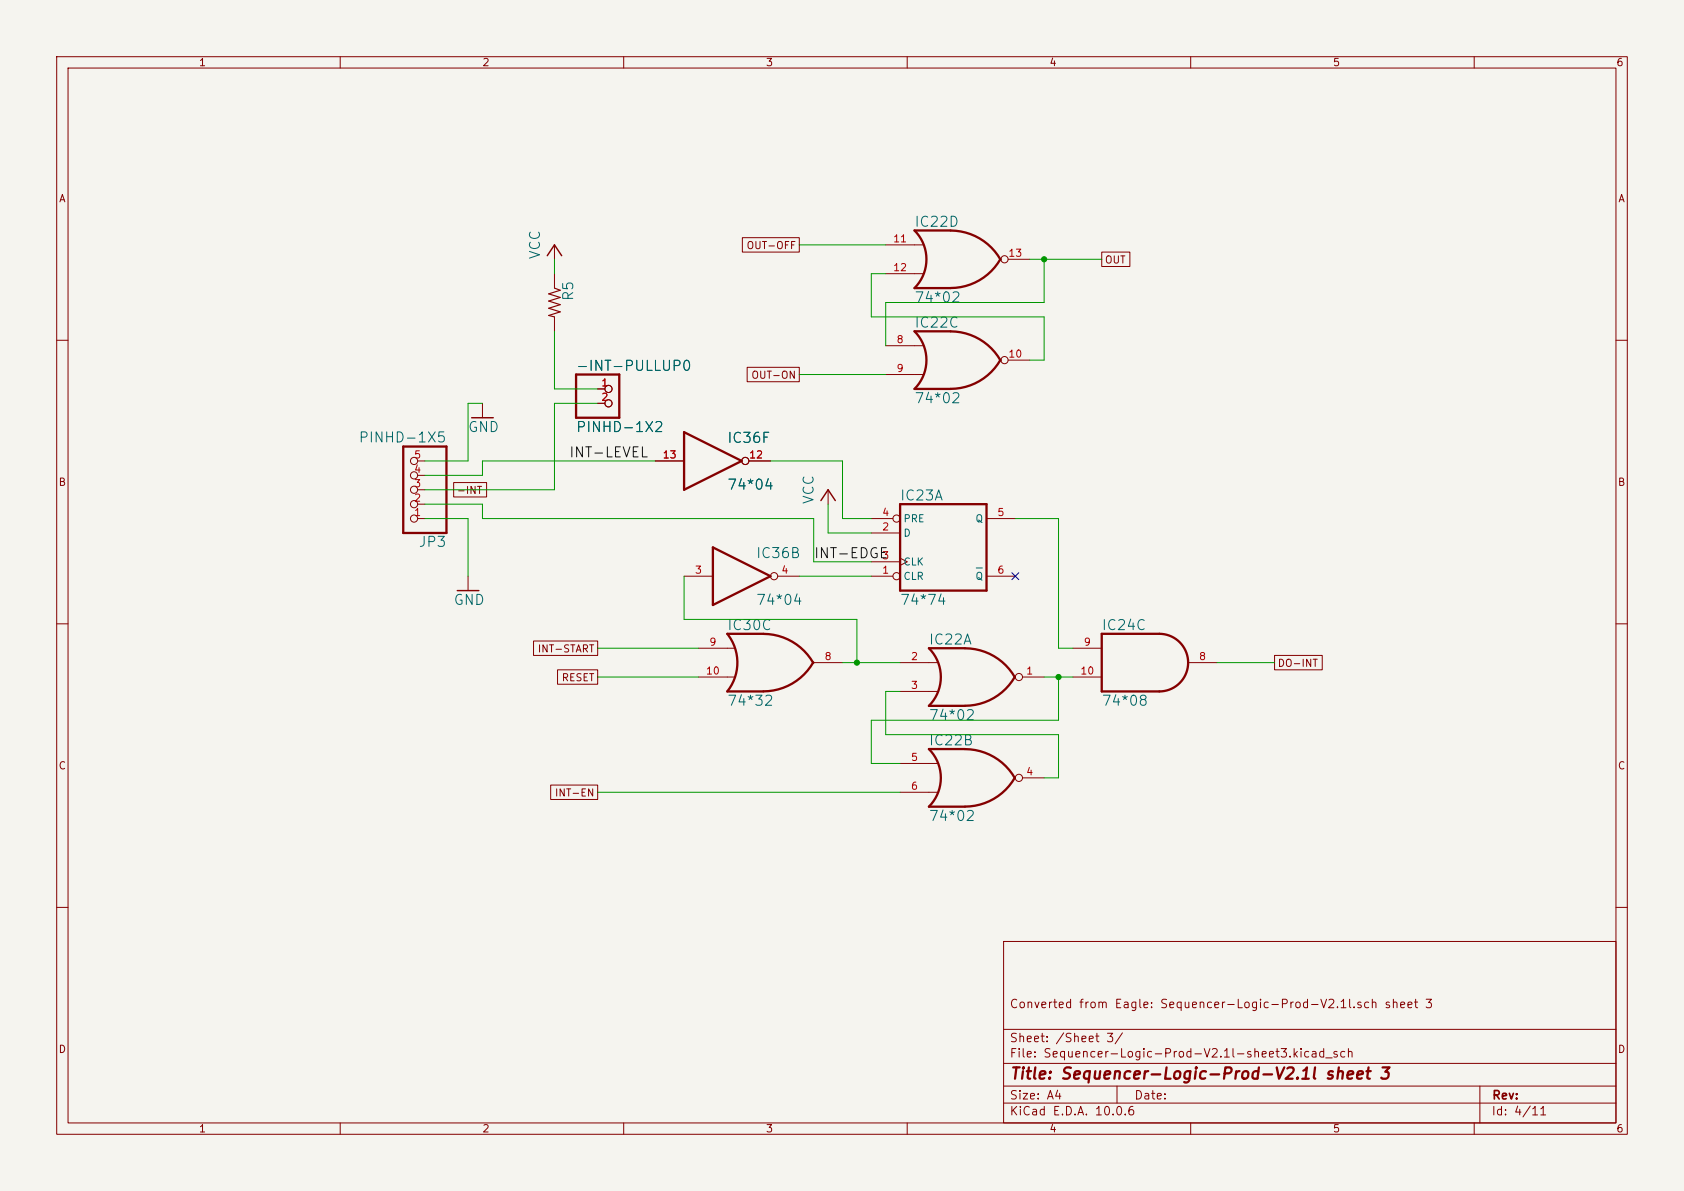
[picture p171: page 4]

Converted from Eagle: Sequencer-Logic-Prod-V2.1l.sch sheet 3

Sheet: /Sheet 3/
File: Sequencer-Logic-Prod-V2.1l-sheet3.kicad_sch
Title: Sequencer-Logic-Prod-V2.1l sheet 3

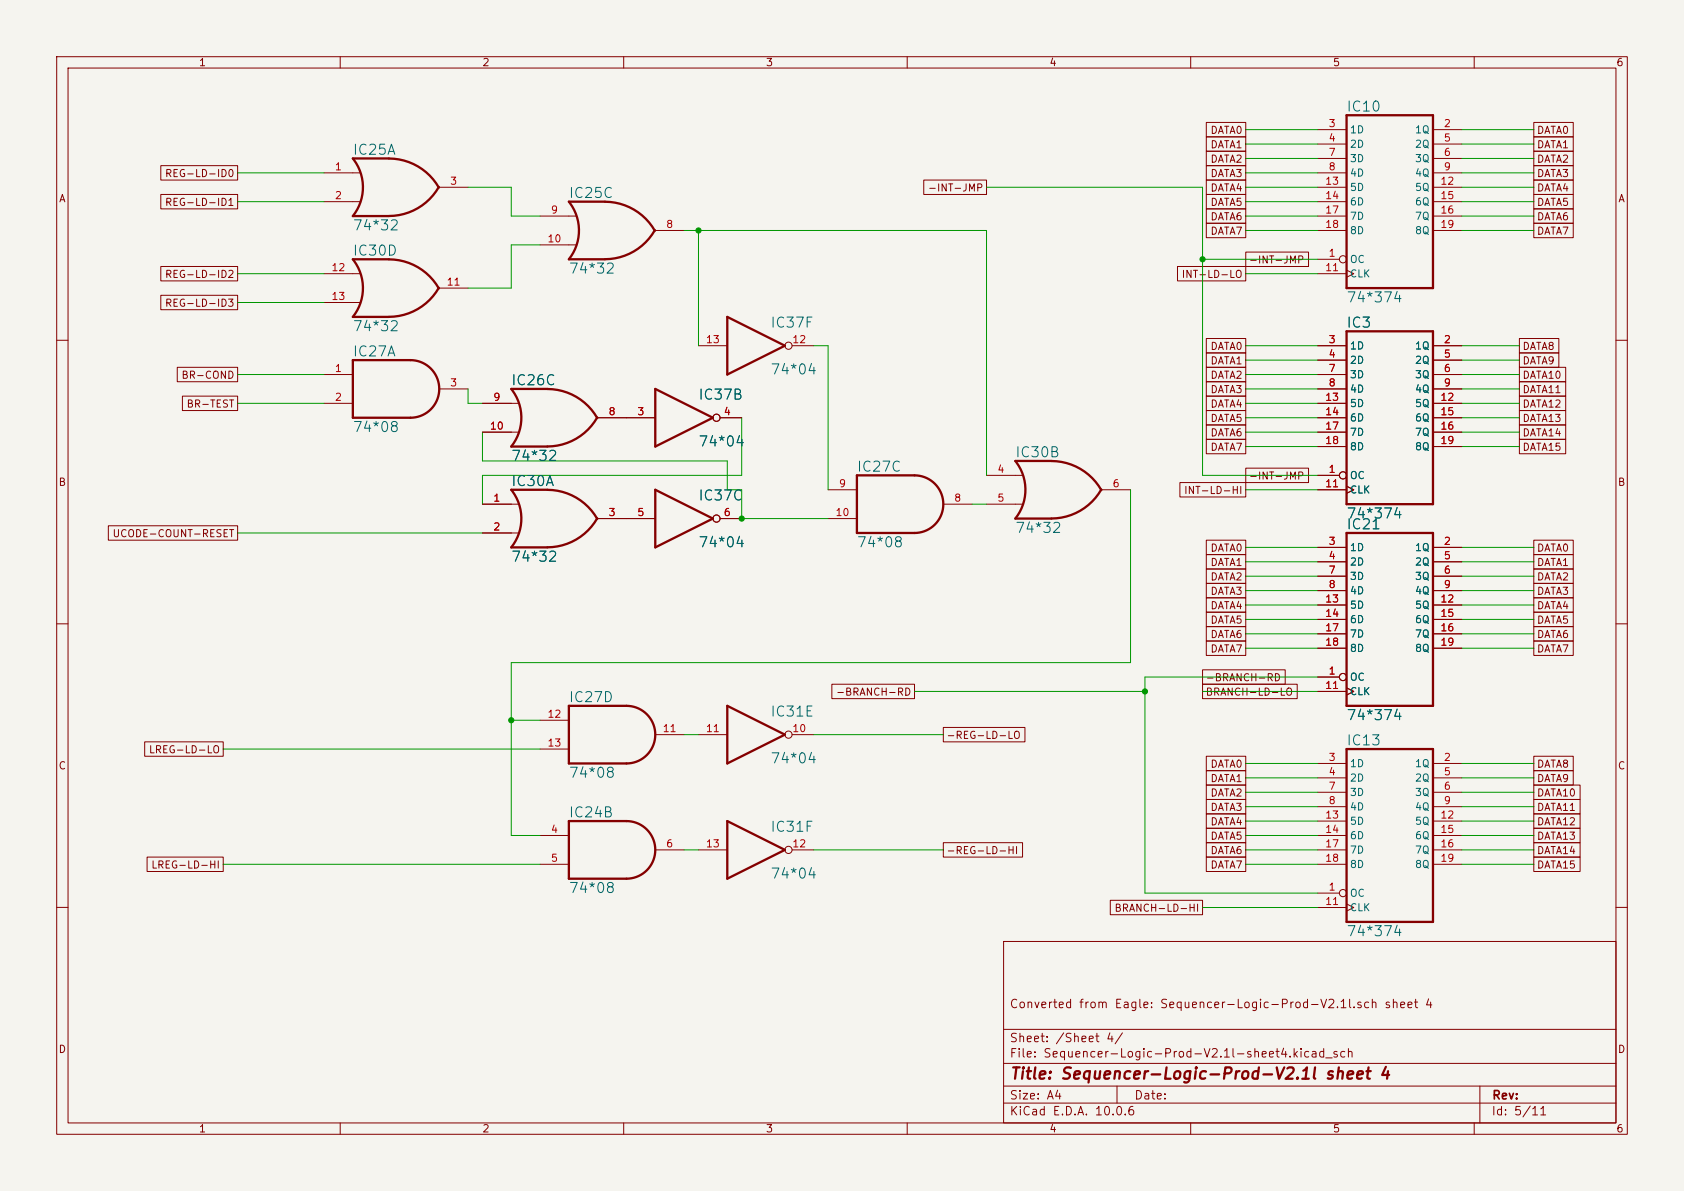
[picture p172: page 5]

Sheet: /Sheet 4/
File: Sequencer-Logic-Prod-V2.1l-sheet4.kicad_sch
Title: Sequencer-Logic-Prod-V2.1l sheet 4

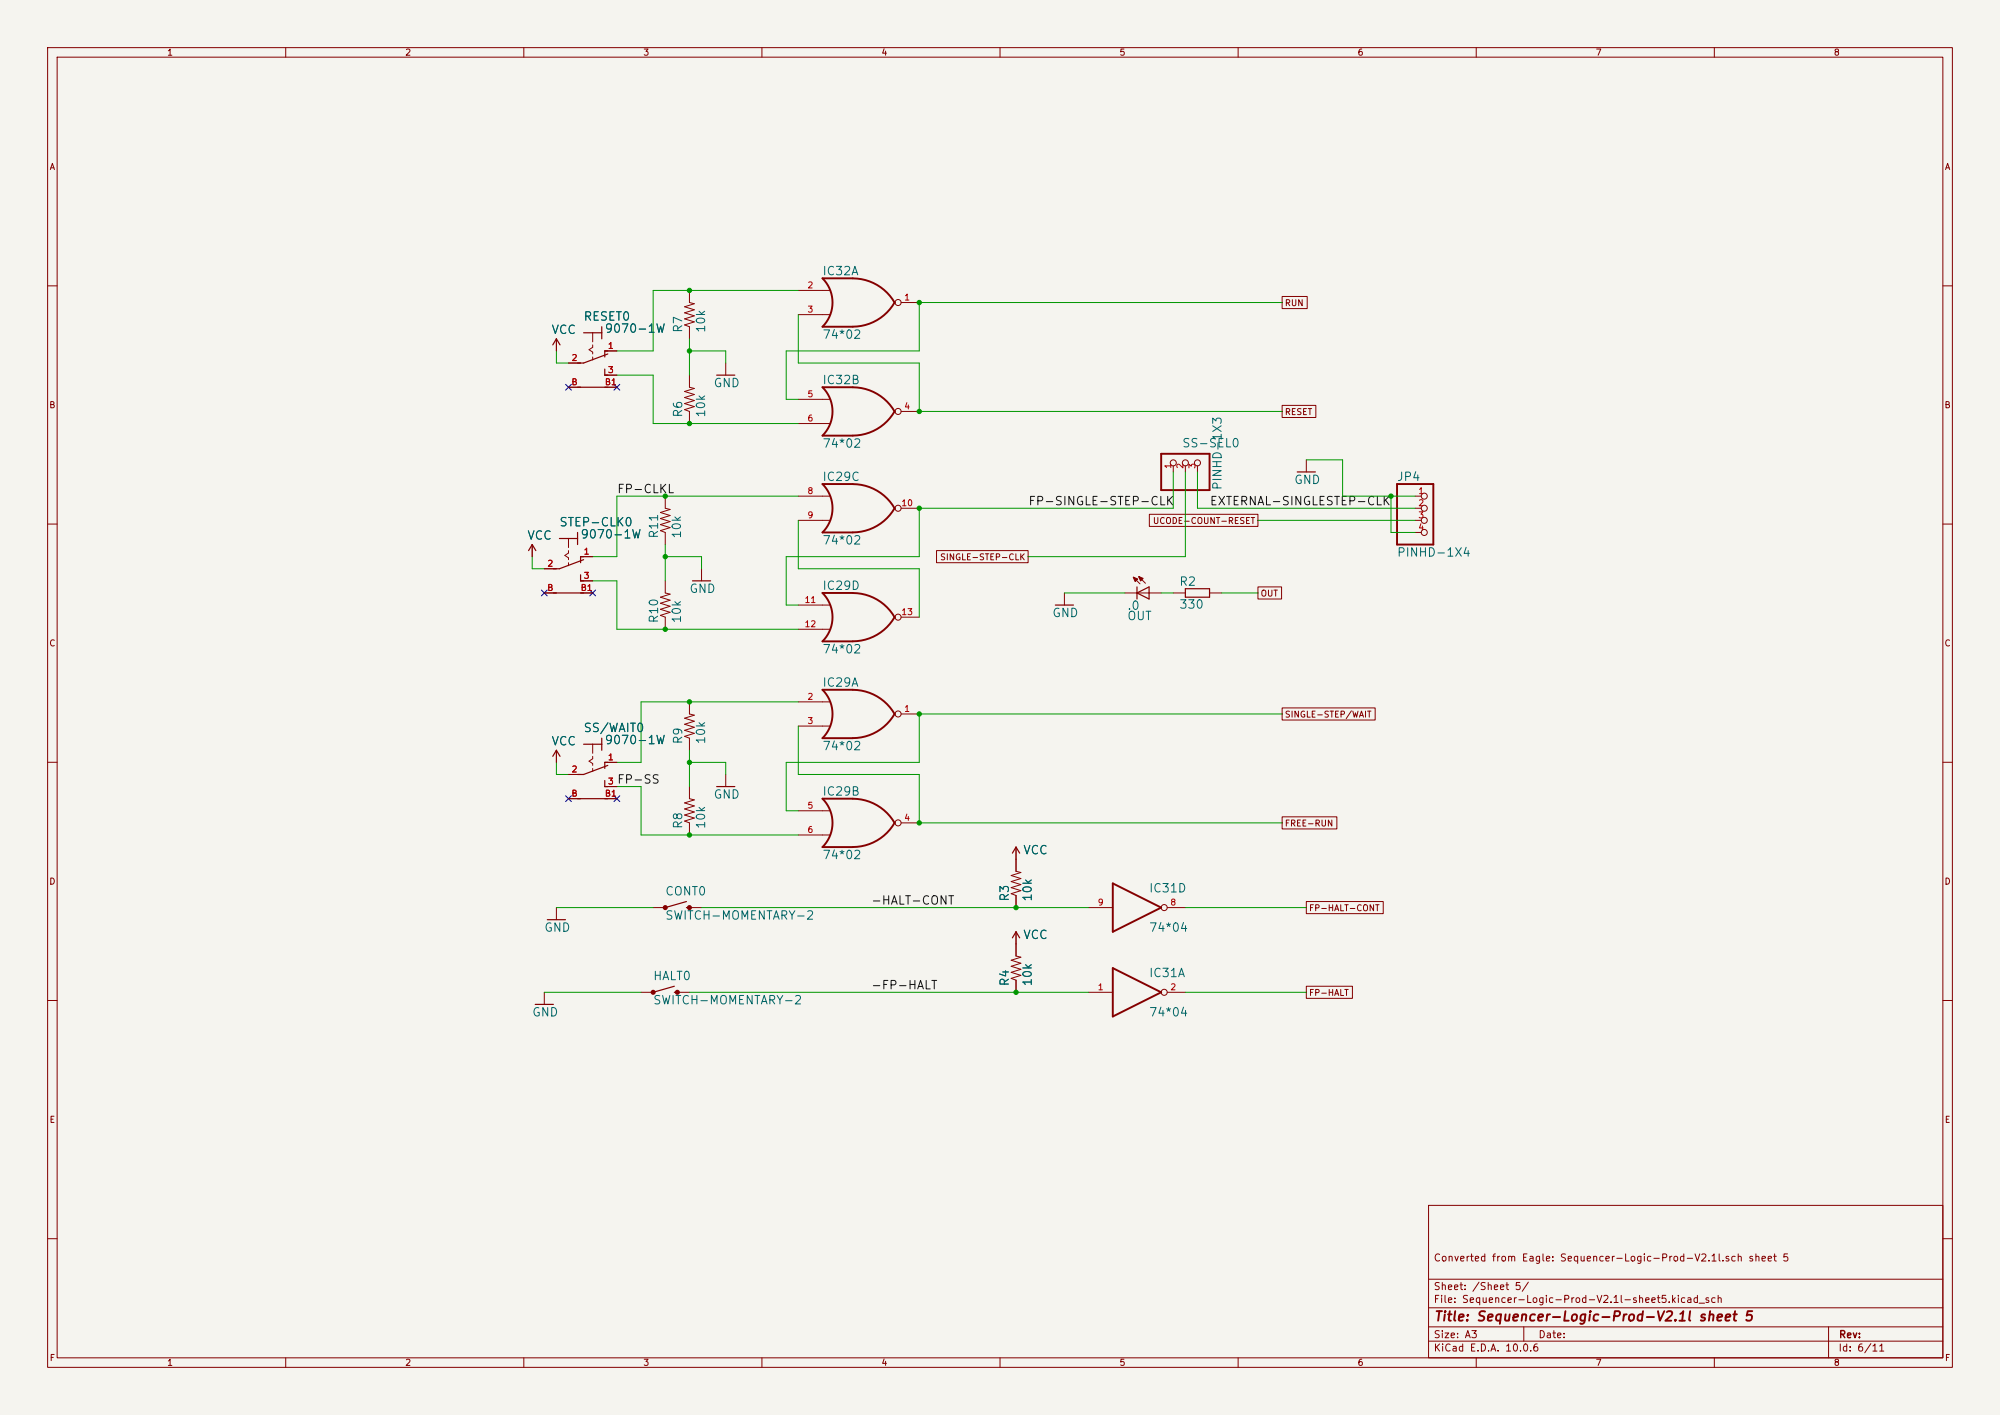
[picture p173: page 6]

RUN
RESET OUT SINGLE-STEP/WAIT

Converted from Eagle: Sequencer-Logic-Prod-V2.1l.sch sheet 5

Sheet: /Sheet 5/
File: Sequencer-Logic-Prod-V2.1l-sheet5.kicad_sch
Title: Sequencer-Logic-Prod-V2.1l sheet 5

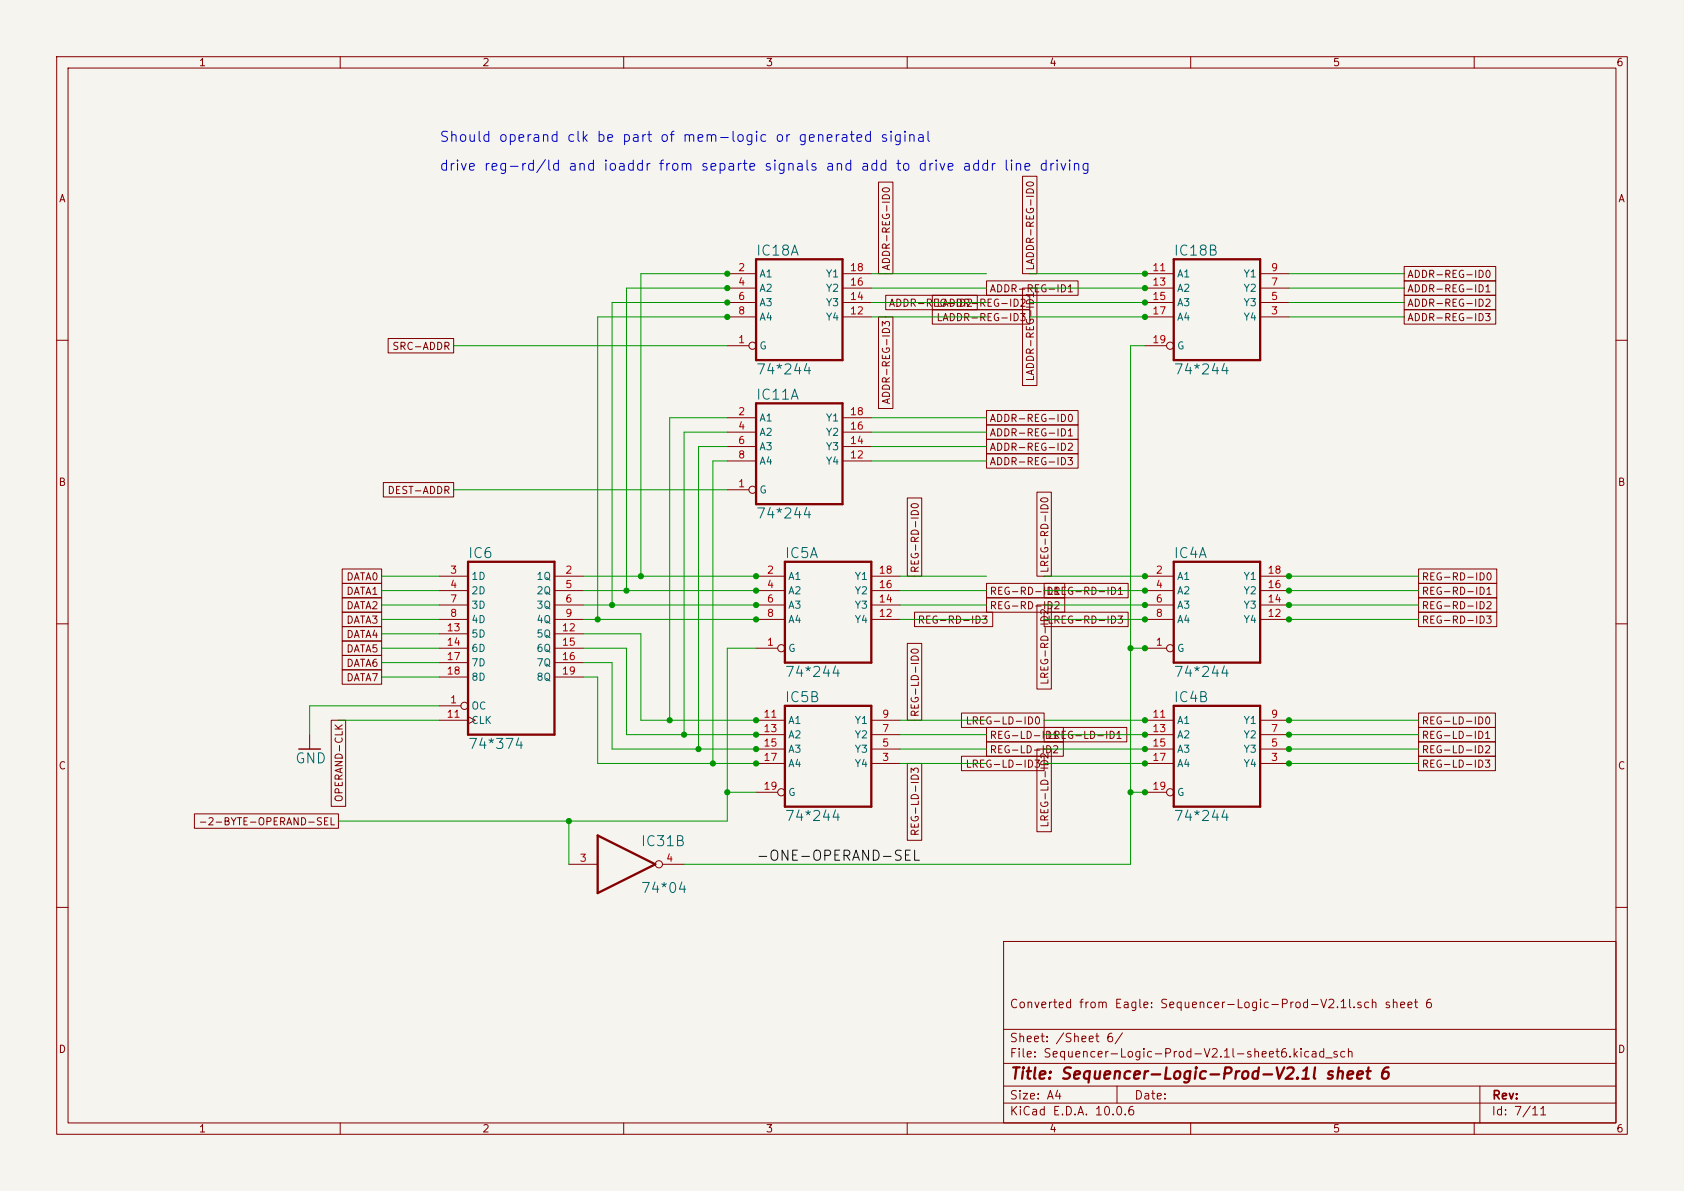
[picture p174: page 7]

Should operand clk be part of mem-logic or generated siginal

drive reg-rd/ld and ioaddr from separte signals and add to drive addr line driving
ADDR-REG-ID3 LREG-RD-ID2 REG-RD-ID3 REG-LD-ID3

ADDR-REG-ID0
ADDR-REG-ID1
ADDR-REG-ID2 REG-RD-ID1LREG-RD-ID1 REG-RD-ID2

DEST-ADDR -2-BYTE-OPERAND-SEL DATA7

LREG-LD-ID0 REG-LD-ID2 REG-LD-ID1

LREG-LD-ID1 LREG-LD-ID2

Converted from Eagle: Sequencer-Logic-Prod-V2.1l.sch sheet 6

Sheet: /Sheet 6/
File: Sequencer-Logic-Prod-V2.1l-sheet6.kicad_sch
Title: Sequencer-Logic-Prod-V2.1l sheet 6

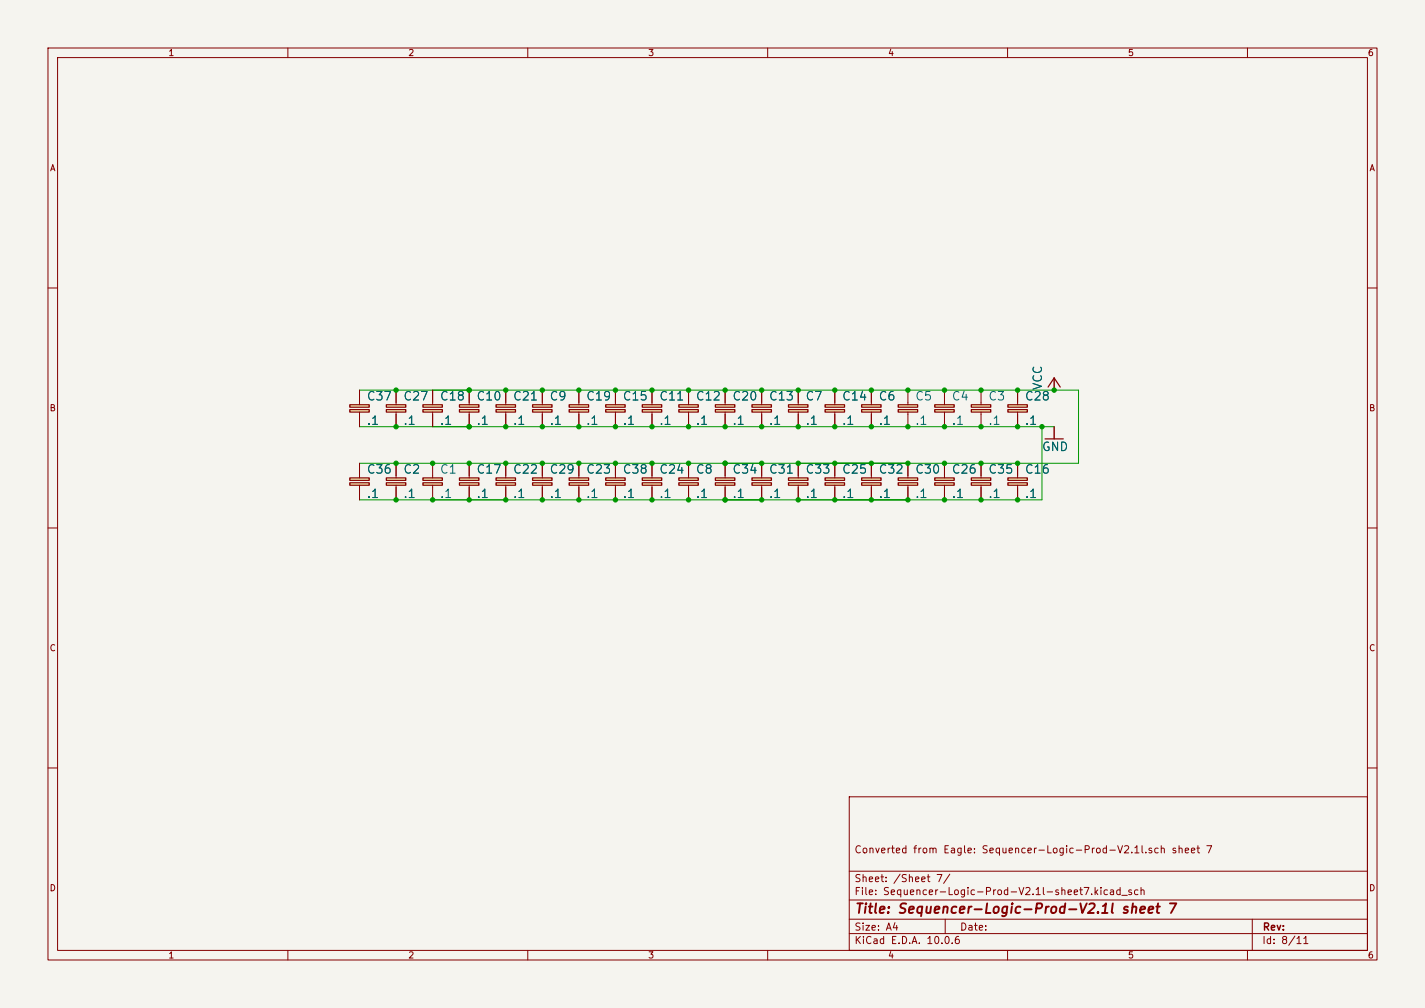
[picture p175: page 8]

Converted from Eagle: Sequencer-Logic-Prod-V2.1l.sch sheet 7

Sheet: /Sheet 7/
File: Sequencer-Logic-Prod-V2.1l-sheet7.kicad_sch
Title: Sequencer-Logic-Prod-V2.1l sheet 7

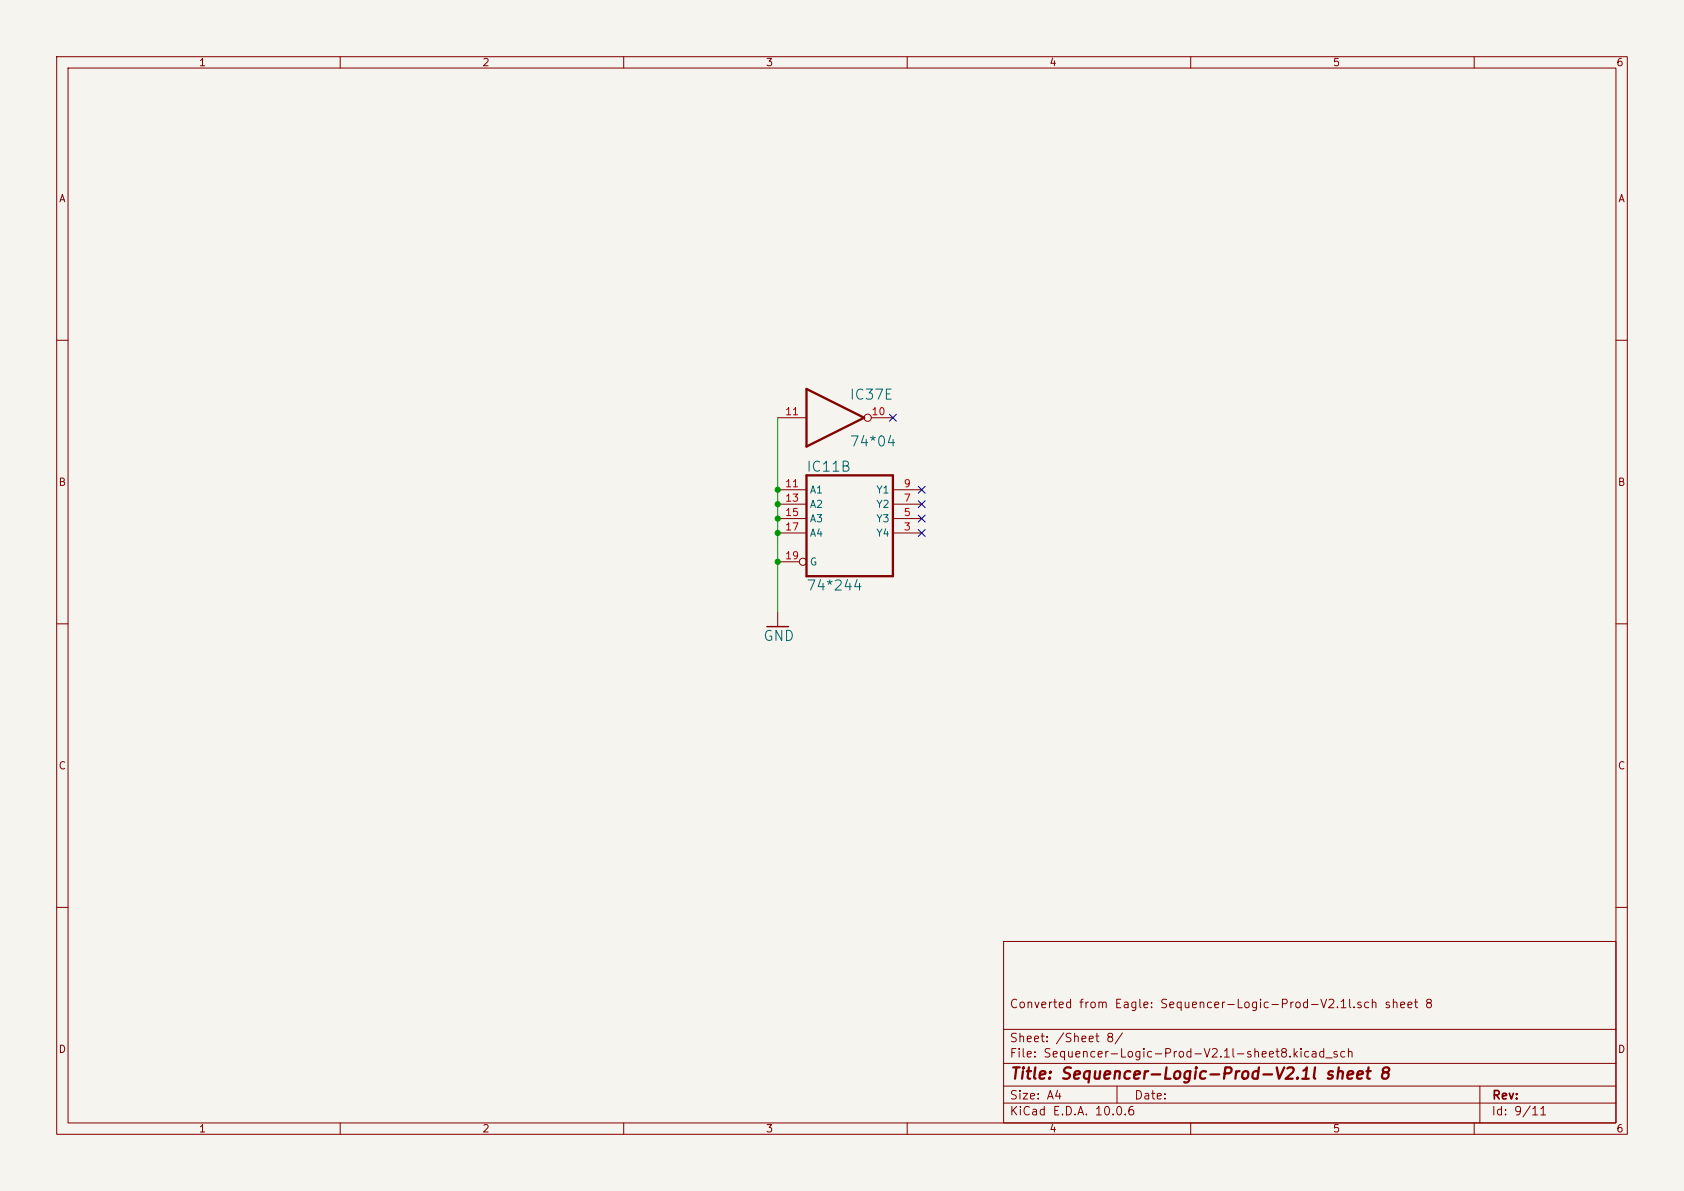
[picture p176: page 9]

Converted from Eagle: Sequencer-Logic-Prod-V2.1l.sch sheet 8

Sheet: /Sheet 8/
File: Sequencer-Logic-Prod-V2.1l-sheet8.kicad_sch
Title: Sequencer-Logic-Prod-V2.1l sheet 8

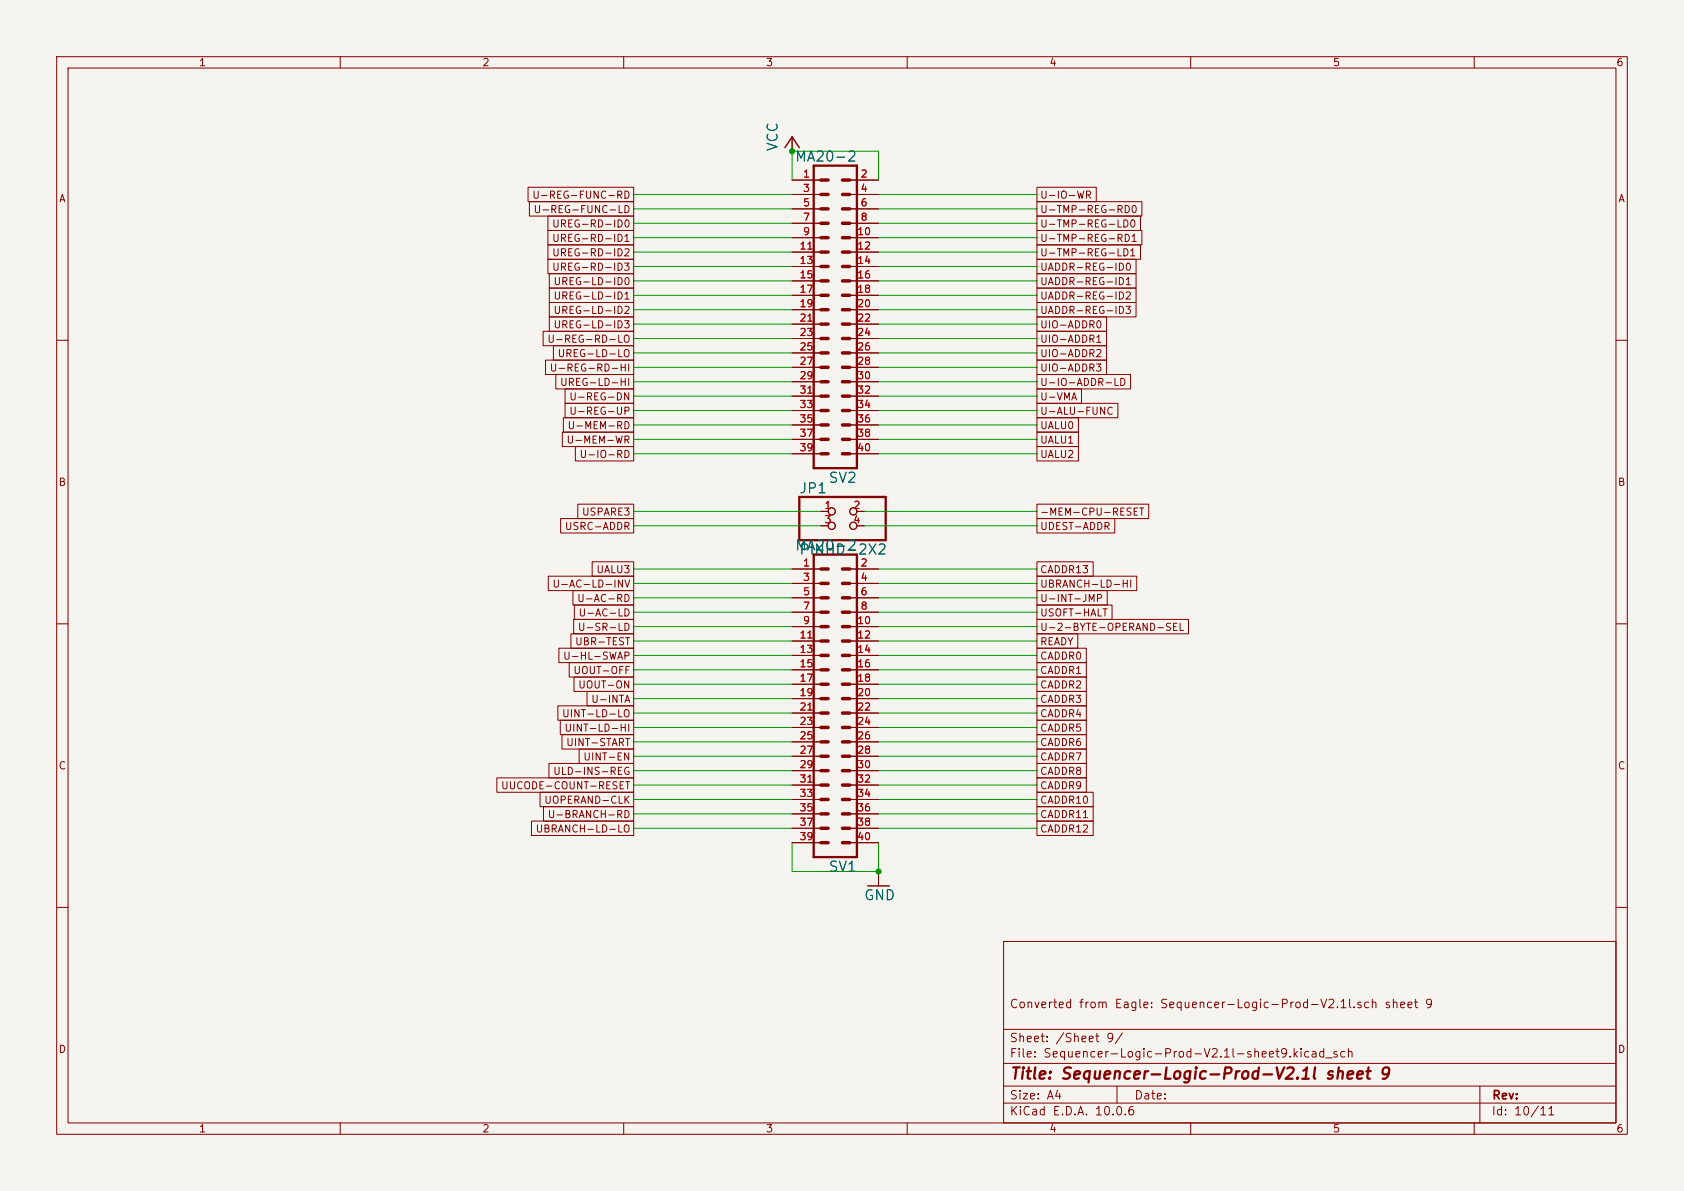
[picture p177: page 10]

UINT-START UINT-LD-HI USRC-ADDR U-SR-LD U-AC-LD U-AC-RD U-AC-LD-INV UBR-TEST UALU3 USPARE3 U-REG-FUNC-LD U-IO-RD U-MEM-WR U-MEM-RD U-REG-UP U-REG-DN
UREG-RD-ID1 U-BRANCH-RD UOPERAND-CLK UUCODE-COUNT-RESET ULD-INS-REG UINT-EN

U-REG-RD-LO
UREG-LD-HI U-REG-RD-HI UREG-LD-LO

U-INTA U-HL-SWAP UBRANCH-LD-LO

UOUT-OFF UOUT-ON

Converted from Eagle: Sequencer-Logic-Prod-V2.1l.sch sheet 9

Sheet: /Sheet 9/
File: Sequencer-Logic-Prod-V2.1l-sheet9.kicad_sch
Title: Sequencer-Logic-Prod-V2.1l sheet 9

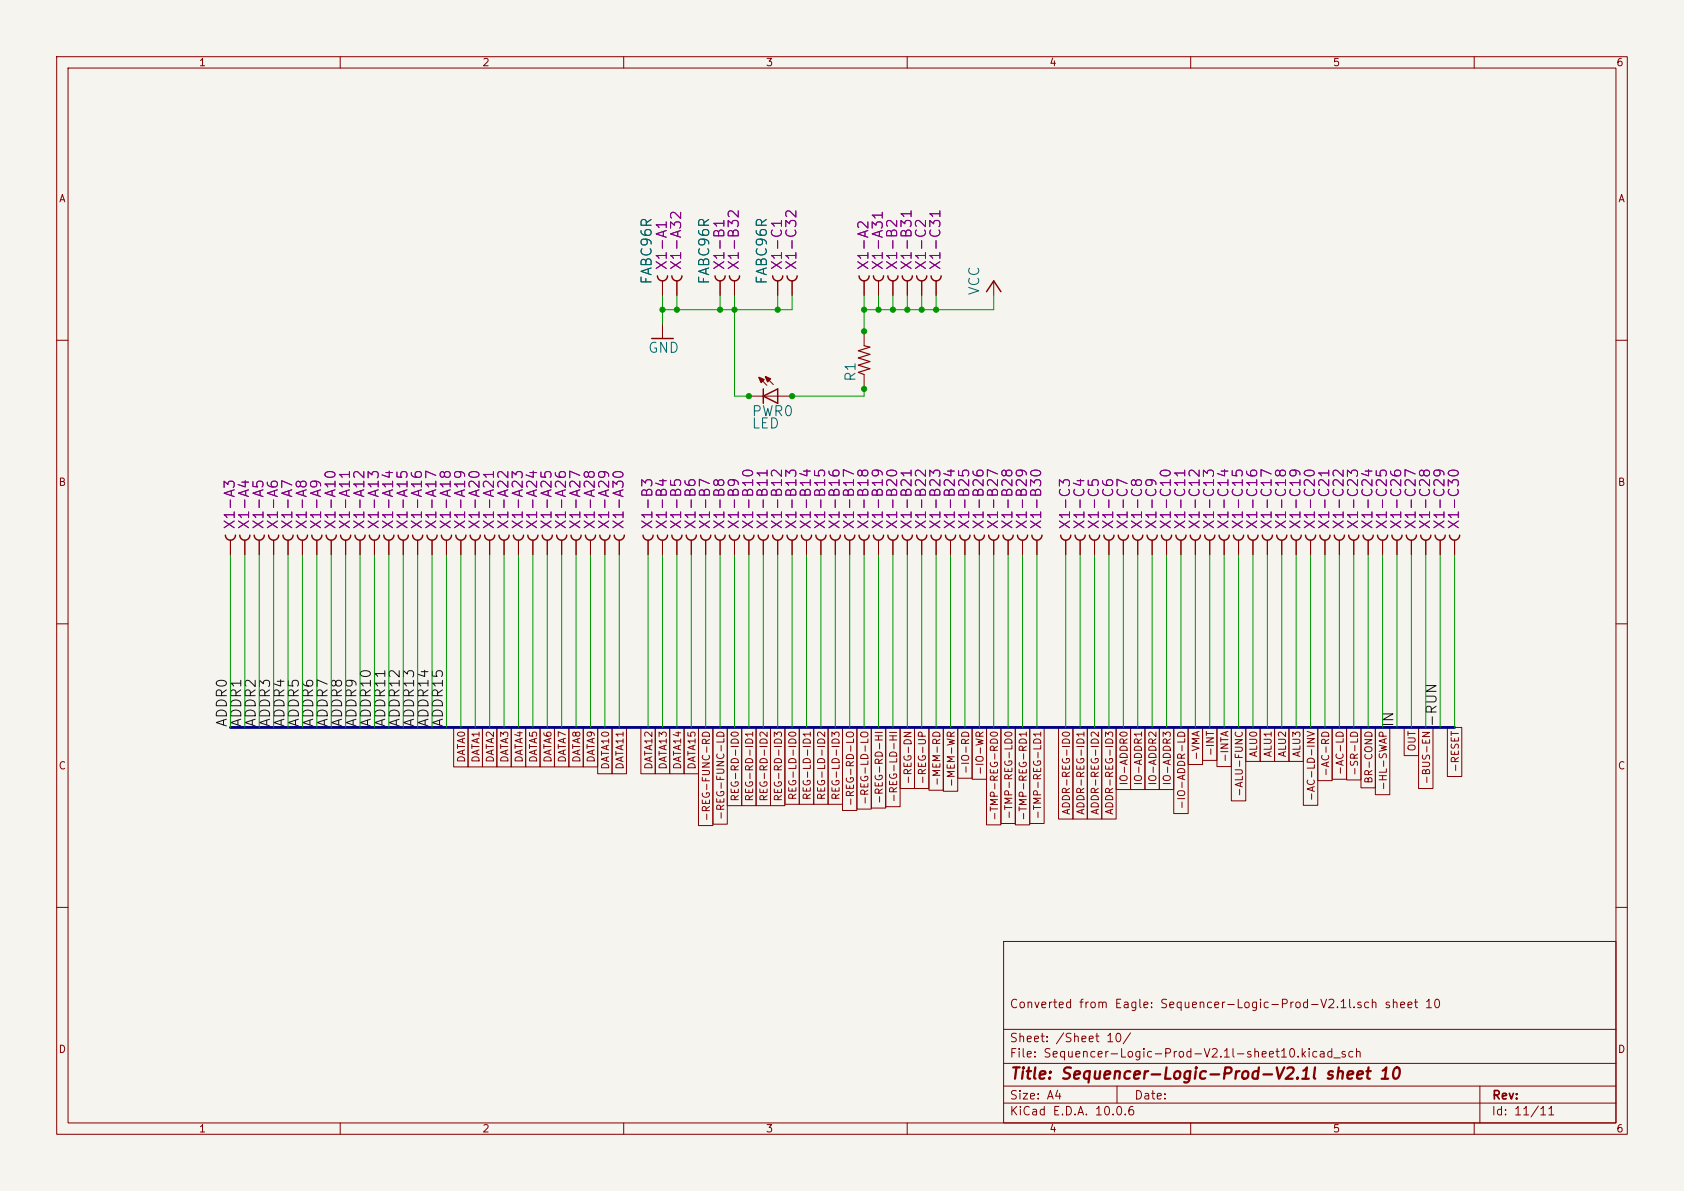
[picture p178: page 11]

Sheet: /Sheet 10/
File: Sequencer-Logic-Prod-V2.1l-sheet10.kicad_sch
Title: Sequencer-Logic-Prod-V2.1l sheet 10
