ksr/YACC1-D/hardware/cards/sequencer-memory/accessories/eeprom-adaptor/pdf/eeprom adaptor-schematic.pdf

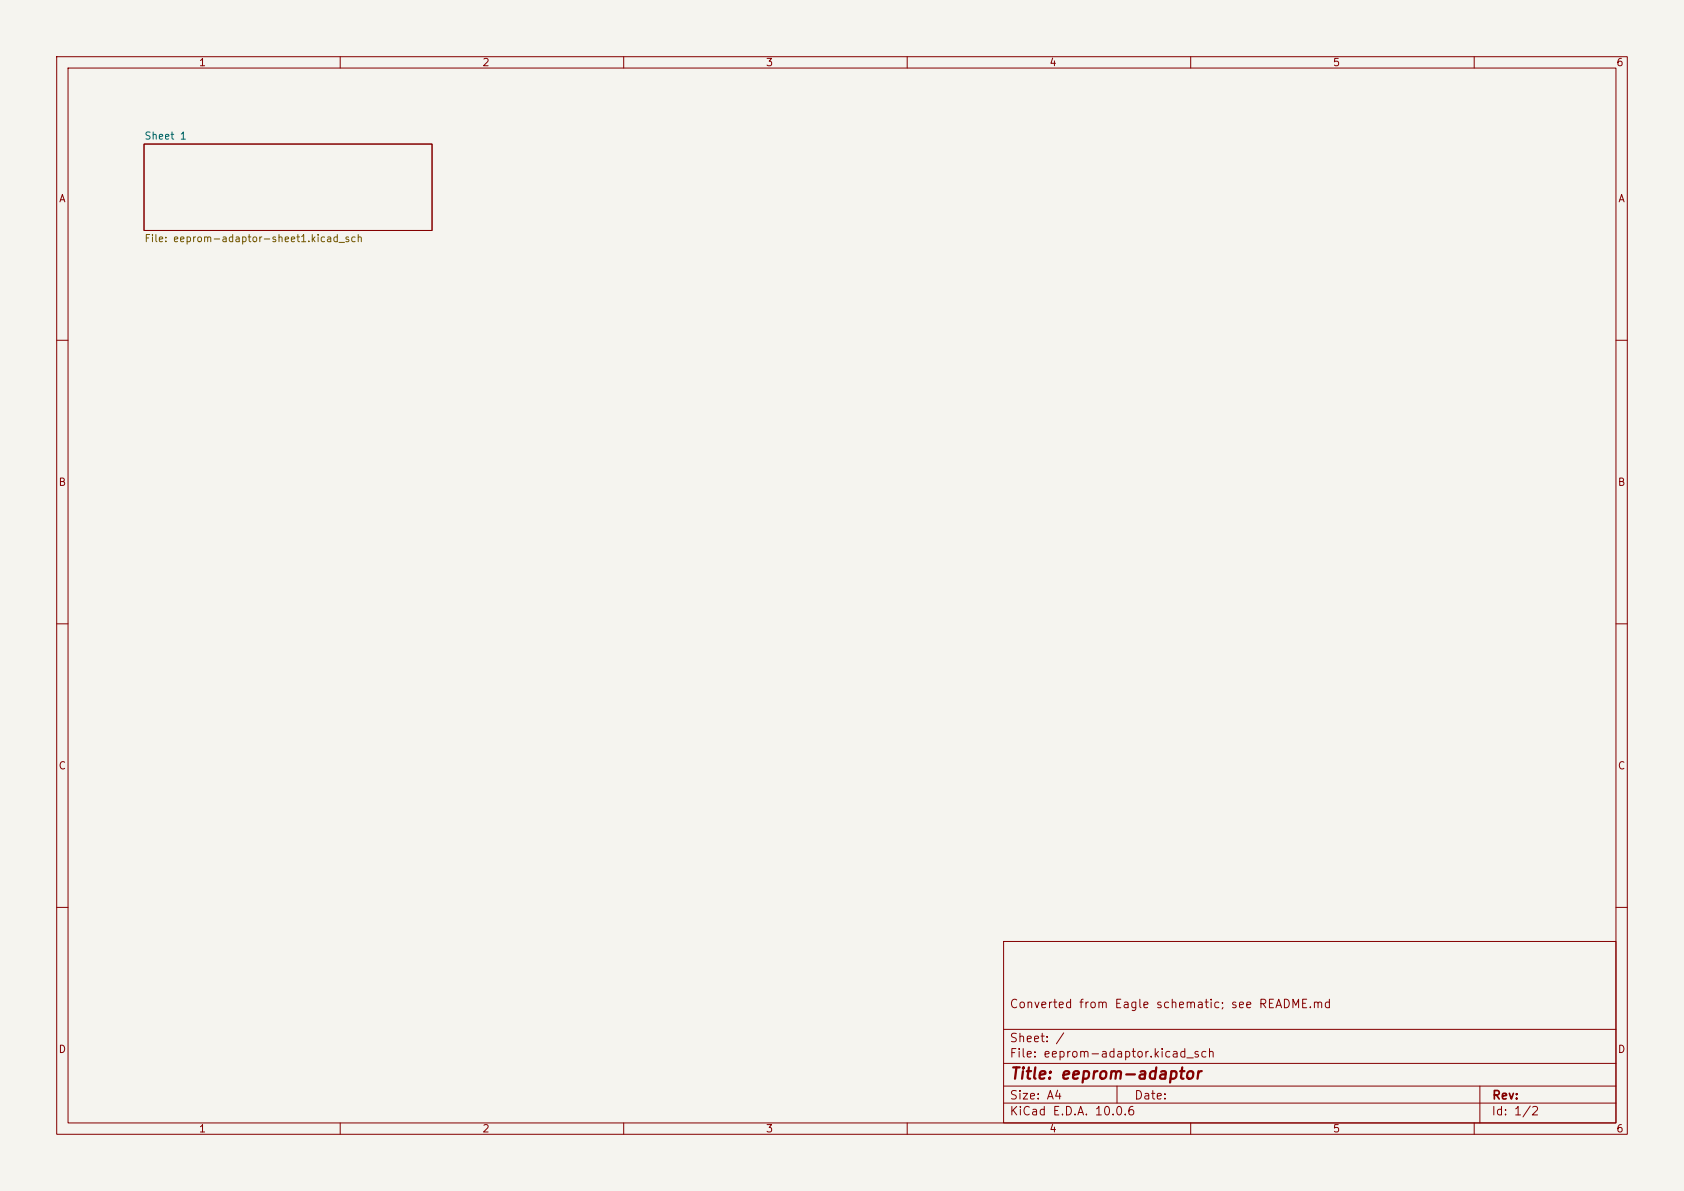
[picture p190: page 1]

Converted from Eagle schematic; see README.md

Size: A4 | Rev:
KiCad E.D.A. 10.0.6 | Id: 1/2

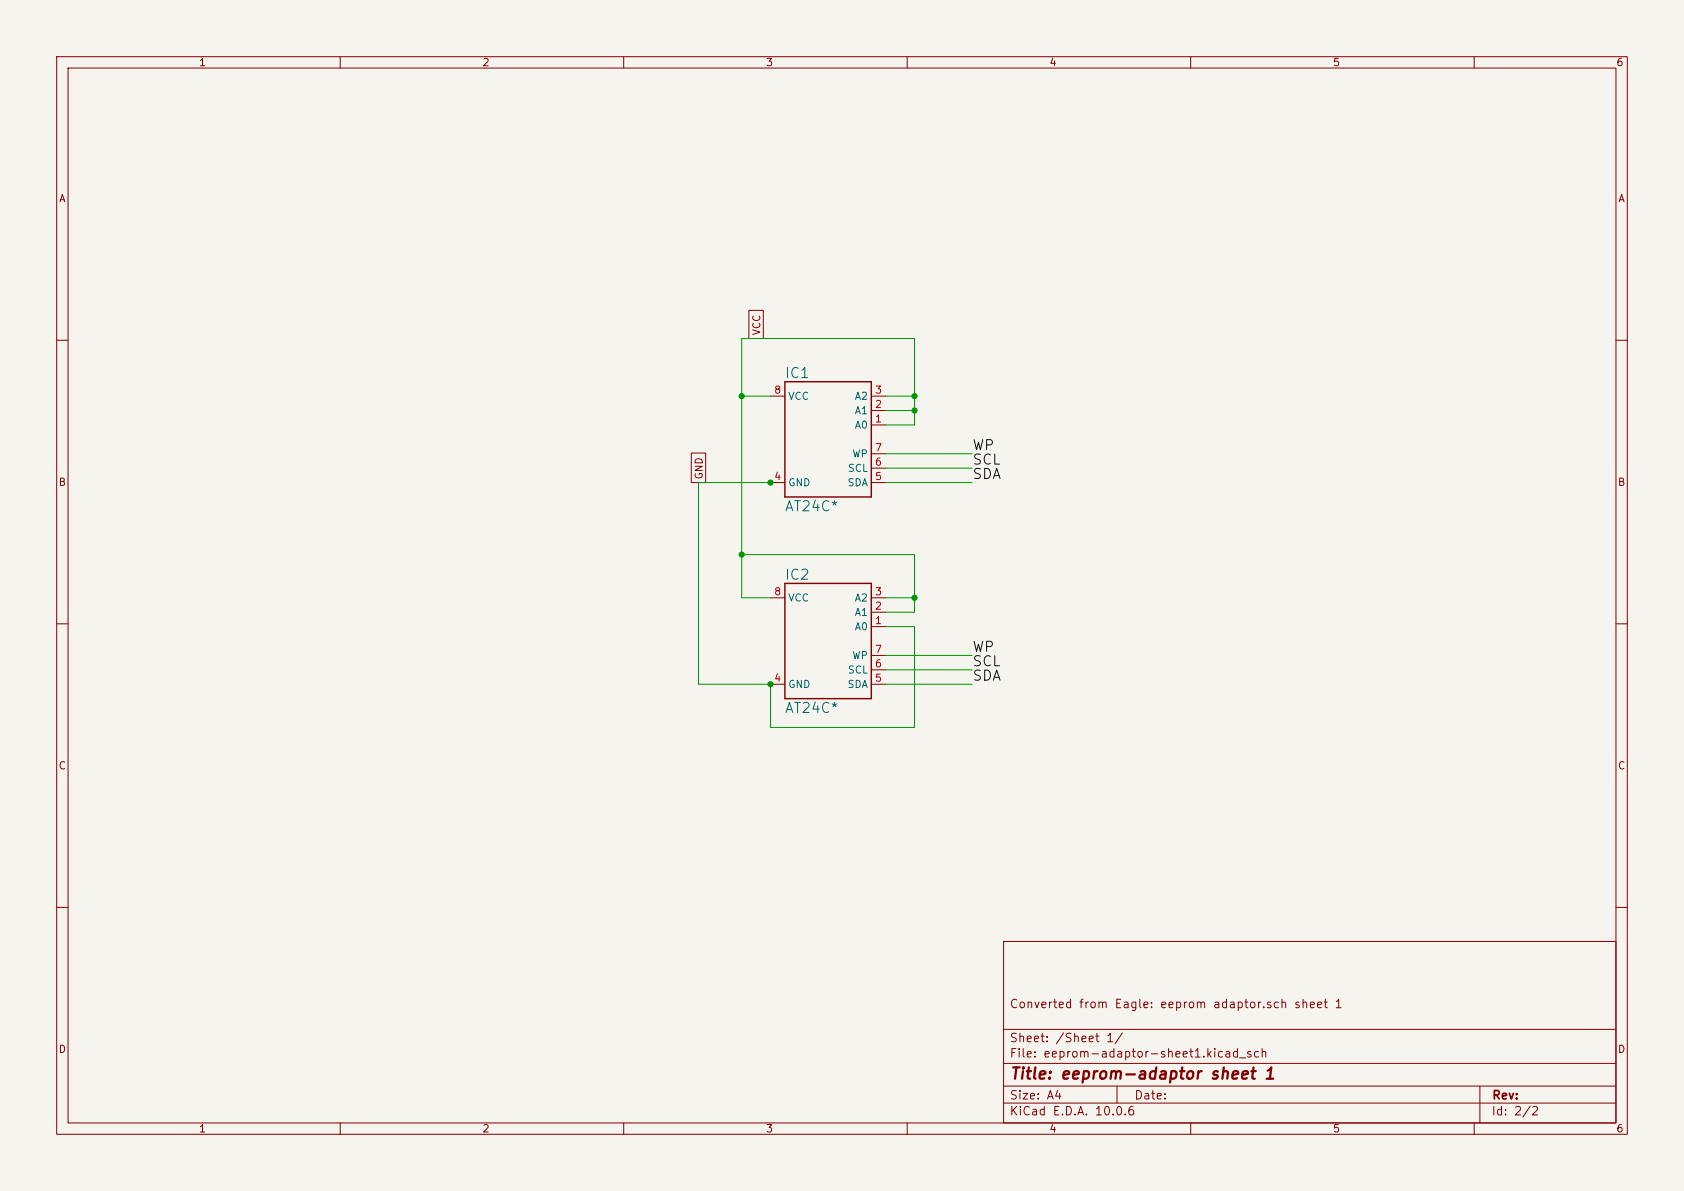
[picture p191: page 2]

Converted from Eagle: eeprom adaptor.sch sheet 1

Sheet: /Sheet 1/
File: eeprom-adaptor-sheet1.kicad_sch
Title: eeprom-adaptor sheet 1

Size: A4 | Rev:
KiCad E.D.A. 10.0.6 | Id: 2/2
