ksr/YACC1-D/hardware/cards/sequencer-memory/eagle/v2.1/pdf/Sequencer-Memory-V2.1-schematic.pdf

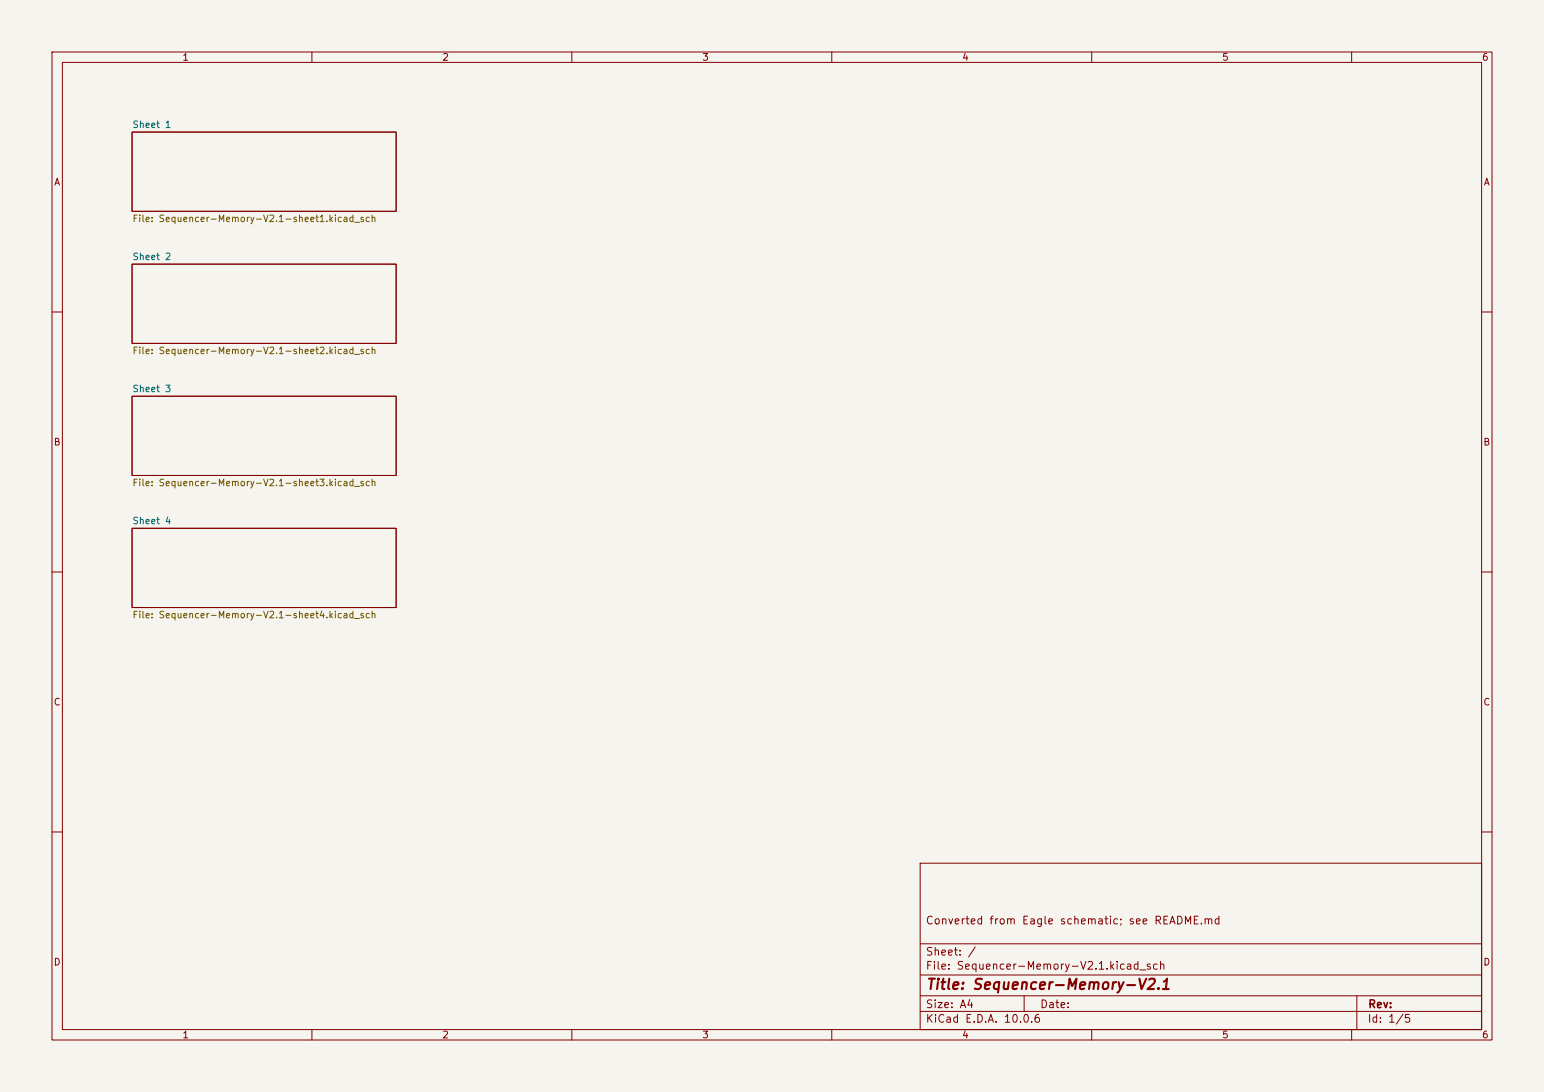
[picture p192: page 1]

File: Sequencer-Memory-V2.1-sheet1.kicad_sch Sheet 2

File: Sequencer-Memory-V2.1-sheet2.kicad_sch Sheet 3

File: Sequencer-Memory-V2.1-sheet3.kicad_sch Sheet 4

Converted from Eagle schematic; see README.md

Size: A4 | Rev:
KiCad E.D.A. 10.0.6 | Id: 1/5

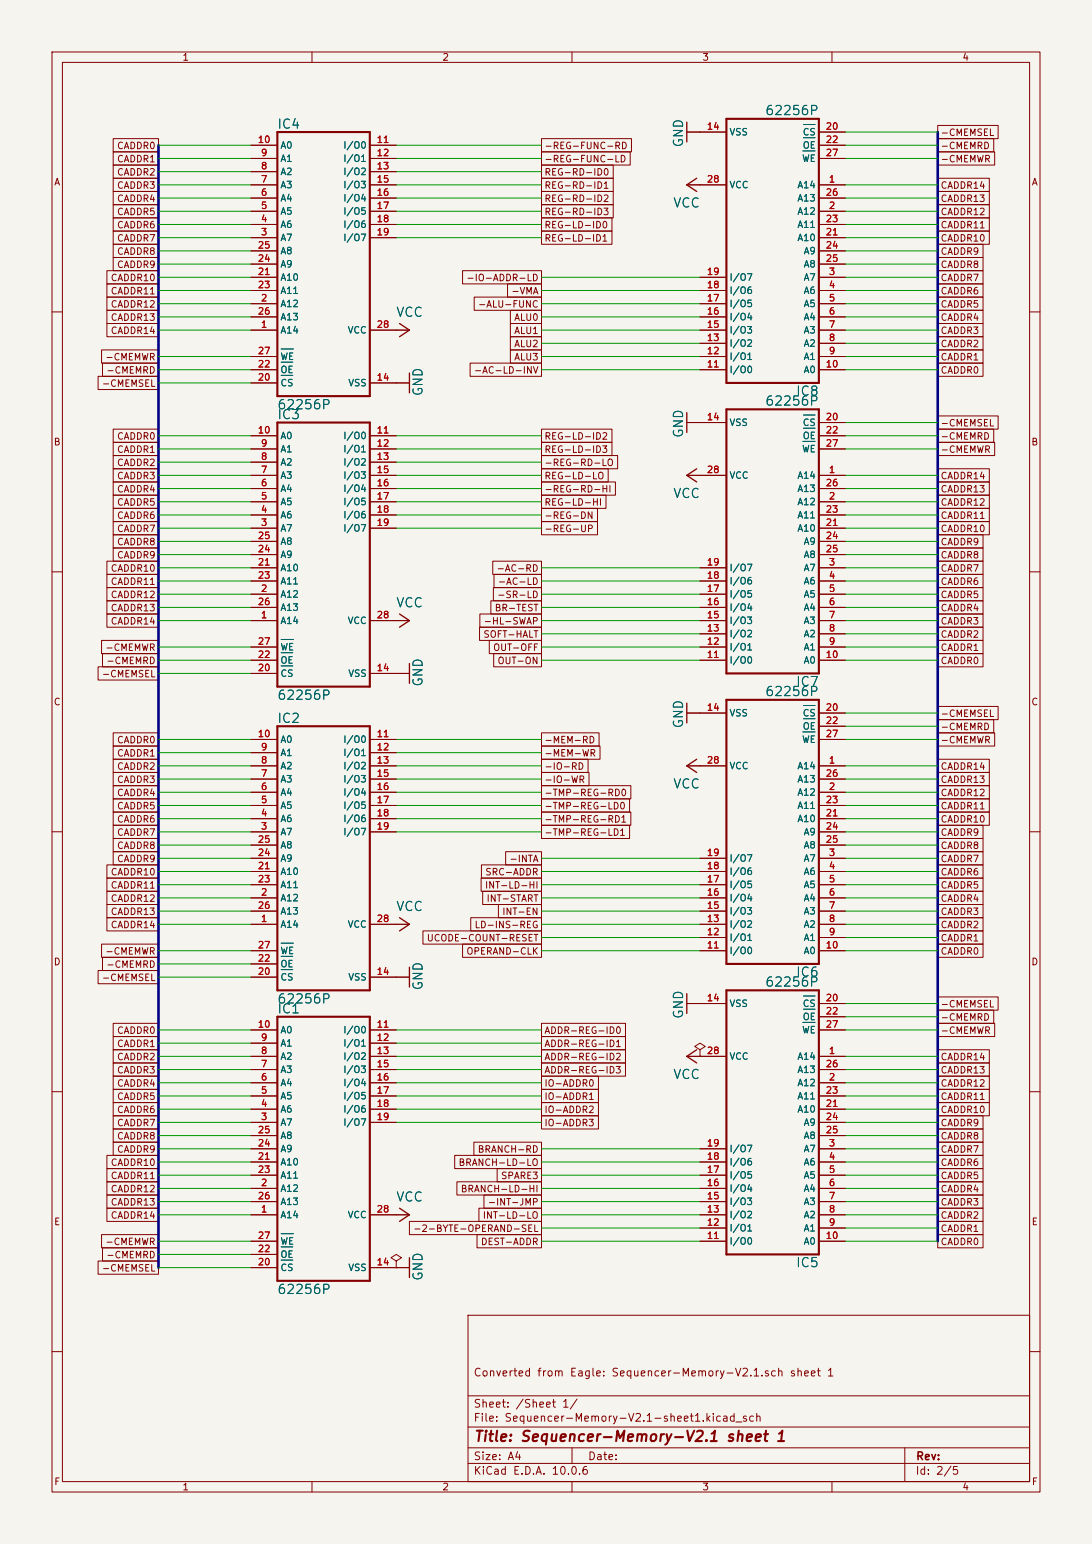
[picture p193: page 2]

REG-LD-HI -REG-RD-HI REG-LD-LO -AC-LD-INV -ALU-FUNC -TMP-REG-RD0 -IO-WR -VMA
VCC GND

VCCGND
REG-RD-ID0 -MEM-RD

REG-LD-ID2 CADDR14 -CMEMSEL -CMEMRD -CMEMWR

REG-LD-ID3 -REG-UP -REG-DN
-REG-RD-LO

-SR-LD -HL-SWAP

LD-INS-REG UCODE-COUNT-RESET OPERAND-CLK

BRANCH-RD
BRANCH-LD-LO
SPARE3 BRANCH-LD-HI -INT-JMP
INT-LD-LO -2-BYTE-OPERAND-SEL DEST-ADDR

Converted from Eagle: Sequencer-Memory-V2.1.sch sheet 1

Sheet: /Sheet 1/
File: Sequencer-Memory-V2.1-sheet1.kicad_sch
Title: Sequencer-Memory-V2.1 sheet 1

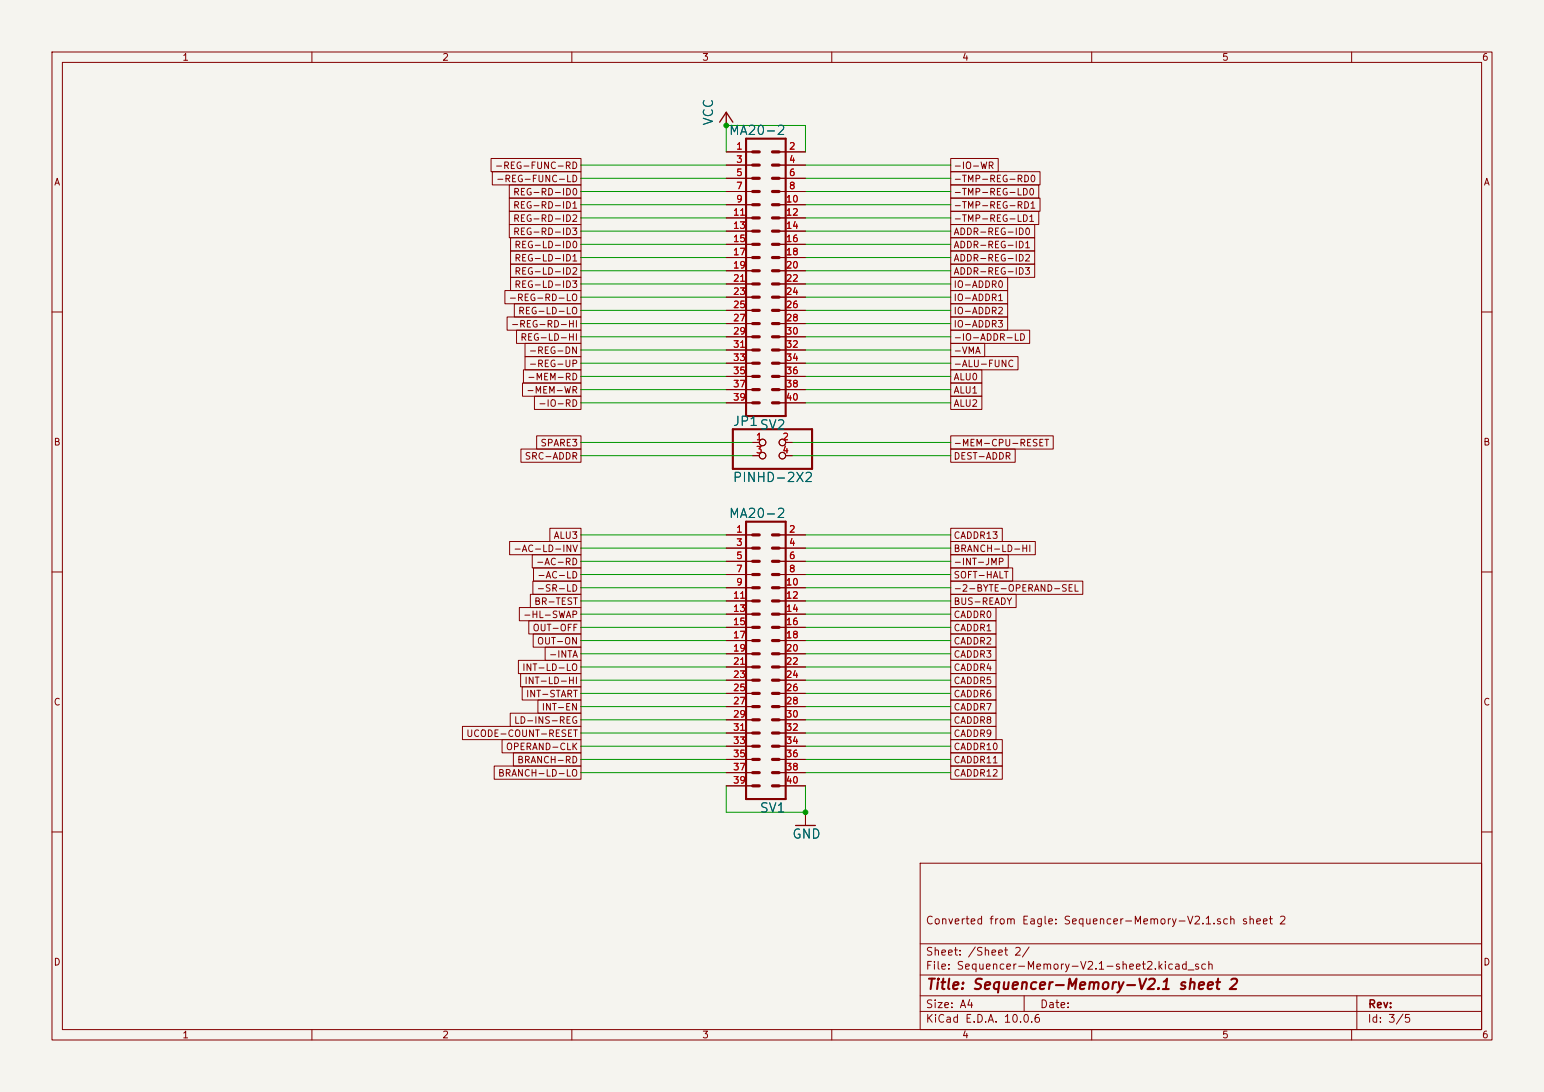
[picture p194: page 3]

ALU2 -VMA -IO-WR -TMP-REG-RD0 -TMP-REG-LD0 -TMP-REG-RD1 -TMP-REG-LD1

CADDR0 -REG-FUNC-RD
REG-LD-ID0 REG-LD-ID3 REG-RD-ID3 REG-RD-ID2 REG-RD-ID1 REG-RD-ID0 -REG-FUNC-LD

ADDR-REG-ID0
ADDR-REG-ID1
ADDR-REG-ID2
ADDR-REG-ID3
IO-ADDR0
IO-ADDR1
IO-ADDR2
IO-ADDR3 -IO-ADDR-LD -ALU-FUNC

REG-LD-ID2 REG-LD-ID1
SRC-ADDR -IO-RD -MEM-WR -REG-RD-HI -MEM-RD -REG-UP -REG-DN

REG-LD-HI REG-LD-LO -REG-RD-LO

BRANCH-LD-HI -MEM-CPU-RESET UCODE-COUNT-RESET LD-INS-REG
INT-LD-HI -SR-LD -AC-LD -AC-RD -AC-LD-INV

Converted from Eagle: Sequencer-Memory-V2.1.sch sheet 2

Sheet: /Sheet 2/
File: Sequencer-Memory-V2.1-sheet2.kicad_sch
Title: Sequencer-Memory-V2.1 sheet 2

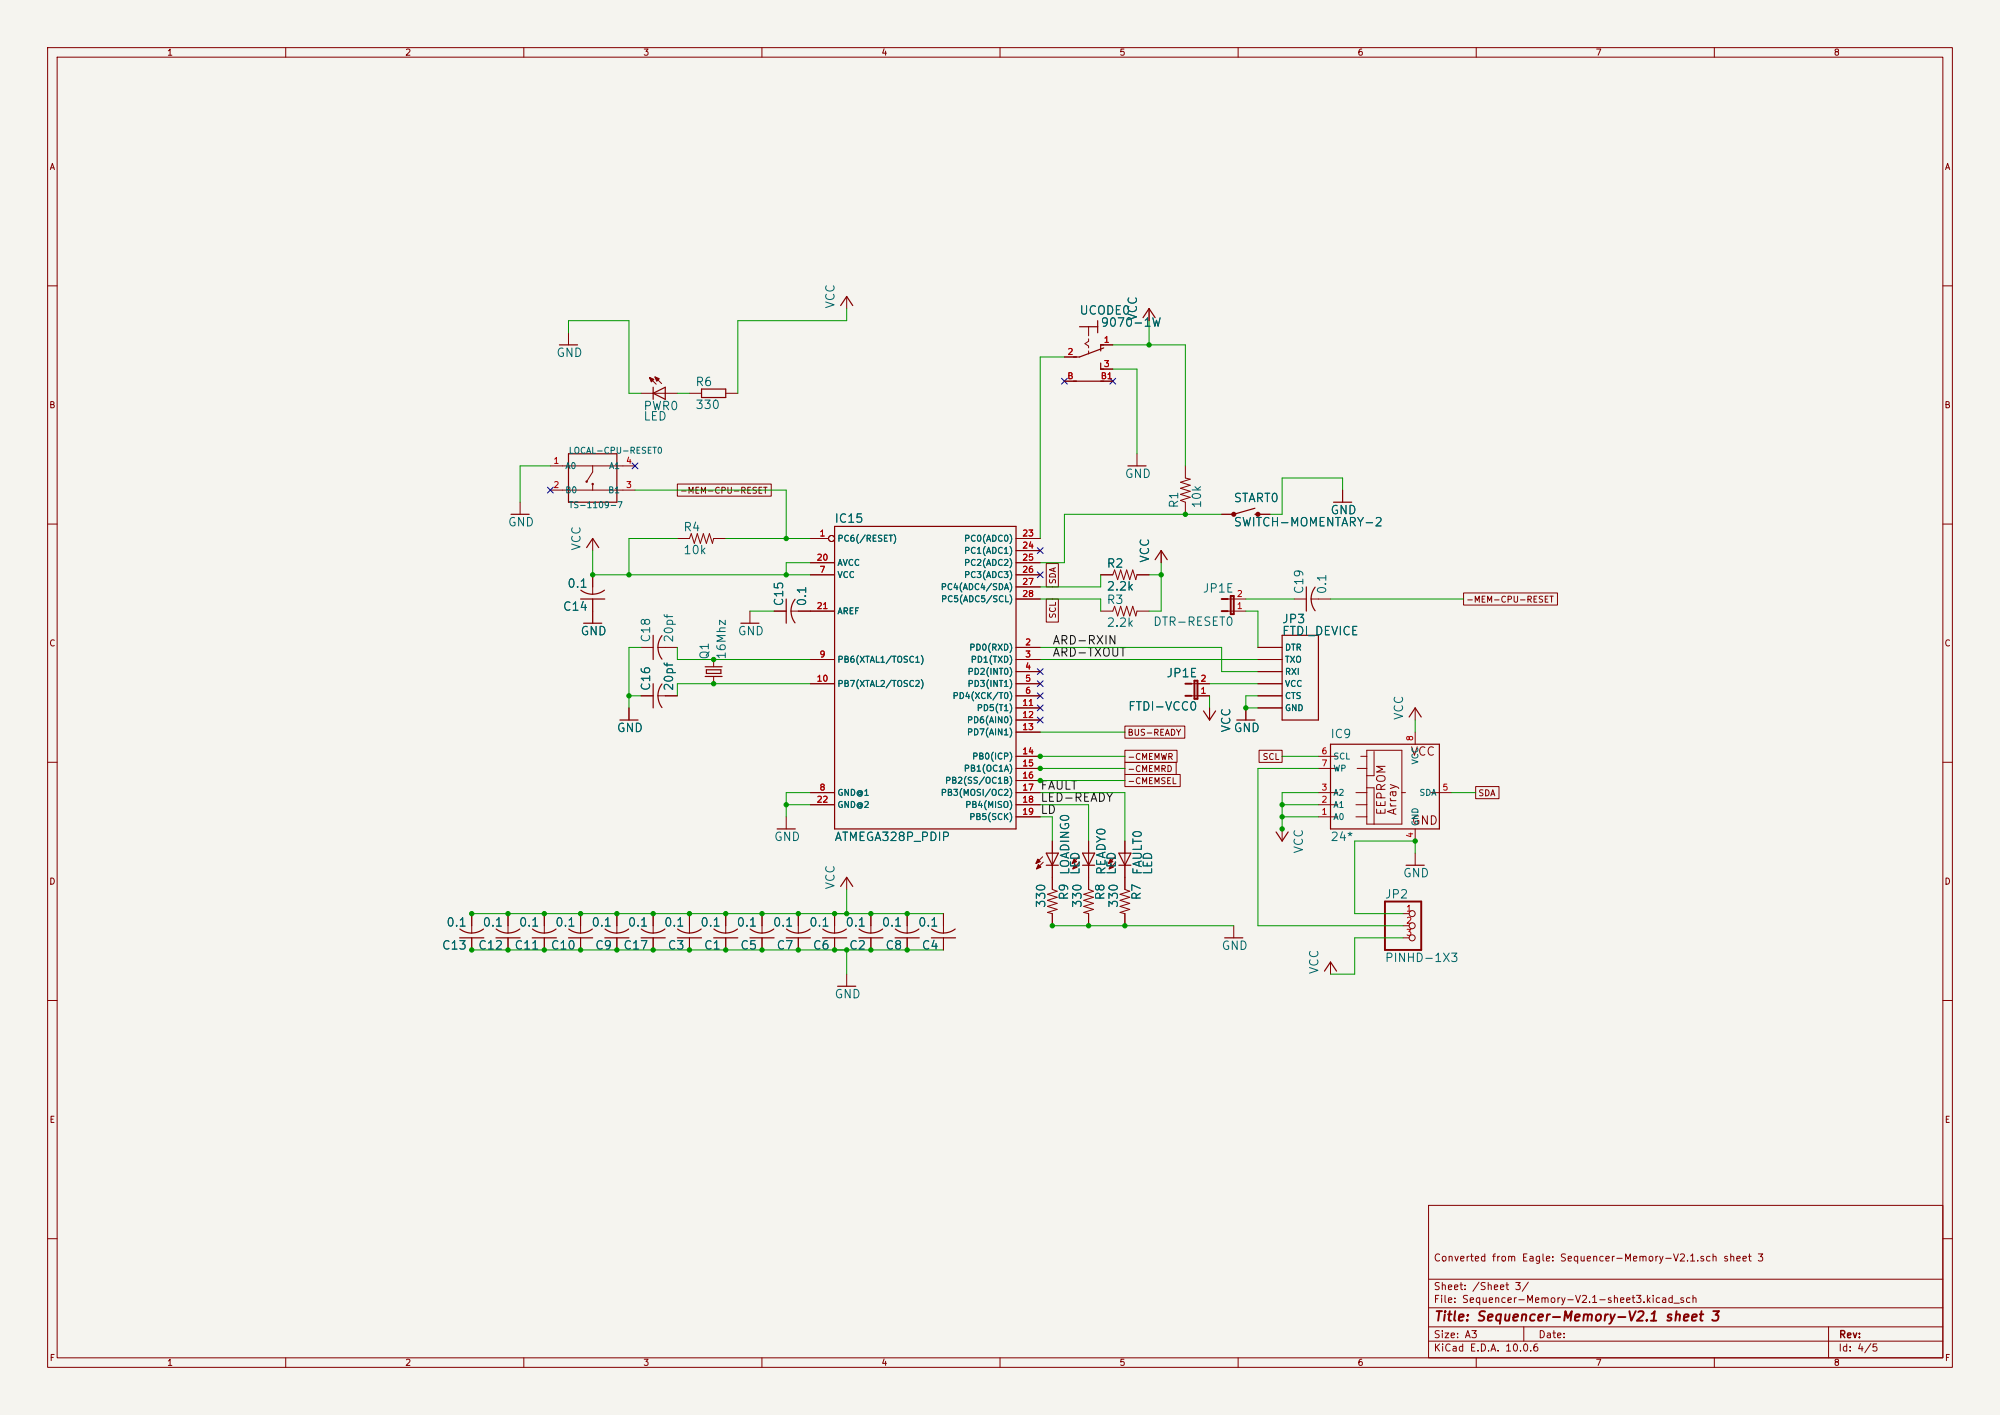
[picture p195: page 4]

Converted from Eagle: Sequencer-Memory-V2.1.sch sheet 3

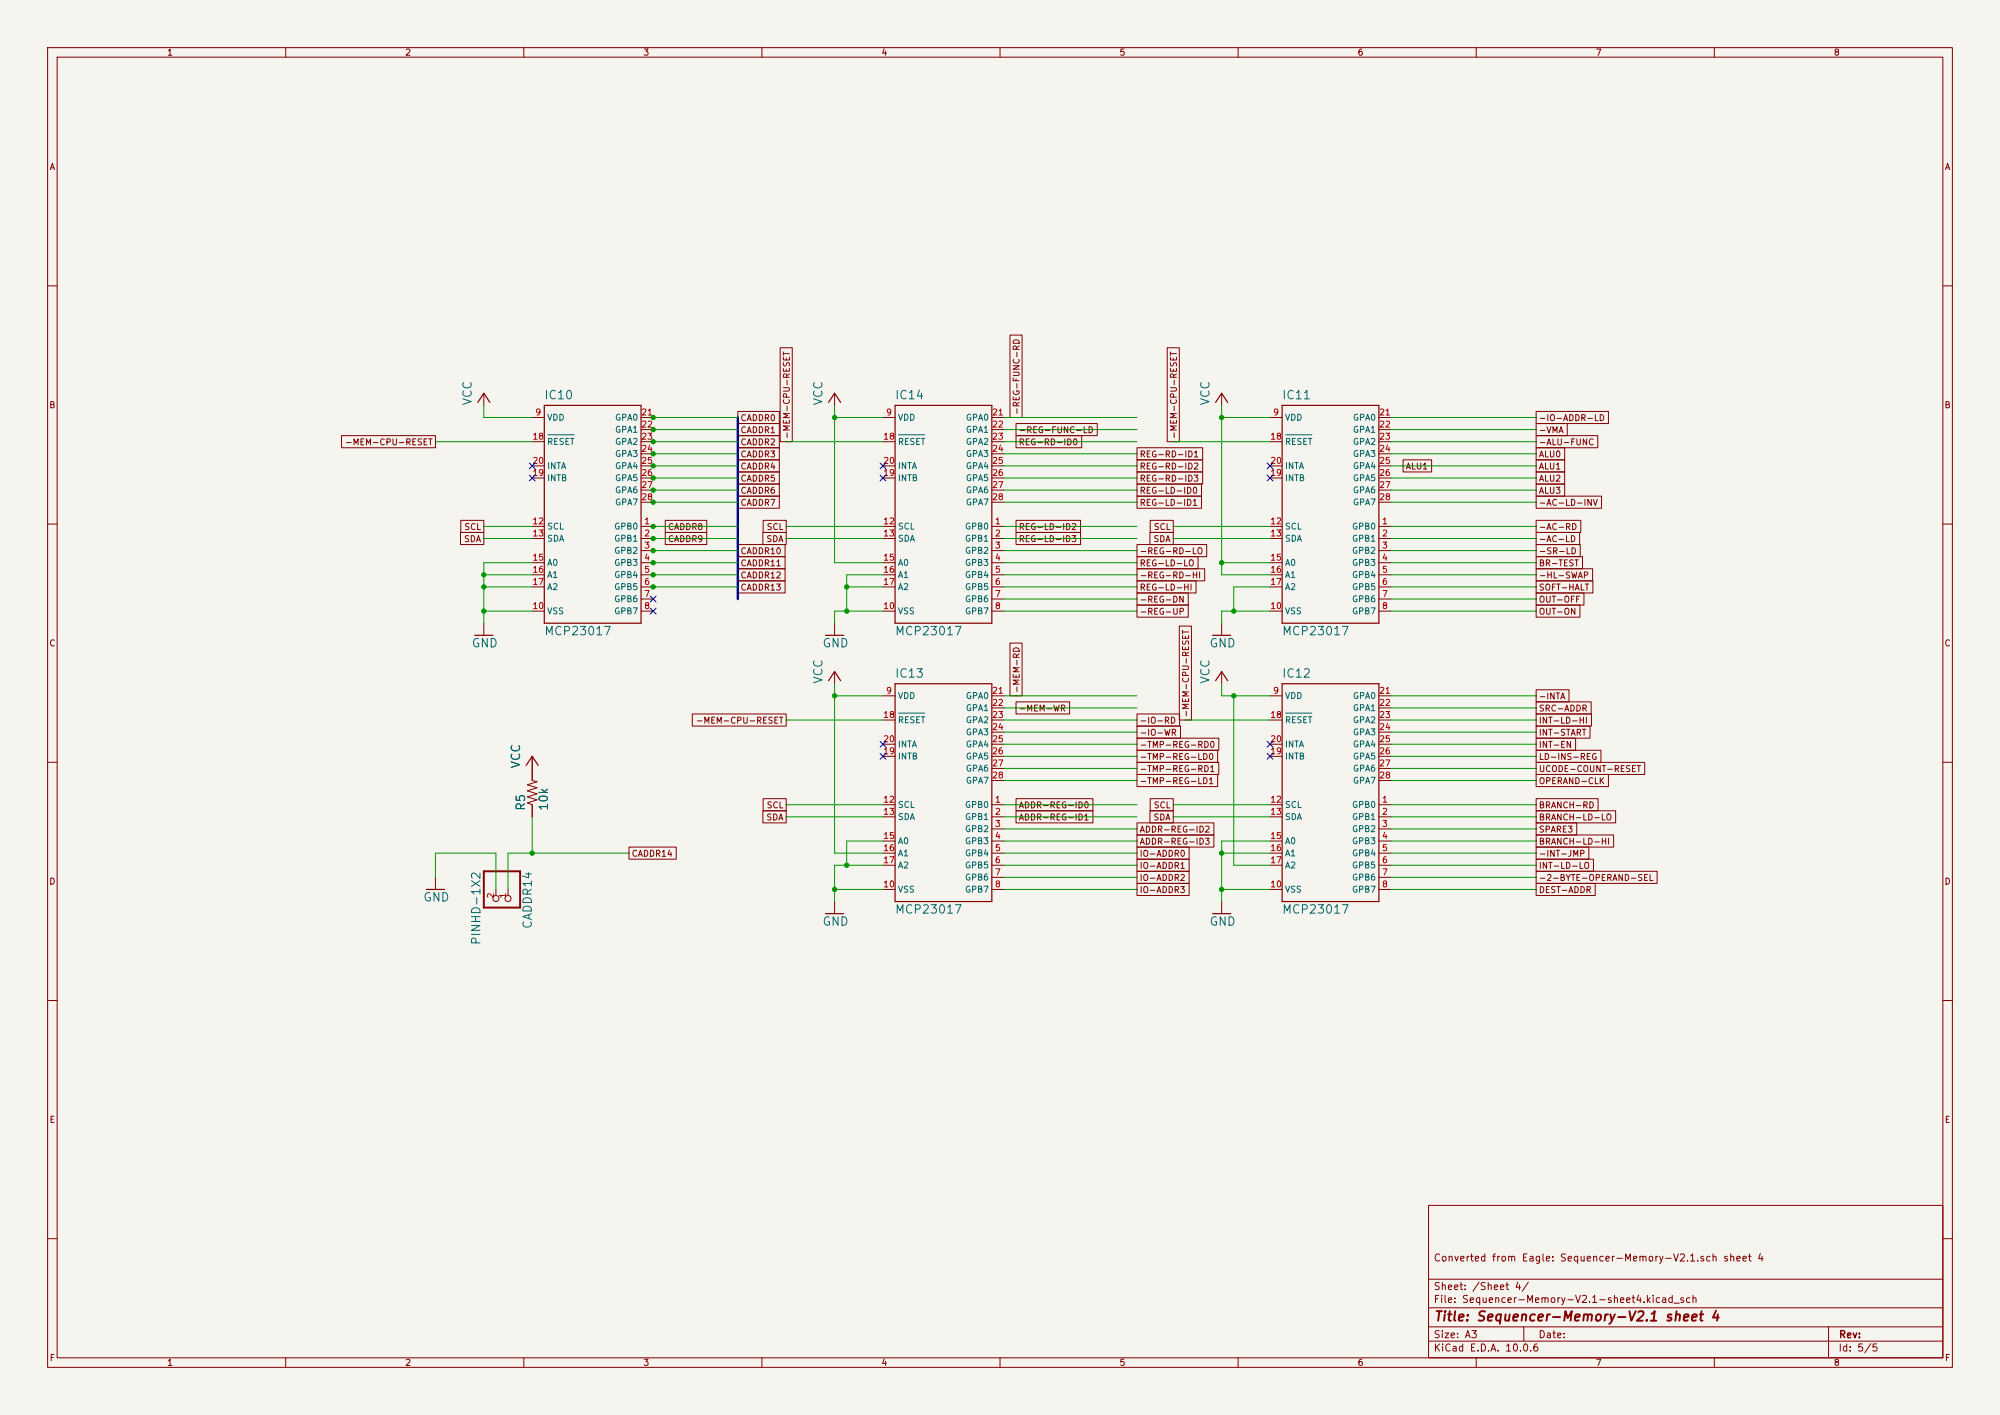
[picture p196: page 5]

INT-LD-HI OPERAND-CLK -MEM-CPU-RESET
A2 17 RESET 18

INT-START LD-INS-REG
INT-EN

UCODE-COUNT-RESET BRANCH-RD

Converted from Eagle: Sequencer-Memory-V2.1.sch sheet 4
