ksr/YACC1-D/hardware/cards/video/eagle/v1.0-fusion-export-2026-09-18/pdf/Video_1.0-schematic.pdf

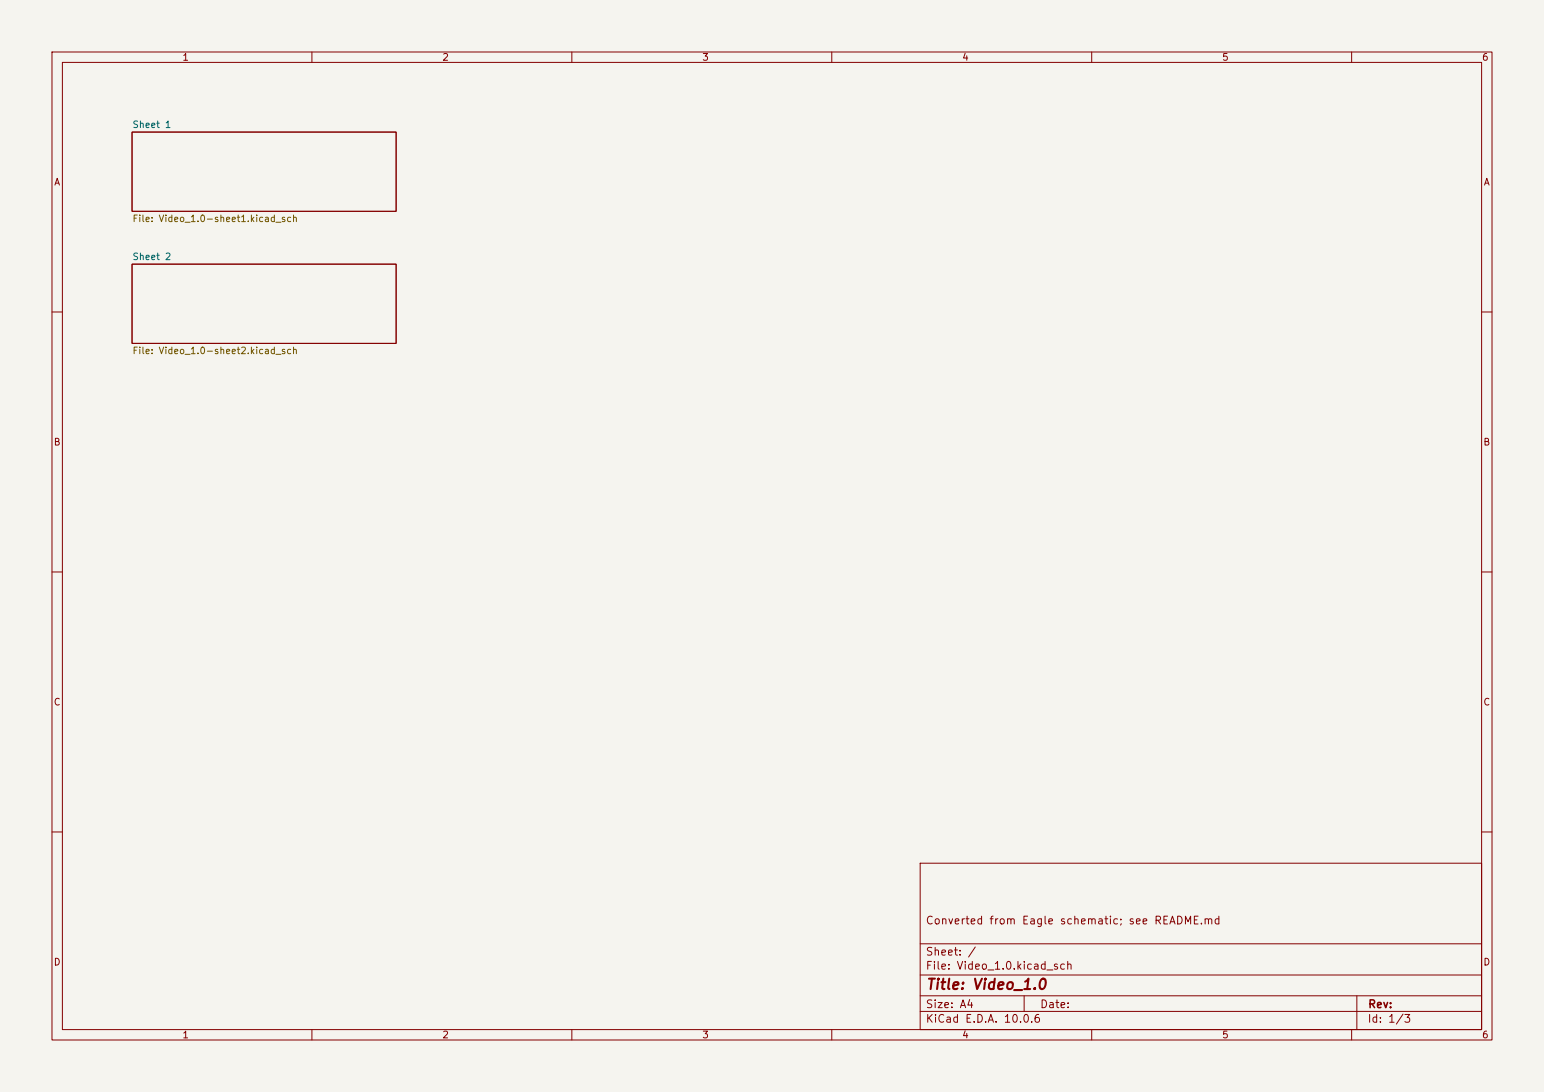
[picture p202: page 1]

Converted from Eagle schematic; see README.md

Size: A4 | Rev:
KiCad E.D.A. 10.0.6 | Id: 1/3

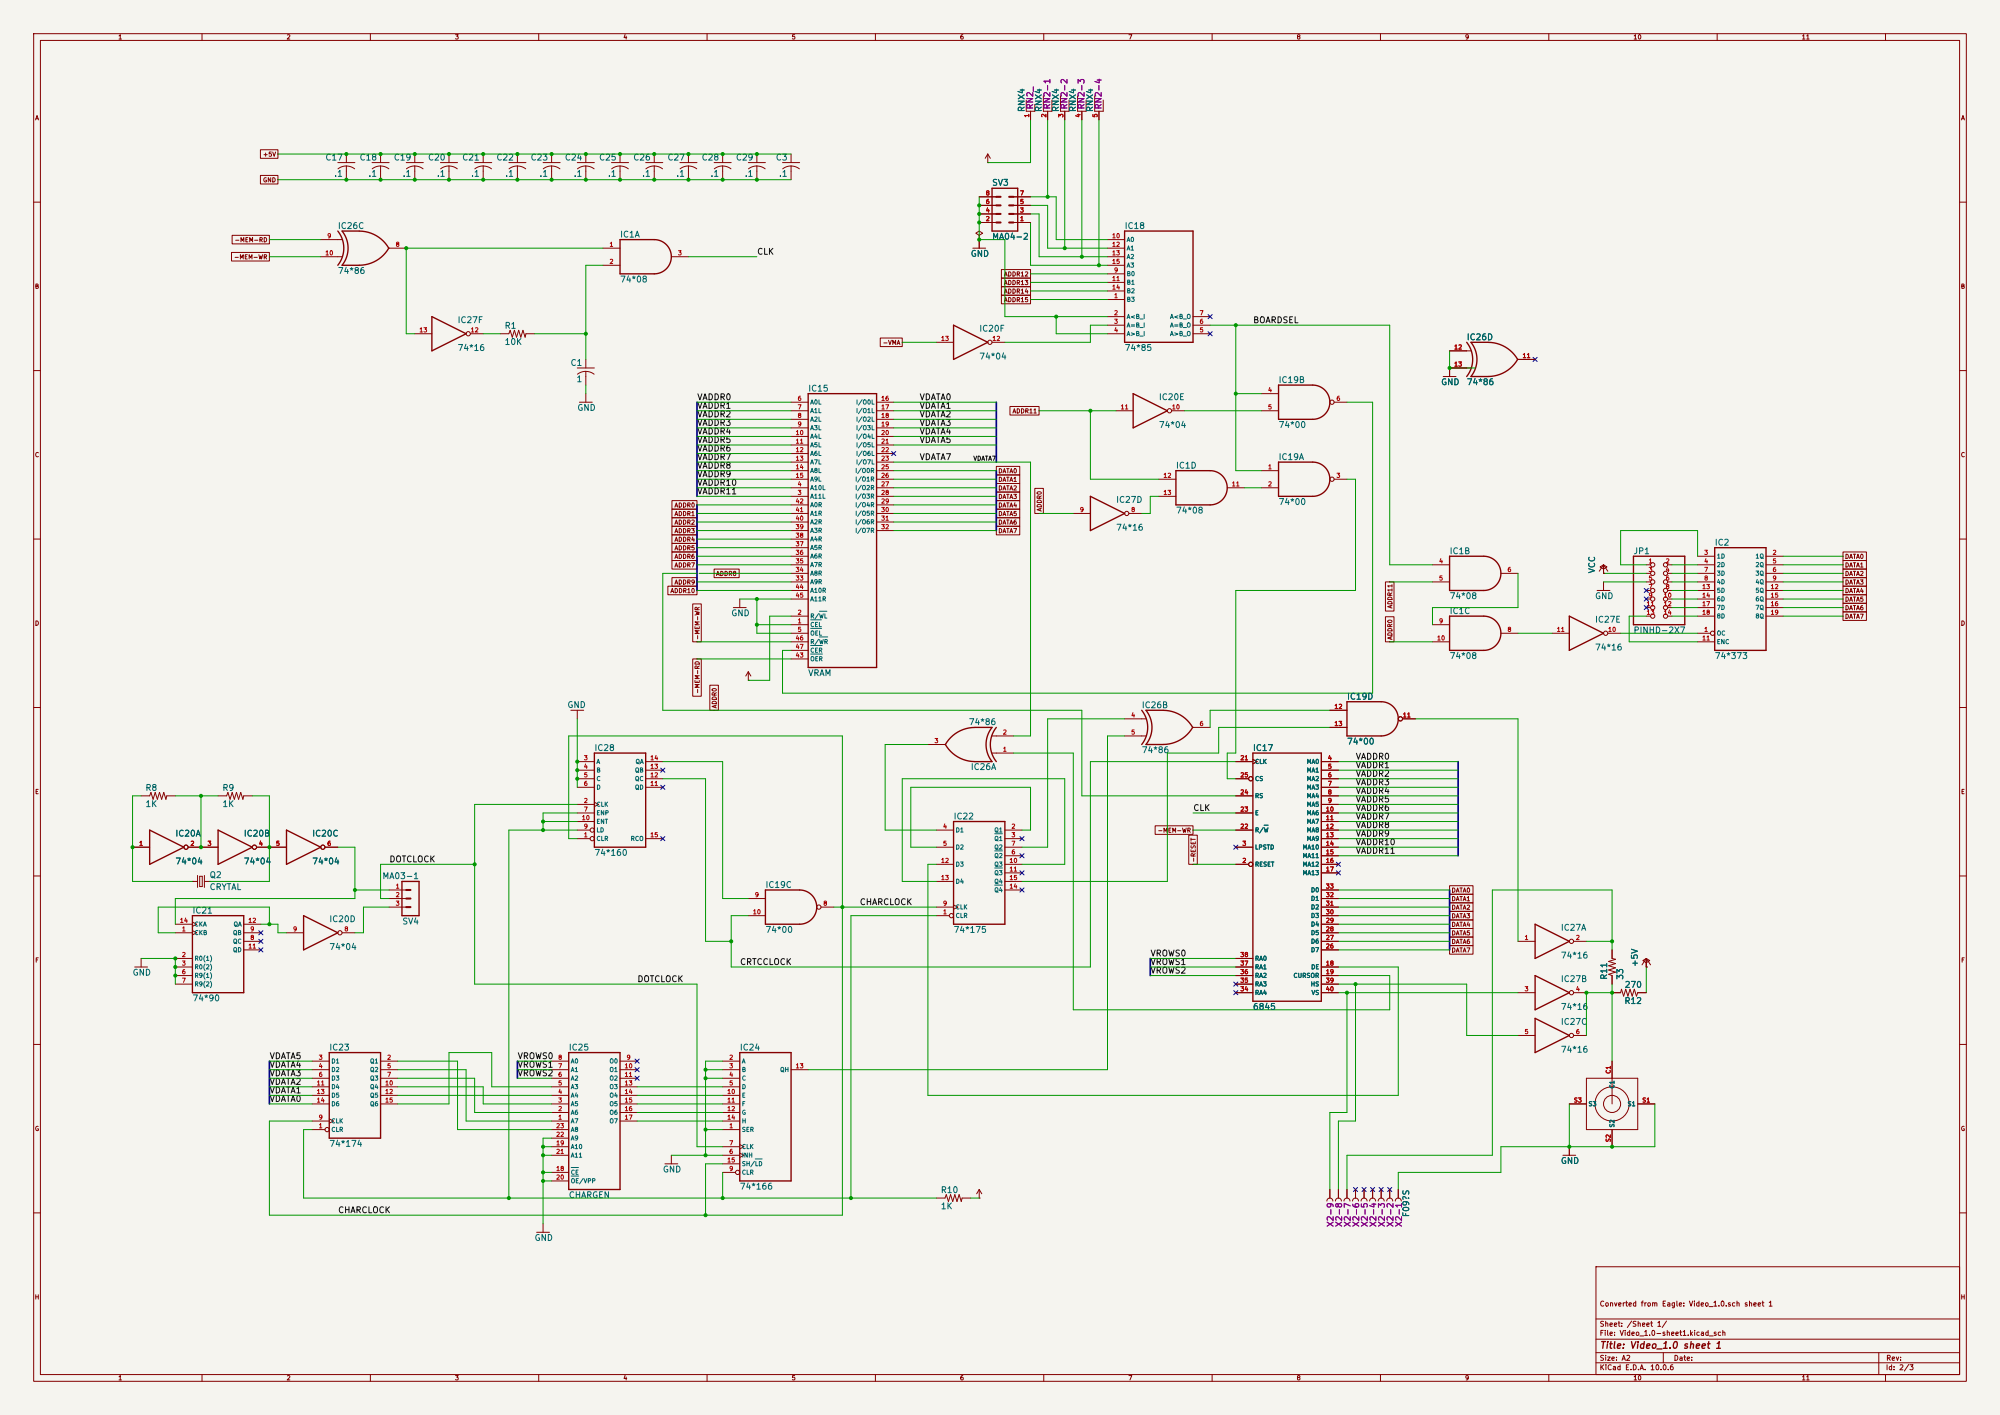
[picture p203: page 2]

+5V GND -MEM-RD -MEM-WR

VDATA1 | A4 4
VDATA0 | A5 3

Converted from Eagle: Video_1.0.sch sheet 1

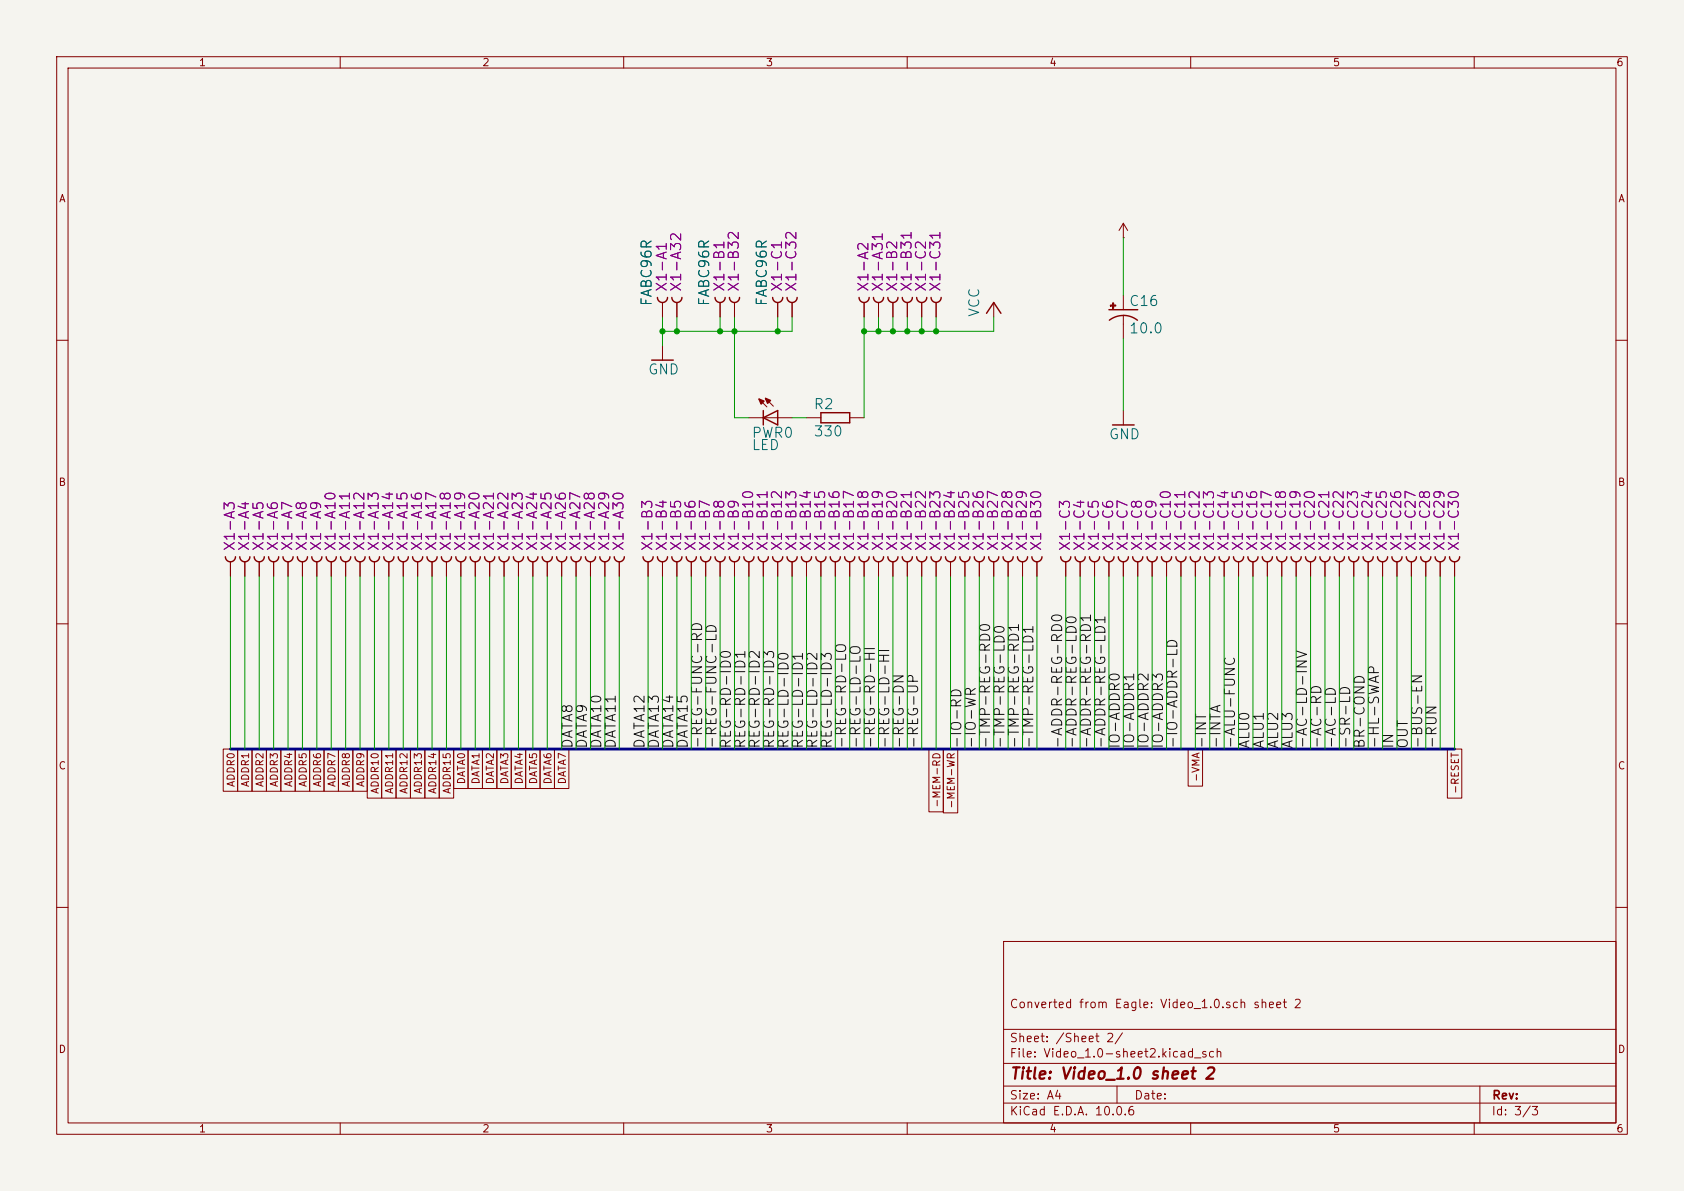
[picture p204: page 3]
