ksr/YACC1-D/hardware/cards/video/kicad/v1.0-fusion-export-2026-09-18/reports/video-v1.0-fusion-export-2026-09-18-schematic.pdf

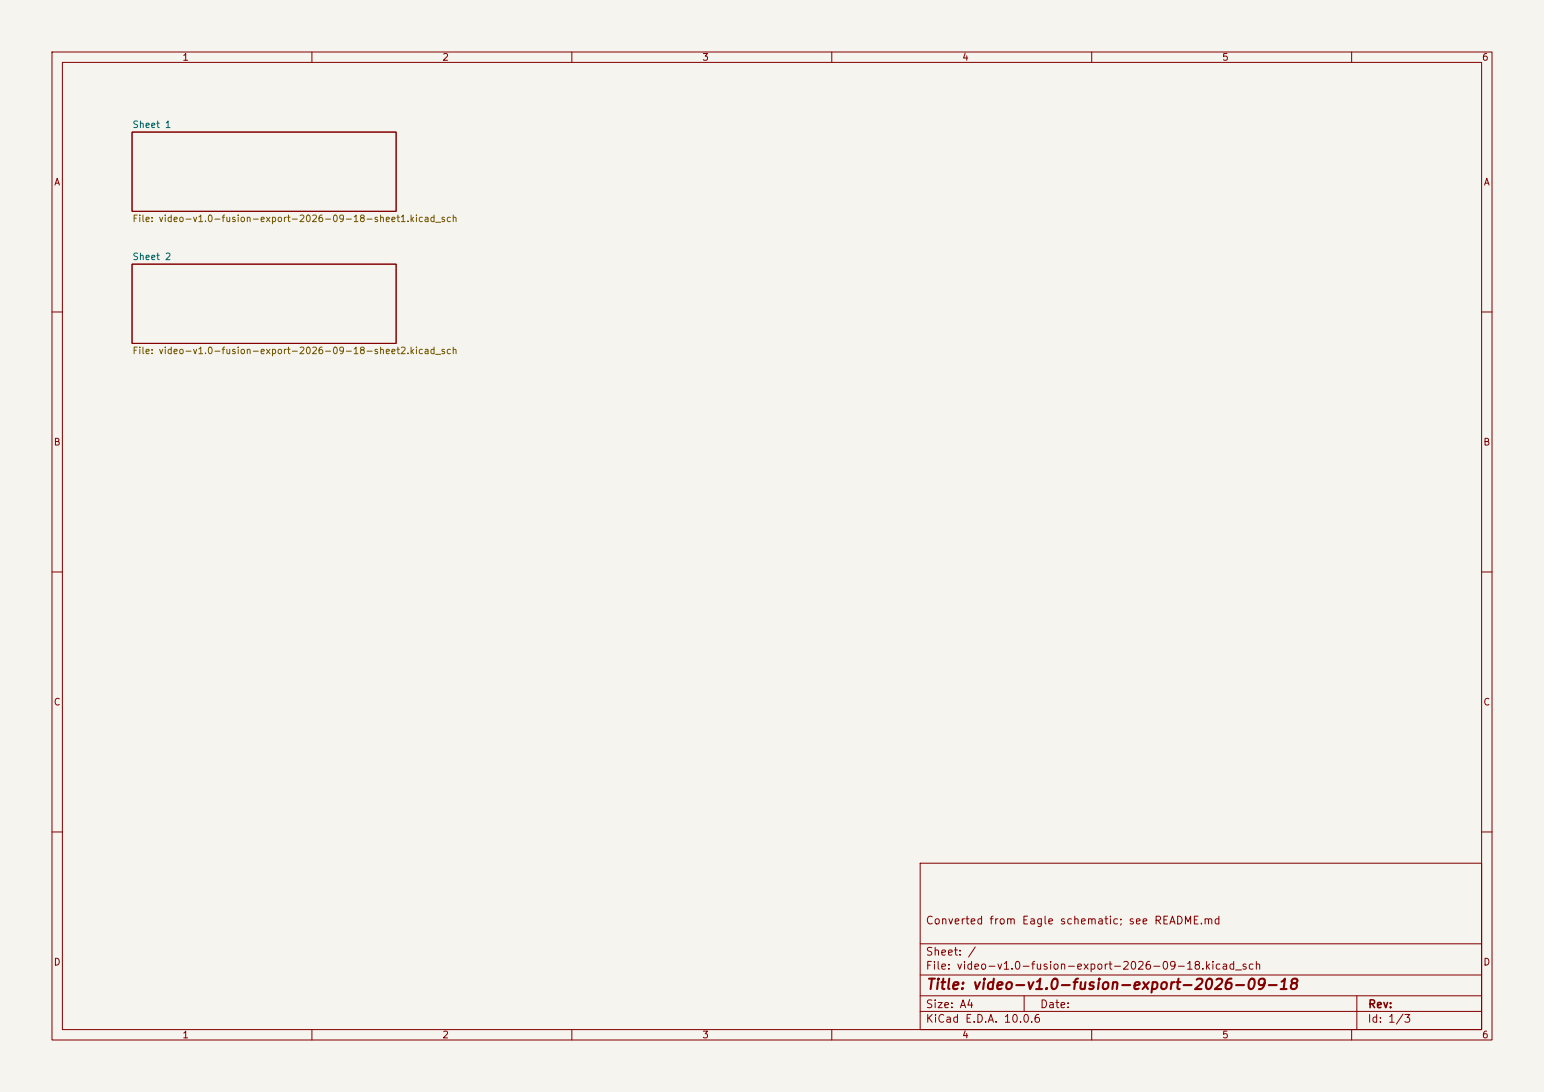
[picture p205: page 1]

File: video-v1.0-fusion-export-2026-09-18-sheet1.kicad_sch Sheet 2

File: video-v1.0-fusion-export-2026-09-18-sheet2.kicad_sch

Converted from Eagle schematic; see README.md

Sheet: /
File: video-v1.0-fusion-export-2026-09-18.kicad_sch
Title: video-v1.0-fusion-export-2026-09-18

Size: A4 | Rev:
KiCad E.D.A. 10.0.6 | Id: 1/3

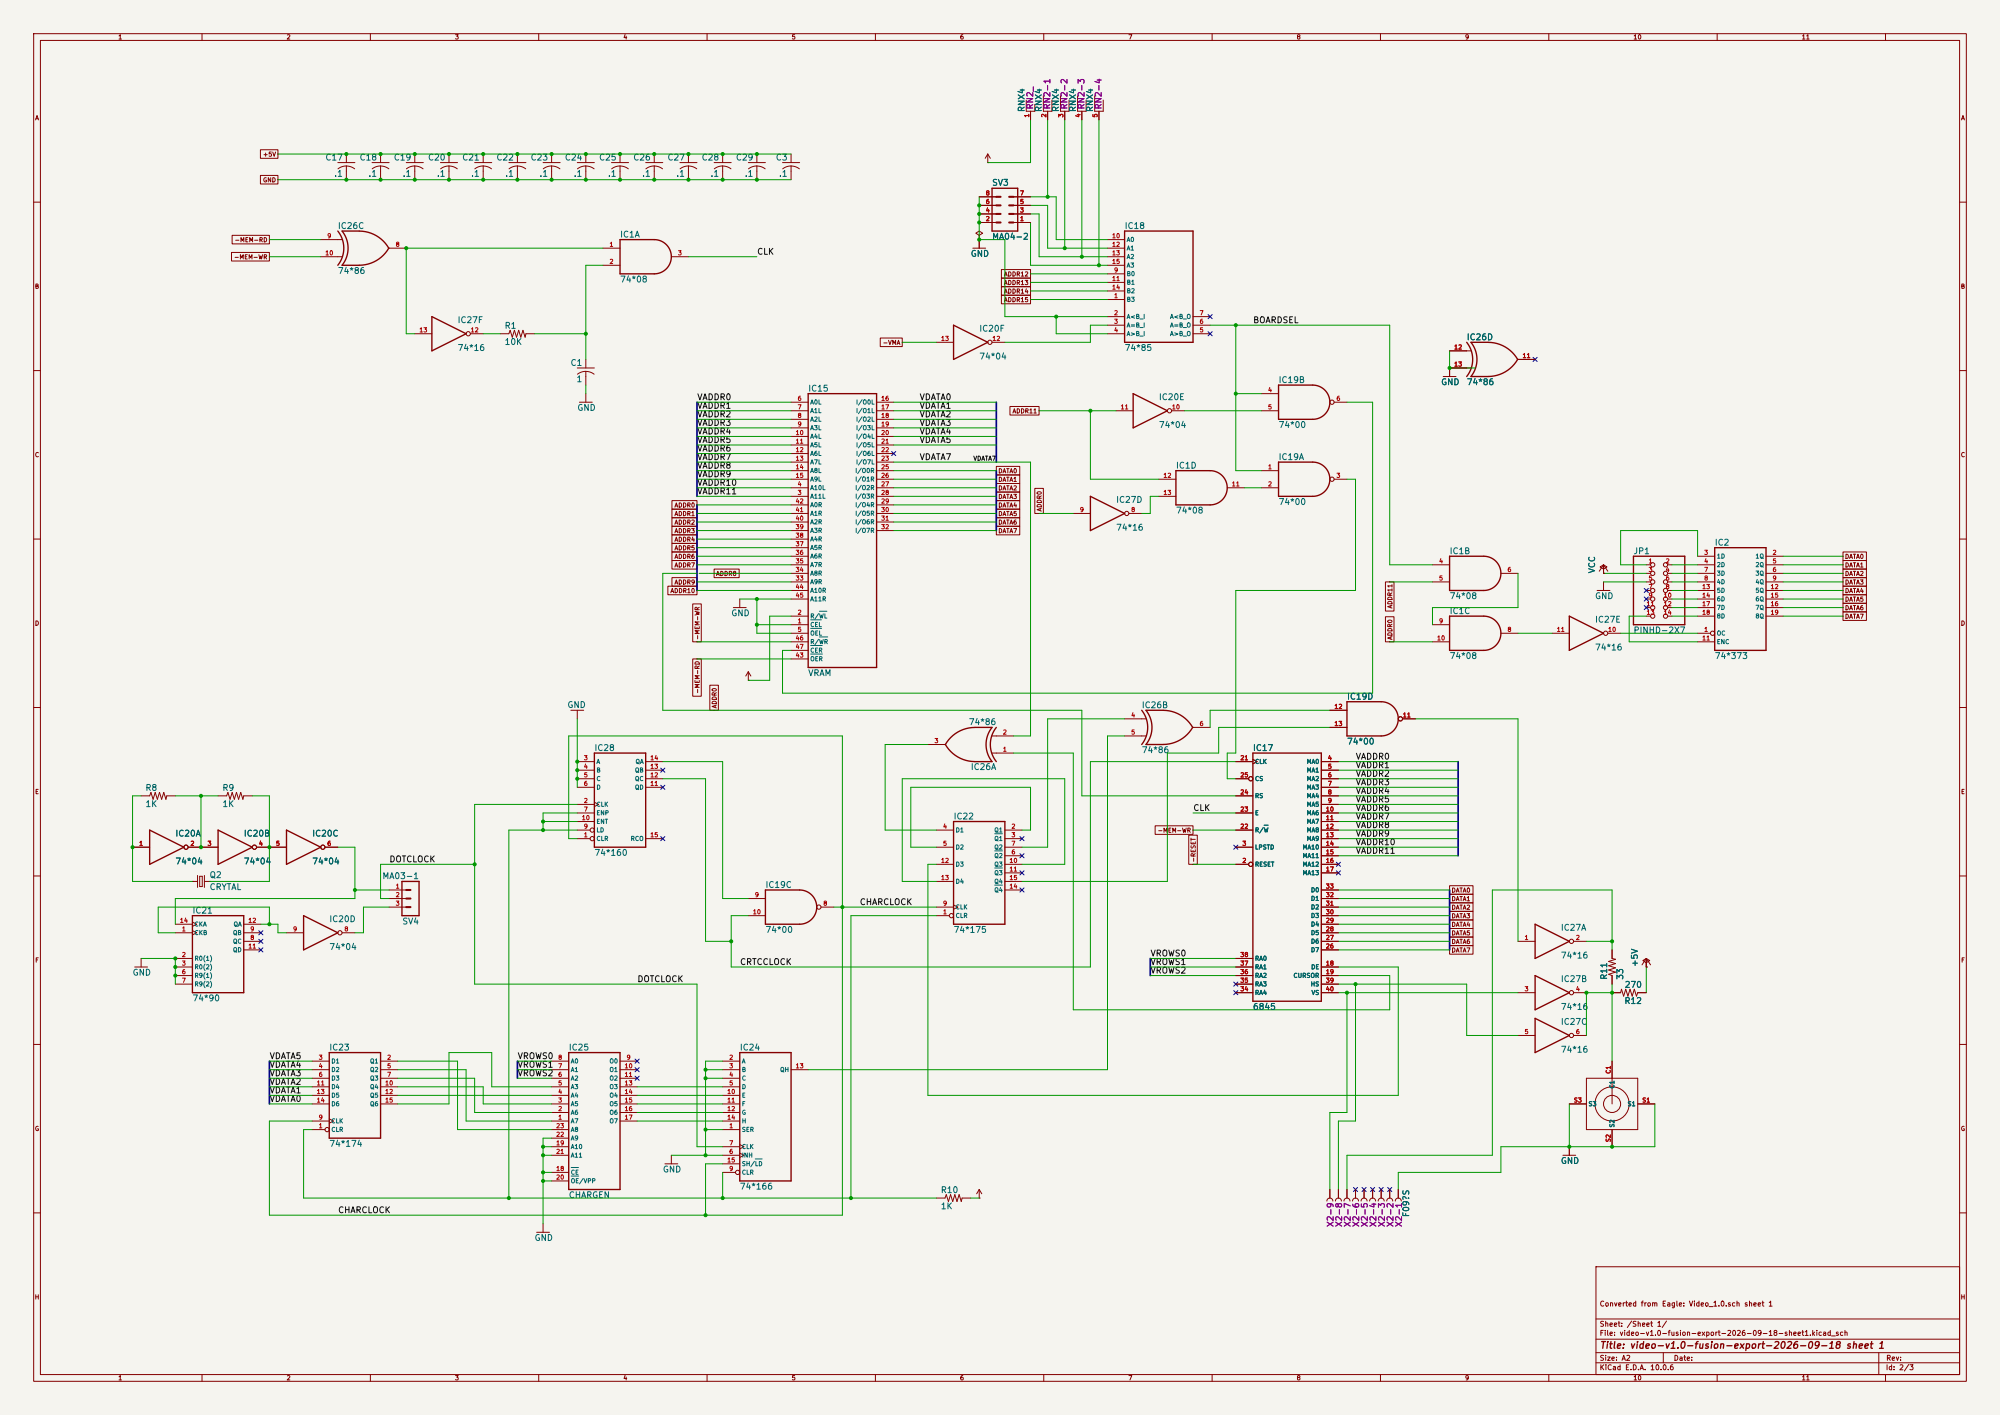
[picture p206: page 2]

+5V GND -MEM-RD -MEM-WR

SER 1

Converted from Eagle: Video_1.0.sch sheet 1

Sheet: /Sheet 1/
File: video-v1.0-fusion-export-2026-09-18-sheet1.kicad_sch
Title: video-v1.0-fusion-export-2026-09-18 sheet 1

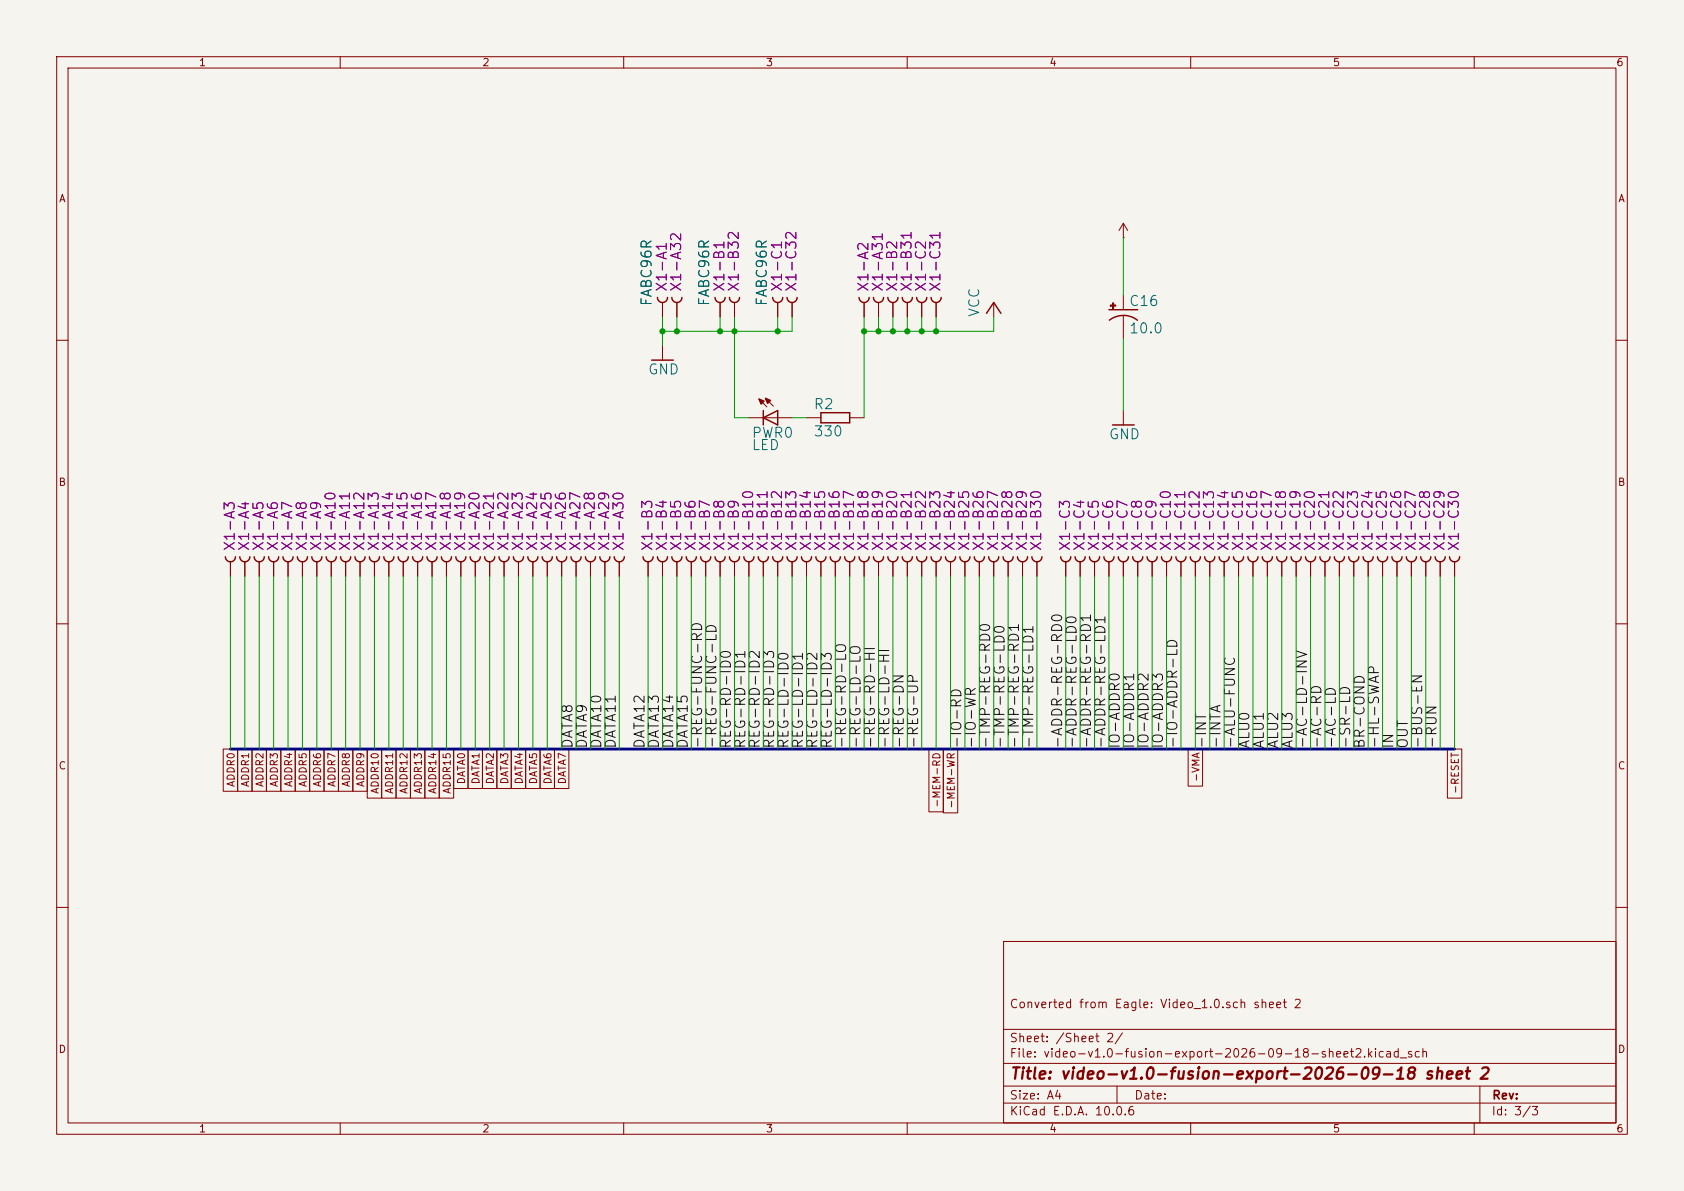
[picture p207: page 3]

Sheet: /Sheet 2/
File: video-v1.0-fusion-export-2026-09-18-sheet2.kicad_sch
Title: video-v1.0-fusion-export-2026-09-18 sheet 2
