ksr/YACC1-D/hardware/cards/video/kicad/v1.1/reports/video-v1.1-schematic.pdf

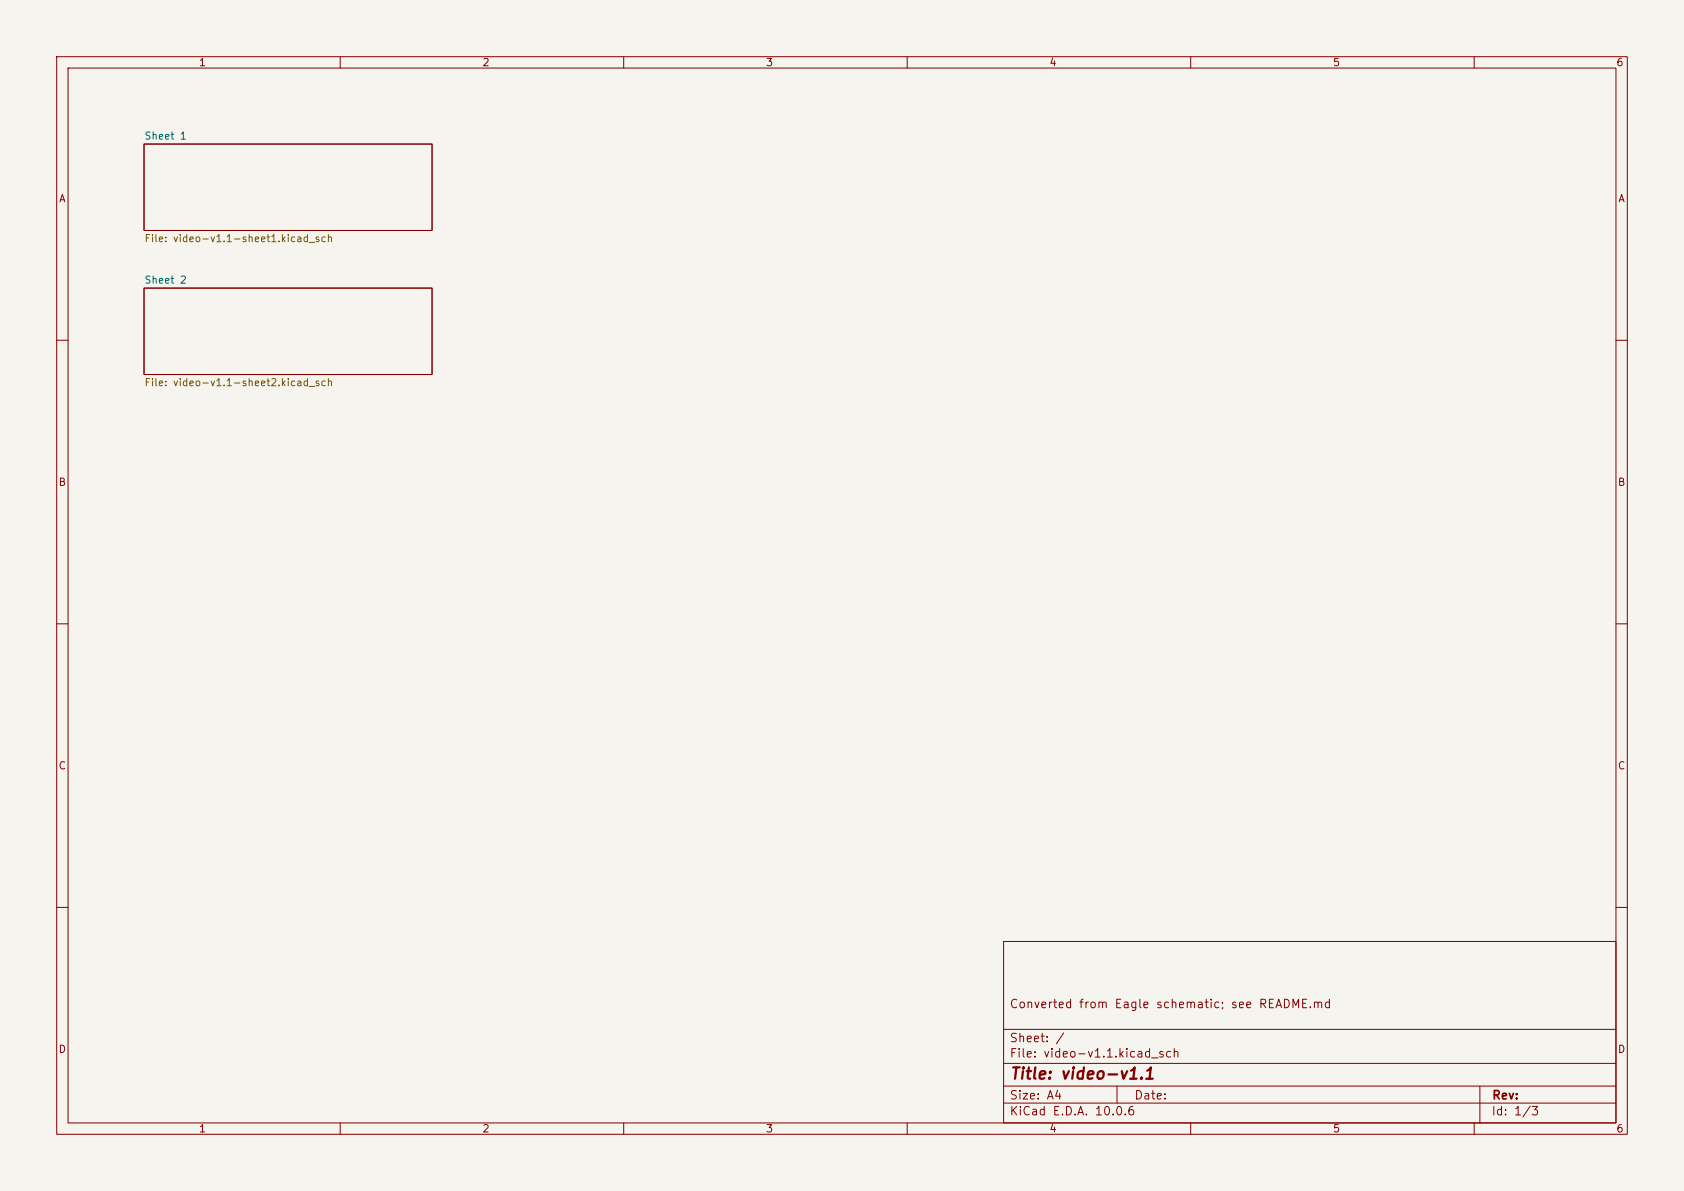
[picture p208: page 1]

Converted from Eagle schematic; see README.md

Size: A4 | Rev:
KiCad E.D.A. 10.0.6 | Id: 1/3

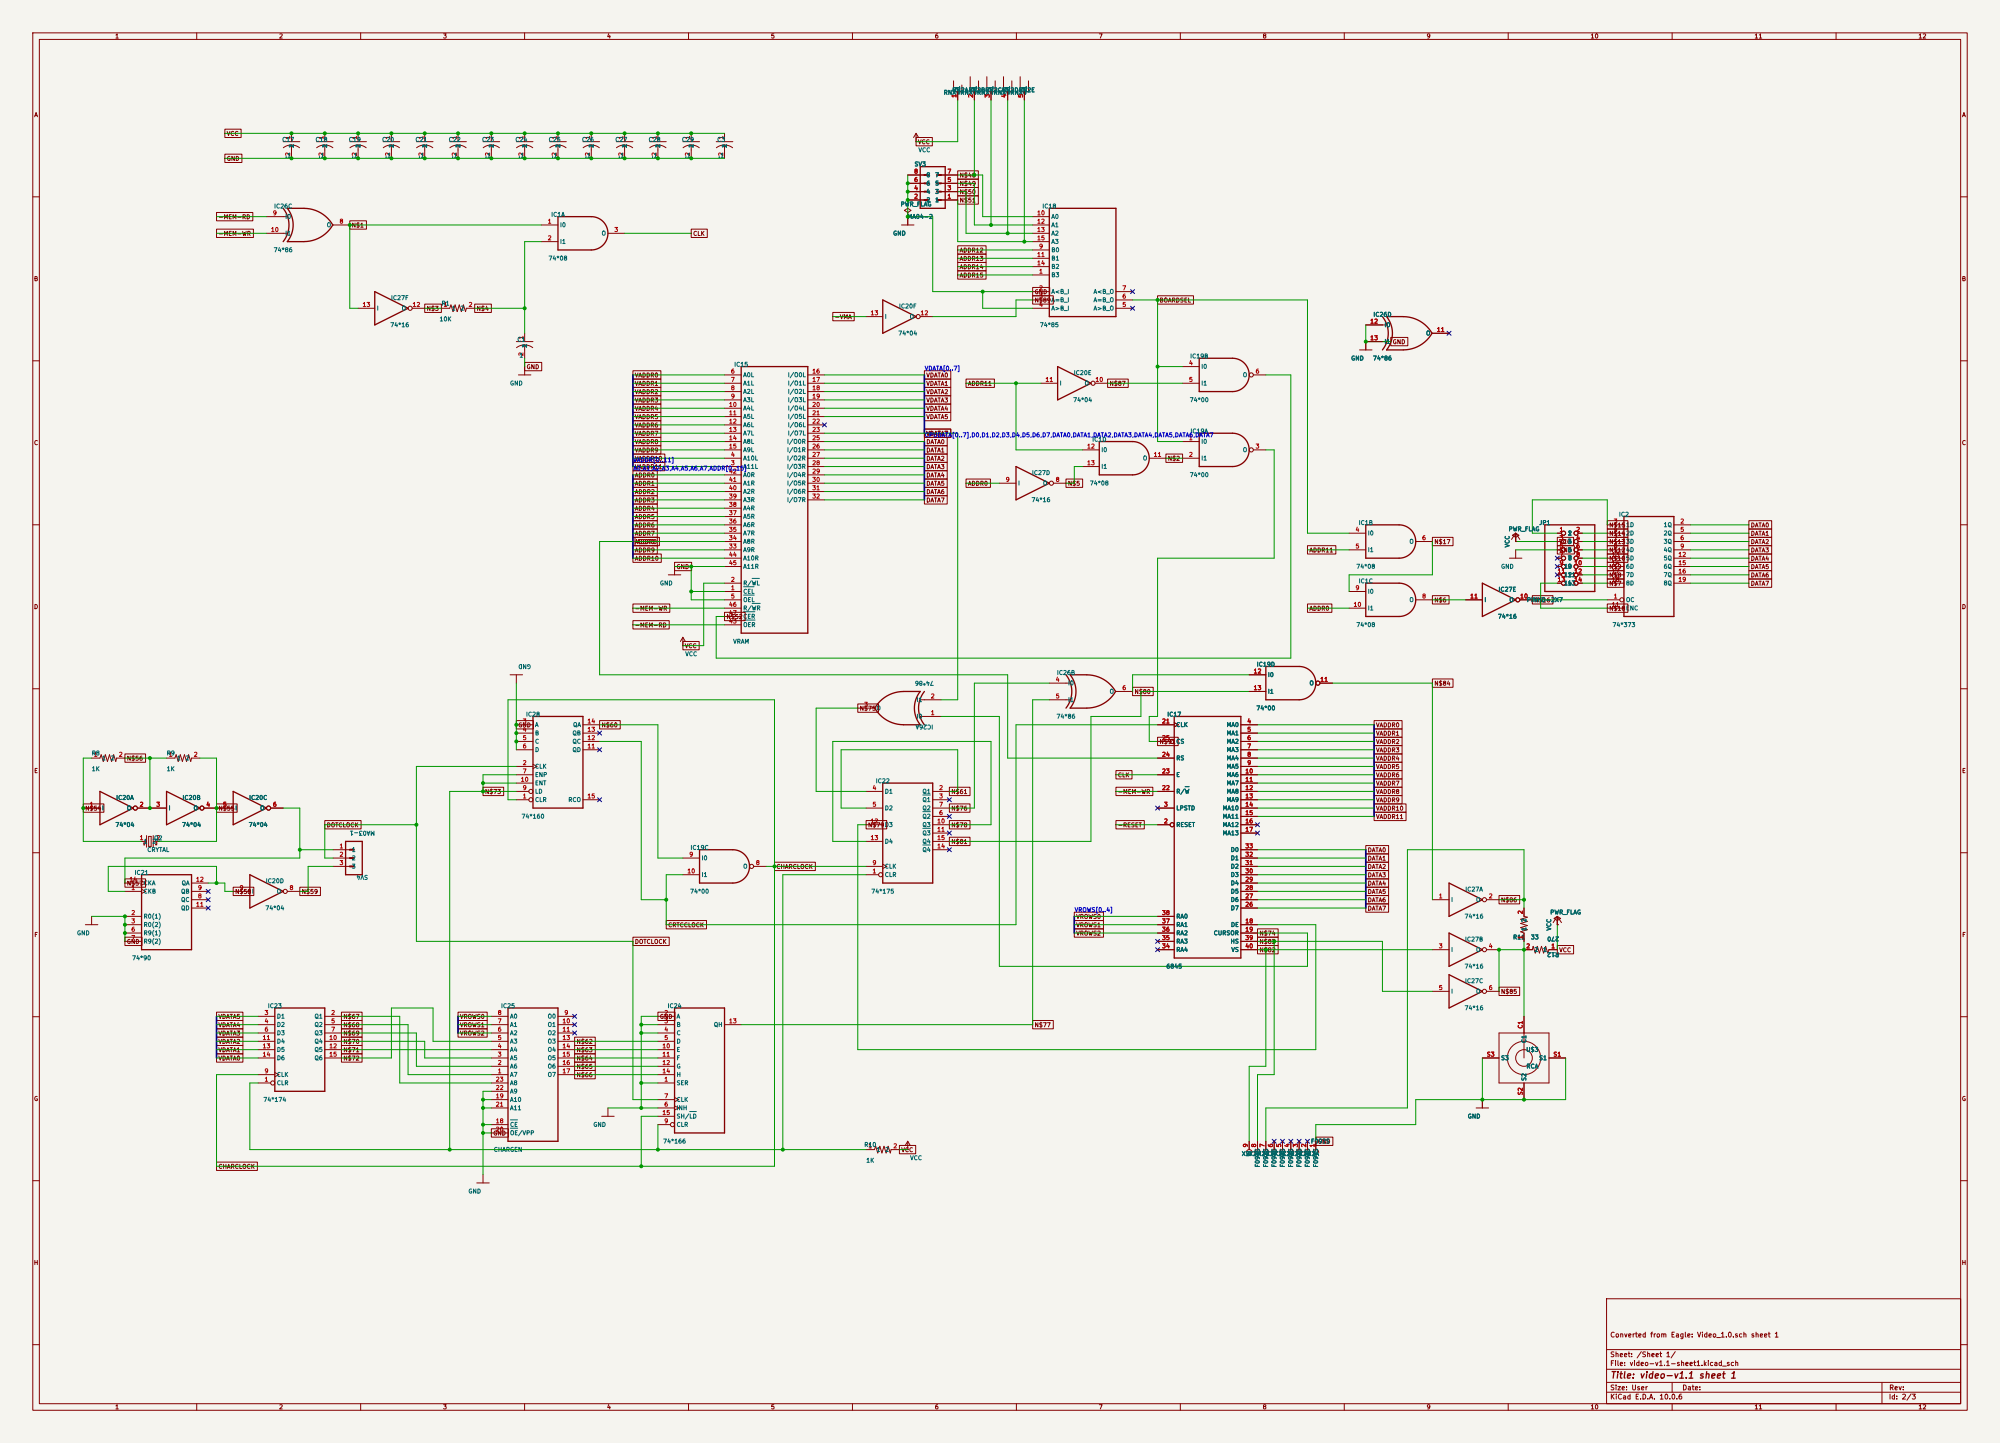
[picture p209: page 2]

VADDR4 | VDATA4
VADDR5 | VDATA5

1 1 2 2 1 1 2 2 3 3 4 4 VCC 3 3 4 4 5 5 6 6 5 5 6 6 7 7 8 8 7 7 8 8 9 9 10 10 10 10 9 9 11 11 12 12 12 12 11 11 13 13 14 14 14 14 13 13 | 4 N$14 7 8 13 N$10 14 N$9

A11R 45 R/WR 46 CER 47

SER 1

Converted from Eagle: Video_1.0.sch sheet 1

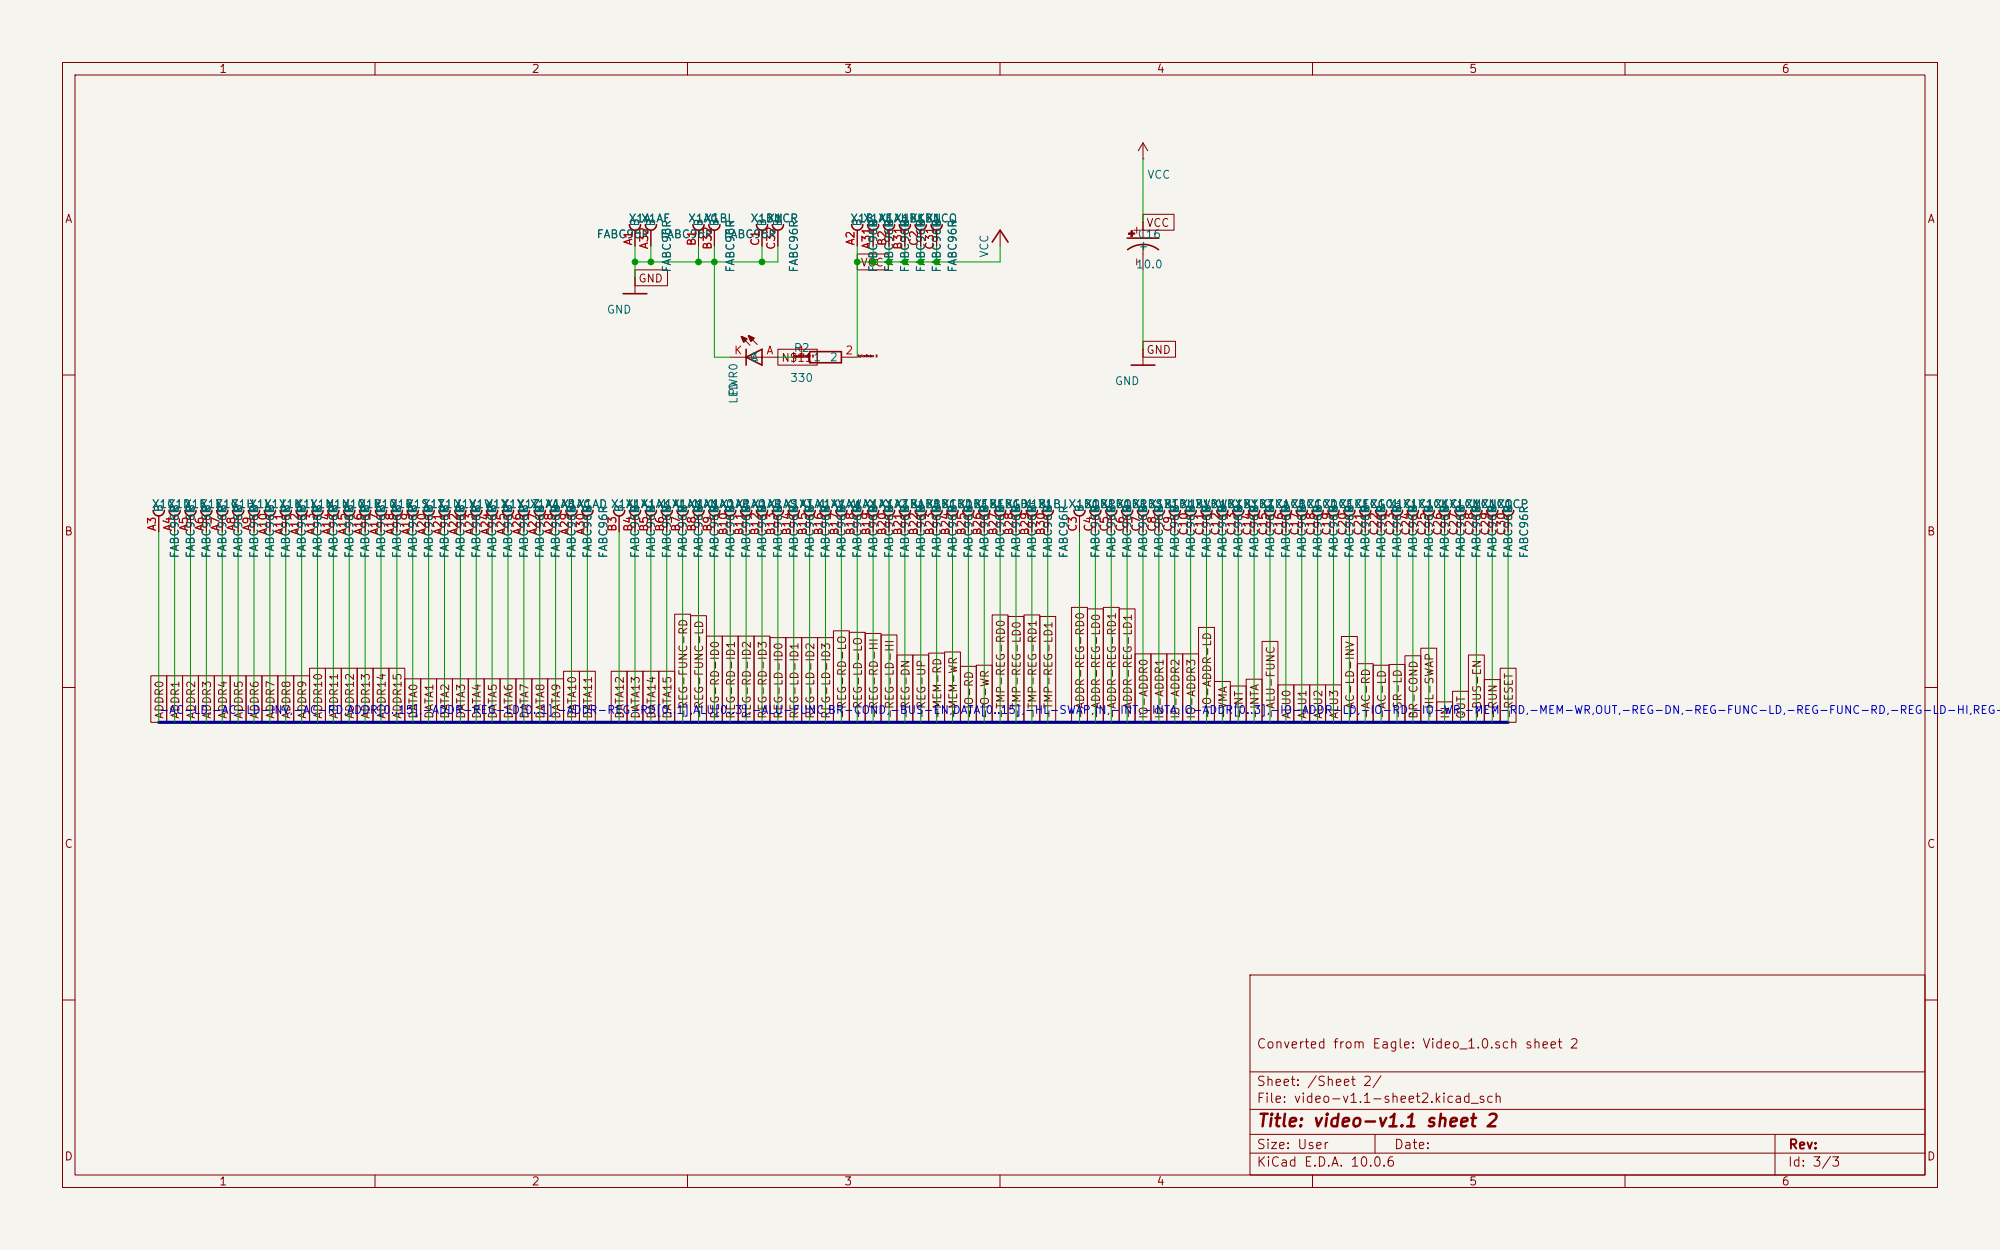
[picture p210: page 3]

Converted from Eagle: Video_1.0.sch sheet 2
