ksr/YACC1-D/hardware/cards/sequencer-logic/eagle/v2.1/orig size/pdf/Sequencer-Logic-Prod-V2.1 copy-schematic.pdf

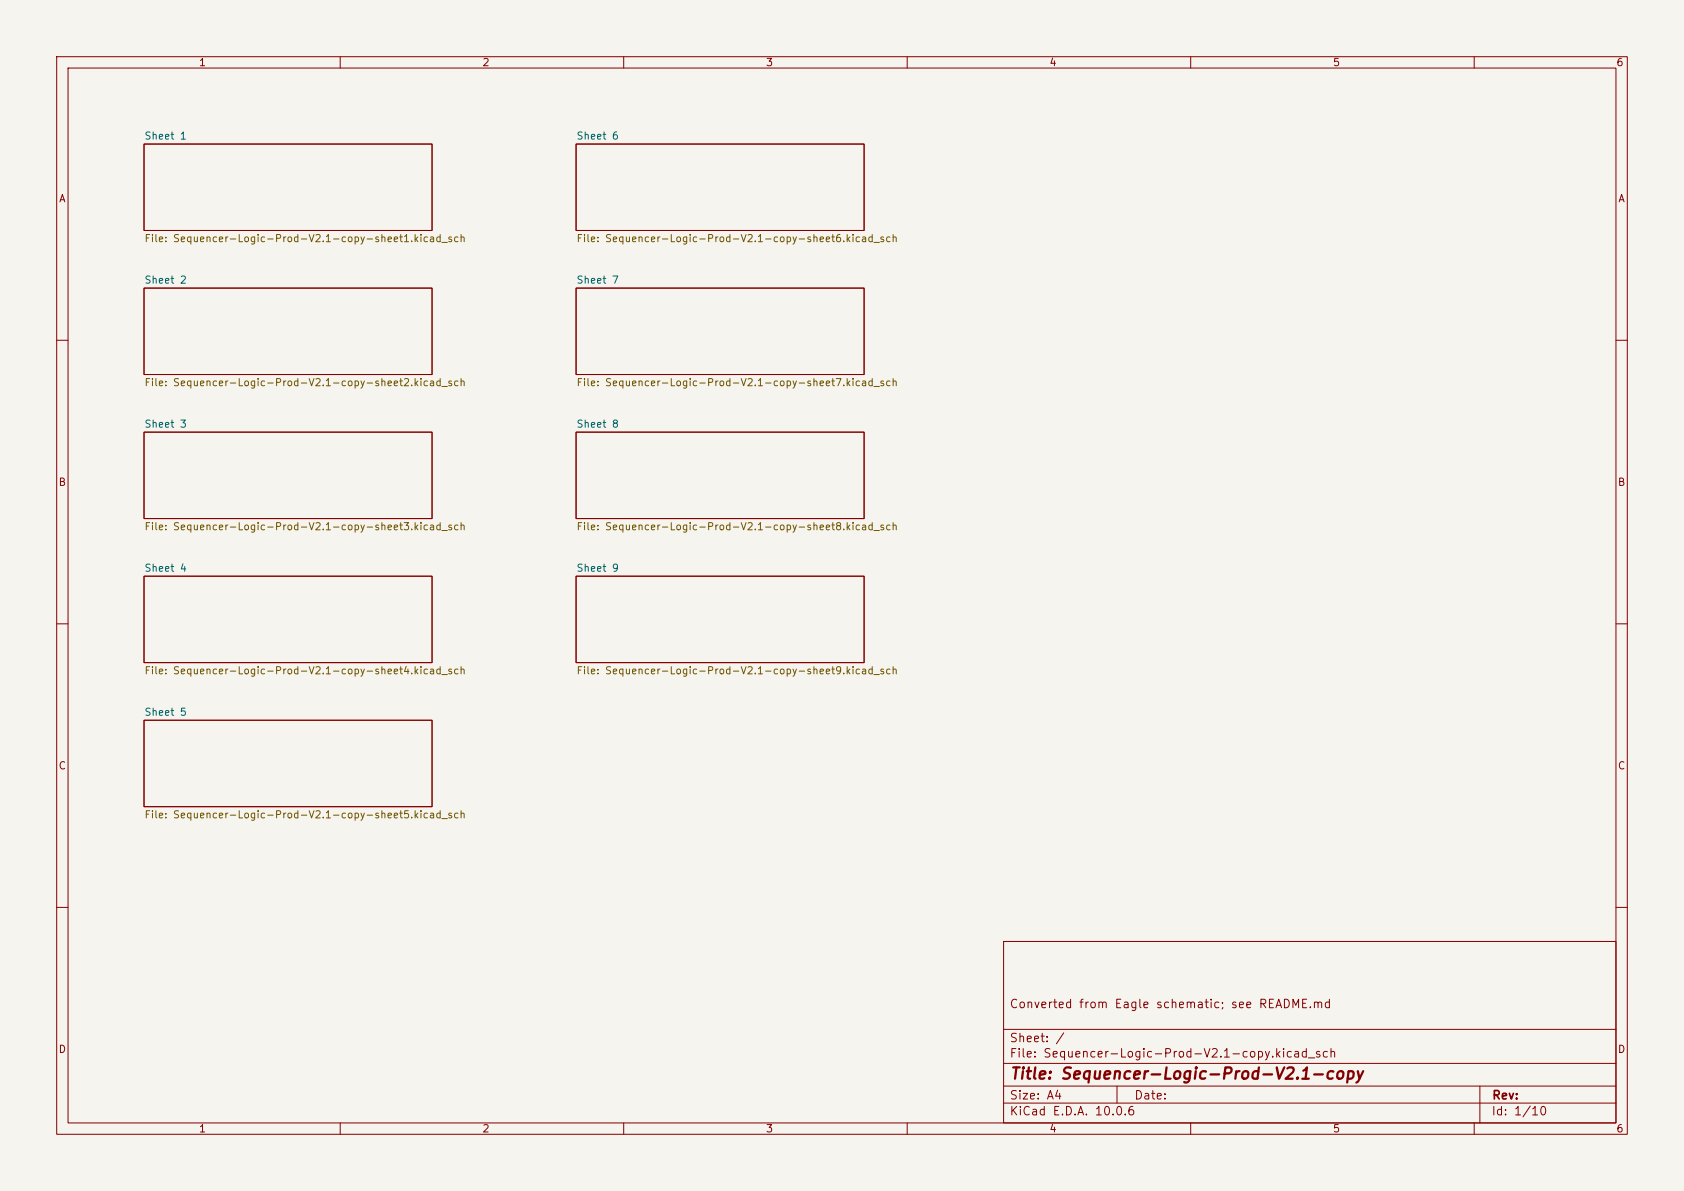
[picture p211: page 1]

File: Sequencer-Logic-Prod-V2.1-copy-sheet1.kicad_sch Sheet 2

File: Sequencer-Logic-Prod-V2.1-copy-sheet6.kicad_sch Sheet 7

File: Sequencer-Logic-Prod-V2.1-copy-sheet2.kicad_sch Sheet 3

File: Sequencer-Logic-Prod-V2.1-copy-sheet7.kicad_sch Sheet 8

File: Sequencer-Logic-Prod-V2.1-copy-sheet3.kicad_sch Sheet 4

File: Sequencer-Logic-Prod-V2.1-copy-sheet8.kicad_sch Sheet 9

File: Sequencer-Logic-Prod-V2.1-copy-sheet4.kicad_sch Sheet 5

File: Sequencer-Logic-Prod-V2.1-copy-sheet9.kicad_sch

File: Sequencer-Logic-Prod-V2.1-copy-sheet5.kicad_sch

Converted from Eagle schematic; see README.md

Sheet: /
File: Sequencer-Logic-Prod-V2.1-copy.kicad_sch
Title: Sequencer-Logic-Prod-V2.1-copy

Size: A4 | Rev:
KiCad E.D.A. 10.0.6 | Id: 1/10

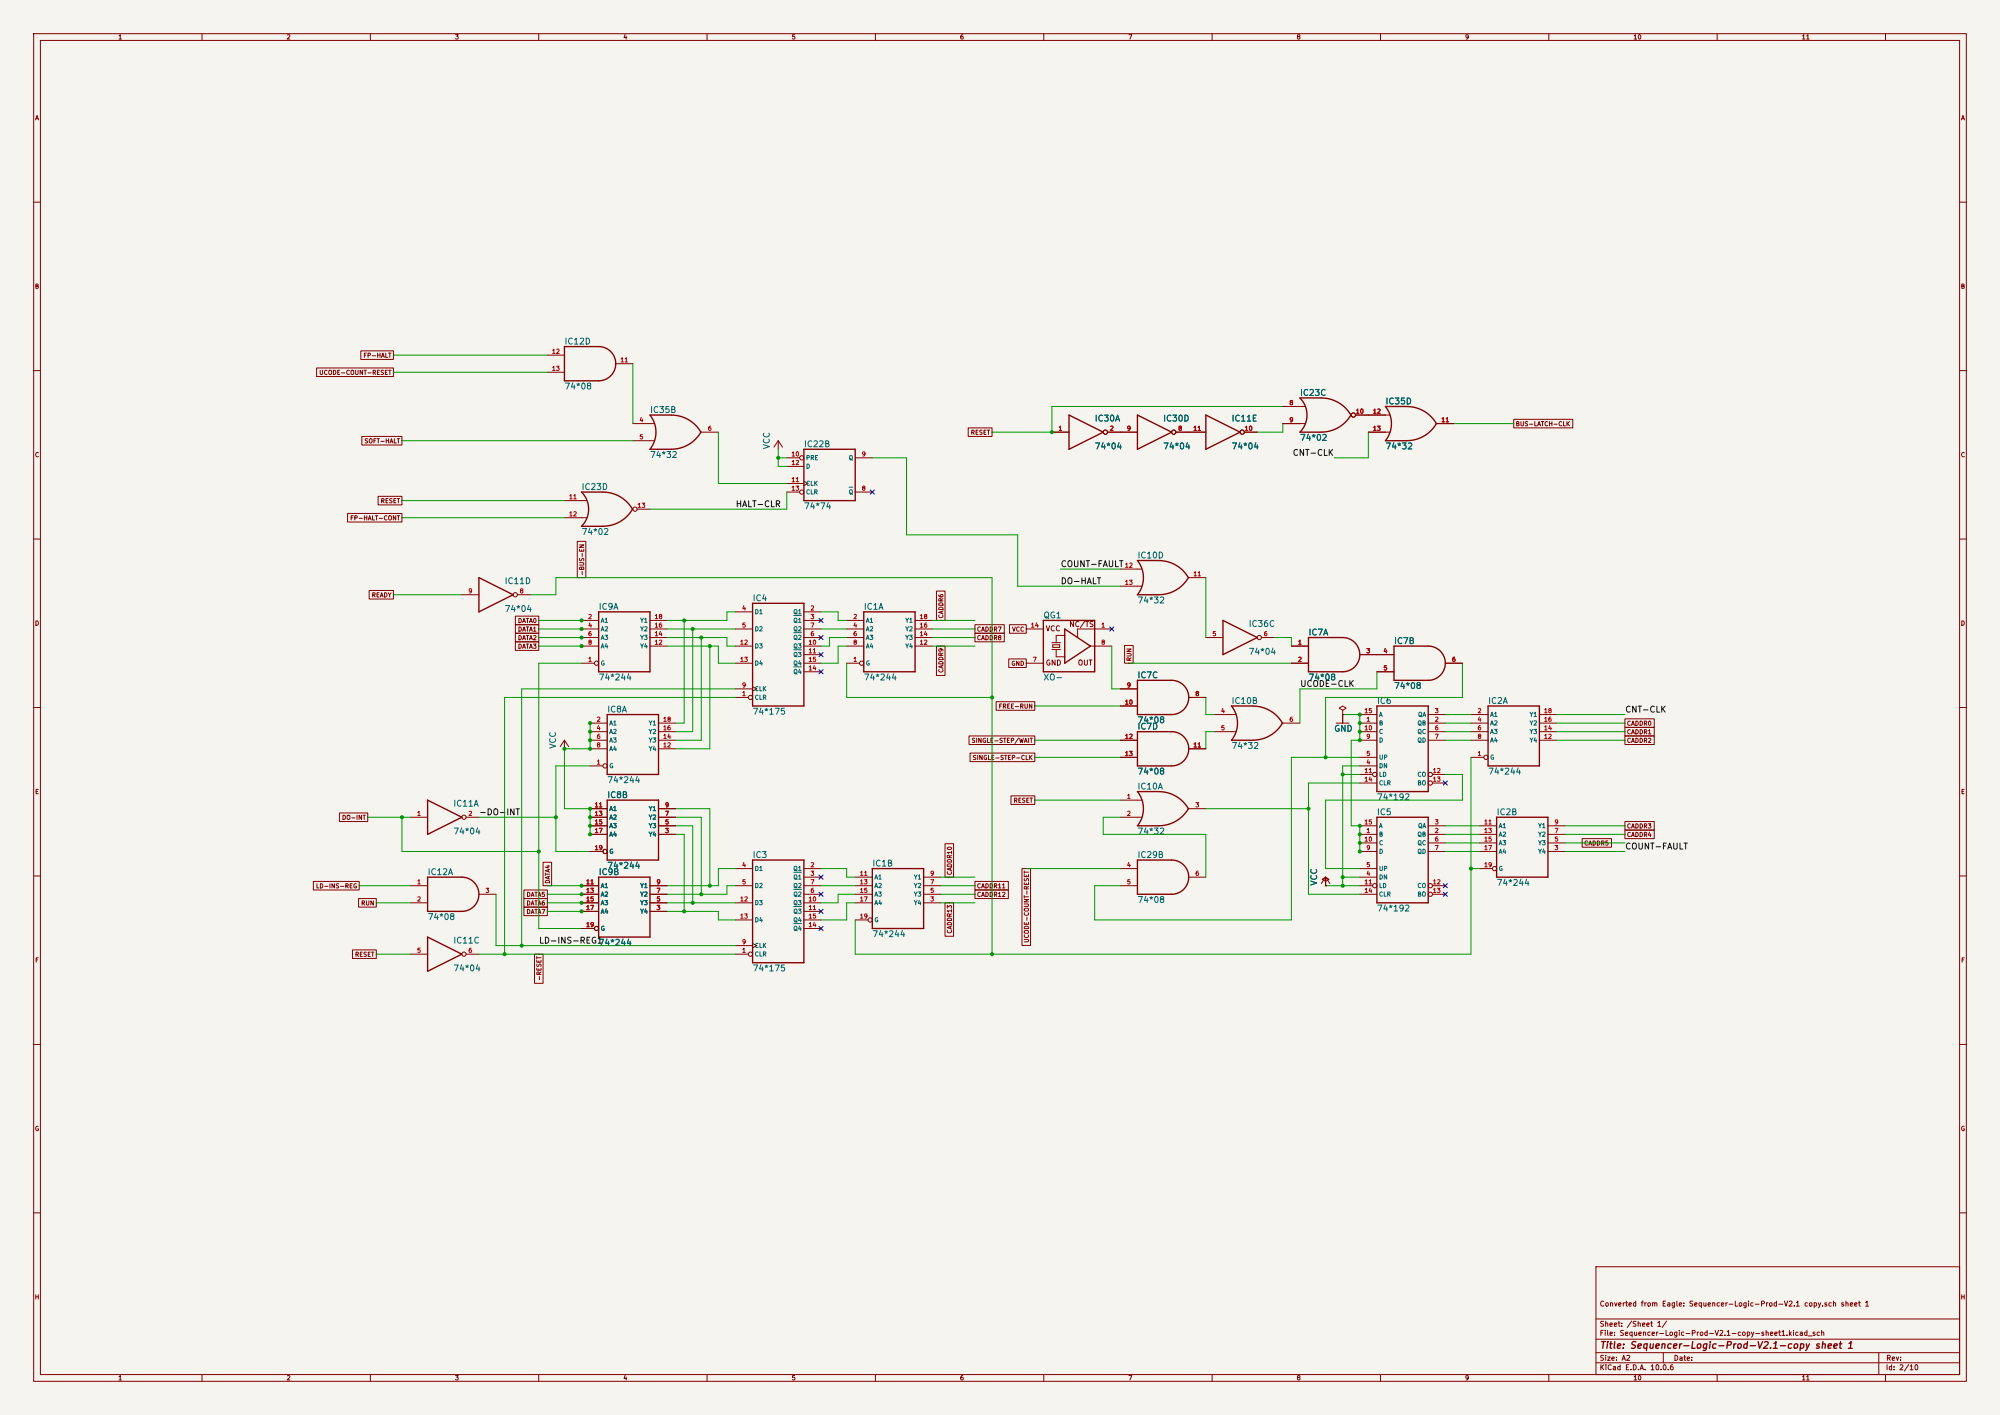
[picture p212: page 2]

Converted from Eagle: Sequencer-Logic-Prod-V2.1 copy.sch sheet 1

Sheet: /Sheet 1/
File: Sequencer-Logic-Prod-V2.1-copy-sheet1.kicad_sch
Title: Sequencer-Logic-Prod-V2.1-copy sheet 1

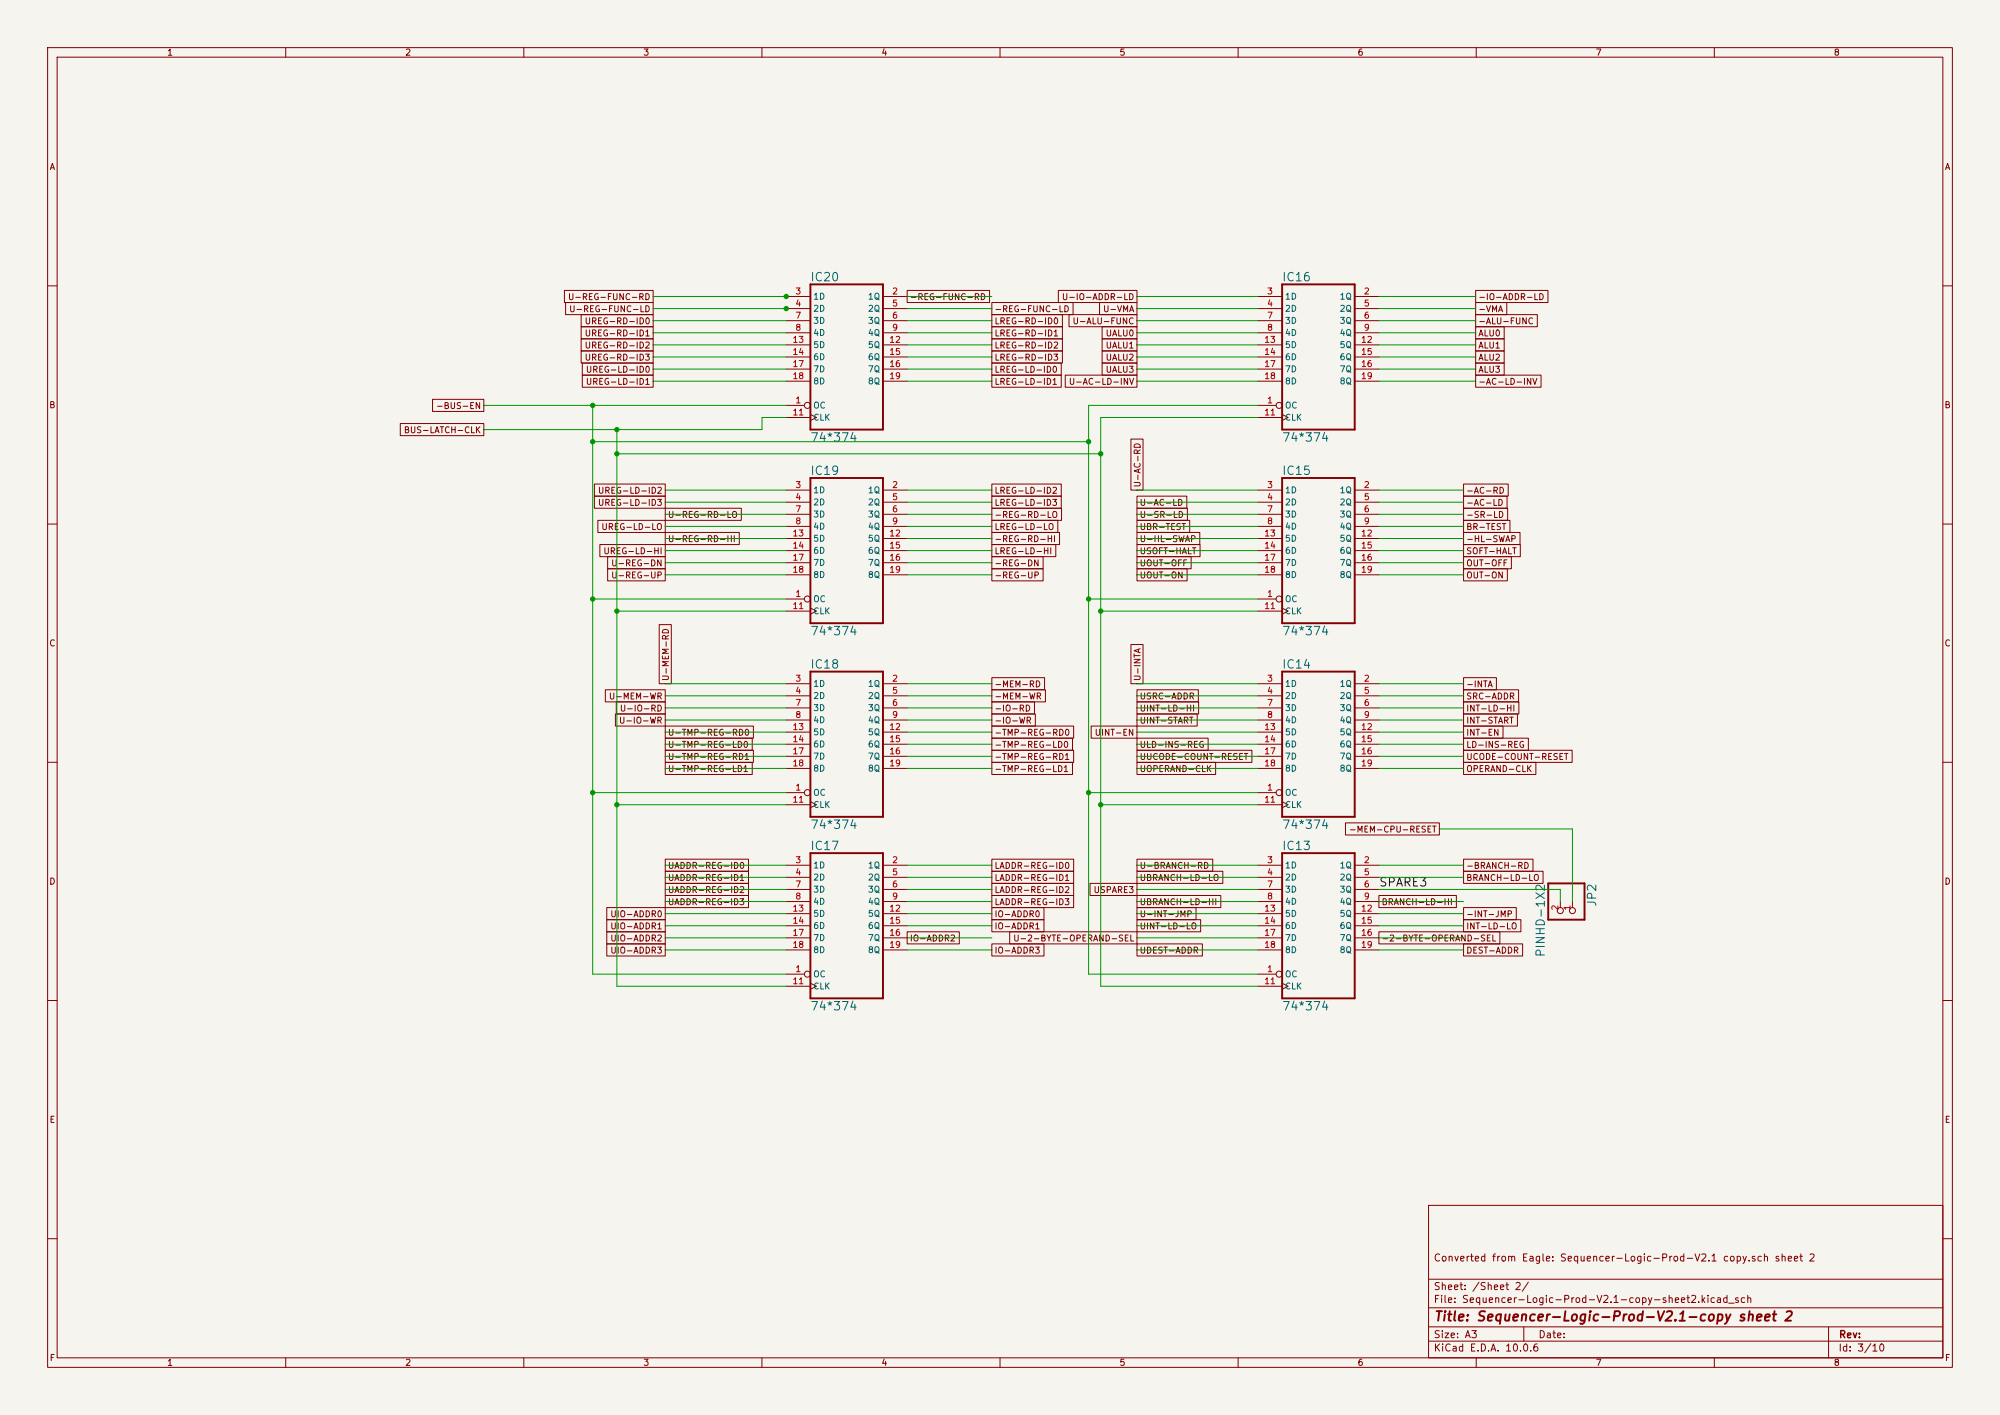
[picture p213: page 3]

LREG-RD-ID0 -REG-FUNC-LD -REG-DN -REG-FUNC-RD

-IO-ADDR-LD -TMP-REG-LD1

INT-LD-LO -2-BYTE-OPERAND-SEL USOFT-HALT UREG-LD-ID1 UREG-LD-ID0 UREG-RD-ID3 -BUS-EN

UREG-LD-HI UREG-LD-LO

BR-TEST -HL-SWAP

SOFT-HALT OUT-OFF OUT-ON

BRANCH-LD-HI U-REG-UP U-REG-DN

UADDR-REG-ID1 UADDR-REG-ID0 UIO-ADDR1

Converted from Eagle: Sequencer-Logic-Prod-V2.1 copy.sch sheet 2

Sheet: /Sheet 2/
File: Sequencer-Logic-Prod-V2.1-copy-sheet2.kicad_sch
Title: Sequencer-Logic-Prod-V2.1-copy sheet 2

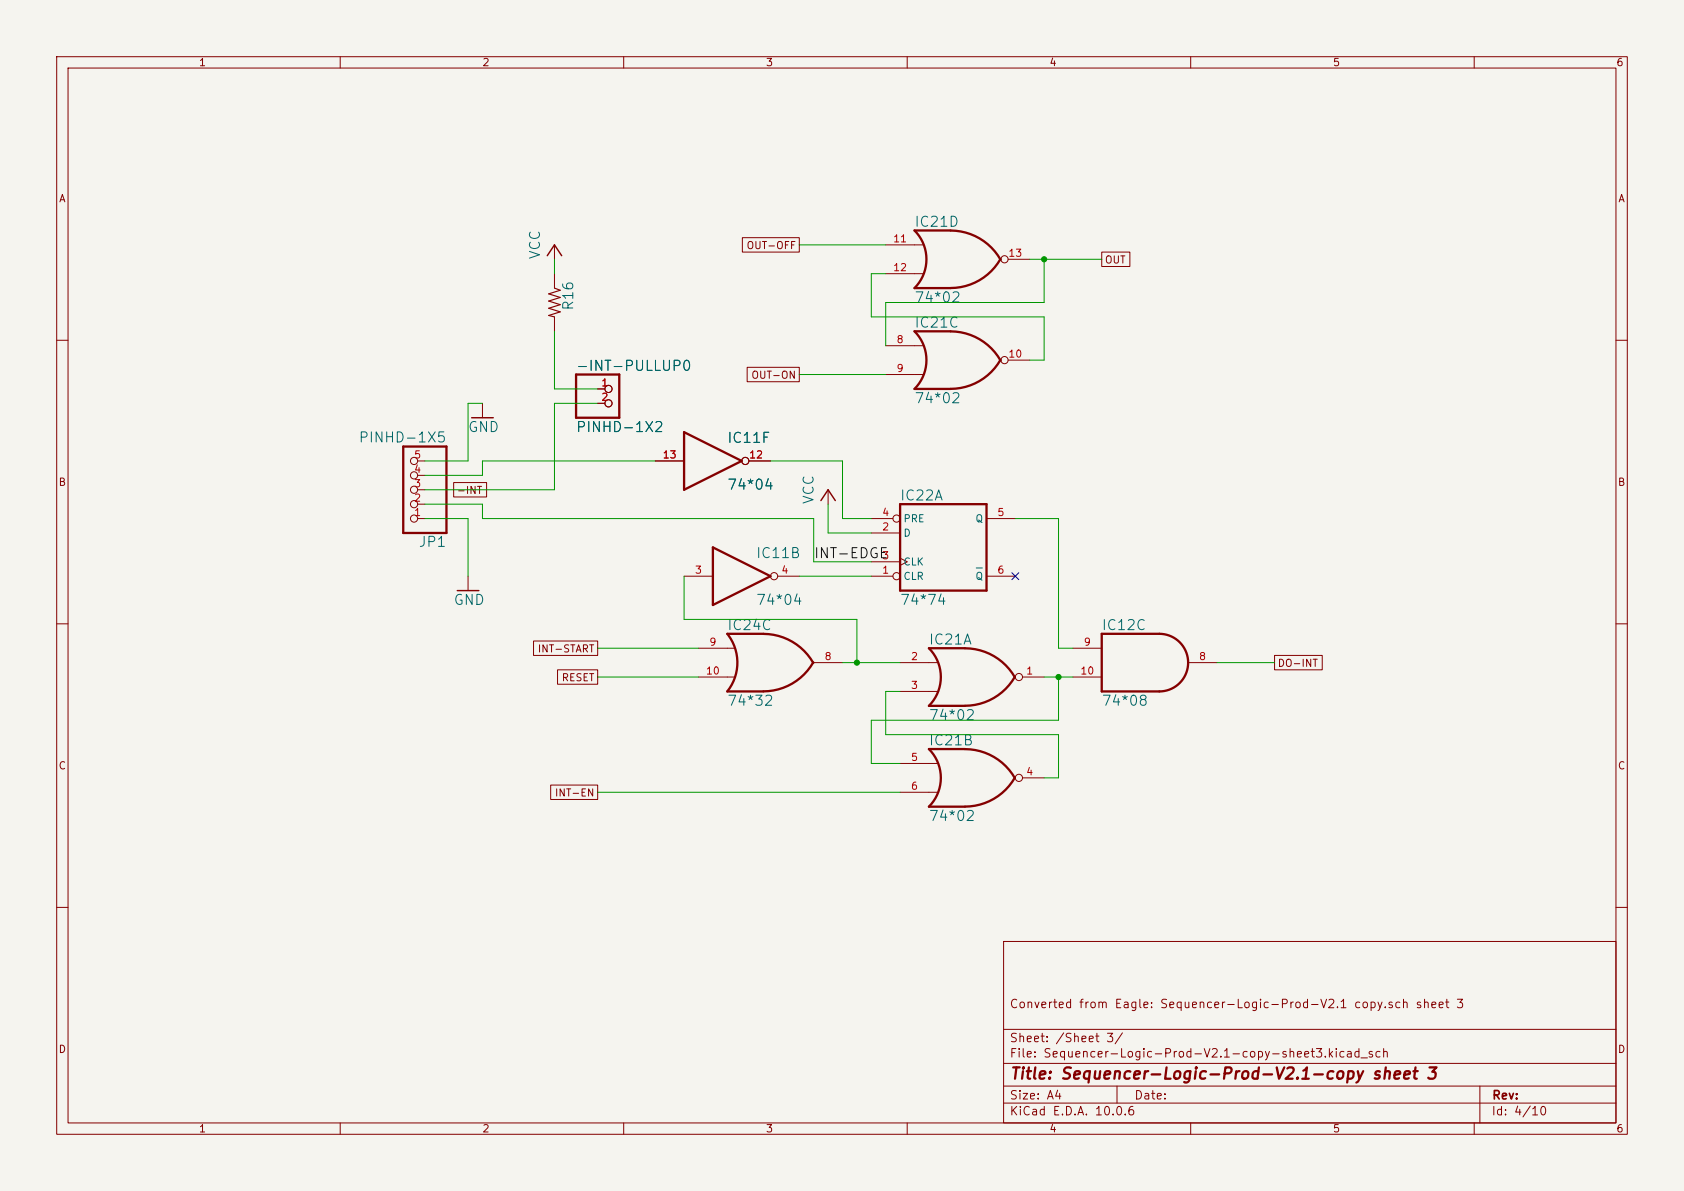
[picture p214: page 4]

DO-INT OUT-OFF -INT

Converted from Eagle: Sequencer-Logic-Prod-V2.1 copy.sch sheet 3

Sheet: /Sheet 3/
File: Sequencer-Logic-Prod-V2.1-copy-sheet3.kicad_sch
Title: Sequencer-Logic-Prod-V2.1-copy sheet 3

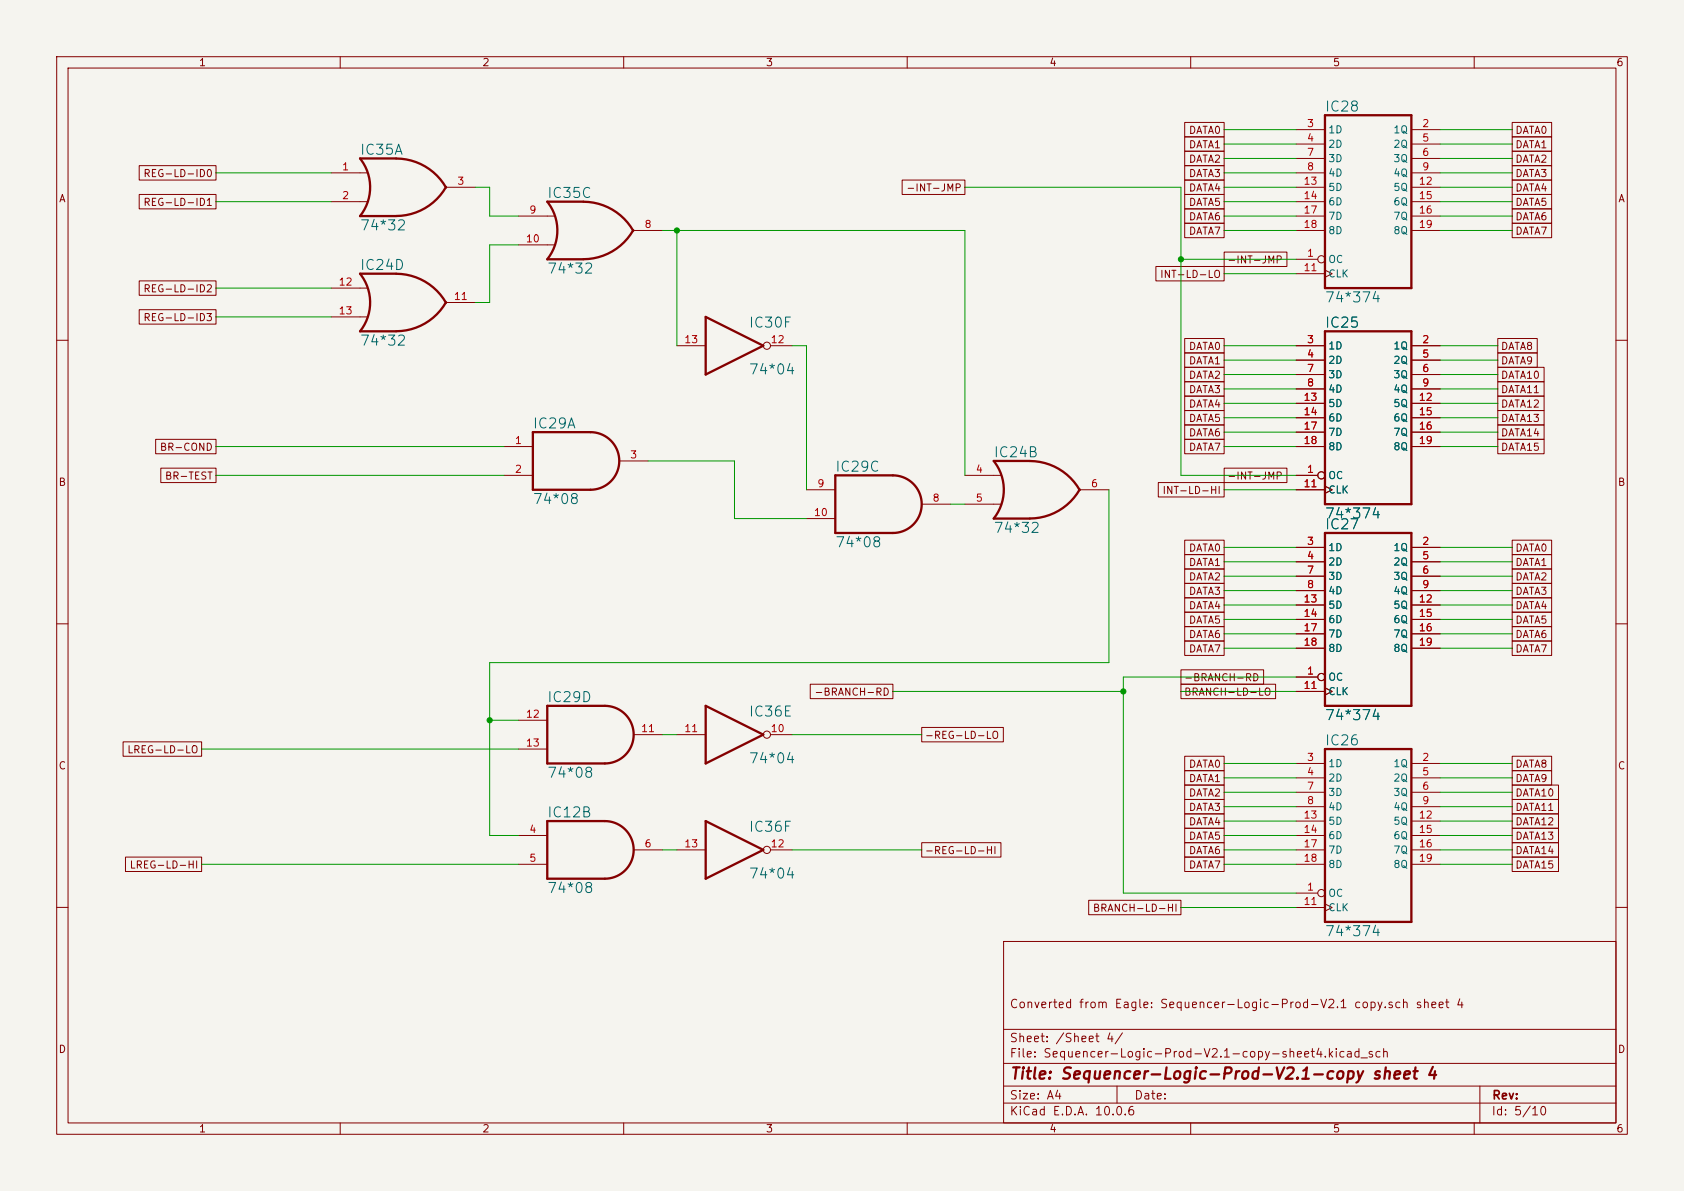
[picture p215: page 5]

DATA5 DATA4 DATA7 DATA3 DATA2 DATA1 DATA0 DATA5 DATA4 BRANCH-LD-HI BR-COND

Converted from Eagle: Sequencer-Logic-Prod-V2.1 copy.sch sheet 4

Sheet: /Sheet 4/
File: Sequencer-Logic-Prod-V2.1-copy-sheet4.kicad_sch
Title: Sequencer-Logic-Prod-V2.1-copy sheet 4

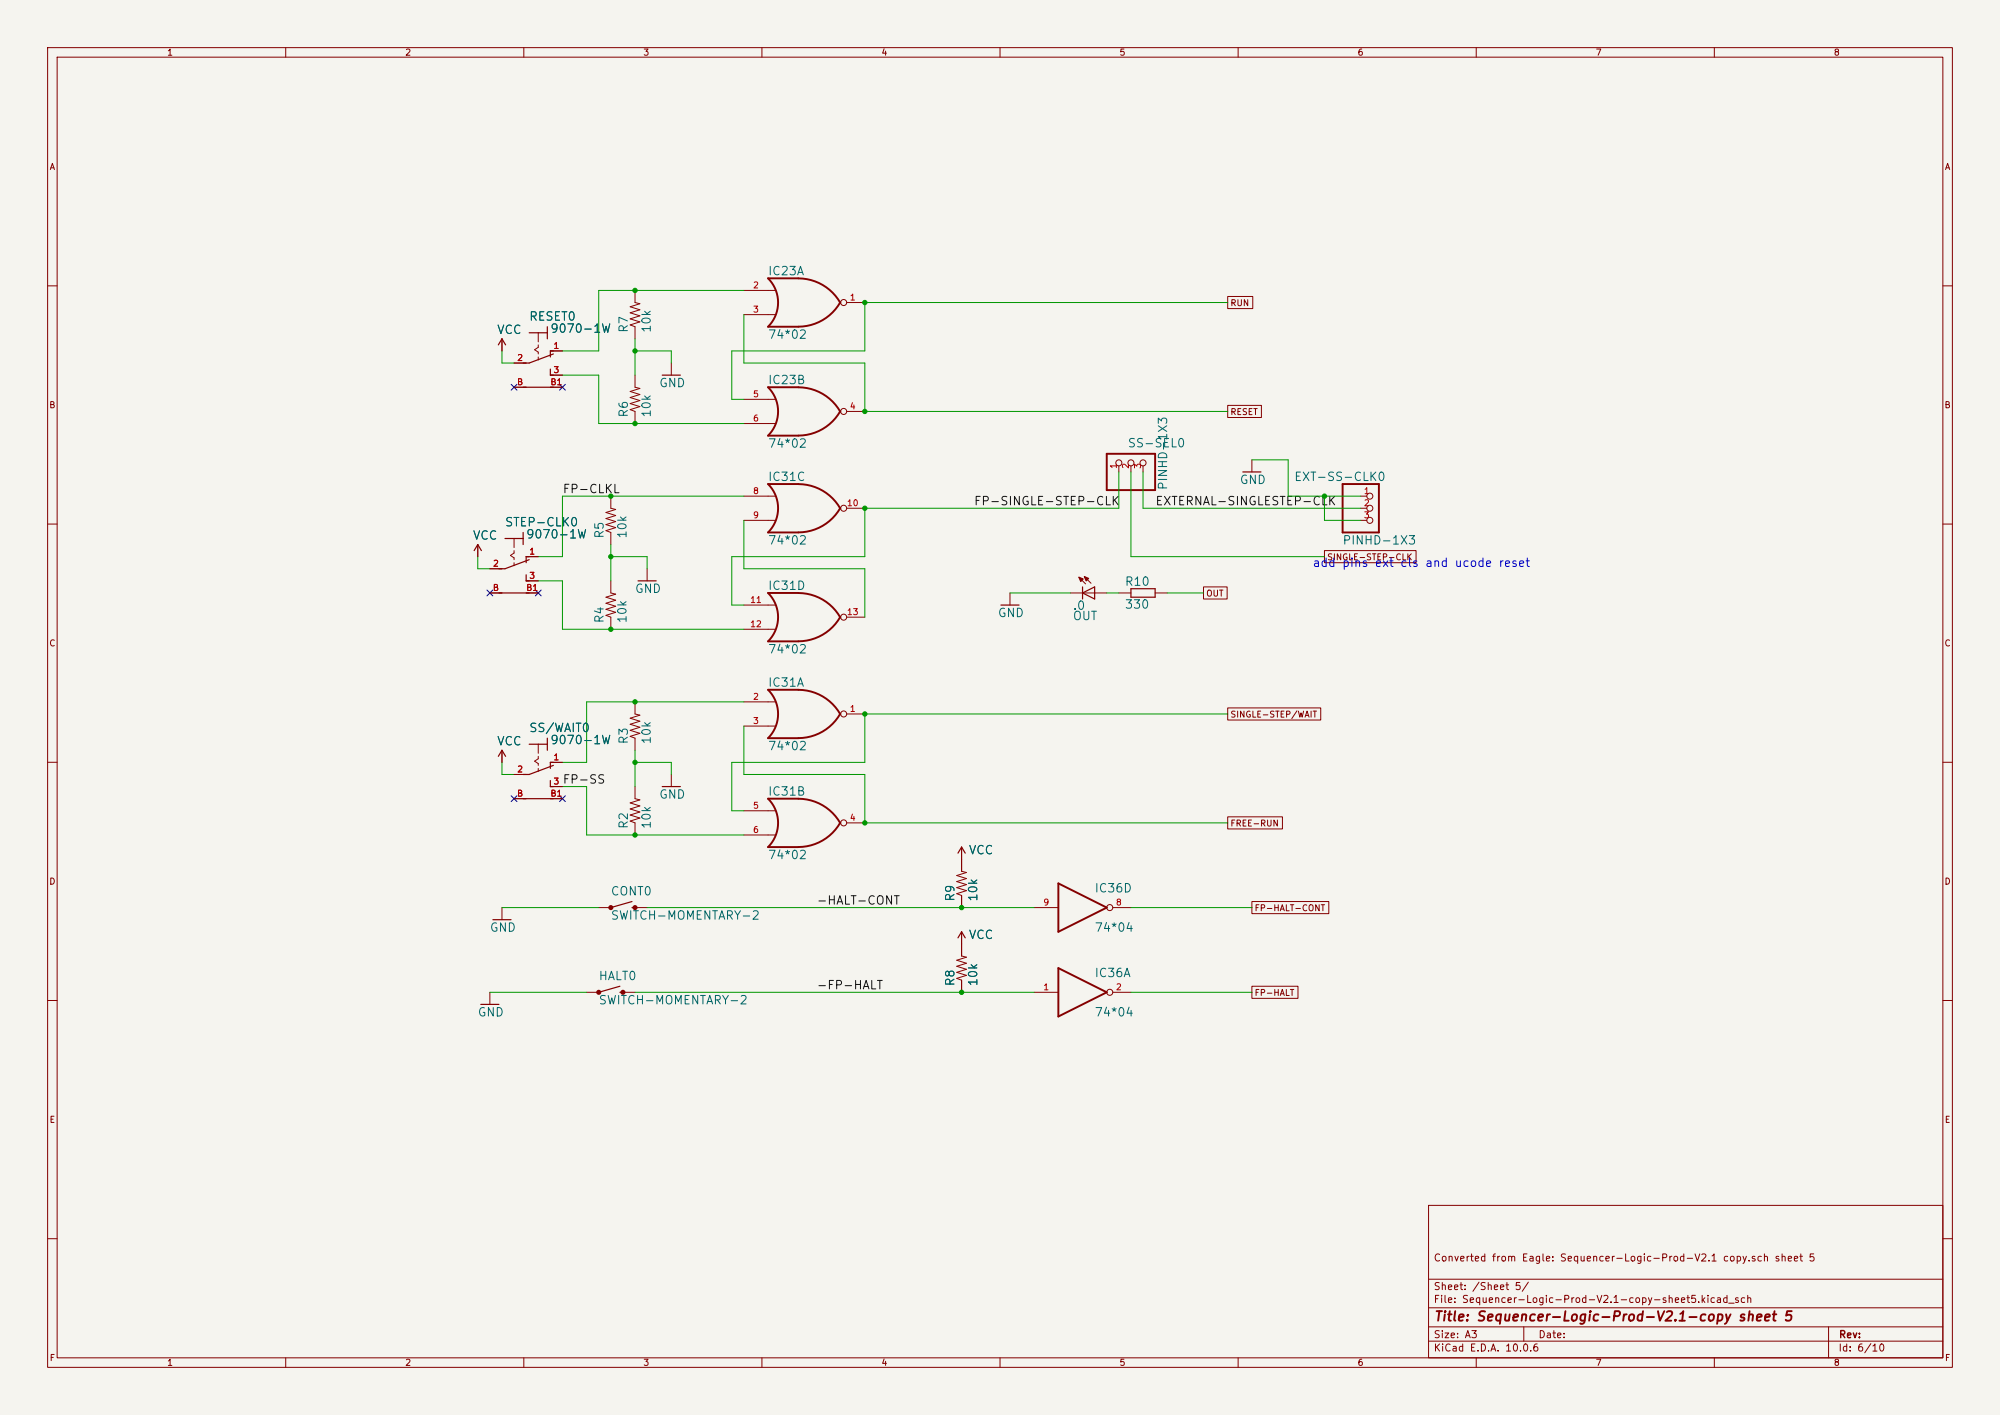
[picture p216: page 6]

FP-HALT-CONT SINGLE-STEP-CLK OUT RUN

FP-SINGLE-STEP-CLK

PINHD-1X3
add pins ext cls and ucode reset

SINGLE-STEP/WAIT
FP-HALT FREE-RUN

Converted from Eagle: Sequencer-Logic-Prod-V2.1 copy.sch sheet 5

Sheet: /Sheet 5/
File: Sequencer-Logic-Prod-V2.1-copy-sheet5.kicad_sch
Title: Sequencer-Logic-Prod-V2.1-copy sheet 5

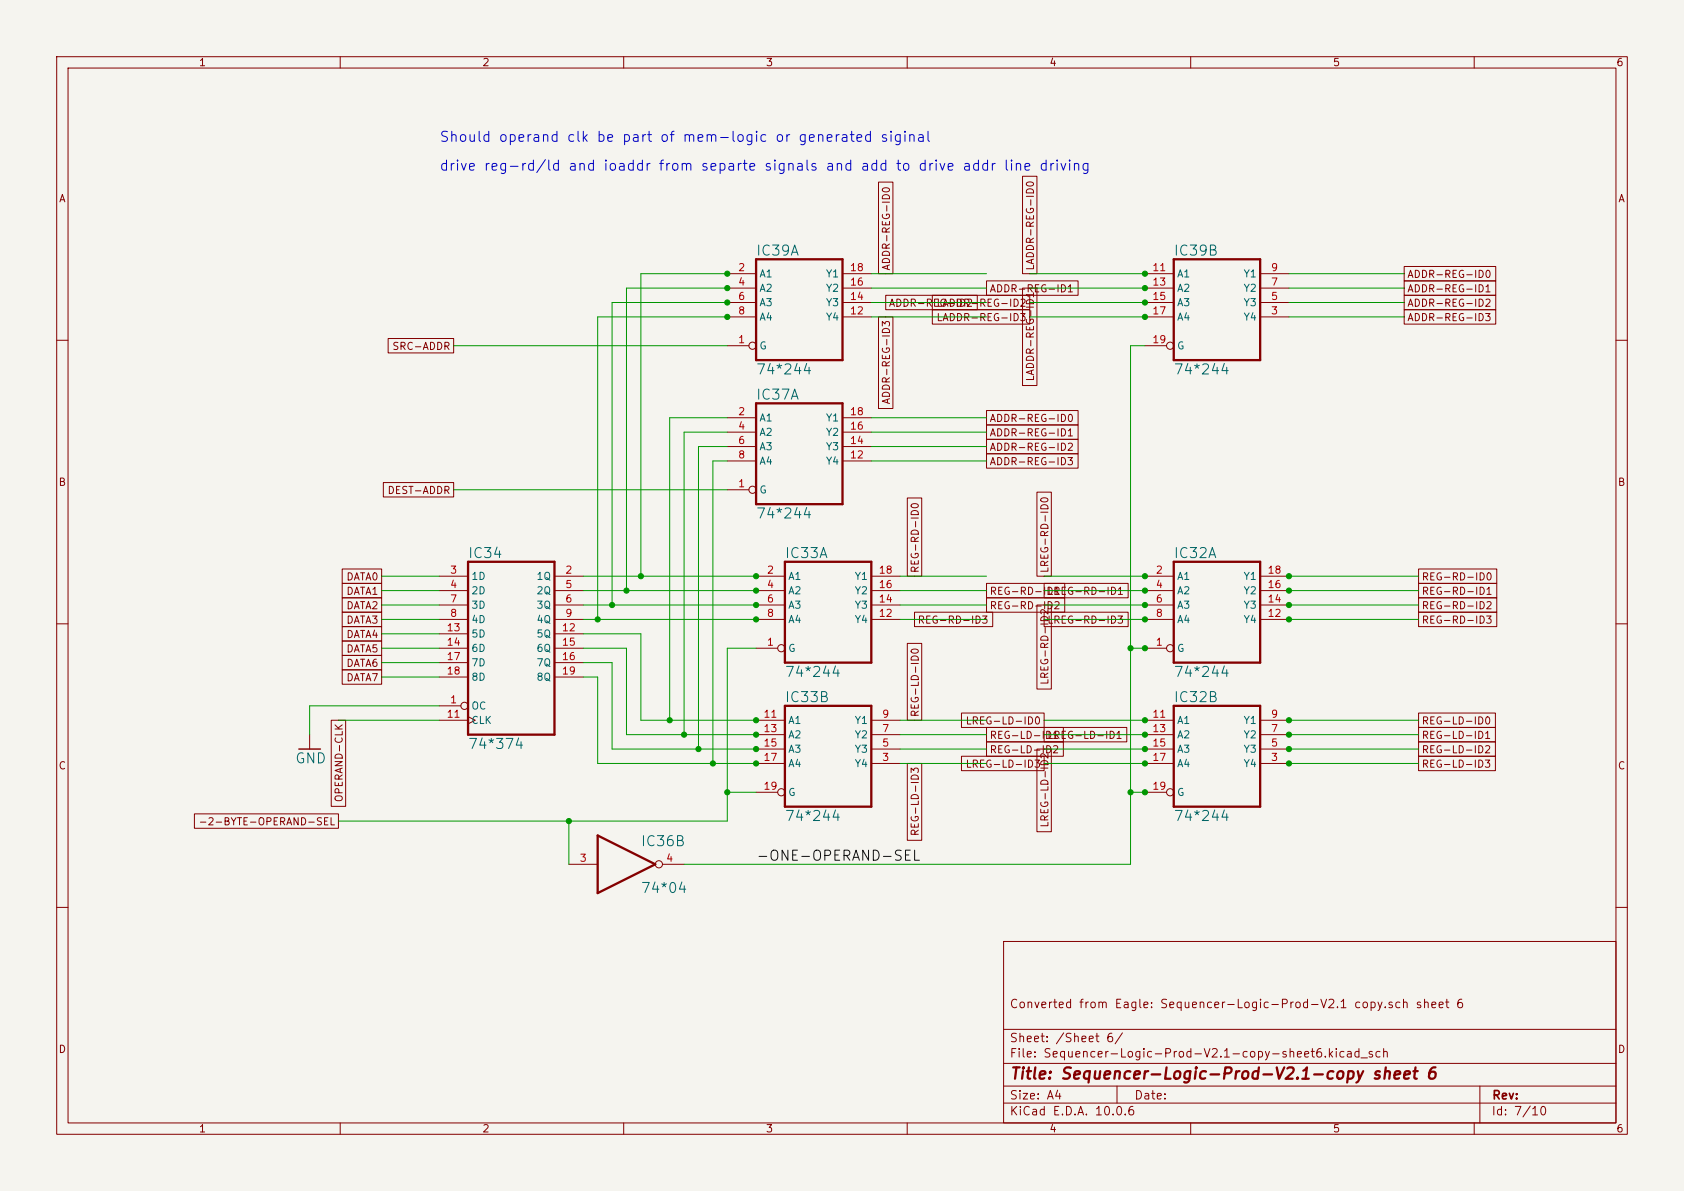
[picture p217: page 7]

Should operand clk be part of mem-logic or generated siginal

drive reg-rd/ld and ioaddr from separte signals and add to drive addr line driving
ADDR-REG-ID3 LREG-RD-ID2 REG-RD-ID3 REG-LD-ID3

ADDR-REG-ID0
ADDR-REG-ID1
ADDR-REG-ID2 REG-RD-ID1LREG-RD-ID1 REG-RD-ID2

DEST-ADDR -2-BYTE-OPERAND-SEL DATA7

LREG-LD-ID0 REG-LD-ID2 REG-LD-ID1

LREG-LD-ID1 LREG-LD-ID2

Converted from Eagle: Sequencer-Logic-Prod-V2.1 copy.sch sheet 6

Sheet: /Sheet 6/
File: Sequencer-Logic-Prod-V2.1-copy-sheet6.kicad_sch
Title: Sequencer-Logic-Prod-V2.1-copy sheet 6

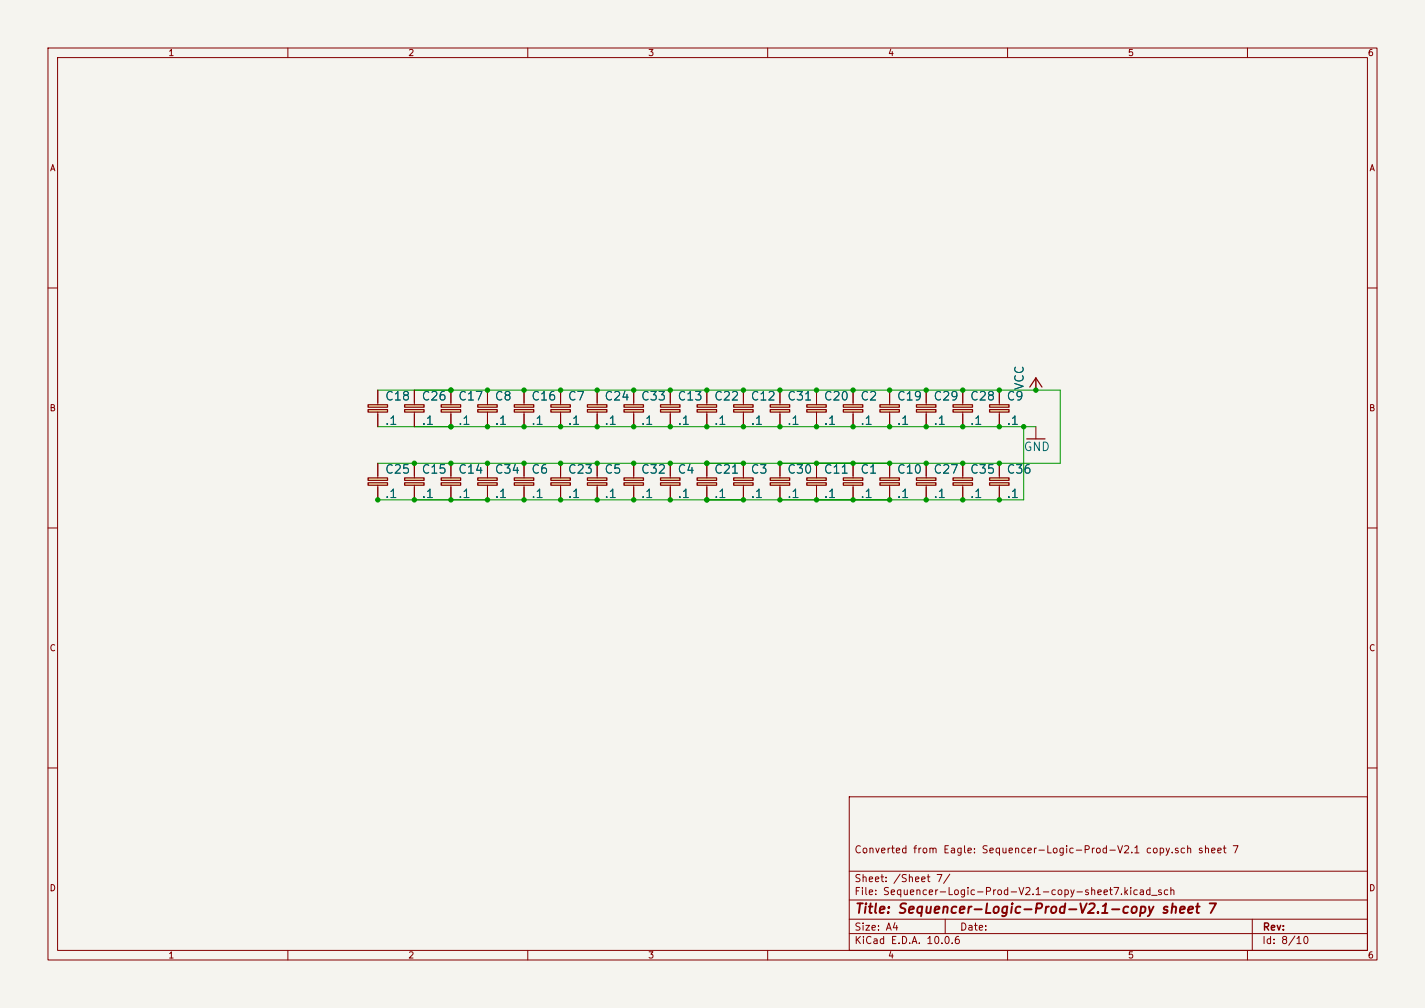
[picture p218: page 8]

Converted from Eagle: Sequencer-Logic-Prod-V2.1 copy.sch sheet 7

Sheet: /Sheet 7/
File: Sequencer-Logic-Prod-V2.1-copy-sheet7.kicad_sch
Title: Sequencer-Logic-Prod-V2.1-copy sheet 7

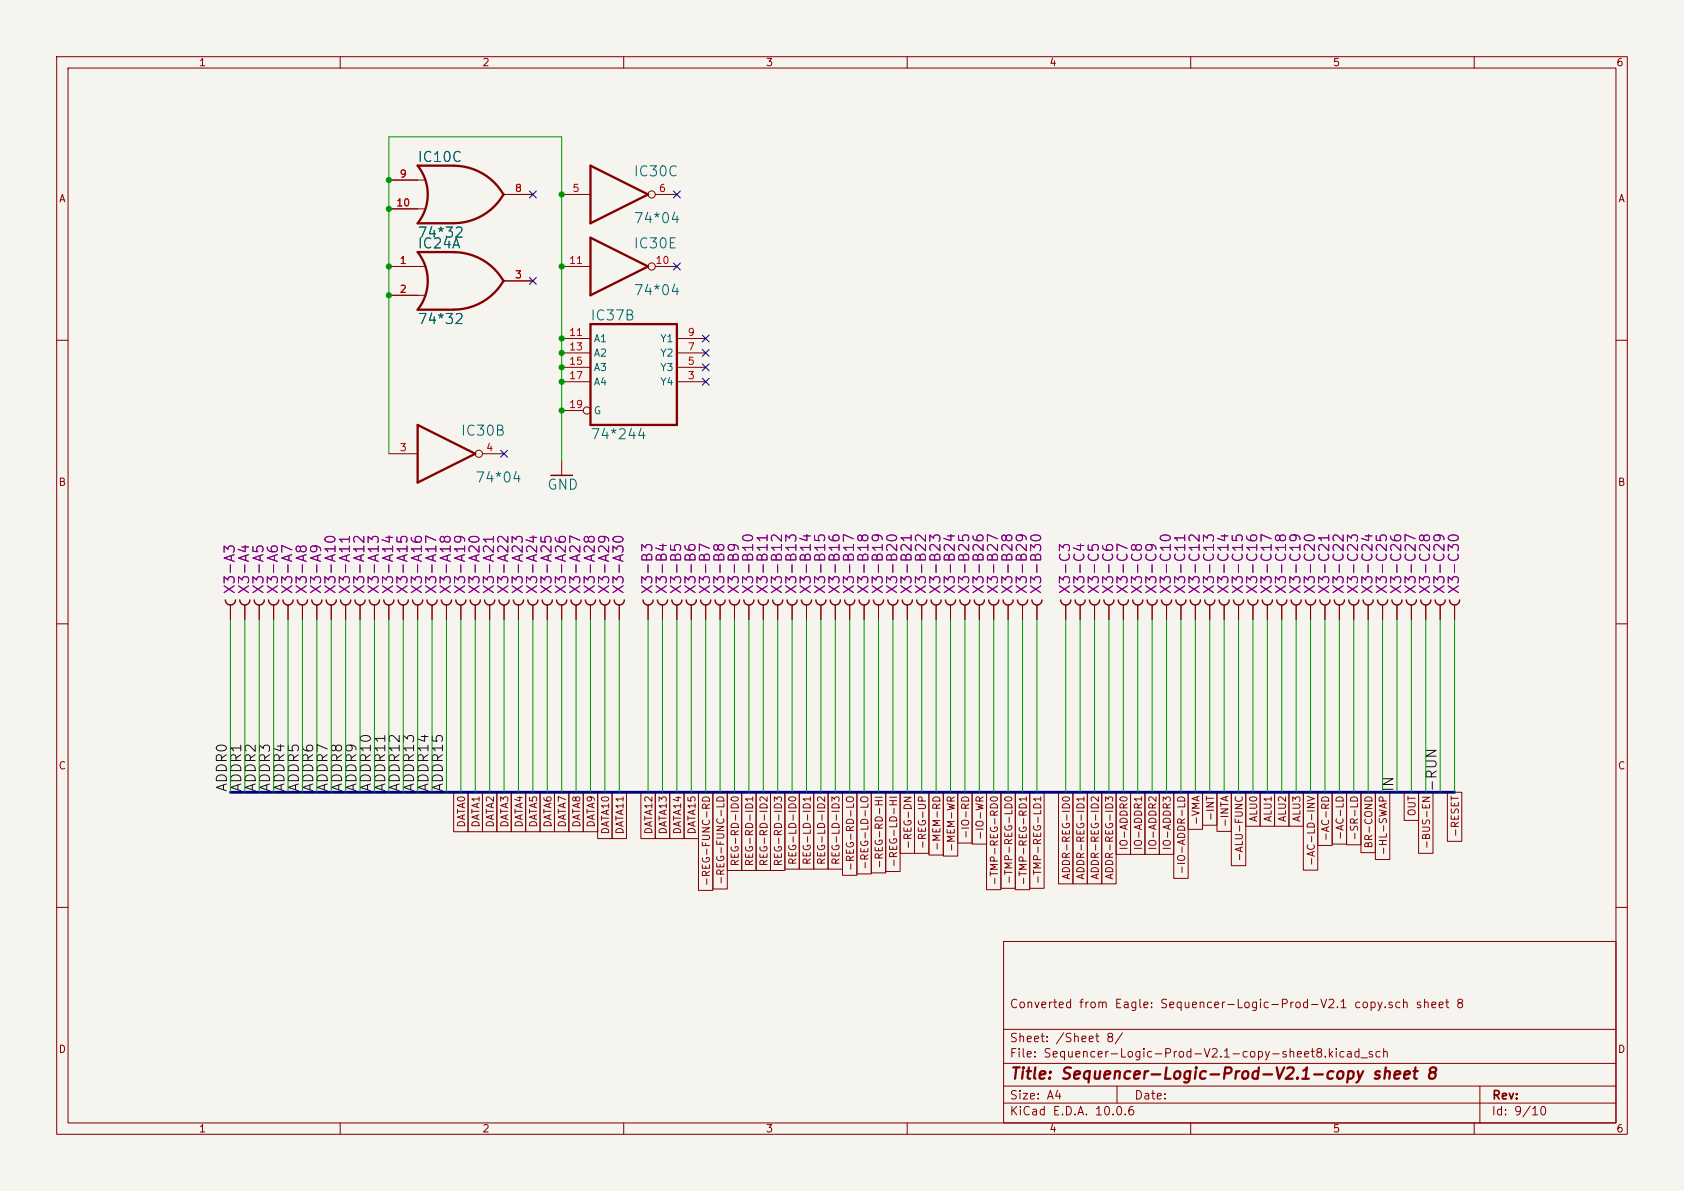
[picture p219: page 9]

Sheet: /Sheet 8/
File: Sequencer-Logic-Prod-V2.1-copy-sheet8.kicad_sch
Title: Sequencer-Logic-Prod-V2.1-copy sheet 8

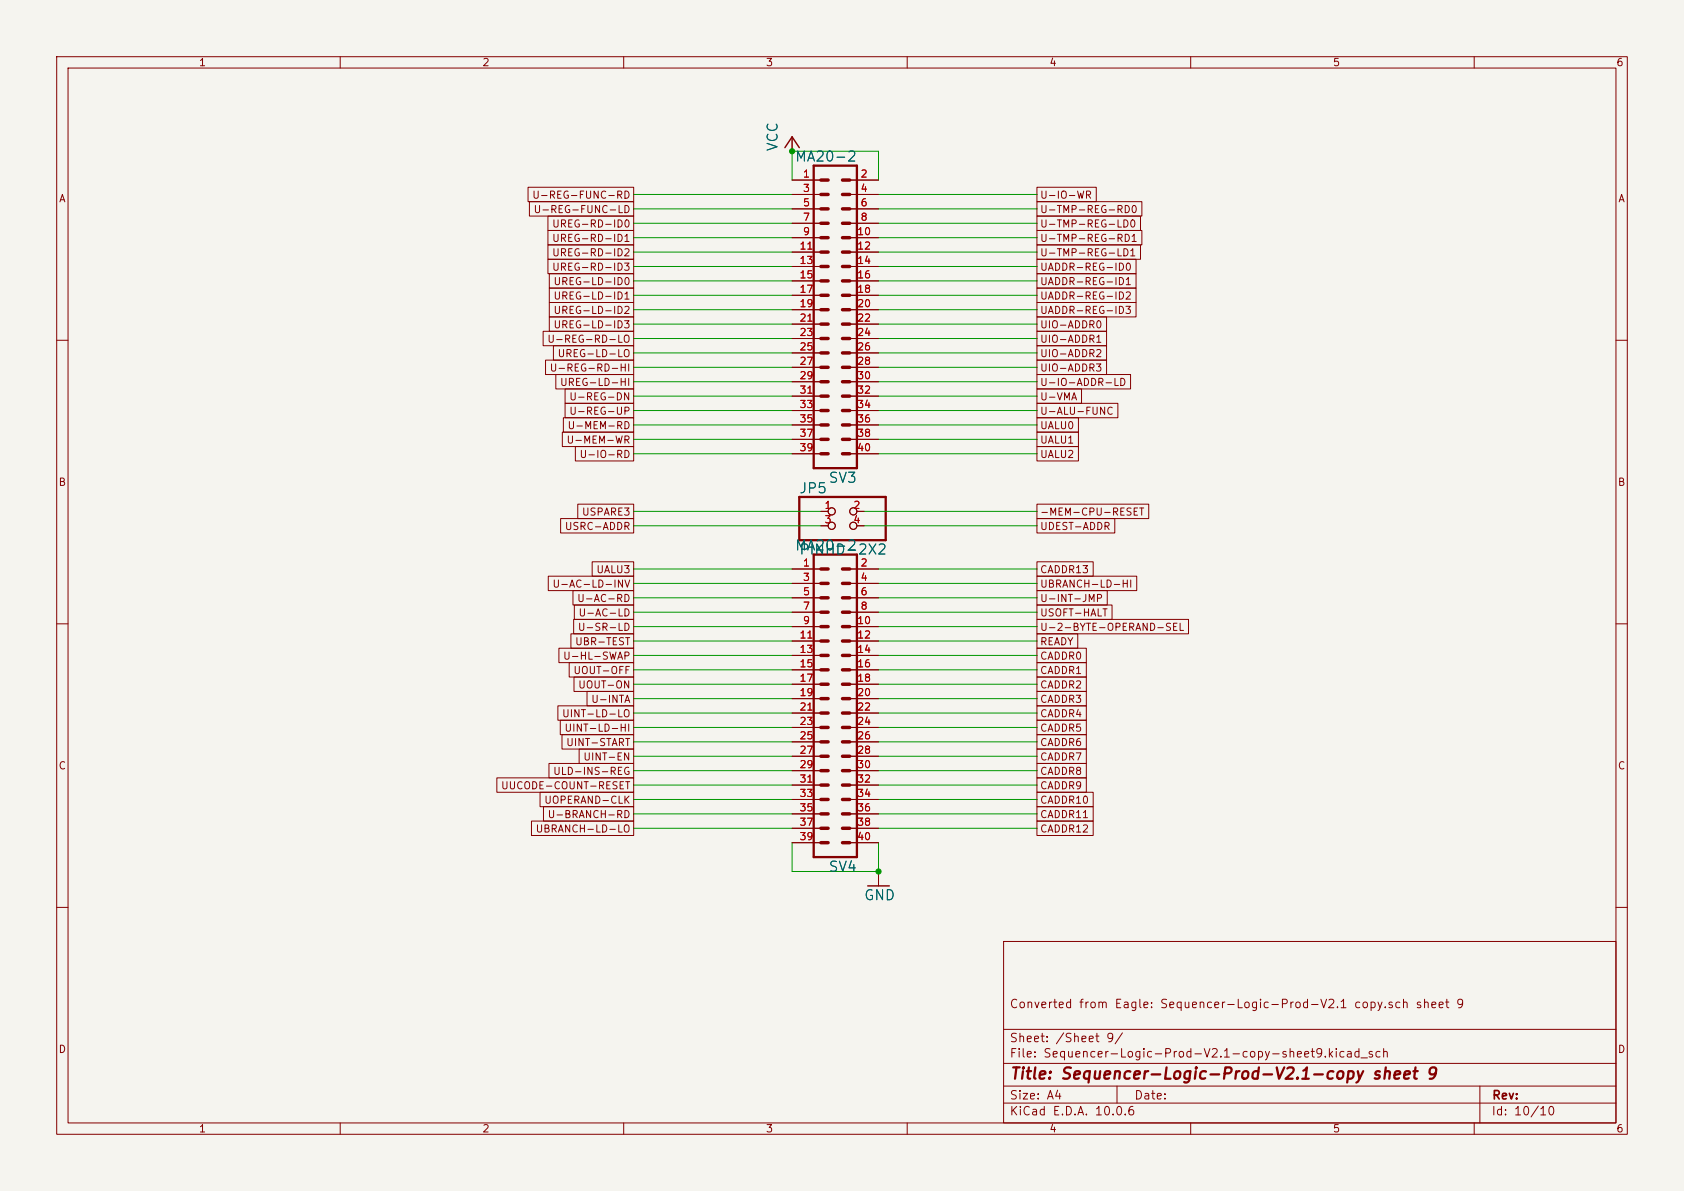
[picture p220: page 10]

UINT-START UINT-LD-HI USRC-ADDR U-SR-LD U-AC-LD U-AC-RD U-AC-LD-INV UBR-TEST UALU3 USPARE3 U-REG-FUNC-LD U-IO-RD U-MEM-WR U-MEM-RD U-REG-UP U-REG-DN
UREG-RD-ID1 U-BRANCH-RD UOPERAND-CLK UUCODE-COUNT-RESET ULD-INS-REG UINT-EN

U-REG-RD-LO
UREG-LD-HI U-REG-RD-HI UREG-LD-LO

U-INTA U-HL-SWAP UBRANCH-LD-LO

UOUT-OFF UOUT-ON

Converted from Eagle: Sequencer-Logic-Prod-V2.1 copy.sch sheet 9

Sheet: /Sheet 9/
File: Sequencer-Logic-Prod-V2.1-copy-sheet9.kicad_sch
Title: Sequencer-Logic-Prod-V2.1-copy sheet 9
