ksr/YACC1-D/hardware/cards/sequencer-memory/accessories/eeprom-adaptor/kicad/reports/sequencer-memory-eeprom-adaptor-schematic.pdf

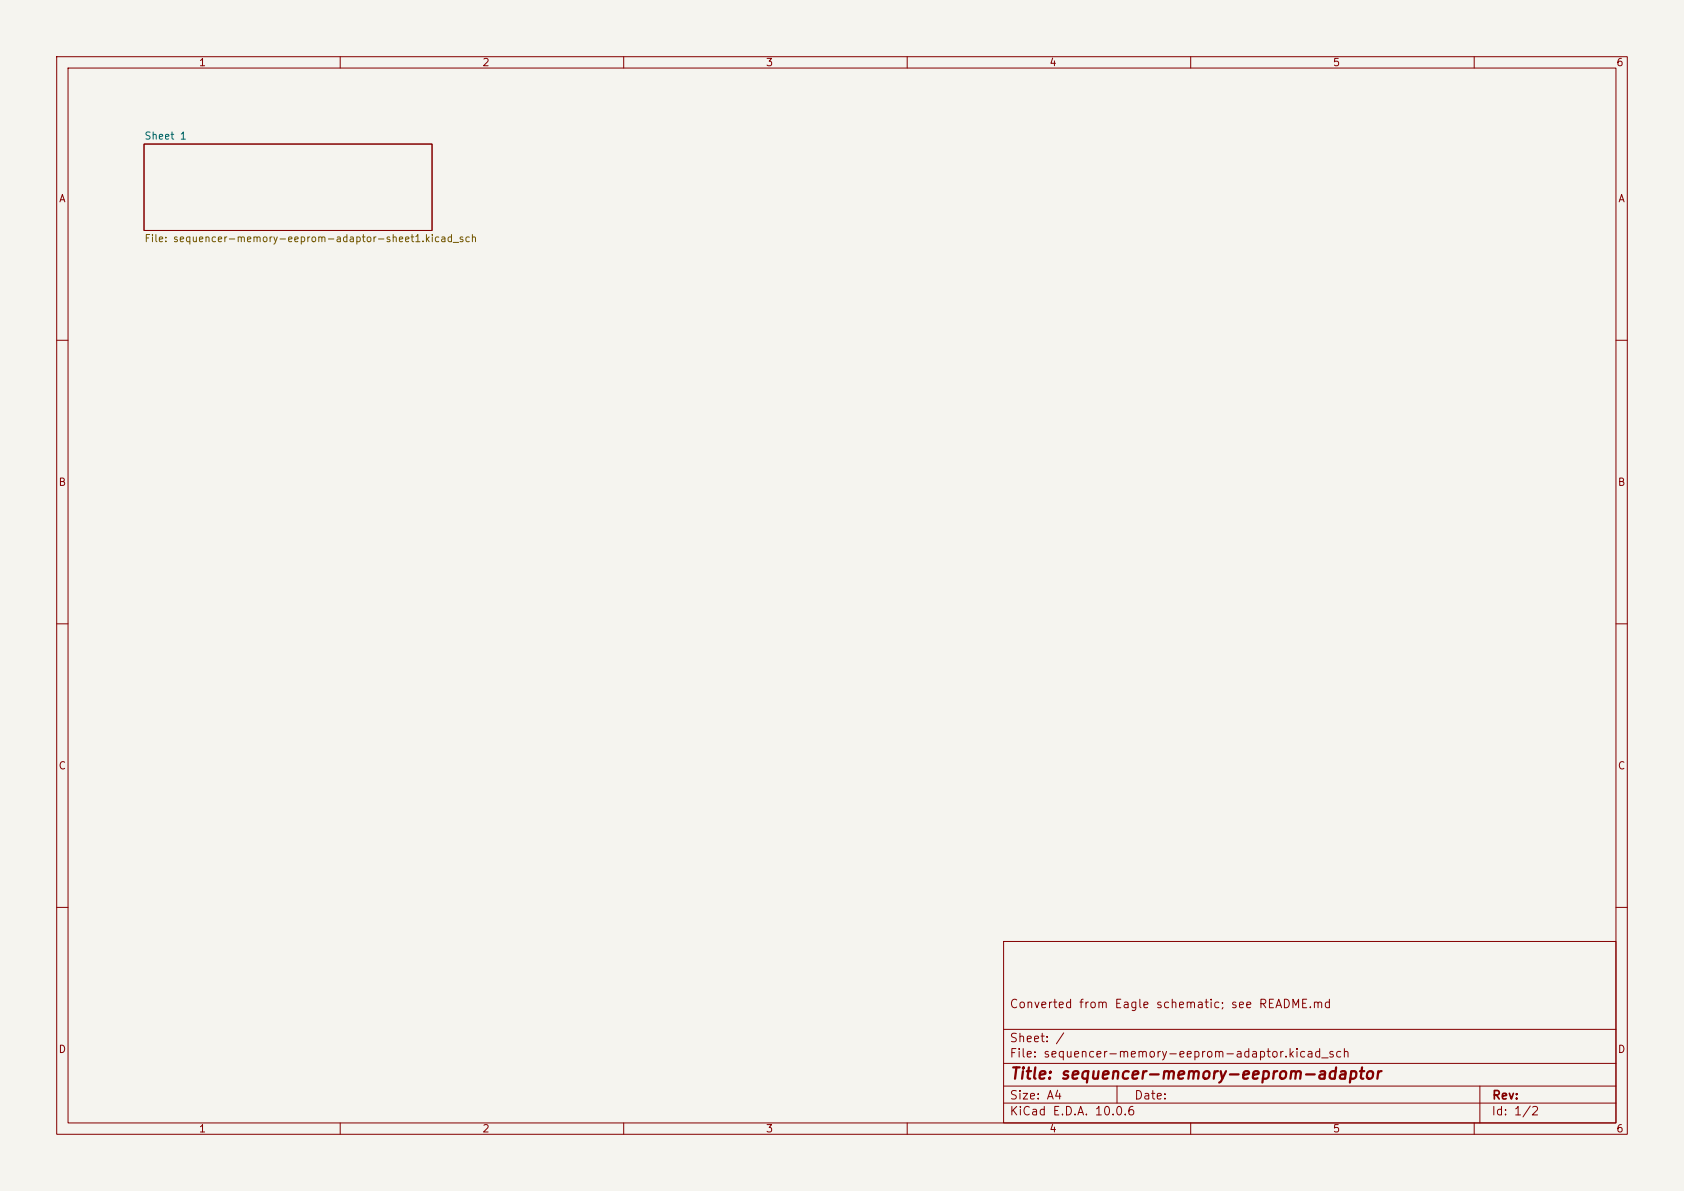
[picture p232: page 1]

File: sequencer-memory-eeprom-adaptor-sheet1.kicad_sch

Converted from Eagle schematic; see README.md

Sheet: /
File: sequencer-memory-eeprom-adaptor.kicad_sch
Title: sequencer-memory-eeprom-adaptor

Size: A4 | Rev:
KiCad E.D.A. 10.0.6 | Id: 1/2

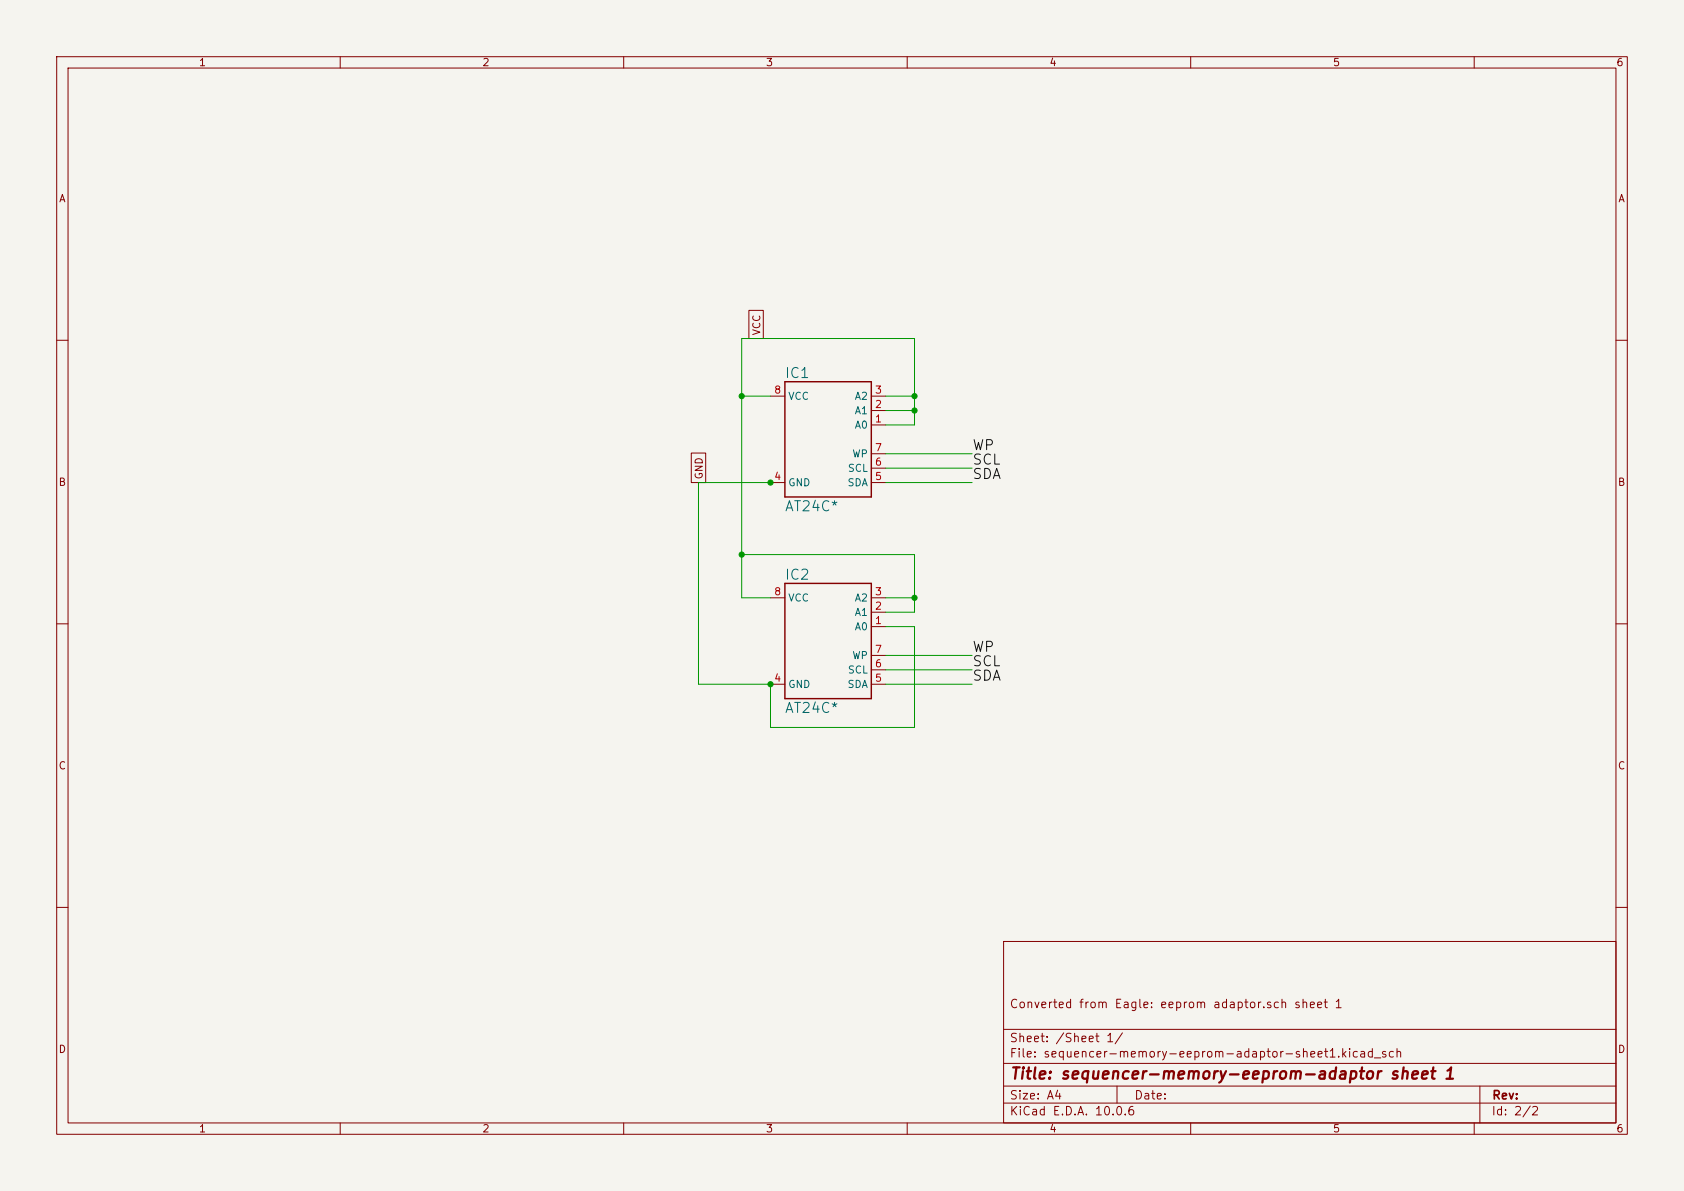
[picture p233: page 2]

Converted from Eagle: eeprom adaptor.sch sheet 1

Sheet: /Sheet 1/
File: sequencer-memory-eeprom-adaptor-sheet1.kicad_sch
Title: sequencer-memory-eeprom-adaptor sheet 1

Size: A4 | Rev:
KiCad E.D.A. 10.0.6 | Id: 2/2
