ksr/YACC1-D/hardware/cards/sequencer-logic/eagle/v2.1/orig size/pdf/Sequencer-Logic-Prod-V2.1-board.pdf

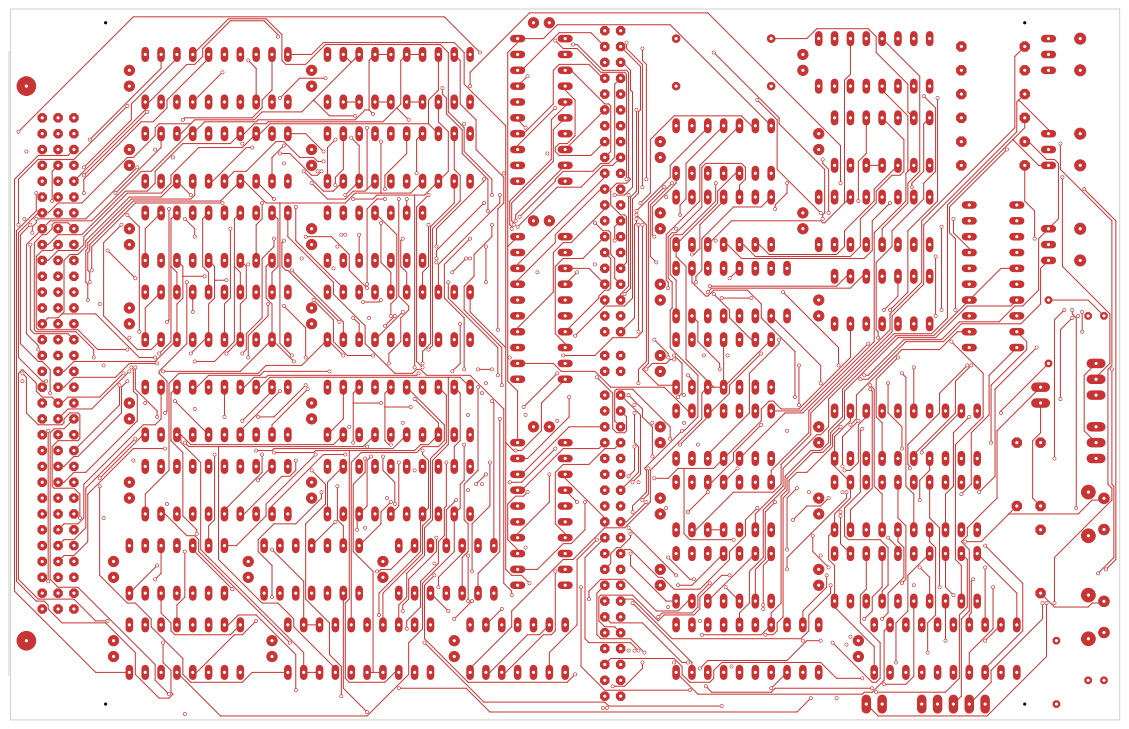
[picture p234: page 1]

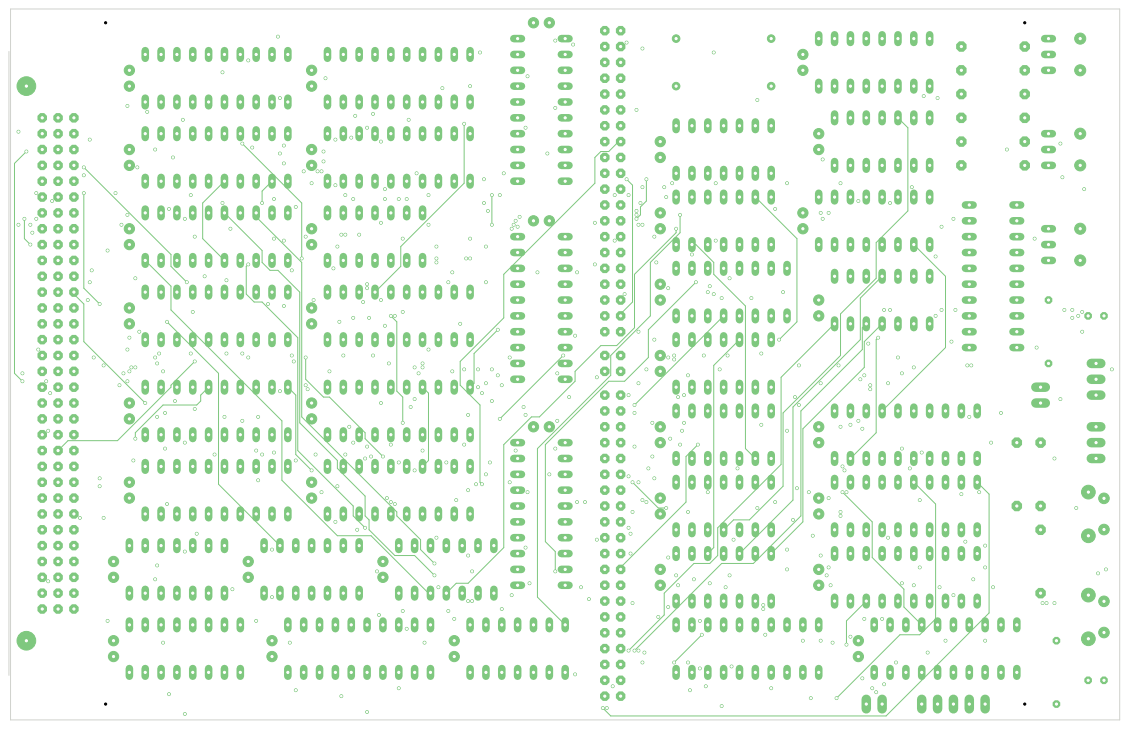
[picture p235: page 2]

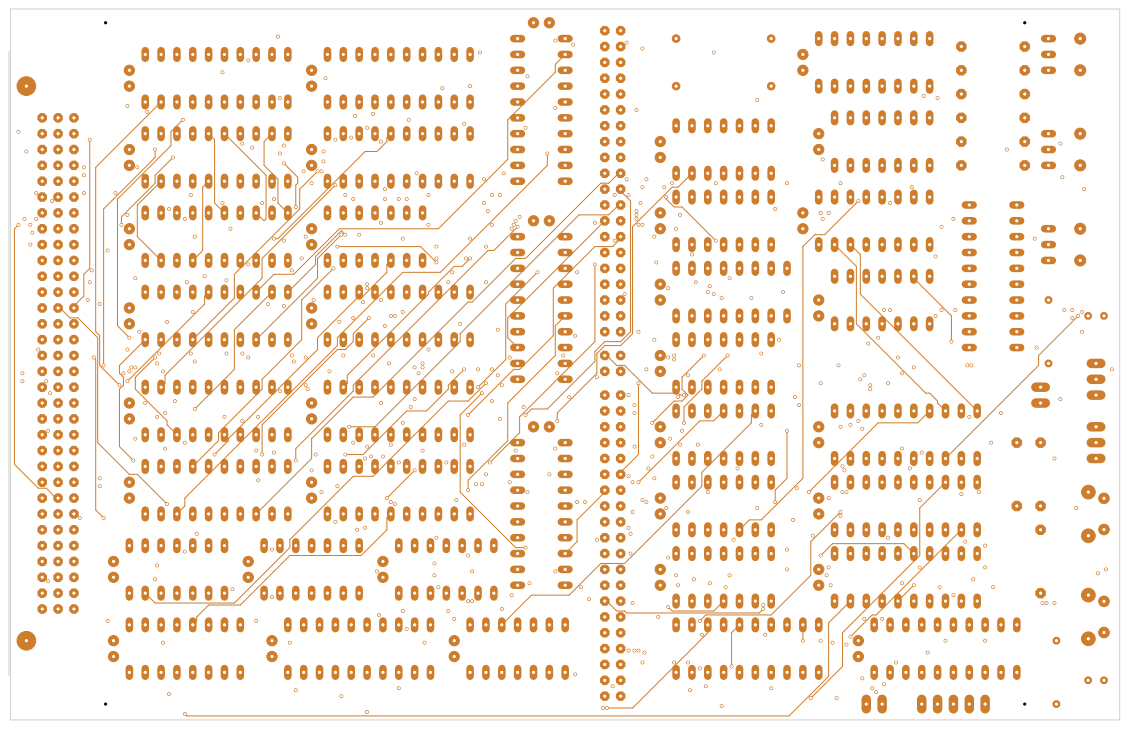
[picture p236: page 3]

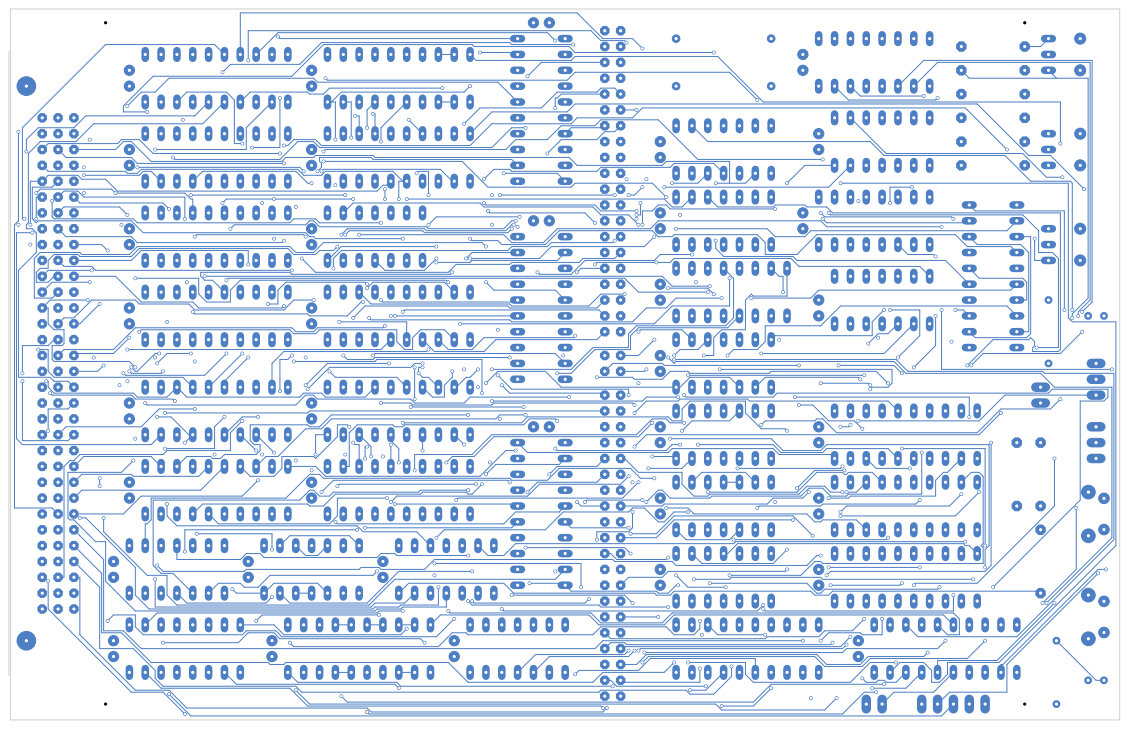
[picture p237: page 4]

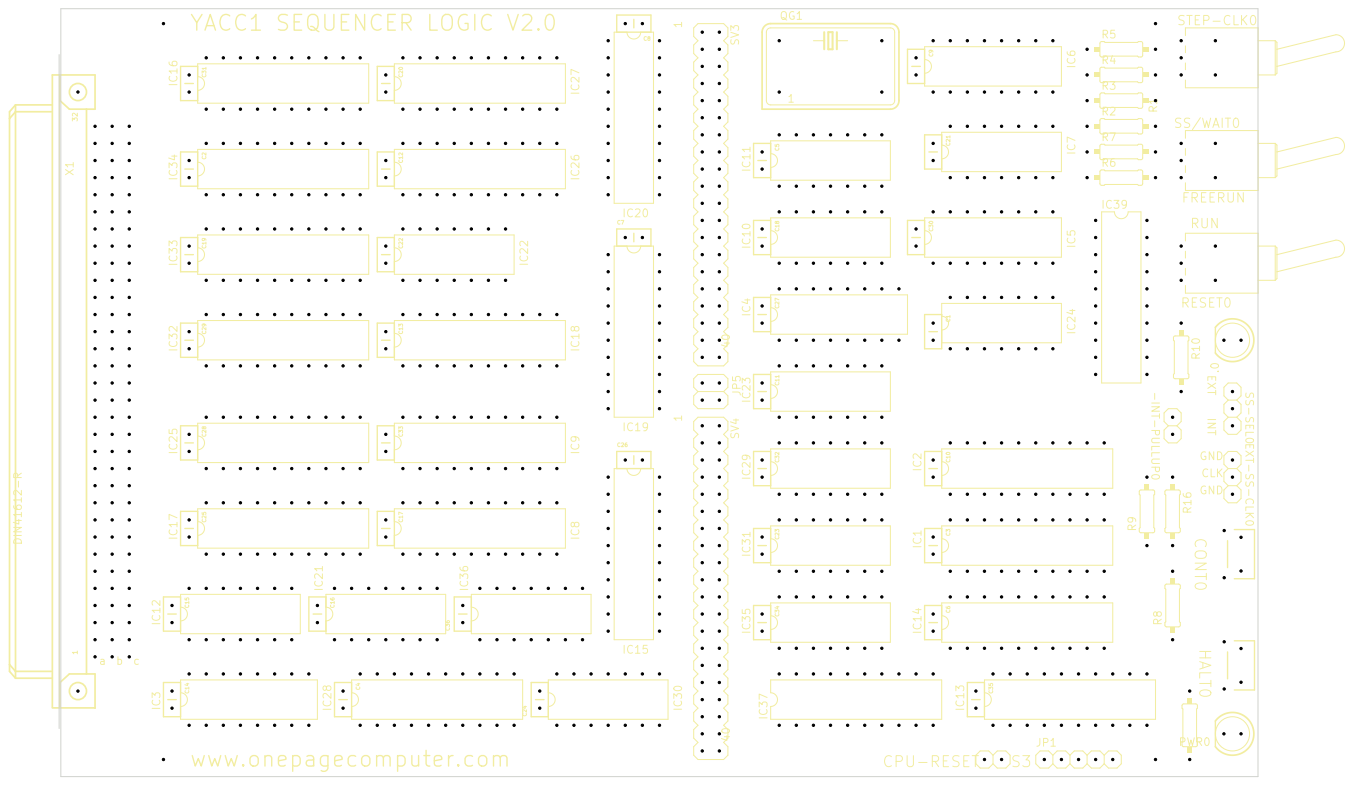
[picture p238: page 5]

GND EXT INT FREERUN

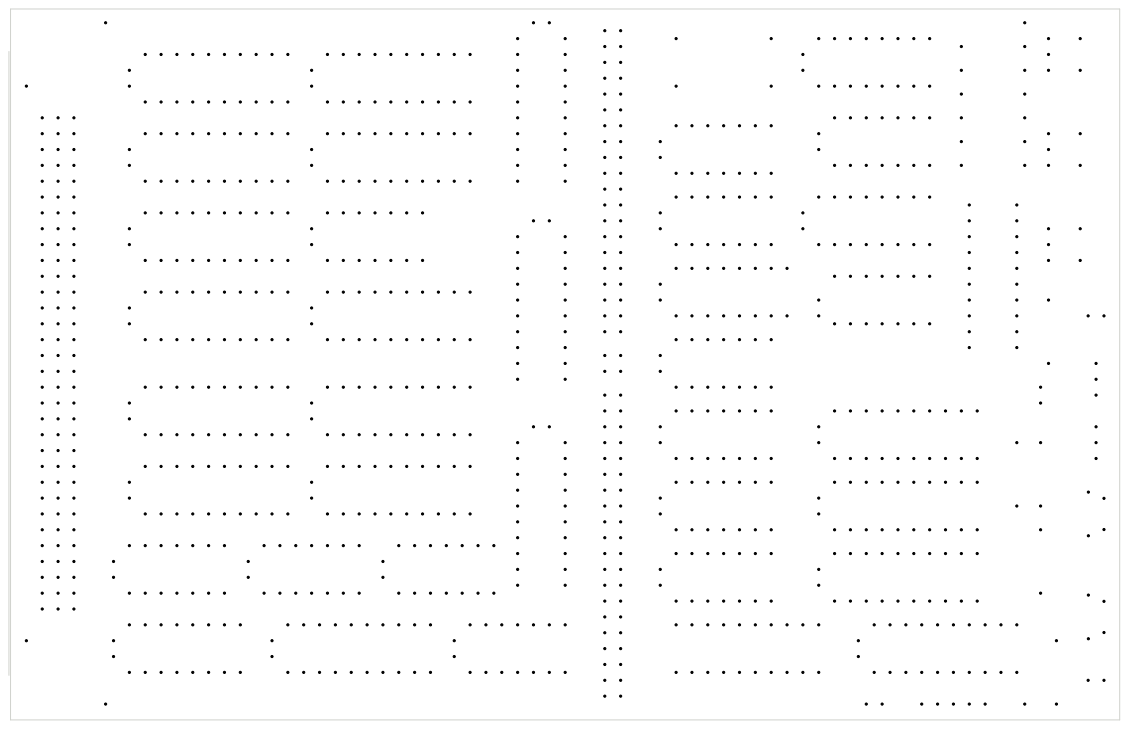
[picture p239: page 6]
