ksr/YACC1-D/docs/procedures/BUS Driver Commands - Google Docs.pdf

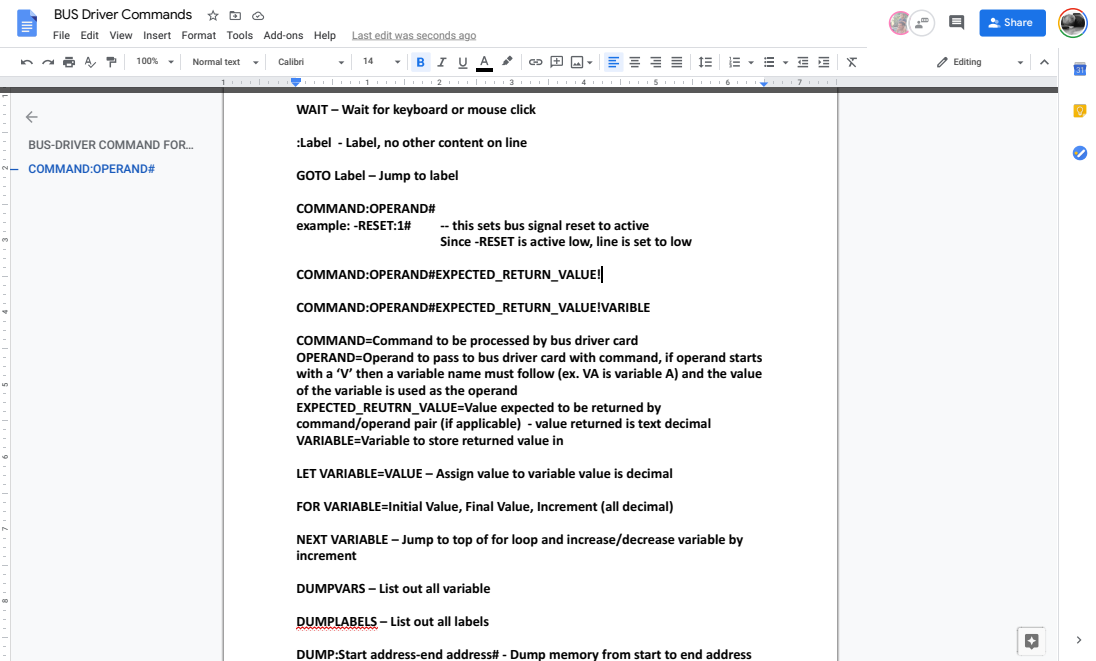
[picture p250: page 1]
File Edit View Insert Format Tools Add-ons Help; Last edit was seconds ago; Normal text; Calibri; Editing; COMMAND:OPERAND#; example: -RESET:1#; -- this sets bus signal reset to active; COMMAND:OPERAND#EXPECTED_RETURN_VALUE!; BUS Driver Commands; Share

BUS Driver Commands

WAIT – Wait for keyboard or mouse click

BUS-DRIVER COMMAND FOR…
— COMMAND:OPERAND#

:Label - Label, no other content on line

GOTO Label – Jump to label

Since -RESET is active low, line is set to low

COMMAND:OPERAND#EXPECTED_RETURN_VALUE!VARIBLE

COMMAND=Command to be processed by bus driver card
OPERAND=Operand to pass to bus driver card with command, if operand starts
with a ‘V’ then a variable name must follow (ex. VA is variable A) and the value
of the variable is used as the operand
EXPECTED_REUTRN_VALUE=Value expected to be returned by
command/operand pair (if applicable) - value returned is text decimal
VARIABLE=Variable to store returned value in

LET VARIABLE=VALUE – Assign value to variable value is decimal

FOR VARIABLE=Initial Value, Final Value, Increment (all decimal)

NEXT VARIABLE – Jump to top of for loop and increase/decrease variable by
increment

DUMPVARS – List out all variable

DUMPLABELS – List out all labels

DUMP:Start address-end address# - Dump memory from start to end address
