ksr/YACC1-D/docs/system/connector/YACC1 Connector - V3.2.pdf

YACC1 Connector | YACC 3.2
A | A | A | B | B | B | C | C | C

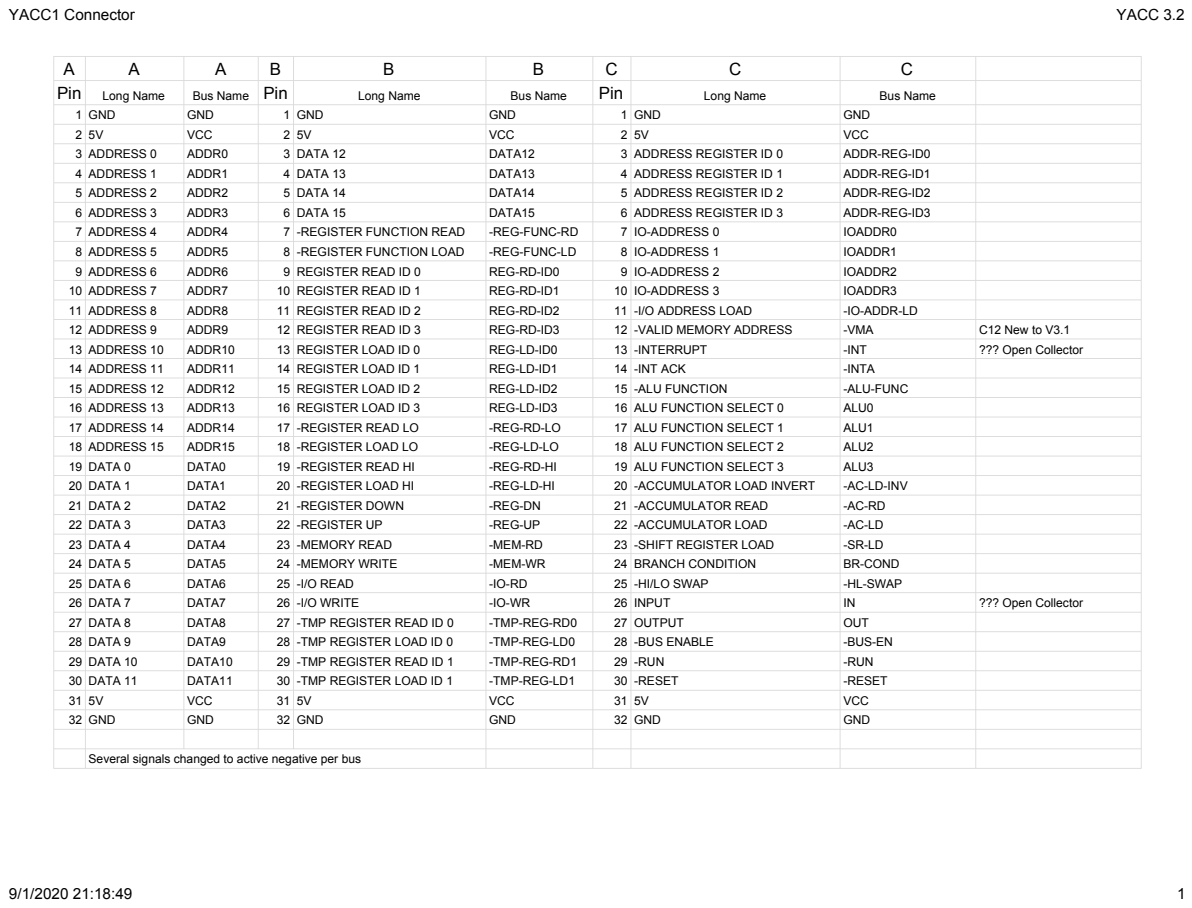
[picture p251: page 1]
Pin; Long Name; Bus Name; 1 GND; GND; VCC; 3 ADDRESS 0; ADDR0; 3 DATA 12; DATA12; 3 ADDRESS REGISTER ID 0; ADDR-REG-ID0; 4 ADDRESS 1; ADDR1; 4 DATA 13; DATA13; 4 ADDRESS REGISTER ID 1; ADDR-REG-ID1; 5 ADDRESS 2; ADDR2; 5 DATA 14; DATA14; 5 ADDRESS REGISTER ID 2; ADDR-REG-ID2; 6 ADDRESS 3; ADDR3; 6 DATA 15; DATA15; 6 ADDRESS REGISTER ID 3; ADDR-REG-ID3; 7 ADDRESS 4; ADDR4; 7 -REGISTER FUNCTION READ; -REG-FUNC-RD; 7 IO-ADDRESS 0; IOADDR0; 8 ADDRESS 5; ADDR5; 8 -REGISTER FUNCTION LOAD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

Several signals changed to active negative per bus
