ksr/YACC1-D/hardware/cards/memory/eagle/v1.3/pdf/Memory V1.3-board.pdf

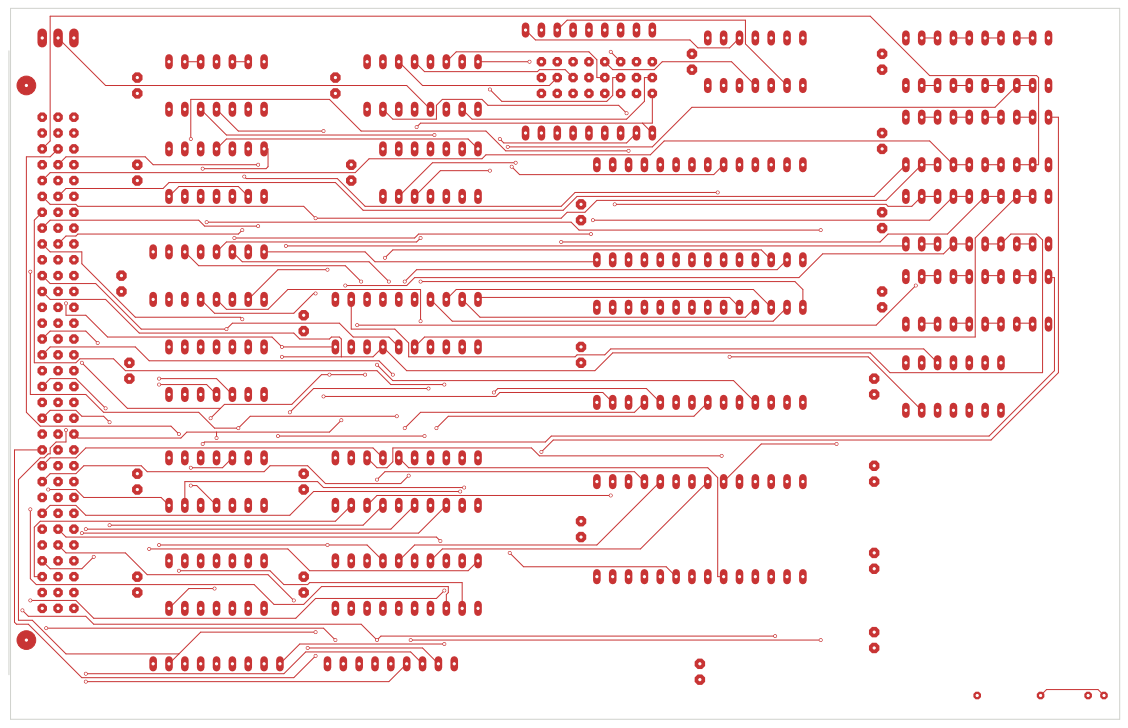
[picture p252: page 1]

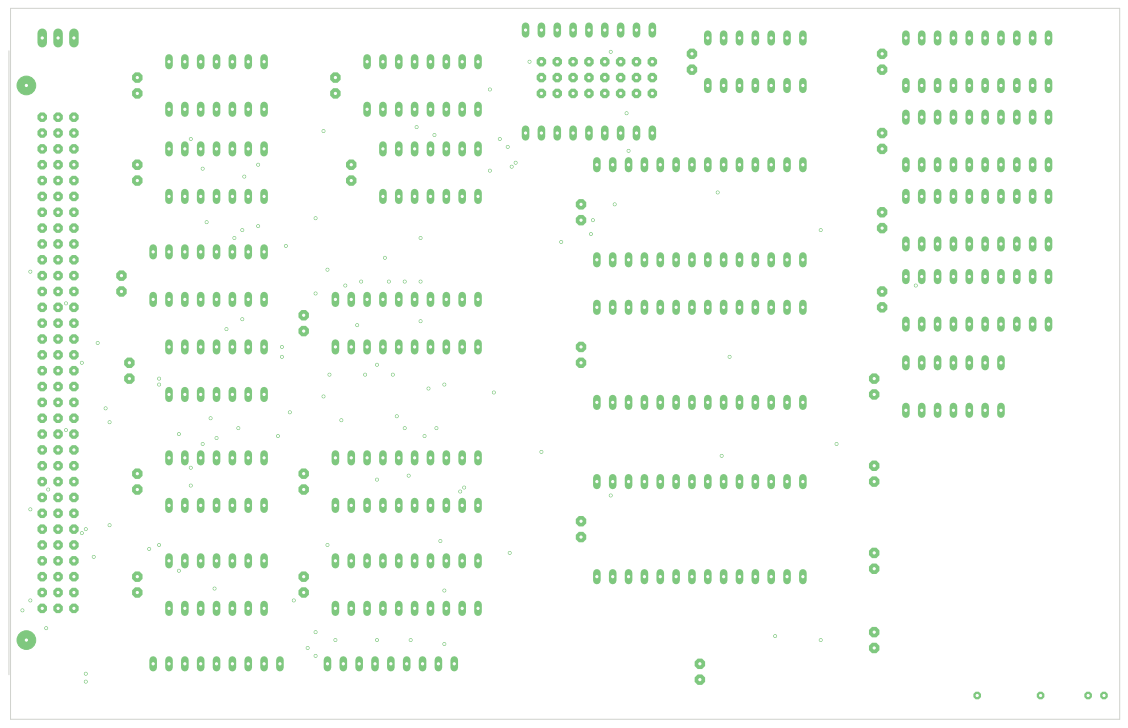
[picture p253: page 2]

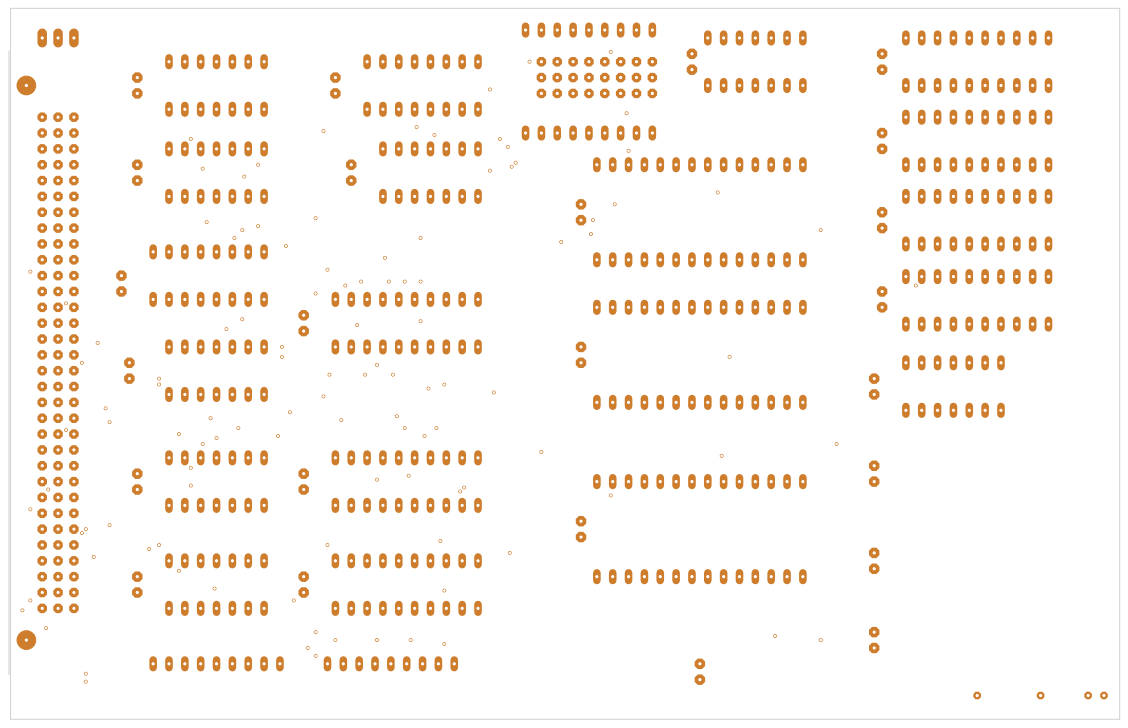
[picture p254: page 3]

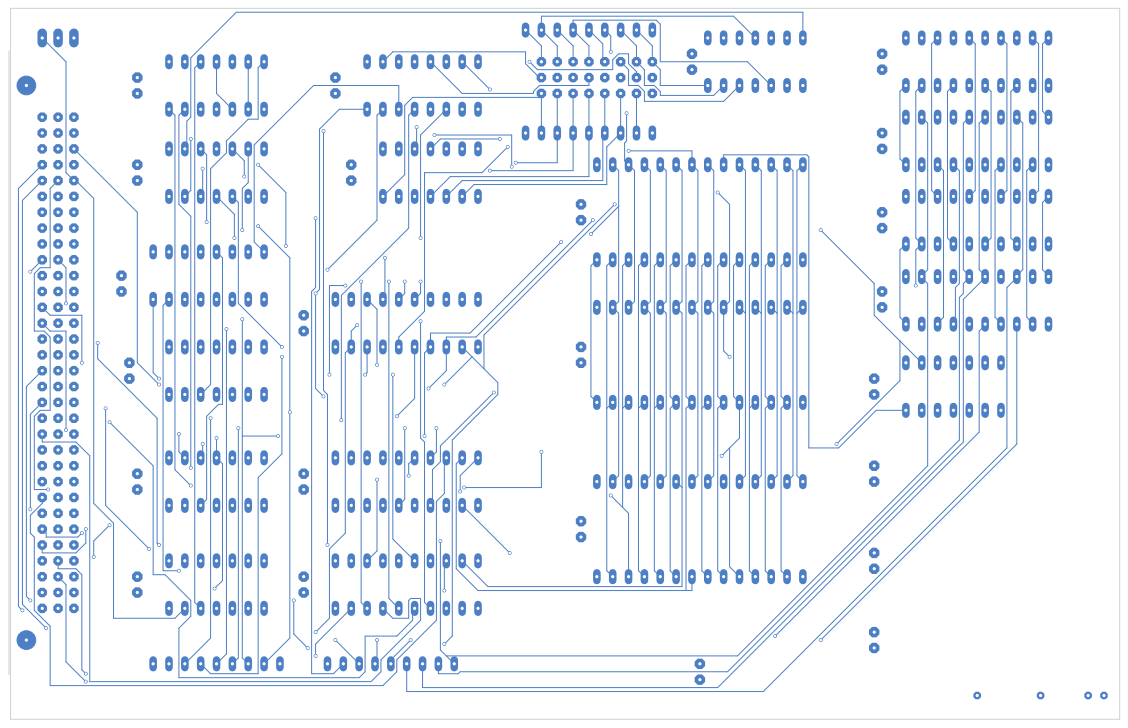
[picture p255: page 4]

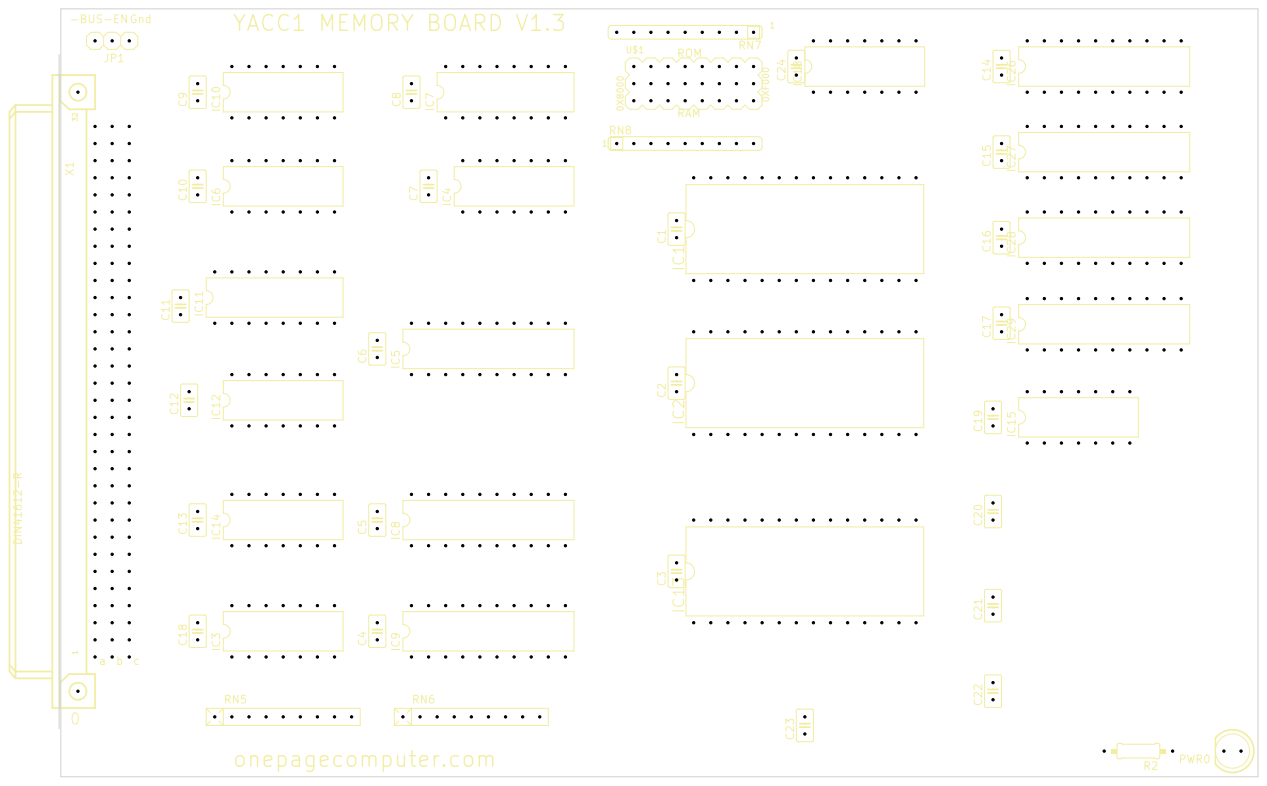
[picture p256: page 5]

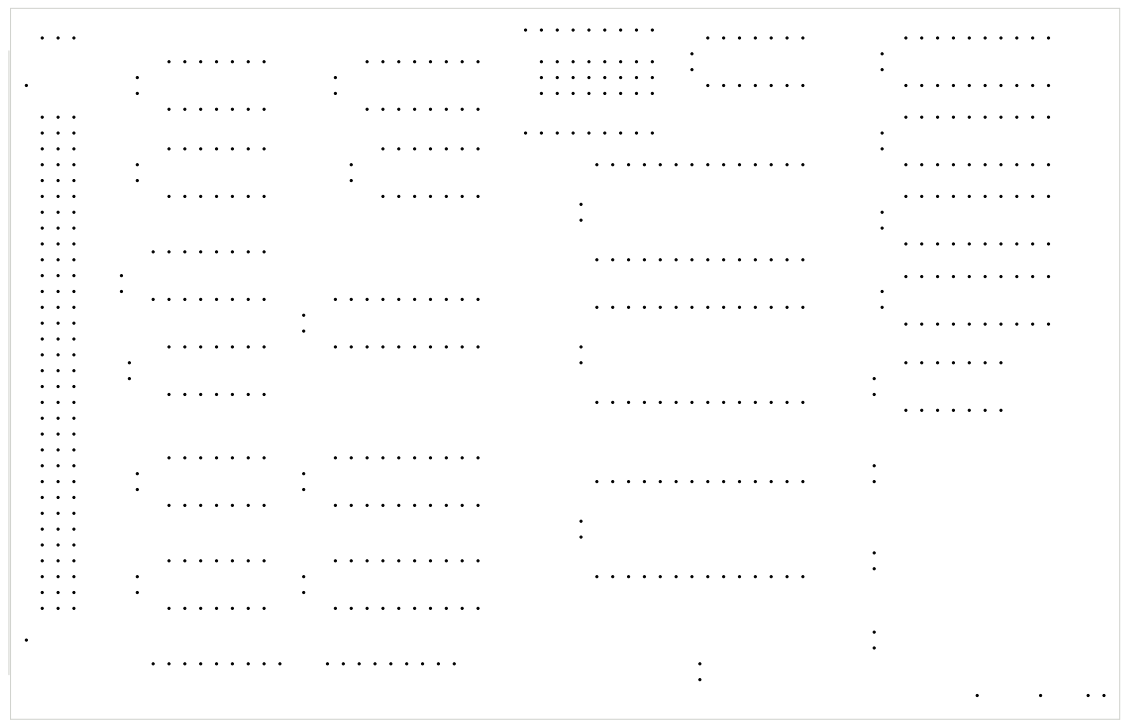
[picture p257: page 6]
