ksr/YACC1-D/docs/system/YACC1-2020 Opcodes - Sheet1-3.pdf

# YACC1-2020 Opcodes

Hex Range; Opcode encoding; BYTE 2; BYTE 3; Description; Mnemonic; Usage; Microcode; ASM; Tested; NA Start reserved; NA Out signal on; NA Out signal off; OFF; NA Halt; HALT; Hi Address Byte Lo Address Byte Jump to subroutine; JSR; JSR XXXX; NA Return from subroutine; RET; LO nibble = src register; register; JSRUR; JSRVR Rn; NA Push Register to stack; PUSHR; PUSHR Rn; NA Pop Register from stack; POPR; NA PUSH accumulator onto stack; PUSH; NA POP stack into accumulator; POP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

Jump to subroutine using

Hi nibble = src register,

Branch is accumulator is less
Branch is accumulator is equal to
Branch is accumulator is greater

Should this be
register based ?
3 byte ins?

Shift accumulator left (MSB-
Shift accumulator right (LSB-

OR accumulator with tmp
And accumulator with tmp
Xor accumulator with tmp

# YACC1-2020 Opcodes

C8 C8-CF Bottom 3 bits = Reg; NA Store tmp register via register; STTVR; STTVR Rn; 2 byte?; D0 D0-D7 Bottom 3 bits = Reg; operand; NA Load memory imm via register; LDIVR; LDIVR Rn,xx; D8 D8-DF Bottom 3 bits = Reg; NA Branch via register; BRVR; BRVR Rn; CSHL; CSHR; ADDIC; ADDTC; Hi Address Byte Lo Address Byte Load accumulator from memory; LDA; LDA ADDR; Moved NOV 25; Hi Address Byte Lo Address Byte Store accumulator to memory; STA; STA ADDR; Hi Address Byte Lo Address Byte Load tmp from memory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
