ksr/YACC1-D/hardware/bus/blank-card/eagle/v3.1/pdf/Blank V3.1-schematic.pdf

Converted from Eagle schematic; see README.md

Size: A4 | Rev:
KiCad E.D.A. 10.0.6 | Id: 1/2


Size: A4 | Rev:
KiCad E.D.A. 10.0.6 | Id: 2/2
