ksr/YACC1-D/hardware/bus/blank-card/kicad/v3.1/reports/blank-card-v3.1-schematic.pdf

Converted from Eagle schematic; see README.md

Size: A4 | Rev:
KiCad E.D.A. 10.0.6 | Id: 1/2


Sheet: /Sheet 1/
File: blank-card-v3.1-sheet1.kicad_sch
Title: blank-card-v3.1 sheet 1

Size: A4 | Rev:
KiCad E.D.A. 10.0.6 | Id: 2/2
