ksr/YACC1-D/hardware/cards/bus-tester/eagle/v1.1/pdf/tester-schematic.pdf

Converted from Eagle schematic; see README.md

Size: A4 | Rev:
KiCad E.D.A. 10.0.6 | Id: 1/5


Converted from Eagle: tester.sch sheet 1 X1-B14



Converted from Eagle: tester.sch sheet 3
