ksr/YACC1-D/hardware/cards/bus-tester/kicad/v1.1/reports/bus-tester-v1.1-schematic.pdf

File: bus-tester-v1.1-sheet1.kicad_sch Sheet 2

File: bus-tester-v1.1-sheet2.kicad_sch Sheet 3

File: bus-tester-v1.1-sheet3.kicad_sch Sheet 4

Converted from Eagle schematic; see README.md

Size: A4 | Rev:
KiCad E.D.A. 10.0.6 | Id: 1/5


Converted from Eagle: tester.sch sheet 1 X1-B14

Sheet: /Sheet 1/
File: bus-tester-v1.1-sheet1.kicad_sch
Title: bus-tester-v1.1 sheet 1


Sheet: /Sheet 2/
File: bus-tester-v1.1-sheet2.kicad_sch
Title: bus-tester-v1.1 sheet 2


Converted from Eagle: tester.sch sheet 3

Sheet: /Sheet 3/
File: bus-tester-v1.1-sheet3.kicad_sch
Title: bus-tester-v1.1 sheet 3


Sheet: /Sheet 4/
File: bus-tester-v1.1-sheet4.kicad_sch
Title: bus-tester-v1.1 sheet 4
