ksr/YACC1-D/hardware/cards/io/kicad/v1.1/reports/io-v1.1-schematic.pdf

Converted from Eagle schematic; see README.md

Size: A4 | Rev:
KiCad E.D.A. 10.0.6 | Id: 1/7



Converted from Eagle: IO V1.1.sch sheet 2


Converted from Eagle: IO V1.1.sch sheet 3


Converted from Eagle: IO V1.1.sch sheet 4 VCC


IO-SELDATA -IO-ADDRSEL
IO-ADDR3-B-RESET

LCD-REGISTER UART-CS UART-A2 UART-A1 UART-A0 DATA0 DATA1
DATA2 DATA6

Converted from Eagle: IO V1.1.sch sheet 5


Converted from Eagle: IO V1.1.sch sheet 6
