ksr/YACC1-D/hardware/cards/mem-register/kicad/v1.0/mem-register-v1.0.kicad_pcb

## KiCad design hardware/cards/mem-register/kicad/v1.0/mem-register-v1.0.kicad_pcb (2026-09-23)

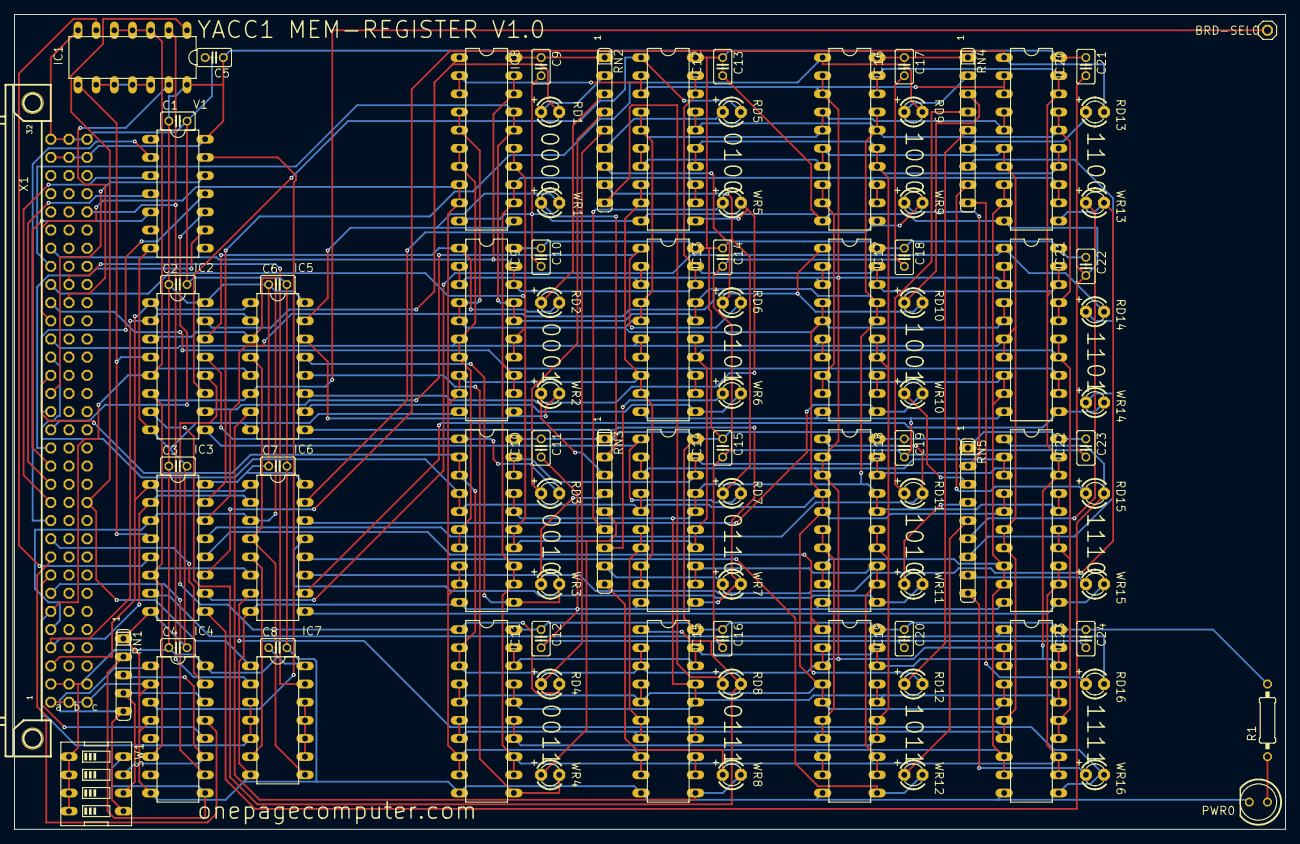
[picture p280: board mem-register-v1.0.kicad_pcb from above]

Board: 2 copper layers, 177.8 x 114.0 mm, 90 parts (0 on the bottom side), 107 nets.

Parts:
BRD-SEL0: PINHD-1X1; 1X01
C1, C2, C3, C4, C5, C6, C7, C8, C9, C10, C11, C12, C13, C14, C15, C16, C17, C18, C19, C20, C21, C22, C23, C24: C025-025X050
IC1, IC7: 74ALS27N; DIL14
IC2, IC3, IC5, IC6: 74LS138N; DIL16
IC4: 74LS85N; DIL16
IC8, IC9, IC10, IC11, IC12, IC13, IC14, IC15, IC16, IC17, IC18, IC19, IC20, IC21, IC22, IC23: 74LS374N; DIL20
PWR0: LED5MM
R1: 330; 0207_10
RD1, RD2, RD3, RD4, RD5, RD6, RD7, RD8, RD9, RD10, RD11, RD12, RD13, RD14, RD15, RD16: LED3MM
RN1: SIL5
RN2, RN3, RN4, RN5: SIL9
SW1: EDG-04
V1: 744078N; DIL14
WR1, WR2, WR3, WR4, WR5, WR6, WR7, WR8, WR9, WR10, WR11, WR12, WR13, WR14, WR15, WR16: LED3MM
X1: FABC96R

Connections:
-BUS-EN: IC1.2, IC7.2, X1.C28
-MEM-RD: IC1.13, X1.B23
-MEM-WR: IC7.13, X1.B24
-VMA: IC1.1, IC7.1, X1.C12
ADDR0: IC2.1, IC3.1, IC5.1, IC6.1, X1.A3
ADDR1: IC2.2, IC3.2, IC5.2, IC6.2, X1.A4
ADDR2: IC2.3, IC3.3, IC5.3, IC6.3, X1.A5
ADDR3: IC1.3, IC1.4, IC1.5, IC2.5, IC5.5, IC7.3, IC7.4, IC7.5, X1.A6
ADDR4: IC4.10, X1.A7
ADDR5: IC4.12, X1.A8
ADDR6: IC4.13, X1.A9
ADDR7: IC4.15, X1.A10
ADDR8: V1.2, X1.A11
ADDR9: V1.3, X1.A12
ADDR10: V1.4, X1.A13
ADDR11: V1.5, X1.A14
ADDR12: V1.9, X1.A15
ADDR13: V1.10, X1.A16
ADDR14: V1.11, X1.A17
ADDR15: V1.12, X1.A18
DATA0: IC8.2, IC8.3, IC9.2, IC9.3, IC10.2, IC10.3, IC11.2, IC11.3, IC12.2, IC12.3, IC13.2, IC13.3, IC14.2, IC14.3, IC15.2, IC15.3, IC16.2, IC16.3, IC17.2, IC17.3, IC18.2, IC18.3, IC19.2, IC19.3, IC20.2, IC20.3, IC21.2, IC21.3, IC22.2, IC22.3, IC23.2, IC23.3, X1.A19
DATA1: IC8.4, IC8.5, IC9.4, IC9.5, IC10.4, IC10.5, IC11.4, IC11.5, IC12.4, IC12.5, IC13.4, IC13.5, IC14.4, IC14.5, IC15.4, IC15.5, IC16.4, IC16.5, IC17.4, IC17.5, IC18.4, IC18.5, IC19.4, IC19.5, IC20.4, IC20.5, IC21.4, IC21.5, IC22.4, IC22.5, IC23.4, IC23.5, X1.A20
DATA2: IC8.6, IC8.7, IC9.6, IC9.7, IC10.6, IC10.7, IC11.6, IC11.7, IC12.6, IC12.7, IC13.6, IC13.7, IC14.6, IC14.7, IC15.6, IC15.7, IC16.6, IC16.7, IC17.6, IC17.7, IC18.6, IC18.7, IC19.6, IC19.7, IC20.6, IC20.7, IC21.6, IC21.7, IC22.6, IC22.7, IC23.6, IC23.7, X1.A21
DATA3: IC8.8, IC8.9, IC9.8, IC9.9, IC10.8, IC10.9, IC11.8, IC11.9, IC12.8, IC12.9, IC13.8, IC13.9, IC14.8, IC14.9, IC15.8, IC15.9, IC16.8, IC16.9, IC17.8, IC17.9, IC18.8, IC18.9, IC19.8, IC19.9, IC20.8, IC20.9, IC21.8, IC21.9, IC22.8, IC22.9, IC23.8, IC23.9, X1.A22
DATA4: IC8.12, IC8.13, IC9.12, IC9.13, IC10.12, IC10.13, IC11.12, IC11.13, IC12.12, IC12.13, IC13.12, IC13.13, IC14.12, IC14.13, IC15.12, IC15.13, IC16.12, IC16.13, IC17.12, IC17.13, IC18.12, IC18.13, IC19.12, IC19.13, IC20.12, IC20.13, IC21.12, IC21.13, IC22.12, IC22.13, IC23.12, IC23.13, X1.A23
DATA5: IC8.14, IC8.15, IC9.14, IC9.15, IC10.14, IC10.15, IC11.14, IC11.15, IC12.14, IC12.15, IC13.14, IC13.15, IC14.14, IC14.15, IC15.14, IC15.15, IC16.14, IC16.15, IC17.14, IC17.15, IC18.14, IC18.15, IC19.14, IC19.15, IC20.14, IC20.15, IC21.14, IC21.15, IC22.14, IC22.15, IC23.14, IC23.15, X1.A24
DATA6: IC8.16, IC8.17, IC9.16, IC9.17, IC10.16, IC10.17, IC11.16, IC11.17, IC12.16, IC12.17, IC13.16, IC13.17, IC14.16, IC14.17, IC15.16, IC15.17, IC16.16, IC16.17, IC17.16, IC17.17, IC18.16, IC18.17, IC19.16, IC19.17, IC20.16, IC20.17, IC21.16, IC21.17, IC22.16, IC22.17, IC23.16, IC23.17, X1.A25
DATA7: IC8.18, IC8.19, IC9.18, IC9.19, IC10.18, IC10.19, IC11.18, IC11.19, IC12.18, IC12.19, IC13.18, IC13.19, IC14.18, IC14.19, IC15.18, IC15.19, IC16.18, IC16.19, IC17.18, IC17.19, IC18.18, IC18.19, IC19.18, IC19.19, IC20.18, IC20.19, IC21.18, IC21.19, IC22.18, IC22.19, IC23.18, IC23.19, X1.A26
GND: C1.2, C2.2, C3.2, C4.2, C5.2, C6.2, C7.2, C8.2, C9.2, C10.2, C11.2, C12.2, C13.2, C14.2, C15.2, C16.2, C17.2, C18.2, C19.2, C20.2, C21.2, C22.2, C23.2, C24.2, IC1.7, IC2.8, IC3.8, IC4.2, IC4.4, IC4.8, IC5.8, IC6.8, IC7.7, IC8.10, IC9.10, IC10.10, IC11.10, IC12.10, IC13.10, IC14.10, IC15.10, IC16.10, IC17.10, IC18.10, IC19.10, IC20.10, IC21.10, IC22.10, IC23.10, PWR0.K, RN1.1, V1.7, X1.A1, X1.A32, X1.B1, X1.B32, X1.C1, X1.C32
unnamed: RD1.A, RN2.2
unnamed: IC7.9, IC7.10, IC7.11, IC7.12
unnamed: IC6.5, IC7.6
unnamed: IC5.4, IC6.4, IC7.8
unnamed: RD3.A, RN2.4
unnamed: BRD-SEL0.1, IC2.6, IC3.6, IC4.6, IC5.6, IC6.6
unnamed: RD2.A, RN2.3
unnamed: IC4.3, V1.13
unnamed: RD9.A, RN4.2
unnamed: RD4.A, RN2.5
unnamed: PWR0.A, R1.1
unnamed: RD5.A, RN2.6
unnamed: RD7.A, RN2.8
unnamed: RD8.A, RN2.9
unnamed: RD6.A, RN2.7
unnamed: RD10.A, RN4.3
unnamed: RD11.A, RN4.4
unnamed: RD12.A, RN4.5
unnamed: IC1.9, IC1.10, IC1.11, IC1.12
unnamed: RD13.A, RN4.6
unnamed: RD14.A, RN4.7
unnamed: RD15.A, RN4.8
unnamed: RD16.A, RN4.9
unnamed: RN3.2, WR1.A
unnamed: RN3.3, WR2.A
unnamed: RN3.4, WR3.A
unnamed: RN3.5, WR4.A
unnamed: IC4.9, RN1.2, SW1.8
unnamed: RN3.7, WR6.A
unnamed: RN3.6, WR5.A
unnamed: RN3.8, WR7.A
unnamed: RN3.9, WR8.A
unnamed: RN5.2, WR9.A
unnamed: RN5.4, WR11.A
unnamed: RN5.6, WR13.A
unnamed: RN5.8, WR15.A
unnamed: IC1.6, IC3.5
unnamed: RN5.9, WR16.A
unnamed: RN5.7, WR14.A
unnamed: RN5.5, WR12.A
unnamed: RN5.3, WR10.A
unnamed: IC4.11, RN1.3, SW1.7
unnamed: IC4.14, RN1.4, SW1.6
unnamed: IC4.1, RN1.5, SW1.5
unnamed: IC1.8, IC2.4, IC3.4
RD0: IC2.15, IC8.1, RD1.K
RD1: IC2.14, IC9.1, RD2.K
RD2: IC2.13, IC10.1, RD3.K
RD3: IC2.12, IC11.1, RD4.K
RD4: IC2.11, IC12.1, RD5.K
RD5: IC2.10, IC13.1, RD6.K
RD6: IC2.9, IC14.1, RD7.K
RD7: IC2.7, IC15.1, RD8.K
RD8: IC3.15, IC16.1, RD9.K
RD9: IC3.14, IC17.1, RD10.K
RD10: IC3.13, IC18.1, RD11.K
RD11: IC3.12, IC19.1, RD12.K
RD12: IC3.11, IC20.1, RD13.K
RD13: IC3.10, IC21.1, RD14.K
RD14: IC3.9, IC22.1, RD15.K
RD15: IC3.7, IC23.1, RD16.K
VCC: C1.1, C2.1, C3.1, C4.1, C5.1, C6.1, C7.1, C8.1, C9.1, C10.1, C11.1, C12.1, C13.1, C14.1, C15.1, C16.1, C17.1, C18.1, C19.1, C20.1, C21.1, C22.1, C23.1, C24.1, IC1.14, IC2.16, IC3.16, IC4.16, IC5.16, IC6.16, IC7.14, IC8.20, IC9.20, IC10.20, IC11.20, IC12.20, IC13.20, IC14.20, IC15.20, IC16.20, IC17.20, IC18.20, IC19.20, IC20.20, IC21.20, IC22.20, IC23.20, R1.2, RN2.1, RN3.1, RN4.1, RN5.1, SW1.1, SW1.2, SW1.3, SW1.4, V1.14, X1.A2, X1.A31, X1.B2, X1.B31, X1.C2, X1.C31
WR0: IC5.15, IC8.11, WR1.K
WR1: IC5.14, IC9.11, WR2.K
WR2: IC5.13, IC10.11, WR3.K
WR3: IC5.12, IC11.11, WR4.K
WR4: IC5.11, IC12.11, WR5.K
WR5: IC5.10, IC13.11, WR6.K
WR6: IC5.9, IC14.11, WR7.K
WR7: IC5.7, IC15.11, WR8.K
WR8: IC6.15, IC16.11, WR9.K
WR9: IC6.14, IC17.11, WR10.K
WR10: IC6.13, IC18.11, WR11.K
WR11: IC6.12, IC19.11, WR12.K
WR12: IC6.11, IC20.11, WR13.K
WR13: IC6.10, IC21.11, WR14.K
WR14: IC6.9, IC22.11, WR15.K
WR15: IC6.7, IC23.11, WR16.K
