ksr/YACC1-D/hardware/cards/cf/kicad/v1.0/yacc1-cf-card.kicad_pcb

## KiCad design hardware/cards/cf/kicad/v1.0/yacc1-cf-card.kicad_pcb (2026-09-23)

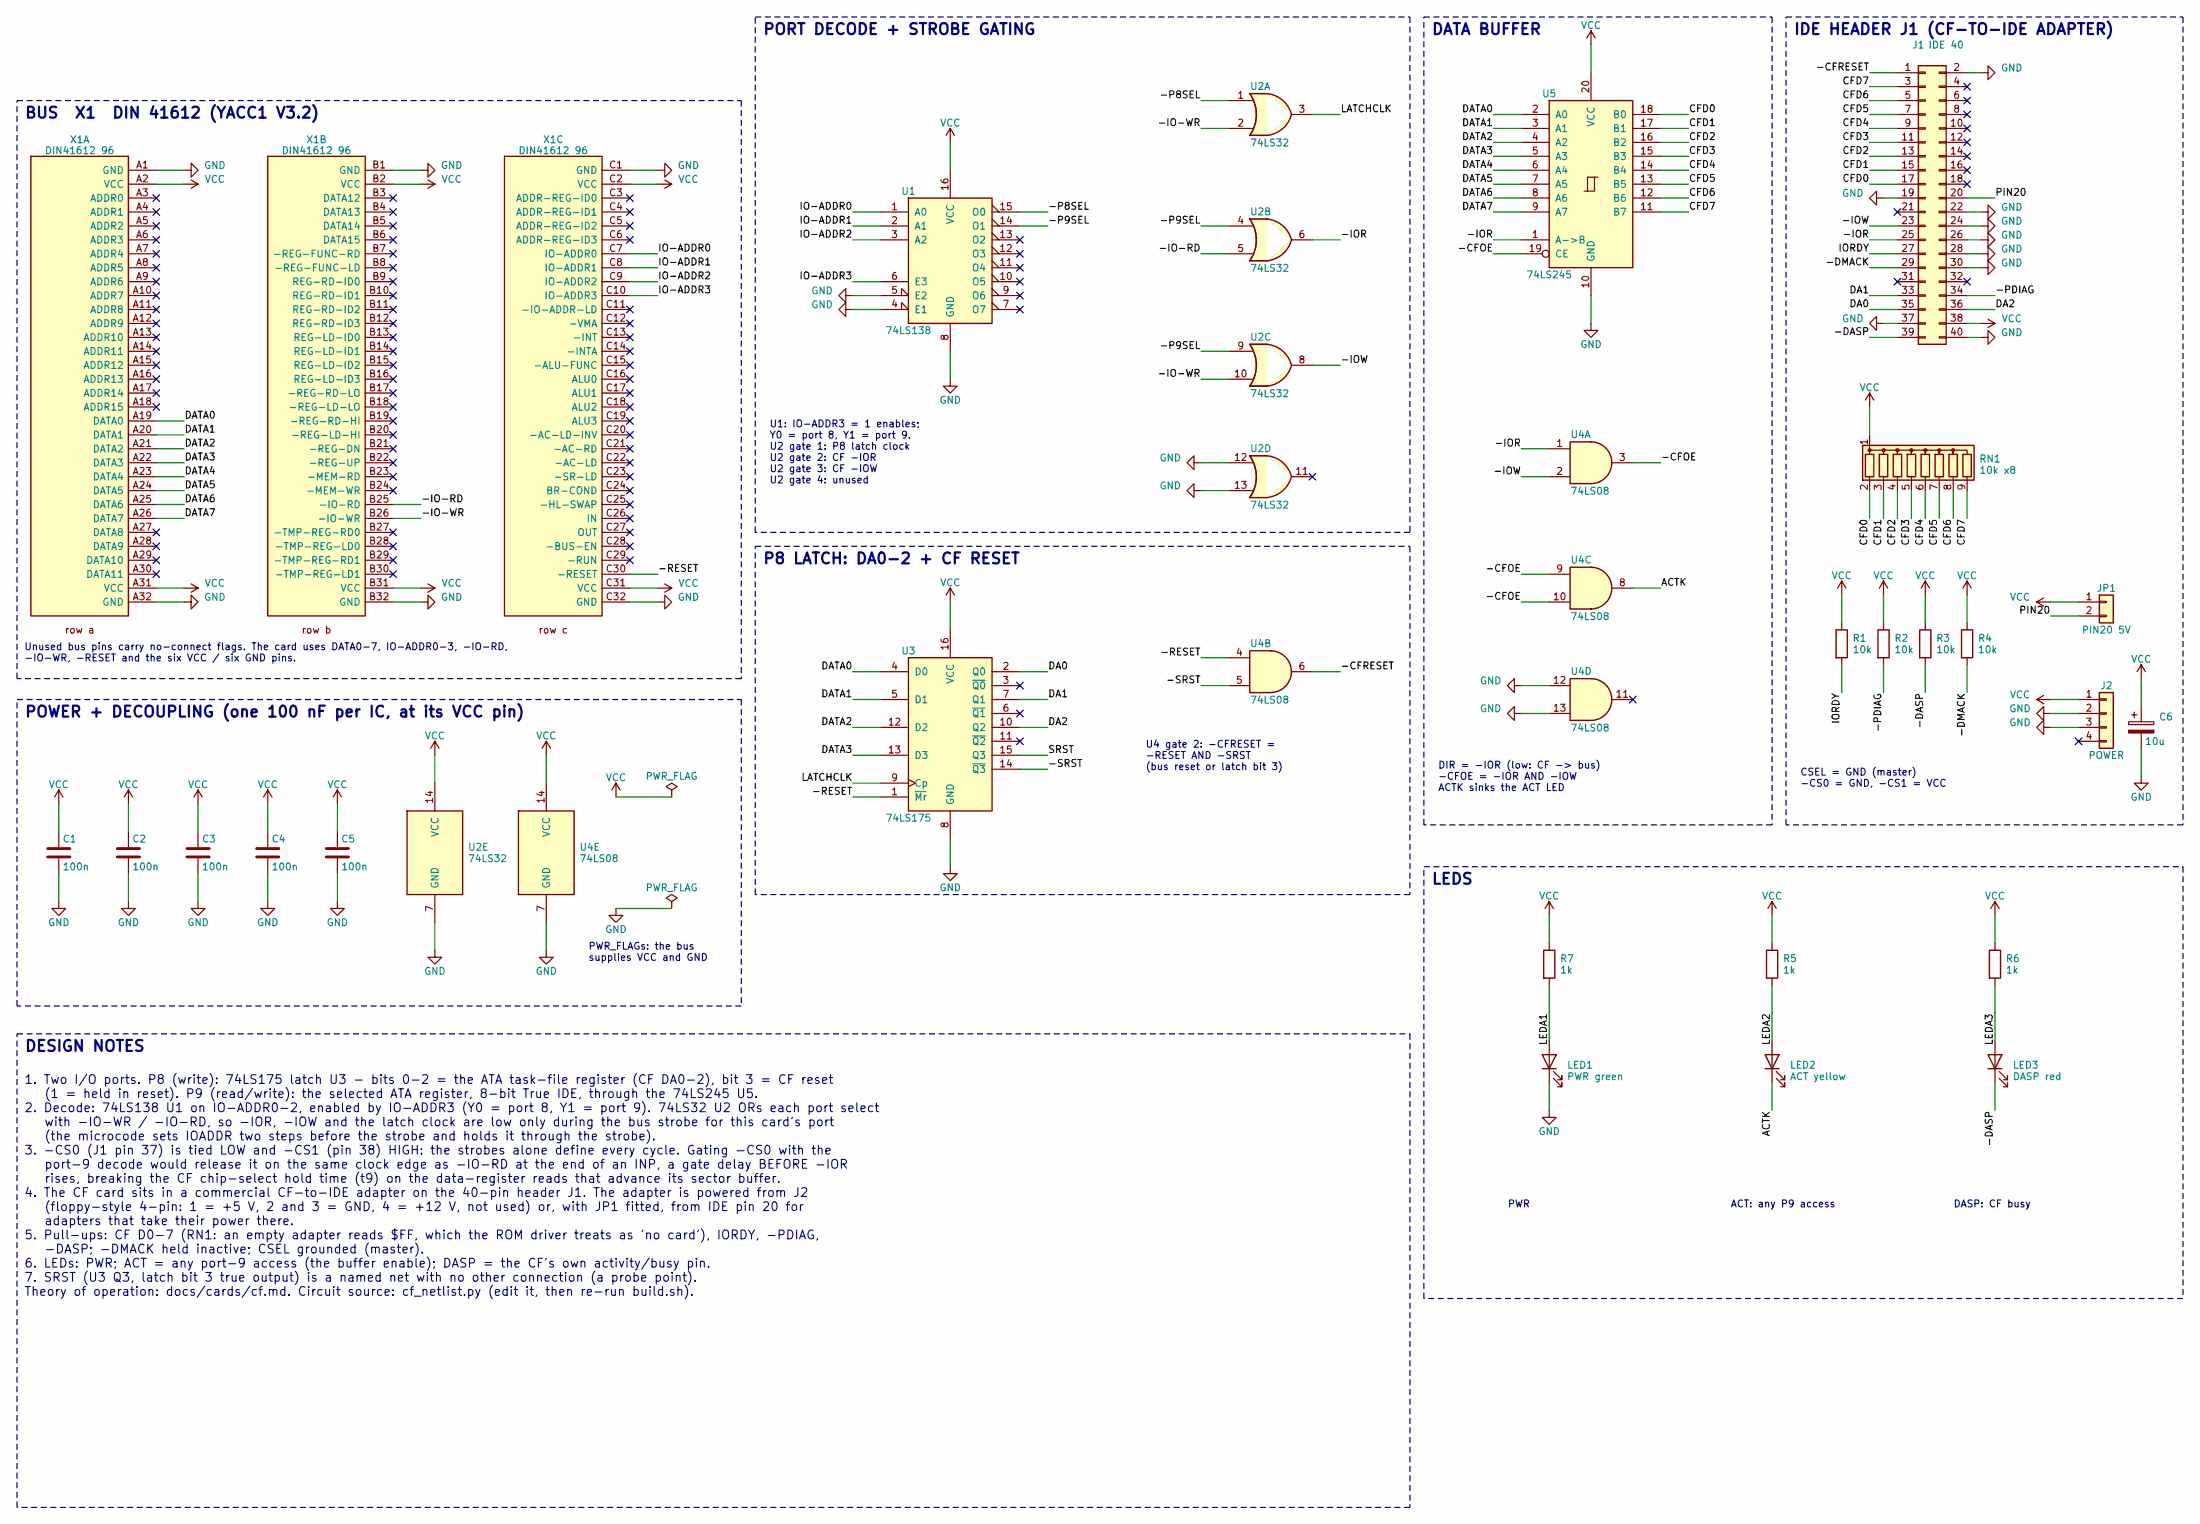
[picture p281: schematic yacc1-cf-card.kicad_sch, YACC1 CF card v1.0]

Parts:
C1, C2, C3, C4, C5: 100n; C_Disc_D5.0mm_W2.5mm_P5.00mm
C6: 10u; CP_Radial_D5.0mm_P2.00mm
J1: IDE 40; IDC-Header_2x20_P2.54mm_Vertical
J2: POWER; PinHeader_1x04_P2.54mm_Vertical
JP1: PIN20 5V; PinHeader_1x02_P2.54mm_Vertical
LED1: PWR green; LED_D5.0mm
LED2: ACT yellow; LED_D5.0mm
LED3: DASP red; LED_D5.0mm
R1, R2, R3, R4: 10k; R_Axial_DIN0207_L6.3mm_D2.5mm_P10.16mm_Horizontal
R5, R6, R7: 1k; R_Axial_DIN0207_L6.3mm_D2.5mm_P10.16mm_Horizontal
RN1: 10k x8; R_Array_SIP9
U1: 74LS138; DIP-16_W7.62mm
U2: 74LS32; DIP-14_W7.62mm
U3: 74LS175; DIP-16_W7.62mm
U4: 74LS08; DIP-14_W7.62mm
U5: 74LS245; DIP-20_W7.62mm
X1: DIN41612 96; FABC96R

Connections:
/-CFOE: U4.3, U4.9, U4.10, U5.19 (CE)
/-CFRESET: J1.1, U4.6
/-DASP: J1.39, LED3.1 (K), R3.2
/-DMACK: J1.29, R4.2
/-IO-RD: U2.5, X1.B25 (-IO-RD)
/-IO-WR: U2.2, U2.10, X1.B26 (-IO-WR)
/-IOR: J1.25, U2.6, U4.1, U5.1 (A->B)
/-IOW: J1.23, U2.8, U4.2
/-P8SEL: U1.15 (O0), U2.1
/-P9SEL: U1.14 (O1), U2.4, U2.9
/-PDIAG: J1.34, R2.2
/-RESET: U3.1 (~Mr), U4.4, X1.C30 (-RESET)
/-SRST: U3.14 (~Q3), U4.5
/ACTK: LED2.1 (K), U4.8
/CFD0: J1.17, RN1.2 (R1), U5.18 (B0)
/CFD1: J1.15, RN1.3 (R2), U5.17 (B1)
/CFD2: J1.13, RN1.4 (R3), U5.16 (B2)
/CFD3: J1.11, RN1.5 (R4), U5.15 (B3)
/CFD4: J1.9, RN1.6 (R5), U5.14 (B4)
/CFD5: J1.7, RN1.7 (R6), U5.13 (B5)
/CFD6: J1.5, RN1.8 (R7), U5.12 (B6)
/CFD7: J1.3, RN1.9 (R8), U5.11 (B7)
/DA0: J1.35, U3.2 (Q0)
/DA1: J1.33, U3.7 (Q1)
/DA2: J1.36, U3.10 (Q2)
/DATA0: U3.4 (D0), U5.2 (A0), X1.A19 (DATA0)
/DATA1: U3.5 (D1), U5.3 (A1), X1.A20 (DATA1)
/DATA2: U3.12 (D2), U5.4 (A2), X1.A21 (DATA2)
/DATA3: U3.13 (D3), U5.5 (A3), X1.A22 (DATA3)
/DATA4: U5.6 (A4), X1.A23 (DATA4)
/DATA5: U5.7 (A5), X1.A24 (DATA5)
/DATA6: U5.8 (A6), X1.A25 (DATA6)
/DATA7: U5.9 (A7), X1.A26 (DATA7)
/IO-ADDR0: U1.1 (A0), X1.C7 (IO-ADDR0)
/IO-ADDR1: U1.2 (A1), X1.C8 (IO-ADDR1)
/IO-ADDR2: U1.3 (A2), X1.C9 (IO-ADDR2)
/IO-ADDR3: U1.6 (E3), X1.C10 (IO-ADDR3)
/IORDY: J1.27, R1.2
/LATCHCLK: U2.3, U3.9 (Cp)
/LEDA1: LED1.2 (A), R7.2
/LEDA2: LED2.2 (A), R5.2
/LEDA3: LED3.2 (A), R6.2
/PIN20: J1.20, JP1.2
/SRST: U3.15 (Q3)
GND: C1.2, C2.2, C3.2, C4.2, C5.2, C6.2, J1.2, J1.19, J1.22, J1.24, J1.26, J1.28, J1.30, J1.37, J1.40, J2.2, J2.3, LED1.1 (K), U1.4 (E1), U1.5 (E2), U1.8 (GND), U2.7 (GND), U2.12, U2.13, U3.8 (GND), U4.7 (GND), U4.12, U4.13, U5.10 (GND), X1.A1 (GND), X1.A32 (GND), X1.B1 (GND), X1.B32 (GND), X1.C1 (GND), X1.C32 (GND)
VCC: C1.1, C2.1, C3.1, C4.1, C5.1, C6.1, J1.38, J2.1, JP1.1, R1.1, R2.1, R3.1, R4.1, R5.1, R6.1, R7.1, RN1.1 (common), U1.16 (VCC), U2.14 (VCC), U3.16 (VCC), U4.14 (VCC), U5.20 (VCC), X1.A2 (VCC), X1.A31 (VCC), X1.B2 (VCC), X1.B31 (VCC), X1.C2 (VCC), X1.C31 (VCC)

Notes on the sheet:
DIR = -IOR (low: CF -> bus) -CFOE = -IOR AND -IOW ACTK sinks the ACT LED
U4 gate 2: -CFRESET = -RESET AND -SRST (bus reset or latch bit 3)
1. Two I/O ports. P8 (write): 74LS175 latch U3 - bits 0-2 = the ATA task-file register (CF DA0-2), bit 3 = CF reset (1 = held in reset). P9 (read/write): the selected ATA register, 8-bit True IDE, through the 74LS245 U5. 2. Decode: 74LS138 U1 on IO-ADDR0-2, enabled by IO-ADDR3 (Y0 = port 8, Y1 = po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
Unused bus pins carry no-connect flags. The card uses DATA0-7, IO-ADDR0-3, -IO-RD, -IO-WR, -RESET and the six VCC / six GND pins.
DATA BUFFER
CSEL = GND (master) -CS0 = GND, -CS1 = VCC
POWER + DECOUPLING (one 100 nF per IC, at its VCC pin)
ACT: any P9 access
DASP: CF busy
IDE HEADER J1 (CF-TO-IDE ADAPTER)
PWR
PWR_FLAGs: the bus supplies VCC and GND
PORT DECODE + STROBE GATING
DESIGN NOTES
U1: IO-ADDR3 = 1 enables; Y0 = port 8, Y1 = port 9. U2 gate 1: P8 latch clock U2 gate 2: CF -IOR U2 gate 3: CF -IOW U2 gate 4: unused
BUS X1 DIN 41612 (YACC1 V3.2)
P8 LATCH: DA0-2 + CF RESET
LEDS

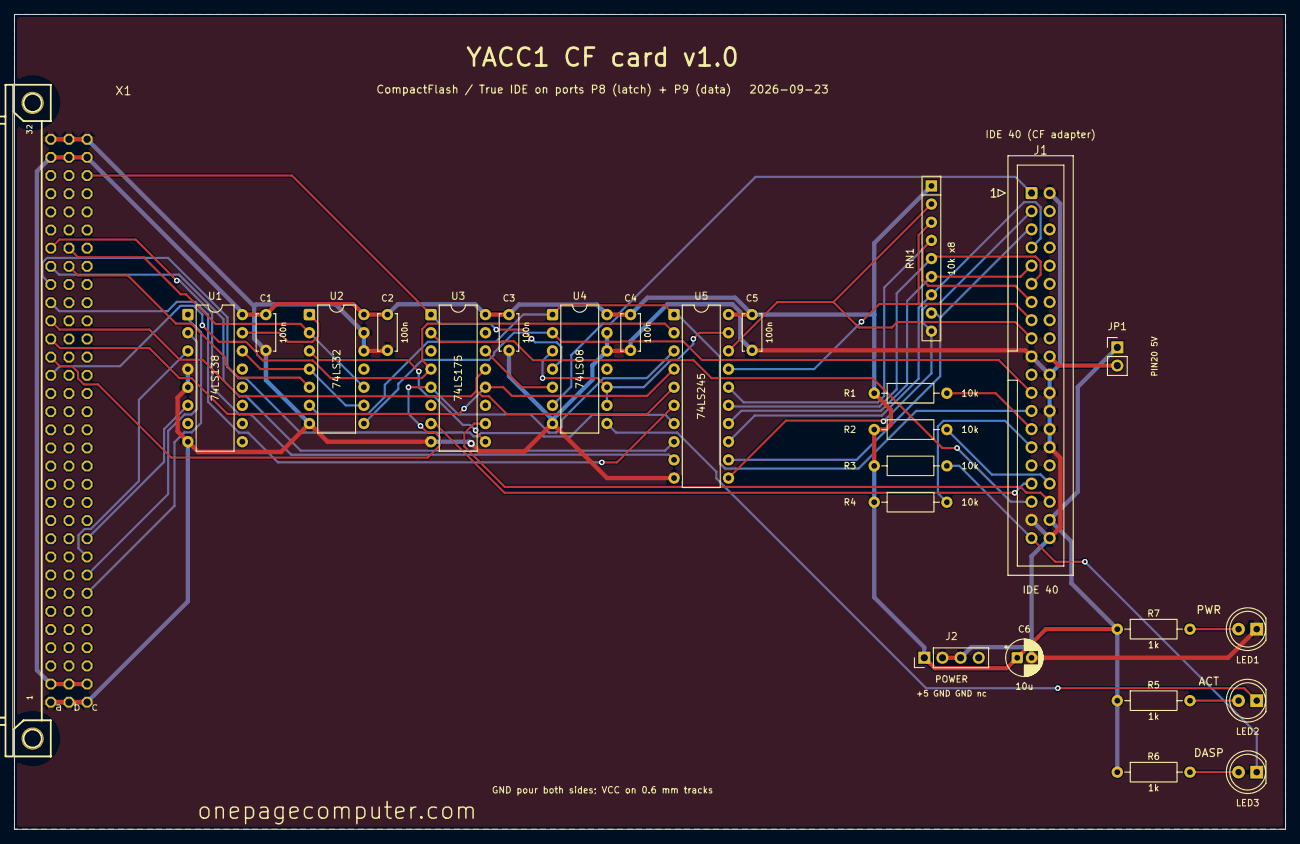
[picture p282: board yacc1-cf-card.kicad_pcb from above]

Board: 2 copper layers, 177.8 x 114.0 mm, 26 parts (0 on the bottom side), 45 nets.
