ksr/YACC1-D/hardware/cards/alu/kicad/v3.2/alu-v3.2.kicad_pcb

## KiCad design hardware/cards/alu/kicad/v3.2/alu-v3.2.kicad_pcb (2026-09-23)

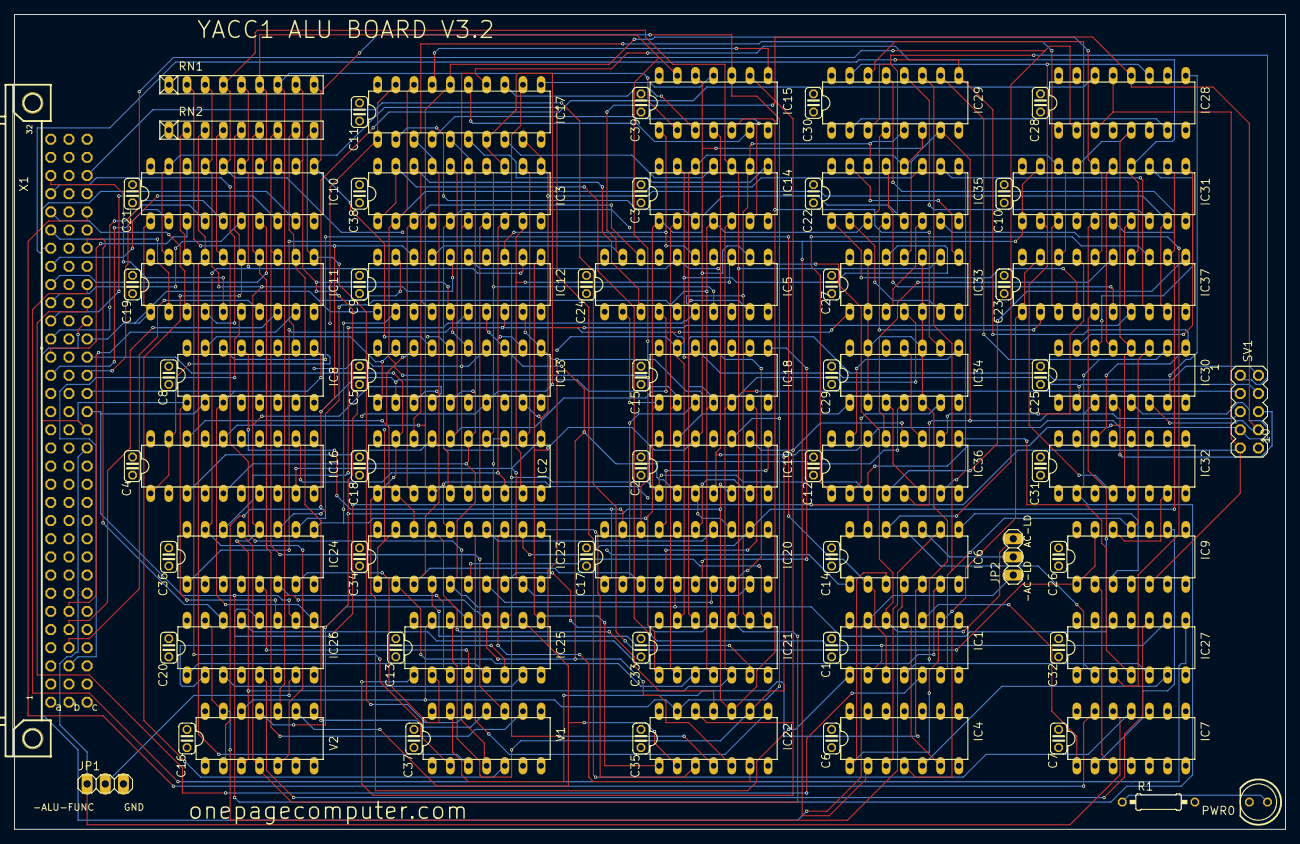
[picture p283: board alu-v3.2.kicad_pcb from above]

Board: 4 copper layers, 177.8 x 114.0 mm, 86 parts (0 on the bottom side), 162 nets.

Parts:
C1, C2, C3, C4, C5, C6, C7, C8, C9, C10, C11, C12, C13, C14, C15, C16, C17, C18, C19, C20, C22, C23, C24, C25, C26, C27, C28, C29, C30, C31, C32, C33, C34, C35, C36, C37, C38, C39: .1uf; C025-024X044
C21: ,1uf; C025-024X044
IC1: 74ALS04N; DIL14
IC2: 74LS240N; DIL20
IC3, IC12, IC13, IC16, IC17, IC20, IC23, IC31, IC37: 74LS244N; DIL20
IC4: 74LS00N; DIL14
IC5: 74LS374N; DIL20
IC6: 74ALS08N; DIL14
IC7, IC21, IC22: 74LS32N; DIL14
IC8: 74LS138N; DIL16
IC9: 74LS74N; DIL14
IC10, IC11: 74LS245N; DIL20
IC14, IC15, IC27, IC33, IC34: 74LS86N; DIL14
IC18, IC19: 74LS08N; DIL14
IC24, IC25: 74LS85N; DIL16
IC26: 74LS251N; DIL16
IC28, IC32: 74LS153N; DIL16
IC29, IC30: 74LS194N; DIL16
IC35, IC36: 74LS283N; DIL16
JP1, JP2: 1X03
PWR0: LED5MM
R1: 330; 0207_10
RN1, RN2: 10k; RN-9
SV1: MA05-2
V1, V2: 744078N; DIL14
X1: FABC96R

Connections:
-AC-LD: IC1.13, JP2.1, X1.C22
-AC-LD-INV: IC1.1, IC2.1, IC2.19, X1.C20
-AC-RD: IC10.1, IC11.1, IC12.1, IC12.19, X1.C21
-ADD: IC6.1, IC8.7
-ADD/SUB: IC1.9, IC4.1, IC6.3, IC37.1, IC37.19
-ALU-FUNC: IC7.12, JP1.1, X1.C15
-ALU-IO-EN: IC7.11, IC10.19, IC11.19
-AND: IC8.13, IC20.1, IC20.19
-BUS-EN: IC7.13, X1.C28
-DATA: IC8.15, IC13.1, IC13.19
-OR: IC8.12, IC23.1, IC23.19
-RESET: IC9.1, IC9.13, X1.C30
-SHIFT: IC4.2, IC8.10, IC31.1, IC31.19
-SR-LD: IC1.5, X1.C23
-SUB: IC1.3, IC6.2, IC8.14
-XOR: IC8.11, IC17.1, IC17.19
-ZERO: IC8.9, IC16.1, IC16.19
AC-LD: IC1.12, IC5.11, JP2.3
AC-LD-INV: IC1.2, IC3.1, IC3.19, IC27.9
ACI-DATA0: IC2.18, IC3.18, IC5.3
ACI-DATA1: IC2.16, IC3.16, IC5.4
ACI-DATA2: IC2.14, IC3.14, IC5.7
ACI-DATA3: IC2.12, IC3.12, IC5.8
ACI-DATA4: IC2.9, IC3.9, IC5.13
ACI-DATA5: IC2.7, IC3.7, IC5.14
ACI-DATA6: IC2.5, IC3.5, IC5.17
ACI-DATA7: IC2.3, IC3.3, IC5.18
ACO-DATA0: IC5.2, IC12.2, IC14.1, IC18.1, IC21.1, IC24.9, IC29.3, IC35.5, SV1.1
ACO-DATA1: IC5.5, IC12.4, IC14.4, IC18.4, IC21.4, IC24.11, IC29.4, IC35.3, SV1.2
ACO-DATA2: IC5.6, IC12.6, IC14.9, IC18.9, IC21.9, IC24.14, IC29.5, IC35.14, SV1.3
ACO-DATA3: IC5.9, IC12.8, IC14.12, IC18.12, IC21.12, IC24.1, IC29.6, IC30.2, IC35.12, SV1.4
ACO-DATA4: IC5.12, IC12.11, IC15.12, IC19.12, IC22.1, IC25.9, IC29.7, IC30.3, IC36.5, SV1.5
ACO-DATA5: IC5.15, IC12.13, IC15.1, IC19.1, IC22.4, IC25.11, IC30.4, IC36.3, SV1.6
ACO-DATA6: IC5.16, IC12.15, IC15.4, IC19.4, IC22.9, IC25.14, IC30.5, IC36.14, SV1.7
ACO-DATA7: IC5.19, IC12.17, IC15.9, IC19.9, IC22.12, IC25.1, IC28.12, IC30.6, IC36.12, SV1.8
ALU0: IC8.1, IC26.11, IC29.9, IC30.9, IC32.14, X1.C16
ALU1: IC8.2, IC26.10, IC29.10, IC30.10, IC32.2, X1.C17
ALU2: IC8.3, IC26.9, IC28.14, X1.C18
ALU3: IC6.12, IC28.2, X1.C19
BDATA0: IC10.18, IC12.18, IC13.2, IC14.2, IC18.2, IC21.2, IC24.10, IC33.1, RN1.2, V2.2
BDATA1: IC10.17, IC12.16, IC13.4, IC14.5, IC18.5, IC21.5, IC24.12, IC33.4, RN1.3, V2.3
BDATA2: IC10.16, IC12.14, IC13.6, IC14.10, IC18.10, IC21.10, IC24.13, IC33.9, RN1.4, V2.4
BDATA3: IC10.15, IC12.12, IC13.8, IC14.13, IC18.13, IC21.13, IC24.15, IC33.12, RN1.5, V2.5
BDATA4: IC10.14, IC12.9, IC13.11, IC15.13, IC19.13, IC22.2, IC25.10, IC34.1, RN1.6, V2.9
BDATA5: IC10.13, IC12.7, IC13.13, IC15.2, IC19.2, IC22.5, IC25.12, IC34.4, RN1.7, V2.10
BDATA6: IC10.12, IC12.5, IC13.15, IC15.5, IC19.5, IC22.10, IC25.13, IC34.9, RN1.8, V2.11
BDATA7: IC10.11, IC12.3, IC13.17, IC15.10, IC19.10, IC22.13, IC25.15, IC34.12, RN1.9, V2.12
BDATA8: IC11.18, RN2.2, V1.2
BDATA9: IC11.17, RN2.3, V1.3
BDATA10: IC11.16, RN2.4, V1.4
BDATA11: IC11.15, RN2.5, V1.5
BDATA12: IC11.14, RN2.6, V1.9
BDATA13: IC11.13, RN2.7, V1.10
BDATA14: IC11.12, RN2.8, V1.11
BDATA15: IC11.11, RN2.9, V1.12
BR-COND: IC27.8, X1.C24
C/SHIFT: IC6.13, IC9.5, IC26.12, IC28.3, IC28.13, SV1.9
CO/BO: IC1.10, IC7.1
DATA0: IC10.2, X1.A19
DATA1: IC10.3, X1.A20
DATA2: IC10.4, X1.A21
DATA3: IC10.5, X1.A22
DATA4: IC10.6, X1.A23
DATA5: IC10.7, X1.A24
DATA6: IC10.8, X1.A25
DATA7: IC10.9, X1.A26
DATA8: IC11.2, X1.A27
DATA9: IC11.3, X1.A28
DATA10: IC11.4, X1.A29
DATA11: IC11.5, X1.A30
DATA12: IC11.6, X1.B3
DATA13: IC11.7, X1.B4
DATA14: IC11.8, X1.B5
DATA15: IC11.9, X1.B6
GND: C1.2, C2.2, C3.2, C4.2, C5.2, C6.2, C7.2, C8.2, C9.2, C10.2, C11.2, C12.2, C13.2, C14.2, C15.2, C16.2, C17.2, C18.2, C19.2, C20.2, C21.2, C22.2, C23.2, C24.2, C25.2, C26.2, C27.2, C28.2, C29.2, C30.2, C31.2, C32.2, C33.2, C34.2, C35.2, C36.2, C37.2, C38.2, C39.2, IC1.7, IC2.10, IC3.10, IC4.7, IC4.9, IC4.10, IC4.12, IC4.13, IC5.1, IC5.10, IC6.7, IC7.4, IC7.5, IC7.7, IC7.9, IC7.10, IC8.4, IC8.5, IC8.8, IC9.7, IC10.10, IC11.10, IC12.10, IC13.10, IC14.7, IC15.7, IC16.2, IC16.4, IC16.6, IC16.8, IC16.10, IC16.11, IC16.13, IC16.15, IC16.17, IC17.10, IC18.7, IC19.7, IC20.10, IC21.7, IC22.7, IC23.10, IC24.2, IC24.4, IC24.8, IC25.8, IC26.8, IC27.7, IC27.12, IC27.13, IC28.1, IC28.4, IC28.6, IC28.8, IC28.10, IC28.15, IC29.8, IC30.8, IC31.10, IC32.1, IC32.3, IC32.6, IC32.8, IC32.10, IC32.11, IC32.12, IC32.13, IC32.15, IC33.7, IC34.7, IC35.8, IC36.8, IC37.10, JP1.3, PWR0.K, SV1.10, V1.7, V2.7, X1.A1, X1.A32, X1.B1, X1.B32, X1.C1, X1.C32
IN: IC26.14, X1.C26
INV-IN0: IC2.2, IC3.2, IC13.18, IC16.18, IC17.18, IC20.18, IC23.18, IC31.18, IC37.18
INV-IN1: IC2.4, IC3.4, IC13.16, IC16.16, IC17.16, IC20.16, IC23.16, IC31.16, IC37.16
INV-IN2: IC2.6, IC3.6, IC13.14, IC16.14, IC17.14, IC20.14, IC23.14, IC31.14, IC37.14
INV-IN3: IC2.8, IC3.8, IC13.12, IC16.12, IC17.12, IC20.12, IC23.12, IC31.12, IC37.12
INV-IN4: IC2.11, IC3.11, IC13.9, IC16.9, IC17.9, IC20.9, IC23.9, IC31.9, IC37.9
INV-IN5: IC2.13, IC3.13, IC13.7, IC16.7, IC17.7, IC20.7, IC23.7, IC31.7, IC37.7
INV-IN6: IC2.15, IC3.15, IC13.5, IC16.5, IC17.5, IC20.5, IC23.5, IC31.5, IC37.5
INV-IN7: IC2.17, IC3.17, IC13.3, IC16.3, IC17.3, IC20.3, IC23.3, IC31.3, IC37.3
unnamed: IC27.4, IC36.9
unnamed: IC27.3, IC35.7
unnamed: IC4.3, IC6.9
unnamed: IC26.7, JP1.2
unnamed: IC6.8, IC9.3
unnamed: IC6.4, IC26.15, V2.13
unnamed: IC7.3, IC9.2
unnamed: IC6.11, IC27.1
unnamed: IC6.10, JP2.2
unnamed: IC4.5, IC27.6
unnamed: IC9.12, IC32.7
unnamed: IC33.6, IC35.2
unnamed: IC34.6, IC36.2
unnamed: PWR0.A, R1.1
unnamed: IC1.8, IC4.4
unnamed: IC1.11, IC4.6
unnamed: IC33.8, IC35.15
unnamed: IC33.11, IC35.11
unnamed: IC33.3, IC35.6
unnamed: IC34.3, IC36.6
unnamed: IC34.8, IC36.15
unnamed: IC34.11, IC36.11
unnamed: IC35.4, IC37.2
unnamed: IC35.1, IC37.4
unnamed: IC35.13, IC37.6
unnamed: IC35.10, IC37.8
unnamed: IC36.4, IC37.11
unnamed: IC36.1, IC37.13
unnamed: IC36.13, IC37.15
unnamed: IC36.10, IC37.17
unnamed: IC35.9, IC36.7
unnamed: IC24.5, IC25.4
unnamed: IC24.6, IC25.3
unnamed: IC24.7, IC25.2
unnamed: IC25.7, IC26.3
unnamed: IC25.6, IC26.2
unnamed: IC25.5, IC26.1
unnamed: IC6.5, V1.13
unnamed: IC6.6, IC26.13
unnamed: IC26.5, IC27.10
unnamed: IC29.14, IC31.4
unnamed: IC29.13, IC31.6
unnamed: IC29.12, IC31.8
unnamed: IC30.15, IC31.11
unnamed: IC30.14, IC31.13
unnamed: IC30.13, IC31.15
unnamed: IC28.7, IC29.2
unnamed: IC28.9, IC30.7
unnamed: IC21.3, IC23.2
unnamed: IC21.6, IC23.4
unnamed: IC21.8, IC23.6
unnamed: IC21.11, IC23.8
unnamed: IC22.3, IC23.11
unnamed: IC22.6, IC23.13
unnamed: IC22.8, IC23.15
unnamed: IC22.11, IC23.17
unnamed: IC18.3, IC20.2
unnamed: IC18.6, IC20.4
unnamed: IC18.8, IC20.6
unnamed: IC18.11, IC20.8
unnamed: IC19.11, IC20.11
unnamed: IC19.3, IC20.13
unnamed: IC19.6, IC20.15
unnamed: IC19.8, IC20.17
unnamed: IC14.3, IC17.2
unnamed: IC14.6, IC17.4
unnamed: IC14.8, IC17.6
unnamed: IC14.11, IC17.8
unnamed: IC15.11, IC17.11
unnamed: IC15.3, IC17.13
unnamed: IC15.6, IC17.15
unnamed: IC15.8, IC17.17
SHIFT-OUT: IC7.2, IC9.9
SR-LD: IC1.6, IC9.11, IC29.11, IC30.11
SRD0: IC28.11, IC29.15, IC31.2, IC32.4
SRD7: IC28.5, IC30.12, IC31.17, IC32.5
SUB: IC1.4, IC27.2, IC27.5, IC33.2, IC33.5, IC33.10, IC33.13, IC34.2, IC34.5, IC34.10, IC34.13
VCC: C1.1, C2.1, C3.1, C4.1, C5.1, C6.1, C7.1, C8.1, C9.1, C10.1, C11.1, C12.1, C13.1, C14.1, C15.1, C16.1, C17.1, C18.1, C19.1, C20.1, C21.1, C22.1, C23.1, C24.1, C25.1, C26.1, C27.1, C28.1, C29.1, C30.1, C31.1, C32.1, C33.1, C34.1, C35.1, C36.1, C37.1, C38.1, C39.1, IC1.14, IC2.20, IC3.20, IC4.14, IC5.20, IC6.14, IC7.14, IC8.6, IC8.16, IC9.4, IC9.10, IC9.14, IC10.20, IC11.20, IC12.20, IC13.20, IC14.14, IC15.14, IC16.20, IC17.20, IC18.14, IC19.14, IC20.20, IC21.14, IC22.14, IC23.20, IC24.3, IC24.16, IC25.16, IC26.4, IC26.16, IC27.14, IC28.16, IC29.1, IC29.16, IC30.1, IC30.16, IC31.20, IC32.16, IC33.14, IC34.14, IC35.16, IC36.16, IC37.20, R1.2, RN1.1, RN2.1, V1.14, V2.14, X1.A2, X1.A31, X1.B2, X1.B31, X1.C2, X1.C31
