ksr/YACC1-D/hardware/cards/memory/eagle/v1.3/Memory V1.3.brd

## EAGLE design hardware/cards/memory/eagle/v1.3/Memory V1.3.brd (2026-09-24)

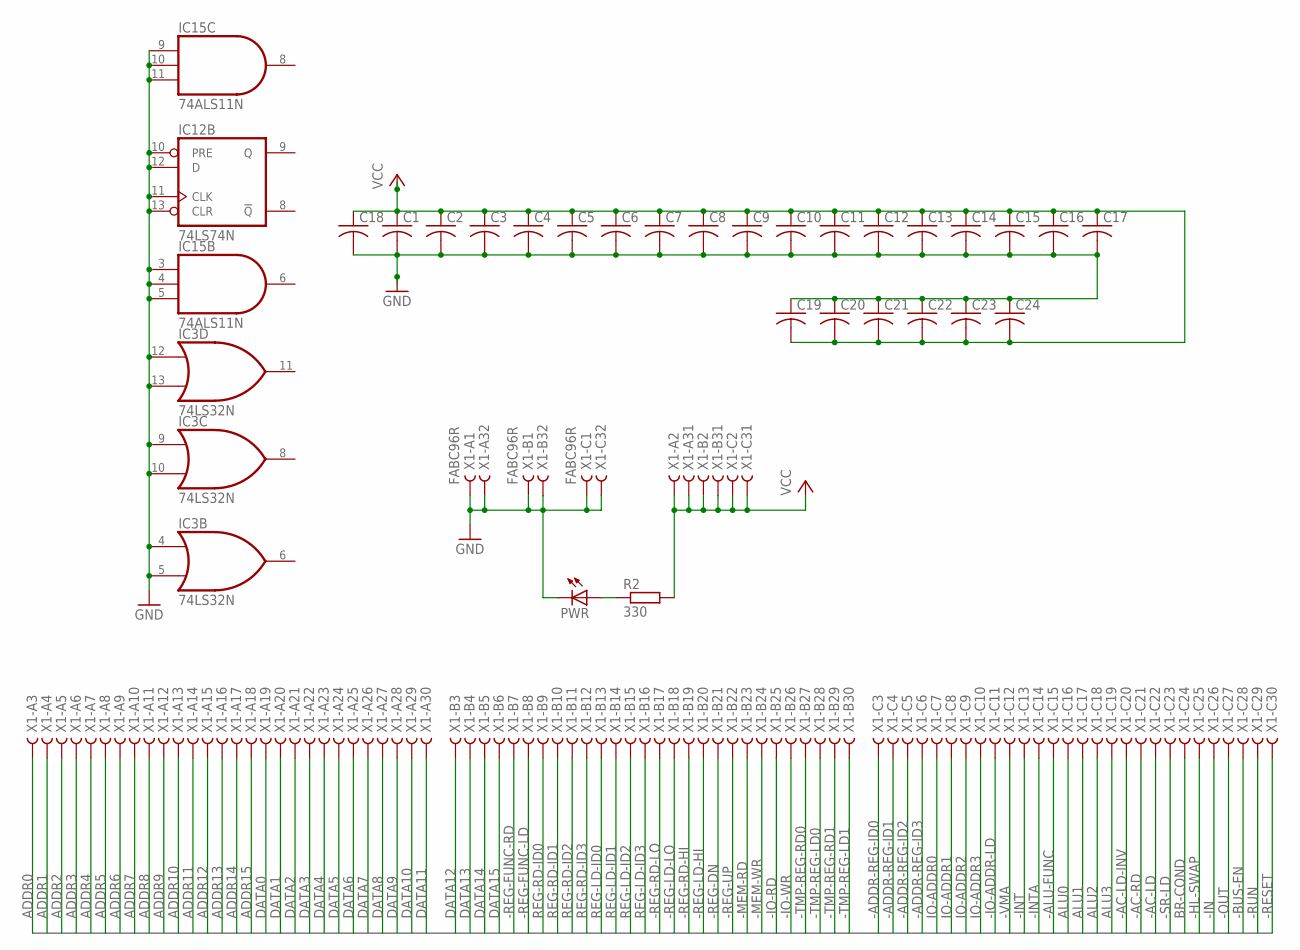
[picture p286: schematic Memory V1.3.sch, sheet 1, BUS]

Parts:
C1, C2, C3, C4, C5, C6, C7, C8, C9, C10, C11, C12, C13, C14, C15, C16, C17, C18, C19, C20, C21, C22, C23, C24: C-US025-025X050; C025-025X050
IC3: 74LS32N; DIL14
IC12: 74LS74N; DIL14
IC15: 74ALS11N; DIL14
PWR: LED5MM
R2: 330; 0207/10
X1: FABC96R

Connections:
-AC-LD: X1.C22
-AC-LD-INV: X1.C20
-AC-RD: X1.C21
-ADDR-REG-ID0: X1.C3
-ADDR-REG-ID1: X1.C4
-ADDR-REG-ID2: X1.C5
-ADDR-REG-ID3: X1.C6
-ALU-FUNC: X1.C15
-BUS-EN: X1.C28; also elsewhere on the board
-HL-SWAP: X1.C25
-IN: X1.C26
-INT: X1.C13
-INTA: X1.C14
-IO-ADDR-LD: X1.C11
-IO-RD: X1.B25
-IO-WR: X1.B26
-MEM-RD: X1.B23; also elsewhere on the board
-MEM-WR: X1.B24; also elsewhere on the board
-OUT: X1.C27
-REG-DN: X1.B21
-REG-FUNC-LD: X1.B8
-REG-FUNC-RD: X1.B7
-REG-LD-HI: X1.B20
-REG-LD-LO: X1.B18
-REG-RD-HI: X1.B19
-REG-RD-LO: X1.B17
-REG-UP: X1.B22
-RESET: X1.C30; also elsewhere on the board
-RUN: X1.C29
-SR-LD: X1.C23
-TMP-REG-LD0: X1.B28; also elsewhere on the board
-TMP-REG-LD1: X1.B30; also elsewhere on the board
-TMP-REG-RD0: X1.B27; also elsewhere on the board
-TMP-REG-RD1: X1.B29; also elsewhere on the board
-VMA: X1.C12; also elsewhere on the board
ADDR0: X1.A3; also elsewhere on the board
ADDR1: X1.A4; also elsewhere on the board
ADDR2: X1.A5; also elsewhere on the board
ADDR3: X1.A6; also elsewhere on the board
ADDR4: X1.A7; also elsewhere on the board
ADDR5: X1.A8; also elsewhere on the board
ADDR6: X1.A9; also elsewhere on the board
ADDR7: X1.A10; also elsewhere on the board
ADDR8: X1.A11; also elsewhere on the board
ADDR9: X1.A12; also elsewhere on the board
ADDR10: X1.A13; also elsewhere on the board
ADDR11: X1.A14; also elsewhere on the board
ADDR12: X1.A15; also elsewhere on the board
ADDR13: X1.A16; also elsewhere on the board
ADDR14: X1.A17; also elsewhere on the board
ADDR15: X1.A18; also elsewhere on the board
ALU0: X1.C16
ALU1: X1.C17
ALU2: X1.C18
ALU3: X1.C19
BR-COND: X1.C24
DATA0: X1.A19; also elsewhere on the board
DATA1: X1.A20; also elsewhere on the board
DATA2: X1.A21; also elsewhere on the board
DATA3: X1.A22; also elsewhere on the board
DATA4: X1.A23; also elsewhere on the board
DATA5: X1.A24; also elsewhere on the board
DATA6: X1.A25; also elsewhere on the board
DATA7: X1.A26; also elsewhere on the board
DATA8: X1.A27; also elsewhere on the board
DATA9: X1.A28; also elsewhere on the board
DATA10: X1.A29; also elsewhere on the board
DATA11: X1.A30; also elsewhere on the board
DATA12: X1.B3; also elsewhere on the board
DATA13: X1.B4; also elsewhere on the board
DATA14: X1.B5; also elsewhere on the board
DATA15: X1.B6; also elsewhere on the board
GND: C1.2, C2.2, C3.2, C4.2, C5.2, C6.2, C7.2, C8.2, C9.2, C10.2, C11.2, C12.2, C13.2, C14.2, C15.2, C16.2, C17.2, C18.2, C19.1, C20.1, C21.1, C22.1, C23.1, C24.1, IC3.4 (I0), IC3.5 (I1), IC3.7 (GND), IC3.9 (I0), IC3.10 (I1), IC3.12 (I0), IC3.13 (I1), IC12.7 (GND), IC12.10 (PRE), IC12.11 (CLK), IC12.12 (D), IC12.13 (CLR), IC15.3 (I0), IC15.4 (I1), IC15.5 (I2), IC15.7 (GND), IC15.9 (I0), IC15.10 (I1), IC15.11 (I2), PWR.K (C), X1.A1, X1.A32, X1.B1, X1.B32, X1.C1, X1.C32; also elsewhere on the board
IO-ADDR0: X1.C7
IO-ADDR1: X1.C8
IO-ADDR2: X1.C9
IO-ADDR3: X1.C10
unnamed: PWR.A, R2.1
REG-LD-ID0: X1.B13
REG-LD-ID1: X1.B14
REG-LD-ID2: X1.B15
REG-LD-ID3: X1.B16
REG-RD-ID0: X1.B9
REG-RD-ID1: X1.B10
REG-RD-ID2: X1.B11
REG-RD-ID3: X1.B12
VCC: C1.1, C2.1, C3.1, C4.1, C5.1, C6.1, C7.1, C8.1, C9.1, C10.1, C11.1, C12.1, C13.1, C14.1, C15.1, C16.1, C17.1, C18.1, C19.2, C20.2, C21.2, C22.2, C23.2, C24.2, IC3.14 (VCC), IC12.14 (VCC), IC15.14 (VCC), R2.2, X1.A2, X1.A31, X1.B2, X1.B31, X1.C2, X1.C31; also elsewhere on the board

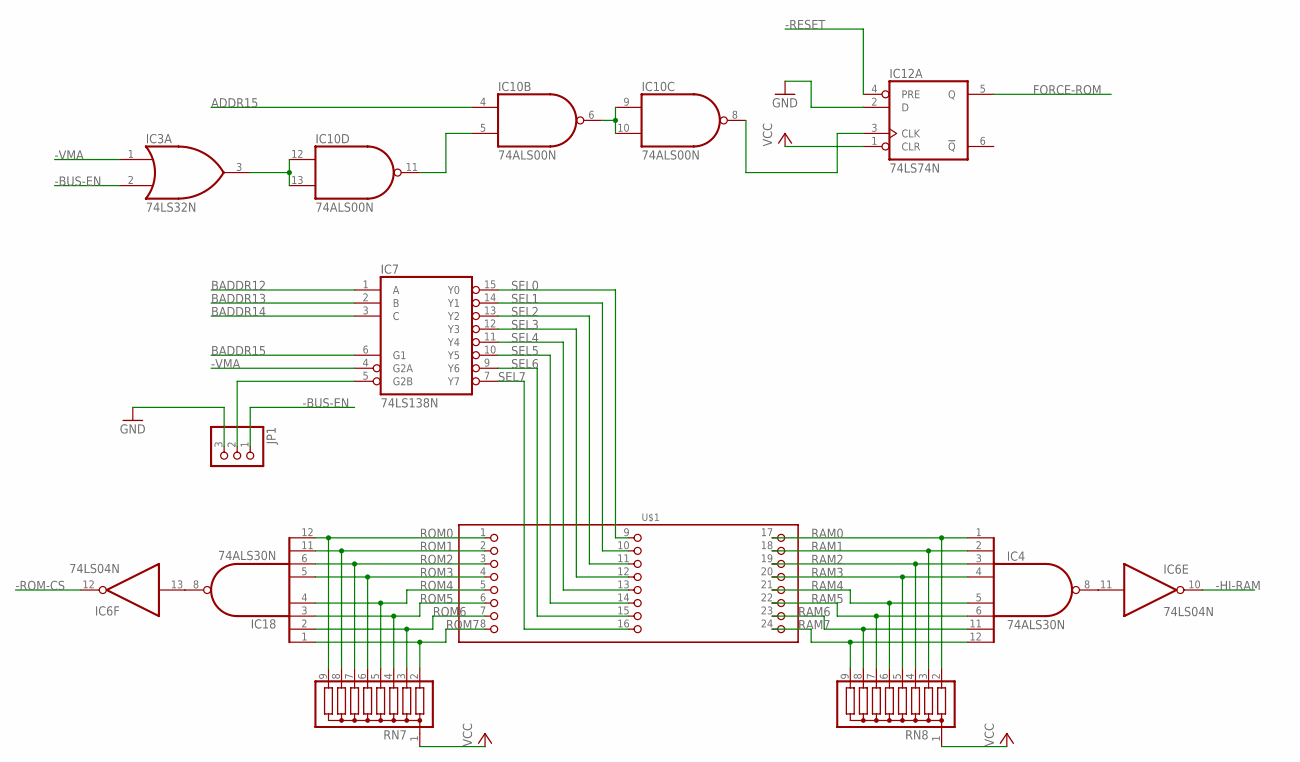
[picture p287: schematic Memory V1.3.sch, sheet 2, Memory Select]

Parts:
IC3: 74LS32N; DIL14
IC4, IC18: 74ALS30N; DIL14
IC6: 74LS04N; DIL14
IC7: 74LS138N; DIL16
IC10: 74ALS00N; DIL14
IC12: 74LS74N; DIL14
JP1: PINHD-1X3; 1X03
RN7, RN8: G08R; SIL9
U$1: PIN_3X8

Connections:
-BUS-EN: IC3.2 (I1), JP1.1; also elsewhere on the board
-HI-RAM: IC6.10 (O); also elsewhere on the board
-RESET: IC12.4 (PRE); also elsewhere on the board
-ROM-CS: IC6.12 (O); also elsewhere on the board
-VMA: IC3.1 (I0), IC7.4 (G2A); also elsewhere on the board
ADDR15: IC10.4 (I0); also elsewhere on the board
BADDR12: IC7.1 (A); also elsewhere on the board
BADDR13: IC7.2 (B); also elsewhere on the board
BADDR14: IC7.3 (C); also elsewhere on the board
BADDR15: IC7.6 (G1); also elsewhere on the board
FORCE-ROM: IC12.5 (Q); also elsewhere on the board
GND: IC3.7 (GND), IC4.7 (GND), IC6.7 (GND), IC7.8 (GND), IC10.7 (GND), IC12.2 (D), IC12.7 (GND), IC18.7 (GND), JP1.3; also elsewhere on the board
unnamed: IC6.13 (I), IC18.8 (O)
unnamed: IC4.8 (O), IC6.11 (I)
unnamed: IC10.8 (O), IC12.3 (CLK)
unnamed: IC10.6 (O), IC10.9 (I0), IC10.10 (I1)
unnamed: IC10.5 (I1), IC10.11 (O)
unnamed: IC7.5 (G2B), JP1.2
unnamed: IC3.3 (O), IC10.12 (I0), IC10.13 (I1)
RAM0: IC4.1 (I0), RN8.2, U$1.17
RAM1: IC4.2 (I1), RN8.3, U$1.18
RAM2: IC4.3 (I2), RN8.4, U$1.19
RAM3: IC4.4 (I3), RN8.5, U$1.20
RAM4: IC4.5 (I4), RN8.6, U$1.21
RAM5: IC4.6 (I5), RN8.7, U$1.22
RAM6: IC4.11 (I6), RN8.8, U$1.23
RAM7: IC4.12 (I7), RN8.9, U$1.24
ROM0: IC18.12 (I7), RN7.9, U$1.1
ROM1: IC18.11 (I6), RN7.8, U$1.2
ROM2: IC18.6 (I5), RN7.7, U$1.3
ROM3: IC18.5 (I4), RN7.6, U$1.4
ROM4: IC18.4 (I3), RN7.5, U$1.5
ROM5: IC18.3 (I2), RN7.4, U$1.6
ROM6: IC18.2 (I1), RN7.3, U$1.7
ROM7: IC18.1 (I0), RN7.2, U$1.8
SEL0: IC7.15 (Y0), U$1.9
SEL1: IC7.14 (Y1), U$1.10
SEL2: IC7.13 (Y2), U$1.11
SEL3: IC7.12 (Y3), U$1.12
SEL4: IC7.11 (Y4), U$1.13
SEL5: IC7.10 (Y5), U$1.14
SEL6: IC7.9 (Y6), U$1.15
SEL7: IC7.7 (Y7), U$1.16
VCC: IC3.14 (VCC), IC4.14 (VCC), IC6.14 (VCC), IC7.16 (VCC), IC10.14 (VCC), IC12.1 (CLR), IC12.14 (VCC), IC18.14 (VCC), RN7.1, RN8.1; also elsewhere on the board

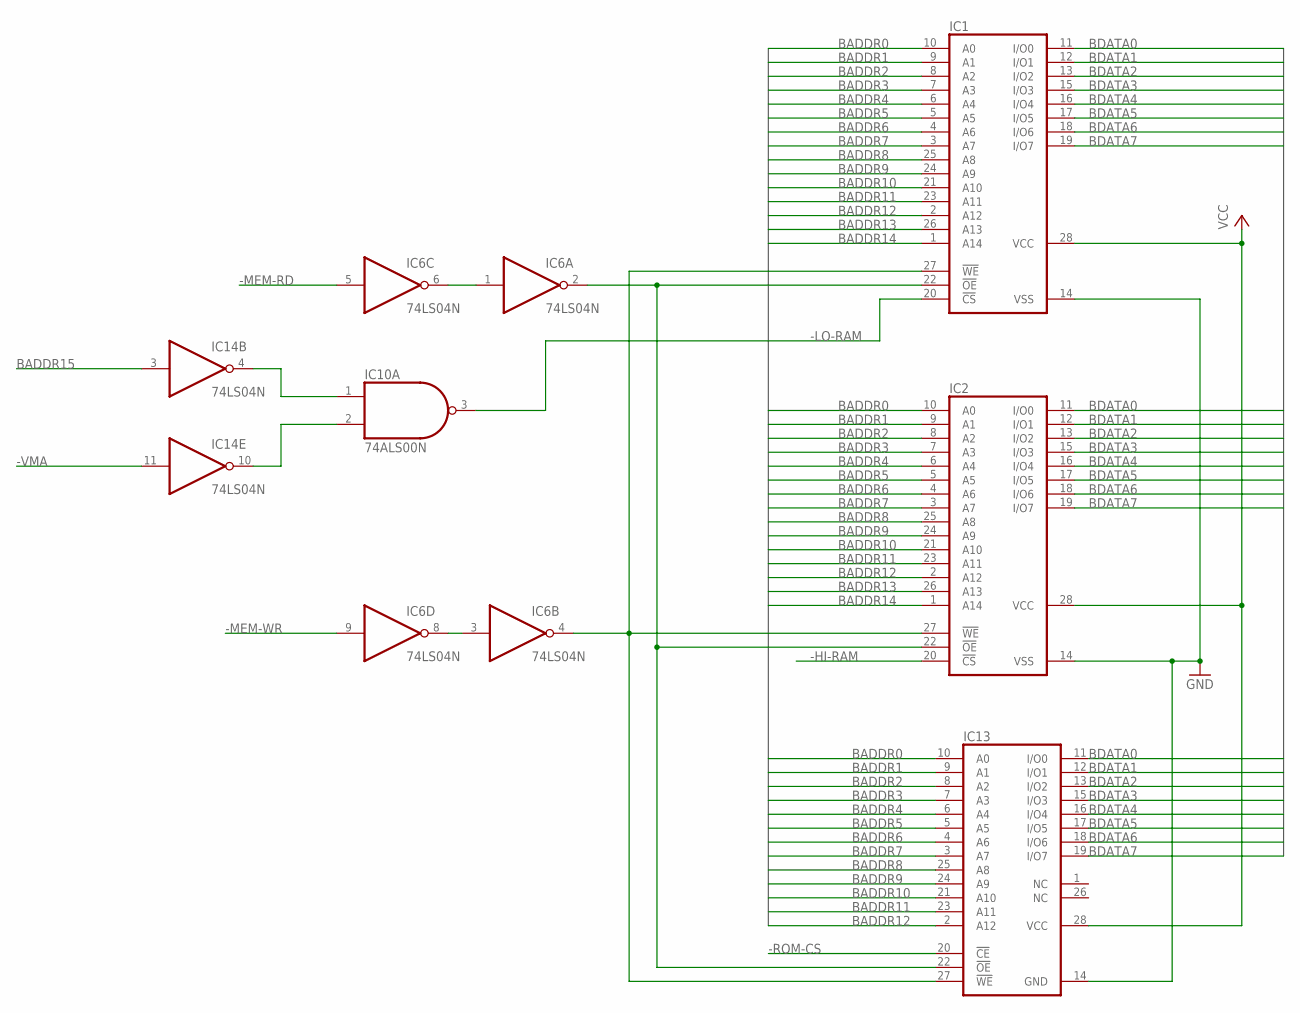
[picture p288: schematic Memory V1.3.sch, sheet 3, Memory]

Parts:
IC1, IC2: 62256P; DIL28-6
IC6, IC14: 74LS04N; DIL14
IC10: 74ALS00N; DIL14
IC13: 28C64C; DIL28-6

Connections:
-HI-RAM: IC2.20 (!CS); also elsewhere on the board
-LO-RAM: IC1.20 (!CS), IC10.3 (O); also elsewhere on the board
-MEM-RD: IC6.5 (I); also elsewhere on the board
-MEM-WR: IC6.9 (I); also elsewhere on the board
-ROM-CS: IC13.20 (!CE); also elsewhere on the board
-VMA: IC14.11 (I); also elsewhere on the board
BADDR0: IC1.10 (A0), IC2.10 (A0), IC13.10 (A0); also elsewhere on the board
BADDR1: IC1.9 (A1), IC2.9 (A1), IC13.9 (A1); also elsewhere on the board
BADDR2: IC1.8 (A2), IC2.8 (A2), IC13.8 (A2); also elsewhere on the board
BADDR3: IC1.7 (A3), IC2.7 (A3), IC13.7 (A3); also elsewhere on the board
BADDR4: IC1.6 (A4), IC2.6 (A4), IC13.6 (A4); also elsewhere on the board
BADDR5: IC1.5 (A5), IC2.5 (A5), IC13.5 (A5); also elsewhere on the board
BADDR6: IC1.4 (A6), IC2.4 (A6), IC13.4 (A6); also elsewhere on the board
BADDR7: IC1.3 (A7), IC2.3 (A7), IC13.3 (A7); also elsewhere on the board
BADDR8: IC1.25 (A8), IC2.25 (A8), IC13.25 (A8); also elsewhere on the board
BADDR9: IC1.24 (A9), IC2.24 (A9), IC13.24 (A9); also elsewhere on the board
BADDR10: IC1.21 (A10), IC2.21 (A10), IC13.21 (A10); also elsewhere on the board
BADDR11: IC1.23 (A11), IC2.23 (A11), IC13.23 (A11); also elsewhere on the board
BADDR12: IC1.2 (A12), IC2.2 (A12), IC13.2 (A12); also elsewhere on the board
BADDR13: IC1.26 (A13), IC2.26 (A13); also elsewhere on the board
BADDR14: IC1.1 (A14), IC2.1 (A14); also elsewhere on the board
BADDR15: IC14.3 (I); also elsewhere on the board
BDATA0: IC1.11 (I/O0), IC2.11 (I/O0), IC13.11 (I/O0); also elsewhere on the board
BDATA1: IC1.12 (I/O1), IC2.12 (I/O1), IC13.12 (I/O1); also elsewhere on the board
BDATA2: IC1.13 (I/O2), IC2.13 (I/O2), IC13.13 (I/O2); also elsewhere on the board
BDATA3: IC1.15 (I/O3), IC2.15 (I/O3), IC13.15 (I/O3); also elsewhere on the board
BDATA4: IC1.16 (I/O4), IC2.16 (I/O4), IC13.16 (I/O4); also elsewhere on the board
BDATA5: IC1.17 (I/O5), IC2.17 (I/O5), IC13.17 (I/O5); also elsewhere on the board
BDATA6: IC1.18 (I/O6), IC2.18 (I/O6), IC13.18 (I/O6); also elsewhere on the board
BDATA7: IC1.19 (I/O7), IC2.19 (I/O7), IC13.19 (I/O7); also elsewhere on the board
GND: IC1.14 (VSS), IC2.14 (VSS), IC6.7 (GND), IC10.7 (GND), IC13.14 (GND), IC14.7 (GND); also elsewhere on the board
MEM-RD: IC6.1 (I), IC6.6 (O)
unnamed: IC6.3 (I), IC6.8 (O)
unnamed: IC1.22 (!OE), IC2.22 (!OE), IC6.2 (O), IC13.22 (!OE)
unnamed: IC1.27 (!WE), IC2.27 (!WE), IC6.4 (O), IC13.27 (!WE)
unnamed: IC10.2 (I1), IC14.10 (O)
unnamed: IC10.1 (I0), IC14.4 (O)
VCC: IC1.28 (VCC), IC2.28 (VCC), IC6.14 (VCC), IC10.14 (VCC), IC13.28 (VCC), IC14.14 (VCC); also elsewhere on the board

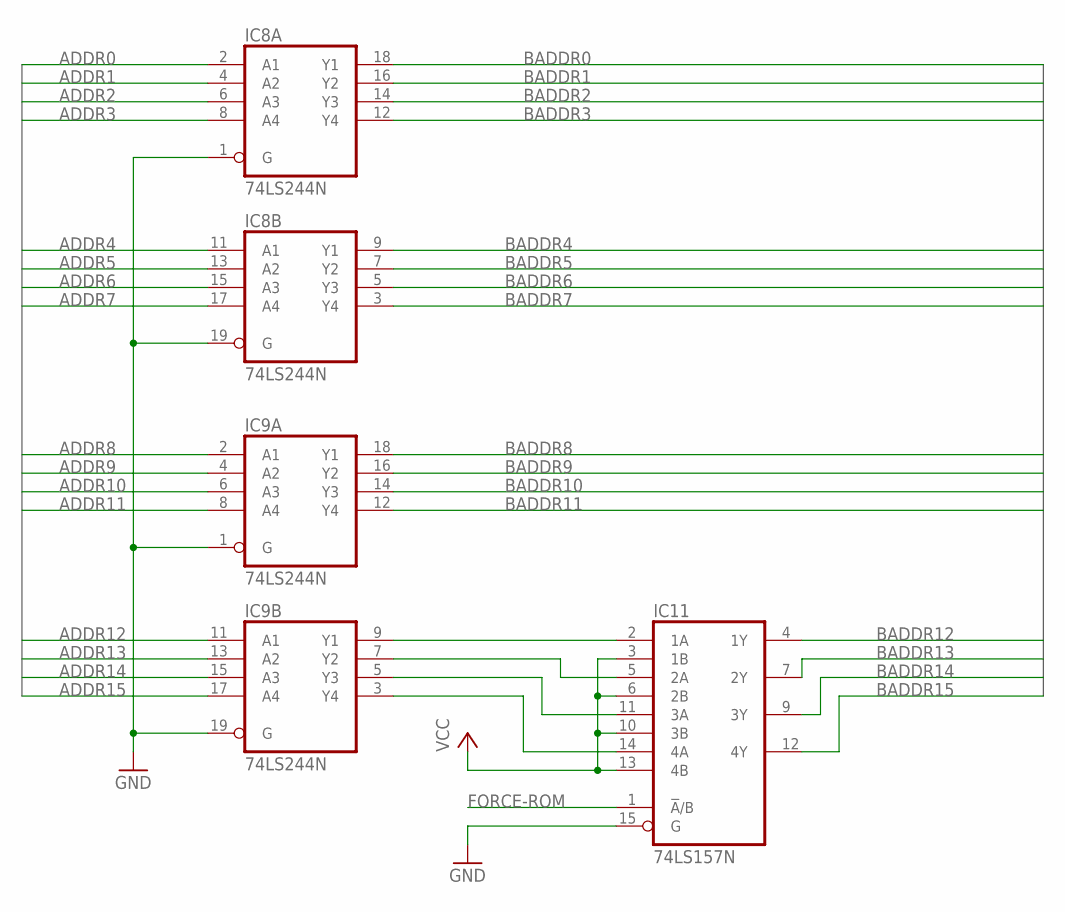
[picture p289: schematic Memory V1.3.sch, sheet 4, Adress Buffering]

Parts:
IC8, IC9: 74LS244N; DIL20
IC11: 74LS157N; DIL16

Connections:
ADDR0: IC8.2 (A1); also elsewhere on the board
ADDR1: IC8.4 (A2); also elsewhere on the board
ADDR2: IC8.6 (A3); also elsewhere on the board
ADDR3: IC8.8 (A4); also elsewhere on the board
ADDR4: IC8.11 (A1); also elsewhere on the board
ADDR5: IC8.13 (A2); also elsewhere on the board
ADDR6: IC8.15 (A3); also elsewhere on the board
ADDR7: IC8.17 (A4); also elsewhere on the board
ADDR8: IC9.2 (A1); also elsewhere on the board
ADDR9: IC9.4 (A2); also elsewhere on the board
ADDR10: IC9.6 (A3); also elsewhere on the board
ADDR11: IC9.8 (A4); also elsewhere on the board
ADDR12: IC9.11 (A1); also elsewhere on the board
ADDR13: IC9.13 (A2); also elsewhere on the board
ADDR14: IC9.15 (A3); also elsewhere on the board
ADDR15: IC9.17 (A4); also elsewhere on the board
BADDR0: IC8.18 (Y1); also elsewhere on the board
BADDR1: IC8.16 (Y2); also elsewhere on the board
BADDR2: IC8.14 (Y3); also elsewhere on the board
BADDR3: IC8.12 (Y4); also elsewhere on the board
BADDR4: IC8.9 (Y1); also elsewhere on the board
BADDR5: IC8.7 (Y2); also elsewhere on the board
BADDR6: IC8.5 (Y3); also elsewhere on the board
BADDR7: IC8.3 (Y4); also elsewhere on the board
BADDR8: IC9.18 (Y1); also elsewhere on the board
BADDR9: IC9.16 (Y2); also elsewhere on the board
BADDR10: IC9.14 (Y3); also elsewhere on the board
BADDR11: IC9.12 (Y4); also elsewhere on the board
BADDR12: IC11.4 (1Y); also elsewhere on the board
BADDR13: IC11.7 (2Y); also elsewhere on the board
BADDR14: IC11.9 (3Y); also elsewhere on the board
BADDR15: IC11.12 (4Y); also elsewhere on the board
FORCE-ROM: IC11.1 (!A!/B); also elsewhere on the board
GND: IC8.1 (G), IC8.10 (GND), IC8.19 (G), IC9.1 (G), IC9.10 (GND), IC9.19 (G), IC11.8 (GND), IC11.15 (G); also elsewhere on the board
unnamed: IC9.9 (Y1), IC11.2 (1A)
unnamed: IC9.7 (Y2), IC11.5 (2A)
unnamed: IC9.5 (Y3), IC11.11 (3A)
unnamed: IC9.3 (Y4), IC11.14 (4A)
VCC: IC8.20 (VCC), IC9.20 (VCC), IC11.3 (1B), IC11.6 (2B), IC11.10 (3B), IC11.13 (4B), IC11.16 (VCC); also elsewhere on the board

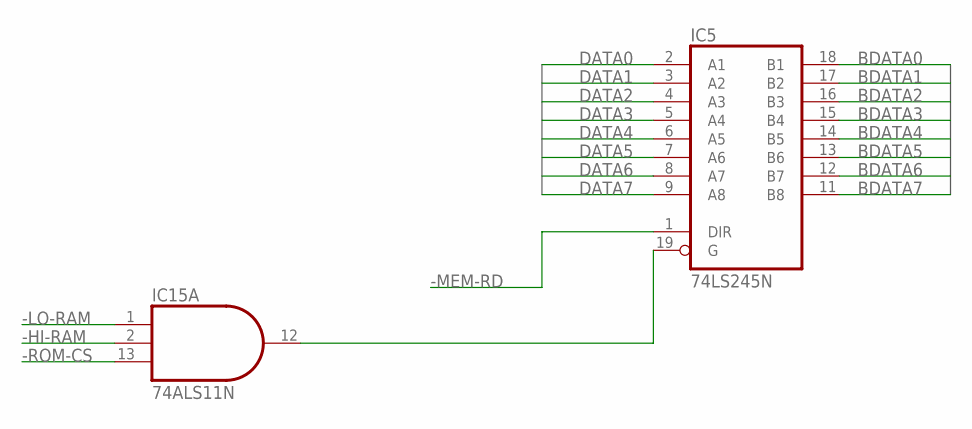
[picture p290: schematic Memory V1.3.sch, sheet 5, Data Buffer]

Parts:
IC5: 74LS245N; DIL20
IC15: 74ALS11N; DIL14

Connections:
-HI-RAM: IC15.2 (I1); also elsewhere on the board
-LO-RAM: IC15.1 (I0); also elsewhere on the board
-MEM-RD: IC5.1 (DIR); also elsewhere on the board
-ROM-CS: IC15.13 (I2); also elsewhere on the board
BDATA0: IC5.18 (B1); also elsewhere on the board
BDATA1: IC5.17 (B2); also elsewhere on the board
BDATA2: IC5.16 (B3); also elsewhere on the board
BDATA3: IC5.15 (B4); also elsewhere on the board
BDATA4: IC5.14 (B5); also elsewhere on the board
BDATA5: IC5.13 (B6); also elsewhere on the board
BDATA6: IC5.12 (B7); also elsewhere on the board
BDATA7: IC5.11 (B8); also elsewhere on the board
DATA0: IC5.2 (A1); also elsewhere on the board
DATA1: IC5.3 (A2); also elsewhere on the board
DATA2: IC5.4 (A3); also elsewhere on the board
DATA3: IC5.5 (A4); also elsewhere on the board
DATA4: IC5.6 (A5); also elsewhere on the board
DATA5: IC5.7 (A6); also elsewhere on the board
DATA6: IC5.8 (A7); also elsewhere on the board
DATA7: IC5.9 (A8); also elsewhere on the board
GND: IC5.10 (GND), IC15.7 (GND); also elsewhere on the board
unnamed: IC5.19 (G), IC15.12 (O)
VCC: IC5.20 (VCC), IC15.14 (VCC); also elsewhere on the board

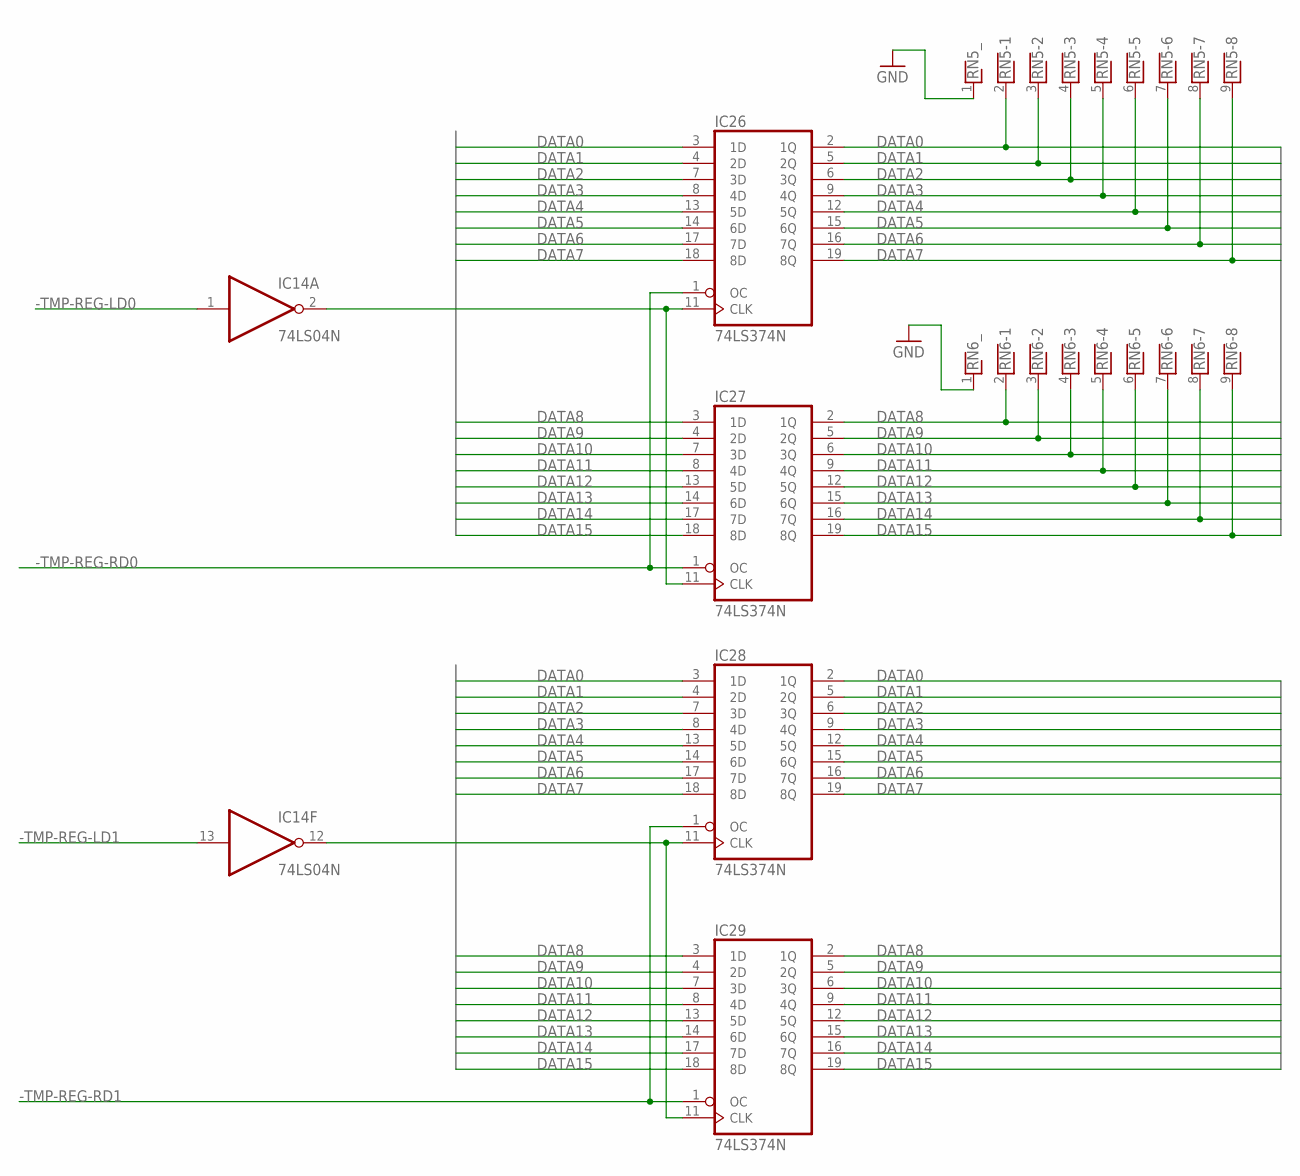
[picture p291: schematic Memory V1.3.sch, sheet 6]

Parts:
IC14: 74LS04N; DIL14
IC26, IC27, IC28, IC29: 74LS374N; DIL20
RN5, RN6: RNX8; RN-9

Connections:
-TMP-REG-LD0: IC14.1 (I); also elsewhere on the board
-TMP-REG-LD1: IC14.13 (I); also elsewhere on the board
-TMP-REG-RD0: IC26.1 (OC), IC27.1 (OC); also elsewhere on the board
-TMP-REG-RD1: IC28.1 (OC), IC29.1 (OC); also elsewhere on the board
DATA0: IC26.2 (1Q), IC26.3 (1D), IC28.2 (1Q), IC28.3 (1D), RN5.2; also elsewhere on the board
DATA1: IC26.4 (2D), IC26.5 (2Q), IC28.4 (2D), IC28.5 (2Q), RN5.3; also elsewhere on the board
DATA2: IC26.6 (3Q), IC26.7 (3D), IC28.6 (3Q), IC28.7 (3D), RN5.4; also elsewhere on the board
DATA3: IC26.8 (4D), IC26.9 (4Q), IC28.8 (4D), IC28.9 (4Q), RN5.5; also elsewhere on the board
DATA4: IC26.12 (5Q), IC26.13 (5D), IC28.12 (5Q), IC28.13 (5D), RN5.6; also elsewhere on the board
DATA5: IC26.14 (6D), IC26.15 (6Q), IC28.14 (6D), IC28.15 (6Q), RN5.7; also elsewhere on the board
DATA6: IC26.16 (7Q), IC26.17 (7D), IC28.16 (7Q), IC28.17 (7D), RN5.8; also elsewhere on the board
DATA7: IC26.18 (8D), IC26.19 (8Q), IC28.18 (8D), IC28.19 (8Q), RN5.9; also elsewhere on the board
DATA8: IC27.2 (1Q), IC27.3 (1D), IC29.2 (1Q), IC29.3 (1D), RN6.2; also elsewhere on the board
DATA9: IC27.4 (2D), IC27.5 (2Q), IC29.4 (2D), IC29.5 (2Q), RN6.3; also elsewhere on the board
DATA10: IC27.6 (3Q), IC27.7 (3D), IC29.6 (3Q), IC29.7 (3D), RN6.4; also elsewhere on the board
DATA11: IC27.8 (4D), IC27.9 (4Q), IC29.8 (4D), IC29.9 (4Q), RN6.5; also elsewhere on the board
DATA12: IC27.12 (5Q), IC27.13 (5D), IC29.12 (5Q), IC29.13 (5D), RN6.6; also elsewhere on the board
DATA13: IC27.14 (6D), IC27.15 (6Q), IC29.14 (6D), IC29.15 (6Q), RN6.7; also elsewhere on the board
DATA14: IC27.16 (7Q), IC27.17 (7D), IC29.16 (7Q), IC29.17 (7D), RN6.8; also elsewhere on the board
DATA15: IC27.18 (8D), IC27.19 (8Q), IC29.18 (8D), IC29.19 (8Q), RN6.9; also elsewhere on the board
GND: IC14.7 (GND), IC26.10 (GND), IC27.10 (GND), IC28.10 (GND), IC29.10 (GND), RN5.1, RN6.1; also elsewhere on the board
unnamed: IC14.2 (O), IC26.11 (CLK), IC27.11 (CLK)
unnamed: IC14.12 (O), IC28.11 (CLK), IC29.11 (CLK)
VCC: IC14.14 (VCC), IC26.20 (VCC), IC27.20 (VCC), IC28.20 (VCC), IC29.20 (VCC); also elsewhere on the board

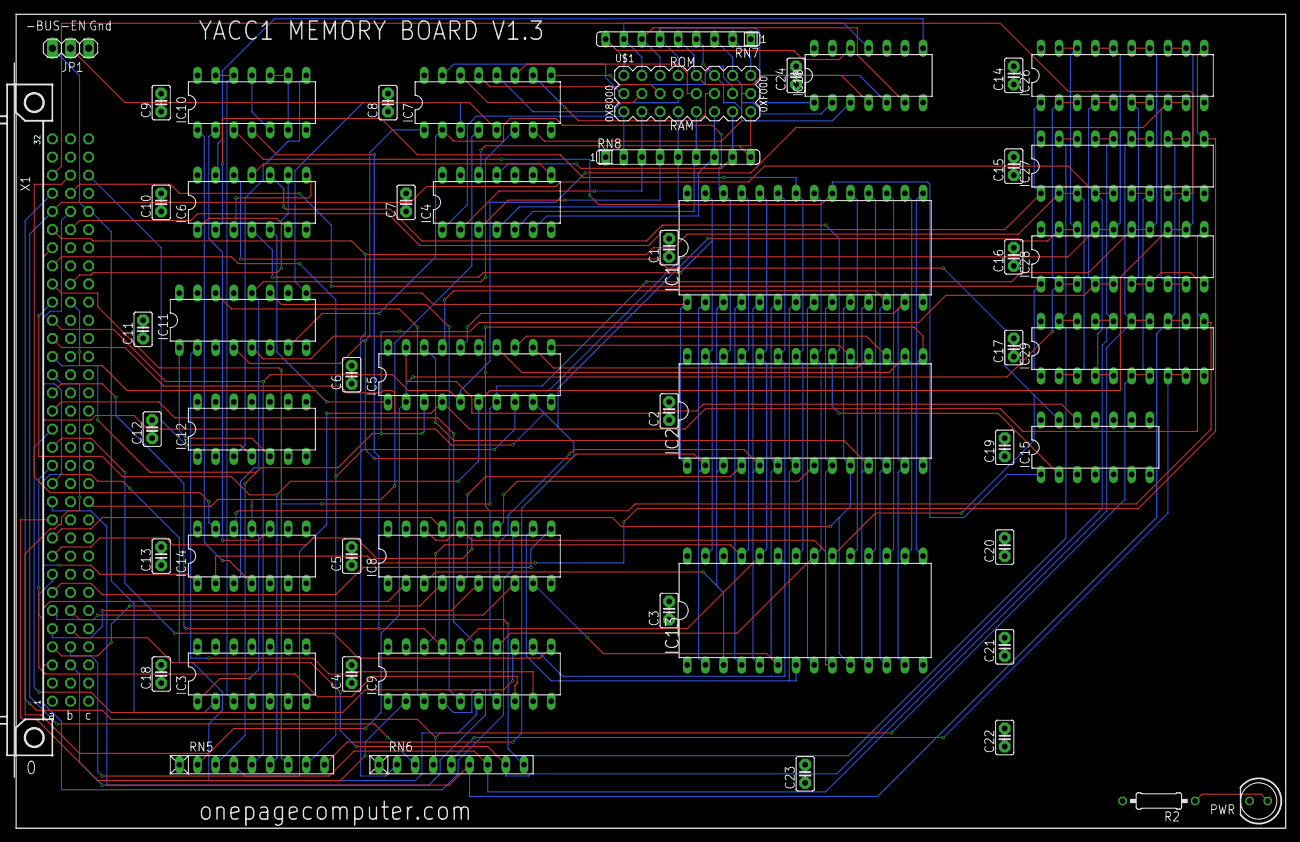
[picture p292: board Memory V1.3.brd from above]

Board: 4 copper layers, 177.8 x 114.0 mm, 53 parts (0 on the bottom side), 116 nets.
