ksr/YACC1-D/hardware/cards/video/eagle/v1.0-fusion-export-2026-09-18/Video_1.0.brd

## EAGLE design hardware/cards/video/eagle/v1.0-fusion-export-2026-09-18/Video_1.0.brd (2026-09-20)

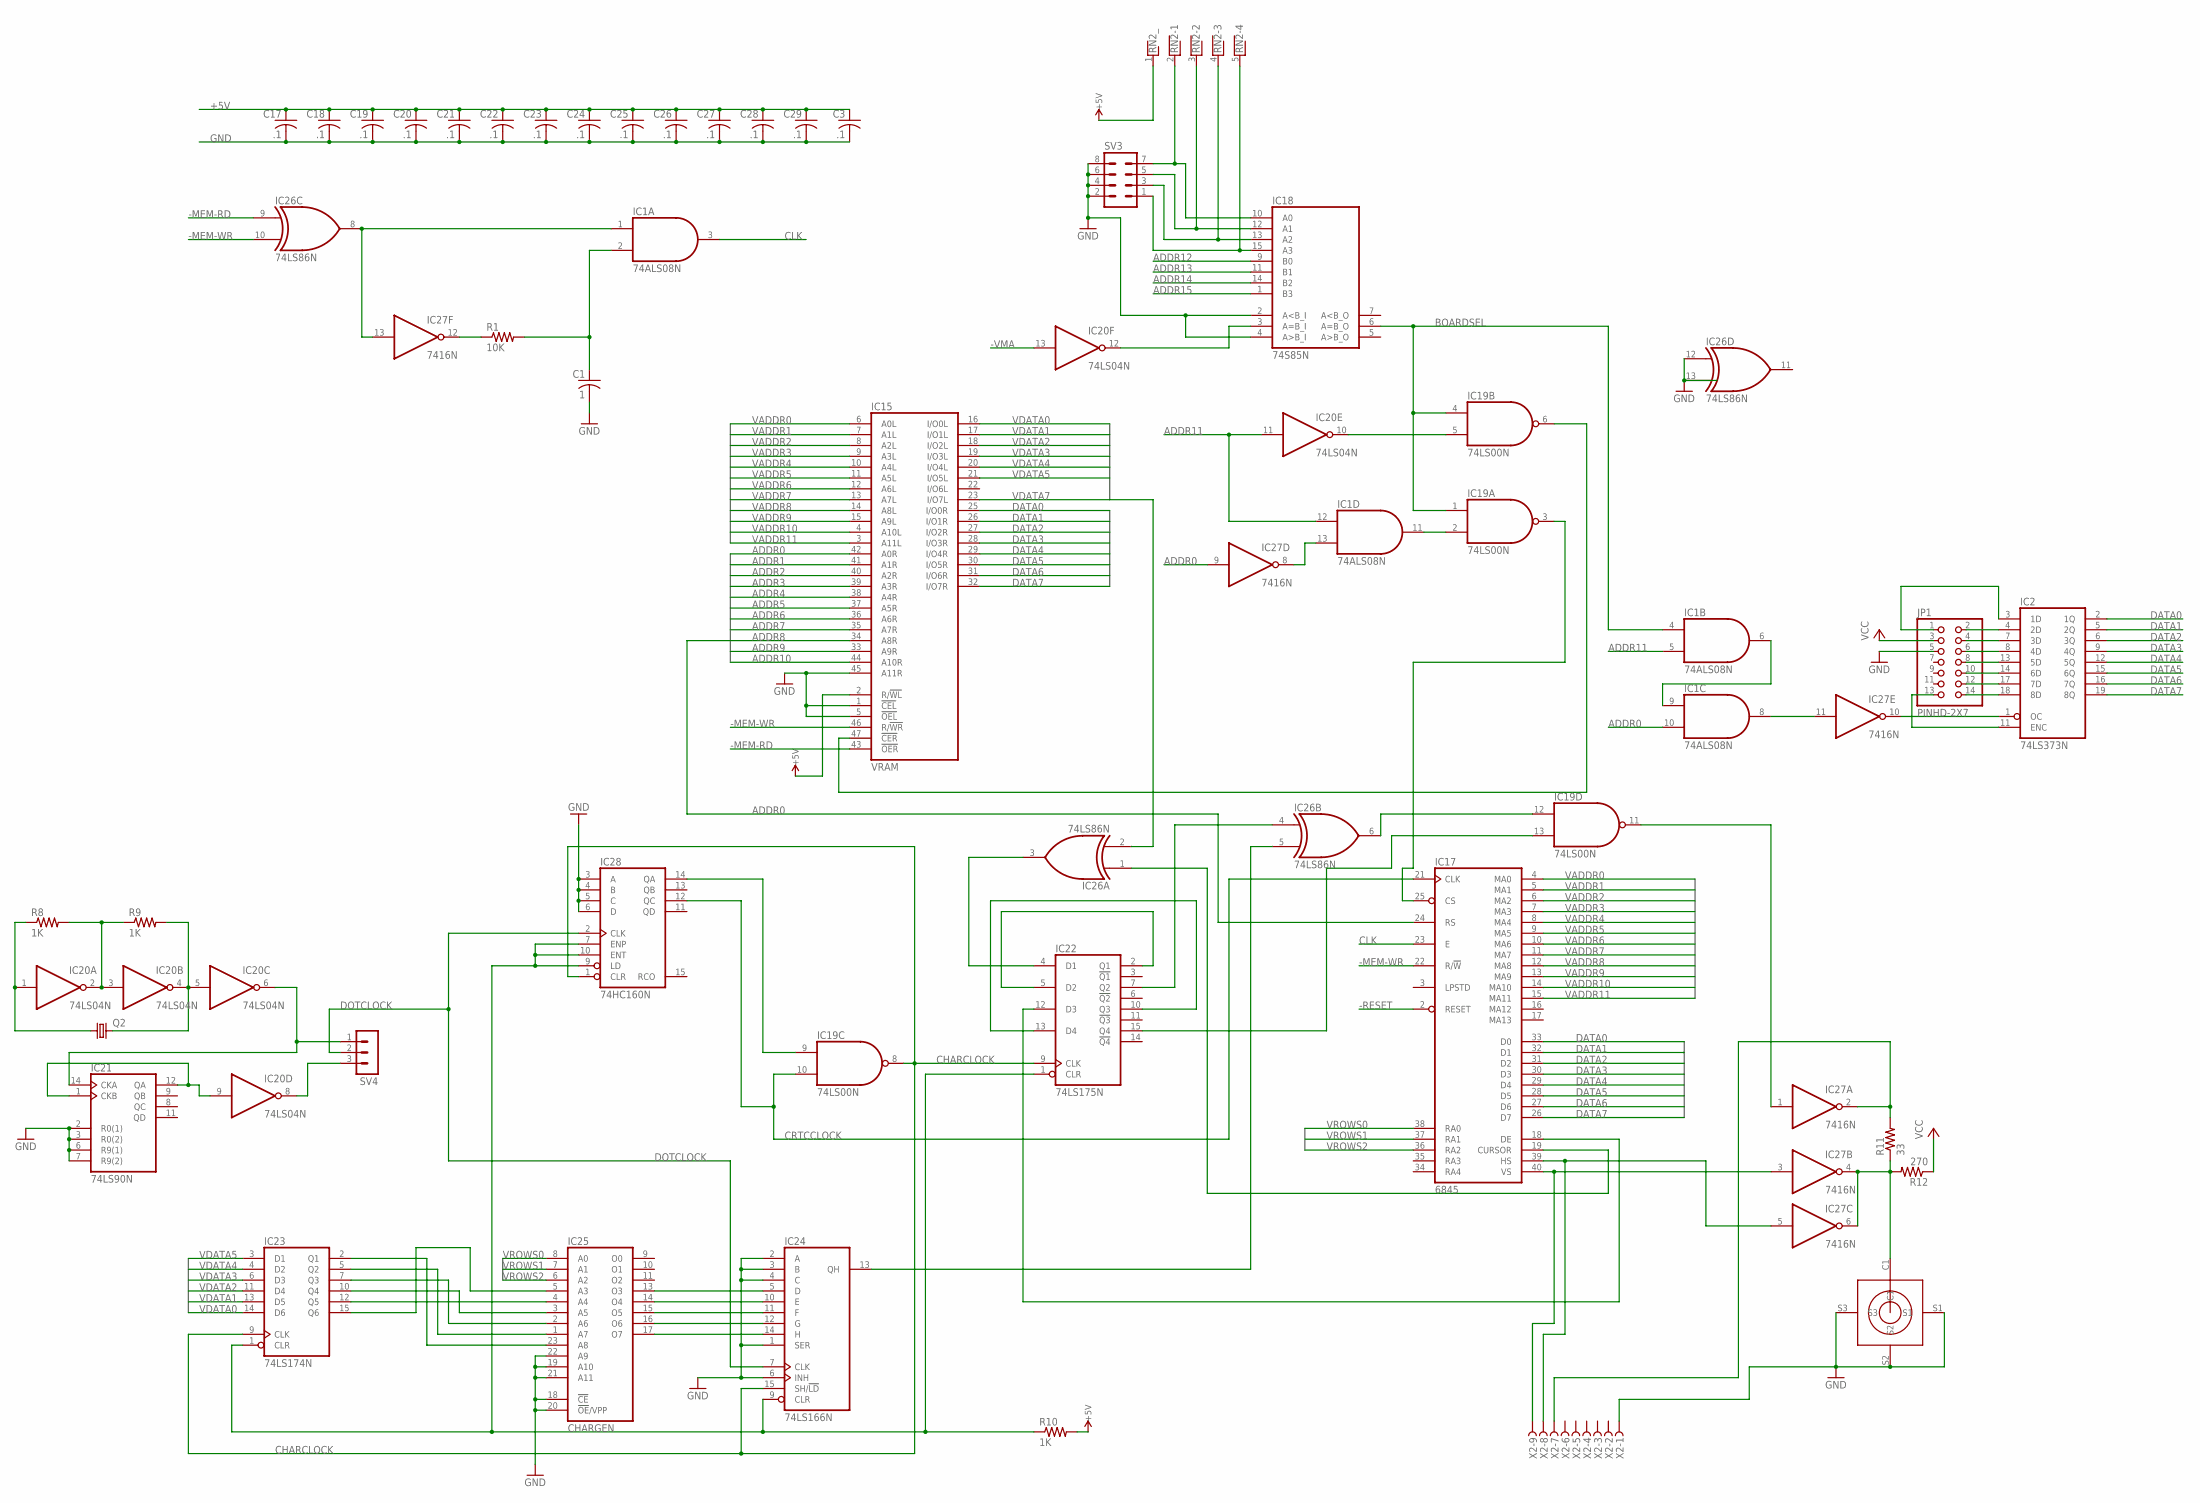
[picture p295: schematic Video_1.0.sch, sheet 1, BUS]

Parts:
C1: 1; C025-050X050
C3, C17, C18, C19, C20, C21, C22, C23, C24, C25, C26, C27, C28, C29: .1; C025-050X050
IC1: 74ALS08N; DIL14
IC2: 74LS373N; DIL20
IC15: VRAM; DIL48
IC17: 6845; DIL40
IC18: 74S85N; DIL16
IC19: 74LS00N; DIL14
IC20: 74LS04N; DIL14
IC21: 74LS90N; DIL14
IC22: 74LS175N; DIL16
IC23: 74LS174N; DIL16
IC24: 74LS166N; DIL16
IC25: CHARGEN; DIL24
IC26: 74LS86N; DIL14
IC27: 7416N; DIL14
IC28: 74HC160N; DIL16
JP1: PINHD-2X7; 2X07
Q2: CRYTALHC49U-V; HC49U-V
R1: 10K; 0207/7
R8, R9, R10: 1K; 0207/7
R11: 33; 0207/7
R12: 270; 0207/7
RN2: RNX4; RN-5
SV3: MA04-2
SV4: MA03-1
U$3: RCA
X2: F09HPS; F09HP

Connections:
+5V: C3.1, C17.1, C18.1, C19.1, C20.1, C21.1, C22.1, C23.1, C24.1, C25.1, C26.1, C27.1, C28.1, C29.1, IC1.14 (VCC), IC2.20 (VCC), IC15.2 (R/!WL), R10.2, R12.1, RN2.1; also elsewhere on the board
-MEM-RD: IC15.43 (!OER), IC26.9 (I0); also elsewhere on the board
-MEM-WR: IC15.46 (R/!WR), IC17.22 (R/!W), IC26.10 (I1); also elsewhere on the board
-RESET: IC17.2 (RESET); also elsewhere on the board
-VMA: IC20.13 (I); also elsewhere on the board
ADDR0: IC1.10 (I1), IC15.42 (A0R), IC17.24 (RS), IC27.9 (I); also elsewhere on the board
ADDR1: IC15.41 (A1R); also elsewhere on the board
ADDR2: IC15.40 (A2R); also elsewhere on the board
ADDR3: IC15.39 (A3R); also elsewhere on the board
ADDR4: IC15.38 (A4R); also elsewhere on the board
ADDR5: IC15.37 (A5R); also elsewhere on the board
ADDR6: IC15.36 (A6R); also elsewhere on the board
ADDR7: IC15.35 (A7R); also elsewhere on the board
ADDR8: IC15.34 (A8R); also elsewhere on the board
ADDR9: IC15.33 (A9R); also elsewhere on the board
ADDR10: IC15.44 (A10R); also elsewhere on the board
ADDR11: IC1.5 (I1), IC1.12 (I0), IC20.11 (I); also elsewhere on the board
ADDR12: IC18.9 (B0); also elsewhere on the board
ADDR13: IC18.11 (B1); also elsewhere on the board
ADDR14: IC18.14 (B2); also elsewhere on the board
ADDR15: IC18.1 (B3); also elsewhere on the board
BOARDSEL: IC1.4 (I0), IC18.6 (A=B_O), IC19.1 (I0), IC19.4 (I0)
CHARCLOCK: IC19.8 (O), IC22.9 (CLK), IC23.9 (CLK), IC24.15 (SH/!LD), IC28.1 (CLR)
CLK: IC1.3 (O), IC17.23 (E)
CRTCCLOCK: IC17.21 (CLK), IC19.10 (I1), IC28.12 (QC)
DATA0: IC2.2 (1Q), IC15.25 (I/O0R), IC17.33 (D0); also elsewhere on the board
DATA1: IC2.5 (2Q), IC15.26 (I/O1R), IC17.32 (D1); also elsewhere on the board
DATA2: IC2.6 (3Q), IC15.27 (I/O2R), IC17.31 (D2); also elsewhere on the board
DATA3: IC2.9 (4Q), IC15.28 (I/O3R), IC17.30 (D3); also elsewhere on the board
DATA4: IC2.12 (5Q), IC15.29 (I/O4R), IC17.29 (D4); also elsewhere on the board
DATA5: IC2.15 (6Q), IC15.30 (I/O5R), IC17.28 (D5); also elsewhere on the board
DATA6: IC2.16 (7Q), IC15.31 (I/O6R), IC17.27 (D6); also elsewhere on the board
DATA7: IC2.19 (8Q), IC15.32 (I/O7R), IC17.26 (D7); also elsewhere on the board
DOTCLOCK: IC24.7 (CLK), IC28.2 (CLK), SV4.2
GND: C1.2, C3.2, C17.2, C18.2, C19.2, C20.2, C21.2, C22.2, C23.2, C24.2, C25.2, C26.2, C27.2, C28.2, C29.2, IC1.7 (GND), IC2.10 (GND), IC15.1 (!CEL), IC15.5 (!OEL), IC15.24 (GND), IC15.45 (A11R), IC17.1 (GND), IC18.2 (A<B_I), IC18.4 (A>B_I), IC18.8 (GND), IC19.7 (GND), IC20.7 (GND), IC21.2 (R0(1)), IC21.3 (R0(2)), IC21.6 (R9(1)), IC21.7 (R9(2)), IC21.10 (GND), IC22.8 (GND), IC23.8 (GND), IC24.1 (SER), IC24.2 (A), IC24.3 (B), IC24.4 (C), IC24.6 (INH), IC24.8 (GND), IC25.12 (GND), IC25.18 (!CE), IC25.19 (A10), IC25.20 (!OE!/VPP), IC25.21 (A11), IC25.22 (A9), IC26.7 (GND), IC26.12 (I0), IC26.13 (I1), IC27.7 (GND), IC28.3 (A), IC28.4 (B), IC28.5 (C), IC28.6 (D), IC28.8 (GND), JP1.5, SV3.2, SV3.4, SV3.6, SV3.8, U$3.S1, U$3.S2, U$3.S3, X2.1; also elsewhere on the board
unnamed: IC1.1 (I0), IC26.8 (O), IC27.13 (I)
unnamed: IC1.11 (O), IC19.2 (I1)
unnamed: IC27.12 (O), R1.1
unnamed: C1.1, IC1.2 (I1), R1.2
unnamed: IC1.13 (I1), IC27.8 (O)
unnamed: IC1.8 (O), IC27.11 (I)
unnamed: IC2.18 (8D), JP1.14
unnamed: IC2.17 (7D), JP1.12
unnamed: IC2.14 (6D), JP1.10
unnamed: IC2.13 (5D), JP1.8
unnamed: IC2.8 (4D), JP1.6
unnamed: IC2.7 (3D), JP1.4
unnamed: IC2.4 (2D), JP1.2
unnamed: IC2.3 (1D), JP1.1
unnamed: IC2.1 (OC), IC27.10 (O)
unnamed: IC1.6 (O), IC1.9 (I0)
unnamed: IC2.11 (ENC), JP1.13
unnamed: IC18.10 (A0), RN2.2, SV3.7
unnamed: IC18.12 (A1), RN2.3, SV3.5
unnamed: IC18.13 (A2), RN2.4, SV3.3
unnamed: IC18.15 (A3), RN2.5, SV3.1
unnamed: IC15.47 (!CER), IC19.6 (O)
unnamed: IC20.1 (I), Q2.1, R8.1
unnamed: IC20.4 (O), IC20.5 (I), Q2.2, R9.2
unnamed: IC20.2 (O), IC20.3 (I), R8.2, R9.1
unnamed: IC20.6 (O), IC21.14 (CKA), SV4.1
unnamed: IC20.9 (I), IC21.1 (CKB), IC21.12 (QA)
unnamed: IC20.8 (O), SV4.3
unnamed: IC19.9 (I0), IC28.14 (QA)
unnamed: IC22.2 (Q1), IC22.5 (D2)
unnamed: IC24.5 (D), IC25.13 (O3)
unnamed: IC24.10 (E), IC25.14 (O4)
unnamed: IC24.11 (F), IC25.15 (O5)
unnamed: IC24.12 (G), IC25.16 (O6)
unnamed: IC24.14 (H), IC25.17 (O7)
unnamed: IC23.2 (Q1), IC25.23 (A8)
unnamed: IC23.5 (Q2), IC25.1 (A7)
unnamed: IC23.7 (Q3), IC25.2 (A6)
unnamed: IC23.10 (Q4), IC25.3 (A5)
unnamed: IC23.12 (Q5), IC25.4 (A4)
unnamed: IC23.15 (Q6), IC25.5 (A3)
unnamed: IC22.1 (CLR), IC23.1 (CLR), IC24.9 (CLR), IC28.7 (ENP), IC28.9 (LD), IC28.10 (ENT), R10.1
unnamed: IC17.19 (CURSOR), IC26.1 (I0)
unnamed: IC22.4 (D1), IC26.3 (O)
unnamed: IC22.7 (Q2), IC26.4 (I0)
unnamed: IC24.13 (QH), IC26.5 (I1)
unnamed: IC22.10 (Q3), IC22.13 (D4)
unnamed: IC17.18 (DE), IC22.12 (D3)
unnamed: IC19.12 (I0), IC26.6 (O)
unnamed: IC19.13 (I1), IC22.15 (Q4)
unnamed: IC17.40 (VS), IC27.3 (I), X2.9
unnamed: IC17.39 (HS), IC27.5 (I), X2.8
unnamed: IC19.11 (O), IC27.1 (I)
unnamed: IC27.4 (O), IC27.6 (O), R11.1, R12.2, U$3.C1
unnamed: IC27.2 (O), R11.2, X2.7
unnamed: IC19.5 (I1), IC20.10 (O)
unnamed: IC18.3 (A=B_I), IC20.12 (O)
unnamed: IC17.25 (CS), IC19.3 (O)
VADDR0: IC15.6 (A0L), IC17.4 (MA0)
VADDR1: IC15.7 (A1L), IC17.5 (MA1)
VADDR2: IC15.8 (A2L), IC17.6 (MA2)
VADDR3: IC15.9 (A3L), IC17.7 (MA3)
VADDR4: IC15.10 (A4L), IC17.8 (MA4)
VADDR5: IC15.11 (A5L), IC17.9 (MA5)
VADDR6: IC15.12 (A6L), IC17.10 (MA6)
VADDR7: IC15.13 (A7L), IC17.11 (MA7)
VADDR8: IC15.14 (A8L), IC17.12 (MA8)
VADDR9: IC15.15 (A9L), IC17.13 (MA9)
VADDR10: IC15.4 (A10L), IC17.14 (MA10)
VADDR11: IC15.3 (A11L), IC17.15 (MA11)
VCC: IC15.48 (VCC), IC17.20 (VCC), IC18.16 (VCC), IC19.14 (VCC), IC20.14 (VCC), IC21.5 (VCC), IC22.16 (VCC), IC23.16 (VCC), IC24.16 (VCC), IC25.24 (VCC), IC26.14 (VCC), IC27.14 (VCC), IC28.16 (VCC), JP1.3; also elsewhere on the board
VDATA0: IC15.16 (I/O0L), IC23.14 (D6)
VDATA1: IC15.17 (I/O1L), IC23.13 (D5)
VDATA2: IC15.18 (I/O2L), IC23.11 (D4)
VDATA3: IC15.19 (I/O3L), IC23.6 (D3)
VDATA4: IC15.20 (I/O4L), IC23.4 (D2)
VDATA5: IC15.21 (I/O5L), IC23.3 (D1)
VDATA7: IC15.23 (I/O7L), IC26.2 (I1)
VROWS0: IC17.38 (RA0), IC25.8 (A0)
VROWS1: IC17.37 (RA1), IC25.7 (A1)
VROWS2: IC17.36 (RA2), IC25.6 (A2)

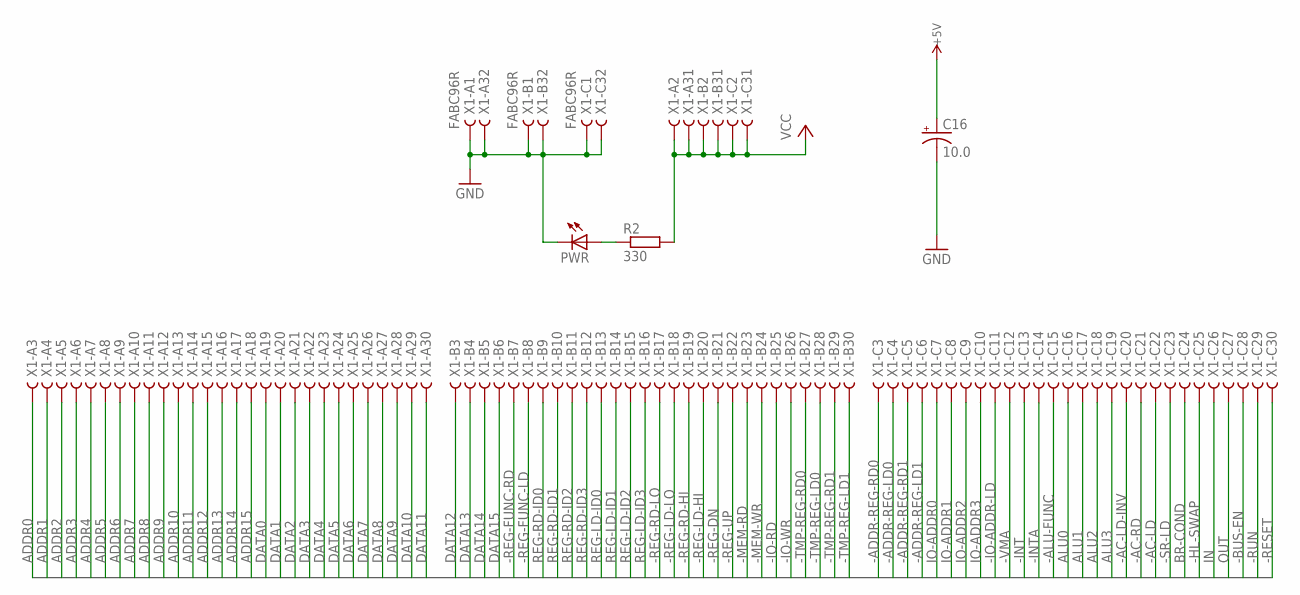
[picture p296: schematic Video_1.0.sch, sheet 2]

Parts:
C16: 10.0; E2,5-7
PWR: LED5MM
R2: 330; 0207/10
X1: FABC96R

Connections:
+5V: C16.+; also elsewhere on the board
-AC-LD: X1.C22
-AC-LD-INV: X1.C20
-AC-RD: X1.C21
-ADDR-REG-LD0: X1.C4
-ADDR-REG-LD1: X1.C6
-ADDR-REG-RD0: X1.C3
-ADDR-REG-RD1: X1.C5
-ALU-FUNC: X1.C15
-BUS-EN: X1.C28
-HL-SWAP: X1.C25
-INT: X1.C13
-INTA: X1.C14
-IO-ADDR-LD: X1.C11
-IO-RD: X1.B25
-IO-WR: X1.B26
-MEM-RD: X1.B23; also elsewhere on the board
-MEM-WR: X1.B24; also elsewhere on the board
-REG-DN: X1.B21
-REG-FUNC-LD: X1.B8
-REG-FUNC-RD: X1.B7
-REG-LD-HI: X1.B20
-REG-LD-LO: X1.B18
-REG-RD-HI: X1.B19
-REG-RD-LO: X1.B17
-REG-UP: X1.B22
-RESET: X1.C30; also elsewhere on the board
-RUN: X1.C29
-SR-LD: X1.C23
-TMP-REG-LD0: X1.B28
-TMP-REG-LD1: X1.B30
-TMP-REG-RD0: X1.B27
-TMP-REG-RD1: X1.B29
-VMA: X1.C12; also elsewhere on the board
ADDR0: X1.A3; also elsewhere on the board
ADDR1: X1.A4; also elsewhere on the board
ADDR2: X1.A5; also elsewhere on the board
ADDR3: X1.A6; also elsewhere on the board
ADDR4: X1.A7; also elsewhere on the board
ADDR5: X1.A8; also elsewhere on the board
ADDR6: X1.A9; also elsewhere on the board
ADDR7: X1.A10; also elsewhere on the board
ADDR8: X1.A11; also elsewhere on the board
ADDR9: X1.A12; also elsewhere on the board
ADDR10: X1.A13; also elsewhere on the board
ADDR11: X1.A14; also elsewhere on the board
ADDR12: X1.A15; also elsewhere on the board
ADDR13: X1.A16; also elsewhere on the board
ADDR14: X1.A17; also elsewhere on the board
ADDR15: X1.A18; also elsewhere on the board
ALU0: X1.C16
ALU1: X1.C17
ALU2: X1.C18
ALU3: X1.C19
BR-COND: X1.C24
DATA0: X1.A19; also elsewhere on the board
DATA1: X1.A20; also elsewhere on the board
DATA2: X1.A21; also elsewhere on the board
DATA3: X1.A22; also elsewhere on the board
DATA4: X1.A23; also elsewhere on the board
DATA5: X1.A24; also elsewhere on the board
DATA6: X1.A25; also elsewhere on the board
DATA7: X1.A26; also elsewhere on the board
DATA8: X1.A27
DATA9: X1.A28
DATA10: X1.A29
DATA11: X1.A30
DATA12: X1.B3
DATA13: X1.B4
DATA14: X1.B5
DATA15: X1.B6
GND: C16.-, PWR.K (C), X1.A1, X1.A32, X1.B1, X1.B32, X1.C1, X1.C32; also elsewhere on the board
IN: X1.C26
IO-ADDR0: X1.C7
IO-ADDR1: X1.C8
IO-ADDR2: X1.C9
IO-ADDR3: X1.C10
unnamed: PWR.A, R2.1
OUT: X1.C27
REG-LD-ID0: X1.B13
REG-LD-ID1: X1.B14
REG-LD-ID2: X1.B15
REG-LD-ID3: X1.B16
REG-RD-ID0: X1.B9
REG-RD-ID1: X1.B10
REG-RD-ID2: X1.B11
REG-RD-ID3: X1.B12
VCC: R2.2, X1.A2, X1.A31, X1.B2, X1.B31, X1.C2, X1.C31; also elsewhere on the board

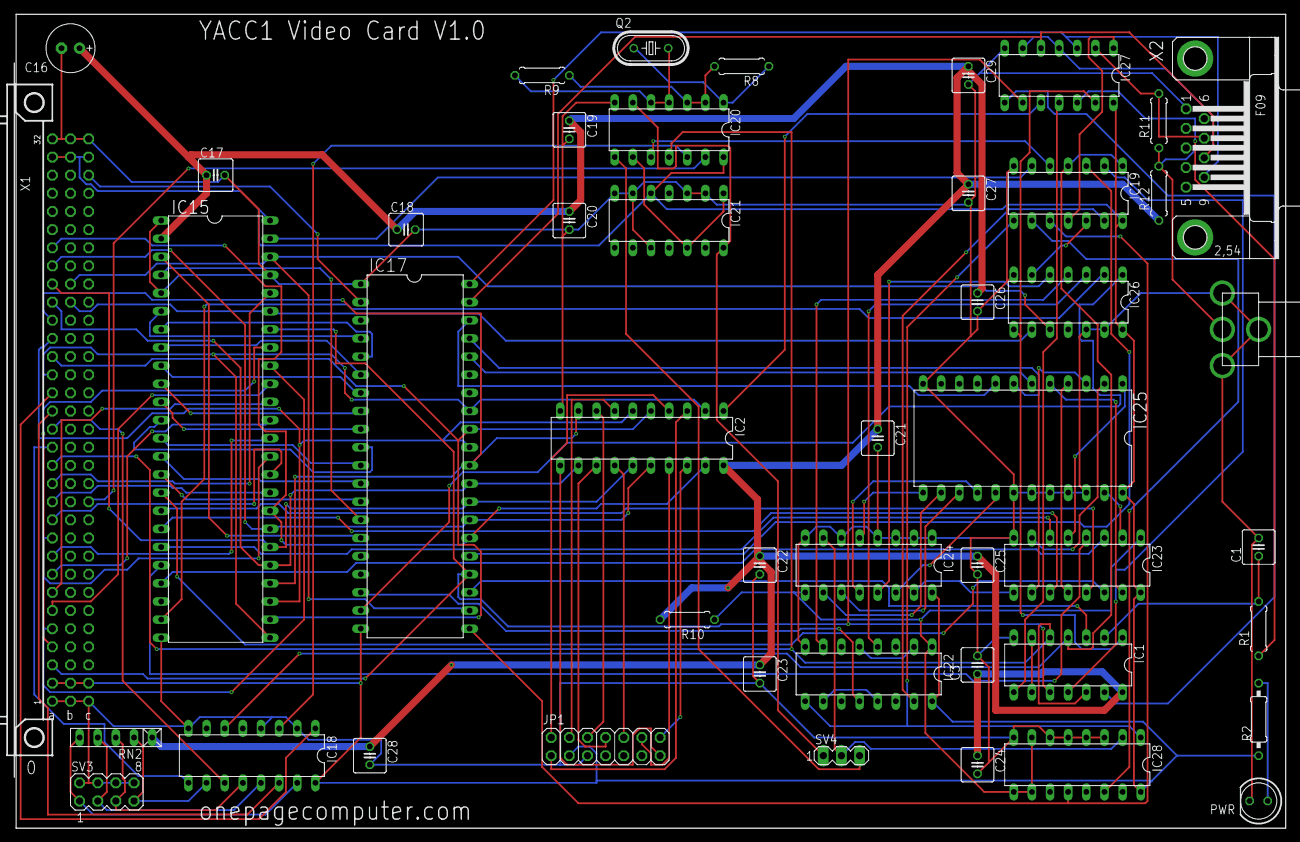
[picture p297: board Video_1.0.brd from above]

Board: 2 copper layers, 177.8 x 114.0 mm, 47 parts (0 on the bottom side), 117 nets.
