ksr/YACC1-D/hardware/cards/sequencer-logic/eagle/v2.1/Sequencer-Logic-Prod-V2.1l.brd

## EAGLE design hardware/cards/sequencer-logic/eagle/v2.1/Sequencer-Logic-Prod-V2.1l.brd (2026-09-20)

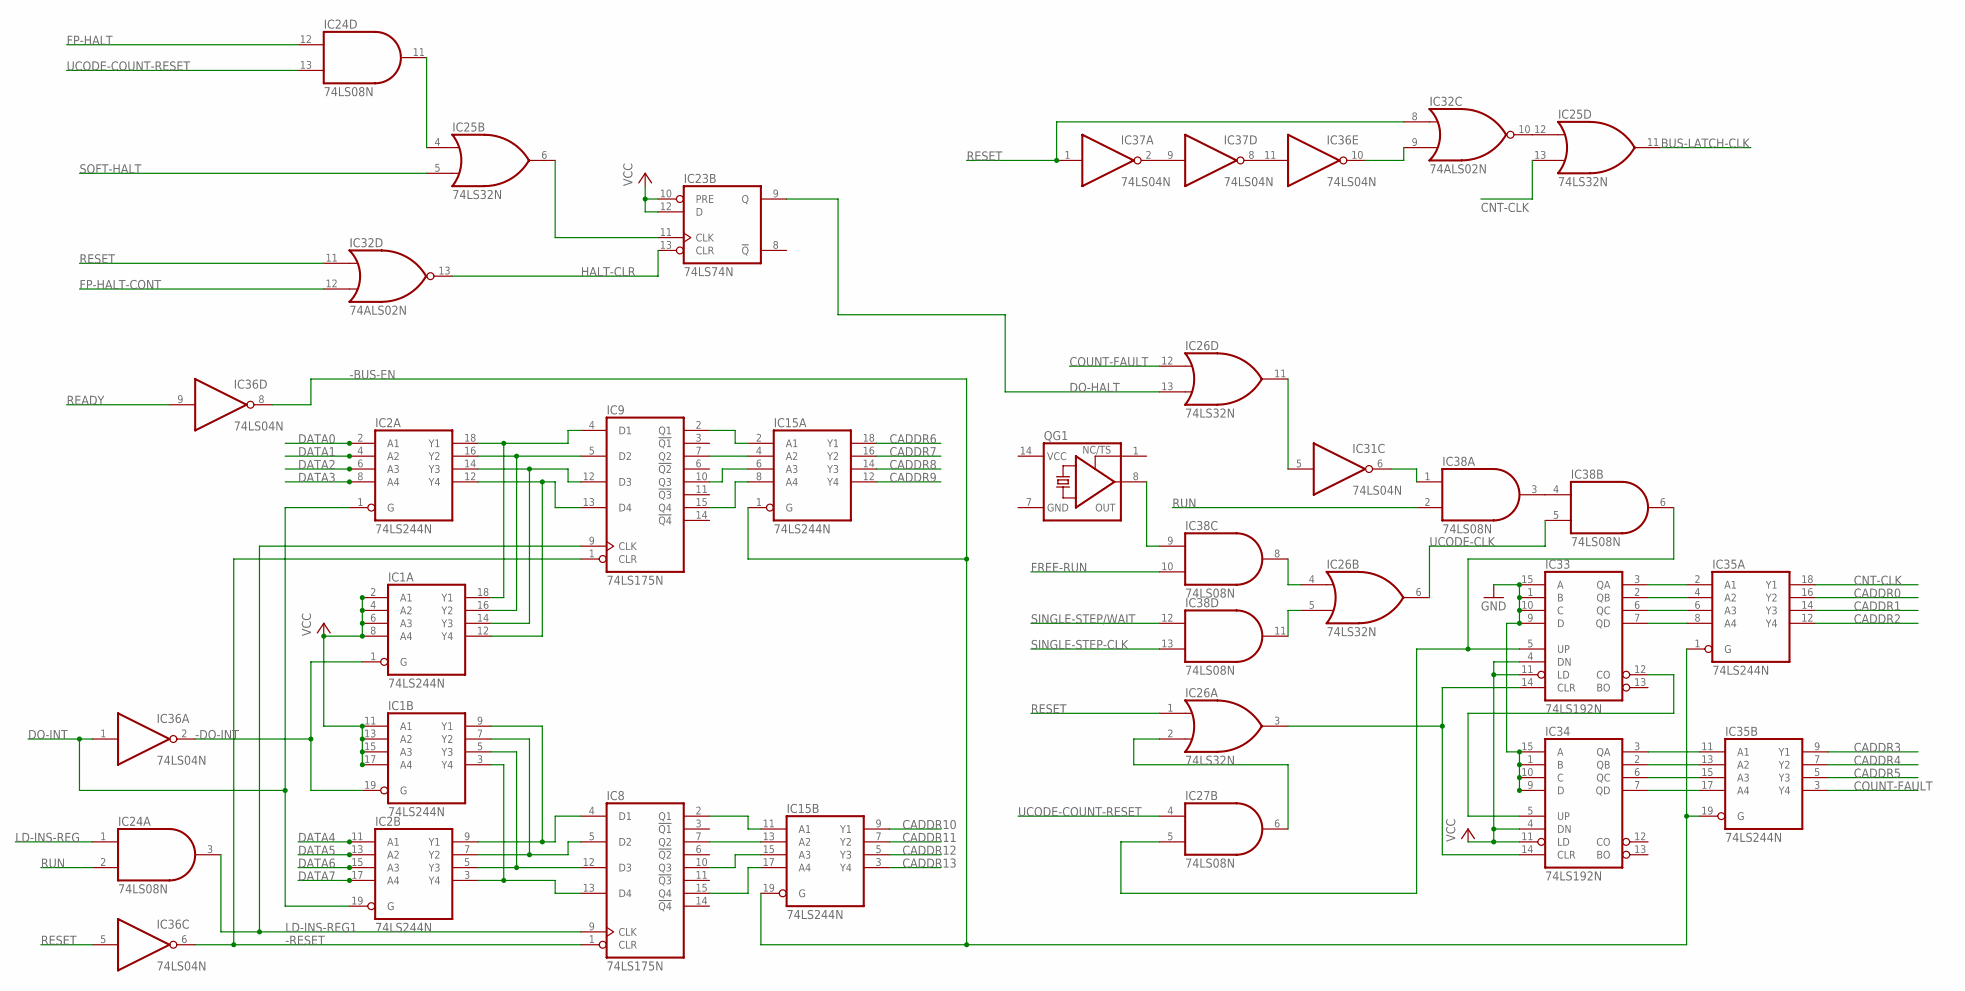
[picture p298: schematic Sequencer-Logic-Prod-V2.1l.sch, sheet 1, uCode PC Counter]

Parts:
IC1, IC2, IC15, IC35: 74LS244N; DIL20
IC8, IC9: 74LS175N; DIL16
IC23: 74LS74N; DIL14
IC24, IC27, IC38: 74LS08N; DIL14
IC25, IC26: 74LS32N; DIL14
IC31, IC36, IC37: 74LS04N; DIL14
IC32: 74ALS02N; DIL14
IC33, IC34: 74LS192N; DIL16
QG1: XO-14; DIL14S

Connections:
-BUS-EN: IC15.1 (G), IC15.19 (G), IC35.1 (G), IC35.19 (G), IC36.8 (O); also elsewhere on the board
-DO-INT: IC1.1 (G), IC1.19 (G), IC36.2 (O)
-RESET: IC8.1 (CLR), IC9.1 (CLR), IC36.6 (O); also elsewhere on the board
BUS-LATCH-CLK: IC25.11 (O); also elsewhere on the board
CADDR0: IC35.16 (Y2); also elsewhere on the board
CADDR1: IC35.14 (Y3); also elsewhere on the board
CADDR2: IC35.12 (Y4); also elsewhere on the board
CADDR3: IC35.9 (Y1); also elsewhere on the board
CADDR4: IC35.7 (Y2); also elsewhere on the board
CADDR5: IC35.5 (Y3); also elsewhere on the board
CADDR6: IC15.18 (Y1); also elsewhere on the board
CADDR7: IC15.16 (Y2); also elsewhere on the board
CADDR8: IC15.14 (Y3); also elsewhere on the board
CADDR9: IC15.12 (Y4); also elsewhere on the board
CADDR10: IC15.9 (Y1); also elsewhere on the board
CADDR11: IC15.7 (Y2); also elsewhere on the board
CADDR12: IC15.5 (Y3); also elsewhere on the board
CADDR13: IC15.3 (Y4); also elsewhere on the board
CNT-CLK: IC25.13 (I1), IC35.18 (Y1)
COUNT-FAULT: IC26.12 (I0), IC35.3 (Y4)
COUNT-RESET: IC26.3 (O), IC33.14 (CLR), IC34.14 (CLR)
DATA0: IC2.2 (A1); also elsewhere on the board
DATA1: IC2.4 (A2); also elsewhere on the board
DATA2: IC2.6 (A3); also elsewhere on the board
DATA3: IC2.8 (A4); also elsewhere on the board
DATA4: IC2.11 (A1); also elsewhere on the board
DATA5: IC2.13 (A2); also elsewhere on the board
DATA6: IC2.15 (A3); also elsewhere on the board
DATA7: IC2.17 (A4); also elsewhere on the board
DO-HALT: IC23.9 (Q), IC26.13 (I1)
DO-INT: IC2.1 (G), IC2.19 (G), IC36.1 (I); also elsewhere on the board
FP-HALT: IC24.12 (I0); also elsewhere on the board
FP-HALT-CONT: IC32.12 (I1); also elsewhere on the board
FREE-RUN: IC38.10 (I1); also elsewhere on the board
GND: IC1.10 (GND), IC2.10 (GND), IC8.8 (GND), IC9.8 (GND), IC15.10 (GND), IC23.7 (GND), IC24.7 (GND), IC25.7 (GND), IC26.7 (GND), IC27.7 (GND), IC31.7 (GND), IC32.7 (GND), IC33.1 (B), IC33.8 (GND), IC33.9 (D), IC33.10 (C), IC33.15 (A), IC34.1 (B), IC34.8 (GND), IC34.9 (D), IC34.10 (C), IC34.15 (A), IC35.10 (GND), IC36.7 (GND), IC37.7 (GND), IC38.7 (GND), QG1.7 (GND); also elsewhere on the board
HALT-CLR: IC23.13 (CLR), IC32.13 (O)
LD-INS-REG: IC24.1 (I0); also elsewhere on the board
LD-INS-REG1: IC8.9 (CLK), IC9.9 (CLK), IC24.3 (O)
unnamed: IC33.12 (CO), IC34.5 (UP)
unnamed: IC9.2 (Q1), IC15.2 (A1)
unnamed: IC9.7 (Q2), IC15.4 (A2)
unnamed: IC27.5 (I1), IC33.5 (UP), IC38.6 (O)
unnamed: IC1.18 (Y1), IC2.18 (Y1), IC9.4 (D1)
unnamed: IC1.16 (Y2), IC2.16 (Y2), IC9.5 (D2)
unnamed: IC33.3 (QA), IC35.2 (A1)
unnamed: IC33.2 (QB), IC35.4 (A2)
unnamed: IC33.6 (QC), IC35.6 (A3)
unnamed: IC9.10 (Q3), IC15.6 (A3)
unnamed: IC33.7 (QD), IC35.8 (A4)
unnamed: IC34.3 (QA), IC35.11 (A1)
unnamed: IC34.2 (QB), IC35.13 (A2)
unnamed: IC34.6 (QC), IC35.15 (A3)
unnamed: IC34.7 (QD), IC35.17 (A4)
unnamed: IC31.6 (O), IC38.1 (I0)
unnamed: IC1.14 (Y3), IC2.14 (Y3), IC9.12 (D3)
unnamed: IC1.12 (Y4), IC2.12 (Y4), IC9.13 (D4)
unnamed: IC1.9 (Y1), IC2.9 (Y1), IC8.4 (D1)
unnamed: IC1.7 (Y2), IC2.7 (Y2), IC8.5 (D2)
unnamed: IC1.5 (Y3), IC2.5 (Y3), IC8.12 (D3)
unnamed: IC1.3 (Y4), IC2.3 (Y4), IC8.13 (D4)
unnamed: IC9.15 (Q4), IC15.8 (A4)
unnamed: IC26.11 (O), IC31.5 (I)
unnamed: IC38.3 (O), IC38.4 (I0)
unnamed: IC25.12 (I0), IC32.10 (O)
unnamed: IC23.11 (CLK), IC25.6 (O)
unnamed: IC8.2 (Q1), IC15.11 (A1)
unnamed: IC8.7 (Q2), IC15.13 (A2)
unnamed: IC8.10 (Q3), IC15.15 (A3)
unnamed: IC8.15 (Q4), IC15.17 (A4)
unnamed: IC26.5 (I1), IC38.11 (O)
unnamed: IC26.4 (I0), IC38.8 (O)
unnamed: IC38.9 (I0), QG1.8 (OUT)
unnamed: IC36.11 (I), IC37.8 (O)
unnamed: IC37.2 (O), IC37.9 (I)
unnamed: IC32.9 (I1), IC36.10 (O)
unnamed: IC24.11 (O), IC25.4 (I0)
unnamed: IC26.2 (I1), IC27.6 (O)
READY: IC36.9 (I); also elsewhere on the board
RESET: IC26.1 (I0), IC32.8 (I0), IC32.11 (I0), IC36.5 (I), IC37.1 (I); also elsewhere on the board
RUN: IC24.2 (I1), IC38.2 (I1); also elsewhere on the board
SINGLE-STEP-CLK: IC38.13 (I1); also elsewhere on the board
SINGLE-STEP/WAIT: IC38.12 (I0); also elsewhere on the board
SOFT-HALT: IC25.5 (I1); also elsewhere on the board
UCODE-CLK: IC26.6 (O), IC38.5 (I1)
UCODE-COUNT-RESET: IC24.13 (I1), IC27.4 (I0); also elsewhere on the board
VCC: IC1.2 (A1), IC1.4 (A2), IC1.6 (A3), IC1.8 (A4), IC1.11 (A1), IC1.13 (A2), IC1.15 (A3), IC1.17 (A4), IC1.20 (VCC), IC2.20 (VCC), IC8.16 (VCC), IC9.16 (VCC), IC15.20 (VCC), IC23.10 (PRE), IC23.12 (D), IC23.14 (VCC), IC24.14 (VCC), IC25.14 (VCC), IC26.14 (VCC), IC27.14 (VCC), IC31.14 (VCC), IC32.14 (VCC), IC33.4 (DN), IC33.11 (LD), IC33.16 (VCC), IC34.4 (DN), IC34.11 (LD), IC34.16 (VCC), IC35.20 (VCC), IC36.14 (VCC), IC37.14 (VCC), IC38.14 (VCC), QG1.14 (VCC); also elsewhere on the board

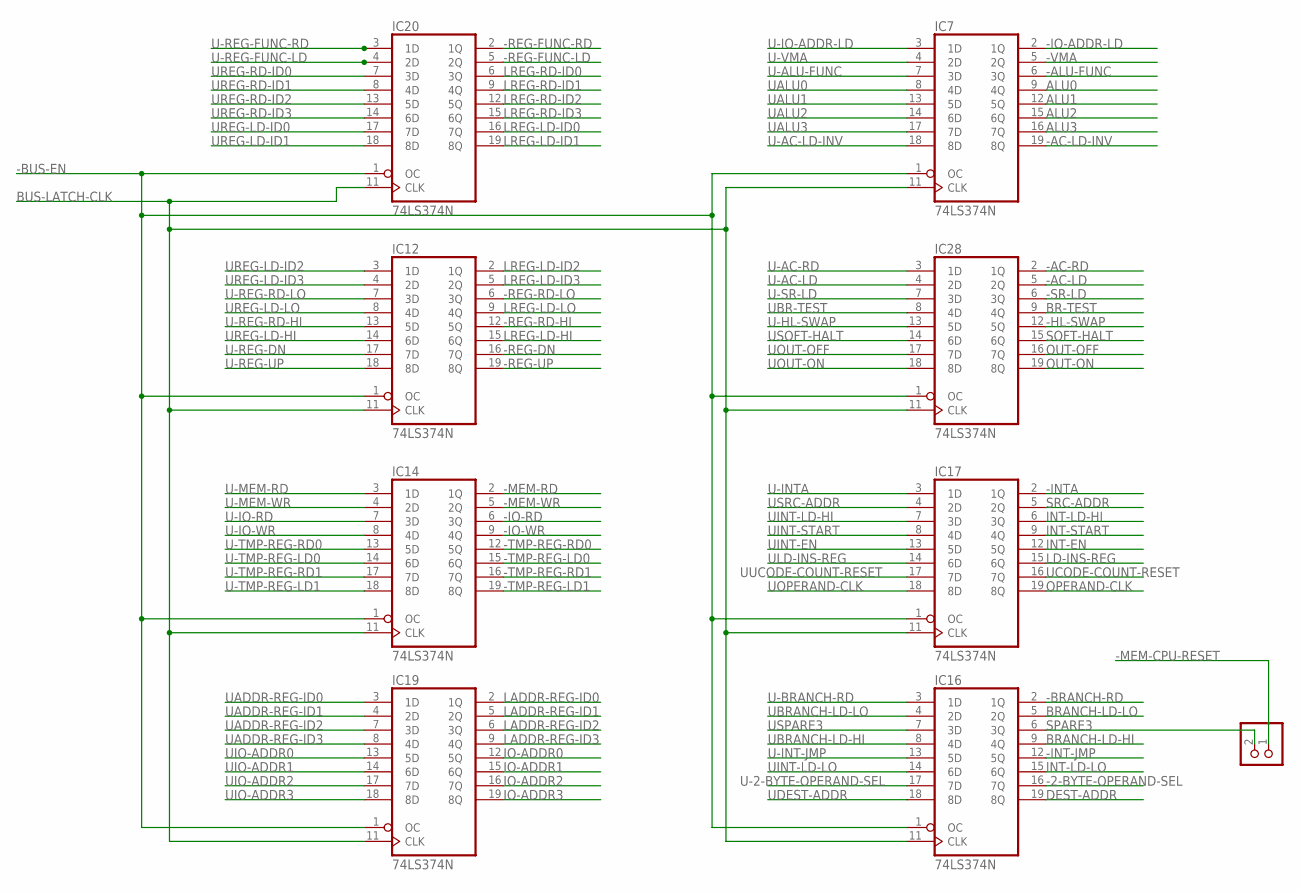
[picture p299: schematic Sequencer-Logic-Prod-V2.1l.sch, sheet 2, Latching]

Parts:
IC7, IC12, IC14, IC16, IC17, IC19, IC20, IC28: 74LS374N; DIL20
JP2: PINHD-1X2; 1X02

Connections:
-2-BYTE-OPERAND-SEL: IC16.16 (7Q); also elsewhere on the board
-AC-LD: IC28.5 (2Q); also elsewhere on the board
-AC-LD-INV: IC7.19 (8Q); also elsewhere on the board
-AC-RD: IC28.2 (1Q); also elsewhere on the board
-ALU-FUNC: IC7.6 (3Q); also elsewhere on the board
-BRANCH-RD: IC16.2 (1Q); also elsewhere on the board
-BUS-EN: IC7.1 (OC), IC12.1 (OC), IC14.1 (OC), IC16.1 (OC), IC17.1 (OC), IC19.1 (OC), IC20.1 (OC), IC28.1 (OC); also elsewhere on the board
-HL-SWAP: IC28.12 (5Q); also elsewhere on the board
-INT-JMP: IC16.12 (5Q); also elsewhere on the board
-INTA: IC17.2 (1Q); also elsewhere on the board
-IO-ADDR-LD: IC7.2 (1Q); also elsewhere on the board
-IO-RD: IC14.6 (3Q); also elsewhere on the board
-IO-WR: IC14.9 (4Q); also elsewhere on the board
-MEM-CPU-RESET: JP2.1; also elsewhere on the board
-MEM-RD: IC14.2 (1Q); also elsewhere on the board
-MEM-WR: IC14.5 (2Q); also elsewhere on the board
-REG-DN: IC12.16 (7Q); also elsewhere on the board
-REG-FUNC-LD: IC20.5 (2Q); also elsewhere on the board
-REG-FUNC-RD: IC20.2 (1Q); also elsewhere on the board
-REG-RD-HI: IC12.12 (5Q); also elsewhere on the board
-REG-RD-LO: IC12.6 (3Q); also elsewhere on the board
-REG-UP: IC12.19 (8Q); also elsewhere on the board
-SR-LD: IC28.6 (3Q); also elsewhere on the board
-TMP-REG-LD0: IC14.15 (6Q); also elsewhere on the board
-TMP-REG-LD1: IC14.19 (8Q); also elsewhere on the board
-TMP-REG-RD0: IC14.12 (5Q); also elsewhere on the board
-TMP-REG-RD1: IC14.16 (7Q); also elsewhere on the board
-VMA: IC7.5 (2Q); also elsewhere on the board
ALU0: IC7.9 (4Q); also elsewhere on the board
ALU1: IC7.12 (5Q); also elsewhere on the board
ALU2: IC7.15 (6Q); also elsewhere on the board
ALU3: IC7.16 (7Q); also elsewhere on the board
BR-TEST: IC28.9 (4Q); also elsewhere on the board
BRANCH-LD-HI: IC16.9 (4Q); also elsewhere on the board
BRANCH-LD-LO: IC16.5 (2Q); also elsewhere on the board
BUS-LATCH-CLK: IC7.11 (CLK), IC12.11 (CLK), IC14.11 (CLK), IC16.11 (CLK), IC17.11 (CLK), IC19.11 (CLK), IC20.11 (CLK), IC28.11 (CLK); also elsewhere on the board
DEST-ADDR: IC16.19 (8Q); also elsewhere on the board
GND: IC7.10 (GND), IC12.10 (GND), IC14.10 (GND), IC16.10 (GND), IC17.10 (GND), IC19.10 (GND), IC20.10 (GND), IC28.10 (GND); also elsewhere on the board
INT-EN: IC17.12 (5Q); also elsewhere on the board
INT-LD-HI: IC17.6 (3Q); also elsewhere on the board
INT-LD-LO: IC16.15 (6Q); also elsewhere on the board
INT-START: IC17.9 (4Q); also elsewhere on the board
IO-ADDR0: IC19.12 (5Q); also elsewhere on the board
IO-ADDR1: IC19.15 (6Q); also elsewhere on the board
IO-ADDR2: IC19.16 (7Q); also elsewhere on the board
IO-ADDR3: IC19.19 (8Q); also elsewhere on the board
LADDR-REG-ID0: IC19.2 (1Q); also elsewhere on the board
LADDR-REG-ID1: IC19.5 (2Q); also elsewhere on the board
LADDR-REG-ID2: IC19.6 (3Q); also elsewhere on the board
LADDR-REG-ID3: IC19.9 (4Q); also elsewhere on the board
LD-INS-REG: IC17.15 (6Q); also elsewhere on the board
LREG-LD-HI: IC12.15 (6Q); also elsewhere on the board
LREG-LD-ID0: IC20.16 (7Q); also elsewhere on the board
LREG-LD-ID1: IC20.19 (8Q); also elsewhere on the board
LREG-LD-ID2: IC12.2 (1Q); also elsewhere on the board
LREG-LD-ID3: IC12.5 (2Q); also elsewhere on the board
LREG-LD-LO: IC12.9 (4Q); also elsewhere on the board
LREG-RD-ID0: IC20.6 (3Q); also elsewhere on the board
LREG-RD-ID1: IC20.9 (4Q); also elsewhere on the board
LREG-RD-ID2: IC20.12 (5Q); also elsewhere on the board
LREG-RD-ID3: IC20.15 (6Q); also elsewhere on the board
OPERAND-CLK: IC17.19 (8Q); also elsewhere on the board
OUT-OFF: IC28.16 (7Q); also elsewhere on the board
OUT-ON: IC28.19 (8Q); also elsewhere on the board
SOFT-HALT: IC28.15 (6Q); also elsewhere on the board
SPARE3: IC16.6 (3Q), JP2.2
SRC-ADDR: IC17.5 (2Q); also elsewhere on the board
U-2-BYTE-OPERAND-SEL: IC16.17 (7D); also elsewhere on the board
U-AC-LD: IC28.4 (2D); also elsewhere on the board
U-AC-LD-INV: IC7.18 (8D); also elsewhere on the board
U-AC-RD: IC28.3 (1D); also elsewhere on the board
U-ALU-FUNC: IC7.7 (3D); also elsewhere on the board
U-BRANCH-RD: IC16.3 (1D); also elsewhere on the board
U-HL-SWAP: IC28.13 (5D); also elsewhere on the board
U-INT-JMP: IC16.13 (5D); also elsewhere on the board
U-INTA: IC17.3 (1D); also elsewhere on the board
U-IO-ADDR-LD: IC7.3 (1D); also elsewhere on the board
U-IO-RD: IC14.7 (3D); also elsewhere on the board
U-IO-WR: IC14.8 (4D); also elsewhere on the board
U-MEM-RD: IC14.3 (1D); also elsewhere on the board
U-MEM-WR: IC14.4 (2D); also elsewhere on the board
U-REG-DN: IC12.17 (7D); also elsewhere on the board
U-REG-FUNC-LD: IC20.4 (2D); also elsewhere on the board
U-REG-FUNC-RD: IC20.3 (1D); also elsewhere on the board
U-REG-RD-HI: IC12.13 (5D); also elsewhere on the board
U-REG-RD-LO: IC12.7 (3D); also elsewhere on the board
U-REG-UP: IC12.18 (8D); also elsewhere on the board
U-SR-LD: IC28.7 (3D); also elsewhere on the board
U-TMP-REG-LD0: IC14.14 (6D); also elsewhere on the board
U-TMP-REG-LD1: IC14.18 (8D); also elsewhere on the board
U-TMP-REG-RD0: IC14.13 (5D); also elsewhere on the board
U-TMP-REG-RD1: IC14.17 (7D); also elsewhere on the board
U-VMA: IC7.4 (2D); also elsewhere on the board
UADDR-REG-ID0: IC19.3 (1D); also elsewhere on the board
UADDR-REG-ID1: IC19.4 (2D); also elsewhere on the board
UADDR-REG-ID2: IC19.7 (3D); also elsewhere on the board
UADDR-REG-ID3: IC19.8 (4D); also elsewhere on the board
UALU0: IC7.8 (4D); also elsewhere on the board
UALU1: IC7.13 (5D); also elsewhere on the board
UALU2: IC7.14 (6D); also elsewhere on the board
UALU3: IC7.17 (7D); also elsewhere on the board
UBR-TEST: IC28.8 (4D); also elsewhere on the board
UBRANCH-LD-HI: IC16.8 (4D); also elsewhere on the board
UBRANCH-LD-LO: IC16.4 (2D); also elsewhere on the board
UCODE-COUNT-RESET: IC17.16 (7Q); also elsewhere on the board
UDEST-ADDR: IC16.18 (8D); also elsewhere on the board
UINT-EN: IC17.13 (5D); also elsewhere on the board
UINT-LD-HI: IC17.7 (3D); also elsewhere on the board
UINT-LD-LO: IC16.14 (6D); also elsewhere on the board
UINT-START: IC17.8 (4D); also elsewhere on the board
UIO-ADDR0: IC19.13 (5D); also elsewhere on the board
UIO-ADDR1: IC19.14 (6D); also elsewhere on the board
UIO-ADDR2: IC19.17 (7D); also elsewhere on the board
UIO-ADDR3: IC19.18 (8D); also elsewhere on the board
ULD-INS-REG: IC17.14 (6D); also elsewhere on the board
UOPERAND-CLK: IC17.18 (8D); also elsewhere on the board
UOUT-OFF: IC28.17 (7D); also elsewhere on the board
UOUT-ON: IC28.18 (8D); also elsewhere on the board
UREG-LD-HI: IC12.14 (6D); also elsewhere on the board
UREG-LD-ID0: IC20.17 (7D); also elsewhere on the board
UREG-LD-ID1: IC20.18 (8D); also elsewhere on the board
UREG-LD-ID2: IC12.3 (1D); also elsewhere on the board
UREG-LD-ID3: IC12.4 (2D); also elsewhere on the board
UREG-LD-LO: IC12.8 (4D); also elsewhere on the board
UREG-RD-ID0: IC20.7 (3D); also elsewhere on the board
UREG-RD-ID1: IC20.8 (4D); also elsewhere on the board
UREG-RD-ID2: IC20.13 (5D); also elsewhere on the board
UREG-RD-ID3: IC20.14 (6D); also elsewhere on the board
USOFT-HALT: IC28.14 (6D); also elsewhere on the board
USPARE3: IC16.7 (3D); also elsewhere on the board
USRC-ADDR: IC17.4 (2D); also elsewhere on the board
UUCODE-COUNT-RESET: IC17.17 (7D); also elsewhere on the board
VCC: IC7.20 (VCC), IC12.20 (VCC), IC14.20 (VCC), IC16.20 (VCC), IC17.20 (VCC), IC19.20 (VCC), IC20.20 (VCC), IC28.20 (VCC); also elsewhere on the board
