ksr/YACC1-D/hardware/cards/sequencer-logic/eagle/v2.1/Sequencer-Logic-Prod-V2.1l.brd

## EAGLE design hardware/cards/sequencer-logic/eagle/v2.1/Sequencer-Logic-Prod-V2.1l.brd (continued)

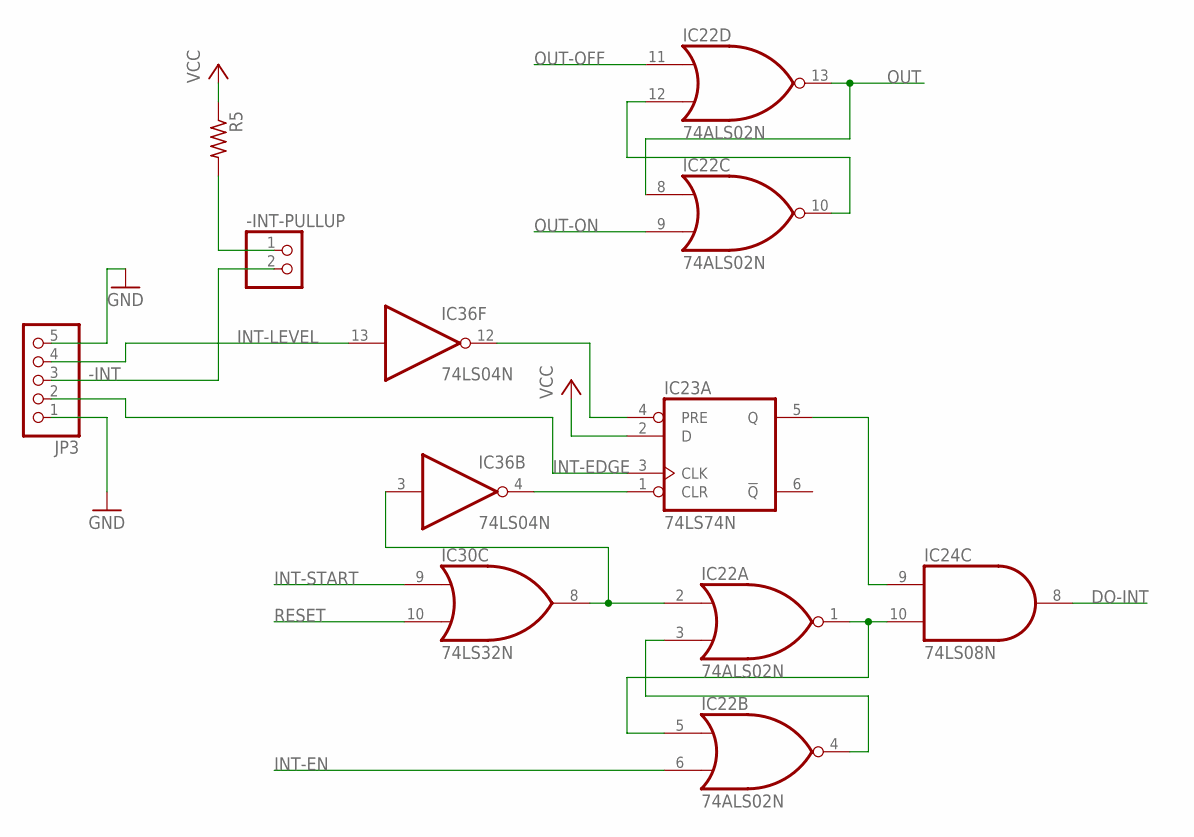
[picture p300: schematic Sequencer-Logic-Prod-V2.1l.sch, sheet 3, Interrupt Mgmt]

Parts:
-INT-PULLUP: PINHD-1X2; 1X02
IC22: 74ALS02N; DIL14
IC23: 74LS74N; DIL14
IC24: 74LS08N; DIL14
IC30: 74LS32N; DIL14
IC36: 74LS04N; DIL14
JP3: PINHD-1X5; 1X05
R5: 10k; 0207/10

Connections:
-INT: -INT-PULLUP.2, JP3.3; also elsewhere on the board
DO-INT: IC24.8 (O); also elsewhere on the board
GND: IC22.7 (GND), IC23.7 (GND), IC24.7 (GND), IC30.7 (GND), IC36.7 (GND), JP3.1, JP3.5; also elsewhere on the board
INT-EDGE: IC23.3 (CLK), JP3.2
INT-EN: IC22.6 (I1); also elsewhere on the board
INT-LEVEL: IC36.13 (I), JP3.4
INT-START: IC30.9 (I0); also elsewhere on the board
unnamed: IC22.1 (O), IC22.5 (I0), IC24.10 (I1)
unnamed: IC22.3 (I1), IC22.4 (O)
unnamed: IC22.2 (I0), IC30.8 (O), IC36.3 (I)
unnamed: IC23.5 (Q), IC24.9 (I0)
unnamed: IC23.1 (CLR), IC36.4 (O)
unnamed: IC23.4 (PRE), IC36.12 (O)
unnamed: IC22.10 (O), IC22.12 (I1)
unnamed: -INT-PULLUP.1, R5.2
OUT: IC22.8 (I0), IC22.13 (O); also elsewhere on the board
OUT-OFF: IC22.11 (I0); also elsewhere on the board
OUT-ON: IC22.9 (I1); also elsewhere on the board
RESET: IC30.10 (I1); also elsewhere on the board
VCC: IC22.14 (VCC), IC23.2 (D), IC23.14 (VCC), IC24.14 (VCC), IC30.14 (VCC), IC36.14 (VCC), R5.1; also elsewhere on the board

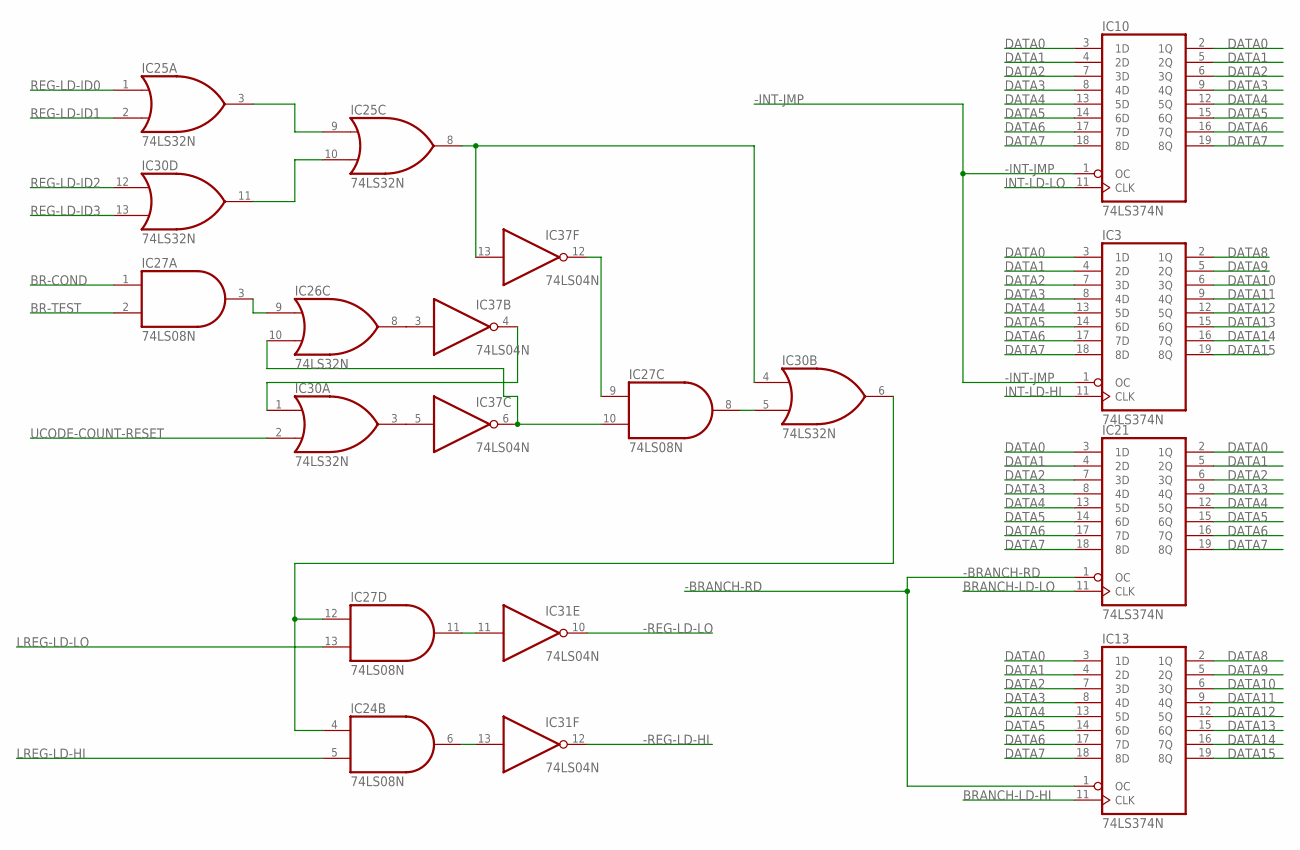
[picture p301: schematic Sequencer-Logic-Prod-V2.1l.sch, sheet 4, Branch Mgmt]

Parts:
IC3, IC10, IC13, IC21: 74LS374N; DIL20
IC24, IC27: 74LS08N; DIL14
IC25, IC26, IC30: 74LS32N; DIL14
IC31, IC37: 74LS04N; DIL14

Connections:
-BRANCH-RD: IC13.1 (OC), IC21.1 (OC); also elsewhere on the board
-INT-JMP: IC3.1 (OC), IC10.1 (OC); also elsewhere on the board
-REG-LD-HI: IC31.12 (O); also elsewhere on the board
-REG-LD-LO: IC31.10 (O); also elsewhere on the board
BR-COND: IC27.1 (I0); also elsewhere on the board
BR-TEST: IC27.2 (I1); also elsewhere on the board
BRANCH-LD-HI: IC13.11 (CLK); also elsewhere on the board
BRANCH-LD-LO: IC21.11 (CLK); also elsewhere on the board
DATA0: IC3.3 (1D), IC10.2 (1Q), IC10.3 (1D), IC13.3 (1D), IC21.2 (1Q), IC21.3 (1D); also elsewhere on the board
DATA1: IC3.4 (2D), IC10.4 (2D), IC10.5 (2Q), IC13.4 (2D), IC21.4 (2D), IC21.5 (2Q); also elsewhere on the board
DATA2: IC3.7 (3D), IC10.6 (3Q), IC10.7 (3D), IC13.7 (3D), IC21.6 (3Q), IC21.7 (3D); also elsewhere on the board
DATA3: IC3.8 (4D), IC10.8 (4D), IC10.9 (4Q), IC13.8 (4D), IC21.8 (4D), IC21.9 (4Q); also elsewhere on the board
DATA4: IC3.13 (5D), IC10.12 (5Q), IC10.13 (5D), IC13.13 (5D), IC21.12 (5Q), IC21.13 (5D); also elsewhere on the board
DATA5: IC3.14 (6D), IC10.14 (6D), IC10.15 (6Q), IC13.14 (6D), IC21.14 (6D), IC21.15 (6Q); also elsewhere on the board
DATA6: IC3.17 (7D), IC10.16 (7Q), IC10.17 (7D), IC13.17 (7D), IC21.16 (7Q), IC21.17 (7D); also elsewhere on the board
DATA7: IC3.18 (8D), IC10.18 (8D), IC10.19 (8Q), IC13.18 (8D), IC21.18 (8D), IC21.19 (8Q); also elsewhere on the board
DATA8: IC3.2 (1Q), IC13.2 (1Q); also elsewhere on the board
DATA9: IC3.5 (2Q), IC13.5 (2Q); also elsewhere on the board
DATA10: IC3.6 (3Q), IC13.6 (3Q); also elsewhere on the board
DATA11: IC3.9 (4Q), IC13.9 (4Q); also elsewhere on the board
DATA12: IC3.12 (5Q), IC13.12 (5Q); also elsewhere on the board
DATA13: IC3.15 (6Q), IC13.15 (6Q); also elsewhere on the board
DATA14: IC3.16 (7Q), IC13.16 (7Q); also elsewhere on the board
DATA15: IC3.19 (8Q), IC13.19 (8Q); also elsewhere on the board
GND: IC3.10 (GND), IC10.10 (GND), IC13.10 (GND), IC21.10 (GND), IC24.7 (GND), IC25.7 (GND), IC26.7 (GND), IC27.7 (GND), IC30.7 (GND), IC31.7 (GND), IC37.7 (GND); also elsewhere on the board
INT-LD-HI: IC3.11 (CLK); also elsewhere on the board
INT-LD-LO: IC10.11 (CLK); also elsewhere on the board
LREG-LD-HI: IC24.5 (I1); also elsewhere on the board
LREG-LD-LO: IC27.13 (I1); also elsewhere on the board
unnamed: IC25.3 (O), IC25.9 (I0)
unnamed: IC25.10 (I1), IC30.11 (O)
unnamed: IC27.9 (I0), IC37.12 (O)
unnamed: IC27.8 (O), IC30.5 (I1)
unnamed: IC24.4 (I0), IC27.12 (I0), IC30.6 (O)
unnamed: IC25.8 (O), IC30.4 (I0), IC37.13 (I)
unnamed: IC27.11 (O), IC31.11 (I)
unnamed: IC24.6 (O), IC31.13 (I)
unnamed: IC26.8 (O), IC37.3 (I)
unnamed: IC30.3 (O), IC37.5 (I)
unnamed: IC30.1 (I0), IC37.4 (O)
unnamed: IC26.10 (I1), IC27.10 (I1), IC37.6 (O)
unnamed: IC26.9 (I0), IC27.3 (O)
REG-LD-ID0: IC25.1 (I0); also elsewhere on the board
REG-LD-ID1: IC25.2 (I1); also elsewhere on the board
REG-LD-ID2: IC30.12 (I0); also elsewhere on the board
REG-LD-ID3: IC30.13 (I1); also elsewhere on the board
UCODE-COUNT-RESET: IC30.2 (I1); also elsewhere on the board
VCC: IC3.20 (VCC), IC10.20 (VCC), IC13.20 (VCC), IC21.20 (VCC), IC24.14 (VCC), IC25.14 (VCC), IC26.14 (VCC), IC27.14 (VCC), IC30.14 (VCC), IC31.14 (VCC), IC37.14 (VCC); also elsewhere on the board

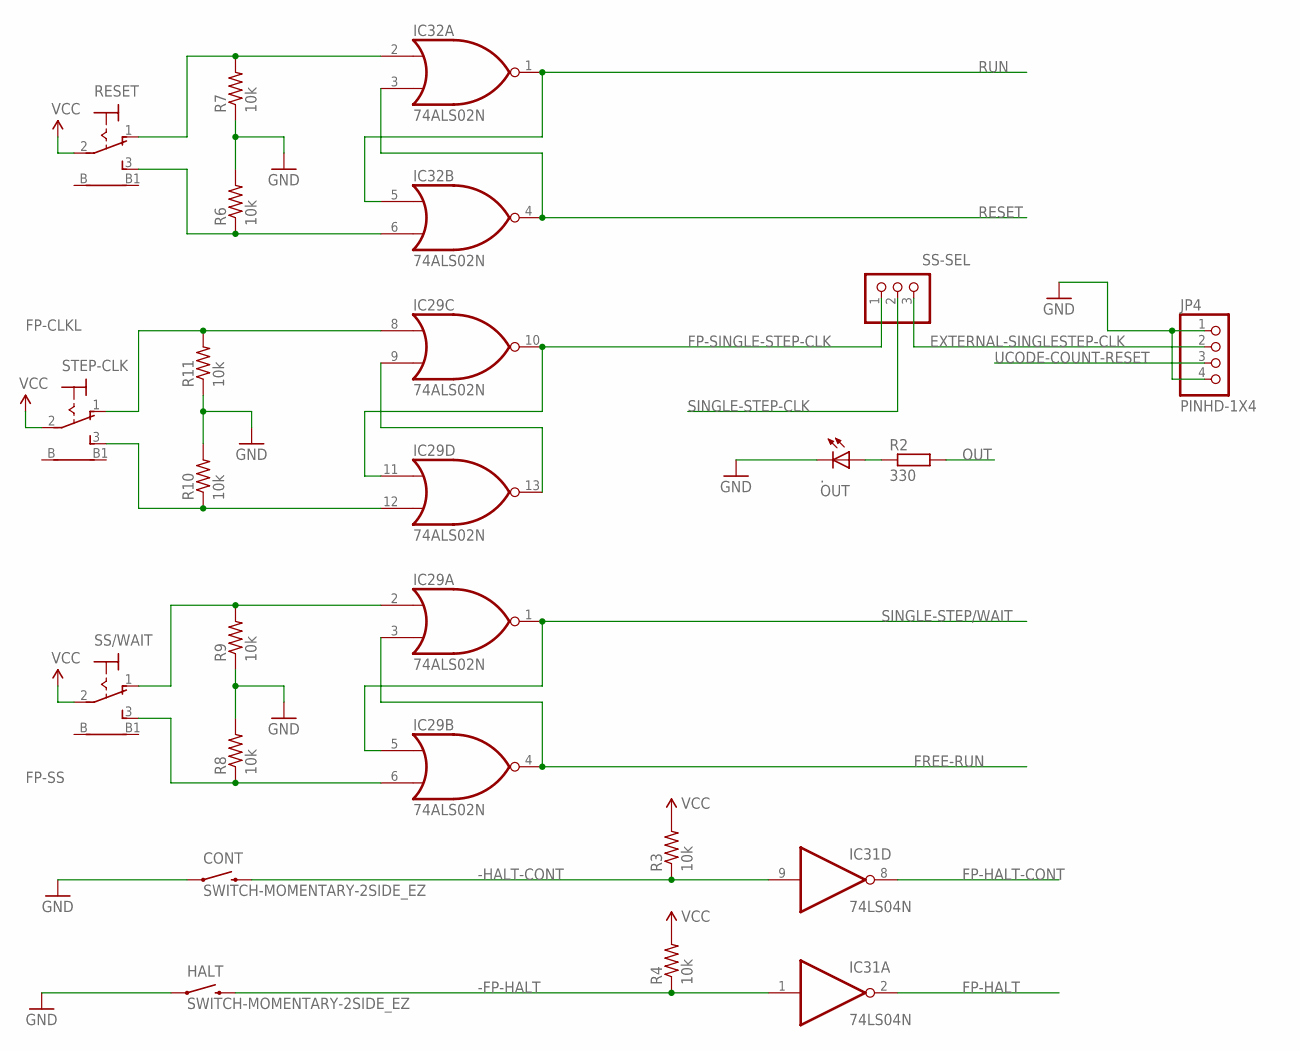
[picture p302: schematic Sequencer-Logic-Prod-V2.1l.sch, sheet 5, CONTROL INTERFACE]

Parts:
.: OUT; LED5MM
CONT: SWITCH-MOMENTARY-2SIDE_EZ; TACTILE-PTH-SIDEEZ
HALT: SWITCH-MOMENTARY-2SIDE_EZ; TACTILE-PTH-SIDEEZ
IC29, IC32: 74ALS02N; DIL14
IC31: 74LS04N; DIL14
JP4: PINHD-1X4; 1X04
R2: 330; 0207/10
R3, R4, R6, R7, R8, R9, R10, R11: 10k; 0207/10
RESET: 9070-1W
SS-SEL: PINHD-1X3; 1X03
SS/WAIT: 9070-1W
STEP-CLK: 9070-1W

Connections:
-FP-HALT: HALT.2, IC31.1 (I), R4.1
-HALT-CONT: CONT.2, IC31.9 (I), R3.1
EXTERNAL-SINGLESTEP-CLK: JP4.2, SS-SEL.3
FP-CLKH: IC29.12 (I1), R10.1, STEP-CLK.3 (S)
FP-CLKL: IC29.8 (I0), R11.2, STEP-CLK.1 (O)
FP-EXECUTE: IC32.6 (I1), R6.1, RESET.3 (S)
FP-FREERUN: IC29.2 (I0), R9.2, SS/WAIT.1 (O)
FP-HALT: IC31.2 (O); also elsewhere on the board
FP-HALT-CONT: IC31.8 (O); also elsewhere on the board
FP-RESET: IC32.2 (I0), R7.2, RESET.1 (O)
FP-SINGLE-STEP-CLK: IC29.10 (O), IC29.11 (I0), SS-SEL.1
FP-SS: IC29.6 (I1), R8.1, SS/WAIT.3 (S)
FREE-RUN: IC29.3 (I1), IC29.4 (O); also elsewhere on the board
GND: ..K (C), CONT.1, HALT.1, IC29.7 (GND), IC31.7 (GND), IC32.7 (GND), JP4.1, JP4.4, R6.2, R7.1, R8.2, R9.1, R10.2, R11.1; also elsewhere on the board
HARD-RESET1: IC29.9 (I1), IC29.13 (O)
unnamed: ..A, R2.1
OUT: R2.2; also elsewhere on the board
RESET: IC32.3 (I1), IC32.4 (O); also elsewhere on the board
RUN: IC32.1 (O), IC32.5 (I0); also elsewhere on the board
SINGLE-STEP-CLK: SS-SEL.2; also elsewhere on the board
SINGLE-STEP/WAIT: IC29.1 (O), IC29.5 (I0); also elsewhere on the board
UCODE-COUNT-RESET: JP4.3; also elsewhere on the board
VCC: IC29.14 (VCC), IC31.14 (VCC), IC32.14 (VCC), R3.2, R4.2, RESET.2, SS/WAIT.2, STEP-CLK.2; also elsewhere on the board

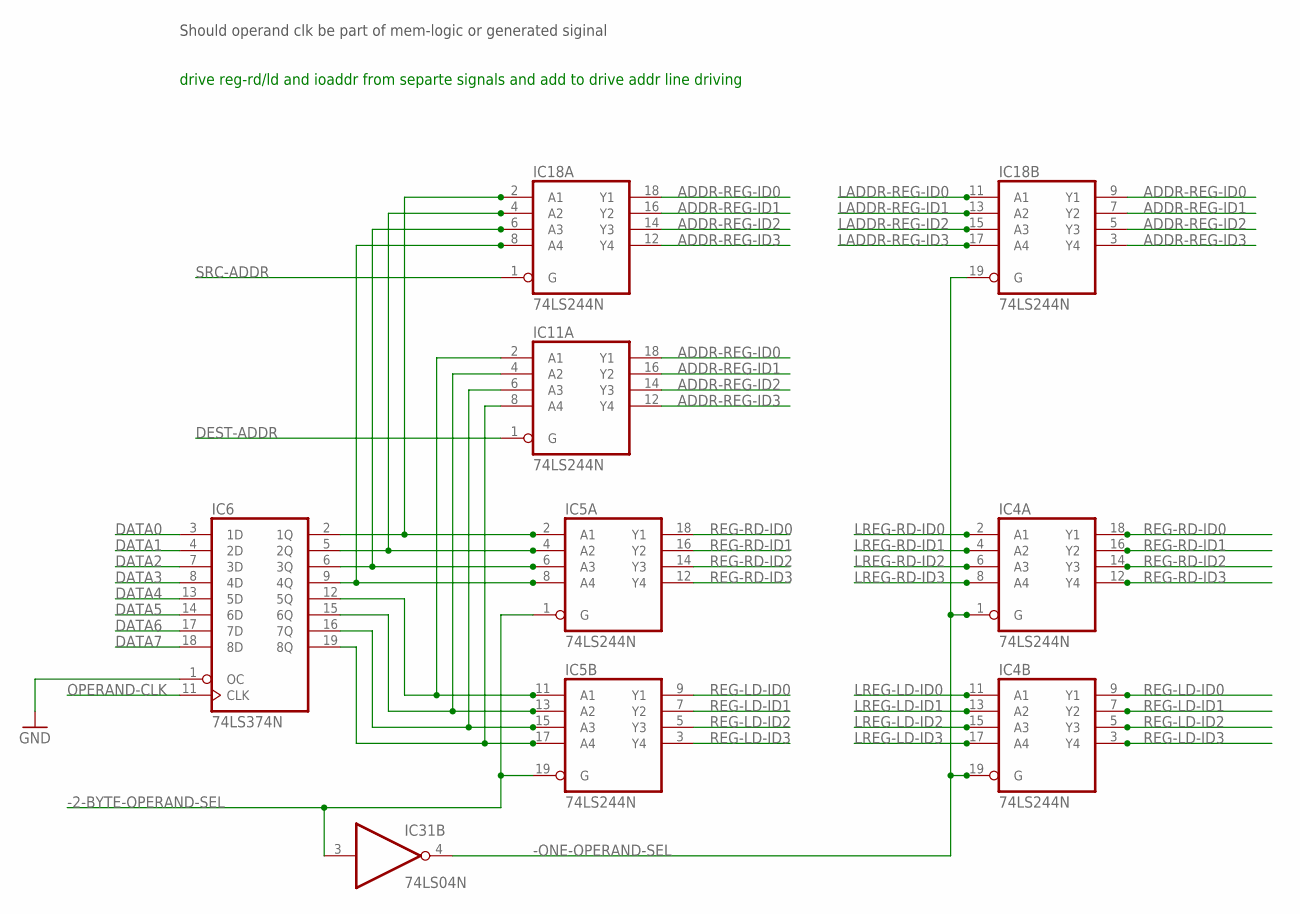
[picture p303: schematic Sequencer-Logic-Prod-V2.1l.sch, sheet 6, OPERAND REGISTER MGMT]

Parts:
IC4, IC5, IC11, IC18: 74LS244N; DIL20
IC6: 74LS374N; DIL20
IC31: 74LS04N; DIL14

Connections:
-2-BYTE-OPERAND-SEL: IC5.1 (G), IC5.19 (G), IC31.3 (I); also elsewhere on the board
-ONE-OPERAND-SEL: IC4.1 (G), IC4.19 (G), IC18.19 (G), IC31.4 (O)
ADDR-REG-ID0: IC11.18 (Y1), IC18.9 (Y1), IC18.18 (Y1); also elsewhere on the board
ADDR-REG-ID1: IC11.16 (Y2), IC18.7 (Y2), IC18.16 (Y2); also elsewhere on the board
ADDR-REG-ID2: IC11.14 (Y3), IC18.5 (Y3), IC18.14 (Y3); also elsewhere on the board
ADDR-REG-ID3: IC11.12 (Y4), IC18.3 (Y4), IC18.12 (Y4); also elsewhere on the board
DATA0: IC6.3 (1D); also elsewhere on the board
DATA1: IC6.4 (2D); also elsewhere on the board
DATA2: IC6.7 (3D); also elsewhere on the board
DATA3: IC6.8 (4D); also elsewhere on the board
DATA4: IC6.13 (5D); also elsewhere on the board
DATA5: IC6.14 (6D); also elsewhere on the board
DATA6: IC6.17 (7D); also elsewhere on the board
DATA7: IC6.18 (8D); also elsewhere on the board
DEST-ADDR: IC11.1 (G); also elsewhere on the board
GND: IC4.10 (GND), IC5.10 (GND), IC6.1 (OC), IC6.10 (GND), IC11.10 (GND), IC18.10 (GND), IC31.7 (GND); also elsewhere on the board
LADDR-REG-ID0: IC18.11 (A1); also elsewhere on the board
LADDR-REG-ID1: IC18.13 (A2); also elsewhere on the board
LADDR-REG-ID2: IC18.15 (A3); also elsewhere on the board
LADDR-REG-ID3: IC18.17 (A4); also elsewhere on the board
LREG-LD-ID0: IC4.11 (A1); also elsewhere on the board
LREG-LD-ID1: IC4.13 (A2); also elsewhere on the board
LREG-LD-ID2: IC4.15 (A3); also elsewhere on the board
LREG-LD-ID3: IC4.17 (A4); also elsewhere on the board
LREG-RD-ID0: IC4.2 (A1); also elsewhere on the board
LREG-RD-ID1: IC4.4 (A2); also elsewhere on the board
LREG-RD-ID2: IC4.6 (A3); also elsewhere on the board
LREG-RD-ID3: IC4.8 (A4); also elsewhere on the board
unnamed: IC5.17 (A4), IC6.19 (8Q), IC11.8 (A4)
unnamed: IC5.2 (A1), IC6.2 (1Q), IC18.2 (A1)
unnamed: IC5.4 (A2), IC6.5 (2Q), IC18.4 (A2)
unnamed: IC5.6 (A3), IC6.6 (3Q), IC18.6 (A3)
unnamed: IC5.8 (A4), IC6.9 (4Q), IC18.8 (A4)
unnamed: IC5.11 (A1), IC6.12 (5Q), IC11.2 (A1)
unnamed: IC5.13 (A2), IC6.15 (6Q), IC11.4 (A2)
unnamed: IC5.15 (A3), IC6.16 (7Q), IC11.6 (A3)
OPERAND-CLK: IC6.11 (CLK); also elsewhere on the board
REG-LD-ID0: IC4.9 (Y1), IC5.9 (Y1); also elsewhere on the board
REG-LD-ID1: IC4.7 (Y2), IC5.7 (Y2); also elsewhere on the board
REG-LD-ID2: IC4.5 (Y3), IC5.5 (Y3); also elsewhere on the board
REG-LD-ID3: IC4.3 (Y4), IC5.3 (Y4); also elsewhere on the board
REG-RD-ID0: IC4.18 (Y1), IC5.18 (Y1); also elsewhere on the board
REG-RD-ID1: IC4.16 (Y2), IC5.16 (Y2); also elsewhere on the board
REG-RD-ID2: IC4.14 (Y3), IC5.14 (Y3); also elsewhere on the board
REG-RD-ID3: IC4.12 (Y4), IC5.12 (Y4); also elsewhere on the board
SRC-ADDR: IC18.1 (G); also elsewhere on the board
VCC: IC4.20 (VCC), IC5.20 (VCC), IC6.20 (VCC), IC11.20 (VCC), IC18.20 (VCC), IC31.14 (VCC); also elsewhere on the board

Notes on the sheet:
Should operand clk be part of mem-logic or generated siginal
drive reg-rd/ld and ioaddr from separte signals and add to drive addr line driving

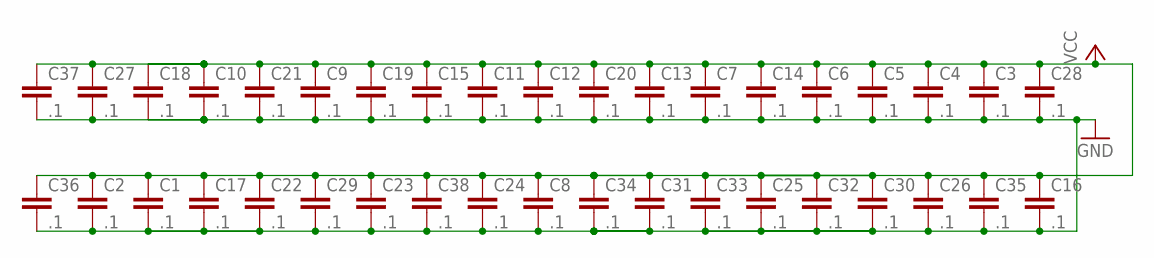
[picture p304: schematic Sequencer-Logic-Prod-V2.1l.sch, sheet 7, BYPASS and UNUSED]

Parts:
C1, C2, C3, C4, C5, C6, C7, C8, C9, C10, C11, C12, C13, C14, C15, C16, C17, C18, C19, C20, C21, C22, C23, C24, C25, C26, C27, C28, C29, C30, C31, C32, C33, C34, C35, C36, C37, C38: .1; CAP-PTH-SMALLEZ

Connections:
GND: C1.2, C2.2, C3.2, C4.2, C5.2, C6.2, C7.2, C8.2, C9.2, C10.2, C11.2, C12.2, C13.2, C14.2, C15.2, C16.2, C17.2, C18.2, C19.2, C20.2, C21.2, C22.2, C23.2, C24.2, C25.2, C26.2, C27.2, C28.2, C29.2, C30.2, C31.2, C32.2, C33.2, C34.2, C35.2, C36.2, C37.2, C38.2; also elsewhere on the board
VCC: C1.1, C2.1, C3.1, C4.1, C5.1, C6.1, C7.1, C8.1, C9.1, C10.1, C11.1, C12.1, C13.1, C14.1, C15.1, C16.1, C17.1, C18.1, C19.1, C20.1, C21.1, C22.1, C23.1, C24.1, C25.1, C26.1, C27.1, C28.1, C29.1, C30.1, C31.1, C32.1, C33.1, C34.1, C35.1, C36.1, C37.1, C38.1; also elsewhere on the board

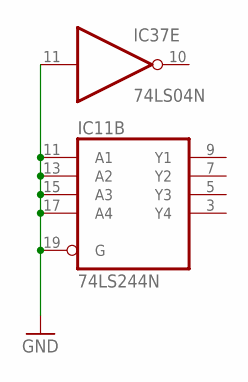
[picture p305: schematic Sequencer-Logic-Prod-V2.1l.sch, sheet 8, BUS]

Parts:
IC11: 74LS244N; DIL20
IC37: 74LS04N; DIL14

Connections:
GND: IC11.10 (GND), IC11.11 (A1), IC11.13 (A2), IC11.15 (A3), IC11.17 (A4), IC11.19 (G), IC37.7 (GND), IC37.11 (I); also elsewhere on the board
VCC: IC11.20 (VCC), IC37.14 (VCC); also elsewhere on the board

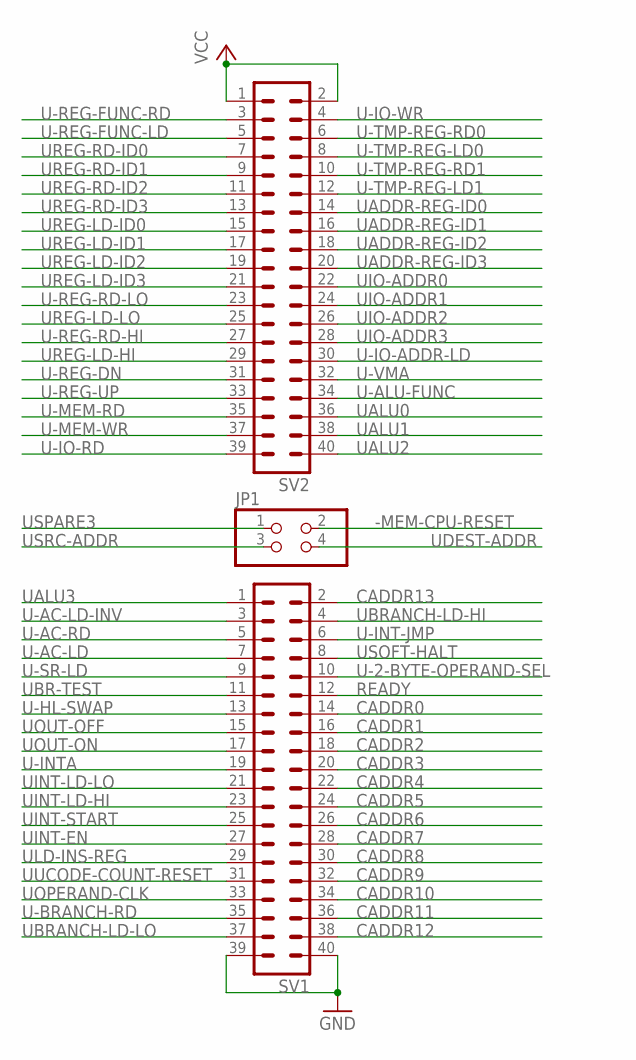
[picture p306: schematic Sequencer-Logic-Prod-V2.1l.sch, sheet 9]

Parts:
JP1: PINHD-2X2; 2X02
SV1, SV2: MA20-2

Connections:
-MEM-CPU-RESET: JP1.2; also elsewhere on the board
CADDR0: SV1.14; also elsewhere on the board
CADDR1: SV1.16; also elsewhere on the board
CADDR2: SV1.18; also elsewhere on the board
CADDR3: SV1.20; also elsewhere on the board
CADDR4: SV1.22; also elsewhere on the board
CADDR5: SV1.24; also elsewhere on the board
CADDR6: SV1.26; also elsewhere on the board
CADDR7: SV1.28; also elsewhere on the board
CADDR8: SV1.30; also elsewhere on the board
CADDR9: SV1.32; also elsewhere on the board
CADDR10: SV1.34; also elsewhere on the board
CADDR11: SV1.36; also elsewhere on the board
CADDR12: SV1.38; also elsewhere on the board
CADDR13: SV1.2; also elsewhere on the board
GND: SV1.39, SV1.40; also elsewhere on the board
READY: SV1.12; also elsewhere on the board
U-2-BYTE-OPERAND-SEL: SV1.10; also elsewhere on the board
U-AC-LD: SV1.7; also elsewhere on the board
U-AC-LD-INV: SV1.3; also elsewhere on the board
U-AC-RD: SV1.5; also elsewhere on the board
U-ALU-FUNC: SV2.34; also elsewhere on the board
U-BRANCH-RD: SV1.35; also elsewhere on the board
U-HL-SWAP: SV1.13; also elsewhere on the board
U-INT-JMP: SV1.6; also elsewhere on the board
U-INTA: SV1.19; also elsewhere on the board
U-IO-ADDR-LD: SV2.30; also elsewhere on the board
U-IO-RD: SV2.39; also elsewhere on the board
U-IO-WR: SV2.4; also elsewhere on the board
U-MEM-RD: SV2.35; also elsewhere on the board
U-MEM-WR: SV2.37; also elsewhere on the board
U-REG-DN: SV2.31; also elsewhere on the board
U-REG-FUNC-LD: SV2.5; also elsewhere on the board
U-REG-FUNC-RD: SV2.3; also elsewhere on the board
U-REG-RD-HI: SV2.27; also elsewhere on the board
U-REG-RD-LO: SV2.23; also elsewhere on the board
U-REG-UP: SV2.33; also elsewhere on the board
U-SR-LD: SV1.9; also elsewhere on the board
U-TMP-REG-LD0: SV2.8; also elsewhere on the board
U-TMP-REG-LD1: SV2.12; also elsewhere on the board
U-TMP-REG-RD0: SV2.6; also elsewhere on the board
U-TMP-REG-RD1: SV2.10; also elsewhere on the board
U-VMA: SV2.32; also elsewhere on the board
UADDR-REG-ID0: SV2.14; also elsewhere on the board
UADDR-REG-ID1: SV2.16; also elsewhere on the board
UADDR-REG-ID2: SV2.18; also elsewhere on the board
UADDR-REG-ID3: SV2.20; also elsewhere on the board
UALU0: SV2.36; also elsewhere on the board
UALU1: SV2.38; also elsewhere on the board
UALU2: SV2.40; also elsewhere on the board
UALU3: SV1.1; also elsewhere on the board
UBR-TEST: SV1.11; also elsewhere on the board
UBRANCH-LD-HI: SV1.4; also elsewhere on the board
UBRANCH-LD-LO: SV1.37; also elsewhere on the board
UDEST-ADDR: JP1.4; also elsewhere on the board
UINT-EN: SV1.27; also elsewhere on the board
UINT-LD-HI: SV1.23; also elsewhere on the board
UINT-LD-LO: SV1.21; also elsewhere on the board
UINT-START: SV1.25; also elsewhere on the board
UIO-ADDR0: SV2.22; also elsewhere on the board
UIO-ADDR1: SV2.24; also elsewhere on the board
UIO-ADDR2: SV2.26; also elsewhere on the board
UIO-ADDR3: SV2.28; also elsewhere on the board
ULD-INS-REG: SV1.29; also elsewhere on the board
UOPERAND-CLK: SV1.33; also elsewhere on the board
UOUT-OFF: SV1.15; also elsewhere on the board
UOUT-ON: SV1.17; also elsewhere on the board
UREG-LD-HI: SV2.29; also elsewhere on the board
UREG-LD-ID0: SV2.15; also elsewhere on the board
UREG-LD-ID1: SV2.17; also elsewhere on the board
UREG-LD-ID2: SV2.19; also elsewhere on the board
UREG-LD-ID3: SV2.21; also elsewhere on the board
UREG-LD-LO: SV2.25; also elsewhere on the board
UREG-RD-ID0: SV2.7; also elsewhere on the board
UREG-RD-ID1: SV2.9; also elsewhere on the board
UREG-RD-ID2: SV2.11; also elsewhere on the board
UREG-RD-ID3: SV2.13; also elsewhere on the board
USOFT-HALT: SV1.8; also elsewhere on the board
USPARE3: JP1.1; also elsewhere on the board
USRC-ADDR: JP1.3; also elsewhere on the board
UUCODE-COUNT-RESET: SV1.31; also elsewhere on the board
VCC: SV2.1, SV2.2; also elsewhere on the board

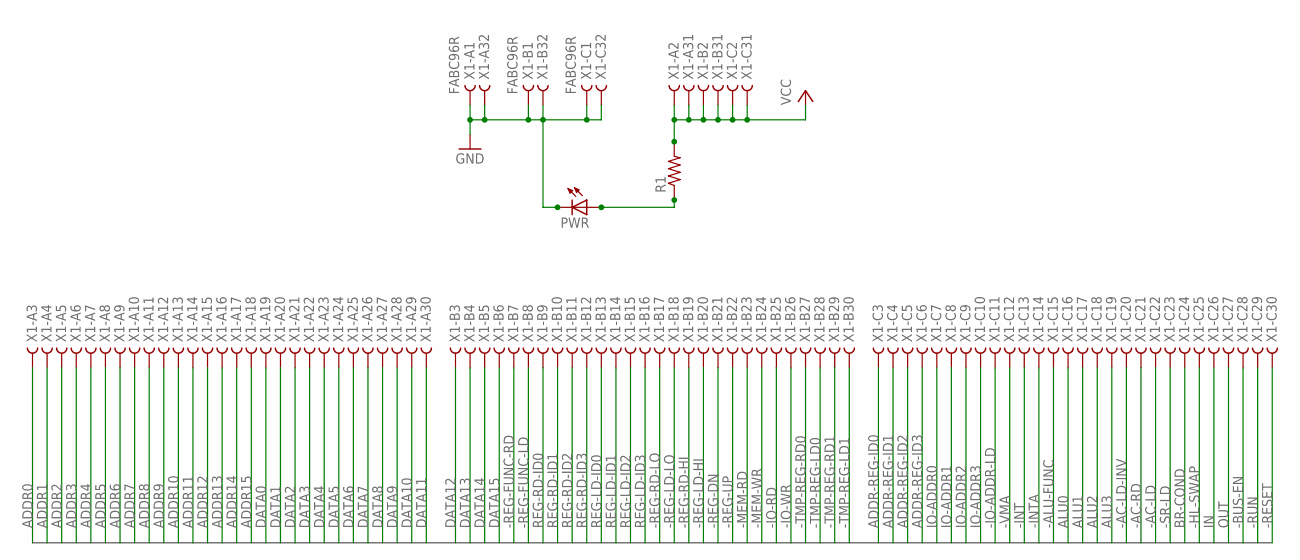
[picture p307: schematic Sequencer-Logic-Prod-V2.1l.sch, sheet 10]

Parts:
PWR: LED5MM
R1: 10k; 0207/10
X1: FABC96R

Connections:
-AC-LD: X1.C22; also elsewhere on the board
-AC-LD-INV: X1.C20; also elsewhere on the board
-AC-RD: X1.C21; also elsewhere on the board
-ALU-FUNC: X1.C15; also elsewhere on the board
-BUS-EN: X1.C28; also elsewhere on the board
-HL-SWAP: X1.C25; also elsewhere on the board
-INT: X1.C13; also elsewhere on the board
-INTA: X1.C14; also elsewhere on the board
-IO-ADDR-LD: X1.C11; also elsewhere on the board
-IO-RD: X1.B25; also elsewhere on the board
-IO-WR: X1.B26; also elsewhere on the board
-MEM-RD: X1.B23; also elsewhere on the board
-MEM-WR: X1.B24; also elsewhere on the board
-REG-DN: X1.B21; also elsewhere on the board
-REG-FUNC-LD: X1.B8; also elsewhere on the board
-REG-FUNC-RD: X1.B7; also elsewhere on the board
-REG-LD-HI: X1.B20; also elsewhere on the board
-REG-LD-LO: X1.B18; also elsewhere on the board
-REG-RD-HI: X1.B19; also elsewhere on the board
-REG-RD-LO: X1.B17; also elsewhere on the board
-REG-UP: X1.B22; also elsewhere on the board
-RESET: X1.C30; also elsewhere on the board
-RUN: X1.C29
-SR-LD: X1.C23; also elsewhere on the board
-TMP-REG-LD0: X1.B28; also elsewhere on the board
-TMP-REG-LD1: X1.B30; also elsewhere on the board
-TMP-REG-RD0: X1.B27; also elsewhere on the board
-TMP-REG-RD1: X1.B29; also elsewhere on the board
-VMA: X1.C12; also elsewhere on the board
ADDR0: X1.A3
ADDR1: X1.A4
ADDR2: X1.A5
ADDR3: X1.A6
ADDR4: X1.A7
ADDR5: X1.A8
ADDR6: X1.A9
ADDR7: X1.A10
ADDR8: X1.A11
ADDR9: X1.A12
ADDR10: X1.A13
ADDR11: X1.A14
ADDR12: X1.A15
ADDR13: X1.A16
ADDR14: X1.A17
ADDR15: X1.A18
ADDR-REG-ID0: X1.C3; also elsewhere on the board
ADDR-REG-ID1: X1.C4; also elsewhere on the board
ADDR-REG-ID2: X1.C5; also elsewhere on the board
ADDR-REG-ID3: X1.C6; also elsewhere on the board
ALU0: X1.C16; also elsewhere on the board
ALU1: X1.C17; also elsewhere on the board
ALU2: X1.C18; also elsewhere on the board
ALU3: X1.C19; also elsewhere on the board
BR-COND: X1.C24; also elsewhere on the board
DATA0: X1.A19; also elsewhere on the board
DATA1: X1.A20; also elsewhere on the board
DATA2: X1.A21; also elsewhere on the board
DATA3: X1.A22; also elsewhere on the board
DATA4: X1.A23; also elsewhere on the board
DATA5: X1.A24; also elsewhere on the board
DATA6: X1.A25; also elsewhere on the board
DATA7: X1.A26; also elsewhere on the board
DATA8: X1.A27; also elsewhere on the board
DATA9: X1.A28; also elsewhere on the board
DATA10: X1.A29; also elsewhere on the board
DATA11: X1.A30; also elsewhere on the board
DATA12: X1.B3; also elsewhere on the board
DATA13: X1.B4; also elsewhere on the board
DATA14: X1.B5; also elsewhere on the board
DATA15: X1.B6; also elsewhere on the board
GND: PWR.K (C), X1.A1, X1.A32, X1.B1, X1.B32, X1.C1, X1.C32; also elsewhere on the board
IN: X1.C26
IO-ADDR0: X1.C7; also elsewhere on the board
IO-ADDR1: X1.C8; also elsewhere on the board
IO-ADDR2: X1.C9; also elsewhere on the board
IO-ADDR3: X1.C10; also elsewhere on the board
unnamed: PWR.A, R1.1
OUT: X1.C27; also elsewhere on the board
REG-LD-ID0: X1.B13; also elsewhere on the board
REG-LD-ID1: X1.B14; also elsewhere on the board
REG-LD-ID2: X1.B15; also elsewhere on the board
REG-LD-ID3: X1.B16; also elsewhere on the board
REG-RD-ID0: X1.B9; also elsewhere on the board
REG-RD-ID1: X1.B10; also elsewhere on the board
REG-RD-ID2: X1.B11; also elsewhere on the board
REG-RD-ID3: X1.B12; also elsewhere on the board
VCC: R1.2, X1.A2, X1.A31, X1.B2, X1.B31, X1.C2, X1.C31; also elsewhere on the board

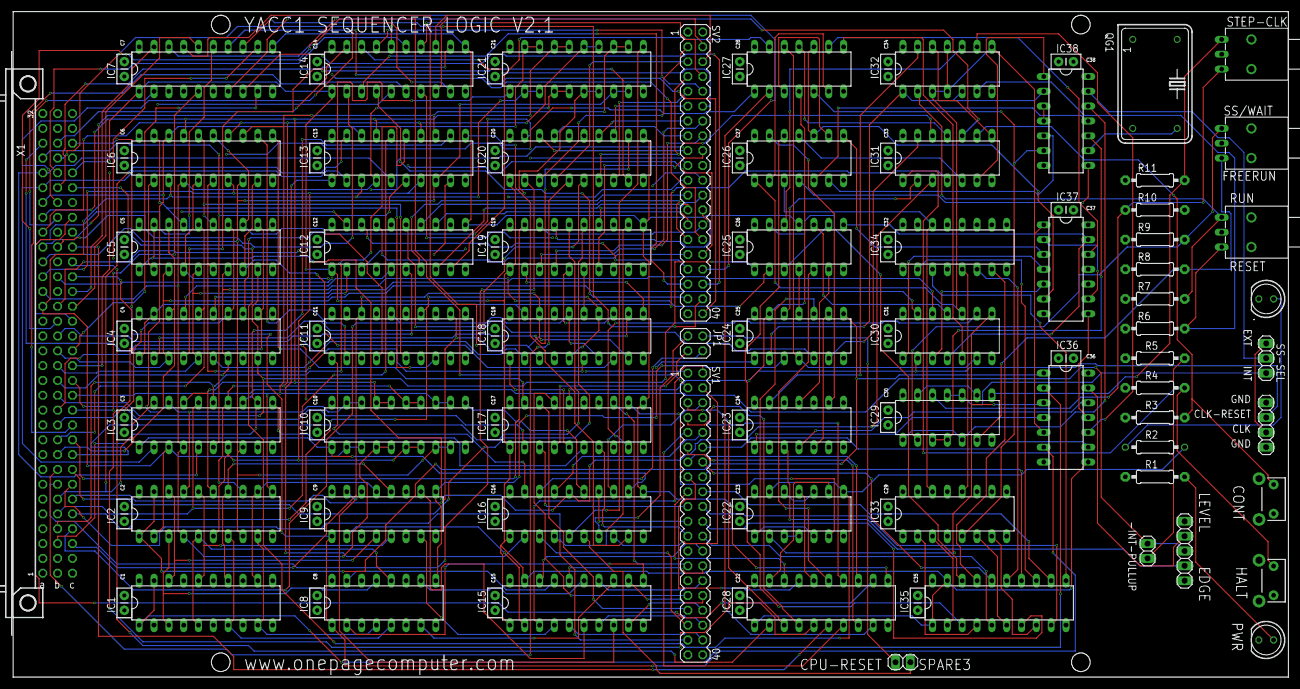
[picture p308: board Sequencer-Logic-Prod-V2.1l.brd from above]

Board: 4 copper layers, 218.4 x 114.0 mm, 104 parts (0 on the bottom side), 282 nets.
