ksr/YACC1-D/hardware/cards/bus-tester/eagle/v1.1/tester.brd

## EAGLE design hardware/cards/bus-tester/eagle/v1.1/tester.brd (2026-09-20, an earlier design)

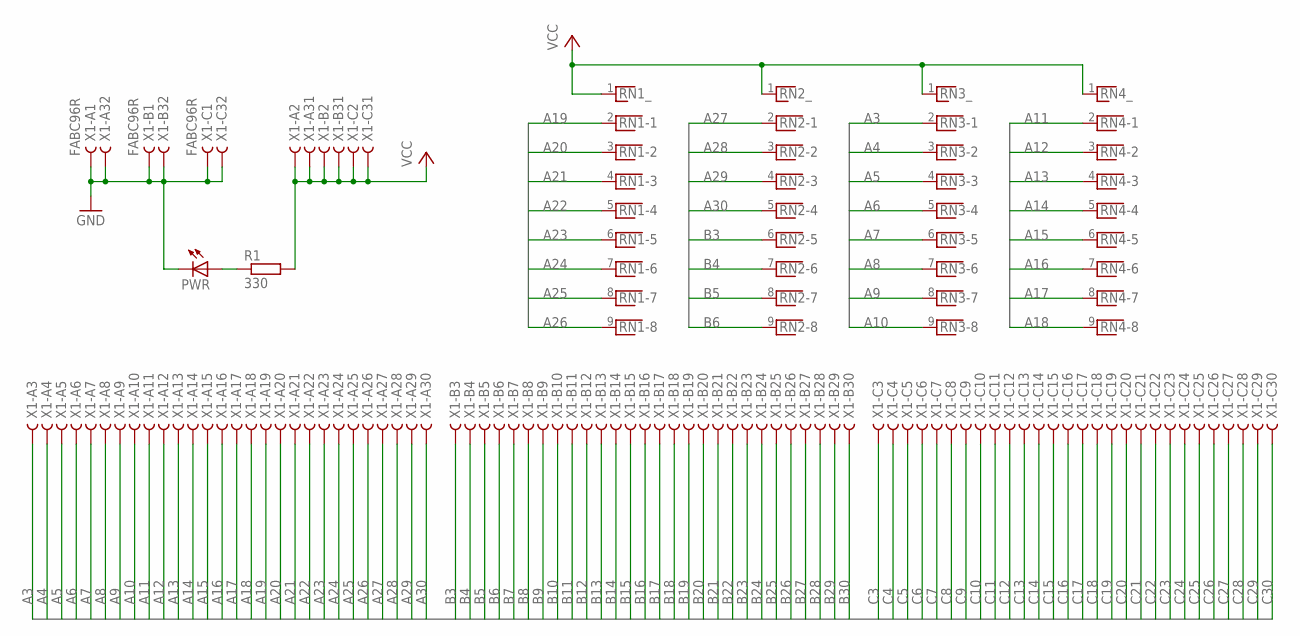
[picture p309: schematic tester.sch, sheet 1, BUS]

Parts:
PWR: LED5MM
R1: 330; 0207/10
RN1, RN2, RN3, RN4: RNX8; RN-9
X1: FABC96R

Connections:
A3: RN3.2, X1.A3; also elsewhere on the board
A4: RN3.3, X1.A4; also elsewhere on the board
A5: RN3.4, X1.A5; also elsewhere on the board
A6: RN3.5, X1.A6; also elsewhere on the board
A7: RN3.6, X1.A7; also elsewhere on the board
A8: RN3.7, X1.A8; also elsewhere on the board
A9: RN3.8, X1.A9; also elsewhere on the board
A10: RN3.9, X1.A10; also elsewhere on the board
A11: RN4.2, X1.A11; also elsewhere on the board
A12: RN4.3, X1.A12; also elsewhere on the board
A13: RN4.4, X1.A13; also elsewhere on the board
A14: RN4.5, X1.A14; also elsewhere on the board
A15: RN4.6, X1.A15; also elsewhere on the board
A16: RN4.7, X1.A16; also elsewhere on the board
A17: RN4.8, X1.A17; also elsewhere on the board
A18: RN4.9, X1.A18; also elsewhere on the board
A19: RN1.2, X1.A19; also elsewhere on the board
A20: RN1.3, X1.A20; also elsewhere on the board
A21: RN1.4, X1.A21; also elsewhere on the board
A22: RN1.5, X1.A22; also elsewhere on the board
A23: RN1.6, X1.A23; also elsewhere on the board
A24: RN1.7, X1.A24; also elsewhere on the board
A25: RN1.8, X1.A25; also elsewhere on the board
A26: RN1.9, X1.A26; also elsewhere on the board
A27: RN2.2, X1.A27; also elsewhere on the board
A28: RN2.3, X1.A28; also elsewhere on the board
A29: RN2.4, X1.A29; also elsewhere on the board
A30: RN2.5, X1.A30; also elsewhere on the board
B3: RN2.6, X1.B3; also elsewhere on the board
B4: RN2.7, X1.B4; also elsewhere on the board
B5: RN2.8, X1.B5; also elsewhere on the board
B6: RN2.9, X1.B6; also elsewhere on the board
B7: X1.B7; also elsewhere on the board
B8: X1.B8; also elsewhere on the board
B9: X1.B9; also elsewhere on the board
B10: X1.B10; also elsewhere on the board
B11: X1.B11; also elsewhere on the board
B12: X1.B12; also elsewhere on the board
B13: X1.B13; also elsewhere on the board
B14: X1.B14; also elsewhere on the board
B15: X1.B15; also elsewhere on the board
B16: X1.B16; also elsewhere on the board
B17: X1.B17; also elsewhere on the board
B18: X1.B18; also elsewhere on the board
B19: X1.B19; also elsewhere on the board
B20: X1.B20; also elsewhere on the board
B21: X1.B21; also elsewhere on the board
B22: X1.B22; also elsewhere on the board
B23: X1.B23; also elsewhere on the board
B24: X1.B24; also elsewhere on the board
B25: X1.B25; also elsewhere on the board
B26: X1.B26; also elsewhere on the board
B27: X1.B27; also elsewhere on the board
B28: X1.B28; also elsewhere on the board
B29: X1.B29; also elsewhere on the board
B30: X1.B30; also elsewhere on the board
C3: X1.C3; also elsewhere on the board
C4: X1.C4; also elsewhere on the board
C5: X1.C5; also elsewhere on the board
C6: X1.C6; also elsewhere on the board
C7: X1.C7; also elsewhere on the board
C8: X1.C8; also elsewhere on the board
C9: X1.C9; also elsewhere on the board
C10: X1.C10; also elsewhere on the board
C11: X1.C11; also elsewhere on the board
C12: X1.C12; also elsewhere on the board
C13: X1.C13; also elsewhere on the board
C14: X1.C14; also elsewhere on the board
C15: X1.C15; also elsewhere on the board
C16: X1.C16; also elsewhere on the board
C17: X1.C17; also elsewhere on the board
C18: X1.C18; also elsewhere on the board
C19: X1.C19; also elsewhere on the board
C20: X1.C20; also elsewhere on the board
C21: X1.C21; also elsewhere on the board
C22: X1.C22; also elsewhere on the board
C23: X1.C23; also elsewhere on the board
C24: X1.C24; also elsewhere on the board
C25: X1.C25; also elsewhere on the board
C26: X1.C26; also elsewhere on the board
C27: X1.C27; also elsewhere on the board
C28: X1.C28; also elsewhere on the board
C29: X1.C29; also elsewhere on the board
C30: X1.C30; also elsewhere on the board
GND: PWR.K (C), X1.A1, X1.A32, X1.B1, X1.B32, X1.C1, X1.C32; also elsewhere on the board
unnamed: PWR.A, R1.1
VCC: R1.2, RN1.1, RN2.1, RN3.1, RN4.1, X1.A2, X1.A31, X1.B2, X1.B31, X1.C2, X1.C31; also elsewhere on the board
