ksr/YACC1-D/hardware/cards/alu/eagle/v3.2/ALU V3.2.brd

## EAGLE design hardware/cards/alu/eagle/v3.2/ALU V3.2.brd (2026-09-20)

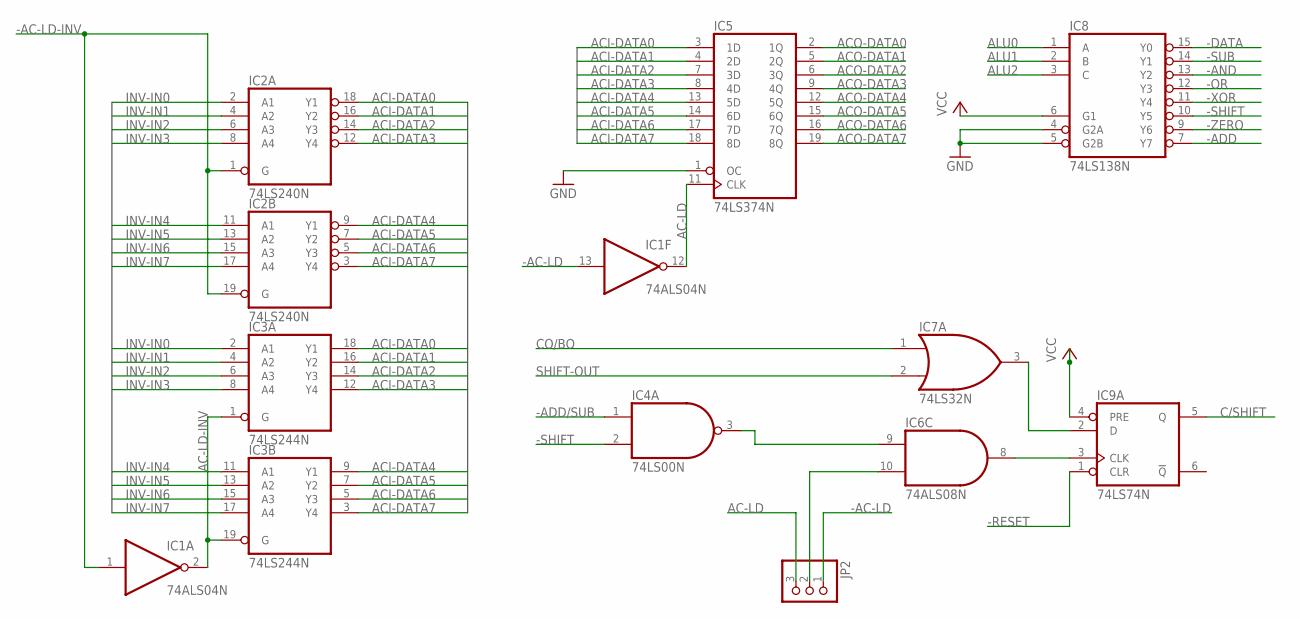
[picture p314: schematic ALU V3.2.sch, sheet 1, Accum Reg]

Parts:
IC1: 74ALS04N; DIL14
IC2: 74LS240N; DIL20
IC3: 74LS244N; DIL20
IC4: 74LS00N; DIL14
IC5: 74LS374N; DIL20
IC6: 74ALS08N; DIL14
IC7: 74LS32N; DIL14
IC8: 74LS138N; DIL16
IC9: 74LS74N; DIL14
JP2: PINHD-1X3; 1X03

Connections:
-AC-LD: IC1.13 (I), JP2.1; also elsewhere on the board
-AC-LD-INV: IC1.1 (I), IC2.1 (G), IC2.19 (G); also elsewhere on the board
-ADD: IC8.7 (Y7); also elsewhere on the board
-ADD/SUB: IC4.1 (I0); also elsewhere on the board
-AND: IC8.13 (Y2); also elsewhere on the board
-DATA: IC8.15 (Y0); also elsewhere on the board
-OR: IC8.12 (Y3); also elsewhere on the board
-RESET: IC9.1 (CLR); also elsewhere on the board
-SHIFT: IC4.2 (I1), IC8.10 (Y5); also elsewhere on the board
-SUB: IC8.14 (Y1); also elsewhere on the board
-XOR: IC8.11 (Y4); also elsewhere on the board
-ZERO: IC8.9 (Y6); also elsewhere on the board
AC-LD: IC1.12 (O), IC5.11 (CLK), JP2.3
AC-LD-INV: IC1.2 (O), IC3.1 (G), IC3.19 (G); also elsewhere on the board
ACI-DATA0: IC2.18 (Y1), IC3.18 (Y1), IC5.3 (1D)
ACI-DATA1: IC2.16 (Y2), IC3.16 (Y2), IC5.4 (2D)
ACI-DATA2: IC2.14 (Y3), IC3.14 (Y3), IC5.7 (3D)
ACI-DATA3: IC2.12 (Y4), IC3.12 (Y4), IC5.8 (4D)
ACI-DATA4: IC2.9 (Y1), IC3.9 (Y1), IC5.13 (5D)
ACI-DATA5: IC2.7 (Y2), IC3.7 (Y2), IC5.14 (6D)
ACI-DATA6: IC2.5 (Y3), IC3.5 (Y3), IC5.17 (7D)
ACI-DATA7: IC2.3 (Y4), IC3.3 (Y4), IC5.18 (8D)
ACO-DATA0: IC5.2 (1Q); also elsewhere on the board
ACO-DATA1: IC5.5 (2Q); also elsewhere on the board
ACO-DATA2: IC5.6 (3Q); also elsewhere on the board
ACO-DATA3: IC5.9 (4Q); also elsewhere on the board
ACO-DATA4: IC5.12 (5Q); also elsewhere on the board
ACO-DATA5: IC5.15 (6Q); also elsewhere on the board
ACO-DATA6: IC5.16 (7Q); also elsewhere on the board
ACO-DATA7: IC5.19 (8Q); also elsewhere on the board
ALU0: IC8.1 (A); also elsewhere on the board
ALU1: IC8.2 (B); also elsewhere on the board
ALU2: IC8.3 (C); also elsewhere on the board
C/SHIFT: IC9.5 (Q); also elsewhere on the board
CO/BO: IC7.1 (I0); also elsewhere on the board
GND: IC1.7 (GND), IC2.10 (GND), IC3.10 (GND), IC4.7 (GND), IC5.1 (OC), IC5.10 (GND), IC6.7 (GND), IC7.7 (GND), IC8.4 (G2A), IC8.5 (G2B), IC8.8 (GND), IC9.7 (GND); also elsewhere on the board
INV-IN0: IC2.2 (A1), IC3.2 (A1); also elsewhere on the board
INV-IN1: IC2.4 (A2), IC3.4 (A2); also elsewhere on the board
INV-IN2: IC2.6 (A3), IC3.6 (A3); also elsewhere on the board
INV-IN3: IC2.8 (A4), IC3.8 (A4); also elsewhere on the board
INV-IN4: IC2.11 (A1), IC3.11 (A1); also elsewhere on the board
INV-IN5: IC2.13 (A2), IC3.13 (A2); also elsewhere on the board
INV-IN6: IC2.15 (A3), IC3.15 (A3); also elsewhere on the board
INV-IN7: IC2.17 (A4), IC3.17 (A4); also elsewhere on the board
unnamed: IC4.3 (O), IC6.9 (I0)
unnamed: IC6.8 (O), IC9.3 (CLK)
unnamed: IC7.3 (O), IC9.2 (D)
unnamed: IC6.10 (I1), JP2.2
SHIFT-OUT: IC7.2 (I1); also elsewhere on the board
VCC: IC1.14 (VCC), IC2.20 (VCC), IC3.20 (VCC), IC4.14 (VCC), IC5.20 (VCC), IC6.14 (VCC), IC7.14 (VCC), IC8.6 (G1), IC8.16 (VCC), IC9.4 (PRE), IC9.14 (VCC); also elsewhere on the board

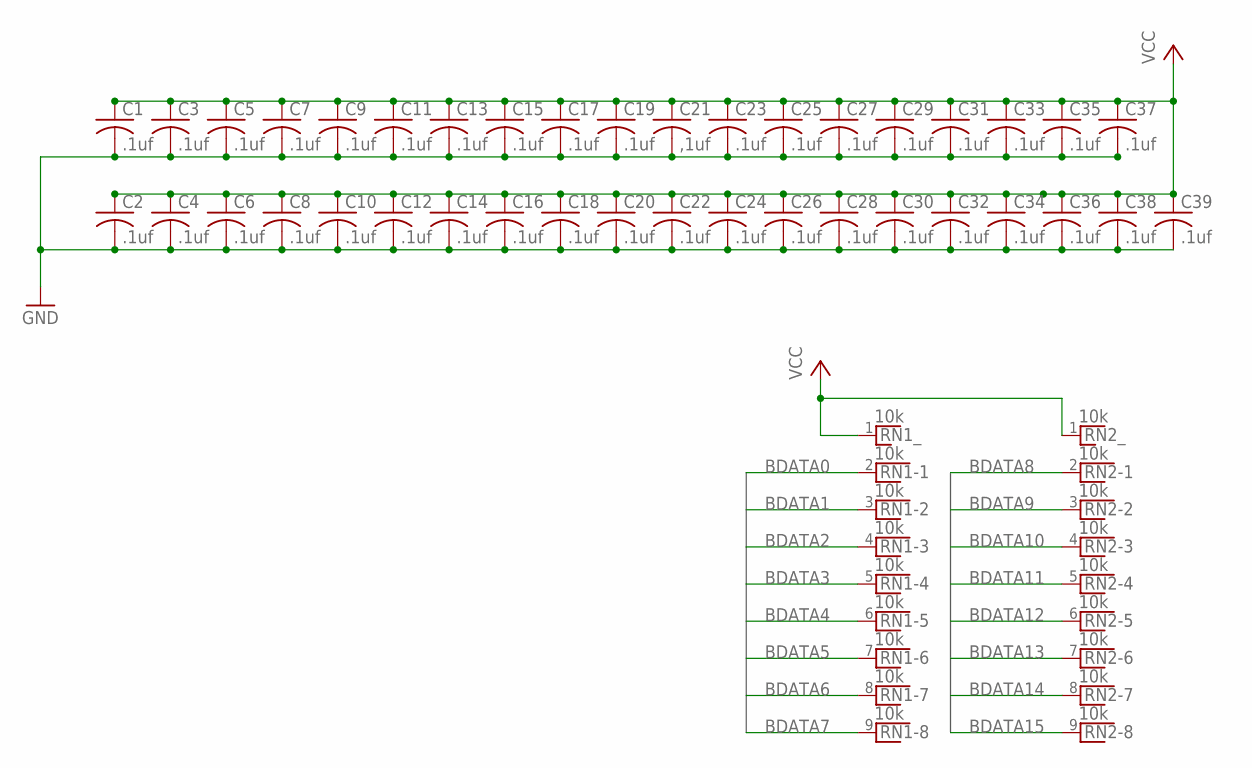
[picture p315: schematic ALU V3.2.sch, sheet 2, caps & pullups]

Parts:
C1, C2, C3, C4, C5, C6, C7, C8, C9, C10, C11, C12, C13, C14, C15, C16, C17, C18, C19, C20, C22, C23, C24, C25, C26, C27, C28, C29, C30, C31, C32, C33, C34, C35, C36, C37, C38, C39: .1uf; C025-024X044
C21: ,1uf; C025-024X044
RN1, RN2: 10k; RN-9

Connections:
BDATA0: RN1.2; also elsewhere on the board
BDATA1: RN1.3; also elsewhere on the board
BDATA2: RN1.4; also elsewhere on the board
BDATA3: RN1.5; also elsewhere on the board
BDATA4: RN1.6; also elsewhere on the board
BDATA5: RN1.7; also elsewhere on the board
BDATA6: RN1.8; also elsewhere on the board
BDATA7: RN1.9; also elsewhere on the board
BDATA8: RN2.2; also elsewhere on the board
BDATA9: RN2.3; also elsewhere on the board
BDATA10: RN2.4; also elsewhere on the board
BDATA11: RN2.5; also elsewhere on the board
BDATA12: RN2.6; also elsewhere on the board
BDATA13: RN2.7; also elsewhere on the board
BDATA14: RN2.8; also elsewhere on the board
BDATA15: RN2.9; also elsewhere on the board
GND: C1.2, C2.2, C3.2, C4.2, C5.2, C6.2, C7.2, C8.2, C9.2, C10.2, C11.2, C12.2, C13.2, C14.2, C15.2, C16.2, C17.2, C18.2, C19.2, C20.2, C21.2, C22.2, C23.2, C24.2, C25.2, C26.2, C27.2, C28.2, C29.2, C30.2, C31.2, C32.2, C33.2, C34.2, C35.2, C36.2, C37.2, C38.2, C39.2; also elsewhere on the board
VCC: C1.1, C2.1, C3.1, C4.1, C5.1, C6.1, C7.1, C8.1, C9.1, C10.1, C11.1, C12.1, C13.1, C14.1, C15.1, C16.1, C17.1, C18.1, C19.1, C20.1, C21.1, C22.1, C23.1, C24.1, C25.1, C26.1, C27.1, C28.1, C29.1, C30.1, C31.1, C32.1, C33.1, C34.1, C35.1, C36.1, C37.1, C38.1, C39.1, RN1.1, RN2.1; also elsewhere on the board

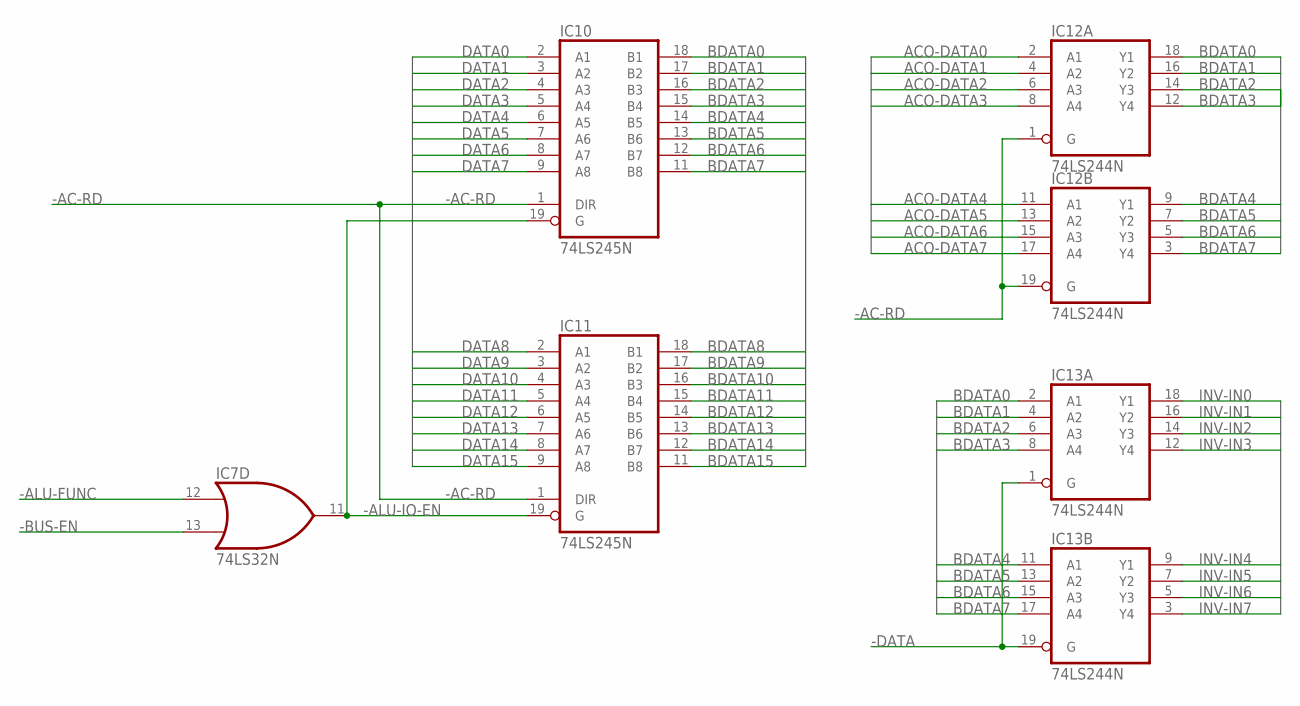
[picture p316: schematic ALU V3.2.sch, sheet 3, Bus Buffering]

Parts:
IC7: 74LS32N; DIL14
IC10, IC11: 74LS245N; DIL20
IC12, IC13: 74LS244N; DIL20

Connections:
-AC-RD: IC10.1 (DIR), IC11.1 (DIR), IC12.1 (G), IC12.19 (G); also elsewhere on the board
-ALU-FUNC: IC7.12 (I0); also elsewhere on the board
-ALU-IO-EN: IC7.11 (O), IC10.19 (G), IC11.19 (G)
-BUS-EN: IC7.13 (I1); also elsewhere on the board
-DATA: IC13.1 (G), IC13.19 (G); also elsewhere on the board
ACO-DATA0: IC12.2 (A1); also elsewhere on the board
ACO-DATA1: IC12.4 (A2); also elsewhere on the board
ACO-DATA2: IC12.6 (A3); also elsewhere on the board
ACO-DATA3: IC12.8 (A4); also elsewhere on the board
ACO-DATA4: IC12.11 (A1); also elsewhere on the board
ACO-DATA5: IC12.13 (A2); also elsewhere on the board
ACO-DATA6: IC12.15 (A3); also elsewhere on the board
ACO-DATA7: IC12.17 (A4); also elsewhere on the board
BDATA0: IC10.18 (B1), IC12.18 (Y1), IC13.2 (A1); also elsewhere on the board
BDATA1: IC10.17 (B2), IC12.16 (Y2), IC13.4 (A2); also elsewhere on the board
BDATA2: IC10.16 (B3), IC12.14 (Y3), IC13.6 (A3); also elsewhere on the board
BDATA3: IC10.15 (B4), IC12.12 (Y4), IC13.8 (A4); also elsewhere on the board
BDATA4: IC10.14 (B5), IC12.9 (Y1), IC13.11 (A1); also elsewhere on the board
BDATA5: IC10.13 (B6), IC12.7 (Y2), IC13.13 (A2); also elsewhere on the board
BDATA6: IC10.12 (B7), IC12.5 (Y3), IC13.15 (A3); also elsewhere on the board
BDATA7: IC10.11 (B8), IC12.3 (Y4), IC13.17 (A4); also elsewhere on the board
BDATA8: IC11.18 (B1); also elsewhere on the board
BDATA9: IC11.17 (B2); also elsewhere on the board
BDATA10: IC11.16 (B3); also elsewhere on the board
BDATA11: IC11.15 (B4); also elsewhere on the board
BDATA12: IC11.14 (B5); also elsewhere on the board
BDATA13: IC11.13 (B6); also elsewhere on the board
BDATA14: IC11.12 (B7); also elsewhere on the board
BDATA15: IC11.11 (B8); also elsewhere on the board
DATA0: IC10.2 (A1); also elsewhere on the board
DATA1: IC10.3 (A2); also elsewhere on the board
DATA2: IC10.4 (A3); also elsewhere on the board
DATA3: IC10.5 (A4); also elsewhere on the board
DATA4: IC10.6 (A5); also elsewhere on the board
DATA5: IC10.7 (A6); also elsewhere on the board
DATA6: IC10.8 (A7); also elsewhere on the board
DATA7: IC10.9 (A8); also elsewhere on the board
DATA8: IC11.2 (A1); also elsewhere on the board
DATA9: IC11.3 (A2); also elsewhere on the board
DATA10: IC11.4 (A3); also elsewhere on the board
DATA11: IC11.5 (A4); also elsewhere on the board
DATA12: IC11.6 (A5); also elsewhere on the board
DATA13: IC11.7 (A6); also elsewhere on the board
DATA14: IC11.8 (A7); also elsewhere on the board
DATA15: IC11.9 (A8); also elsewhere on the board
GND: IC7.7 (GND), IC10.10 (GND), IC11.10 (GND), IC12.10 (GND), IC13.10 (GND); also elsewhere on the board
INV-IN0: IC13.18 (Y1); also elsewhere on the board
INV-IN1: IC13.16 (Y2); also elsewhere on the board
INV-IN2: IC13.14 (Y3); also elsewhere on the board
INV-IN3: IC13.12 (Y4); also elsewhere on the board
INV-IN4: IC13.9 (Y1); also elsewhere on the board
INV-IN5: IC13.7 (Y2); also elsewhere on the board
INV-IN6: IC13.5 (Y3); also elsewhere on the board
INV-IN7: IC13.3 (Y4); also elsewhere on the board
VCC: IC7.14 (VCC), IC10.20 (VCC), IC11.20 (VCC), IC12.20 (VCC), IC13.20 (VCC); also elsewhere on the board

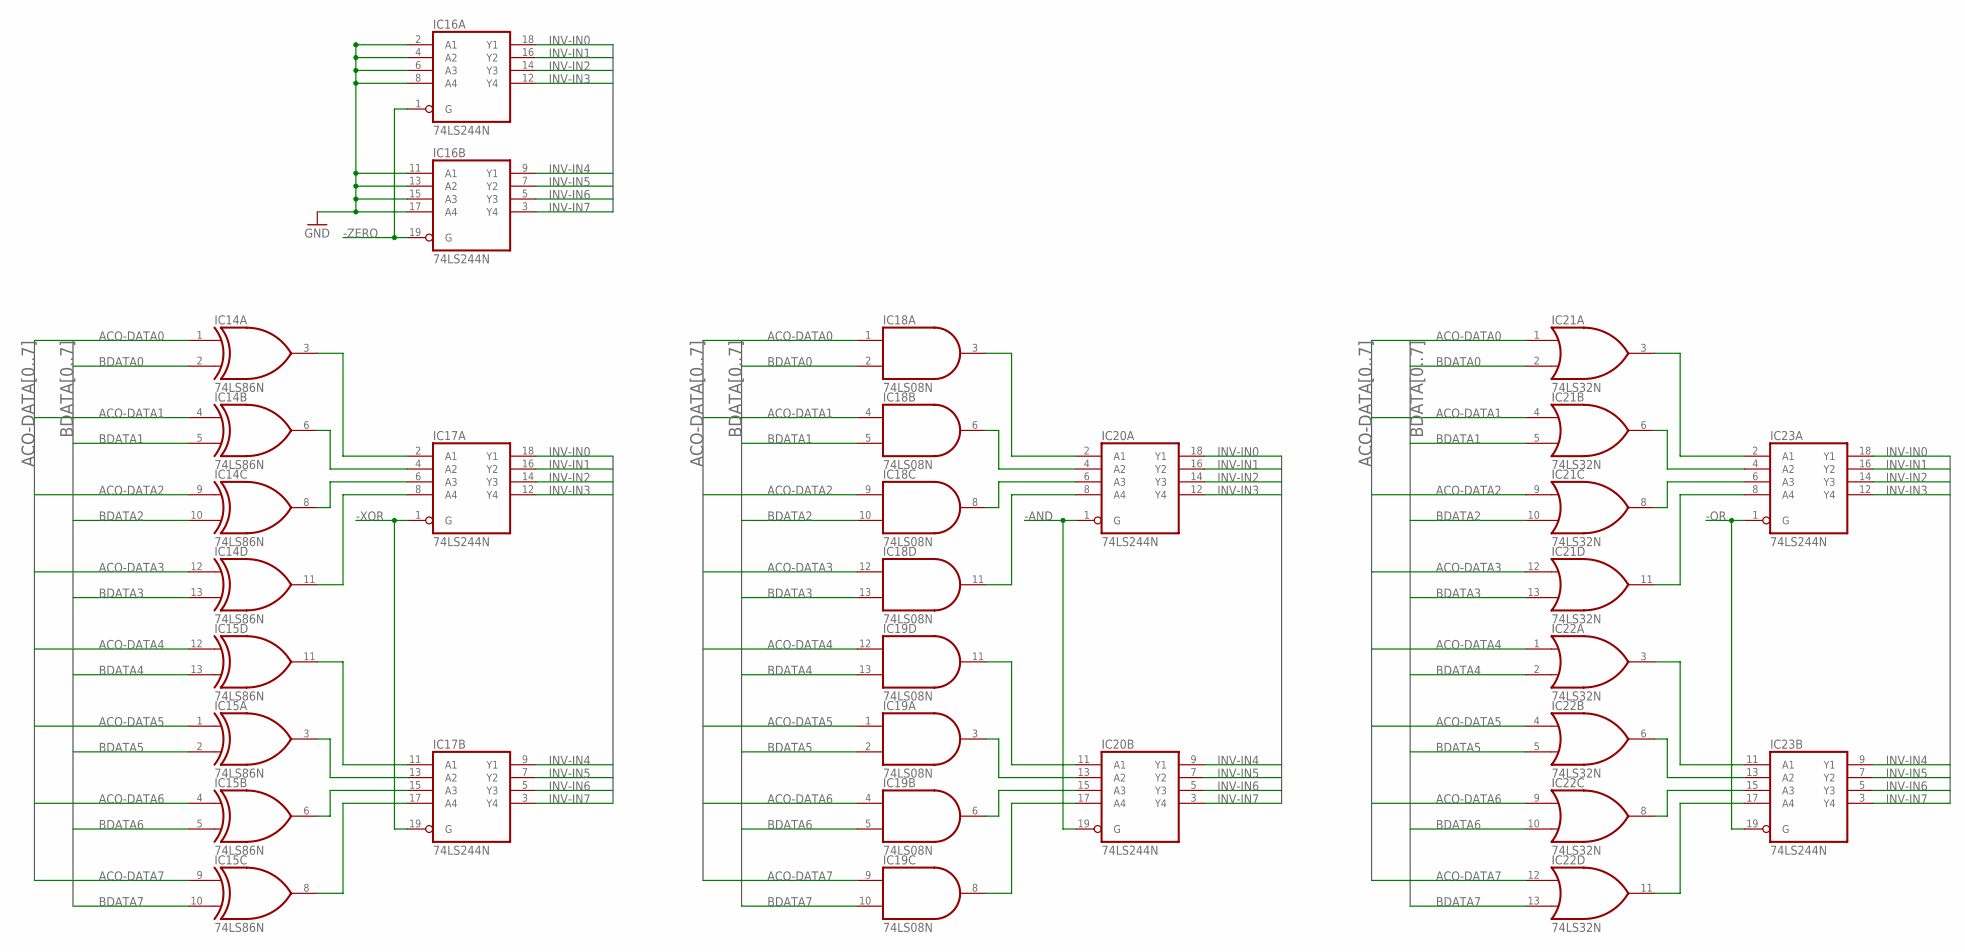
[picture p317: schematic ALU V3.2.sch, sheet 4, Logical]

Parts:
IC14, IC15: 74LS86N; DIL14
IC16, IC17, IC20, IC23: 74LS244N; DIL20
IC18, IC19: 74LS08N; DIL14
IC21, IC22: 74LS32N; DIL14

Connections:
-AND: IC20.1 (G), IC20.19 (G); also elsewhere on the board
-OR: IC23.1 (G), IC23.19 (G); also elsewhere on the board
-XOR: IC17.1 (G), IC17.19 (G); also elsewhere on the board
-ZERO: IC16.1 (G), IC16.19 (G); also elsewhere on the board
ACO-DATA0: IC14.1 (I0), IC18.1 (I0), IC21.1 (I0); also elsewhere on the board
ACO-DATA1: IC14.4 (I0), IC18.4 (I0), IC21.4 (I0); also elsewhere on the board
ACO-DATA2: IC14.9 (I0), IC18.9 (I0), IC21.9 (I0); also elsewhere on the board
ACO-DATA3: IC14.12 (I0), IC18.12 (I0), IC21.12 (I0); also elsewhere on the board
ACO-DATA4: IC15.12 (I0), IC19.12 (I0), IC22.1 (I0); also elsewhere on the board
ACO-DATA5: IC15.1 (I0), IC19.1 (I0), IC22.4 (I0); also elsewhere on the board
ACO-DATA6: IC15.4 (I0), IC19.4 (I0), IC22.9 (I0); also elsewhere on the board
ACO-DATA7: IC15.9 (I0), IC19.9 (I0), IC22.12 (I0); also elsewhere on the board
BDATA0: IC14.2 (I1), IC18.2 (I1), IC21.2 (I1); also elsewhere on the board
BDATA1: IC14.5 (I1), IC18.5 (I1), IC21.5 (I1); also elsewhere on the board
BDATA2: IC14.10 (I1), IC18.10 (I1), IC21.10 (I1); also elsewhere on the board
BDATA3: IC14.13 (I1), IC18.13 (I1), IC21.13 (I1); also elsewhere on the board
BDATA4: IC15.13 (I1), IC19.13 (I1), IC22.2 (I1); also elsewhere on the board
BDATA5: IC15.2 (I1), IC19.2 (I1), IC22.5 (I1); also elsewhere on the board
BDATA6: IC15.5 (I1), IC19.5 (I1), IC22.10 (I1); also elsewhere on the board
BDATA7: IC15.10 (I1), IC19.10 (I1), IC22.13 (I1); also elsewhere on the board
GND: IC14.7 (GND), IC15.7 (GND), IC16.2 (A1), IC16.4 (A2), IC16.6 (A3), IC16.8 (A4), IC16.10 (GND), IC16.11 (A1), IC16.13 (A2), IC16.15 (A3), IC16.17 (A4), IC17.10 (GND), IC18.7 (GND), IC19.7 (GND), IC20.10 (GND), IC21.7 (GND), IC22.7 (GND), IC23.10 (GND); also elsewhere on the board
INV-IN0: IC16.18 (Y1), IC17.18 (Y1), IC20.18 (Y1), IC23.18 (Y1); also elsewhere on the board
INV-IN1: IC16.16 (Y2), IC17.16 (Y2), IC20.16 (Y2), IC23.16 (Y2); also elsewhere on the board
INV-IN2: IC16.14 (Y3), IC17.14 (Y3), IC20.14 (Y3), IC23.14 (Y3); also elsewhere on the board
INV-IN3: IC16.12 (Y4), IC17.12 (Y4), IC20.12 (Y4), IC23.12 (Y4); also elsewhere on the board
INV-IN4: IC16.9 (Y1), IC17.9 (Y1), IC20.9 (Y1), IC23.9 (Y1); also elsewhere on the board
INV-IN5: IC16.7 (Y2), IC17.7 (Y2), IC20.7 (Y2), IC23.7 (Y2); also elsewhere on the board
INV-IN6: IC16.5 (Y3), IC17.5 (Y3), IC20.5 (Y3), IC23.5 (Y3); also elsewhere on the board
INV-IN7: IC16.3 (Y4), IC17.3 (Y4), IC20.3 (Y4), IC23.3 (Y4); also elsewhere on the board
unnamed: IC21.3 (O), IC23.2 (A1)
unnamed: IC21.6 (O), IC23.4 (A2)
unnamed: IC21.8 (O), IC23.6 (A3)
unnamed: IC21.11 (O), IC23.8 (A4)
unnamed: IC22.3 (O), IC23.11 (A1)
unnamed: IC22.6 (O), IC23.13 (A2)
unnamed: IC22.8 (O), IC23.15 (A3)
unnamed: IC22.11 (O), IC23.17 (A4)
unnamed: IC18.3 (O), IC20.2 (A1)
unnamed: IC18.6 (O), IC20.4 (A2)
unnamed: IC18.8 (O), IC20.6 (A3)
unnamed: IC18.11 (O), IC20.8 (A4)
unnamed: IC19.11 (O), IC20.11 (A1)
unnamed: IC19.3 (O), IC20.13 (A2)
unnamed: IC19.6 (O), IC20.15 (A3)
unnamed: IC19.8 (O), IC20.17 (A4)
unnamed: IC14.3 (O), IC17.2 (A1)
unnamed: IC14.6 (O), IC17.4 (A2)
unnamed: IC14.8 (O), IC17.6 (A3)
unnamed: IC14.11 (O), IC17.8 (A4)
unnamed: IC15.11 (O), IC17.11 (A1)
unnamed: IC15.3 (O), IC17.13 (A2)
unnamed: IC15.6 (O), IC17.15 (A3)
unnamed: IC15.8 (O), IC17.17 (A4)
VCC: IC14.14 (VCC), IC15.14 (VCC), IC16.20 (VCC), IC17.20 (VCC), IC18.14 (VCC), IC19.14 (VCC), IC20.20 (VCC), IC21.14 (VCC), IC22.14 (VCC), IC23.20 (VCC); also elsewhere on the board
