ksr/YACC1-D/hardware/cards/alu/eagle/v3.2/ALU V3.2.brd

## EAGLE design hardware/cards/alu/eagle/v3.2/ALU V3.2.brd (continued)

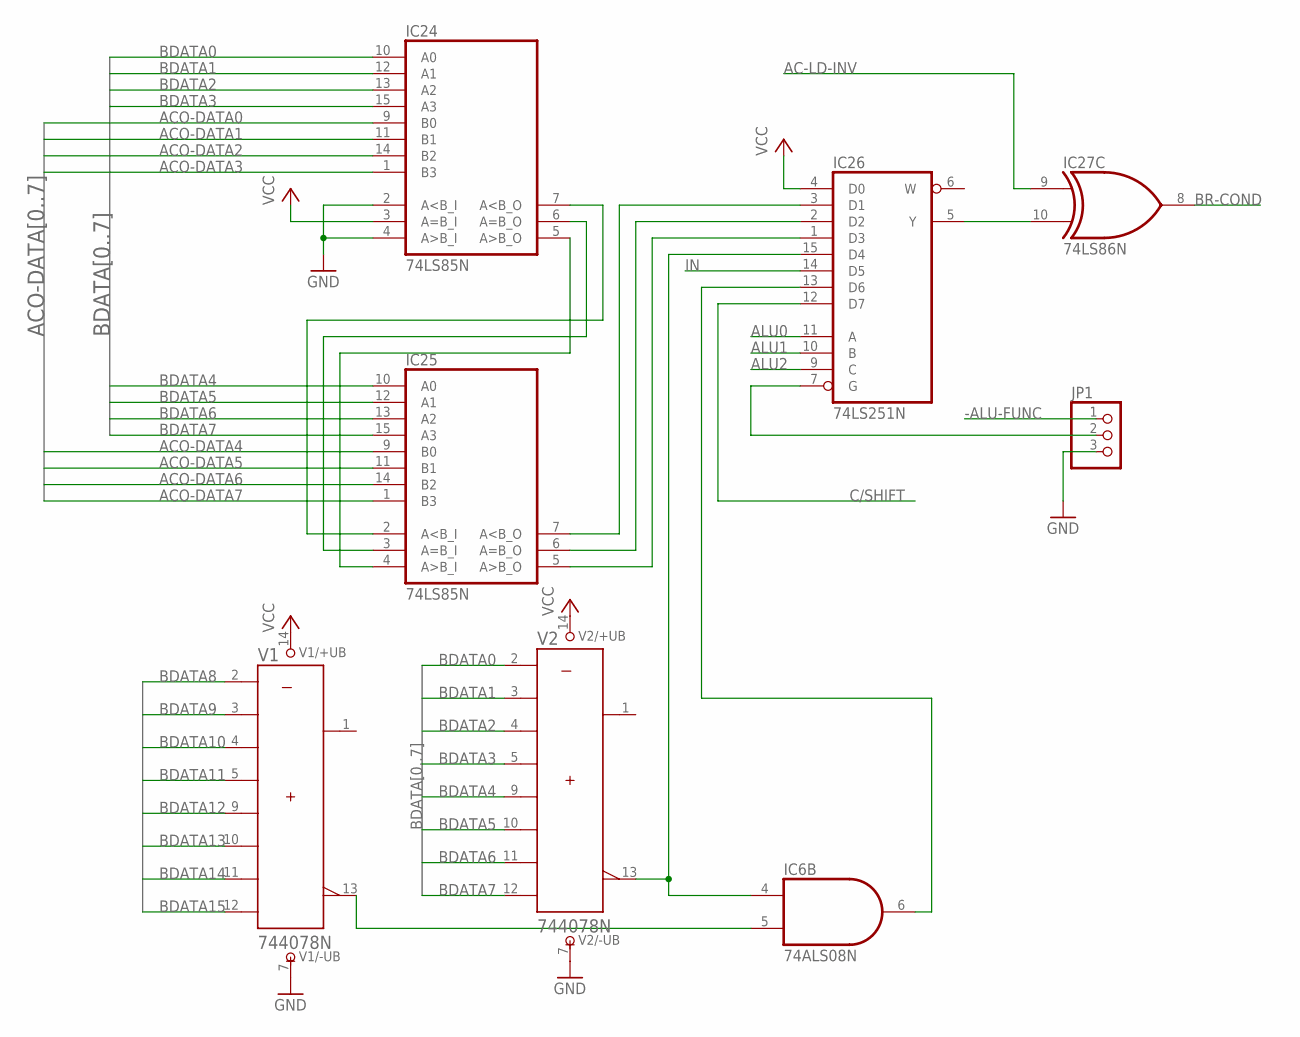
[picture p318: schematic ALU V3.2.sch, sheet 5, Compare]

Parts:
IC6: 74ALS08N; DIL14
IC24, IC25: 74LS85N; DIL16
IC26: 74LS251N; DIL16
IC27: 74LS86N; DIL14
JP1: PINHD-1X3; 1X03
V1, V2: 744078N; DIL14

Connections:
-ALU-FUNC: JP1.1; also elsewhere on the board
AC-LD-INV: IC27.9 (I0); also elsewhere on the board
ACO-DATA0: IC24.9 (B0); also elsewhere on the board
ACO-DATA1: IC24.11 (B1); also elsewhere on the board
ACO-DATA2: IC24.14 (B2); also elsewhere on the board
ACO-DATA3: IC24.1 (B3); also elsewhere on the board
ACO-DATA4: IC25.9 (B0); also elsewhere on the board
ACO-DATA5: IC25.11 (B1); also elsewhere on the board
ACO-DATA6: IC25.14 (B2); also elsewhere on the board
ACO-DATA7: IC25.1 (B3); also elsewhere on the board
ALU0: IC26.11 (A); also elsewhere on the board
ALU1: IC26.10 (B); also elsewhere on the board
ALU2: IC26.9 (C); also elsewhere on the board
BDATA0: IC24.10 (A0), V2.2 (A); also elsewhere on the board
BDATA1: IC24.12 (A1), V2.3 (B); also elsewhere on the board
BDATA2: IC24.13 (A2), V2.4 (C); also elsewhere on the board
BDATA3: IC24.15 (A3), V2.5 (D); also elsewhere on the board
BDATA4: IC25.10 (A0), V2.9 (E); also elsewhere on the board
BDATA5: IC25.12 (A1), V2.10 (F); also elsewhere on the board
BDATA6: IC25.13 (A2), V2.11 (G); also elsewhere on the board
BDATA7: IC25.15 (A3), V2.12 (H); also elsewhere on the board
BDATA8: V1.2 (A); also elsewhere on the board
BDATA9: V1.3 (B); also elsewhere on the board
BDATA10: V1.4 (C); also elsewhere on the board
BDATA11: V1.5 (D); also elsewhere on the board
BDATA12: V1.9 (E); also elsewhere on the board
BDATA13: V1.10 (F); also elsewhere on the board
BDATA14: V1.11 (G); also elsewhere on the board
BDATA15: V1.12 (H); also elsewhere on the board
BR-COND: IC27.8 (O); also elsewhere on the board
C/SHIFT: IC26.12 (D7); also elsewhere on the board
GND: IC6.7 (GND), IC24.2 (A<B_I), IC24.4 (A>B_I), IC24.8 (GND), IC25.8 (GND), IC26.8 (GND), IC27.7 (GND), JP1.3, V1.7 (-UB), V2.7 (-UB); also elsewhere on the board
IN: IC26.14 (D5); also elsewhere on the board
unnamed: IC26.7 (G), JP1.2
unnamed: IC6.4 (I0), IC26.15 (D4), V2.13 (W)
unnamed: IC24.5 (A>B_O), IC25.4 (A>B_I)
unnamed: IC24.6 (A=B_O), IC25.3 (A=B_I)
unnamed: IC24.7 (A<B_O), IC25.2 (A<B_I)
unnamed: IC25.7 (A<B_O), IC26.3 (D1)
unnamed: IC25.6 (A=B_O), IC26.2 (D2)
unnamed: IC25.5 (A>B_O), IC26.1 (D3)
unnamed: IC6.5 (I1), V1.13 (W)
unnamed: IC6.6 (O), IC26.13 (D6)
unnamed: IC26.5 (Y), IC27.10 (I1)
VCC: IC6.14 (VCC), IC24.3 (A=B_I), IC24.16 (VCC), IC25.16 (VCC), IC26.4 (D0), IC26.16 (VCC), IC27.14 (VCC), V1.14 (+UB), V2.14 (+UB); also elsewhere on the board

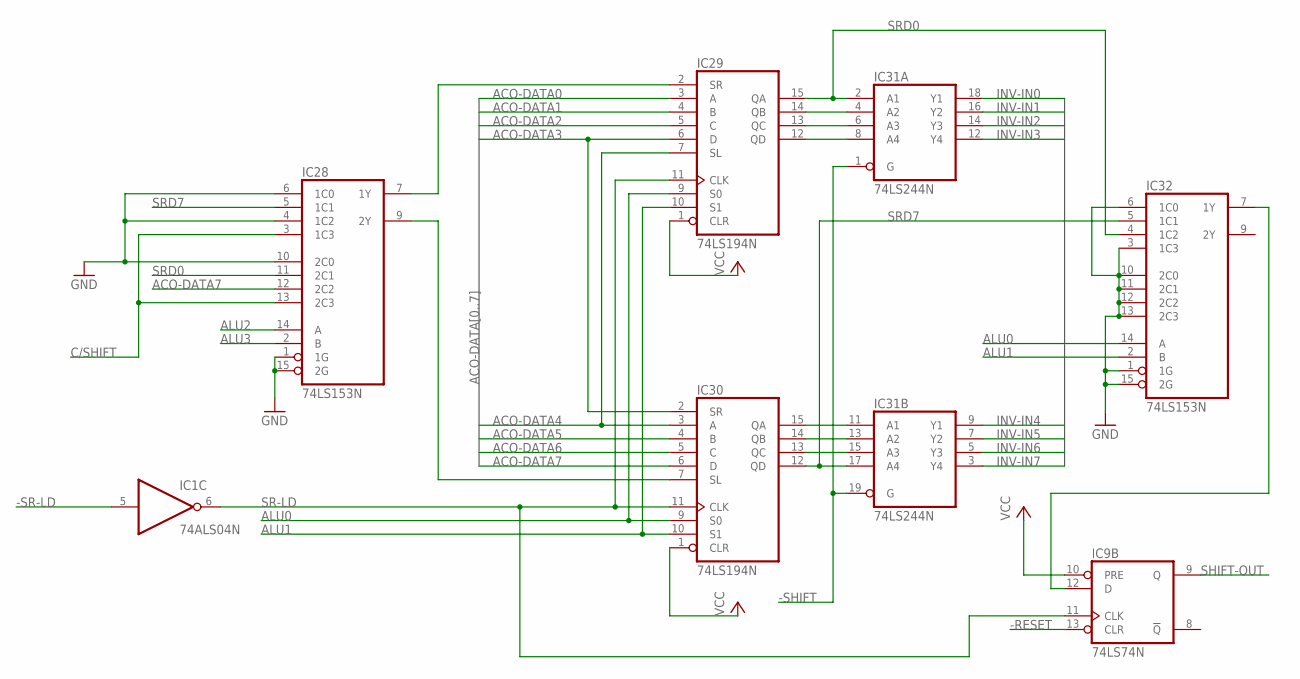
[picture p319: schematic ALU V3.2.sch, sheet 6, Shifter]

Parts:
IC1: 74ALS04N; DIL14
IC9: 74LS74N; DIL14
IC28, IC32: 74LS153N; DIL16
IC29, IC30: 74LS194N; DIL16
IC31: 74LS244N; DIL20

Connections:
-RESET: IC9.13 (CLR); also elsewhere on the board
-SHIFT: IC31.1 (G), IC31.19 (G); also elsewhere on the board
-SR-LD: IC1.5 (I); also elsewhere on the board
ACO-DATA0: IC29.3 (A); also elsewhere on the board
ACO-DATA1: IC29.4 (B); also elsewhere on the board
ACO-DATA2: IC29.5 (C); also elsewhere on the board
ACO-DATA3: IC29.6 (D), IC30.2 (SR); also elsewhere on the board
ACO-DATA4: IC29.7 (SL), IC30.3 (A); also elsewhere on the board
ACO-DATA5: IC30.4 (B); also elsewhere on the board
ACO-DATA6: IC30.5 (C); also elsewhere on the board
ACO-DATA7: IC28.12 (2C2), IC30.6 (D); also elsewhere on the board
ALU0: IC29.9 (S0), IC30.9 (S0), IC32.14 (A); also elsewhere on the board
ALU1: IC29.10 (S1), IC30.10 (S1), IC32.2 (B); also elsewhere on the board
ALU2: IC28.14 (A); also elsewhere on the board
ALU3: IC28.2 (B); also elsewhere on the board
C/SHIFT: IC28.3 (1C3), IC28.13 (2C3); also elsewhere on the board
GND: IC1.7 (GND), IC9.7 (GND), IC28.1 (1G), IC28.4 (1C2), IC28.6 (1C0), IC28.8 (GND), IC28.10 (2C0), IC28.15 (2G), IC29.8 (GND), IC30.8 (GND), IC31.10 (GND), IC32.1 (1G), IC32.3 (1C3), IC32.6 (1C0), IC32.8 (GND), IC32.10 (2C0), IC32.11 (2C1), IC32.12 (2C2), IC32.13 (2C3), IC32.15 (2G); also elsewhere on the board
INV-IN0: IC31.18 (Y1); also elsewhere on the board
INV-IN1: IC31.16 (Y2); also elsewhere on the board
INV-IN2: IC31.14 (Y3); also elsewhere on the board
INV-IN3: IC31.12 (Y4); also elsewhere on the board
INV-IN4: IC31.9 (Y1); also elsewhere on the board
INV-IN5: IC31.7 (Y2); also elsewhere on the board
INV-IN6: IC31.5 (Y3); also elsewhere on the board
INV-IN7: IC31.3 (Y4); also elsewhere on the board
unnamed: IC9.12 (D), IC32.7 (1Y)
unnamed: IC29.14 (QB), IC31.4 (A2)
unnamed: IC29.13 (QC), IC31.6 (A3)
unnamed: IC29.12 (QD), IC31.8 (A4)
unnamed: IC30.15 (QA), IC31.11 (A1)
unnamed: IC30.14 (QB), IC31.13 (A2)
unnamed: IC30.13 (QC), IC31.15 (A3)
unnamed: IC28.7 (1Y), IC29.2 (SR)
unnamed: IC28.9 (2Y), IC30.7 (SL)
SHIFT-OUT: IC9.9 (Q); also elsewhere on the board
SR-LD: IC1.6 (O), IC9.11 (CLK), IC29.11 (CLK), IC30.11 (CLK)
SRD0: IC28.11 (2C1), IC29.15 (QA), IC31.2 (A1), IC32.4 (1C2)
SRD7: IC28.5 (1C1), IC30.12 (QD), IC31.17 (A4), IC32.5 (1C1)
VCC: IC1.14 (VCC), IC9.10 (PRE), IC9.14 (VCC), IC28.16 (VCC), IC29.1 (CLR), IC29.16 (VCC), IC30.1 (CLR), IC30.16 (VCC), IC31.20 (VCC), IC32.16 (VCC); also elsewhere on the board

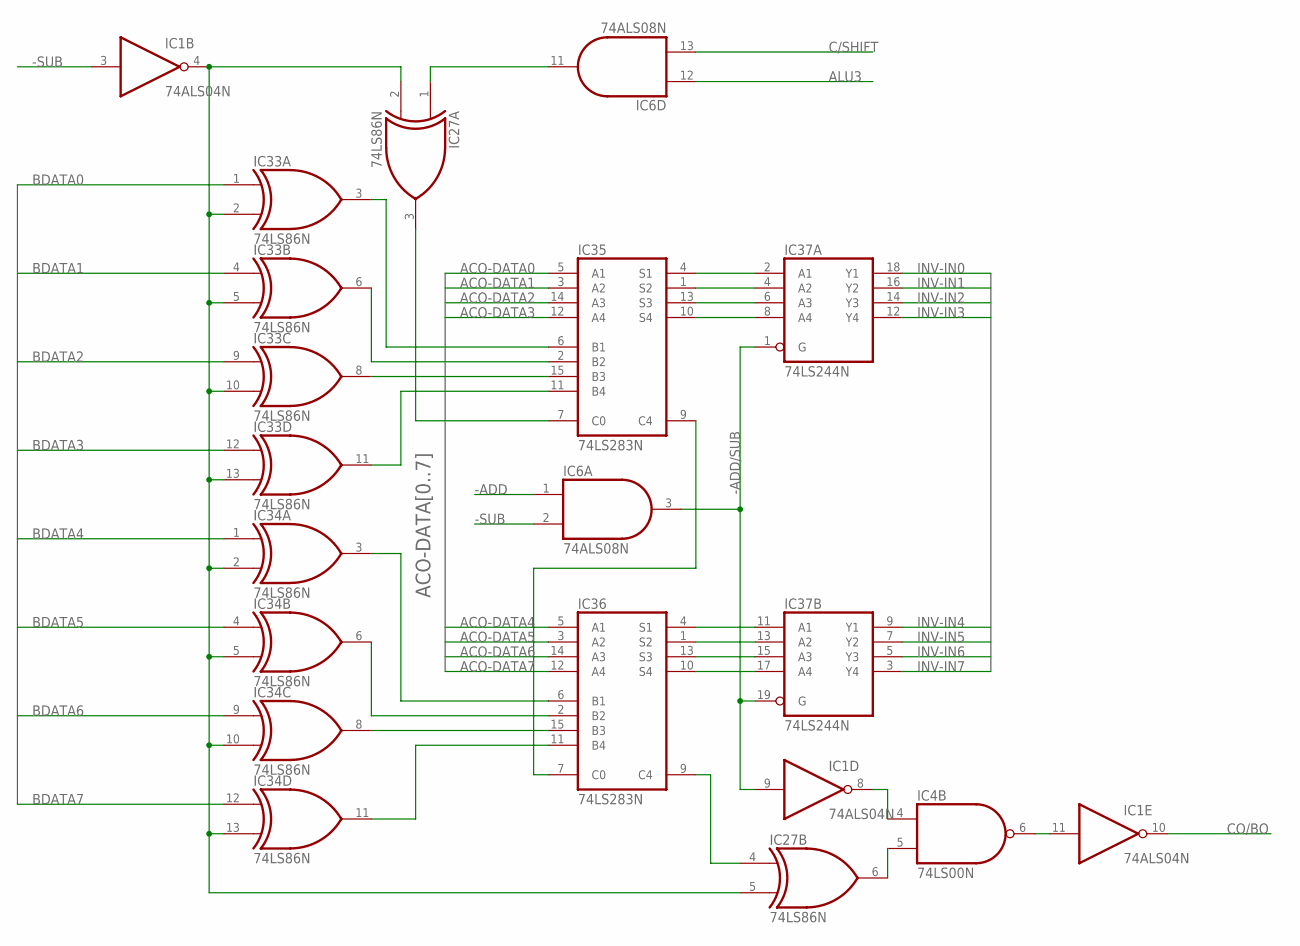
[picture p320: schematic ALU V3.2.sch, sheet 7, Add/Sub]

Parts:
IC1: 74ALS04N; DIL14
IC4: 74LS00N; DIL14
IC6: 74ALS08N; DIL14
IC27, IC33, IC34: 74LS86N; DIL14
IC35, IC36: 74LS283N; DIL16
IC37: 74LS244N; DIL20

Connections:
-ADD: IC6.1 (I0); also elsewhere on the board
-ADD/SUB: IC1.9 (I), IC6.3 (O), IC37.1 (G), IC37.19 (G); also elsewhere on the board
-SUB: IC1.3 (I), IC6.2 (I1); also elsewhere on the board
ACO-DATA0: IC35.5 (A1); also elsewhere on the board
ACO-DATA1: IC35.3 (A2); also elsewhere on the board
ACO-DATA2: IC35.14 (A3); also elsewhere on the board
ACO-DATA3: IC35.12 (A4); also elsewhere on the board
ACO-DATA4: IC36.5 (A1); also elsewhere on the board
ACO-DATA5: IC36.3 (A2); also elsewhere on the board
ACO-DATA6: IC36.14 (A3); also elsewhere on the board
ACO-DATA7: IC36.12 (A4); also elsewhere on the board
ALU3: IC6.12 (I0); also elsewhere on the board
BDATA0: IC33.1 (I0); also elsewhere on the board
BDATA1: IC33.4 (I0); also elsewhere on the board
BDATA2: IC33.9 (I0); also elsewhere on the board
BDATA3: IC33.12 (I0); also elsewhere on the board
BDATA4: IC34.1 (I0); also elsewhere on the board
BDATA5: IC34.4 (I0); also elsewhere on the board
BDATA6: IC34.9 (I0); also elsewhere on the board
BDATA7: IC34.12 (I0); also elsewhere on the board
C/SHIFT: IC6.13 (I1); also elsewhere on the board
CO/BO: IC1.10 (O); also elsewhere on the board
GND: IC1.7 (GND), IC4.7 (GND), IC6.7 (GND), IC27.7 (GND), IC33.7 (GND), IC34.7 (GND), IC35.8 (GND), IC36.8 (GND), IC37.10 (GND); also elsewhere on the board
INV-IN0: IC37.18 (Y1); also elsewhere on the board
INV-IN1: IC37.16 (Y2); also elsewhere on the board
INV-IN2: IC37.14 (Y3); also elsewhere on the board
INV-IN3: IC37.12 (Y4); also elsewhere on the board
INV-IN4: IC37.9 (Y1); also elsewhere on the board
INV-IN5: IC37.7 (Y2); also elsewhere on the board
INV-IN6: IC37.5 (Y3); also elsewhere on the board
INV-IN7: IC37.3 (Y4); also elsewhere on the board
unnamed: IC27.4 (I0), IC36.9 (C4)
unnamed: IC27.3 (O), IC35.7 (C0)
unnamed: IC6.11 (O), IC27.1 (I0)
unnamed: IC4.5 (I1), IC27.6 (O)
unnamed: IC33.6 (O), IC35.2 (B2)
unnamed: IC34.6 (O), IC36.2 (B2)
unnamed: IC1.8 (O), IC4.4 (I0)
unnamed: IC1.11 (I), IC4.6 (O)
unnamed: IC33.8 (O), IC35.15 (B3)
unnamed: IC33.11 (O), IC35.11 (B4)
unnamed: IC33.3 (O), IC35.6 (B1)
unnamed: IC34.3 (O), IC36.6 (B1)
unnamed: IC34.8 (O), IC36.15 (B3)
unnamed: IC34.11 (O), IC36.11 (B4)
unnamed: IC35.4 (S1), IC37.2 (A1)
unnamed: IC35.1 (S2), IC37.4 (A2)
unnamed: IC35.13 (S3), IC37.6 (A3)
unnamed: IC35.10 (S4), IC37.8 (A4)
unnamed: IC36.4 (S1), IC37.11 (A1)
unnamed: IC36.1 (S2), IC37.13 (A2)
unnamed: IC36.13 (S3), IC37.15 (A3)
unnamed: IC36.10 (S4), IC37.17 (A4)
unnamed: IC35.9 (C4), IC36.7 (C0)
SUB: IC1.4 (O), IC27.2 (I1), IC27.5 (I1), IC33.2 (I1), IC33.5 (I1), IC33.10 (I1), IC33.13 (I1), IC34.2 (I1), IC34.5 (I1), IC34.10 (I1), IC34.13 (I1)
VCC: IC1.14 (VCC), IC4.14 (VCC), IC6.14 (VCC), IC27.14 (VCC), IC33.14 (VCC), IC34.14 (VCC), IC35.16 (VCC), IC36.16 (VCC), IC37.20 (VCC); also elsewhere on the board

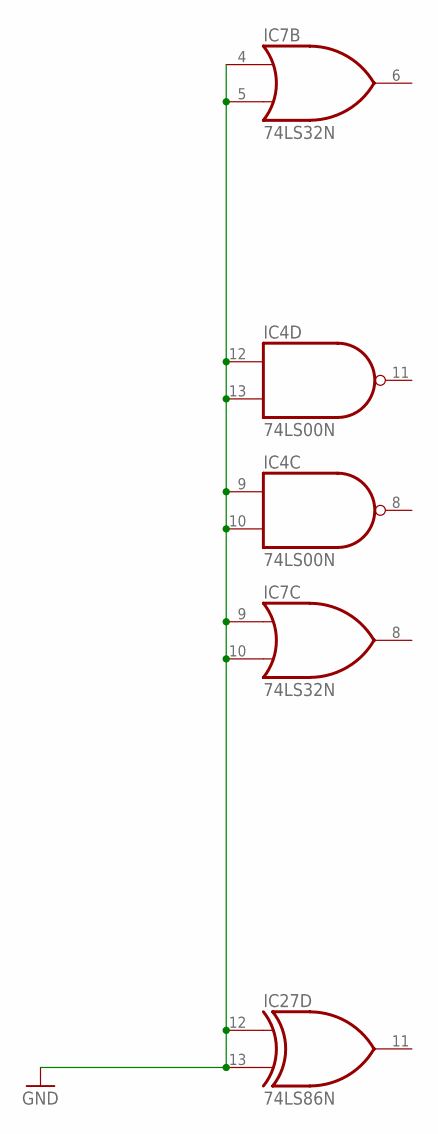
[picture p321: schematic ALU V3.2.sch, sheet 8, unused]

Parts:
IC4: 74LS00N; DIL14
IC7: 74LS32N; DIL14
IC27: 74LS86N; DIL14

Connections:
GND: IC4.7 (GND), IC4.9 (I0), IC4.10 (I1), IC4.12 (I0), IC4.13 (I1), IC7.4 (I0), IC7.5 (I1), IC7.7 (GND), IC7.9 (I0), IC7.10 (I1), IC27.7 (GND), IC27.12 (I0), IC27.13 (I1); also elsewhere on the board
VCC: IC4.14 (VCC), IC7.14 (VCC), IC27.14 (VCC); also elsewhere on the board

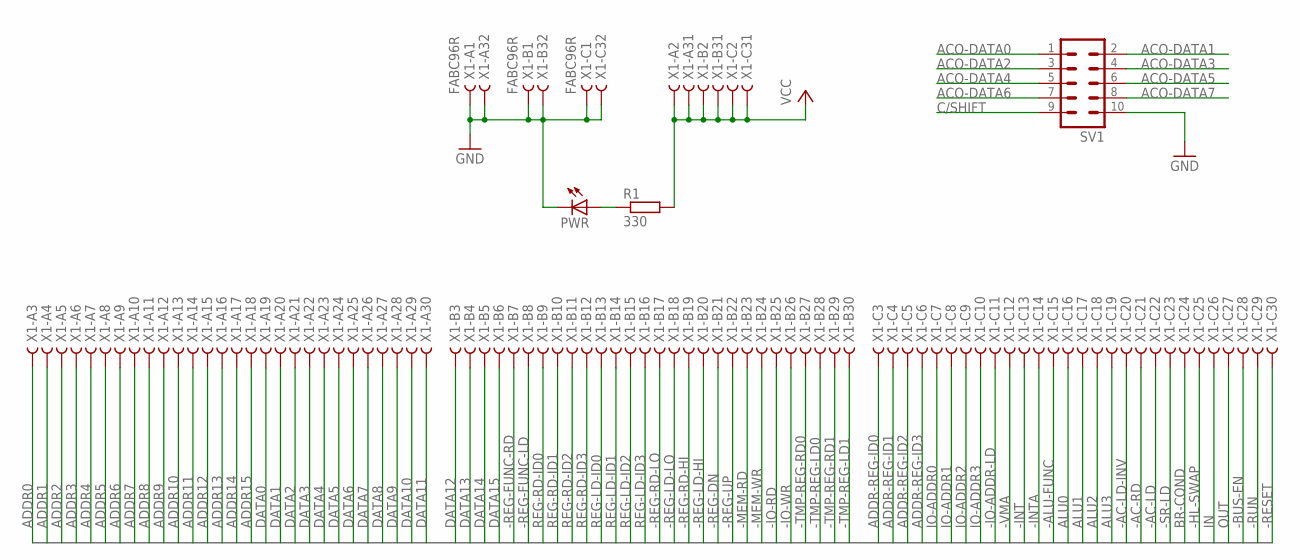
[picture p322: schematic ALU V3.2.sch, sheet 9, BUS]

Parts:
PWR: LED5MM
R1: 330; 0207/10
SV1: MA05-2
X1: FABC96R

Connections:
-AC-LD: X1.C22; also elsewhere on the board
-AC-LD-INV: X1.C20; also elsewhere on the board
-AC-RD: X1.C21; also elsewhere on the board
-ALU-FUNC: X1.C15; also elsewhere on the board
-BUS-EN: X1.C28; also elsewhere on the board
-HL-SWAP: X1.C25
-INT: X1.C13
-INTA: X1.C14
-IO-ADDR-LD: X1.C11
-IO-RD: X1.B25
-IO-WR: X1.B26
-MEM-RD: X1.B23
-MEM-WR: X1.B24
-REG-DN: X1.B21
-REG-FUNC-LD: X1.B8
-REG-FUNC-RD: X1.B7
-REG-LD-HI: X1.B20
-REG-LD-LO: X1.B18
-REG-RD-HI: X1.B19
-REG-RD-LO: X1.B17
-REG-UP: X1.B22
-RESET: X1.C30; also elsewhere on the board
-RUN: X1.C29
-SR-LD: X1.C23; also elsewhere on the board
-TMP-REG-LD0: X1.B28
-TMP-REG-LD1: X1.B30
-TMP-REG-RD0: X1.B27
-TMP-REG-RD1: X1.B29
-VMA: X1.C12
ACO-DATA0: SV1.1; also elsewhere on the board
ACO-DATA1: SV1.2; also elsewhere on the board
ACO-DATA2: SV1.3; also elsewhere on the board
ACO-DATA3: SV1.4; also elsewhere on the board
ACO-DATA4: SV1.5; also elsewhere on the board
ACO-DATA5: SV1.6; also elsewhere on the board
ACO-DATA6: SV1.7; also elsewhere on the board
ACO-DATA7: SV1.8; also elsewhere on the board
ADDR0: X1.A3
ADDR1: X1.A4
ADDR2: X1.A5
ADDR3: X1.A6
ADDR4: X1.A7
ADDR5: X1.A8
ADDR6: X1.A9
ADDR7: X1.A10
ADDR8: X1.A11
ADDR9: X1.A12
ADDR10: X1.A13
ADDR11: X1.A14
ADDR12: X1.A15
ADDR13: X1.A16
ADDR14: X1.A17
ADDR15: X1.A18
ADDR-REG-ID0: X1.C3
ADDR-REG-ID1: X1.C4
ADDR-REG-ID2: X1.C5
ADDR-REG-ID3: X1.C6
ALU0: X1.C16; also elsewhere on the board
ALU1: X1.C17; also elsewhere on the board
ALU2: X1.C18; also elsewhere on the board
ALU3: X1.C19; also elsewhere on the board
BR-COND: X1.C24; also elsewhere on the board
C/SHIFT: SV1.9; also elsewhere on the board
DATA0: X1.A19; also elsewhere on the board
DATA1: X1.A20; also elsewhere on the board
DATA2: X1.A21; also elsewhere on the board
DATA3: X1.A22; also elsewhere on the board
DATA4: X1.A23; also elsewhere on the board
DATA5: X1.A24; also elsewhere on the board
DATA6: X1.A25; also elsewhere on the board
DATA7: X1.A26; also elsewhere on the board
DATA8: X1.A27; also elsewhere on the board
DATA9: X1.A28; also elsewhere on the board
DATA10: X1.A29; also elsewhere on the board
DATA11: X1.A30; also elsewhere on the board
DATA12: X1.B3; also elsewhere on the board
DATA13: X1.B4; also elsewhere on the board
DATA14: X1.B5; also elsewhere on the board
DATA15: X1.B6; also elsewhere on the board
GND: PWR.K (C), SV1.10, X1.A1, X1.A32, X1.B1, X1.B32, X1.C1, X1.C32; also elsewhere on the board
IN: X1.C26; also elsewhere on the board
IO-ADDR0: X1.C7
IO-ADDR1: X1.C8
IO-ADDR2: X1.C9
IO-ADDR3: X1.C10
unnamed: PWR.A, R1.1
OUT: X1.C27
REG-LD-ID0: X1.B13
REG-LD-ID1: X1.B14
REG-LD-ID2: X1.B15
REG-LD-ID3: X1.B16
REG-RD-ID0: X1.B9
REG-RD-ID1: X1.B10
REG-RD-ID2: X1.B11
REG-RD-ID3: X1.B12
VCC: R1.2, X1.A2, X1.A31, X1.B2, X1.B31, X1.C2, X1.C31; also elsewhere on the board

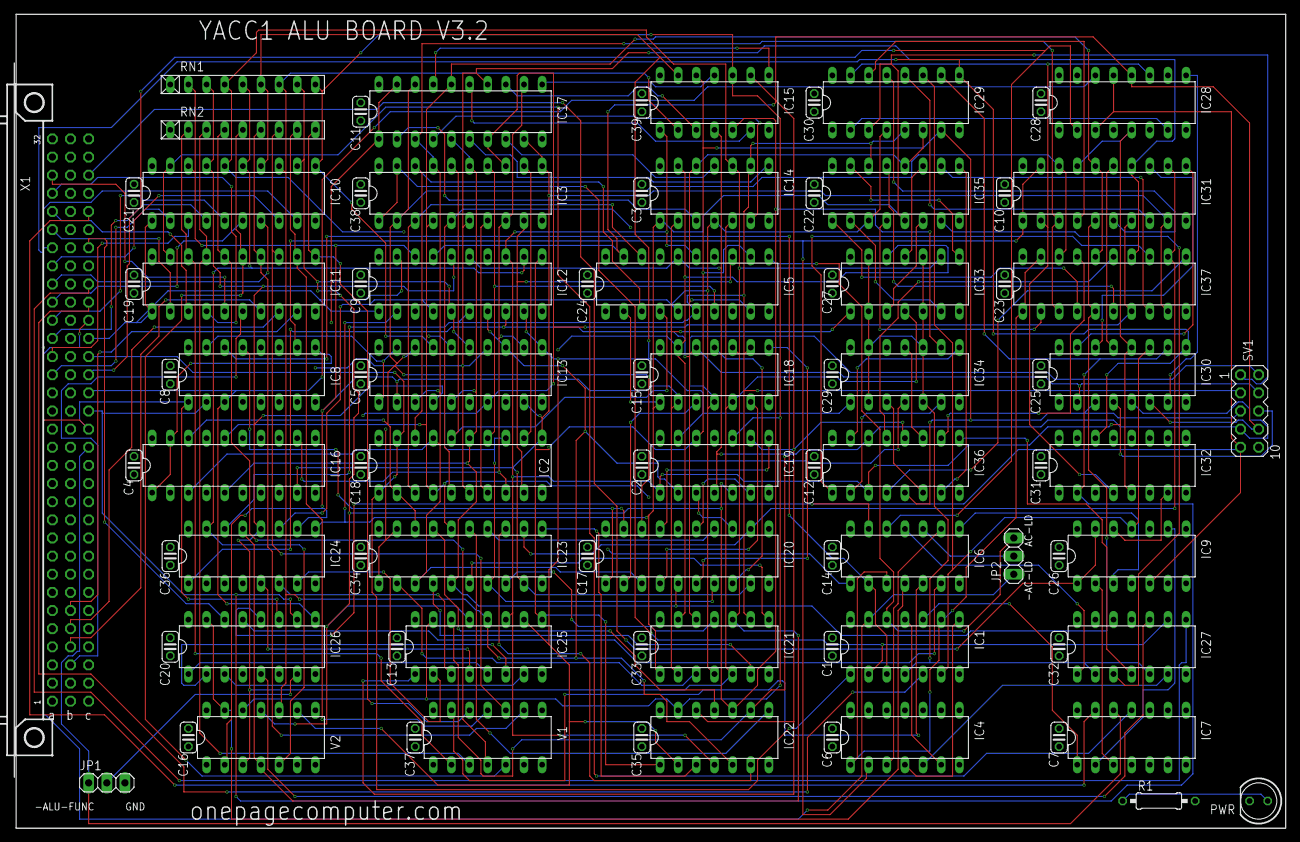
[picture p323: board ALU V3.2.brd from above]

Board: 4 copper layers, 177.8 x 114.0 mm, 86 parts (0 on the bottom side), 162 nets.
