ksr/YACC1-D/hardware/cards/mem-register/eagle/v1.0/Mem Register V1.0.brd

## EAGLE design hardware/cards/mem-register/eagle/v1.0/Mem Register V1.0.brd (2026-09-20)

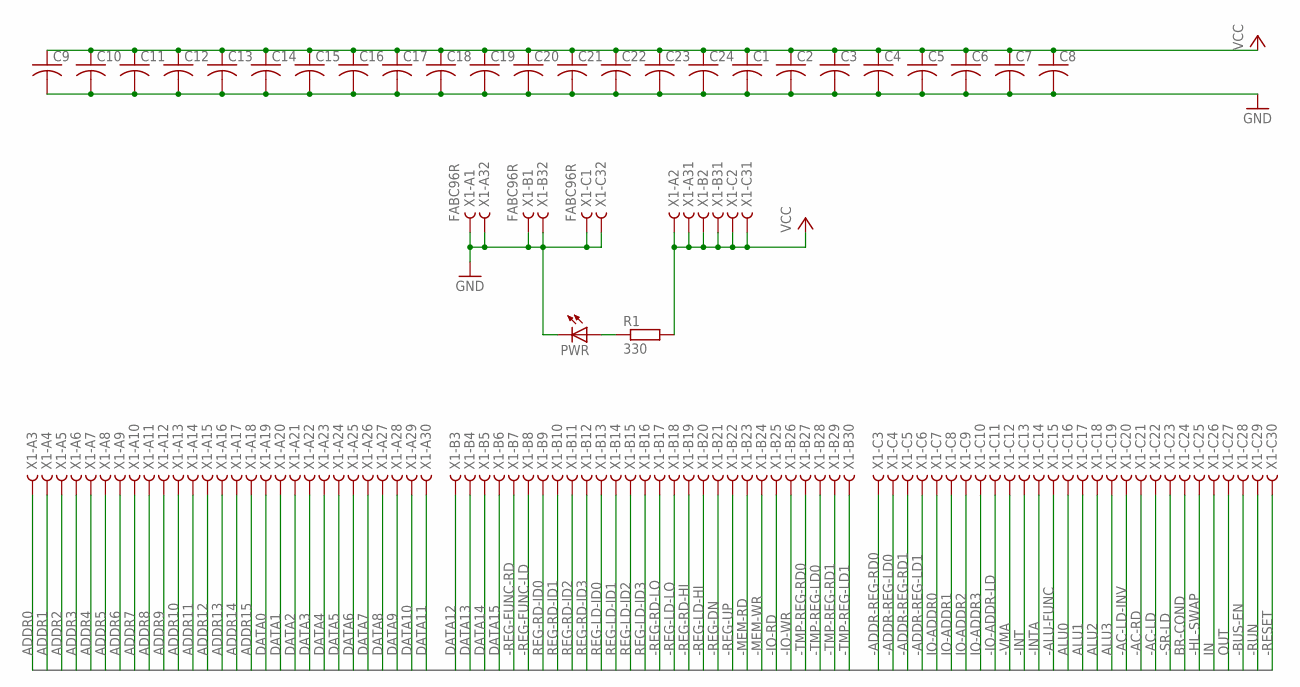
[picture p324: schematic Mem Register V1.0.sch, sheet 1, BUS]

Parts:
C1, C2, C3, C4, C5, C6, C7, C8, C9, C10, C11, C12, C13, C14, C15, C16, C17, C18, C19, C20, C21, C22, C23, C24: C-US025-025X050; C025-025X050
PWR: LED5MM
R1: 330; 0207/10
X1: FABC96R

Connections:
-AC-LD: X1.C22
-AC-LD-INV: X1.C20
-AC-RD: X1.C21
-ADDR-REG-LD0: X1.C4
-ADDR-REG-LD1: X1.C6
-ADDR-REG-RD0: X1.C3
-ADDR-REG-RD1: X1.C5
-ALU-FUNC: X1.C15
-BUS-EN: X1.C28; also elsewhere on the board
-HL-SWAP: X1.C25
-INT: X1.C13
-INTA: X1.C14
-IO-ADDR-LD: X1.C11
-IO-RD: X1.B25
-IO-WR: X1.B26
-MEM-RD: X1.B23; also elsewhere on the board
-MEM-WR: X1.B24; also elsewhere on the board
-REG-DN: X1.B21
-REG-FUNC-LD: X1.B8
-REG-FUNC-RD: X1.B7
-REG-LD-HI: X1.B20
-REG-LD-LO: X1.B18
-REG-RD-HI: X1.B19
-REG-RD-LO: X1.B17
-REG-UP: X1.B22
-RESET: X1.C30
-RUN: X1.C29
-SR-LD: X1.C23
-TMP-REG-LD0: X1.B28
-TMP-REG-LD1: X1.B30
-TMP-REG-RD0: X1.B27
-TMP-REG-RD1: X1.B29
-VMA: X1.C12; also elsewhere on the board
ADDR0: X1.A3; also elsewhere on the board
ADDR1: X1.A4; also elsewhere on the board
ADDR2: X1.A5; also elsewhere on the board
ADDR3: X1.A6; also elsewhere on the board
ADDR4: X1.A7; also elsewhere on the board
ADDR5: X1.A8; also elsewhere on the board
ADDR6: X1.A9; also elsewhere on the board
ADDR7: X1.A10; also elsewhere on the board
ADDR8: X1.A11; also elsewhere on the board
ADDR9: X1.A12; also elsewhere on the board
ADDR10: X1.A13; also elsewhere on the board
ADDR11: X1.A14; also elsewhere on the board
ADDR12: X1.A15; also elsewhere on the board
ADDR13: X1.A16; also elsewhere on the board
ADDR14: X1.A17; also elsewhere on the board
ADDR15: X1.A18; also elsewhere on the board
ALU0: X1.C16
ALU1: X1.C17
ALU2: X1.C18
ALU3: X1.C19
BR-COND: X1.C24
DATA0: X1.A19; also elsewhere on the board
DATA1: X1.A20; also elsewhere on the board
DATA2: X1.A21; also elsewhere on the board
DATA3: X1.A22; also elsewhere on the board
DATA4: X1.A23; also elsewhere on the board
DATA5: X1.A24; also elsewhere on the board
DATA6: X1.A25; also elsewhere on the board
DATA7: X1.A26; also elsewhere on the board
DATA8: X1.A27
DATA9: X1.A28
DATA10: X1.A29
DATA11: X1.A30
DATA12: X1.B3
DATA13: X1.B4
DATA14: X1.B5
DATA15: X1.B6
GND: C1.2, C2.2, C3.2, C4.2, C5.2, C6.2, C7.2, C8.2, C9.2, C10.2, C11.2, C12.2, C13.2, C14.2, C15.2, C16.2, C17.2, C18.2, C19.2, C20.2, C21.2, C22.2, C23.2, C24.2, PWR.K (C), X1.A1, X1.A32, X1.B1, X1.B32, X1.C1, X1.C32; also elsewhere on the board
IN: X1.C26
IO-ADDR0: X1.C7
IO-ADDR1: X1.C8
IO-ADDR2: X1.C9
IO-ADDR3: X1.C10
unnamed: PWR.A, R1.1
OUT: X1.C27
REG-LD-ID0: X1.B13
REG-LD-ID1: X1.B14
REG-LD-ID2: X1.B15
REG-LD-ID3: X1.B16
REG-RD-ID0: X1.B9
REG-RD-ID1: X1.B10
REG-RD-ID2: X1.B11
REG-RD-ID3: X1.B12
VCC: C1.1, C2.1, C3.1, C4.1, C5.1, C6.1, C7.1, C8.1, C9.1, C10.1, C11.1, C12.1, C13.1, C14.1, C15.1, C16.1, C17.1, C18.1, C19.1, C20.1, C21.1, C22.1, C23.1, C24.1, R1.2, X1.A2, X1.A31, X1.B2, X1.B31, X1.C2, X1.C31; also elsewhere on the board

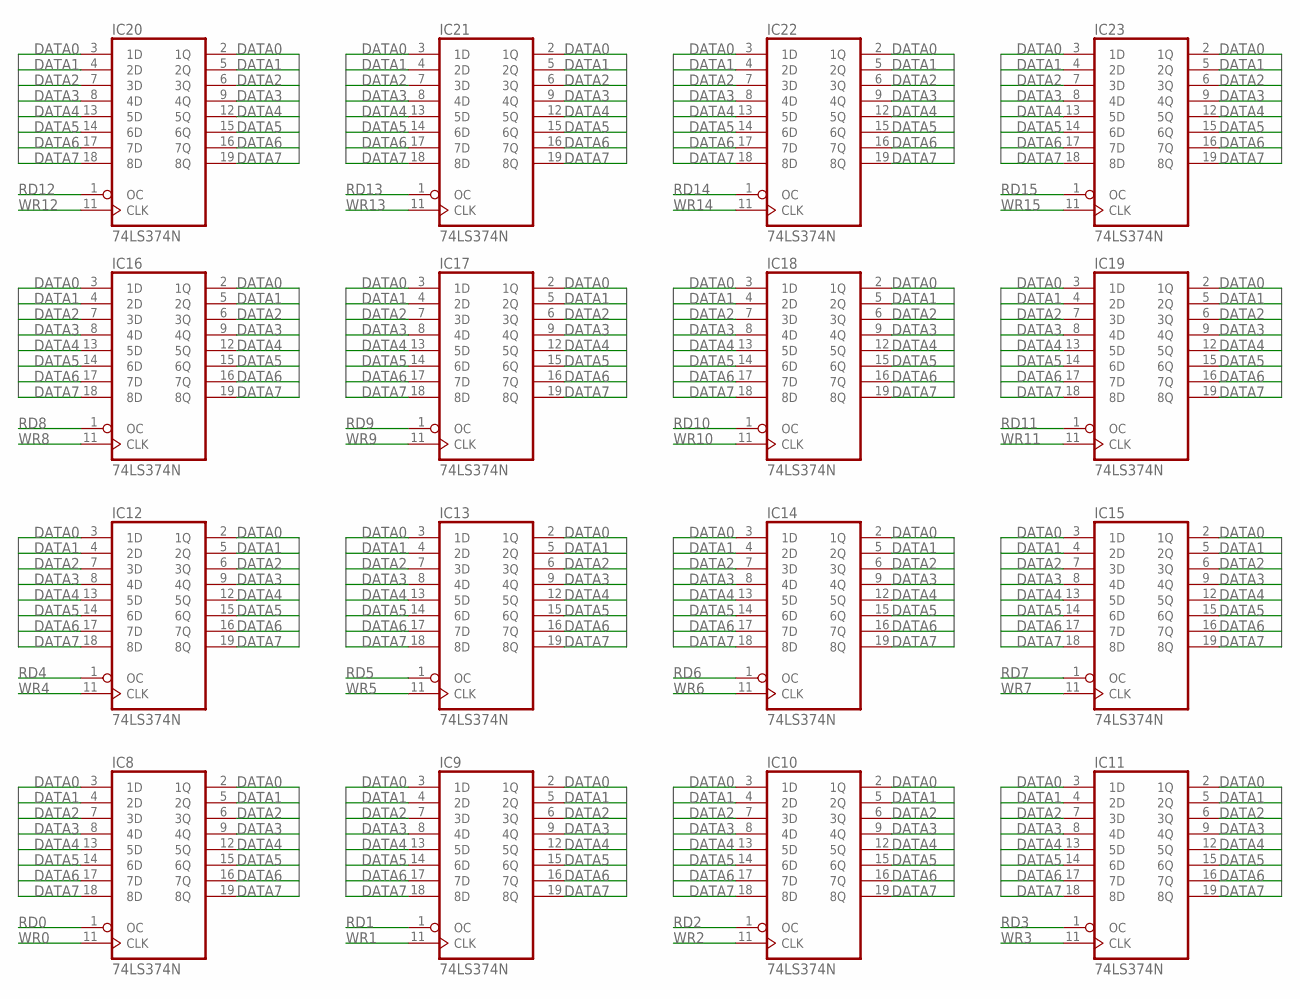
[picture p325: schematic Mem Register V1.0.sch, sheet 2]

Parts:
IC8, IC9, IC10, IC11, IC12, IC13, IC14, IC15, IC16, IC17, IC18, IC19, IC20, IC21, IC22, IC23: 74LS374N; DIL20

Connections:
DATA0: IC8.2 (1Q), IC8.3 (1D), IC9.2 (1Q), IC9.3 (1D), IC10.2 (1Q), IC10.3 (1D), IC11.2 (1Q), IC11.3 (1D), IC12.2 (1Q), IC12.3 (1D), IC13.2 (1Q), IC13.3 (1D), IC14.2 (1Q), IC14.3 (1D), IC15.2 (1Q), IC15.3 (1D), IC16.2 (1Q), IC16.3 (1D), IC17.2 (1Q), IC17.3 (1D), IC18.2 (1Q), IC18.3 (1D), IC19.2 (1Q), IC19.3 (1D), IC20.2 (1Q), IC20.3 (1D), IC21.2 (1Q), IC21.3 (1D), IC22.2 (1Q), IC22.3 (1D), IC23.2 (1Q), IC23.3 (1D); also elsewhere on the board
DATA1: IC8.4 (2D), IC8.5 (2Q), IC9.4 (2D), IC9.5 (2Q), IC10.4 (2D), IC10.5 (2Q), IC11.4 (2D), IC11.5 (2Q), IC12.4 (2D), IC12.5 (2Q), IC13.4 (2D), IC13.5 (2Q), IC14.4 (2D), IC14.5 (2Q), IC15.4 (2D), IC15.5 (2Q), IC16.4 (2D), IC16.5 (2Q), IC17.4 (2D), IC17.5 (2Q), IC18.4 (2D), IC18.5 (2Q), IC19.4 (2D), IC19.5 (2Q), IC20.4 (2D), IC20.5 (2Q), IC21.4 (2D), IC21.5 (2Q), IC22.4 (2D), IC22.5 (2Q), IC23.4 (2D), IC23.5 (2Q); also elsewhere on the board
DATA2: IC8.6 (3Q), IC8.7 (3D), IC9.6 (3Q), IC9.7 (3D), IC10.6 (3Q), IC10.7 (3D), IC11.6 (3Q), IC11.7 (3D), IC12.6 (3Q), IC12.7 (3D), IC13.6 (3Q), IC13.7 (3D), IC14.6 (3Q), IC14.7 (3D), IC15.6 (3Q), IC15.7 (3D), IC16.6 (3Q), IC16.7 (3D), IC17.6 (3Q), IC17.7 (3D), IC18.6 (3Q), IC18.7 (3D), IC19.6 (3Q), IC19.7 (3D), IC20.6 (3Q), IC20.7 (3D), IC21.6 (3Q), IC21.7 (3D), IC22.6 (3Q), IC22.7 (3D), IC23.6 (3Q), IC23.7 (3D); also elsewhere on the board
DATA3: IC8.8 (4D), IC8.9 (4Q), IC9.8 (4D), IC9.9 (4Q), IC10.8 (4D), IC10.9 (4Q), IC11.8 (4D), IC11.9 (4Q), IC12.8 (4D), IC12.9 (4Q), IC13.8 (4D), IC13.9 (4Q), IC14.8 (4D), IC14.9 (4Q), IC15.8 (4D), IC15.9 (4Q), IC16.8 (4D), IC16.9 (4Q), IC17.8 (4D), IC17.9 (4Q), IC18.8 (4D), IC18.9 (4Q), IC19.8 (4D), IC19.9 (4Q), IC20.8 (4D), IC20.9 (4Q), IC21.8 (4D), IC21.9 (4Q), IC22.8 (4D), IC22.9 (4Q), IC23.8 (4D), IC23.9 (4Q); also elsewhere on the board
DATA4: IC8.12 (5Q), IC8.13 (5D), IC9.12 (5Q), IC9.13 (5D), IC10.12 (5Q), IC10.13 (5D), IC11.12 (5Q), IC11.13 (5D), IC12.12 (5Q), IC12.13 (5D), IC13.12 (5Q), IC13.13 (5D), IC14.12 (5Q), IC14.13 (5D), IC15.12 (5Q), IC15.13 (5D), IC16.12 (5Q), IC16.13 (5D), IC17.12 (5Q), IC17.13 (5D), IC18.12 (5Q), IC18.13 (5D), IC19.12 (5Q), IC19.13 (5D), IC20.12 (5Q), IC20.13 (5D), IC21.12 (5Q), IC21.13 (5D), IC22.12 (5Q), IC22.13 (5D), IC23.12 (5Q), IC23.13 (5D); also elsewhere on the board
DATA5: IC8.14 (6D), IC8.15 (6Q), IC9.14 (6D), IC9.15 (6Q), IC10.14 (6D), IC10.15 (6Q), IC11.14 (6D), IC11.15 (6Q), IC12.14 (6D), IC12.15 (6Q), IC13.14 (6D), IC13.15 (6Q), IC14.14 (6D), IC14.15 (6Q), IC15.14 (6D), IC15.15 (6Q), IC16.14 (6D), IC16.15 (6Q), IC17.14 (6D), IC17.15 (6Q), IC18.14 (6D), IC18.15 (6Q), IC19.14 (6D), IC19.15 (6Q), IC20.14 (6D), IC20.15 (6Q), IC21.14 (6D), IC21.15 (6Q), IC22.14 (6D), IC22.15 (6Q), IC23.14 (6D), IC23.15 (6Q); also elsewhere on the board
DATA6: IC8.16 (7Q), IC8.17 (7D), IC9.16 (7Q), IC9.17 (7D), IC10.16 (7Q), IC10.17 (7D), IC11.16 (7Q), IC11.17 (7D), IC12.16 (7Q), IC12.17 (7D), IC13.16 (7Q), IC13.17 (7D), IC14.16 (7Q), IC14.17 (7D), IC15.16 (7Q), IC15.17 (7D), IC16.16 (7Q), IC16.17 (7D), IC17.16 (7Q), IC17.17 (7D), IC18.16 (7Q), IC18.17 (7D), IC19.16 (7Q), IC19.17 (7D), IC20.16 (7Q), IC20.17 (7D), IC21.16 (7Q), IC21.17 (7D), IC22.16 (7Q), IC22.17 (7D), IC23.16 (7Q), IC23.17 (7D); also elsewhere on the board
DATA7: IC8.18 (8D), IC8.19 (8Q), IC9.18 (8D), IC9.19 (8Q), IC10.18 (8D), IC10.19 (8Q), IC11.18 (8D), IC11.19 (8Q), IC12.18 (8D), IC12.19 (8Q), IC13.18 (8D), IC13.19 (8Q), IC14.18 (8D), IC14.19 (8Q), IC15.18 (8D), IC15.19 (8Q), IC16.18 (8D), IC16.19 (8Q), IC17.18 (8D), IC17.19 (8Q), IC18.18 (8D), IC18.19 (8Q), IC19.18 (8D), IC19.19 (8Q), IC20.18 (8D), IC20.19 (8Q), IC21.18 (8D), IC21.19 (8Q), IC22.18 (8D), IC22.19 (8Q), IC23.18 (8D), IC23.19 (8Q); also elsewhere on the board
GND: IC8.10 (GND), IC9.10 (GND), IC10.10 (GND), IC11.10 (GND), IC12.10 (GND), IC13.10 (GND), IC14.10 (GND), IC15.10 (GND), IC16.10 (GND), IC17.10 (GND), IC18.10 (GND), IC19.10 (GND), IC20.10 (GND), IC21.10 (GND), IC22.10 (GND), IC23.10 (GND); also elsewhere on the board
RD0: IC8.1 (OC); also elsewhere on the board
RD1: IC9.1 (OC); also elsewhere on the board
RD2: IC10.1 (OC); also elsewhere on the board
RD3: IC11.1 (OC); also elsewhere on the board
RD4: IC12.1 (OC); also elsewhere on the board
RD5: IC13.1 (OC); also elsewhere on the board
RD6: IC14.1 (OC); also elsewhere on the board
RD7: IC15.1 (OC); also elsewhere on the board
RD8: IC16.1 (OC); also elsewhere on the board
RD9: IC17.1 (OC); also elsewhere on the board
RD10: IC18.1 (OC); also elsewhere on the board
RD11: IC19.1 (OC); also elsewhere on the board
RD12: IC20.1 (OC); also elsewhere on the board
RD13: IC21.1 (OC); also elsewhere on the board
RD14: IC22.1 (OC); also elsewhere on the board
RD15: IC23.1 (OC); also elsewhere on the board
VCC: IC8.20 (VCC), IC9.20 (VCC), IC10.20 (VCC), IC11.20 (VCC), IC12.20 (VCC), IC13.20 (VCC), IC14.20 (VCC), IC15.20 (VCC), IC16.20 (VCC), IC17.20 (VCC), IC18.20 (VCC), IC19.20 (VCC), IC20.20 (VCC), IC21.20 (VCC), IC22.20 (VCC), IC23.20 (VCC); also elsewhere on the board
WR0: IC8.11 (CLK); also elsewhere on the board
WR1: IC9.11 (CLK); also elsewhere on the board
WR2: IC10.11 (CLK); also elsewhere on the board
WR3: IC11.11 (CLK); also elsewhere on the board
WR4: IC12.11 (CLK); also elsewhere on the board
WR5: IC13.11 (CLK); also elsewhere on the board
WR6: IC14.11 (CLK); also elsewhere on the board
WR7: IC15.11 (CLK); also elsewhere on the board
WR8: IC16.11 (CLK); also elsewhere on the board
WR9: IC17.11 (CLK); also elsewhere on the board
WR10: IC18.11 (CLK); also elsewhere on the board
WR11: IC19.11 (CLK); also elsewhere on the board
WR12: IC20.11 (CLK); also elsewhere on the board
WR13: IC21.11 (CLK); also elsewhere on the board
WR14: IC22.11 (CLK); also elsewhere on the board
WR15: IC23.11 (CLK); also elsewhere on the board
