ksr/YACC1-D/hardware/cards/mem-register/eagle/v1.0/Mem Register V1.0.brd

## EAGLE design hardware/cards/mem-register/eagle/v1.0/Mem Register V1.0.brd (continued)

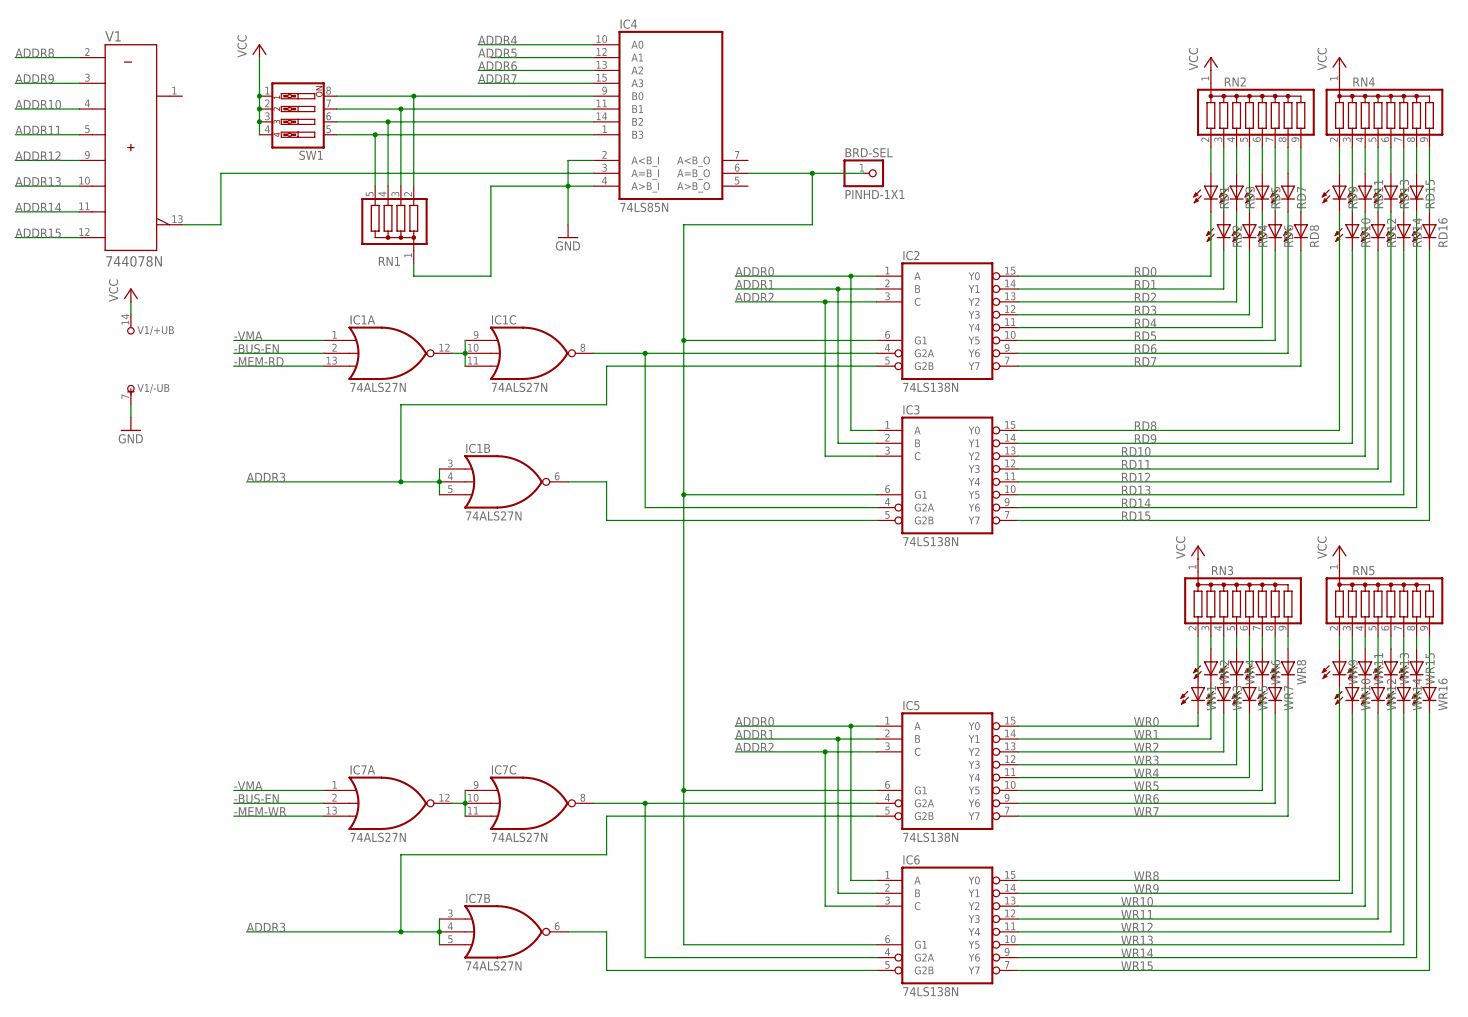
[picture p326: schematic Mem Register V1.0.sch, sheet 3]

Parts:
BRD-SEL: PINHD-1X1; 1X01
IC1, IC7: 74ALS27N; DIL14
IC2, IC3, IC5, IC6: 74LS138N; DIL16
IC4: 74LS85N; DIL16
RD1, RD2, RD3, RD4, RD5, RD6, RD7, RD8, RD9, RD10, RD11, RD12, RD13, RD14, RD15, RD16: LED3MM
RN1: G04R; SIL5
RN2, RN3, RN4, RN5: G08R; SIL9
SW1: SW_DIP-4; EDG-04
V1: 744078N; DIL14
WR1, WR2, WR3, WR4, WR5, WR6, WR7, WR8, WR9, WR10, WR11, WR12, WR13, WR14, WR15, WR16: LED3MM

Connections:
-BUS-EN: IC1.2 (I1), IC7.2 (I1); also elsewhere on the board
-MEM-RD: IC1.13 (I2); also elsewhere on the board
-MEM-WR: IC7.13 (I2); also elsewhere on the board
-VMA: IC1.1 (I0), IC7.1 (I0); also elsewhere on the board
ADDR0: IC2.1 (A), IC3.1 (A), IC5.1 (A), IC6.1 (A); also elsewhere on the board
ADDR1: IC2.2 (B), IC3.2 (B), IC5.2 (B), IC6.2 (B); also elsewhere on the board
ADDR2: IC2.3 (C), IC3.3 (C), IC5.3 (C), IC6.3 (C); also elsewhere on the board
ADDR3: IC1.3 (I0), IC1.4 (I1), IC1.5 (I2), IC2.5 (G2B), IC5.5 (G2B), IC7.3 (I0), IC7.4 (I1), IC7.5 (I2); also elsewhere on the board
ADDR4: IC4.10 (A0); also elsewhere on the board
ADDR5: IC4.12 (A1); also elsewhere on the board
ADDR6: IC4.13 (A2); also elsewhere on the board
ADDR7: IC4.15 (A3); also elsewhere on the board
ADDR8: V1.2 (A); also elsewhere on the board
ADDR9: V1.3 (B); also elsewhere on the board
ADDR10: V1.4 (C); also elsewhere on the board
ADDR11: V1.5 (D); also elsewhere on the board
ADDR12: V1.9 (E); also elsewhere on the board
ADDR13: V1.10 (F); also elsewhere on the board
ADDR14: V1.11 (G); also elsewhere on the board
ADDR15: V1.12 (H); also elsewhere on the board
GND: IC1.7 (GND), IC2.8 (GND), IC3.8 (GND), IC4.2 (A<B_I), IC4.4 (A>B_I), IC4.8 (GND), IC5.8 (GND), IC6.8 (GND), IC7.7 (GND), RN1.1, V1.7 (-UB); also elsewhere on the board
unnamed: RD1.A, RN2.2
unnamed: IC7.9 (I0), IC7.10 (I1), IC7.11 (I2), IC7.12 (O)
unnamed: IC6.5 (G2B), IC7.6 (O)
unnamed: IC5.4 (G2A), IC6.4 (G2A), IC7.8 (O)
unnamed: RD3.A, RN2.4
unnamed: BRD-SEL.1, IC2.6 (G1), IC3.6 (G1), IC4.6 (A=B_O), IC5.6 (G1), IC6.6 (G1)
unnamed: RD2.A, RN2.3
unnamed: IC4.3 (A=B_I), V1.13 (W)
unnamed: RD9.A, RN4.2
unnamed: RD4.A, RN2.5
unnamed: RD5.A, RN2.6
unnamed: RD7.A, RN2.8
unnamed: RD8.A, RN2.9
unnamed: RD6.A, RN2.7
unnamed: RD10.A, RN4.3
unnamed: RD11.A, RN4.4
unnamed: RD12.A, RN4.5
unnamed: IC1.9 (I0), IC1.10 (I1), IC1.11 (I2), IC1.12 (O)
unnamed: RD13.A, RN4.6
unnamed: RD14.A, RN4.7
unnamed: RD15.A, RN4.8
unnamed: RD16.A, RN4.9
unnamed: RN3.2, WR1.A
unnamed: RN3.3, WR2.A
unnamed: RN3.4, WR3.A
unnamed: RN3.5, WR4.A
unnamed: IC4.9 (B0), RN1.2, SW1.8
unnamed: RN3.7, WR6.A
unnamed: RN3.6, WR5.A
unnamed: RN3.8, WR7.A
unnamed: RN3.9, WR8.A
unnamed: RN5.2, WR9.A
unnamed: RN5.4, WR11.A
unnamed: RN5.6, WR13.A
unnamed: RN5.8, WR15.A
unnamed: IC1.6 (O), IC3.5 (G2B)
unnamed: RN5.9, WR16.A
unnamed: RN5.7, WR14.A
unnamed: RN5.5, WR12.A
unnamed: RN5.3, WR10.A
unnamed: IC4.11 (B1), RN1.3, SW1.7
unnamed: IC4.14 (B2), RN1.4, SW1.6
unnamed: IC4.1 (B3), RN1.5, SW1.5
unnamed: IC1.8 (O), IC2.4 (G2A), IC3.4 (G2A)
RD0: IC2.15 (Y0), RD1.K (C); also elsewhere on the board
RD1: IC2.14 (Y1), RD2.K (C); also elsewhere on the board
RD2: IC2.13 (Y2), RD3.K (C); also elsewhere on the board
RD3: IC2.12 (Y3), RD4.K (C); also elsewhere on the board
RD4: IC2.11 (Y4), RD5.K (C); also elsewhere on the board
RD5: IC2.10 (Y5), RD6.K (C); also elsewhere on the board
RD6: IC2.9 (Y6), RD7.K (C); also elsewhere on the board
RD7: IC2.7 (Y7), RD8.K (C); also elsewhere on the board
RD8: IC3.15 (Y0), RD9.K (C); also elsewhere on the board
RD9: IC3.14 (Y1), RD10.K (C); also elsewhere on the board
RD10: IC3.13 (Y2), RD11.K (C); also elsewhere on the board
RD11: IC3.12 (Y3), RD12.K (C); also elsewhere on the board
RD12: IC3.11 (Y4), RD13.K (C); also elsewhere on the board
RD13: IC3.10 (Y5), RD14.K (C); also elsewhere on the board
RD14: IC3.9 (Y6), RD15.K (C); also elsewhere on the board
RD15: IC3.7 (Y7), RD16.K (C); also elsewhere on the board
VCC: IC1.14 (VCC), IC2.16 (VCC), IC3.16 (VCC), IC4.16 (VCC), IC5.16 (VCC), IC6.16 (VCC), IC7.14 (VCC), RN2.1, RN3.1, RN4.1, RN5.1, SW1.1, SW1.2, SW1.3, SW1.4, V1.14 (+UB); also elsewhere on the board
WR0: IC5.15 (Y0), WR1.K (C); also elsewhere on the board
WR1: IC5.14 (Y1), WR2.K (C); also elsewhere on the board
WR2: IC5.13 (Y2), WR3.K (C); also elsewhere on the board
WR3: IC5.12 (Y3), WR4.K (C); also elsewhere on the board
WR4: IC5.11 (Y4), WR5.K (C); also elsewhere on the board
WR5: IC5.10 (Y5), WR6.K (C); also elsewhere on the board
WR6: IC5.9 (Y6), WR7.K (C); also elsewhere on the board
WR7: IC5.7 (Y7), WR8.K (C); also elsewhere on the board
WR8: IC6.15 (Y0), WR9.K (C); also elsewhere on the board
WR9: IC6.14 (Y1), WR10.K (C); also elsewhere on the board
WR10: IC6.13 (Y2), WR11.K (C); also elsewhere on the board
WR11: IC6.12 (Y3), WR12.K (C); also elsewhere on the board
WR12: IC6.11 (Y4), WR13.K (C); also elsewhere on the board
WR13: IC6.10 (Y5), WR14.K (C); also elsewhere on the board
WR14: IC6.9 (Y6), WR15.K (C); also elsewhere on the board
WR15: IC6.7 (Y7), WR16.K (C); also elsewhere on the board

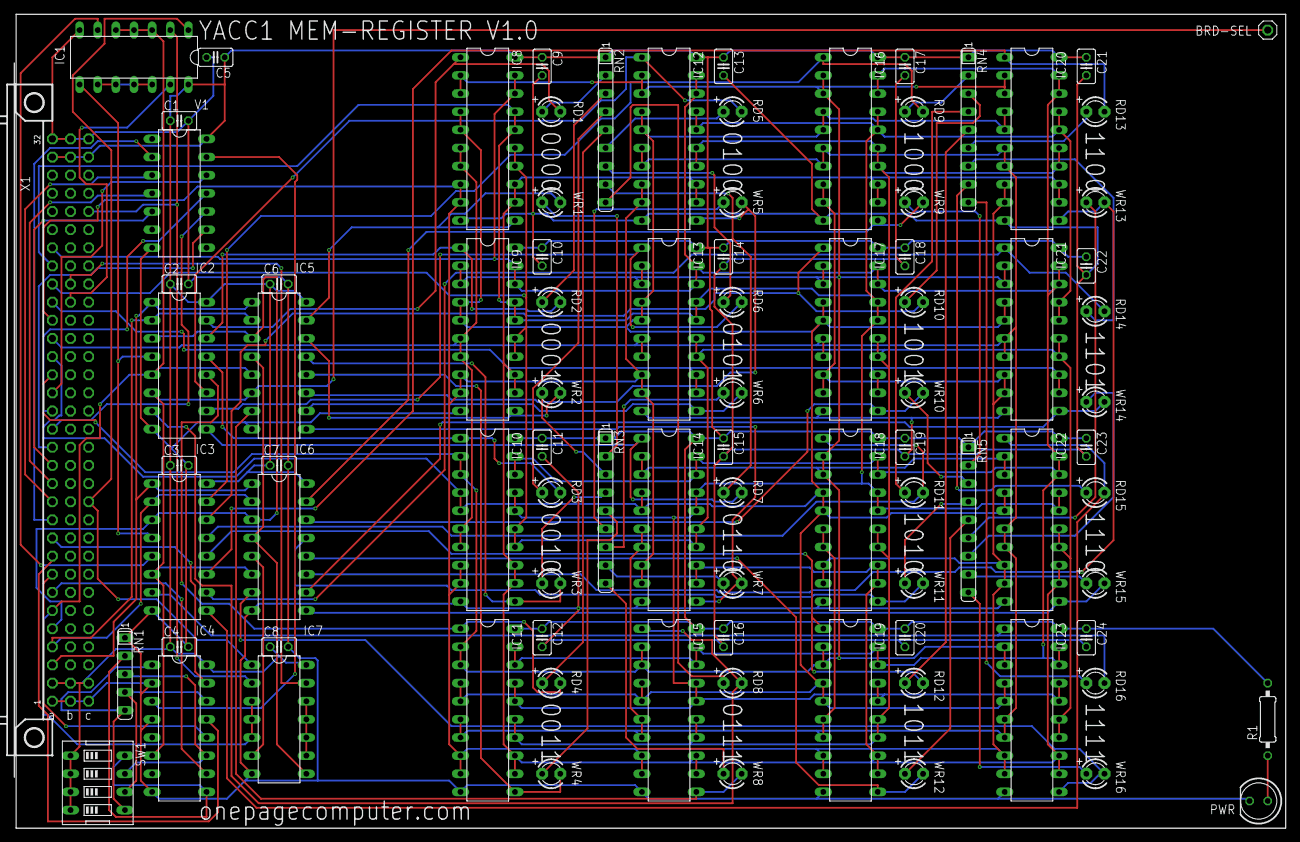
[picture p327: board Mem Register V1.0.brd from above]

Board: 2 copper layers, 177.8 x 114.0 mm, 90 parts (0 on the bottom side), 107 nets.
