ksr/YACC1-D/hardware/cards/register/eagle/v1.1/Index Registers - 1.1.brd

## EAGLE design hardware/cards/register/eagle/v1.1/Index Registers - 1.1.brd (continued)

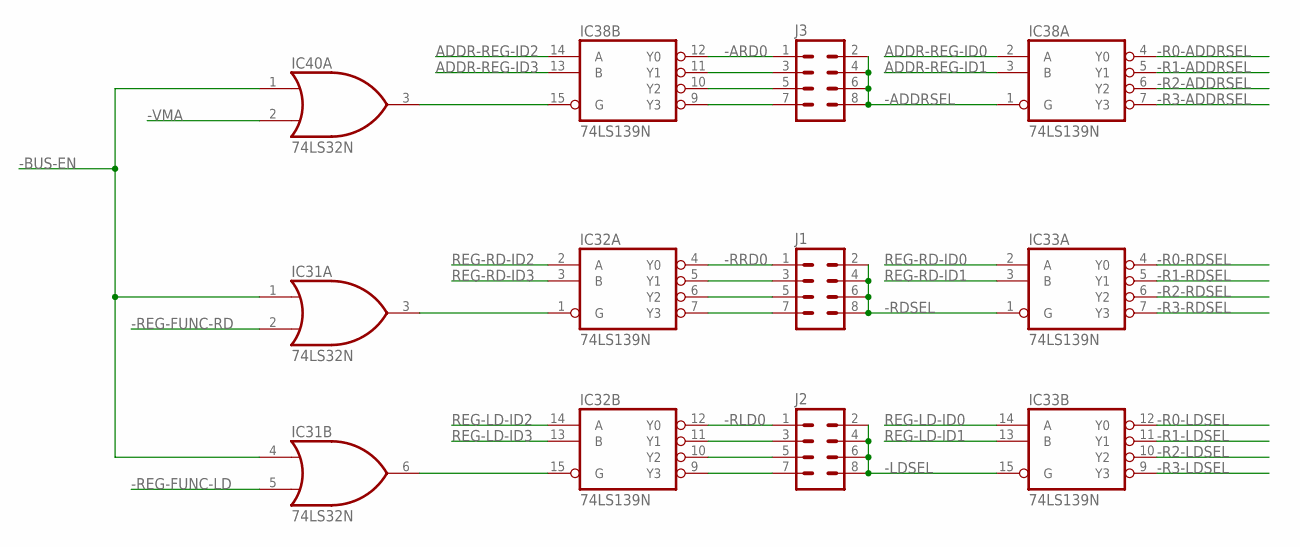
[picture p333: schematic Index Registers - 1.1.sch, sheet 6, Select Logic]

Parts:
IC31, IC40: 74LS32N; DIL14
IC32, IC33, IC38: 74LS139N; DIL16
J1, J2, J3: M04X2; 2X4

Connections:
-ADDRSEL: IC38.1 (G), J3.2, J3.4, J3.6, J3.8
-ARD0: IC38.12 (Y0), J3.1
-BUS-EN: IC31.1 (I0), IC31.4 (I0), IC40.1 (I0); also elsewhere on the board
-LDSEL: IC33.15 (G), J2.2, J2.4, J2.6, J2.8; also elsewhere on the board
-R0-ADDRSEL: IC38.4 (Y0); also elsewhere on the board
-R0-LDSEL: IC33.12 (Y0); also elsewhere on the board
-R0-RDSEL: IC33.4 (Y0); also elsewhere on the board
-R1-ADDRSEL: IC38.5 (Y1); also elsewhere on the board
-R1-LDSEL: IC33.11 (Y1); also elsewhere on the board
-R1-RDSEL: IC33.5 (Y1); also elsewhere on the board
-R2-ADDRSEL: IC38.6 (Y2); also elsewhere on the board
-R2-LDSEL: IC33.10 (Y2); also elsewhere on the board
-R2-RDSEL: IC33.6 (Y2); also elsewhere on the board
-R3-ADDRSEL: IC38.7 (Y3); also elsewhere on the board
-R3-LDSEL: IC33.9 (Y3); also elsewhere on the board
-R3-RDSEL: IC33.7 (Y3); also elsewhere on the board
-RDSEL: IC33.1 (G), J1.2, J1.4, J1.6, J1.8; also elsewhere on the board
-REG-FUNC-LD: IC31.5 (I1); also elsewhere on the board
-REG-FUNC-RD: IC31.2 (I1); also elsewhere on the board
-RLD0: IC32.12 (Y0), J2.1
-RRD0: IC32.4 (Y0), J1.1
-VMA: IC40.2 (I1); also elsewhere on the board
ADDR-REG-ID0: IC38.2 (A); also elsewhere on the board
ADDR-REG-ID1: IC38.3 (B); also elsewhere on the board
ADDR-REG-ID2: IC38.14 (A); also elsewhere on the board
ADDR-REG-ID3: IC38.13 (B); also elsewhere on the board
GND: IC31.7 (GND), IC32.8 (GND), IC33.8 (GND), IC38.8 (GND), IC40.7 (GND); also elsewhere on the board
unnamed: IC31.3 (O), IC32.1 (G)
unnamed: IC31.6 (O), IC32.15 (G)
unnamed: IC32.5 (Y1), J1.3
unnamed: IC38.15 (G), IC40.3 (O)
unnamed: IC32.6 (Y2), J1.5
unnamed: IC32.7 (Y3), J1.7
unnamed: IC32.11 (Y1), J2.3
unnamed: IC32.10 (Y2), J2.5
unnamed: IC32.9 (Y3), J2.7
unnamed: IC38.11 (Y1), J3.3
unnamed: IC38.10 (Y2), J3.5
unnamed: IC38.9 (Y3), J3.7
REG-LD-ID0: IC33.14 (A); also elsewhere on the board
REG-LD-ID1: IC33.13 (B); also elsewhere on the board
REG-LD-ID2: IC32.14 (A); also elsewhere on the board
REG-LD-ID3: IC32.13 (B); also elsewhere on the board
REG-RD-ID0: IC33.2 (A); also elsewhere on the board
REG-RD-ID1: IC33.3 (B); also elsewhere on the board
REG-RD-ID2: IC32.2 (A); also elsewhere on the board
REG-RD-ID3: IC32.3 (B); also elsewhere on the board
VCC: IC31.14 (VCC), IC32.16 (VCC), IC33.16 (VCC), IC38.16 (VCC), IC40.14 (VCC); also elsewhere on the board

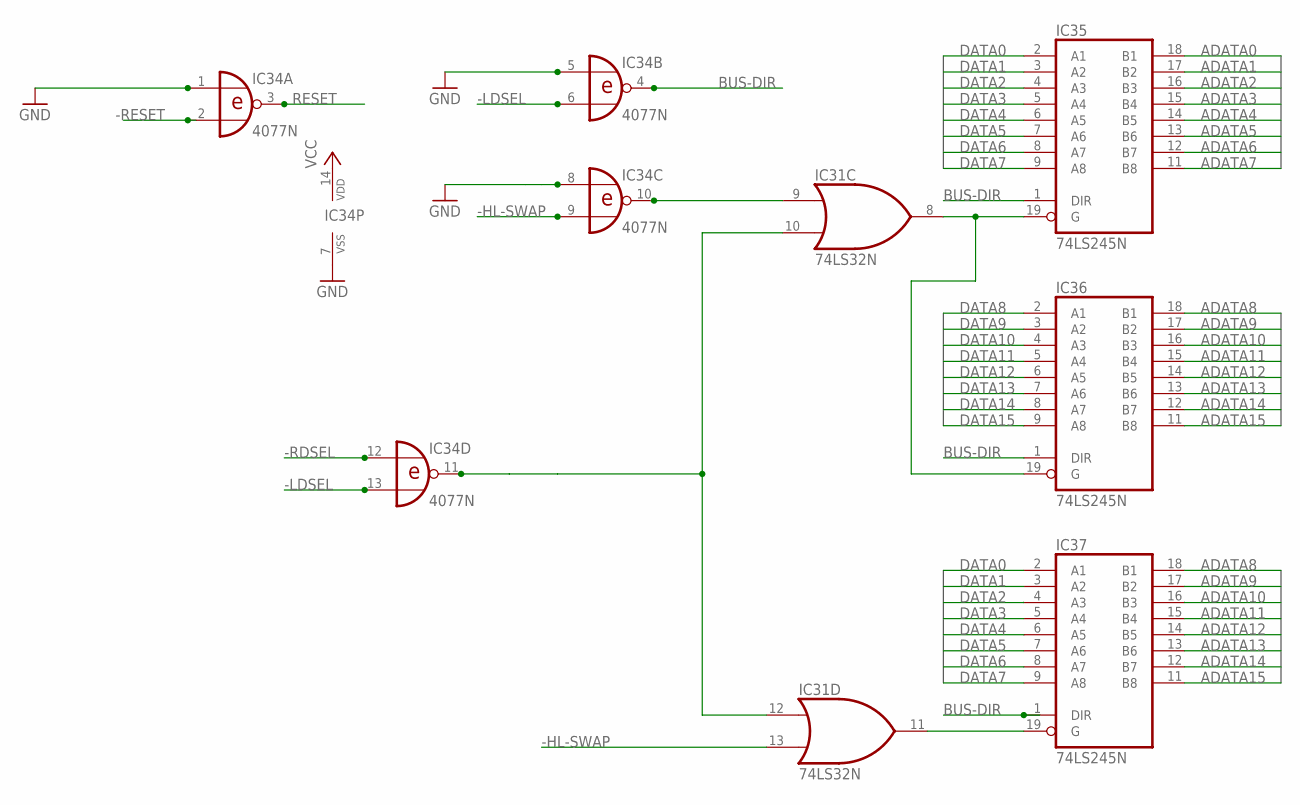
[picture p334: schematic Index Registers - 1.1.sch, sheet 7, bus buffering]

Parts:
IC31: 74LS32N; DIL14
IC34: 4077N; DIL14
IC35, IC36, IC37: 74LS245N; DIL20

Connections:
-HL-SWAP: IC31.13 (I1), IC34.9 (I1); also elsewhere on the board
-LDSEL: IC34.6 (I1), IC34.13 (I1); also elsewhere on the board
-RDSEL: IC34.12 (I0); also elsewhere on the board
-RESET: IC34.2 (I1); also elsewhere on the board
ADATA0: IC35.18 (B1); also elsewhere on the board
ADATA1: IC35.17 (B2); also elsewhere on the board
ADATA2: IC35.16 (B3); also elsewhere on the board
ADATA3: IC35.15 (B4); also elsewhere on the board
ADATA4: IC35.14 (B5); also elsewhere on the board
ADATA5: IC35.13 (B6); also elsewhere on the board
ADATA6: IC35.12 (B7); also elsewhere on the board
ADATA7: IC35.11 (B8); also elsewhere on the board
ADATA8: IC36.18 (B1), IC37.18 (B1); also elsewhere on the board
ADATA9: IC36.17 (B2), IC37.17 (B2); also elsewhere on the board
ADATA10: IC36.16 (B3), IC37.16 (B3); also elsewhere on the board
ADATA11: IC36.15 (B4), IC37.15 (B4); also elsewhere on the board
ADATA12: IC36.14 (B5), IC37.14 (B5); also elsewhere on the board
ADATA13: IC36.13 (B6), IC37.13 (B6); also elsewhere on the board
ADATA14: IC36.12 (B7), IC37.12 (B7); also elsewhere on the board
ADATA15: IC36.11 (B8), IC37.11 (B8); also elsewhere on the board
BUS-DIR: IC34.4 (O), IC35.1 (DIR), IC36.1 (DIR), IC37.1 (DIR)
DATA0: IC35.2 (A1), IC37.2 (A1); also elsewhere on the board
DATA1: IC35.3 (A2), IC37.3 (A2); also elsewhere on the board
DATA2: IC35.4 (A3), IC37.4 (A3); also elsewhere on the board
DATA3: IC35.5 (A4), IC37.5 (A4); also elsewhere on the board
DATA4: IC35.6 (A5), IC37.6 (A5); also elsewhere on the board
DATA5: IC35.7 (A6), IC37.7 (A6); also elsewhere on the board
DATA6: IC35.8 (A7), IC37.8 (A7); also elsewhere on the board
DATA7: IC35.9 (A8), IC37.9 (A8); also elsewhere on the board
DATA8: IC36.2 (A1); also elsewhere on the board
DATA9: IC36.3 (A2); also elsewhere on the board
DATA10: IC36.4 (A3); also elsewhere on the board
DATA11: IC36.5 (A4); also elsewhere on the board
DATA12: IC36.6 (A5); also elsewhere on the board
DATA13: IC36.7 (A6); also elsewhere on the board
DATA14: IC36.8 (A7); also elsewhere on the board
DATA15: IC36.9 (A8); also elsewhere on the board
GND: IC31.7 (GND), IC34.1 (I0), IC34.5 (I0), IC34.7 (VSS), IC34.8 (I0), IC35.10 (GND), IC36.10 (GND), IC37.10 (GND); also elsewhere on the board
unnamed: IC31.8 (O), IC35.19 (G), IC36.19 (G)
unnamed: IC31.11 (O), IC37.19 (G)
unnamed: IC31.9 (I0), IC34.10 (O)
unnamed: IC31.10 (I1), IC31.12 (I0), IC34.11 (O)
RESET: IC34.3 (O); also elsewhere on the board
VCC: IC31.14 (VCC), IC34.14 (VDD), IC35.20 (VCC), IC36.20 (VCC), IC37.20 (VCC); also elsewhere on the board

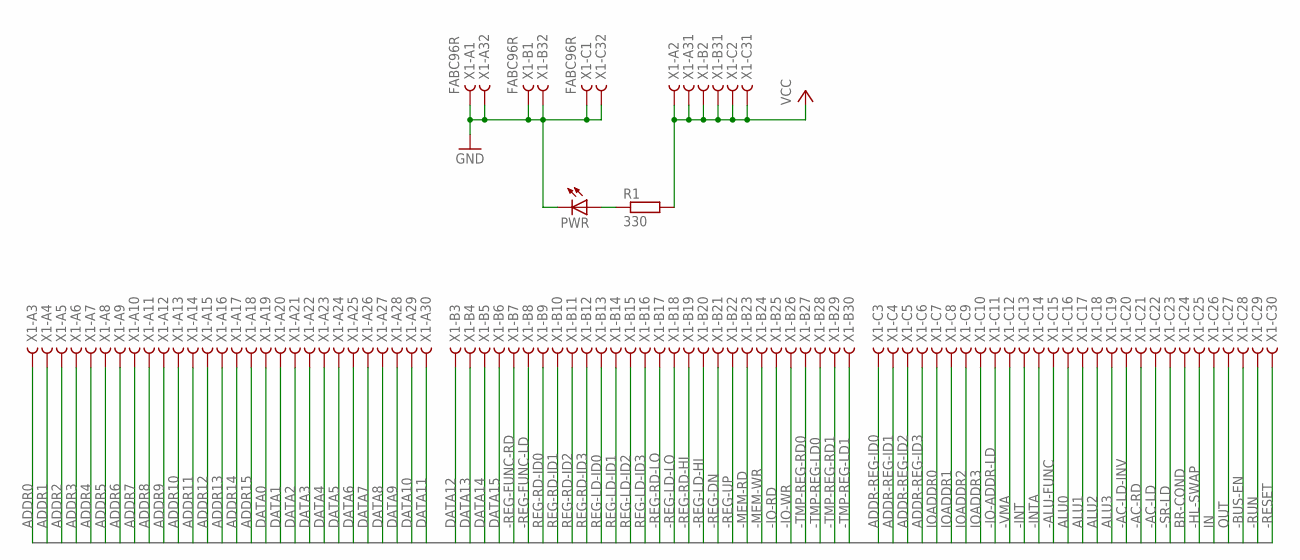
[picture p335: schematic Index Registers - 1.1.sch, sheet 8, BUS]

Parts:
PWR: LED5MM
R1: 330; 0207/10
X1: FABC96R

Connections:
-AC-LD: X1.C22
-AC-LD-INV: X1.C20
-AC-RD: X1.C21
-ALU-FUNC: X1.C15
-BUS-EN: X1.C28; also elsewhere on the board
-HL-SWAP: X1.C25; also elsewhere on the board
-INT: X1.C13
-INTA: X1.C14
-IO-ADDR-LD: X1.C11
-IO-RD: X1.B25
-IO-WR: X1.B26
-MEM-RD: X1.B23
-MEM-WR: X1.B24
-REG-DN: X1.B21; also elsewhere on the board
-REG-FUNC-LD: X1.B8; also elsewhere on the board
-REG-FUNC-RD: X1.B7; also elsewhere on the board
-REG-LD-HI: X1.B20; also elsewhere on the board
-REG-LD-LO: X1.B18; also elsewhere on the board
-REG-RD-HI: X1.B19; also elsewhere on the board
-REG-RD-LO: X1.B17; also elsewhere on the board
-REG-UP: X1.B22; also elsewhere on the board
-RESET: X1.C30; also elsewhere on the board
-RUN: X1.C29
-SR-LD: X1.C23
-TMP-REG-LD0: X1.B28
-TMP-REG-LD1: X1.B30
-TMP-REG-RD0: X1.B27
-TMP-REG-RD1: X1.B29
-VMA: X1.C12; also elsewhere on the board
ADDR0: X1.A3; also elsewhere on the board
ADDR1: X1.A4; also elsewhere on the board
ADDR2: X1.A5; also elsewhere on the board
ADDR3: X1.A6; also elsewhere on the board
ADDR4: X1.A7; also elsewhere on the board
ADDR5: X1.A8; also elsewhere on the board
ADDR6: X1.A9; also elsewhere on the board
ADDR7: X1.A10; also elsewhere on the board
ADDR8: X1.A11; also elsewhere on the board
ADDR9: X1.A12; also elsewhere on the board
ADDR10: X1.A13; also elsewhere on the board
ADDR11: X1.A14; also elsewhere on the board
ADDR12: X1.A15; also elsewhere on the board
ADDR13: X1.A16; also elsewhere on the board
ADDR14: X1.A17; also elsewhere on the board
ADDR15: X1.A18; also elsewhere on the board
ADDR-REG-ID0: X1.C3; also elsewhere on the board
ADDR-REG-ID1: X1.C4; also elsewhere on the board
ADDR-REG-ID2: X1.C5; also elsewhere on the board
ADDR-REG-ID3: X1.C6; also elsewhere on the board
ALU0: X1.C16
ALU1: X1.C17
ALU2: X1.C18
ALU3: X1.C19
BR-COND: X1.C24
DATA0: X1.A19; also elsewhere on the board
DATA1: X1.A20; also elsewhere on the board
DATA2: X1.A21; also elsewhere on the board
DATA3: X1.A22; also elsewhere on the board
DATA4: X1.A23; also elsewhere on the board
DATA5: X1.A24; also elsewhere on the board
DATA6: X1.A25; also elsewhere on the board
DATA7: X1.A26; also elsewhere on the board
DATA8: X1.A27; also elsewhere on the board
DATA9: X1.A28; also elsewhere on the board
DATA10: X1.A29; also elsewhere on the board
DATA11: X1.A30; also elsewhere on the board
DATA12: X1.B3; also elsewhere on the board
DATA13: X1.B4; also elsewhere on the board
DATA14: X1.B5; also elsewhere on the board
DATA15: X1.B6; also elsewhere on the board
GND: PWR.K (C), X1.A1, X1.A32, X1.B1, X1.B32, X1.C1, X1.C32; also elsewhere on the board
IN: X1.C26
IOADDR0: X1.C7
IOADDR1: X1.C8
IOADDR2: X1.C9
IOADDR3: X1.C10
unnamed: PWR.A, R1.1
OUT: X1.C27
REG-LD-ID0: X1.B13; also elsewhere on the board
REG-LD-ID1: X1.B14; also elsewhere on the board
REG-LD-ID2: X1.B15; also elsewhere on the board
REG-LD-ID3: X1.B16; also elsewhere on the board
REG-RD-ID0: X1.B9; also elsewhere on the board
REG-RD-ID1: X1.B10; also elsewhere on the board
REG-RD-ID2: X1.B11; also elsewhere on the board
REG-RD-ID3: X1.B12; also elsewhere on the board
VCC: R1.2, X1.A2, X1.A31, X1.B2, X1.B31, X1.C2, X1.C31; also elsewhere on the board

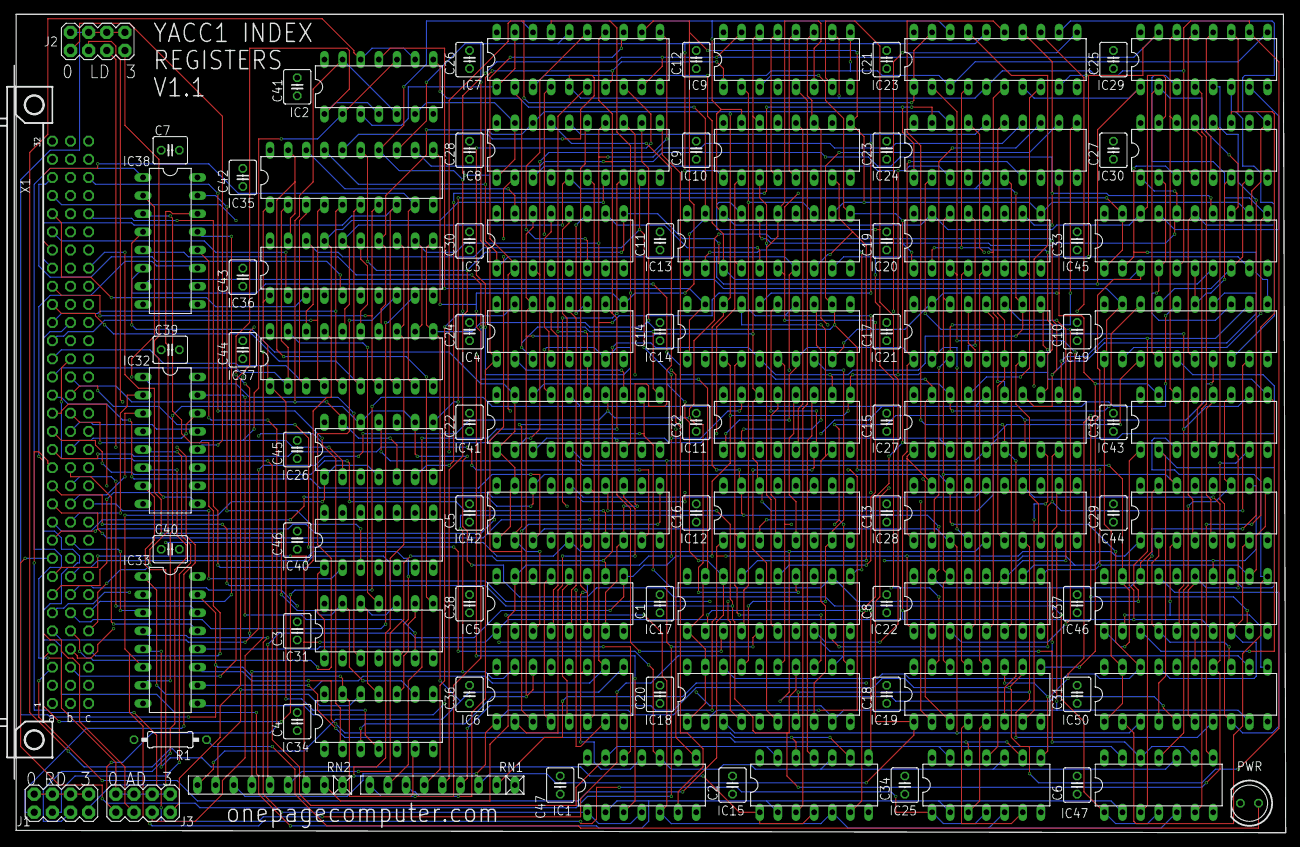
[picture p336: board Index Registers - 1.1.brd from above]

Board: 4 copper layers, 177.8 x 114.6 mm, 102 parts (0 on the bottom side), 223 nets.
