ksr/YACC1-D/hardware/cards/sequencer-memory/eagle/v2.1/Sequencer-Memory-V2.1.brd

## EAGLE design hardware/cards/sequencer-memory/eagle/v2.1/Sequencer-Memory-V2.1.brd (2026-09-20)

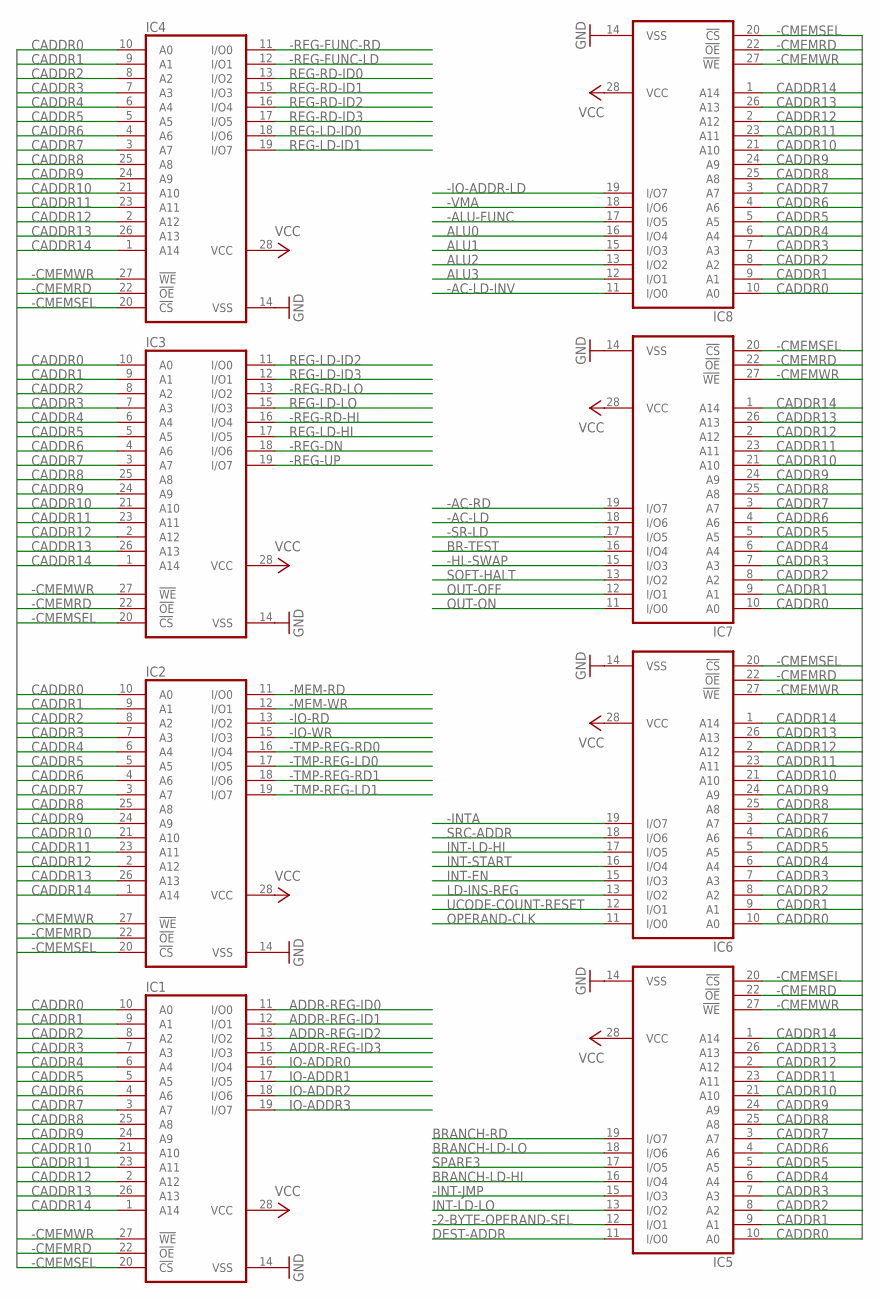
[picture p337: schematic Sequencer-Memory-V2.1.sch, sheet 1, Memory]

Parts:
IC1, IC2, IC3, IC4, IC5, IC6, IC7, IC8: 62256P; DIL28-6

Connections:
-2-BYTE-OPERAND-SEL: IC5.12 (I/O1); also elsewhere on the board
-AC-LD: IC7.18 (I/O6); also elsewhere on the board
-AC-LD-INV: IC8.11 (I/O0); also elsewhere on the board
-AC-RD: IC7.19 (I/O7); also elsewhere on the board
-ALU-FUNC: IC8.17 (I/O5); also elsewhere on the board
-CMEMRD: IC1.22 (!OE), IC2.22 (!OE), IC3.22 (!OE), IC4.22 (!OE), IC5.22 (!OE), IC6.22 (!OE), IC7.22 (!OE), IC8.22 (!OE); also elsewhere on the board
-CMEMSEL: IC1.20 (!CS), IC2.20 (!CS), IC3.20 (!CS), IC4.20 (!CS), IC5.20 (!CS), IC6.20 (!CS), IC7.20 (!CS), IC8.20 (!CS); also elsewhere on the board
-CMEMWR: IC1.27 (!WE), IC2.27 (!WE), IC3.27 (!WE), IC4.27 (!WE), IC5.27 (!WE), IC6.27 (!WE), IC7.27 (!WE), IC8.27 (!WE); also elsewhere on the board
-HL-SWAP: IC7.15 (I/O3); also elsewhere on the board
-INT-JMP: IC5.15 (I/O3); also elsewhere on the board
-INTA: IC6.19 (I/O7); also elsewhere on the board
-IO-ADDR-LD: IC8.19 (I/O7); also elsewhere on the board
-IO-RD: IC2.13 (I/O2); also elsewhere on the board
-IO-WR: IC2.15 (I/O3); also elsewhere on the board
-MEM-RD: IC2.11 (I/O0); also elsewhere on the board
-MEM-WR: IC2.12 (I/O1); also elsewhere on the board
-REG-DN: IC3.18 (I/O6); also elsewhere on the board
-REG-FUNC-LD: IC4.12 (I/O1); also elsewhere on the board
-REG-FUNC-RD: IC4.11 (I/O0); also elsewhere on the board
-REG-RD-HI: IC3.16 (I/O4); also elsewhere on the board
-REG-RD-LO: IC3.13 (I/O2); also elsewhere on the board
-REG-UP: IC3.19 (I/O7); also elsewhere on the board
-SR-LD: IC7.17 (I/O5); also elsewhere on the board
-TMP-REG-LD0: IC2.17 (I/O5); also elsewhere on the board
-TMP-REG-LD1: IC2.19 (I/O7); also elsewhere on the board
-TMP-REG-RD0: IC2.16 (I/O4); also elsewhere on the board
-TMP-REG-RD1: IC2.18 (I/O6); also elsewhere on the board
-VMA: IC8.18 (I/O6); also elsewhere on the board
ADDR-REG-ID0: IC1.11 (I/O0); also elsewhere on the board
ADDR-REG-ID1: IC1.12 (I/O1); also elsewhere on the board
ADDR-REG-ID2: IC1.13 (I/O2); also elsewhere on the board
ADDR-REG-ID3: IC1.15 (I/O3); also elsewhere on the board
ALU0: IC8.16 (I/O4); also elsewhere on the board
ALU1: IC8.15 (I/O3); also elsewhere on the board
ALU2: IC8.13 (I/O2); also elsewhere on the board
ALU3: IC8.12 (I/O1); also elsewhere on the board
BR-TEST: IC7.16 (I/O4); also elsewhere on the board
BRANCH-LD-HI: IC5.16 (I/O4); also elsewhere on the board
BRANCH-LD-LO: IC5.18 (I/O6); also elsewhere on the board
BRANCH-RD: IC5.19 (I/O7); also elsewhere on the board
CADDR0: IC1.10 (A0), IC2.10 (A0), IC3.10 (A0), IC4.10 (A0), IC5.10 (A0), IC6.10 (A0), IC7.10 (A0), IC8.10 (A0); also elsewhere on the board
CADDR1: IC1.9 (A1), IC2.9 (A1), IC3.9 (A1), IC4.9 (A1), IC5.9 (A1), IC6.9 (A1), IC7.9 (A1), IC8.9 (A1); also elsewhere on the board
CADDR2: IC1.8 (A2), IC2.8 (A2), IC3.8 (A2), IC4.8 (A2), IC5.8 (A2), IC6.8 (A2), IC7.8 (A2), IC8.8 (A2); also elsewhere on the board
CADDR3: IC1.7 (A3), IC2.7 (A3), IC3.7 (A3), IC4.7 (A3), IC5.7 (A3), IC6.7 (A3), IC7.7 (A3), IC8.7 (A3); also elsewhere on the board
CADDR4: IC1.6 (A4), IC2.6 (A4), IC3.6 (A4), IC4.6 (A4), IC5.6 (A4), IC6.6 (A4), IC7.6 (A4), IC8.6 (A4); also elsewhere on the board
CADDR5: IC1.5 (A5), IC2.5 (A5), IC3.5 (A5), IC4.5 (A5), IC5.5 (A5), IC6.5 (A5), IC7.5 (A5), IC8.5 (A5); also elsewhere on the board
CADDR6: IC1.4 (A6), IC2.4 (A6), IC3.4 (A6), IC4.4 (A6), IC5.4 (A6), IC6.4 (A6), IC7.4 (A6), IC8.4 (A6); also elsewhere on the board
CADDR7: IC1.3 (A7), IC2.3 (A7), IC3.3 (A7), IC4.3 (A7), IC5.3 (A7), IC6.3 (A7), IC7.3 (A7), IC8.3 (A7); also elsewhere on the board
CADDR8: IC1.25 (A8), IC2.25 (A8), IC3.25 (A8), IC4.25 (A8), IC5.25 (A8), IC6.25 (A8), IC7.25 (A8), IC8.25 (A8); also elsewhere on the board
CADDR9: IC1.24 (A9), IC2.24 (A9), IC3.24 (A9), IC4.24 (A9), IC5.24 (A9), IC6.24 (A9), IC7.24 (A9), IC8.24 (A9); also elsewhere on the board
CADDR10: IC1.21 (A10), IC2.21 (A10), IC3.21 (A10), IC4.21 (A10), IC5.21 (A10), IC6.21 (A10), IC7.21 (A10), IC8.21 (A10); also elsewhere on the board
CADDR11: IC1.23 (A11), IC2.23 (A11), IC3.23 (A11), IC4.23 (A11), IC5.23 (A11), IC6.23 (A11), IC7.23 (A11), IC8.23 (A11); also elsewhere on the board
CADDR12: IC1.2 (A12), IC2.2 (A12), IC3.2 (A12), IC4.2 (A12), IC5.2 (A12), IC6.2 (A12), IC7.2 (A12), IC8.2 (A12); also elsewhere on the board
CADDR13: IC1.26 (A13), IC2.26 (A13), IC3.26 (A13), IC4.26 (A13), IC5.26 (A13), IC6.26 (A13), IC7.26 (A13), IC8.26 (A13); also elsewhere on the board
CADDR14: IC1.1 (A14), IC2.1 (A14), IC3.1 (A14), IC4.1 (A14), IC5.1 (A14), IC6.1 (A14), IC7.1 (A14), IC8.1 (A14); also elsewhere on the board
DEST-ADDR: IC5.11 (I/O0); also elsewhere on the board
GND: IC1.14 (VSS), IC2.14 (VSS), IC3.14 (VSS), IC4.14 (VSS), IC5.14 (VSS), IC6.14 (VSS), IC7.14 (VSS), IC8.14 (VSS); also elsewhere on the board
INT-EN: IC6.15 (I/O3); also elsewhere on the board
INT-LD-HI: IC6.17 (I/O5); also elsewhere on the board
INT-LD-LO: IC5.13 (I/O2); also elsewhere on the board
INT-START: IC6.16 (I/O4); also elsewhere on the board
IO-ADDR0: IC1.16 (I/O4); also elsewhere on the board
IO-ADDR1: IC1.17 (I/O5); also elsewhere on the board
IO-ADDR2: IC1.18 (I/O6); also elsewhere on the board
IO-ADDR3: IC1.19 (I/O7); also elsewhere on the board
LD-INS-REG: IC6.13 (I/O2); also elsewhere on the board
OPERAND-CLK: IC6.11 (I/O0); also elsewhere on the board
OUT-OFF: IC7.12 (I/O1); also elsewhere on the board
OUT-ON: IC7.11 (I/O0); also elsewhere on the board
REG-LD-HI: IC3.17 (I/O5); also elsewhere on the board
REG-LD-ID0: IC4.18 (I/O6); also elsewhere on the board
REG-LD-ID1: IC4.19 (I/O7); also elsewhere on the board
REG-LD-ID2: IC3.11 (I/O0); also elsewhere on the board
REG-LD-ID3: IC3.12 (I/O1); also elsewhere on the board
REG-LD-LO: IC3.15 (I/O3); also elsewhere on the board
REG-RD-ID0: IC4.13 (I/O2); also elsewhere on the board
REG-RD-ID1: IC4.15 (I/O3); also elsewhere on the board
REG-RD-ID2: IC4.16 (I/O4); also elsewhere on the board
REG-RD-ID3: IC4.17 (I/O5); also elsewhere on the board
SOFT-HALT: IC7.13 (I/O2); also elsewhere on the board
SPARE3: IC5.17 (I/O5); also elsewhere on the board
SRC-ADDR: IC6.18 (I/O6); also elsewhere on the board
UCODE-COUNT-RESET: IC6.12 (I/O1); also elsewhere on the board
VCC: IC1.28 (VCC), IC2.28 (VCC), IC3.28 (VCC), IC4.28 (VCC), IC5.28 (VCC), IC6.28 (VCC), IC7.28 (VCC), IC8.28 (VCC); also elsewhere on the board

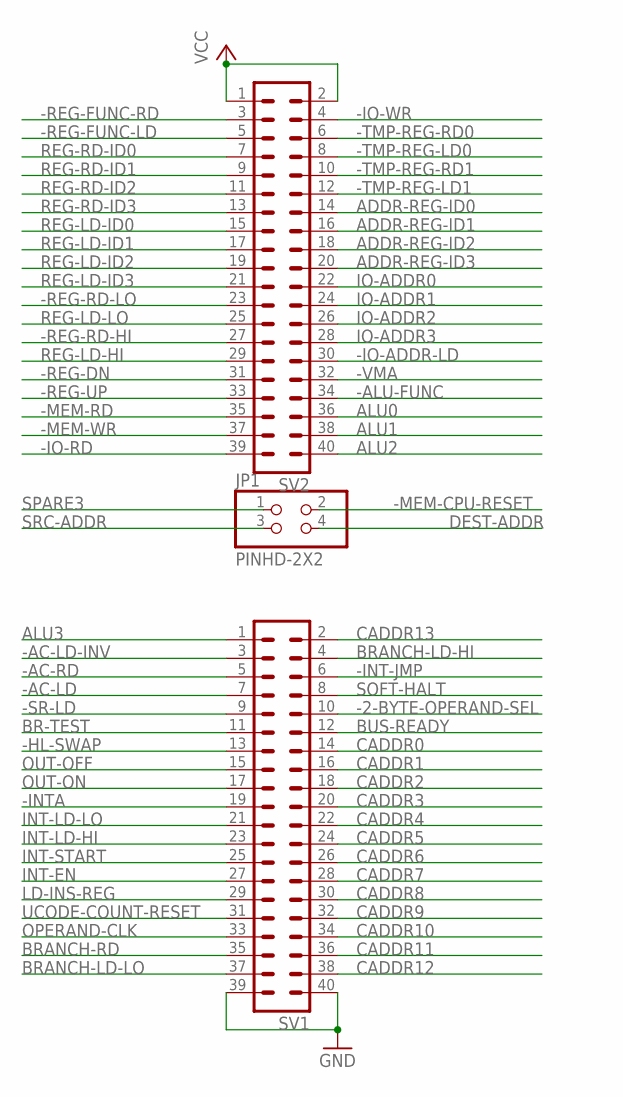
[picture p338: schematic Sequencer-Memory-V2.1.sch, sheet 2, Connector]

Parts:
JP1: PINHD-2X2; 2X02
SV1, SV2: MA20-2

Connections:
-2-BYTE-OPERAND-SEL: SV1.10; also elsewhere on the board
-AC-LD: SV1.7; also elsewhere on the board
-AC-LD-INV: SV1.3; also elsewhere on the board
-AC-RD: SV1.5; also elsewhere on the board
-ALU-FUNC: SV2.34; also elsewhere on the board
-HL-SWAP: SV1.13; also elsewhere on the board
-INT-JMP: SV1.6; also elsewhere on the board
-INTA: SV1.19; also elsewhere on the board
-IO-ADDR-LD: SV2.30; also elsewhere on the board
-IO-RD: SV2.39; also elsewhere on the board
-IO-WR: SV2.4; also elsewhere on the board
-MEM-CPU-RESET: JP1.2; also elsewhere on the board
-MEM-RD: SV2.35; also elsewhere on the board
-MEM-WR: SV2.37; also elsewhere on the board
-REG-DN: SV2.31; also elsewhere on the board
-REG-FUNC-LD: SV2.5; also elsewhere on the board
-REG-FUNC-RD: SV2.3; also elsewhere on the board
-REG-RD-HI: SV2.27; also elsewhere on the board
-REG-RD-LO: SV2.23; also elsewhere on the board
-REG-UP: SV2.33; also elsewhere on the board
-SR-LD: SV1.9; also elsewhere on the board
-TMP-REG-LD0: SV2.8; also elsewhere on the board
-TMP-REG-LD1: SV2.12; also elsewhere on the board
-TMP-REG-RD0: SV2.6; also elsewhere on the board
-TMP-REG-RD1: SV2.10; also elsewhere on the board
-VMA: SV2.32; also elsewhere on the board
ADDR-REG-ID0: SV2.14; also elsewhere on the board
ADDR-REG-ID1: SV2.16; also elsewhere on the board
ADDR-REG-ID2: SV2.18; also elsewhere on the board
ADDR-REG-ID3: SV2.20; also elsewhere on the board
ALU0: SV2.36; also elsewhere on the board
ALU1: SV2.38; also elsewhere on the board
ALU2: SV2.40; also elsewhere on the board
ALU3: SV1.1; also elsewhere on the board
BR-TEST: SV1.11; also elsewhere on the board
BRANCH-LD-HI: SV1.4; also elsewhere on the board
BRANCH-LD-LO: SV1.37; also elsewhere on the board
BRANCH-RD: SV1.35; also elsewhere on the board
BUS-READY: SV1.12; also elsewhere on the board
CADDR0: SV1.14; also elsewhere on the board
CADDR1: SV1.16; also elsewhere on the board
CADDR2: SV1.18; also elsewhere on the board
CADDR3: SV1.20; also elsewhere on the board
CADDR4: SV1.22; also elsewhere on the board
CADDR5: SV1.24; also elsewhere on the board
CADDR6: SV1.26; also elsewhere on the board
CADDR7: SV1.28; also elsewhere on the board
CADDR8: SV1.30; also elsewhere on the board
CADDR9: SV1.32; also elsewhere on the board
CADDR10: SV1.34; also elsewhere on the board
CADDR11: SV1.36; also elsewhere on the board
CADDR12: SV1.38; also elsewhere on the board
CADDR13: SV1.2; also elsewhere on the board
DEST-ADDR: JP1.4; also elsewhere on the board
GND: SV1.39, SV1.40; also elsewhere on the board
INT-EN: SV1.27; also elsewhere on the board
INT-LD-HI: SV1.23; also elsewhere on the board
INT-LD-LO: SV1.21; also elsewhere on the board
INT-START: SV1.25; also elsewhere on the board
IO-ADDR0: SV2.22; also elsewhere on the board
IO-ADDR1: SV2.24; also elsewhere on the board
IO-ADDR2: SV2.26; also elsewhere on the board
IO-ADDR3: SV2.28; also elsewhere on the board
LD-INS-REG: SV1.29; also elsewhere on the board
OPERAND-CLK: SV1.33; also elsewhere on the board
OUT-OFF: SV1.15; also elsewhere on the board
OUT-ON: SV1.17; also elsewhere on the board
REG-LD-HI: SV2.29; also elsewhere on the board
REG-LD-ID0: SV2.15; also elsewhere on the board
REG-LD-ID1: SV2.17; also elsewhere on the board
REG-LD-ID2: SV2.19; also elsewhere on the board
REG-LD-ID3: SV2.21; also elsewhere on the board
REG-LD-LO: SV2.25; also elsewhere on the board
REG-RD-ID0: SV2.7; also elsewhere on the board
REG-RD-ID1: SV2.9; also elsewhere on the board
REG-RD-ID2: SV2.11; also elsewhere on the board
REG-RD-ID3: SV2.13; also elsewhere on the board
SOFT-HALT: SV1.8; also elsewhere on the board
SPARE3: JP1.1; also elsewhere on the board
SRC-ADDR: JP1.3; also elsewhere on the board
UCODE-COUNT-RESET: SV1.31; also elsewhere on the board
VCC: SV2.1, SV2.2; also elsewhere on the board

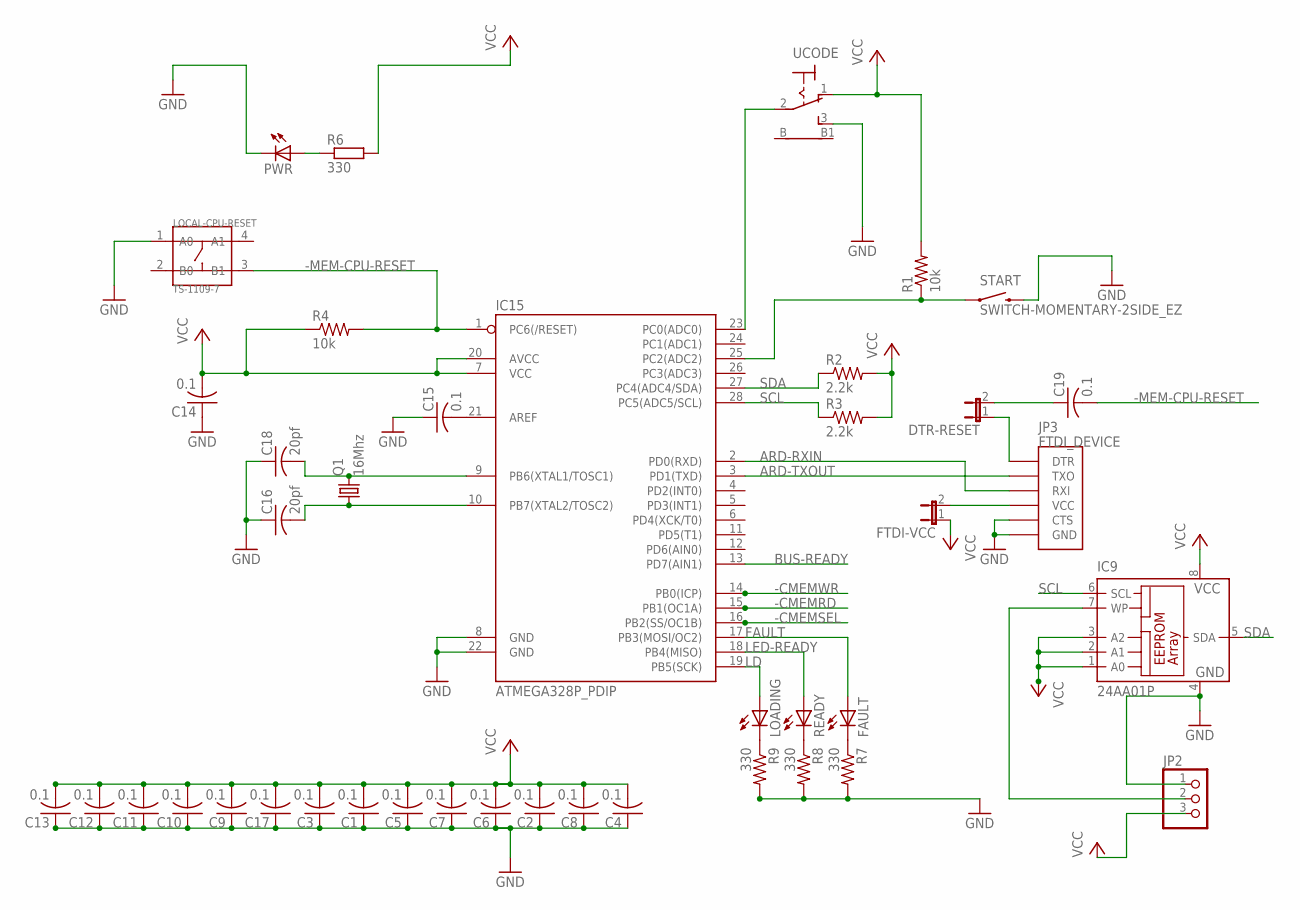
[picture p339: schematic Sequencer-Memory-V2.1.sch, sheet 3, CPU]

Parts:
C1, C2, C3, C4, C5, C6, C7, C8, C9, C10, C11, C12, C13, C14, C15, C17, C19: 0.1; C025-024X044
C16, C18: 20pf; C025-024X044
DTR-RESET: JP1E; JP1
FAULT: LED5MM
FTDI-VCC: JP1E; JP1
IC9: 24AA01P; DIL8
IC15: ATMEGA328P_PDIP; DIL28-3
JP2: PINHD-1X3; 1X03
JP3: FTDI_DEVICE; FTDI_DEVICE_SIDE
LOADING: LED5MM
LOCAL-CPU-RESET: TS-1109-7; SW4-6.2X6.2X5.0MM
PWR: LED5MM
Q1: 16Mhz; HC49/S
R1, R4: 10k; 0207/10
R2, R3: 2.2k; 0207/10
R6, R7, R8, R9: 330; 0207/10
READY: LED5MM
START: SWITCH-MOMENTARY-2SIDE_EZ; TACTILE-PTH-SIDEEZ
UCODE: 9070-1W

Connections:
-CMEMRD: IC15.15 (PB1(OC1A)); also elsewhere on the board
-CMEMSEL: IC15.16 (PB2(SS/OC1B)); also elsewhere on the board
-CMEMWR: IC15.14 (PB0(ICP)); also elsewhere on the board
-MEM-CPU-RESET: C19.2, IC15.1 (PC6(/RESET)), LOCAL-CPU-RESET.3 (B1), R4.2; also elsewhere on the board
ARD-RXIN: IC15.2 (PD0(RXD)), JP3.P$3 (RXI)
ARD-TXOUT: IC15.3 (PD1(TXD)), JP3.P$2 (TXO)
BUS-READY: IC15.13 (PD7(AIN1)); also elsewhere on the board
FAULT: FAULT.A, IC15.17 (PB3(MOSI/OC2))
GND: C1.1, C2.1, C3.1, C4.1, C5.1, C6.1, C7.1, C8.1, C9.1, C10.1, C11.1, C12.1, C13.1, C14.1, C15.1, C16.1, C17.1, C18.1, IC9.4 (GND), IC15.8 (GND), IC15.22 (GND), JP2.1, JP3.P$5 (CTS), JP3.P$6 (GND), LOCAL-CPU-RESET.1 (A0), PWR.K (C), R7.2, R8.2, R9.2, START.2, UCODE.3 (S); also elsewhere on the board
LD: IC15.19 (PB5(SCK)), LOADING.A
LED-READY: IC15.18 (PB4(MISO)), READY.A
unnamed: PWR.A, R6.1
unnamed: C18.2, IC15.9 (PB6(XTAL1/TOSC1)), Q1.2
unnamed: C16.2, IC15.10 (PB7(XTAL2/TOSC2)), Q1.1
unnamed: C19.1, DTR-RESET.2
unnamed: C15.2, IC15.21 (AREF)
unnamed: R8.1, READY.K (C)
unnamed: LOADING.K (C), R9.1
unnamed: FAULT.K (C), R7.1
unnamed: IC15.23 (PC0(ADC0)), UCODE.2
unnamed: IC9.7 (WP), JP2.2
unnamed: DTR-RESET.1, JP3.P$1 (DTR)
unnamed: FTDI-VCC.2, JP3.P$4 (VCC)
unnamed: IC15.25 (PC2(ADC2)), R1.1, START.1
SCL: IC9.6 (SCL), IC15.28 (PC5(ADC5/SCL)), R3.1; also elsewhere on the board
SDA: IC9.5 (SDA), IC15.27 (PC4(ADC4/SDA)), R2.1; also elsewhere on the board
VCC: C1.2, C2.2, C3.2, C4.2, C5.2, C6.2, C7.2, C8.2, C9.2, C10.2, C11.2, C12.2, C13.2, C14.2, C17.2, FTDI-VCC.1, IC9.1 (A0), IC9.2 (A1), IC9.3 (A2), IC9.8 (VCC), IC15.7 (VCC), IC15.20 (AVCC), JP2.3, R1.2, R2.2, R3.2, R4.1, R6.2, UCODE.1 (O); also elsewhere on the board
