ksr/YACC1-D/hardware/cards/sequencer-memory/eagle/v2.1/Sequencer-Memory-V2.1.brd

## EAGLE design hardware/cards/sequencer-memory/eagle/v2.1/Sequencer-Memory-V2.1.brd (continued)

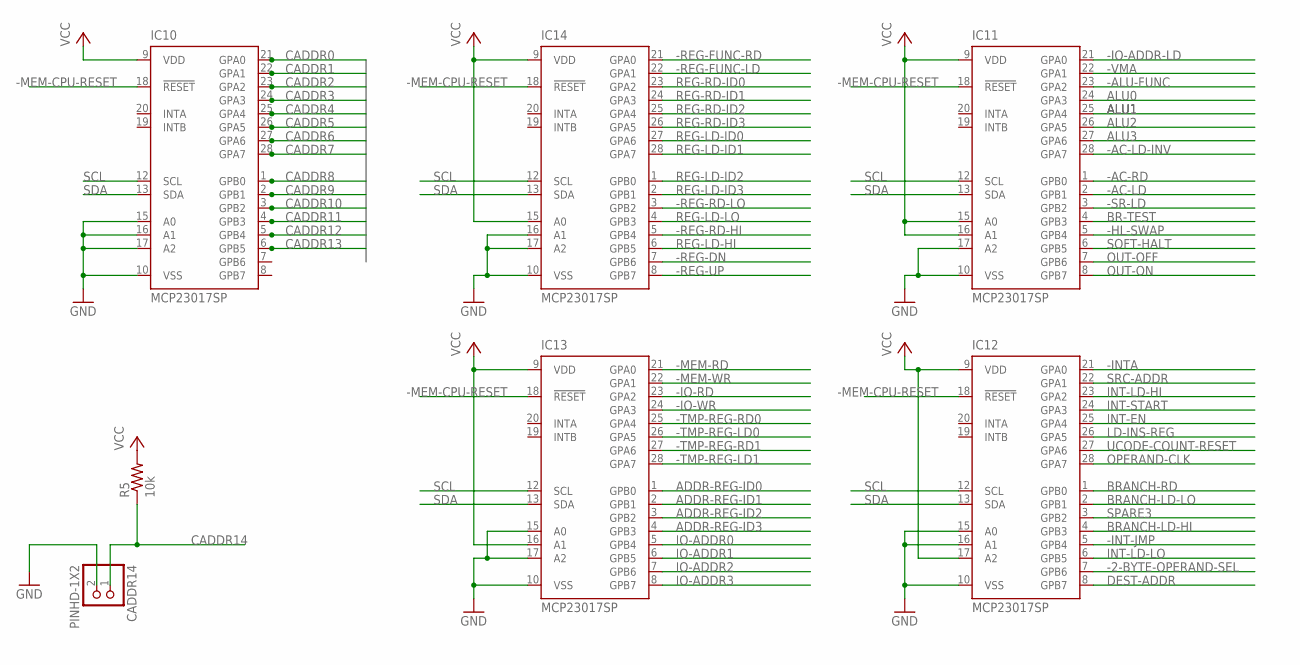
[picture p340: schematic Sequencer-Memory-V2.1.sch, sheet 4, IO]

Parts:
CADDR14: PINHD-1X2; 1X02
IC10, IC11, IC12, IC13, IC14: MCP23017SP; DIL28-3
R5: 10k; 0207/10

Connections:
-2-BYTE-OPERAND-SEL: IC12.7 (GPB6); also elsewhere on the board
-AC-LD: IC11.2 (GPB1); also elsewhere on the board
-AC-LD-INV: IC11.28 (GPA7); also elsewhere on the board
-AC-RD: IC11.1 (GPB0); also elsewhere on the board
-ALU-FUNC: IC11.23 (GPA2); also elsewhere on the board
-HL-SWAP: IC11.5 (GPB4); also elsewhere on the board
-INT-JMP: IC12.5 (GPB4); also elsewhere on the board
-INTA: IC12.21 (GPA0); also elsewhere on the board
-IO-ADDR-LD: IC11.21 (GPA0); also elsewhere on the board
-IO-RD: IC13.23 (GPA2); also elsewhere on the board
-IO-WR: IC13.24 (GPA3); also elsewhere on the board
-MEM-CPU-RESET: IC10.18 (!RESET), IC11.18 (!RESET), IC12.18 (!RESET), IC13.18 (!RESET), IC14.18 (!RESET); also elsewhere on the board
-MEM-RD: IC13.21 (GPA0); also elsewhere on the board
-MEM-WR: IC13.22 (GPA1); also elsewhere on the board
-REG-DN: IC14.7 (GPB6); also elsewhere on the board
-REG-FUNC-LD: IC14.22 (GPA1); also elsewhere on the board
-REG-FUNC-RD: IC14.21 (GPA0); also elsewhere on the board
-REG-RD-HI: IC14.5 (GPB4); also elsewhere on the board
-REG-RD-LO: IC14.3 (GPB2); also elsewhere on the board
-REG-UP: IC14.8 (GPB7); also elsewhere on the board
-SR-LD: IC11.3 (GPB2); also elsewhere on the board
-TMP-REG-LD0: IC13.26 (GPA5); also elsewhere on the board
-TMP-REG-LD1: IC13.28 (GPA7); also elsewhere on the board
-TMP-REG-RD0: IC13.25 (GPA4); also elsewhere on the board
-TMP-REG-RD1: IC13.27 (GPA6); also elsewhere on the board
-VMA: IC11.22 (GPA1); also elsewhere on the board
ADDR-REG-ID0: IC13.1 (GPB0); also elsewhere on the board
ADDR-REG-ID1: IC13.2 (GPB1); also elsewhere on the board
ADDR-REG-ID2: IC13.3 (GPB2); also elsewhere on the board
ADDR-REG-ID3: IC13.4 (GPB3); also elsewhere on the board
ALU0: IC11.24 (GPA3); also elsewhere on the board
ALU1: IC11.25 (GPA4); also elsewhere on the board
ALU2: IC11.26 (GPA5); also elsewhere on the board
ALU3: IC11.27 (GPA6); also elsewhere on the board
BR-TEST: IC11.4 (GPB3); also elsewhere on the board
BRANCH-LD-HI: IC12.4 (GPB3); also elsewhere on the board
BRANCH-LD-LO: IC12.2 (GPB1); also elsewhere on the board
BRANCH-RD: IC12.1 (GPB0); also elsewhere on the board
CADDR0: IC10.21 (GPA0); also elsewhere on the board
CADDR1: IC10.22 (GPA1); also elsewhere on the board
CADDR2: IC10.23 (GPA2); also elsewhere on the board
CADDR3: IC10.24 (GPA3); also elsewhere on the board
CADDR4: IC10.25 (GPA4); also elsewhere on the board
CADDR5: IC10.26 (GPA5); also elsewhere on the board
CADDR6: IC10.27 (GPA6); also elsewhere on the board
CADDR7: IC10.28 (GPA7); also elsewhere on the board
CADDR8: IC10.1 (GPB0); also elsewhere on the board
CADDR9: IC10.2 (GPB1); also elsewhere on the board
CADDR10: IC10.3 (GPB2); also elsewhere on the board
CADDR11: IC10.4 (GPB3); also elsewhere on the board
CADDR12: IC10.5 (GPB4); also elsewhere on the board
CADDR13: IC10.6 (GPB5); also elsewhere on the board
CADDR14: CADDR14.1, R5.1; also elsewhere on the board
DEST-ADDR: IC12.8 (GPB7); also elsewhere on the board
GND: CADDR14.2, IC10.10 (VSS), IC10.15 (A0), IC10.16 (A1), IC10.17 (A2), IC11.10 (VSS), IC11.17 (A2), IC12.10 (VSS), IC12.15 (A0), IC12.16 (A1), IC13.10 (VSS), IC13.15 (A0), IC13.17 (A2), IC14.10 (VSS), IC14.16 (A1), IC14.17 (A2); also elsewhere on the board
INT-EN: IC12.25 (GPA4); also elsewhere on the board
INT-LD-HI: IC12.23 (GPA2); also elsewhere on the board
INT-LD-LO: IC12.6 (GPB5); also elsewhere on the board
INT-START: IC12.24 (GPA3); also elsewhere on the board
IO-ADDR0: IC13.5 (GPB4); also elsewhere on the board
IO-ADDR1: IC13.6 (GPB5); also elsewhere on the board
IO-ADDR2: IC13.7 (GPB6); also elsewhere on the board
IO-ADDR3: IC13.8 (GPB7); also elsewhere on the board
LD-INS-REG: IC12.26 (GPA5); also elsewhere on the board
OPERAND-CLK: IC12.28 (GPA7); also elsewhere on the board
OUT-OFF: IC11.7 (GPB6); also elsewhere on the board
OUT-ON: IC11.8 (GPB7); also elsewhere on the board
REG-LD-HI: IC14.6 (GPB5); also elsewhere on the board
REG-LD-ID0: IC14.27 (GPA6); also elsewhere on the board
REG-LD-ID1: IC14.28 (GPA7); also elsewhere on the board
REG-LD-ID2: IC14.1 (GPB0); also elsewhere on the board
REG-LD-ID3: IC14.2 (GPB1); also elsewhere on the board
REG-LD-LO: IC14.4 (GPB3); also elsewhere on the board
REG-RD-ID0: IC14.23 (GPA2); also elsewhere on the board
REG-RD-ID1: IC14.24 (GPA3); also elsewhere on the board
REG-RD-ID2: IC14.25 (GPA4); also elsewhere on the board
REG-RD-ID3: IC14.26 (GPA5); also elsewhere on the board
SCL: IC10.12 (SCL), IC11.12 (SCL), IC12.12 (SCL), IC13.12 (SCL), IC14.12 (SCL); also elsewhere on the board
SDA: IC10.13 (SDA), IC11.13 (SDA), IC12.13 (SDA), IC13.13 (SDA), IC14.13 (SDA); also elsewhere on the board
SOFT-HALT: IC11.6 (GPB5); also elsewhere on the board
SPARE3: IC12.3 (GPB2); also elsewhere on the board
SRC-ADDR: IC12.22 (GPA1); also elsewhere on the board
UCODE-COUNT-RESET: IC12.27 (GPA6); also elsewhere on the board
VCC: IC10.9 (VDD), IC11.9 (VDD), IC11.15 (A0), IC11.16 (A1), IC12.9 (VDD), IC12.17 (A2), IC13.9 (VDD), IC13.16 (A1), IC14.9 (VDD), IC14.15 (A0), R5.2; also elsewhere on the board

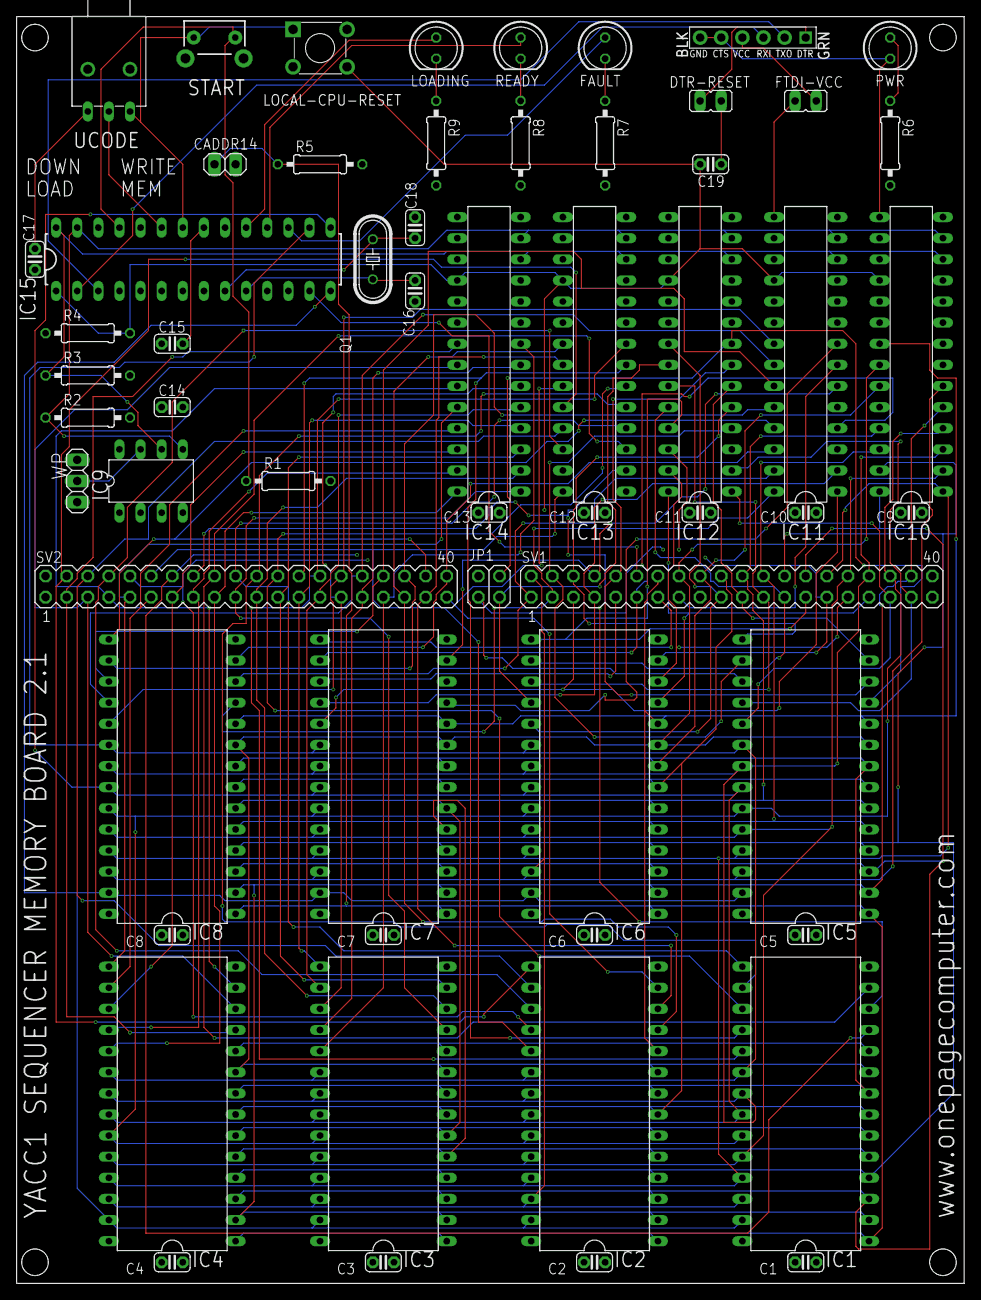
[picture p341: board Sequencer-Memory-V2.1.brd from above]

Board: 4 copper layers, 114.0 x 152.4 mm, 59 parts (0 on the bottom side), 106 nets.
