ksr/YACC1-D/hardware/cards/protocard/eagle/v1.0/ProtoCard-Prod-V1.0.brd

## EAGLE design hardware/cards/protocard/eagle/v1.0/ProtoCard-Prod-V1.0.brd (2026-09-20)

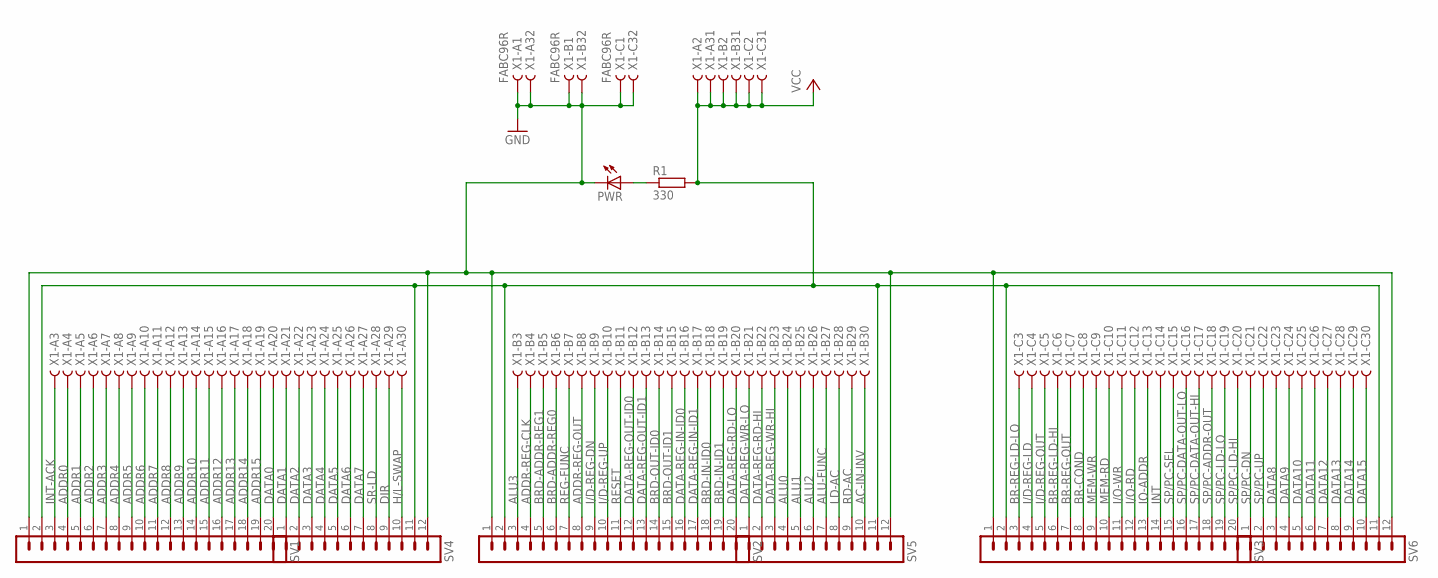
[picture p342: schematic ProtoCard-Prod-V1.0.sch]

Parts:
PWR: LED5MM
R1: 330; 0207/10
SV1, SV2, SV3: MA20-1
SV4, SV5, SV6: MA12-1
X1: FABC96R

Connections:
AC-IN-INV: SV5.10, X1.B30
ADDR0: SV1.4, X1.A4
ADDR1: SV1.5, X1.A5
ADDR2: SV1.6, X1.A6
ADDR3: SV1.7, X1.A7
ADDR4: SV1.8, X1.A8
ADDR5: SV1.9, X1.A9
ADDR6: SV1.10, X1.A10
ADDR7: SV1.11, X1.A11
ADDR8: SV1.12, X1.A12
ADDR9: SV1.13, X1.A13
ADDR10: SV1.14, X1.A14
ADDR11: SV1.15, X1.A15
ADDR12: SV1.16, X1.A16
ADDR13: SV1.17, X1.A17
ADDR14: SV1.18, X1.A18
ADDR15: SV1.19, X1.A19
ADDR-REG-CLK: SV2.4, X1.B4
ADDR-REG-OUT: SV2.8, X1.B8
ALU0: SV5.4, X1.B24
ALU1: SV5.5, X1.B25
ALU2: SV5.6, X1.B26
ALU3: SV2.3, X1.B3
ALU-FUNC: SV5.7, X1.B27
BR-COND: SV3.8, X1.C8
BR-REG-LD-HI: SV3.6, X1.C6
BR-REG-LD-LO: SV3.3, X1.C3
BR-REG-OUT: SV3.7, X1.C7
BRD-ADDR-REG0: SV2.6, X1.B6
BRD-ADDR-REG1: SV2.5, X1.B5
BRD-IN-ID0: SV2.18, X1.B18
BRD-IN-ID1: SV2.19, X1.B19
BRD-OUT-ID0: SV2.14, X1.B14
BRD-OUT-ID1: SV2.15, X1.B15
DATA0: SV1.20, X1.A20
DATA1: SV4.1, X1.A21
DATA2: SV4.2, X1.A22
DATA3: SV4.3, X1.A23
DATA4: SV4.4, X1.A24
DATA5: SV4.5, X1.A25
DATA6: SV4.6, X1.A26
DATA7: SV4.7, X1.A27
DATA8: SV6.3, X1.C23
DATA9: SV6.4, X1.C24
DATA10: SV6.5, X1.C25
DATA11: SV6.6, X1.C26
DATA12: SV6.7, X1.C27
DATA13: SV6.8, X1.C28
DATA14: SV6.9, X1.C29
DATA15: SV6.10, X1.C30
DATA-REG-IN-ID0: SV2.16, X1.B16
DATA-REG-IN-ID1: SV2.17, X1.B17
DATA-REG-OUT-ID0: SV2.12, X1.B12
DATA-REG-OUT-ID1: SV2.13, X1.B13
DATA-REG-RD-HI: SV5.2, X1.B22
DATA-REG-RD-LO: SV2.20, X1.B20
DATA-REG-WR-HI: SV5.3, X1.B23
DATA-REG-WR-LO: SV5.1, X1.B21
DIR: SV4.9, X1.A29
GND: PWR.K (C), SV1.1, SV2.1, SV3.1, SV4.12, SV5.12, SV6.12, X1.A1, X1.A32, X1.B1, X1.B32, X1.C1, X1.C32
H/L-SWAP: SV4.10, X1.A30
I/D-REG-DN: SV2.9, X1.B9
I/D-REG-LD: SV3.4, X1.C4
I/D-REG-OUT: SV3.5, X1.C5
I/D-REG-UP: SV2.10, X1.B10
I/O-RD: SV3.12, X1.C12
I/O-WR: SV3.11, X1.C11
INT: SV3.14, X1.C14
INT-ACK: SV1.3, X1.A3
IO-ADDR: SV3.13, X1.C13
LD-AC: SV5.8, X1.B28
MEM-RD: SV3.10, X1.C10
MEM-WR: SV3.9, X1.C9
unnamed: PWR.A, R1.1
RD-AC: SV5.9, X1.B29
REG-FUNC: SV2.7, X1.B7
RESET: SV2.11, X1.B11
SP/PC-ADDR-OUT: SV3.18, X1.C18
SP/PC-DATA-OUT-HI: SV3.17, X1.C17
SP/PC-DATA-OUT-LO: SV3.16, X1.C16
SP/PC-DN: SV6.1, X1.C21
SP/PC-LD-HI: SV3.20, X1.C20
SP/PC-LD-LO: SV3.19, X1.C19
SP/PC-SEL: SV3.15, X1.C15
SP/PC-UP: SV6.2, X1.C22
SR-LD: SV4.8, X1.A28
VCC: R1.2, SV1.2, SV2.2, SV3.2, SV4.11, SV5.11, SV6.11, X1.A2, X1.A31, X1.B2, X1.B31, X1.C2, X1.C31

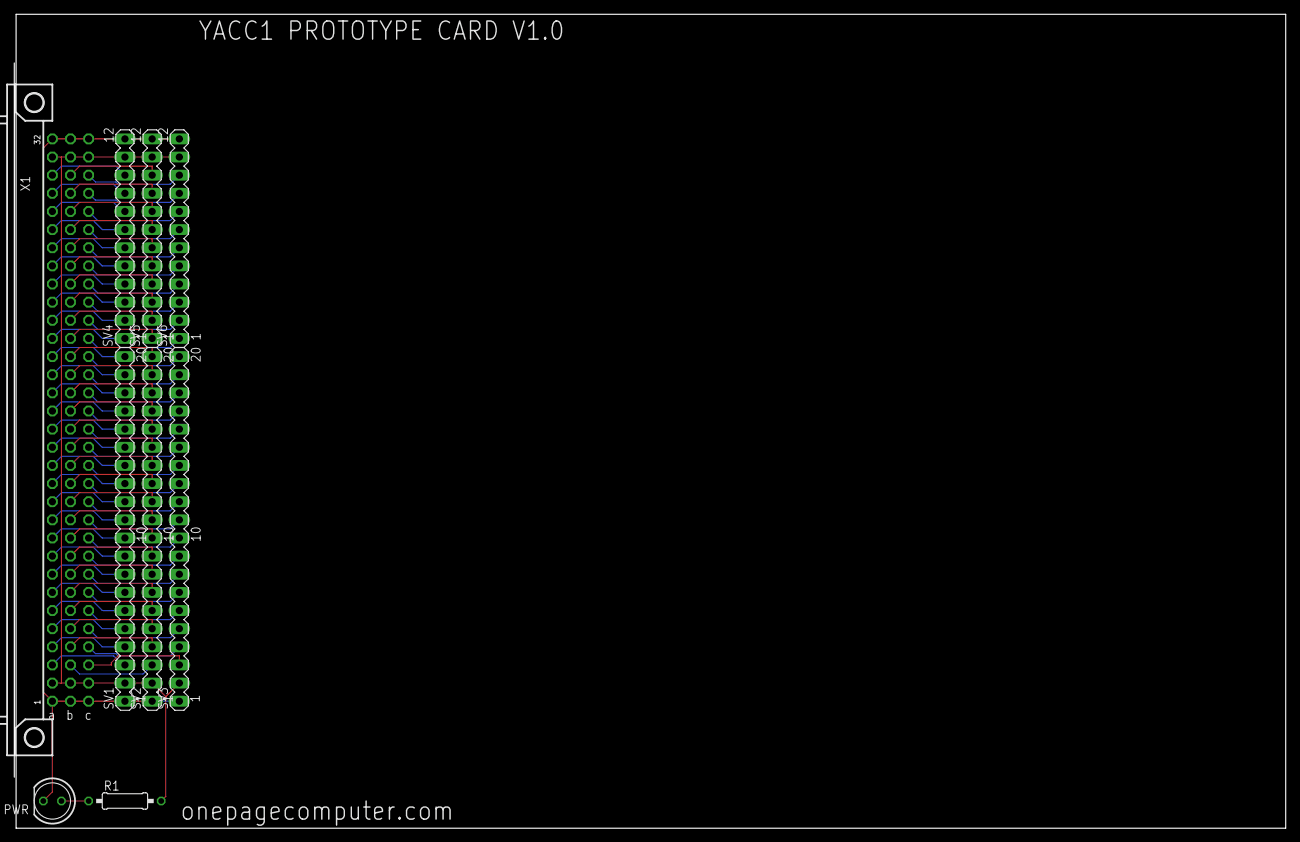
[picture p343: board ProtoCard-Prod-V1.0.brd from above]

Board: 2 copper layers, 177.8 x 114.0 mm, 9 parts (0 on the bottom side), 87 nets.
