ksr/YACC1-D/hardware/bus/bus-jumper-vertical/eagle/v3.0/Jumper Board V3.0.brd

## EAGLE design hardware/bus/bus-jumper-vertical/eagle/v3.0/Jumper Board V3.0.brd (2026-09-20)

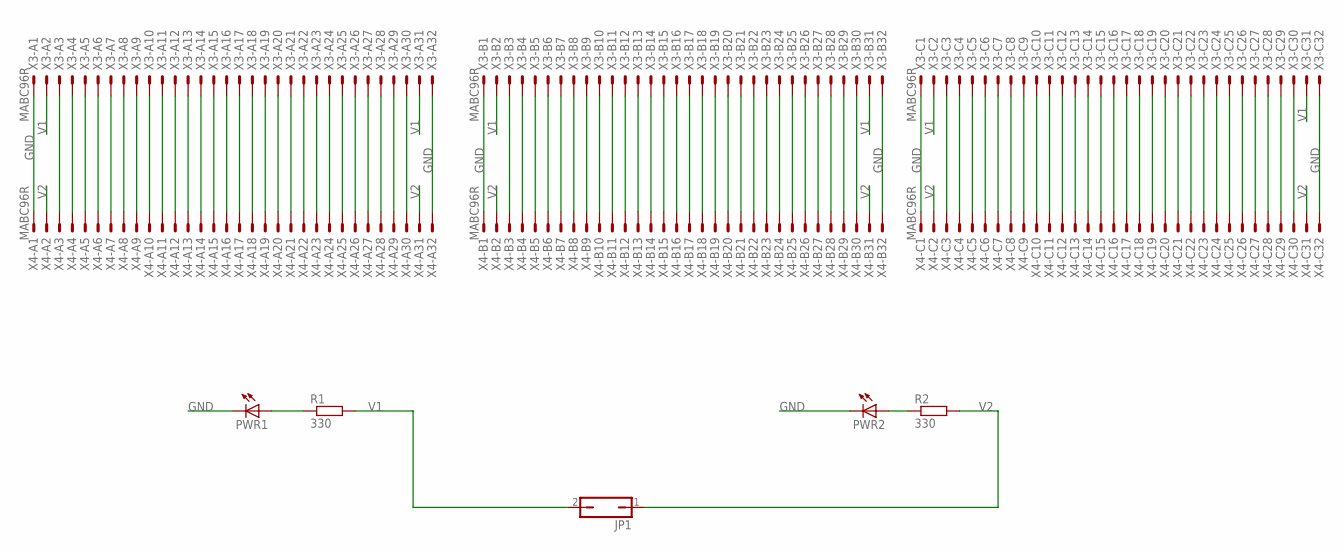
[picture p344: schematic Jumper Board V3.0.sch]

Parts:
JP1: JP1Q; JP1
PWR1, PWR2: LED5MM
R1, R2: 330; 0207/10
X3, X4: MABC96R

Connections:
GND: PWR1.K (C), PWR2.K (C), X3.A1, X3.A32, X3.B1, X3.B32, X3.C1, X3.C32, X4.A1, X4.A32, X4.B1, X4.B32, X4.C1, X4.C32
unnamed: X3.A3, X4.A3
unnamed: X3.A4, X4.A4
unnamed: X3.A5, X4.A5
unnamed: X3.A6, X4.A6
unnamed: X3.A7, X4.A7
unnamed: X3.A8, X4.A8
unnamed: X3.A9, X4.A9
unnamed: X3.A10, X4.A10
unnamed: X3.A11, X4.A11
unnamed: X3.A12, X4.A12
unnamed: X3.A13, X4.A13
unnamed: X3.A14, X4.A14
unnamed: X3.A15, X4.A15
unnamed: X3.A16, X4.A16
unnamed: X3.A17, X4.A17
unnamed: X3.A18, X4.A18
unnamed: X3.A19, X4.A19
unnamed: X3.A20, X4.A20
unnamed: X3.A21, X4.A21
unnamed: X3.A22, X4.A22
unnamed: X3.A23, X4.A23
unnamed: X3.A24, X4.A24
unnamed: X3.A25, X4.A25
unnamed: X3.A26, X4.A26
unnamed: X3.A27, X4.A27
unnamed: X3.A28, X4.A28
unnamed: X3.A29, X4.A29
unnamed: X3.A30, X4.A30
unnamed: PWR1.A, R1.1
unnamed: PWR2.A, R2.1
unnamed: X3.B3, X4.B3
unnamed: X3.B4, X4.B4
unnamed: X3.B5, X4.B5
unnamed: X3.B6, X4.B6
unnamed: X3.B7, X4.B7
unnamed: X3.B8, X4.B8
unnamed: X3.B9, X4.B9
unnamed: X3.B10, X4.B10
unnamed: X3.B11, X4.B11
unnamed: X3.B12, X4.B12
unnamed: X3.B13, X4.B13
unnamed: X3.B14, X4.B14
unnamed: X3.B15, X4.B15
unnamed: X3.B16, X4.B16
unnamed: X3.B17, X4.B17
unnamed: X3.B18, X4.B18
unnamed: X3.B19, X4.B19
unnamed: X3.B20, X4.B20
unnamed: X3.B21, X4.B21
unnamed: X3.B22, X4.B22
unnamed: X3.B23, X4.B23
unnamed: X3.B24, X4.B24
unnamed: X3.B25, X4.B25
unnamed: X3.B26, X4.B26
unnamed: X3.B27, X4.B27
unnamed: X3.B28, X4.B28
unnamed: X3.B29, X4.B29
unnamed: X3.B30, X4.B30
unnamed: X3.C3, X4.C3
unnamed: X3.C4, X4.C4
unnamed: X3.C5, X4.C5
unnamed: X3.C6, X4.C6
unnamed: X3.C7, X4.C7
unnamed: X3.C8, X4.C8
unnamed: X3.C9, X4.C9
unnamed: X3.C10, X4.C10
unnamed: X3.C11, X4.C11
unnamed: X3.C12, X4.C12
unnamed: X3.C13, X4.C13
unnamed: X3.C14, X4.C14
unnamed: X3.C15, X4.C15
unnamed: X3.C16, X4.C16
unnamed: X3.C17, X4.C17
unnamed: X3.C18, X4.C18
unnamed: X3.C19, X4.C19
unnamed: X3.C20, X4.C20
unnamed: X3.C21, X4.C21
unnamed: X3.C22, X4.C22
unnamed: X3.C23, X4.C23
unnamed: X3.C24, X4.C24
unnamed: X3.C25, X4.C25
unnamed: X3.C26, X4.C26
unnamed: X3.C27, X4.C27
unnamed: X3.C28, X4.C28
unnamed: X3.C29, X4.C29
unnamed: X3.C30, X4.C30
V1: JP1.2, R1.2, X3.A2, X3.A31, X3.B2, X3.B31, X3.C2, X3.C31
V2: JP1.1, R2.2, X4.A2, X4.A31, X4.B2, X4.B31, X4.C2, X4.C31

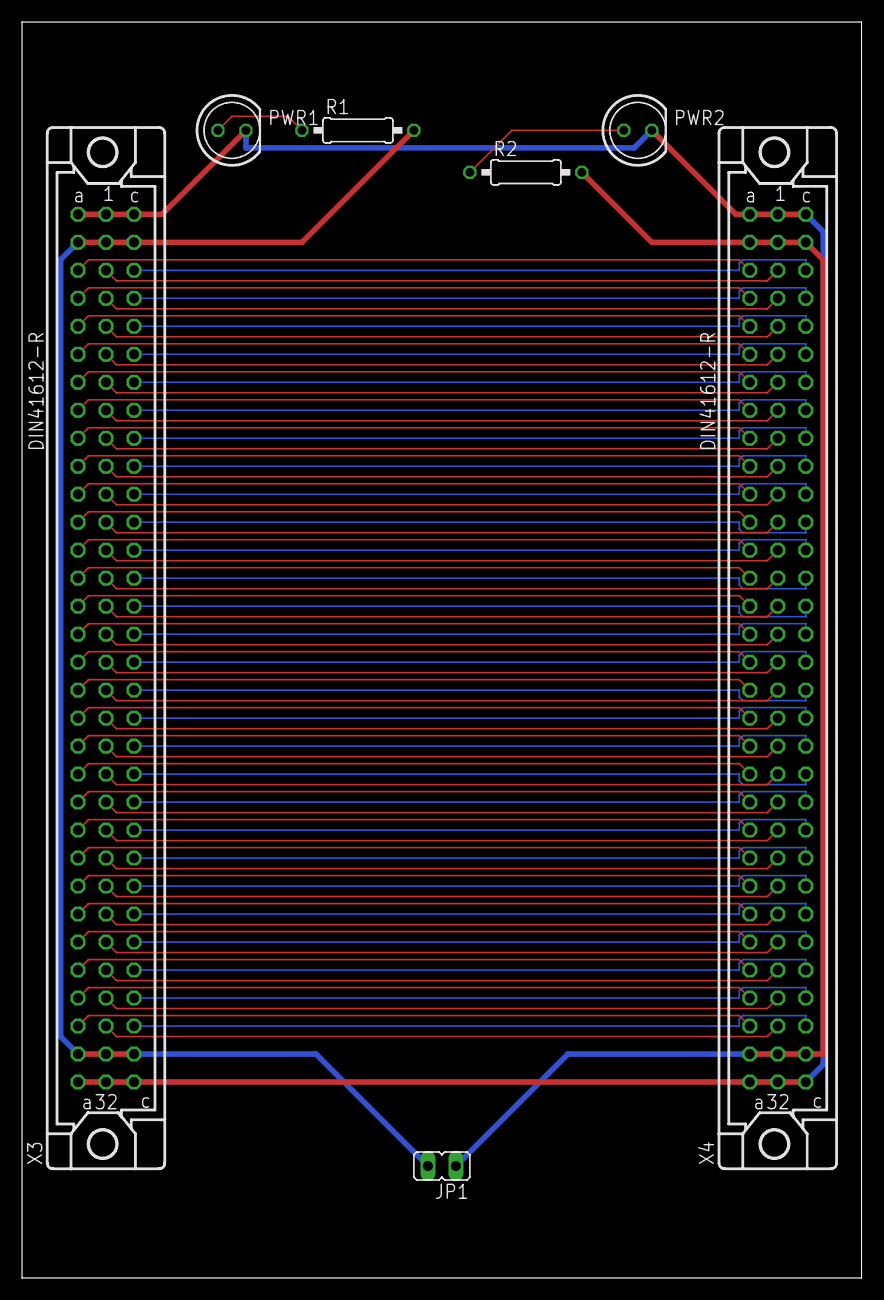
[picture p345: board Jumper Board V3.0.brd from above]

Board: 2 copper layers, 76.2 x 114.0 mm, 7 parts (0 on the bottom side), 89 nets.
