ksr/YACC1-D/hardware/cards/mem-switch/eagle/v1.1/Mem Switch V1.1.brd

## EAGLE design hardware/cards/mem-switch/eagle/v1.1/Mem Switch V1.1.brd (continued)

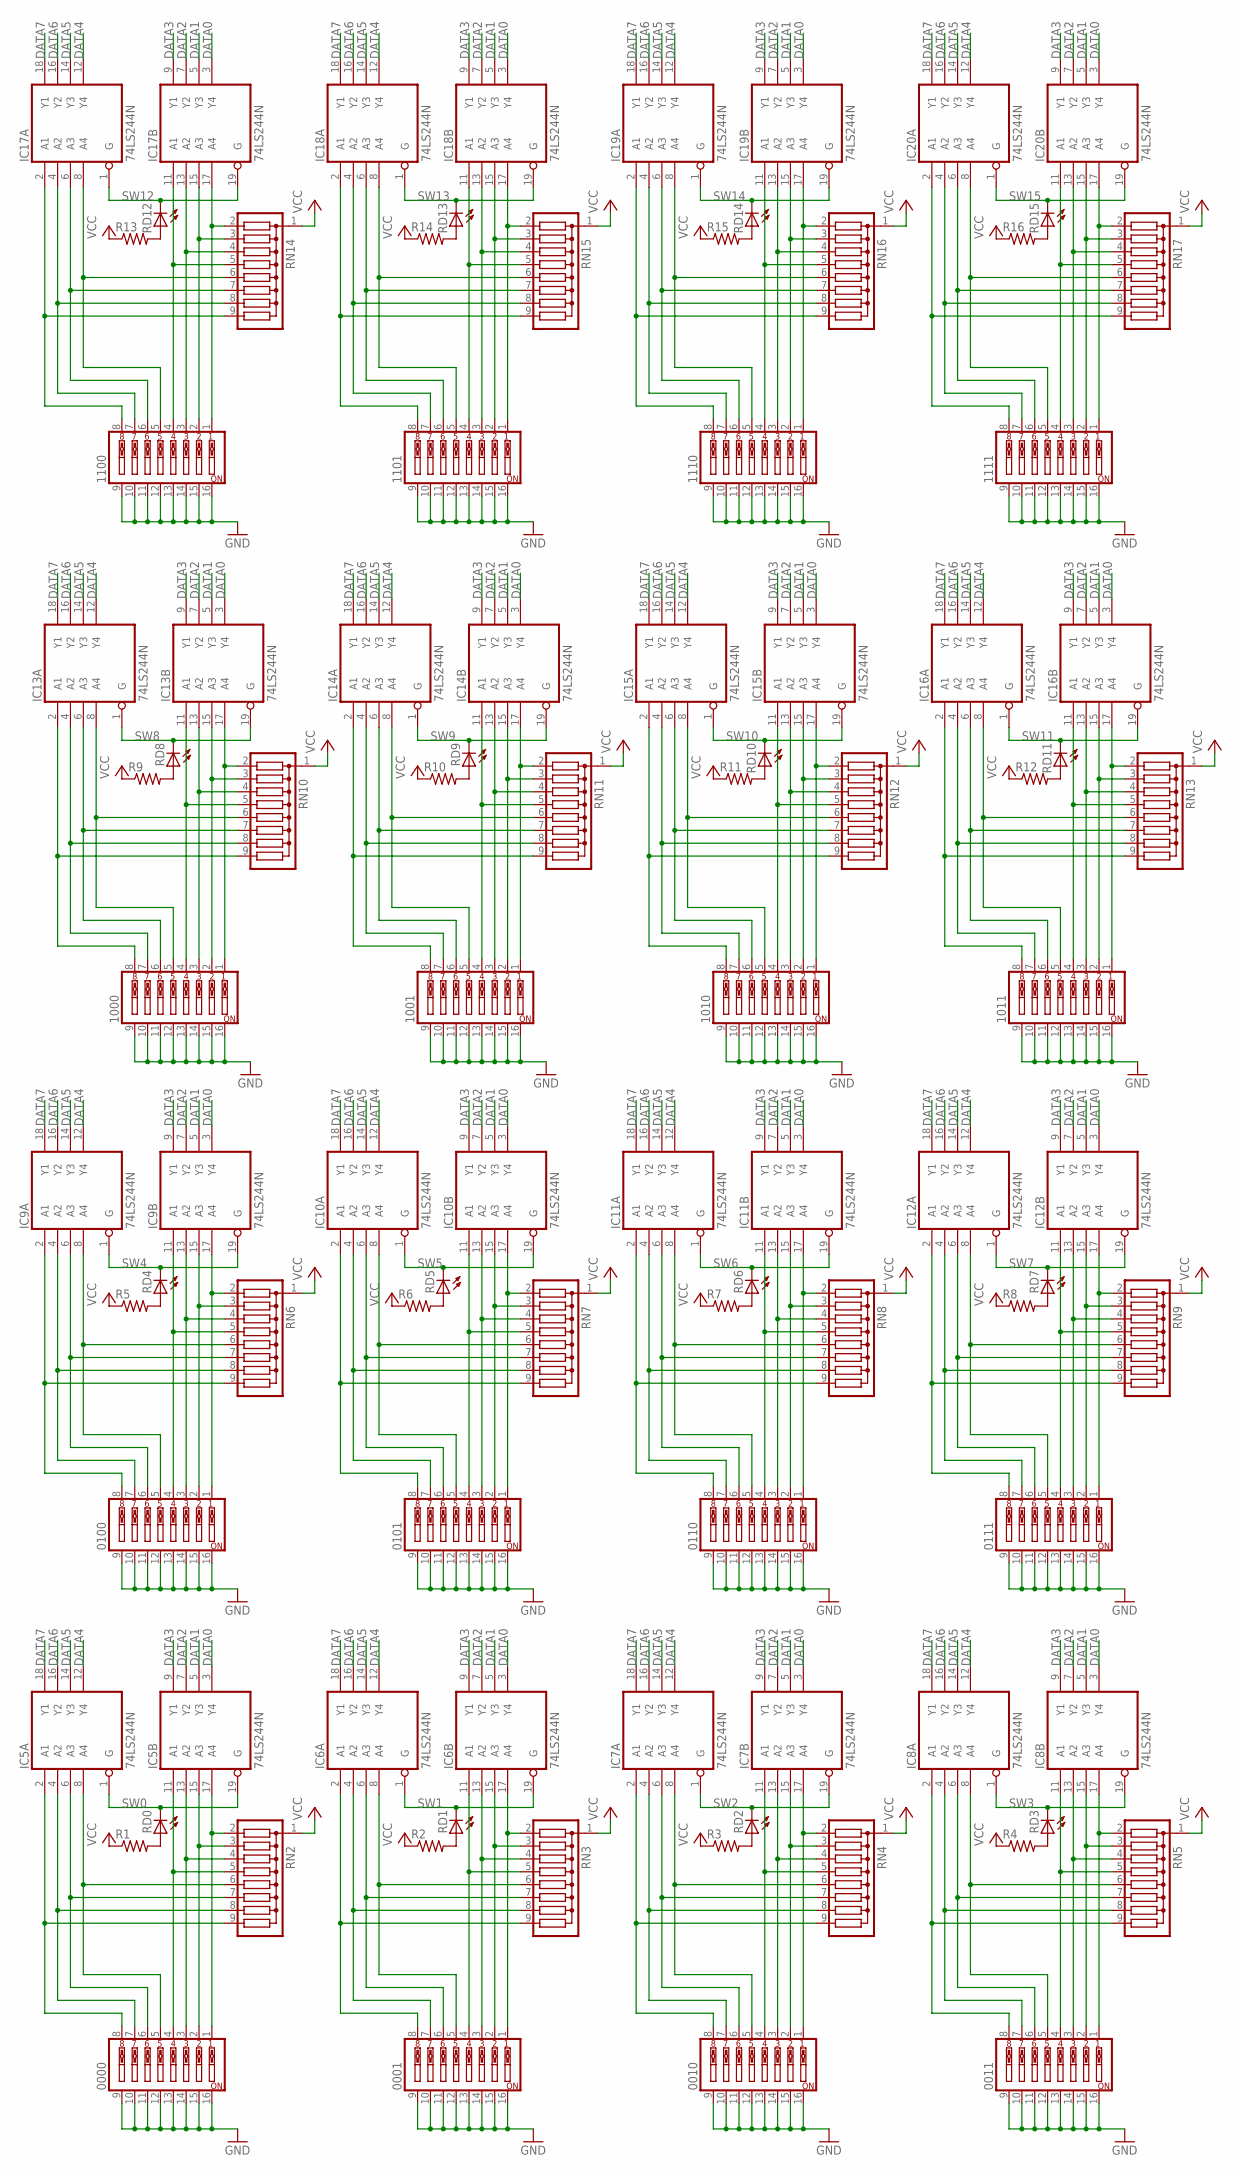
[picture p347: schematic Mem Switch V1.1.sch, sheet 2]

Parts:
0000, 0001, 0010, 0011, 0100, 0101, 0110, 0111, 1000, 1001, 1010, 1011, 1100, 1101, 1110, 1111: SW_DIP-8; EDG-08
IC5, IC6, IC7, IC8, IC9, IC10, IC11, IC12, IC13, IC14, IC15, IC16, IC17, IC18, IC19, IC20: 74LS244N; DIL20
R1, R2, R3, R4, R5, R6, R7, R8, R9, R10, R11, R12, R13, R14, R15, R16: R-US_0207/10; 0207/10
RD0, RD1, RD2, RD3, RD4, RD5, RD6, RD7, RD8, RD9, RD10, RD11, RD12, RD13, RD14, RD15: LED3MM
RN2, RN3, RN4, RN5, RN6, RN7, RN8, RN9, RN10, RN11, RN12, RN13, RN14, RN15, RN16, RN17: G08R; SIL9

Connections:
DATA0: IC5.3 (Y4), IC6.3 (Y4), IC7.3 (Y4), IC8.3 (Y4), IC9.3 (Y4), IC10.3 (Y4), IC11.3 (Y4), IC12.3 (Y4), IC13.3 (Y4), IC14.3 (Y4), IC15.3 (Y4), IC16.3 (Y4), IC17.3 (Y4), IC18.3 (Y4), IC19.3 (Y4), IC20.3 (Y4); also elsewhere on the board
DATA1: IC5.5 (Y3), IC6.5 (Y3), IC7.5 (Y3), IC8.5 (Y3), IC9.5 (Y3), IC10.5 (Y3), IC11.5 (Y3), IC12.5 (Y3), IC13.5 (Y3), IC14.5 (Y3), IC15.5 (Y3), IC16.5 (Y3), IC17.5 (Y3), IC18.5 (Y3), IC19.5 (Y3), IC20.5 (Y3); also elsewhere on the board
DATA2: IC5.7 (Y2), IC6.7 (Y2), IC7.7 (Y2), IC8.7 (Y2), IC9.7 (Y2), IC10.7 (Y2), IC11.7 (Y2), IC12.7 (Y2), IC13.7 (Y2), IC14.7 (Y2), IC15.7 (Y2), IC16.7 (Y2), IC17.7 (Y2), IC18.7 (Y2), IC19.7 (Y2), IC20.7 (Y2); also elsewhere on the board
DATA3: IC5.9 (Y1), IC6.9 (Y1), IC7.9 (Y1), IC8.9 (Y1), IC9.9 (Y1), IC10.9 (Y1), IC11.9 (Y1), IC12.9 (Y1), IC13.9 (Y1), IC14.9 (Y1), IC15.9 (Y1), IC16.9 (Y1), IC17.9 (Y1), IC18.9 (Y1), IC19.9 (Y1), IC20.9 (Y1); also elsewhere on the board
DATA4: IC5.12 (Y4), IC6.12 (Y4), IC7.12 (Y4), IC8.12 (Y4), IC9.12 (Y4), IC10.12 (Y4), IC11.12 (Y4), IC12.12 (Y4), IC13.12 (Y4), IC14.12 (Y4), IC15.12 (Y4), IC16.12 (Y4), IC17.12 (Y4), IC18.12 (Y4), IC19.12 (Y4), IC20.12 (Y4); also elsewhere on the board
DATA5: IC5.14 (Y3), IC6.14 (Y3), IC7.14 (Y3), IC8.14 (Y3), IC9.14 (Y3), IC10.14 (Y3), IC11.14 (Y3), IC12.14 (Y3), IC13.14 (Y3), IC14.14 (Y3), IC15.14 (Y3), IC16.14 (Y3), IC17.14 (Y3), IC18.14 (Y3), IC19.14 (Y3), IC20.14 (Y3); also elsewhere on the board
DATA6: IC5.16 (Y2), IC6.16 (Y2), IC7.16 (Y2), IC8.16 (Y2), IC9.16 (Y2), IC10.16 (Y2), IC11.16 (Y2), IC12.16 (Y2), IC13.16 (Y2), IC14.16 (Y2), IC15.16 (Y2), IC16.16 (Y2), IC17.16 (Y2), IC18.16 (Y2), IC19.16 (Y2), IC20.16 (Y2); also elsewhere on the board
DATA7: IC5.18 (Y1), IC6.18 (Y1), IC7.18 (Y1), IC8.18 (Y1), IC9.18 (Y1), IC10.18 (Y1), IC11.18 (Y1), IC12.18 (Y1), IC13.18 (Y1), IC14.18 (Y1), IC15.18 (Y1), IC16.18 (Y1), IC17.18 (Y1), IC18.18 (Y1), IC19.18 (Y1), IC20.18 (Y1); also elsewhere on the board
GND: 0000.9, 0000.10, 0000.11, 0000.12, 0000.13, 0000.14, 0000.15, 0000.16, 0001.9, 0001.10, 0001.11, 0001.12, 0001.13, 0001.14, 0001.15, 0001.16, 0010.9, 0010.10, 0010.11, 0010.12, 0010.13, 0010.14, 0010.15, 0010.16, 0011.9, 0011.10, 0011.11, 0011.12, 0011.13, 0011.14, 0011.15, 0011.16, 0100.9, 0100.10, 0100.11, 0100.12, 0100.13, 0100.14, 0100.15, 0100.16, 0101.9, 0101.10, 0101.11, 0101.12, 0101.13, 0101.14, 0101.15, 0101.16, 0110.9, 0110.10, 0110.11, 0110.12, 0110.13, 0110.14, 0110.15, 0110.16, 0111.9, 0111.10, 0111.11, 0111.12, 0111.13, 0111.14, 0111.15, 0111.16, 1000.9, 1000.10, 1000.11, 1000.12, 1000.13, 1000.14, 1000.15, 1000.16, 1001.9, 1001.10, 1001.11, 1001.12, 1001.13, 1001.14, 1001.15, 1001.16, 1010.9, 1010.10, 1010.11, 1010.12, 1010.13, 1010.14, 1010.15, 1010.16, 1011.9, 1011.10, 1011.11, 1011.12, 1011.13, 1011.14, 1011.15, 1011.16, 1100.9, 1100.10, 1100.11, 1100.12, 1100.13, 1100.14, 1100.15, 1100.16, 1101.9, 1101.10, 1101.11, 1101.12, 1101.13, 1101.14, 1101.15, 1101.16, 1110.9, 1110.10, 1110.11, 1110.12, 1110.13, 1110.14, 1110.15, 1110.16, 1111.9, 1111.10, 1111.11, 1111.12, 1111.13, 1111.14, 1111.15, 1111.16, IC5.10 (GND), IC6.10 (GND), IC7.10 (GND), IC8.10 (GND), IC9.10 (GND), IC10.10 (GND), IC11.10 (GND), IC12.10 (GND), IC13.10 (GND), IC14.10 (GND), IC15.10 (GND), IC16.10 (GND), IC17.10 (GND), IC18.10 (GND), IC19.10 (GND), IC20.10 (GND); also elsewhere on the board
unnamed: 0000.1, IC5.17 (A4), RN2.2
unnamed: 0000.2, IC5.15 (A3), RN2.3
unnamed: 0000.3, IC5.13 (A2), RN2.4
unnamed: 0000.4, IC5.11 (A1), RN2.5
unnamed: 0000.5, IC5.8 (A4), RN2.6
unnamed: 0000.6, IC5.6 (A3), RN2.7
unnamed: 0000.7, IC5.4 (A2), RN2.8
unnamed: 0000.8, IC5.2 (A1), RN2.9
unnamed: 0001.1, IC6.17 (A4), RN3.2
unnamed: 0001.2, IC6.15 (A3), RN3.3
unnamed: 0001.3, IC6.13 (A2), RN3.4
unnamed: 0001.4, IC6.11 (A1), RN3.5
unnamed: 0001.5, IC6.8 (A4), RN3.6
unnamed: 0001.6, IC6.6 (A3), RN3.7
unnamed: 0001.7, IC6.4 (A2), RN3.8
unnamed: 0001.8, IC6.2 (A1), RN3.9
unnamed: 0010.1, IC7.17 (A4), RN4.2
unnamed: 0010.2, IC7.15 (A3), RN4.3
unnamed: 0010.3, IC7.13 (A2), RN4.4
unnamed: 0010.4, IC7.11 (A1), RN4.5
unnamed: 0010.5, IC7.8 (A4), RN4.6
unnamed: 0010.6, IC7.6 (A3), RN4.7
unnamed: 0010.7, IC7.4 (A2), RN4.8
unnamed: 0010.8, IC7.2 (A1), RN4.9
unnamed: 0011.1, IC8.17 (A4), RN5.2
unnamed: 0011.2, IC8.15 (A3), RN5.3
unnamed: 0011.3, IC8.13 (A2), RN5.4
unnamed: 0011.4, IC8.11 (A1), RN5.5
unnamed: 0011.5, IC8.8 (A4), RN5.6
unnamed: 0011.6, IC8.6 (A3), RN5.7
unnamed: 0011.7, IC8.4 (A2), RN5.8
unnamed: 0011.8, IC8.2 (A1), RN5.9
unnamed: 0100.1, IC9.17 (A4), RN6.2
unnamed: 0100.2, IC9.15 (A3), RN6.3
unnamed: 0100.3, IC9.13 (A2), RN6.4
unnamed: 0100.4, IC9.11 (A1), RN6.5
unnamed: 0100.5, IC9.8 (A4), RN6.6
unnamed: 0100.6, IC9.6 (A3), RN6.7
unnamed: 0100.7, IC9.4 (A2), RN6.8
unnamed: 0100.8, IC9.2 (A1), RN6.9
unnamed: 0101.1, IC10.17 (A4), RN7.2
unnamed: 0101.2, IC10.15 (A3), RN7.3
unnamed: 0101.3, IC10.13 (A2), RN7.4
unnamed: 0101.4, IC10.11 (A1), RN7.5
unnamed: 0101.5, IC10.8 (A4), RN7.6
unnamed: 0101.6, IC10.6 (A3), RN7.7
unnamed: 0101.7, IC10.4 (A2), RN7.8
unnamed: 0101.8, IC10.2 (A1), RN7.9
unnamed: 0110.1, IC11.17 (A4), RN8.2
unnamed: 0110.2, IC11.15 (A3), RN8.3
unnamed: 0110.3, IC11.13 (A2), RN8.4
unnamed: 0110.4, IC11.11 (A1), RN8.5
unnamed: 0110.5, IC11.8 (A4), RN8.6
unnamed: 0110.6, IC11.6 (A3), RN8.7
unnamed: 0110.7, IC11.4 (A2), RN8.8
unnamed: 0110.8, IC11.2 (A1), RN8.9
unnamed: 0111.1, IC12.17 (A4), RN9.2
unnamed: 0111.2, IC12.15 (A3), RN9.3
unnamed: 0111.3, IC12.13 (A2), RN9.4
unnamed: 0111.4, IC12.11 (A1), RN9.5
unnamed: 0111.5, IC12.8 (A4), RN9.6
unnamed: 0111.6, IC12.6 (A3), RN9.7
unnamed: 0111.7, IC12.4 (A2), RN9.8
unnamed: 0111.8, IC12.2 (A1), RN9.9
unnamed: 1000.1, IC13.17 (A4), RN10.2
unnamed: 1000.2, IC13.15 (A3), RN10.3
unnamed: 1000.3, IC13.13 (A2), RN10.4
unnamed: 1000.4, IC13.11 (A1), RN10.5
unnamed: 1000.5, IC13.8 (A4), RN10.6
unnamed: 1000.6, IC13.6 (A3), RN10.7
unnamed: 1000.7, IC13.4 (A2), RN10.8
unnamed: 1000.8, IC13.2 (A1), RN10.9
unnamed: 1001.1, IC14.17 (A4), RN11.2
unnamed: 1001.2, IC14.15 (A3), RN11.3
unnamed: 1001.3, IC14.13 (A2), RN11.4
unnamed: 1001.4, IC14.11 (A1), RN11.5
unnamed: 1001.5, IC14.8 (A4), RN11.6
unnamed: 1001.6, IC14.6 (A3), RN11.7
unnamed: 1001.7, IC14.4 (A2), RN11.8
unnamed: 1001.8, IC14.2 (A1), RN11.9
unnamed: R1.2, RD0.A
unnamed: 1010.1, IC15.17 (A4), RN12.2
unnamed: 1010.2, IC15.15 (A3), RN12.3
unnamed: 1010.3, IC15.13 (A2), RN12.4
unnamed: 1010.4, IC15.11 (A1), RN12.5
unnamed: 1010.5, IC15.8 (A4), RN12.6
unnamed: 1010.6, IC15.6 (A3), RN12.7
unnamed: 1010.7, IC15.4 (A2), RN12.8
unnamed: 1010.8, IC15.2 (A1), RN12.9
unnamed: R2.2, RD1.A
unnamed: 1011.1, IC16.17 (A4), RN13.2
unnamed: 1011.2, IC16.15 (A3), RN13.3
unnamed: 1011.3, IC16.13 (A2), RN13.4
unnamed: 1011.4, IC16.11 (A1), RN13.5
unnamed: 1011.5, IC16.8 (A4), RN13.6
unnamed: 1011.6, IC16.6 (A3), RN13.7
unnamed: 1011.7, IC16.4 (A2), RN13.8
unnamed: 1011.8, IC16.2 (A1), RN13.9
unnamed: R3.2, RD2.A
unnamed: 1100.1, IC17.17 (A4), RN14.2
unnamed: 1100.2, IC17.15 (A3), RN14.3
unnamed: 1100.3, IC17.13 (A2), RN14.4
unnamed: 1100.4, IC17.11 (A1), RN14.5
unnamed: 1100.5, IC17.8 (A4), RN14.6
unnamed: 1100.6, IC17.6 (A3), RN14.7
unnamed: 1100.7, IC17.4 (A2), RN14.8
unnamed: 1100.8, IC17.2 (A1), RN14.9
unnamed: R4.2, RD3.A
unnamed: 1101.1, IC18.17 (A4), RN15.2
unnamed: 1101.2, IC18.15 (A3), RN15.3
unnamed: 1101.3, IC18.13 (A2), RN15.4
unnamed: 1101.4, IC18.11 (A1), RN15.5
unnamed: 1101.5, IC18.8 (A4), RN15.6
unnamed: 1101.6, IC18.6 (A3), RN15.7
unnamed: 1101.7, IC18.4 (A2), RN15.8
unnamed: 1101.8, IC18.2 (A1), RN15.9
unnamed: R5.2, RD4.A
unnamed: 1110.1, IC19.17 (A4), RN16.2
unnamed: 1110.2, IC19.15 (A3), RN16.3
unnamed: 1110.3, IC19.13 (A2), RN16.4
unnamed: 1110.4, IC19.11 (A1), RN16.5
unnamed: 1110.5, IC19.8 (A4), RN16.6
unnamed: 1110.6, IC19.6 (A3), RN16.7
unnamed: 1110.7, IC19.4 (A2), RN16.8
unnamed: 1110.8, IC19.2 (A1), RN16.9
unnamed: R6.2, RD5.A
unnamed: 1111.1, IC20.17 (A4), RN17.2
unnamed: 1111.2, IC20.15 (A3), RN17.3
unnamed: 1111.3, IC20.13 (A2), RN17.4
unnamed: 1111.4, IC20.11 (A1), RN17.5
unnamed: 1111.5, IC20.8 (A4), RN17.6
unnamed: 1111.6, IC20.6 (A3), RN17.7
unnamed: 1111.7, IC20.4 (A2), RN17.8
unnamed: 1111.8, IC20.2 (A1), RN17.9
unnamed: R7.2, RD6.A
unnamed: R8.2, RD7.A
unnamed: R9.2, RD8.A
unnamed: R10.2, RD9.A
unnamed: R11.2, RD10.A
unnamed: R12.2, RD11.A
unnamed: R13.2, RD12.A
unnamed: R14.2, RD13.A
unnamed: R15.2, RD14.A
unnamed: R16.2, RD15.A
SW0: IC5.1 (G), IC5.19 (G), RD0.K (C); also elsewhere on the board
SW1: IC6.1 (G), IC6.19 (G), RD1.K (C); also elsewhere on the board
SW2: IC7.1 (G), IC7.19 (G), RD2.K (C); also elsewhere on the board
SW3: IC8.1 (G), IC8.19 (G), RD3.K (C); also elsewhere on the board
SW4: IC9.1 (G), IC9.19 (G), RD4.K (C); also elsewhere on the board
SW5: IC10.1 (G), IC10.19 (G), RD5.K (C); also elsewhere on the board
SW6: IC11.1 (G), IC11.19 (G), RD6.K (C); also elsewhere on the board
SW7: IC12.1 (G), IC12.19 (G), RD7.K (C); also elsewhere on the board
SW8: IC13.1 (G), IC13.19 (G), RD8.K (C); also elsewhere on the board
SW9: IC14.1 (G), IC14.19 (G), RD9.K (C); also elsewhere on the board
SW10: IC15.1 (G), IC15.19 (G), RD10.K (C); also elsewhere on the board
SW11: IC16.1 (G), IC16.19 (G), RD11.K (C); also elsewhere on the board
SW12: IC17.1 (G), IC17.19 (G), RD12.K (C); also elsewhere on the board
SW13: IC18.1 (G), IC18.19 (G), RD13.K (C); also elsewhere on the board
SW14: IC19.1 (G), IC19.19 (G), RD14.K (C); also elsewhere on the board
SW15: IC20.1 (G), IC20.19 (G), RD15.K (C); also elsewhere on the board
VCC: IC5.20 (VCC), IC6.20 (VCC), IC7.20 (VCC), IC8.20 (VCC), IC9.20 (VCC), IC10.20 (VCC), IC11.20 (VCC), IC12.20 (VCC), IC13.20 (VCC), IC14.20 (VCC), IC15.20 (VCC), IC16.20 (VCC), IC17.20 (VCC), IC18.20 (VCC), IC19.20 (VCC), IC20.20 (VCC), R1.1, R2.1, R3.1, R4.1, R5.1, R6.1, R7.1, R8.1, R9.1, R10.1, R11.1, R12.1, R13.1, R14.1, R15.1, R16.1, RN2.1, RN3.1, RN4.1, RN5.1, RN6.1, RN7.1, RN8.1, RN9.1, RN10.1, RN11.1, RN12.1, RN13.1, RN14.1, RN15.1, RN16.1, RN17.1; also elsewhere on the board

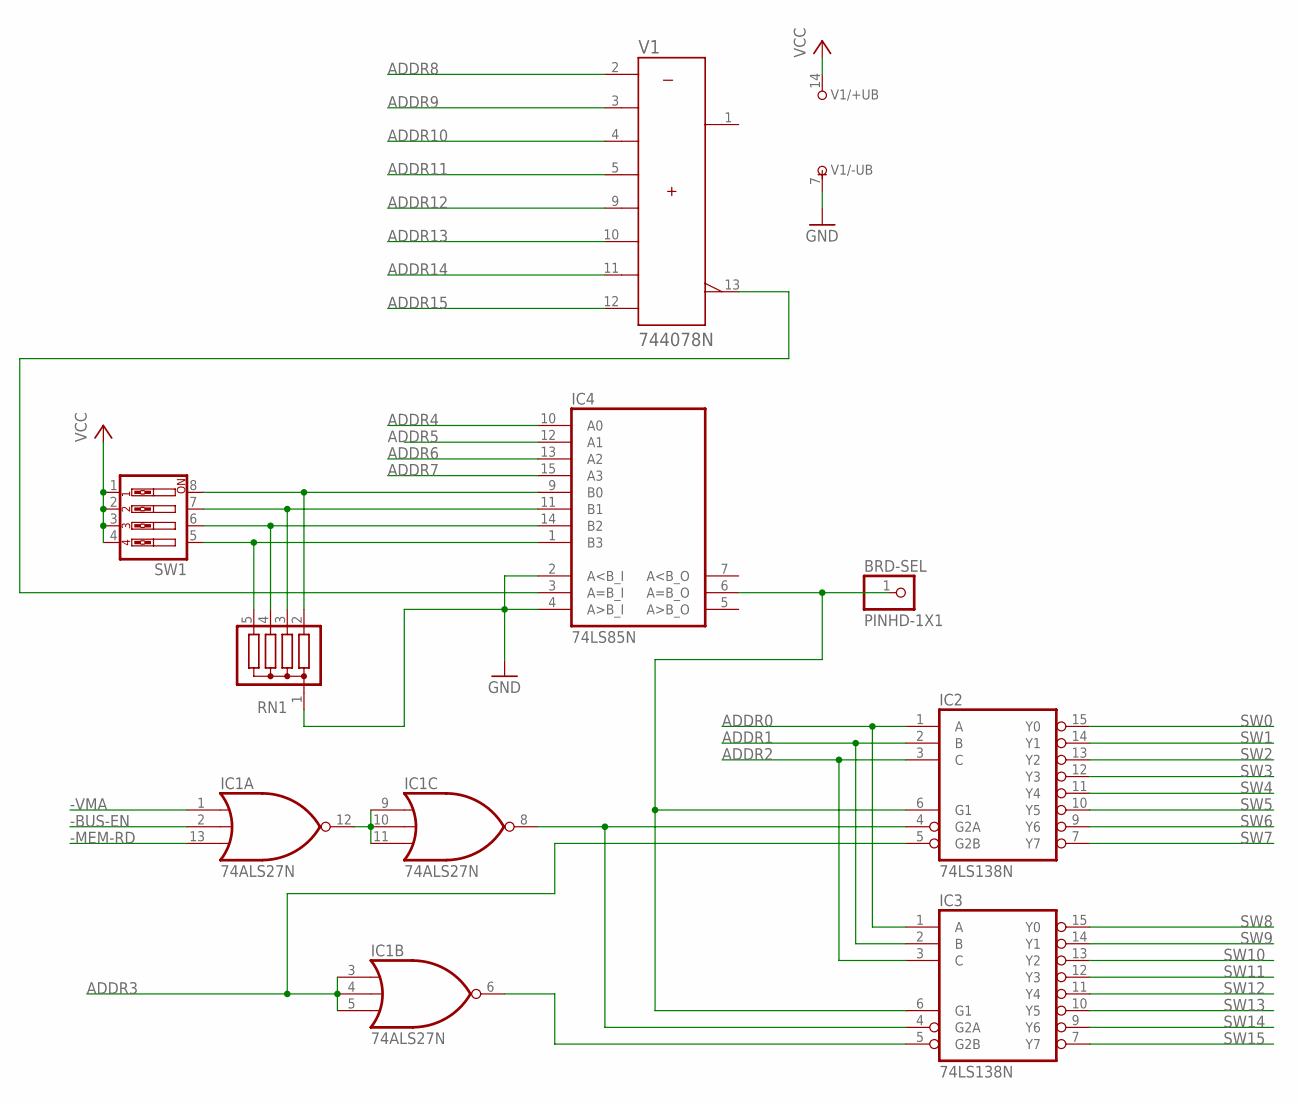
[picture p348: schematic Mem Switch V1.1.sch, sheet 3]

Parts:
BRD-SEL: PINHD-1X1; 1X01
IC1: 74ALS27N; DIL14
IC2, IC3: 74LS138N; DIL16
IC4: 74LS85N; DIL16
RN1: G04R; SIL5
SW1: SW_DIP-4; EDG-04
V1: 744078N; DIL14

Connections:
-BUS-EN: IC1.2 (I1); also elsewhere on the board
-MEM-RD: IC1.13 (I2); also elsewhere on the board
-VMA: IC1.1 (I0); also elsewhere on the board
ADDR0: IC2.1 (A), IC3.1 (A); also elsewhere on the board
ADDR1: IC2.2 (B), IC3.2 (B); also elsewhere on the board
ADDR2: IC2.3 (C), IC3.3 (C); also elsewhere on the board
ADDR3: IC1.3 (I0), IC1.4 (I1), IC1.5 (I2), IC2.5 (G2B); also elsewhere on the board
ADDR4: IC4.10 (A0); also elsewhere on the board
ADDR5: IC4.12 (A1); also elsewhere on the board
ADDR6: IC4.13 (A2); also elsewhere on the board
ADDR7: IC4.15 (A3); also elsewhere on the board
ADDR8: V1.2 (A); also elsewhere on the board
ADDR9: V1.3 (B); also elsewhere on the board
ADDR10: V1.4 (C); also elsewhere on the board
ADDR11: V1.5 (D); also elsewhere on the board
ADDR12: V1.9 (E); also elsewhere on the board
ADDR13: V1.10 (F); also elsewhere on the board
ADDR14: V1.11 (G); also elsewhere on the board
ADDR15: V1.12 (H); also elsewhere on the board
GND: IC1.7 (GND), IC2.8 (GND), IC3.8 (GND), IC4.2 (A<B_I), IC4.4 (A>B_I), IC4.8 (GND), RN1.1, V1.7 (-UB); also elsewhere on the board
unnamed: BRD-SEL.1, IC2.6 (G1), IC3.6 (G1), IC4.6 (A=B_O)
unnamed: IC1.9 (I0), IC1.10 (I1), IC1.11 (I2), IC1.12 (O)
unnamed: IC4.9 (B0), RN1.2, SW1.8
unnamed: IC1.6 (O), IC3.5 (G2B)
unnamed: IC4.11 (B1), RN1.3, SW1.7
unnamed: IC4.3 (A=B_I), V1.13 (W)
unnamed: IC4.14 (B2), RN1.4, SW1.6
unnamed: IC4.1 (B3), RN1.5, SW1.5
unnamed: IC1.8 (O), IC2.4 (G2A), IC3.4 (G2A)
SW0: IC2.15 (Y0); also elsewhere on the board
SW1: IC2.14 (Y1); also elsewhere on the board
SW2: IC2.13 (Y2); also elsewhere on the board
SW3: IC2.12 (Y3); also elsewhere on the board
SW4: IC2.11 (Y4); also elsewhere on the board
SW5: IC2.10 (Y5); also elsewhere on the board
SW6: IC2.9 (Y6); also elsewhere on the board
SW7: IC2.7 (Y7); also elsewhere on the board
SW8: IC3.15 (Y0); also elsewhere on the board
SW9: IC3.14 (Y1); also elsewhere on the board
SW10: IC3.13 (Y2); also elsewhere on the board
SW11: IC3.12 (Y3); also elsewhere on the board
SW12: IC3.11 (Y4); also elsewhere on the board
SW13: IC3.10 (Y5); also elsewhere on the board
SW14: IC3.9 (Y6); also elsewhere on the board
SW15: IC3.7 (Y7); also elsewhere on the board
VCC: IC1.14 (VCC), IC2.16 (VCC), IC3.16 (VCC), IC4.16 (VCC), SW1.1, SW1.2, SW1.3, SW1.4, V1.14 (+UB); also elsewhere on the board

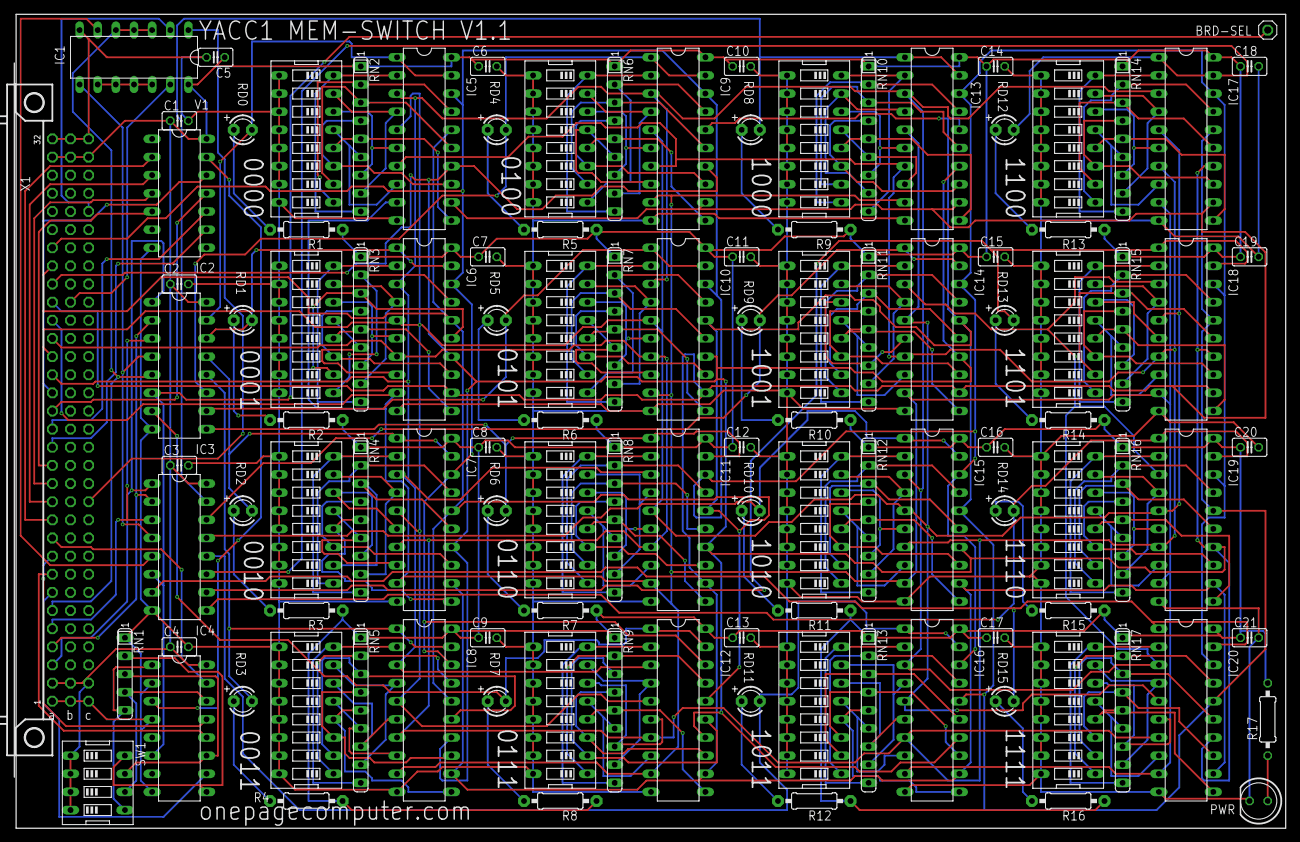
[picture p349: board Mem Switch V1.1.brd from above]

Board: 2 copper layers, 177.8 x 114.0 mm, 112 parts (0 on the bottom side), 199 nets.
