ksr/YACC1-D/hardware/cards/io/eagle/v1.1/IO V1.1.brd

## EAGLE design hardware/cards/io/eagle/v1.1/IO V1.1.brd (2026-09-20)

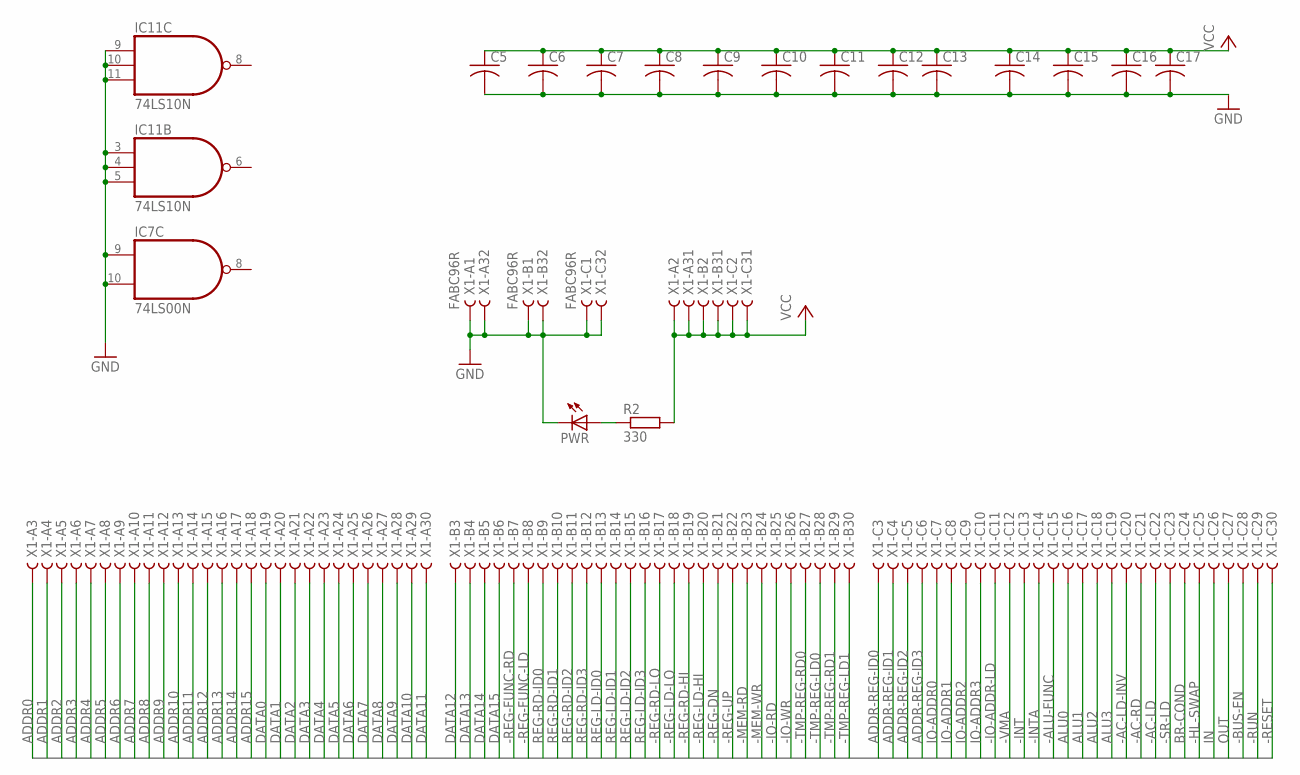
[picture p352: schematic IO V1.1.sch, sheet 1, BUS]

Parts:
C5, C6, C7, C8, C9, C10, C11, C12, C13, C14, C15, C16, C17: C-US025-024X044; C025-024X044
IC7: 74LS00N; DIL14
IC11: 74LS10N; DIL14
PWR: LED5MM
R2: 330; 0207/10
X1: FABC96R

Connections:
-AC-LD: X1.C22
-AC-LD-INV: X1.C20
-AC-RD: X1.C21
-ALU-FUNC: X1.C15
-BUS-EN: X1.C28
-HL-SWAP: X1.C25
-INT: X1.C13; also elsewhere on the board
-INTA: X1.C14
-IO-ADDR-LD: X1.C11
-IO-RD: X1.B25; also elsewhere on the board
-IO-WR: X1.B26; also elsewhere on the board
-MEM-RD: X1.B23
-MEM-WR: X1.B24
-REG-DN: X1.B21
-REG-FUNC-LD: X1.B8
-REG-FUNC-RD: X1.B7
-REG-LD-HI: X1.B20
-REG-LD-LO: X1.B18
-REG-RD-HI: X1.B19
-REG-RD-LO: X1.B17
-REG-UP: X1.B22
-RESET: X1.C30; also elsewhere on the board
-RUN: X1.C29
-SR-LD: X1.C23
-TMP-REG-LD0: X1.B28
-TMP-REG-LD1: X1.B30
-TMP-REG-RD0: X1.B27
-TMP-REG-RD1: X1.B29
-VMA: X1.C12
ADDR0: X1.A3
ADDR1: X1.A4
ADDR2: X1.A5
ADDR3: X1.A6
ADDR4: X1.A7
ADDR5: X1.A8
ADDR6: X1.A9
ADDR7: X1.A10
ADDR8: X1.A11
ADDR9: X1.A12
ADDR10: X1.A13
ADDR11: X1.A14
ADDR12: X1.A15
ADDR13: X1.A16
ADDR14: X1.A17
ADDR15: X1.A18
ADDR-REG-ID0: X1.C3
ADDR-REG-ID1: X1.C4
ADDR-REG-ID2: X1.C5
ADDR-REG-ID3: X1.C6
ALU0: X1.C16
ALU1: X1.C17
ALU2: X1.C18
ALU3: X1.C19
BR-COND: X1.C24
DATA0: X1.A19; also elsewhere on the board
DATA1: X1.A20; also elsewhere on the board
DATA2: X1.A21; also elsewhere on the board
DATA3: X1.A22; also elsewhere on the board
DATA4: X1.A23; also elsewhere on the board
DATA5: X1.A24; also elsewhere on the board
DATA6: X1.A25; also elsewhere on the board
DATA7: X1.A26; also elsewhere on the board
DATA8: X1.A27
DATA9: X1.A28
DATA10: X1.A29
DATA11: X1.A30
DATA12: X1.B3
DATA13: X1.B4
DATA14: X1.B5
DATA15: X1.B6
GND: C5.2, C6.2, C7.2, C8.2, C9.2, C10.2, C11.2, C12.2, C13.2, C14.2, C15.2, C16.2, C17.2, IC7.7 (GND), IC7.9 (I0), IC7.10 (I1), IC11.3 (I0), IC11.4 (I1), IC11.5 (I2), IC11.7 (GND), IC11.9 (I0), IC11.10 (I1), IC11.11 (I2), PWR.K (C), X1.A1, X1.A32, X1.B1, X1.B32, X1.C1, X1.C32; also elsewhere on the board
IN: X1.C26; also elsewhere on the board
IO-ADDR0: X1.C7; also elsewhere on the board
IO-ADDR1: X1.C8; also elsewhere on the board
IO-ADDR2: X1.C9; also elsewhere on the board
IO-ADDR3: X1.C10; also elsewhere on the board
unnamed: PWR.A, R2.1
OUT: X1.C27; also elsewhere on the board
REG-LD-ID0: X1.B13
REG-LD-ID1: X1.B14
REG-LD-ID2: X1.B15
REG-LD-ID3: X1.B16
REG-RD-ID0: X1.B9
REG-RD-ID1: X1.B10
REG-RD-ID2: X1.B11
REG-RD-ID3: X1.B12
VCC: C5.1, C6.1, C7.1, C8.1, C9.1, C10.1, C11.1, C12.1, C13.1, C14.1, C15.1, C16.1, C17.1, IC7.14 (VCC), IC11.14 (VCC), R2.2, X1.A2, X1.A31, X1.B2, X1.B31, X1.C2, X1.C31; also elsewhere on the board

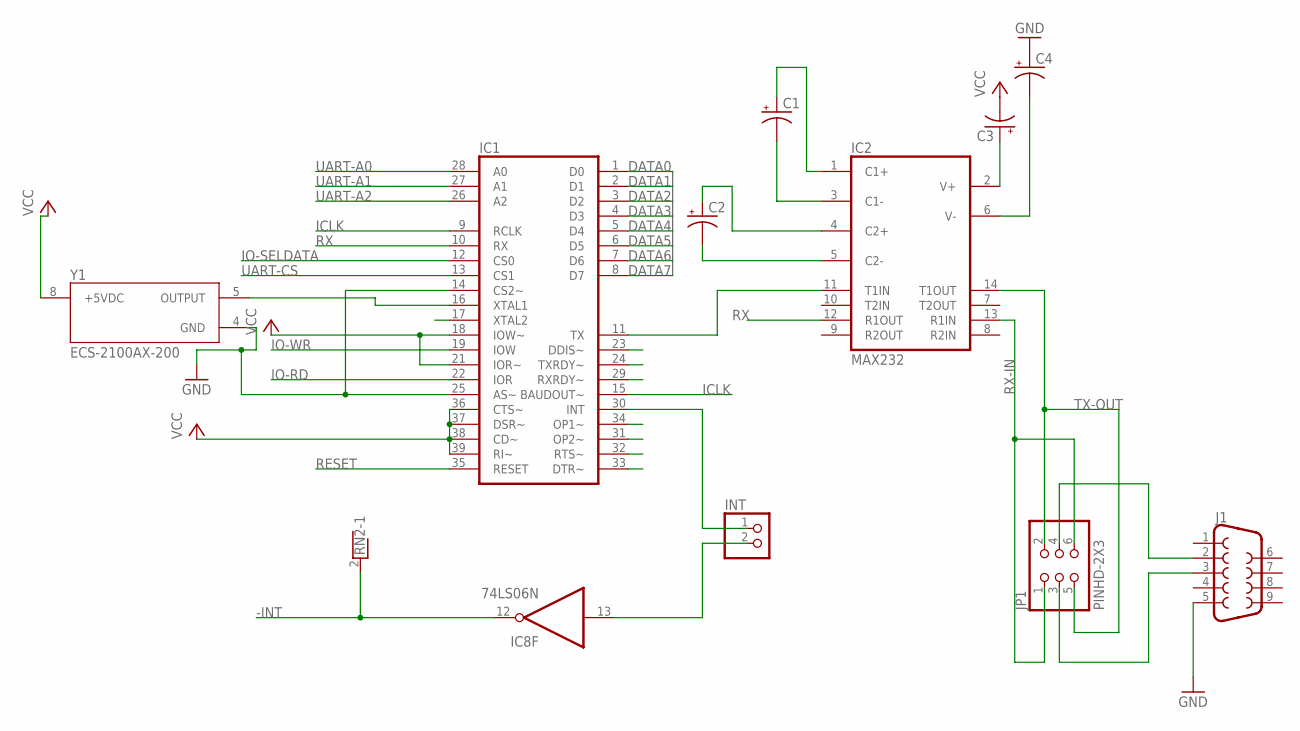
[picture p353: schematic IO V1.1.sch, sheet 2, Serial Interface]

Parts:
C1, C2, C3, C4: CPOL-USE2,5-6E; E2,5-6E
IC1: XR-16C550P; DIL40
IC2: MAX232; DIL16
IC8: 74LS06N; DIL14
INT: PINHD-1X2; 1X02
J1: DB9FEMALE; DB9
JP1: PINHD-2X3; 2X03
RN2: RNX6; RN-7
Y1: ECS-2100AX-200

Connections:
-INT: IC8.12 (O), RN2.2; also elsewhere on the board
DATA0: IC1.1 (D0); also elsewhere on the board
DATA1: IC1.2 (D1); also elsewhere on the board
DATA2: IC1.3 (D2); also elsewhere on the board
DATA3: IC1.4 (D3); also elsewhere on the board
DATA4: IC1.5 (D4); also elsewhere on the board
DATA5: IC1.6 (D5); also elsewhere on the board
DATA6: IC1.7 (D6); also elsewhere on the board
DATA7: IC1.8 (D7); also elsewhere on the board
GND: C4.+, IC1.14 (CS2~), IC1.20 (GND), IC1.25 (AS~), IC2.15 (GND), IC8.7 (GND), J1.5, Y1.4 (GND); also elsewhere on the board
ICLK: IC1.9 (RCLK), IC1.15 (BAUDOUT~)
IO-RD: IC1.22 (IOR); also elsewhere on the board
IO-SELDATA: IC1.12 (CS0); also elsewhere on the board
IO-WR: IC1.19 (IOW); also elsewhere on the board
unnamed: IC1.16 (XTAL1), Y1.5 (OUTPUT)
unnamed: J1.2, JP1.4
unnamed: J1.3, JP1.3
unnamed: IC1.11 (TX), IC2.11 (T1IN)
unnamed: C2.-, IC2.5 (C2-)
unnamed: C2.+, IC2.4 (C2+)
unnamed: IC1.30 (INT), INT.1
unnamed: C1.-, IC2.3 (C1-)
unnamed: C1.+, IC2.1 (C1+)
unnamed: C3.+, IC2.2 (V+)
unnamed: C4.-, IC2.6 (V-)
unnamed: IC8.13 (I), INT.2
RESET: IC1.35 (RESET); also elsewhere on the board
RX: IC1.10 (RX), IC2.12 (R1OUT)
RX-IN: IC2.13 (R1IN), JP1.1, JP1.6
TX-OUT: IC2.14 (T1OUT), JP1.2, JP1.5
UART-A0: IC1.28 (A0); also elsewhere on the board
UART-A1: IC1.27 (A1); also elsewhere on the board
UART-A2: IC1.26 (A2); also elsewhere on the board
UART-CS: IC1.13 (CS1); also elsewhere on the board
VCC: C3.-, IC1.18 (IOW~), IC1.21 (IOR~), IC1.36 (CTS~), IC1.37 (DSR~), IC1.38 (CD~), IC1.39 (RI~), IC1.40 (VCC), IC2.16 (VCC), IC8.14 (VCC), Y1.8 (+5VDC); also elsewhere on the board

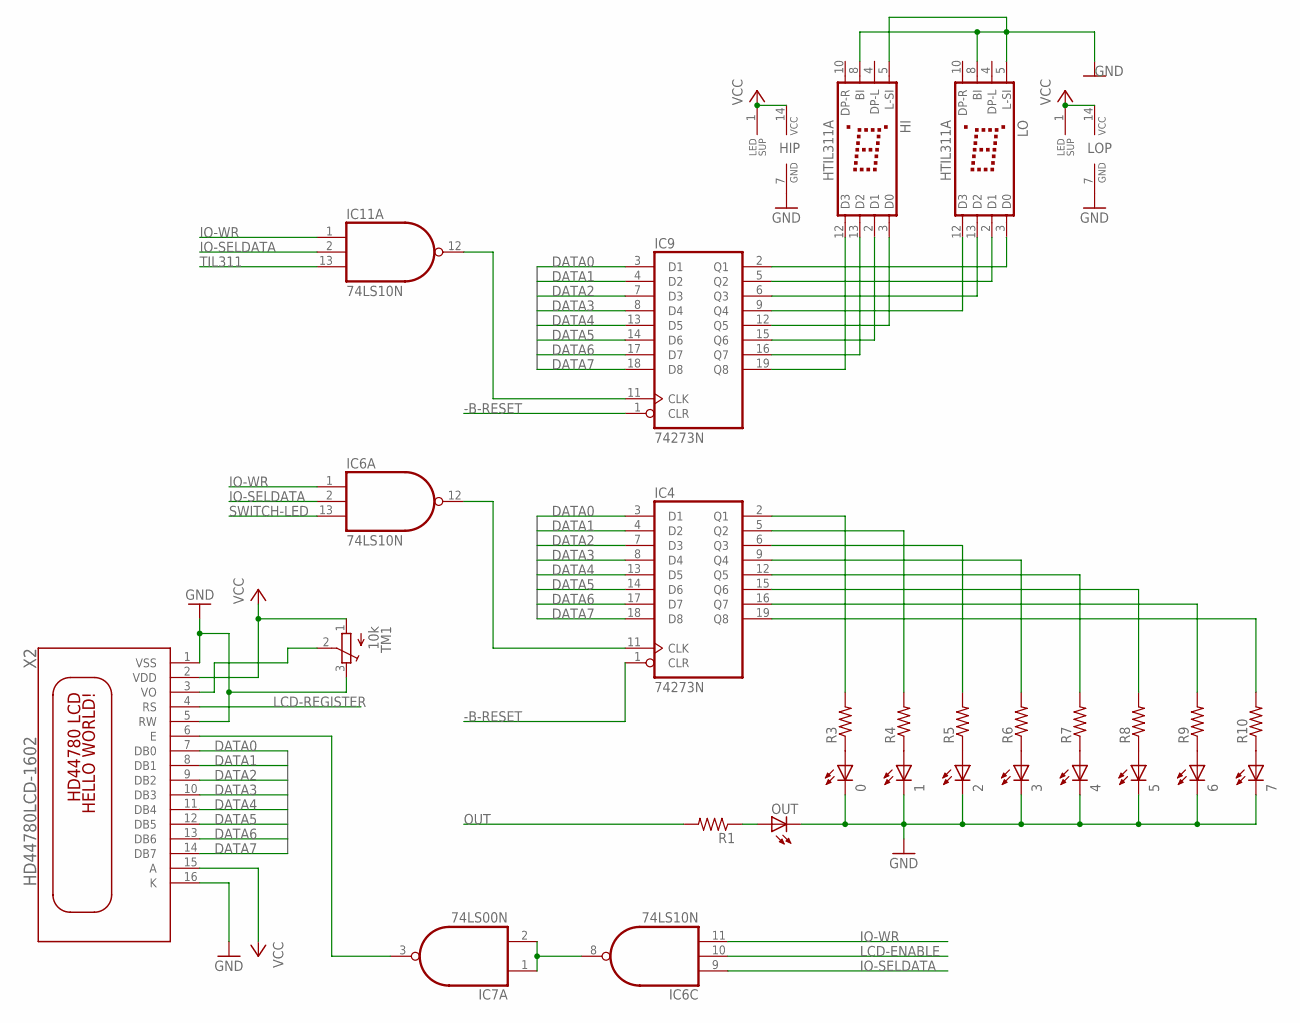
[picture p354: schematic IO V1.1.sch, sheet 3, Output]

Parts:
0, 1, 2, 3, 4, 5, 6, 7: LED5MM
HI: HTIL311A
IC4, IC9: 74273N; DIL20
IC6, IC11: 74LS10N; DIL14
IC7: 74LS00N; DIL14
LO: HTIL311A
OUT: LED5MM
R1, R3, R4, R5, R6, R7, R8, R9, R10: R-US_0207/10; 0207/10
TM1: 10k; TRIM-3386
X2: HD44780LCD-1602; LCD1602

Connections:
-B-RESET: IC4.1 (CLR), IC9.1 (CLR); also elsewhere on the board
DATA0: IC4.3 (D1), IC9.3 (D1), X2.7 (DB0); also elsewhere on the board
DATA1: IC4.4 (D2), IC9.4 (D2), X2.8 (DB1); also elsewhere on the board
DATA2: IC4.7 (D3), IC9.7 (D3), X2.9 (DB2); also elsewhere on the board
DATA3: IC4.8 (D4), IC9.8 (D4), X2.10 (DB3); also elsewhere on the board
DATA4: IC4.13 (D5), IC9.13 (D5), X2.11 (DB4); also elsewhere on the board
DATA5: IC4.14 (D6), IC9.14 (D6), X2.12 (DB5); also elsewhere on the board
DATA6: IC4.17 (D7), IC9.17 (D7), X2.13 (DB6); also elsewhere on the board
DATA7: IC4.18 (D8), IC9.18 (D8), X2.14 (DB7); also elsewhere on the board
GND: 0.K (C), 1.K (C), 2.K (C), 3.K (C), 4.K (C), 5.K (C), 6.K (C), 7.K (C), HI.5 (L-SI), HI.7 (GND), HI.8 (BI), IC4.10 (GND), IC6.7 (GND), IC7.7 (GND), IC9.10 (GND), IC11.7 (GND), LO.5 (L-SI), LO.7 (GND), LO.8 (BI), OUT.K (C), TM1.3 (E), X2.1 (VSS), X2.5 (RW), X2.16 (K); also elsewhere on the board
IO-SELDATA: IC6.2 (I1), IC6.9 (I0), IC11.2 (I1); also elsewhere on the board
IO-WR: IC6.1 (I0), IC6.11 (I2), IC11.1 (I0); also elsewhere on the board
LCD-ENABLE: IC6.10 (I1); also elsewhere on the board
LCD-REGISTER: X2.4 (RS); also elsewhere on the board
unnamed: OUT.A, R1.1
unnamed: 2.A, R5.1
unnamed: 3.A, R6.1
unnamed: 4.A, R7.1
unnamed: 0.A, R3.1
unnamed: 1.A, R4.1
unnamed: 5.A, R8.1
unnamed: 7.A, R10.1
unnamed: 6.A, R9.1
unnamed: IC4.19 (Q8), R10.2
unnamed: IC4.16 (Q7), R9.2
unnamed: IC4.15 (Q6), R8.2
unnamed: IC4.12 (Q5), R7.2
unnamed: IC4.9 (Q4), R6.2
unnamed: IC4.6 (Q3), R5.2
unnamed: IC4.5 (Q2), R4.2
unnamed: IC4.2 (Q1), R3.2
unnamed: HI.12 (D3), IC9.19 (Q8)
unnamed: IC7.3 (O), X2.6 (E)
unnamed: IC6.8 (O), IC7.1 (I0), IC7.2 (I1)
unnamed: IC4.11 (CLK), IC6.12 (O)
unnamed: TM1.2 (S), X2.3 (VO)
unnamed: HI.13 (D2), IC9.16 (Q7)
unnamed: HI.2 (D1), IC9.15 (Q6)
unnamed: HI.3 (D0), IC9.12 (Q5)
unnamed: IC9.9 (Q4), LO.12 (D3)
unnamed: IC9.6 (Q3), LO.13 (D2)
unnamed: IC9.5 (Q2), LO.2 (D1)
unnamed: IC9.2 (Q1), LO.3 (D0)
unnamed: IC9.11 (CLK), IC11.12 (O)
OUT: R1.2; also elsewhere on the board
SWITCH-LED: IC6.13 (I2); also elsewhere on the board
TIL311: IC11.13 (I2); also elsewhere on the board
VCC: HI.1 (LEDSUP), HI.14 (VCC), IC4.20 (VCC), IC6.14 (VCC), IC7.14 (VCC), IC9.20 (VCC), IC11.14 (VCC), LO.1 (LEDSUP), LO.14 (VCC), TM1.1 (A), X2.2 (VDD), X2.15 (A); also elsewhere on the board

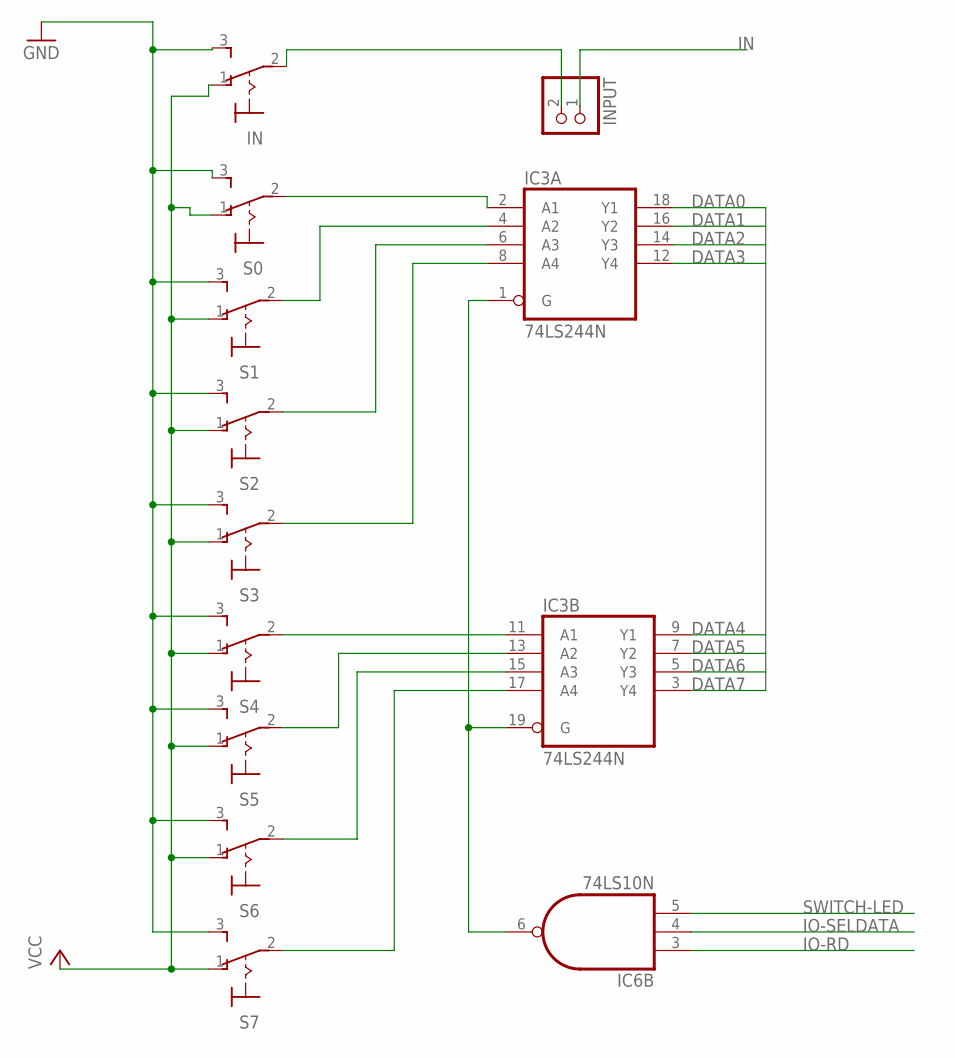
[picture p355: schematic IO V1.1.sch, sheet 4, Input]

Parts:
IC3: 74LS244N; DIL20
IC6: 74LS10N; DIL14
IN: M9040P
INPUT: PINHD-1X2; 1X02
S0, S1, S2, S3, S4, S5, S6, S7: M9040P

Connections:
DATA0: IC3.18 (Y1); also elsewhere on the board
DATA1: IC3.16 (Y2); also elsewhere on the board
DATA2: IC3.14 (Y3); also elsewhere on the board
DATA3: IC3.12 (Y4); also elsewhere on the board
DATA4: IC3.9 (Y1); also elsewhere on the board
DATA5: IC3.7 (Y2); also elsewhere on the board
DATA6: IC3.5 (Y3); also elsewhere on the board
DATA7: IC3.3 (Y4); also elsewhere on the board
GND: IC3.10 (GND), IC6.7 (GND), IN.3 (S), S0.3 (S), S1.3 (S), S2.3 (S), S3.3 (S), S4.3 (S), S5.3 (S), S6.3 (S), S7.3 (S); also elsewhere on the board
IN: INPUT.1; also elsewhere on the board
IO-RD: IC6.3 (I0); also elsewhere on the board
IO-SELDATA: IC6.4 (I1); also elsewhere on the board
unnamed: IC3.2 (A1), S0.2
unnamed: IC3.4 (A2), S1.2
unnamed: IC3.6 (A3), S2.2
unnamed: IC3.8 (A4), S3.2
unnamed: IC3.11 (A1), S4.2
unnamed: IC3.13 (A2), S5.2
unnamed: IC3.15 (A3), S6.2
unnamed: IC3.17 (A4), S7.2
unnamed: IC3.1 (G), IC3.19 (G), IC6.6 (O)
unnamed: IN.2, INPUT.2
SWITCH-LED: IC6.5 (I2); also elsewhere on the board
VCC: IC3.20 (VCC), IC6.14 (VCC), IN.1 (O), S0.1 (O), S1.1 (O), S2.1 (O), S3.1 (O), S4.1 (O), S5.1 (O), S6.1 (O), S7.1 (O); also elsewhere on the board

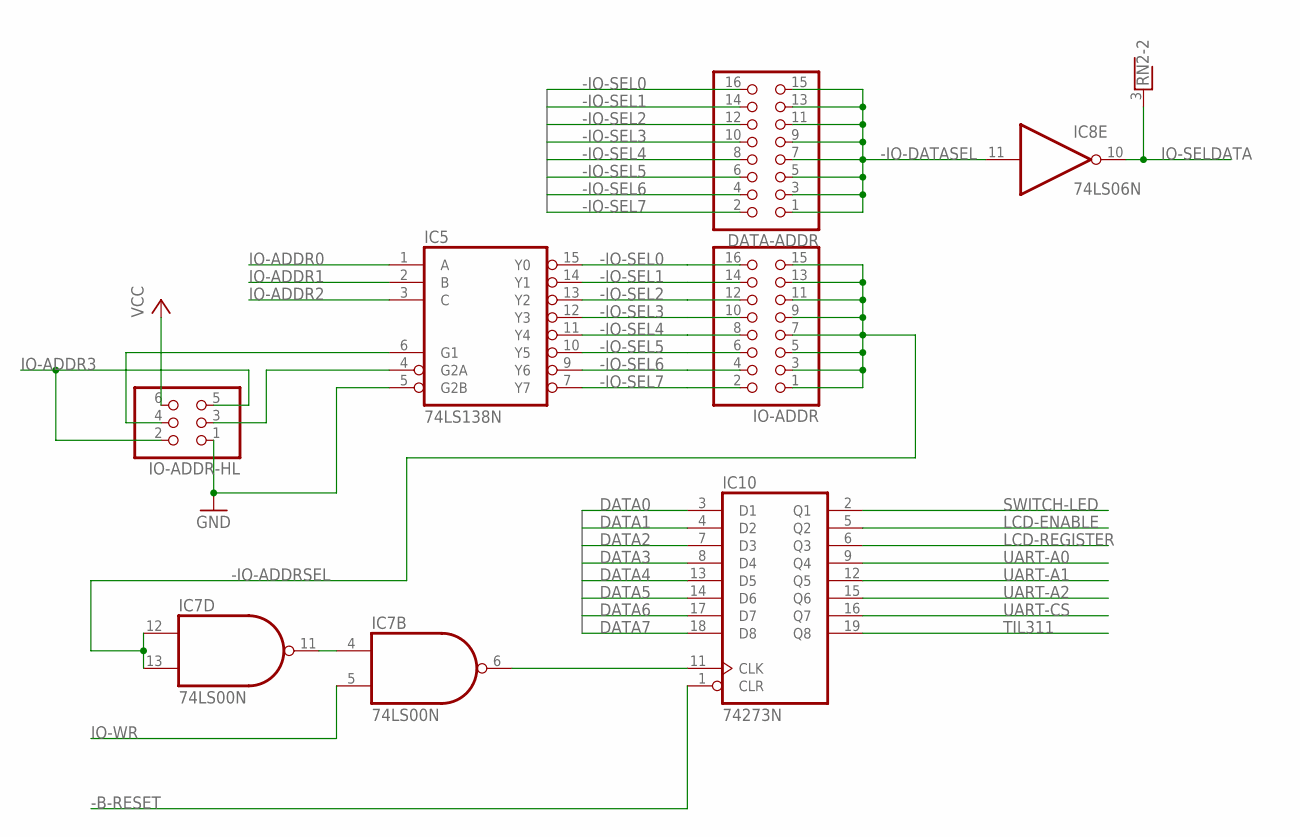
[picture p356: schematic IO V1.1.sch, sheet 5, Board Select logic]

Parts:
DATA-ADDR: PINHD-2X8; 2X08
IC5: 74LS138N; DIL16
IC7: 74LS00N; DIL14
IC8: 74LS06N; DIL14
IC10: 74273N; DIL20
IO-ADDR: PINHD-2X8; 2X08
IO-ADDR-HL: PINHD-2X3; 2X03
RN2: RNX6; RN-7

Connections:
-B-RESET: IC10.1 (CLR); also elsewhere on the board
-IO-ADDRSEL: IC7.12 (I0), IC7.13 (I1), IO-ADDR.1, IO-ADDR.3, IO-ADDR.5, IO-ADDR.7, IO-ADDR.9, IO-ADDR.11, IO-ADDR.13, IO-ADDR.15
-IO-DATASEL: DATA-ADDR.1, DATA-ADDR.3, DATA-ADDR.5, DATA-ADDR.7, DATA-ADDR.9, DATA-ADDR.11, DATA-ADDR.13, DATA-ADDR.15, IC8.11 (I)
-IO-SEL0: DATA-ADDR.16, IC5.15 (Y0), IO-ADDR.16
-IO-SEL1: DATA-ADDR.14, IC5.14 (Y1), IO-ADDR.14
-IO-SEL2: DATA-ADDR.12, IC5.13 (Y2), IO-ADDR.12
-IO-SEL3: DATA-ADDR.10, IC5.12 (Y3), IO-ADDR.10
-IO-SEL4: DATA-ADDR.8, IC5.11 (Y4), IO-ADDR.8
-IO-SEL5: DATA-ADDR.6, IC5.10 (Y5), IO-ADDR.6
-IO-SEL6: DATA-ADDR.4, IC5.9 (Y6), IO-ADDR.4
-IO-SEL7: DATA-ADDR.2, IC5.7 (Y7), IO-ADDR.2
DATA0: IC10.3 (D1); also elsewhere on the board
DATA1: IC10.4 (D2); also elsewhere on the board
DATA2: IC10.7 (D3); also elsewhere on the board
DATA3: IC10.8 (D4); also elsewhere on the board
DATA4: IC10.13 (D5); also elsewhere on the board
DATA5: IC10.14 (D6); also elsewhere on the board
DATA6: IC10.17 (D7); also elsewhere on the board
DATA7: IC10.18 (D8); also elsewhere on the board
GND: IC5.5 (G2B), IC5.8 (GND), IC7.7 (GND), IC8.7 (GND), IC10.10 (GND), IO-ADDR-HL.1; also elsewhere on the board
IO-ADDR0: IC5.1 (A); also elsewhere on the board
IO-ADDR1: IC5.2 (B); also elsewhere on the board
IO-ADDR2: IC5.3 (C); also elsewhere on the board
IO-ADDR3: IO-ADDR-HL.2, IO-ADDR-HL.5; also elsewhere on the board
IO-SELDATA: IC8.10 (O), RN2.3; also elsewhere on the board
IO-WR: IC7.5 (I1); also elsewhere on the board
LCD-ENABLE: IC10.5 (Q2); also elsewhere on the board
LCD-REGISTER: IC10.6 (Q3); also elsewhere on the board
unnamed: IC5.4 (G2A), IO-ADDR-HL.3
unnamed: IC5.6 (G1), IO-ADDR-HL.4
unnamed: IC7.6 (O), IC10.11 (CLK)
unnamed: IC7.4 (I0), IC7.11 (O)
SWITCH-LED: IC10.2 (Q1); also elsewhere on the board
TIL311: IC10.19 (Q8); also elsewhere on the board
UART-A0: IC10.9 (Q4); also elsewhere on the board
UART-A1: IC10.12 (Q5); also elsewhere on the board
UART-A2: IC10.15 (Q6); also elsewhere on the board
UART-CS: IC10.16 (Q7); also elsewhere on the board
VCC: IC5.16 (VCC), IC7.14 (VCC), IC8.14 (VCC), IC10.20 (VCC), IO-ADDR-HL.6; also elsewhere on the board

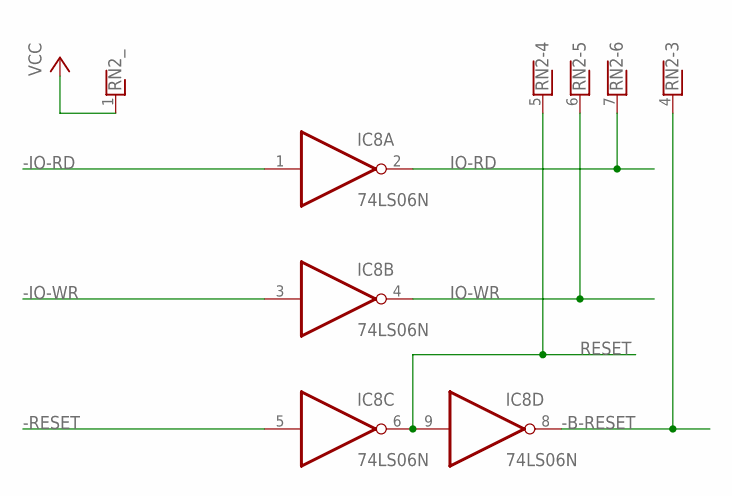
[picture p357: schematic IO V1.1.sch, sheet 6, Bus Buffering]

Parts:
IC8: 74LS06N; DIL14
RN2: RNX6; RN-7

Connections:
-B-RESET: IC8.8 (O), RN2.4; also elsewhere on the board
-IO-RD: IC8.1 (I); also elsewhere on the board
-IO-WR: IC8.3 (I); also elsewhere on the board
-RESET: IC8.5 (I); also elsewhere on the board
GND: IC8.7 (GND); also elsewhere on the board
IO-RD: IC8.2 (O), RN2.7; also elsewhere on the board
IO-WR: IC8.4 (O), RN2.6; also elsewhere on the board
RESET: IC8.6 (O), IC8.9 (I), RN2.5; also elsewhere on the board
VCC: IC8.14 (VCC), RN2.1; also elsewhere on the board

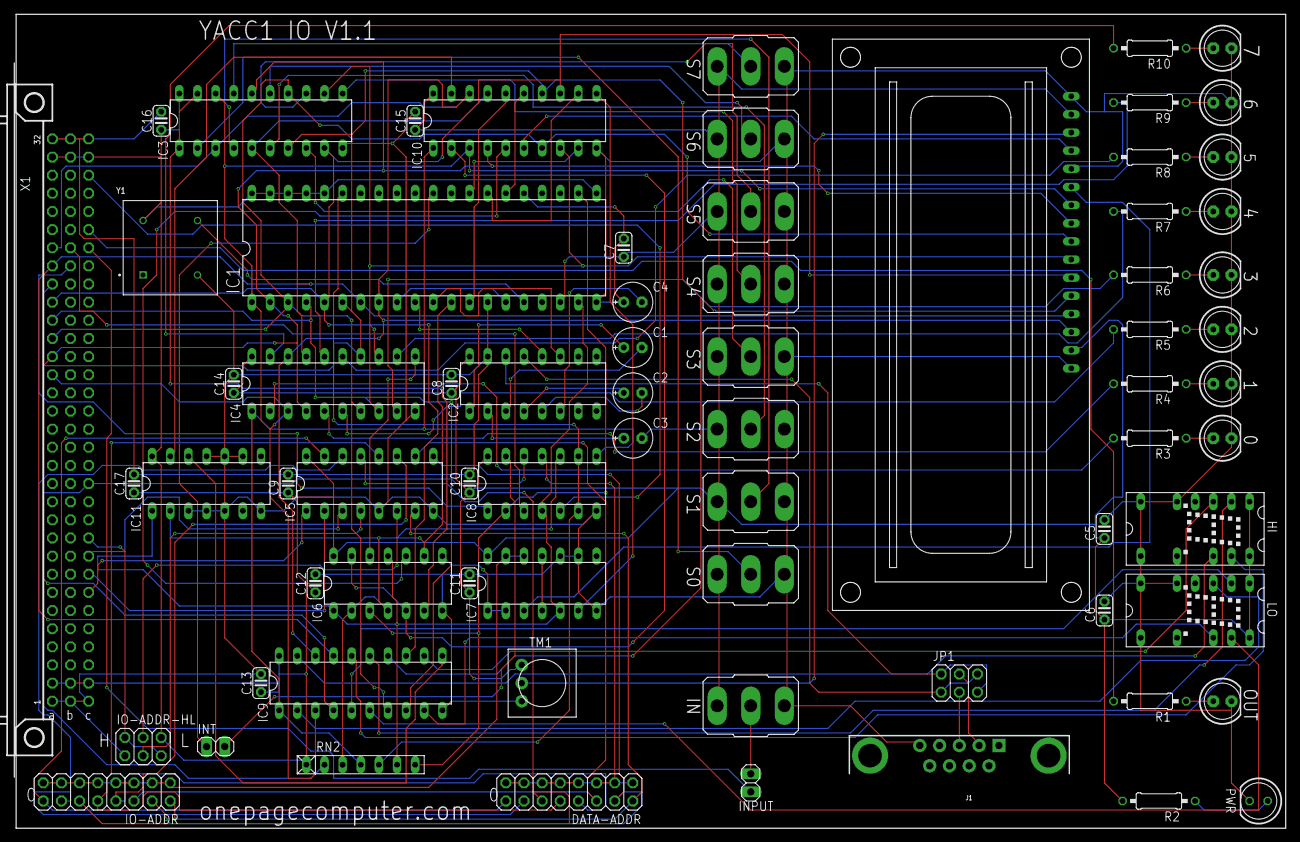
[picture p358: board IO V1.1.brd from above]

Board: 2 copper layers, 177.8 x 114.0 mm, 71 parts (0 on the bottom side), 104 nets.
