ksr/YACC1-D/migration/rebuild-diff-2026-09-20.txt

only in old tree:
archive/superseded-revisions/snapshot-2021-01-old/PCB/Production/Old & obsolete/.DS_Store
firmware/rom/eprom-captured-2026-09-18.bin
firmware/rom/eprom-captured-2026-09-18.hex

only in new tree:
archive/gen1-2015-2018/YACC1-BACKUP/Old/NewFolder/CppApplication_1/nbproject/Makefile-Debug.mk
archive/gen1-2015-2018/YACC1-BACKUP/Old/NewFolder/CppApplication_1/nbproject/Makefile-Release.mk
archive/gen1-2015-2018/YACC1-BACKUP/Old/NewFolder/CppApplication_1/nbproject/Makefile-impl.mk
archive/gen1-2015-2018/YACC1-BACKUP/Old/NewFolder/CppApplication_1/nbproject/Makefile-variables.mk
archive/gen1-2015-2018/YACC1-BACKUP/Old/NewFolder/CppApplication_1/nbproject/Package-Debug.bash
archive/gen1-2015-2018/YACC1-BACKUP/Old/NewFolder/CppApplication_1/nbproject/Package-Release.bash
archive/gen1-2015-2018/YACC1-BACKUP/Old/NewFolder/test EPROM/nbproject/configurations.xml
archive/gen1-2015-2018/YACC1-BACKUP/Old/NewFolder/test EPROM/nbproject/project.xml
archive/gen1-2015-2018/YACC1-BACKUP/Software/CommonHeaderFiles/nbproject/Makefile-Debug.mk
archive/gen1-2015-2018/YACC1-BACKUP/Software/CommonHeaderFiles/nbproject/Makefile-Release.mk
archive/gen1-2015-2018/YACC1-BACKUP/Software/CommonHeaderFiles/nbproject/Makefile-impl.mk
archive/gen1-2015-2018/YACC1-BACKUP/Software/CommonHeaderFiles/nbproject/Makefile-variables.mk
archive/gen1-2015-2018/YACC1-BACKUP/Software/CommonHeaderFiles/nbproject/Package-Debug.bash
archive/gen1-2015-2018/YACC1-BACKUP/Software/CommonHeaderFiles/nbproject/Package-Release.bash
archive/gen1-2015-2018/YACC1-BACKUP/Software/CommonHeaderFiles/nbproject/project.xml
archive/gen1-2015-2018/YACC1-BACKUP/Software/test EPROM/nbproject/project.xml
archive/gen1-2015-2018/YACC1A/deprecated/Software/uCode-Generator/nbproject/Makefile-Debug.mk
archive/gen1-2015-2018/YACC1A/deprecated/Software/uCode-Generator/nbproject/Makefile-Release.mk
archive/gen1-2015-2018/YACC1A/deprecated/Software/uCode-Generator/nbproject/project.xml
archive/superseded-revisions/sequencer-card-old/uCode-Generator copy/nbproject/Makefile-Debug.mk
archive/superseded-revisions/sequencer-card-old/uCode-Generator copy/nbproject/Makefile-Release.mk
archive/superseded-revisions/sequencer-card-old/uCode-Generator copy/nbproject/Makefile-impl.mk
archive/superseded-revisions/sequencer-card-old/uCode-Generator copy/nbproject/Makefile-variables.mk
archive/superseded-revisions/sequencer-card-old/uCode-Generator copy/nbproject/Package-Debug.bash
archive/superseded-revisions/sequencer-card-old/uCode-Generator copy/nbproject/Package-Release.bash
archive/superseded-revisions/sequencer-card-old/uCode-Generator copy/nbproject/configurations.xml
archive/superseded-revisions/sequencer-card-old/uCode-Generator copy/nbproject/project.xml
archive/superseded-revisions/snapshot-2020-08-orig/Software/Assembler/nbproject/configurations.xml
archive/superseded-revisions/snapshot-2020-08-orig/Software/Sequencer Card/uCode-Generator/nbproject/configurations.xml
archive/superseded-revisions/snapshot-2020-08-orig/Software/TinyBasicC/nbproject/Makefile-Debug.mk
archive/superseded-revisions/snapshot-2020-08-orig/Software/TinyBasicC/nbproject/Makefile-Release.mk
archive/superseded-revisions/snapshot-2020-08-orig/Software/TinyBasicC/nbproject/Makefile-impl.mk
archive/superseded-revisions/snapshot-2020-08-orig/Software/TinyBasicC/nbproject/Makefile-variables.mk
archive/superseded-revisions/snapshot-2020-08-orig/Software/TinyBasicC/nbproject/Package-Debug.bash
archive/superseded-revisions/snapshot-2020-08-orig/Software/TinyBasicC/nbproject/Package-Release.bash
archive/superseded-revisions/snapshot-2020-08-orig/Software/TinyBasicC/nbproject/configurations.xml
archive/superseded-revisions/snapshot-2020-08-orig/Software/TinyBasicC/nbproject/project.xml
archive/superseded-revisions/snapshot-2020-08-orig/Software/TinyBasicC/old/tb/tb/nbproject/Makefile-Debug.mk
archive/superseded-revisions/snapshot-2020-08-orig/Software/TinyBasicC/old/tb/tb/nbproject/Makefile-Release.mk
archive/superseded-revisions/snapshot-2020-08-orig/Software/TinyBasicC/old/tb/tb/nbproject/Makefile-impl.mk
archive/superseded-revisions/snapshot-2020-08-orig/Software/TinyBasicC/old/tb/tb/nbproject/Makefile-variables.mk
archive/superseded-revisions/snapshot-2020-08-orig/Software/TinyBasicC/old/tb/tb/nbproject/Package-Debug.bash
archive/superseded-revisions/snapshot-2020-08-orig/Software/TinyBasicC/old/tb/tb/nbproject/Package-Release.bash
archive/superseded-revisions/snapshot-2020-08-orig/Software/TinyBasicC/old/tb/tb/nbproject/project.xml
archive/superseded-revisions/snapshot-2021-07/Software/emulator/nbproject/Makefile-Debug.mk
archive/superseded-revisions/snapshot-2021-07/Software/emulator/nbproject/Makefile-Release.mk
archive/superseded-revisions/snapshot-2021-07/Software/emulator/nbproject/Makefile-impl.mk
archive/superseded-revisions/snapshot-2021-07/Software/emulator/nbproject/project.xml
archive/superseded-revisions/software-old-obsolete/Emulator/nbproject/Makefile-Debug.mk
archive/superseded-revisions/software-old-obsolete/Emulator/nbproject/Makefile-Release.mk
archive/superseded-revisions/software-old-obsolete/Emulator/nbproject/Makefile-impl.mk
archive/superseded-revisions/software-old-obsolete/Emulator/nbproject/Makefile-variables.mk
archive/superseded-revisions/software-old-obsolete/Emulator/nbproject/Package-Debug.bash
archive/superseded-revisions/software-old-obsolete/Emulator/nbproject/Package-Release.bash
archive/superseded-revisions/software-old-obsolete/Emulator/nbproject/configurations.xml
archive/superseded-revisions/software-old-obsolete/Emulator/nbproject/project.xml
archive/superseded-revisions/software-old-obsolete/Memory Card/test EPROM/nbproject/Makefile-Debug.mk
archive/superseded-revisions/software-old-obsolete/Memory Card/test EPROM/nbproject/Makefile-Release.mk
archive/superseded-revisions/software-old-obsolete/Memory Card/test EPROM/nbproject/Makefile-impl.mk
archive/superseded-revisions/software-old-obsolete/Memory Card/test EPROM/nbproject/Makefile-variables.mk
archive/superseded-revisions/software-old-obsolete/Memory Card/test EPROM/nbproject/Package-Debug.bash
archive/superseded-revisions/software-old-obsolete/Memory Card/test EPROM/nbproject/Package-Release.bash
archive/superseded-revisions/software-old-obsolete/Memory Card/test EPROM/nbproject/configurations.xml
archive/superseded-revisions/software-old-obsolete/Memory Card/test EPROM/nbproject/project.xml
archive/superseded-revisions/software-old-obsolete/Tiny-basic-notused/nbproject/configurations.xml
archive/superseded-revisions/software-old-obsolete/Tiny-basic-notused/nbproject/project.xml
archive/superseded-revisions/ucode-generator-v1/nbproject/Makefile-Debug.mk
archive/superseded-revisions/ucode-generator-v1/nbproject/Makefile-Release.mk
archive/superseded-revisions/ucode-generator-v1/nbproject/configurations.xml
firmware/microcode/ucode-generator2/nbproject/Makefile-Debug.mk
firmware/microcode/ucode-generator2/nbproject/Makefile-Release.mk
firmware/microcode/ucode-generator2/nbproject/Makefile-impl.mk
firmware/microcode/ucode-generator2/nbproject/Makefile-variables.mk
firmware/microcode/ucode-generator2/nbproject/Package-Debug.bash
firmware/microcode/ucode-generator2/nbproject/Package-Release.bash
firmware/microcode/ucode-generator2/nbproject/configurations.xml
firmware/microcode/ucode-generator2/nbproject/project.xml
software/assembler/nbproject/Makefile-Debug.mk
software/assembler/nbproject/Makefile-Release.mk
software/assembler/nbproject/Makefile-impl.mk
software/assembler/nbproject/Makefile-variables.mk
software/assembler/nbproject/Package-Debug.bash
software/assembler/nbproject/Package-Release.bash
software/assembler/nbproject/configurations.xml
software/assembler/nbproject/project.xml
software/assembler/old/a18/a18/nbproject/Makefile-Debug.mk
software/assembler/old/a18/a18/nbproject/Makefile-Release.mk
software/assembler/old/a18/a18/nbproject/Makefile-impl.mk
software/assembler/old/a18/a18/nbproject/Makefile-variables.mk
software/assembler/old/a18/a18/nbproject/Package-Debug.bash
software/assembler/old/a18/a18/nbproject/Package-Release.bash
software/assembler/old/a18/a18/nbproject/configurations.xml
software/assembler/old/a18/a18/nbproject/project.xml
software/disassembler/disasm/nbproject/Makefile-Debug.mk
software/disassembler/disasm/nbproject/Makefile-Release.mk
software/disassembler/disasm/nbproject/Makefile-impl.mk
software/disassembler/disasm/nbproject/Makefile-variables.mk
software/disassembler/disasm/nbproject/Package-Debug.bash
software/disassembler/disasm/nbproject/Package-Release.bash
software/disassembler/disasm/nbproject/configurations.xml
software/disassembler/disasm/nbproject/project.xml
software/disassembler/disasm2/nbproject/Makefile-Debug.mk
software/disassembler/disasm2/nbproject/Makefile-Release.mk
software/disassembler/disasm2/nbproject/Makefile-impl.mk
software/disassembler/disasm2/nbproject/Makefile-variables.mk
software/disassembler/disasm2/nbproject/Package-Debug.bash
software/disassembler/disasm2/nbproject/Package-Release.bash
software/disassembler/disasm2/nbproject/configurations.xml
software/disassembler/disasm2/nbproject/project.xml
software/experiments/16bit/assembler-16/nbproject/Makefile-Debug.mk
software/experiments/16bit/assembler-16/nbproject/Makefile-Release.mk
software/experiments/16bit/assembler-16/nbproject/Makefile-impl.mk
software/experiments/16bit/assembler-16/nbproject/Makefile-variables.mk
software/experiments/16bit/assembler-16/nbproject/Package-Debug.bash
software/experiments/16bit/assembler-16/nbproject/Package-Release.bash
software/experiments/16bit/assembler-16/nbproject/configurations.xml
software/experiments/16bit/assembler-16/nbproject/project.xml
software/experiments/16bit/emulator-16/nbproject/Makefile-Debug.mk
software/experiments/16bit/emulator-16/nbproject/Makefile-Release.mk
software/experiments/16bit/emulator-16/nbproject/Makefile-impl.mk
software/experiments/16bit/emulator-16/nbproject/Makefile-variables.mk
software/experiments/16bit/emulator-16/nbproject/Package-Debug.bash
software/experiments/16bit/emulator-16/nbproject/Package-Release.bash
software/experiments/16bit/emulator-16/nbproject/configurations.xml
software/experiments/16bit/emulator-16/nbproject/project.xml
software/ubasic-c/ubasic-master-orig/nbproject/configurations.xml
software/ubasic-c/ubasic-master-orig/nbproject/project.xml
software/ubasic-c/ubasic-master/nbproject/configurations.xml
software/ubasic-c/ubasic-master/nbproject/project.xml
tests/bus-tester-scripts/Gen Test Vectors/gen test vectors/nbproject/Makefile-Debug.mk
tests/bus-tester-scripts/Gen Test Vectors/gen test vectors/nbproject/Makefile-Release.mk
tests/bus-tester-scripts/Gen Test Vectors/gen test vectors/nbproject/Makefile-impl.mk
tests/bus-tester-scripts/Gen Test Vectors/gen test vectors/nbproject/Makefile-variables.mk
tests/bus-tester-scripts/Gen Test Vectors/gen test vectors/nbproject/Package-Debug.bash
tests/bus-tester-scripts/Gen Test Vectors/gen test vectors/nbproject/Package-Release.bash
tests/bus-tester-scripts/Gen Test Vectors/gen test vectors/nbproject/configurations.xml
tests/bus-tester-scripts/Gen Test Vectors/gen test vectors/nbproject/project.xml

different content:
migration/copy-duplicates.txt
migration/production-boards.txt
migration/same-name-different-content.txt
