ksr/YACC1-D/os/y1os.asm

; Author: Claude (Anthropic) for Ken Rother's YACC1 project, 2026

; =====================================================================================================================
; y1os.asm - Y1/OS v0.2 (2026-09-23): the YACC1 disk operating system, hand-written in YACC1 assembly.
;
; The same OS as y1os.c (v0.1, the C version compiled by y1cc, which stays in the tree as THE SPECIFICATION and is
; still built with `make -C os OS=c`): the same shell, commands, messages, syscall numbers, arguments, results and
; side effects, the same redirection and pipes, the same RAM areas and the same bytes on the card. Every routine
; below names the C function it implements; where the C does something odd, this does it too (os/README.md lists
; those behaviours, BACKLOG.md the ones worth changing). The console transcripts of tests/os are the contract.
;
; Loaded from the CompactFlash card (LBA 1.., OSCNT sectors) to $1000 by the monitor's O command, which JSRURs
; $1000; `exit` RETs to the monitor. Console and sectors come from the ROM's BIOS vectors ($FFC0..).
;
; Build: os/Makefile (make -C os): os/mkstrings.py turns os/strings.txt into build/asm/y1os_str.inc (the messages as
; numeric DB bytes: the assembler upper-cases its source), then software/assembler/asm assembles this file there.
;
; ---- conventions -----------------------------------------------------------------------------------------------
; Registers: R0 = PC, R1 = SP. R2 is NEVER used: on the machine LDA/STA/LDT/STT/LDR/STR load the operand address into
;   R2 (the interpreter hides it in a ninth register). R3 = the main value / result (16 bits), R4, R5 = operands and
;   pointers, R6, R7 = scratch (the ROM's CFREAD/CFWRITE clobber them). ACC, TMP: byte work and compares.
; Results: a routine that returns a number leaves it in R3 (16 bits, the syscall's SYSRES) and, for a yes/no or a
;   handle, the same in ACC so that the caller can BRZ/BRNZ at once. ret0/ret1/reta/retr3 are the shared exits.
; 16-bit arithmetic: an add is ADDT/ADDI then ADDTC/ADDIC with nothing but register moves between them (the carry
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
